uob-hep-cad/uob-hep-pc072/images/boardlocations.jpg

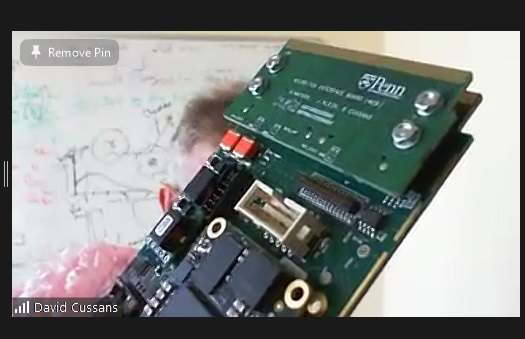
images/boardlocations.jpg
