uob-hep-cad/uob-hep-pc072/images/dune_mib_rev3_v224_top_layer_with_power_colour_white_bg.pdf

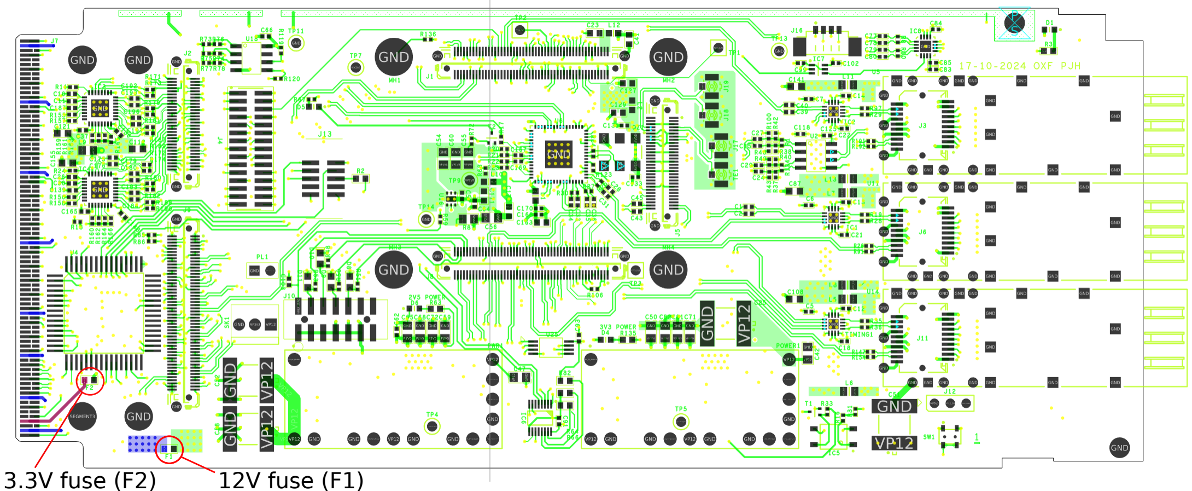
[picture p3: page 1]

3.3V fuse (F2) 12V fuse (F1)
