uob-hep-cad/uob-hep-pc072/hardware/Cadence/top/mtca_interface_board_reocc/02_#20power/sch_1/page1.csv

FILE_TYPE = CONNECTIVITY;
{Allegro Design Entry HDL 24.1 P001 (4234998) 9/4/2024}
"PAGE_NUMBER" = 1;
0"NC";
1"VCC3V3\g";
2"MP3V3\G";
3"GND\g";
4"GND\g";
5"GND\g";
8"GND\G";
7"GND\G";
6"GND\G";
9"GND\g";
10"GND\g";
11"GND\g";
12"GND\g";
13"GND\g";
14"GND\g";
15"GND\g";
16"GND\g";
17"P2V5\g";
18"VP1V8\g";
20"VCC3V3\G";
19"VCC3V3\G";
21"GND\g";
22"GND\g";
23"VP12\g";
24"MP3V3\g";
25"GND\g";
26"VP12";
27"MP3V3\g";
28"MP3V3\g";
29"VCC3V3_PRE_RSHUNT";
30"VO_3V3<1..0>";
31"UN$1$LTC2991$I162$V1";
32"UN$1$LTC2991$I162$V2";
33"VP12_EN";
34"UN$1$OPTOCOUPLERACEC$I139$ANODE";
35"UN$1$RSMD0603$I144$B";
37"SENSE_12C_SCL";
36"SENSE_12C_SCL";
38"UN$1$PTH08T210W$I137$VADJ";
39"P2V5_MON_HIGH";
40"UN$1$PTH08T210W$I137$TURBOTRANS";
41"UN$1$OPTOCOUPLERACEC$I139$COLLECTOR";
42"UN$1$LTC2991$I162$ADR1";
43"UN$1$LTC2991$I162$ADR0";
44"DC_DC_ENABLE";
45"DCDC_ENABLE";
46"1V8_POST_RSHUNT";
47"P2V5_MON_LOW";
49"SENSE_12C_SDA";
48"SENSE_12C_SDA";
50"UN$1$LTC2991$I162$ADR2";
51"VIN<1..0>";
52"DCDC_3V3_PG";
53"UN$1$ledred06030$121P$A";
54"UN$1$r$I154$1";
%"r"
"1","(1200,-4750)","0","discrete","108P";
;
VALUE"10K"
$LOCATION"R85"
SEC"1"
PART_NUMBER"M55342K11B10E0RS3"
PART_TYPE"Thick Film"
DESCRIPTION"RES SMD 10K OHM 1% 1/20W 0402"
POWER"1/10W"
TOLERANCE"1%"
MPN"M55342K11B10E0RS3"
MANUFACTURER"Vishay Dale"
DISTRIBUTOR_PARTNUMBER"1135-1061-1-ND"
DISTRIBUTOR"Digikey"
DATASHEET"C:\EMA\CISQuickStart\Technical_Datasheets\Vishay\dcrcwe3.pdf"
ROOM"MAIN_PWR"
SOURCE_PACKAGE"R"
JEDEC_TYPE"res0402"
CDS_LOCATION"R85"
CDS_LIB"discrete";
"1"
$PN"1"20,19;
"2"
$PN"2"52;
%"r"
"1","(800,-4800)","6","discrete","111P";
;
VALUE"249 Ohm"
$LOCATION"R135"
CDS_LIB"discrete"
CDS_LOCATION"R135"
JEDEC_TYPE"res0603"
SOURCE_PACKAGE"R"
REUSE_ANNOTATE"TRUE"
PART_NUMBER"EMA-00003608"
PART_TYPE"Thick Film"
DESCRIPTION"RES, Thick Film, 249 Ohm, 1.0 %, 1/10 W, SMD, 0603"
POWER"1/10 W"
TOLERANCE"1.0 %"
MPN"MCR03EZPFX2490"
MANUFACTURER"Rohm"
DISTRIBUTOR_PARTNUMBER"RHM249HTR-ND"
DISTRIBUTOR"Digikey"
DATASHEET"C:\EMA\CISQuickStart\Technical_Datasheets\Rohm\mcr03.pdf"
ROOM"VCC3V3I_V"
SEC"1";
"1"
$PN"1"53;
"2"
$PN"2"20,19;
%"r"
"1","(1200,-5225)","0","discrete","117P";
;
$LOCATION"R86"
VALUE"4.99k"
CDS_LIB"discrete"
CDS_LOCATION"R86"
JEDEC_TYPE"res0402"
SOURCE_PACKAGE"R"
REUSE_ANNOTATE"TRUE"
PART_NUMBER"ERJ-2RKF4991X"
PART_TYPE"Thick Film"
DESCRIPTION"RES SMD 4.99K OHM 1% 1/10W 0402"
POWER"1/10 W"
TOLERANCE"1%"
MPN"ERJ-2RKF4991X"
MANUFACTURER"Panasonic"
DISTRIBUTOR_PARTNUMBER"P4.99KLTR-ND"
DISTRIBUTOR"Digikey"
AVAILABILITY"In Stock"
ROOM"VP3V3"
SEC"1";
"1"
$PN"1"52;
"2"
$PN"2"8,7,6;
%"cap_np"
"1","(3675,-2075)","0","ocad_parts_lib","118P";
;
VALUE"0.1UF"
$LOCATION"C92"
VOLTAGE"25V"
CLASS"DISCRETE"
LAST_EDIT_BY"SNF"
ALT_SYMBOLS""
ROOM"MAIN_PWR"
PART_NUMBER"445-8173-1-ND"
PART_TYPE"Ceramic"
DESCRIPTION"CAP 0.1__F __10% 25V Ceramic Capacitor X7R 0805 "
PSPICE"C"
MPN"CGJ4J2X7R1E104K125AA "
MANUFACTURER"TDK CORP"
DISTRIBUTOR_PARTNUMBER"445-8173-1-ND"
DISTRIBUTOR"Digi-Key"
AVAILABILITY"In Stock"
SOURCE_PACKAGE"CAP_NP"
JEDEC_TYPE"cap0805"
SEC"1"
CDS_LOCATION"C92"
CDS_LIB"ocad_parts_lib";
"1"
$PN"1"29;
"2"
$PN"2"9;
%"cap_np"
"1","(3950,-2050)","0","ocad_parts_lib","119P";
;
VOLTAGE"6.3V"
VALUE"100UF"
$LOCATION"C95"
CDS_LIB"ocad_parts_lib"
CDS_LOCATION"C95"
JEDEC_TYPE"cap1206"
SOURCE_PACKAGE"CAP_NP"
REUSE_ANNOTATE"TRUE"
PART_NUMBER"GRM31CD80J107ME39K"
PART_TYPE"Ceramic"
DESCRIPTION"CAP CER 100UF 6.3V X6T 1206"
TOLERANCE"20%"
PSPICE"C"
MPN"GRM31CD80J107ME39K"
MANUFACTURER"Murata"
DISTRIBUTOR_PARTNUMBER"490-16313-2-ND"
DISTRIBUTOR"Digi-Key"
PRICE"0.5"
AVAILABILITY"In Stock"
ROOM"MAIN_PWR"
ALT_SYMBOLS""
LAST_EDIT_BY"SNF"
CLASS"DISCRETE"
SEC"1";
"1"
$PN"1"29;
"2"
$PN"2"9;
%"led red 0603_0"
"1","(750,-5100)","3","atcs","121P";
;
$LOCATION"D4"
VALUE"Red"
SEC"1"
MFR_PART_NUMBER"LTST-C190CKT"
DEVICE"LED_RED0603"
MFR_NAME"Lite-On Trading USA, Inc."
CY_PART_"860R-13780"
REUSE_ANNOTATE"TRUE"
ROOM"VCC3V3I_V"
PART_NUMBER"LNJ237W82RA"
PART_TYPE"LED\Red"
RATING"50 mW"
LEDCOLOR"Red"
MPN"LNJ237W82RA"
MANUFACTURER"Panasonic"
DISTRIBUTOR_PARTNUMBER"LNJ237W82RACT-ND"
DISTRIBUTOR"Digikey"
DATASHEET"C:\EMA\CISQuickStart\Technical_Datasheets\Panasonic\ATA7000CE271.pdf"
DESCRIPTION"LED RED 0603 SMD"
SOURCE_PACKAGE"LED RED 0603_0"
JEDEC_TYPE"LEDC1608X80N"
CDS_LOCATION"D4"
CDS_LIB"atcs";
"A"
$PN"2"53;
"K"
$PN"1"8,7,6;
%"cap_np_0"
"1","(4850,-3750)","7","ocad_parts_lib","126P";
;
VOLTAGE"25V"
VALUE"0.1UF"
$LOCATION"C91"
SEC"1"
ALT_SYMBOLS""
LAST_EDIT_BY"SNF"
CLASS"DISCRETE"
REUSE_ANNOTATE"TRUE"
ROOM"MAIN_PWR"
AVAILABILITY"In Stock"
DISTRIBUTOR"Digi-Key"
DISTRIBUTOR_PARTNUMBER"445-7348-2-ND"
MANUFACTURER"TDK CORP"
MPN"C1005X7R1E104K050BB "
PSPICE"C"
DESCRIPTION"CAP 0.1__F __10% 25V Ceramic Capacitor X7R 0402 "
PART_TYPE"Ceramic"
PART_NUMBER"445-7348-2-ND"
REUSE_ID"169"
SOURCE_PACKAGE"CAP_NP_0"
JEDEC_TYPE"cap0402"
CDS_LOCATION"C91"
CDS_LIB"ocad_parts_lib";
"1"
$PN"1"16;
"2"
$PN"2"28;
%"hdr1x3"
"2","(675,-3475)","0","ocad_parts_lib","127P";
;
$LOCATION"J12"
VALUE"HDR1x3"
SEC"1"
REUSE_ANNOTATE"TRUE"
ROOM"USB-JTAG"
PART_NUMBER"HDR1x3"
PART_TYPE"Header"
DESCRIPTION"CONN3, Header,TH"
CONTACTCURRENT"6.0 A"
CONTACTVOLTAGE"600 V"
CONTACTGENDER"Male"
HOUSINGGENDER"Male"
MANUFACTURER"Samtec"
DISTRIBUTOR"Digikey"
DATASHEET"C:\EMA\CISQuickStart\Technical_Datasheets\Molex Inc\MX42385.pdf"
SOURCE_PACKAGE"HDR1x3"
JEDEC_TYPE"Hdr_1x3"
CDS_LOCATION"J12"
CDS_LIB"ocad_parts_lib";
"P1"
$PN"1"2;
"P2"
$PN"2"33;
"P3"
$PN"3"45;
%"testpoint"
"1","(4900,-2125)","5","testpoint","130P";
;
BOM_IGNORE"TRUE"
$LOCATION"TP5"
SEC"1"
VALUE"5002 White"
ROOM"MAIN_PWR"
PART_NUMBER"EMA-00001481V22"
PART_TYPE"Testpoint"
DESCRIPTION"MISC, Testpoint, 5002 White, TH, 2.5x2.5x4.6 mm"
MPN"5002"
MANUFACTURER"Keystone Electronics"
DATASHEET"C:\EMA\CISQuickStart\Technical_Datasheets\Keystone Electronics\M55p51.pdf"
SOURCE_PACKAGE"TESTPOINT"
JEDEC_TYPE"TP_KEYSTONE_5000A"
CDS_LOCATION"TP5"
CDS_LIB"testpoint";
"TP"
$PN"1"29;
%"vcc_bar"
"1","(6750,-1725)","0","mtca_interface_board","132P";
;
HDL_POWER"VCC3V3"
CDS_LIB"mtca_interface_board";
"HOTSPOT_0"1;
%"vcc_bar"
"1","(875,-2950)","0","mtca_interface_board","133P";
;
HDL_POWER"MP3V3"
CDS_LIB"mtca_interface_board";
"HOTSPOT_0"2;
%"gnd"
"1","(1375,-2700)","0","mtca_interface_board","38P";
;
CDS_LIB"mtca_interface_board"
HDL_POWER"GND";
"HOTSPOT_0"3;
%"gnd"
"1","(2200,-2700)","0","mtca_interface_board","39P";
;
CDS_LIB"mtca_interface_board"
HDL_POWER"GND";
"HOTSPOT_0"4;
%"gnd"
"1","(5850,-2325)","0","mtca_interface_board","40P";
;
CDS_LIB"mtca_interface_board"
HDL_POWER"GND";
"HOTSPOT_0"5;
%"gnd"
"1","(750,-5575)","0","mtca_interface_board","41P";
;
CDS_LIB"mtca_interface_board"
HDL_POWER"GND";
"HOTSPOT_0"8,7,6;
%"gnd"
"1","(3900,-2475)","0","mtca_interface_board","5P";
;
CDS_LIB"mtca_interface_board"
HDL_POWER"GND";
"HOTSPOT_0"9;
%"PTH08T210W"
"1","(2775,-1950)","0","cnlinear","I137";
;
$LOCATION"IC?"
PACK_TYPE"ECP"
TYPE"PTH08T210WAD"
CDS_LIB"cnlinear";
"VI<1..0>"51;
"GND<3..0>"10;
"VO<1..0>"30;
"TURBOTRANS"40;
"SENSP"35;
"SENSM"11;
"UVLO"44;
"TRACK"26;
"VADJ"38;
%"TRANS MOSFET"
"1","(2200,-2400)","0","cndiscrete","I138";
;
$LOCATION"T?"
TYPE"SOT523"
VALUE"PJE8408"
CDS_LIB"cndiscrete"
PACK_TYPE"GSD";
"D\NAC"44;
"S\NAC"4;
"G\NAC"41;
%"OPTOCOUPLER_AC_EC"
"1","(1675,-2575)","0","cndiscrete","I139";
;
$LOCATION"IC?"
CASE"SOIC"
TYPE"TLP183"
NEEDS_NO_SIZE"TRUE"
CDS_LIB"cndiscrete"
PACK_TYPE"1264";
"EMITTER"13;
"COLLECTOR"41;
"CATHODE"3;
"ANODE"34;
%"r"
"1","(1925,-2150)","0","discrete","I141";
;
$LOCATION"?"
VALUE"150K"
CDS_LIB"discrete"
JEDEC_TYPE"res0402"
SOURCE_PACKAGE"R"
ROOM"MMC_DISCRETE"
DISTRIBUTOR"Digikey"
DISTRIBUTOR_PARTNUMBER"P150KLTR-ND"
MANUFACTURER"Panasonic"
MPN"ERJ-2RKF1873X"
TOLERANCE"1 %"
POWER"1/10 W"
DESCRIPTION"RES SMD 150K OHM 1% 1/10W 0402"
PART_TYPE"Thick Film"
PART_NUMBER"ERJ-2RKF1503X";
"1"
$PN"?"26;
"2"
$PN"?"41;
%"gnd"
"1","(2575,-2325)","0","mtca_interface_board","I142";
;
CDS_LIB"mtca_interface_board"
HDL_POWER"GND";
"HOTSPOT_0"10;
%"gnd"
"1","(3225,-2400)","0","mtca_interface_board","I143";
;
CDS_LIB"mtca_interface_board"
HDL_POWER"GND";
"HOTSPOT_0"11;
%"RSMD0603"
"1","(3175,-1600)","0","cnpassive","I144";
;
$LOCATION"R?"
VALUE"XX"
TOL"1%"
SIZE"1B"
TOL_ON_OFF"ON"
POSTOL"RTOL%"
NEGTOL"RTOL%"
DIST"FLAT"
POWER"RMAX"
VOLTAGE"RVMAX"
SLOPE"RSMAX"
MAX_TEMP"RTMAX"
TC1"RTMPL"
TC2"RTMPQ"
PACK_TYPE"1/10W"
CDS_LIB"cnpassive";
"B <SIZE-1..0>\NAC"35;
"A <SIZE-1..0>\NAC"40;
%"RSMD0603"
"1","(2925,-2450)","1","cnpassive","I145";
;
$LOCATION"R?"
TOL"1%"
VALUE"1.6K"
PACK_TYPE"1/10W"
CDS_LIB"cnpassive"
SIZE"1B"
TOL_ON_OFF"ON"
POSTOL"RTOL%"
NEGTOL"RTOL%"
DIST"FLAT"
POWER"RMAX"
VOLTAGE"RVMAX"
SLOPE"RSMAX"
MAX_TEMP"RTMAX"
TC1"RTMPL"
TC2"RTMPQ";
"B <SIZE-1..0>\NAC"38;
"A <SIZE-1..0>\NAC"12;
%"gnd"
"1","(2875,-2675)","0","mtca_interface_board","I146";
;
CDS_LIB"mtca_interface_board"
HDL_POWER"GND";
"HOTSPOT_0"12;
%"RSMD0603"
"1","(3700,-1600)","0","cnpassive","I148";
;
LOCATION"R84"
TOL"1%"
VALUE"1"
CDS_LIB"cnpassive"
SIZE"1B"
TOL_ON_OFF"ON"
POSTOL"RTOL%"
NEGTOL"RTOL%"
DIST"FLAT"
POWER"RMAX"
VOLTAGE"RVMAX"
SLOPE"RSMAX"
MAX_TEMP"RTMAX"
TC1"RTMPL"
TC2"RTMPQ"
PACK_TYPE"1/10W";
"B <SIZE-1..0>\NAC"1;
"A <SIZE-1..0>\NAC"35;
%"r"
"1","(1225,-3075)","2","discrete","I154";
;
$LOCATION"?"
VALUE"24.9"
CDS_LIB"discrete"
REUSE_ANNOTATE"TRUE"
ROOM"JTAG"
PART_NUMBER"311-24.9LRCT-ND"
PART_TYPE"Thick Film"
DESCRIPTION"RES SMD 24.9 OHM 1% 1/16W 0402"
POWER"1/10W"
TOLERANCE"1%"
MPN"RC0402FR-0724R9L"
MANUFACTURER"Yageo"
DISTRIBUTOR_PARTNUMBER"311-24.9LRCT-ND"
DISTRIBUTOR"Digikey"
REUSE_ID"38"
SOURCE_PACKAGE"R"
JEDEC_TYPE"res0402";
"1"
$PN"?"54;
"2"
$PN"?"33;
%"gnd"
"1","(1925,-2700)","0","mtca_interface_board","I155";
;
CDS_LIB"mtca_interface_board"
HDL_POWER"GND";
"HOTSPOT_0"13;
%"gnd"
"1","(1075,-2350)","0","mtca_interface_board","I158";
;
CDS_LIB"mtca_interface_board"
HDL_POWER"GND";
"HOTSPOT_0"14;
%"r"
"1","(1225,-2725)","2","discrete","I159";
;
$LOCATION"?"
VALUE"24.9"
CDS_LIB"discrete"
REUSE_ANNOTATE"TRUE"
ROOM"JTAG"
PART_NUMBER"311-24.9LRCT-ND"
PART_TYPE"Thick Film"
DESCRIPTION"RES SMD 24.9 OHM 1% 1/16W 0402"
POWER"1/10W"
TOLERANCE"1%"
MPN"RC0402FR-0724R9L"
MANUFACTURER"Yageo"
DISTRIBUTOR_PARTNUMBER"311-24.9LRCT-ND"
DISTRIBUTOR"Digikey"
REUSE_ID"38"
SOURCE_PACKAGE"R"
JEDEC_TYPE"res0402";
"1"
$PN"?"34;
"2"
$PN"?"54;
%"CTAP"
"1","(2225,-1850)","2","standard","I160";
;
CDS_LIB"standard"
BODY_TYPE"PLUMBING"
HDL_TAP"TRUE";
"S \NAC"
BN"0"26;
"B \NAC \NWC"51;
%"CTAP"
"1","(2225,-1775)","2","standard","I161";
;
CDS_LIB"standard"
BODY_TYPE"PLUMBING"
HDL_TAP"TRUE";
"S \NAC"
BN"1"26;
"B \NAC \NWC"51;
%"LTC2991"
"1","(4825,-2875)","0","cnlinear","I162";
;
$LOCATION"IC?"
POWER_GROUP"VCC=MP3V3"
PACK_TYPE"MSOP"
TYPE"LTC2991CMS#PBF"
CDS_LIB"cnlinear"
CDS_LMAN_SYM_OUTLINE"-200,225,200,-200";
"V4"46;
"V8"47;
"V7"39;
"V5"18;
"V6"0;
"V1"31;
"V2"32;
"V3"17;
"PWM"0;
"ADR2"50;
"ADR1"42;
"SDA"49,48;
"ADR0"43;
"SCL"37,36;
%"CTAP"
"1","(3350,-1975)","0","standard","I163";
;
CDS_LIB"standard"
BODY_TYPE"PLUMBING"
HDL_TAP"TRUE";
"S \NAC"
BN"1"29;
"B \NAC \NWC"30;
%"CTAP"
"1","(3350,-2050)","0","standard","I164";
;
CDS_LIB"standard"
BODY_TYPE"PLUMBING"
HDL_TAP"TRUE";
"S \NAC"
BN"0"29;
"B \NAC \NWC"30;
%"RSMD0603"
"1","(4300,-2925)","0","cnpassive","I165";
;
$LOCATION"R?"
TOL""
VALUE"00"
PACK_TYPE""
CDS_LIB"cnpassive"
SIZE"1B"
TOL_ON_OFF"ON"
POSTOL"RTOL%"
NEGTOL"RTOL%"
DIST"FLAT"
POWER"RMAX"
VOLTAGE"RVMAX"
SLOPE"RSMAX"
MAX_TEMP"RTMAX"
TC1"RTMPL"
TC2"RTMPQ";
"B <SIZE-1..0>\NAC"43;
"A <SIZE-1..0>\NAC"27;
%"RSMD0603"
"1","(4300,-2975)","0","cnpassive","I166";
;
$LOCATION"R?"
TOL""
VALUE"00"
PACK_TYPE""
CDS_LIB"cnpassive"
SIZE"1B"
TOL_ON_OFF"ON"
POSTOL"RTOL%"
NEGTOL"RTOL%"
DIST"FLAT"
POWER"RMAX"
VOLTAGE"RVMAX"
SLOPE"RSMAX"
MAX_TEMP"RTMAX"
TC1"RTMPL"
TC2"RTMPQ";
"B <SIZE-1..0>\NAC"42;
"A <SIZE-1..0>\NAC"15;
%"RSMD0603"
"1","(4300,-3025)","0","cnpassive","I167";
;
$LOCATION"R?"
VALUE"00"
TOL""
TC2"RTMPQ"
TC1"RTMPL"
MAX_TEMP"RTMAX"
SLOPE"RSMAX"
VOLTAGE"RVMAX"
POWER"RMAX"
DIST"FLAT"
NEGTOL"RTOL%"
POSTOL"RTOL%"
TOL_ON_OFF"ON"
SIZE"1B"
CDS_LIB"cnpassive"
PACK_TYPE"";
"B <SIZE-1..0>\NAC"50;
"A <SIZE-1..0>\NAC"15;
%"gnd"
"1","(4100,-3100)","0","mtca_interface_board","I168";
;
CDS_LIB"mtca_interface_board"
HDL_POWER"GND";
"HOTSPOT_0"15;
%"gnd"
"1","(5000,-3825)","0","mtca_interface_board","I169";
;
CDS_LIB"mtca_interface_board"
HDL_POWER"GND";
"HOTSPOT_0"16;
%"P2V5"
"1","(5850,-2650)","0","cnpower","I171";
;
CDS_LIB"cnpower"
SIZE"1B"
BODY_TYPE"PLUMBING"
HDL_POWER"P2V5";
"A<SIZE-1..0>\NAC"
VHDL_INIT"1"17;
%"vcc_bar"
"1","(6075,-2775)","0","mtca_interface_board","I172";
;
HDL_POWER"VP1V8"
CDS_LIB"mtca_interface_board";
"HOTSPOT_0"18;
%"cap_np"
"1","(1125,-2100)","0","ocad_parts_lib","I175";
;
CDS_LOCATION"C92"
$LOCATION"C92"
VALUE"0.1UF"
VOLTAGE"25V"
CDS_LIB"ocad_parts_lib"
JEDEC_TYPE"cap0805"
SOURCE_PACKAGE"CAP_NP"
AVAILABILITY"In Stock"
DISTRIBUTOR"Digi-Key"
DISTRIBUTOR_PARTNUMBER"445-8173-1-ND"
MANUFACTURER"TDK CORP"
MPN"CGJ4J2X7R1E104K125AA "
PSPICE"C"
DESCRIPTION"CAP 0.1__F __10% 25V Ceramic Capacitor X7R 0805 "
PART_TYPE"Ceramic"
PART_NUMBER"445-8173-1-ND"
ROOM"MAIN_PWR"
ALT_SYMBOLS""
LAST_EDIT_BY"SNF"
CLASS"DISCRETE"
SEC"1";
"1"
$PN"1"26;
"2"
$PN"2"14;
%"testpoint"
"1","(3550,-4600)","5","testpoint","I176";
;
$LOCATION"TP7"
JEDEC_TYPE"TP_KEYSTONE_5000A"
CDS_LOCATION"TP7"
CDS_LIB"testpoint"
SEC"1"
PART_NUMBER"EMA-00001481V22"
SOURCE_PACKAGE"TESTPOINT";
"TP"
$PN"1"20,19;
%"testpoint"
"1","(3550,-5425)","5","testpoint","I177";
;
$LOCATION"TP13"
SEC"1"
VALUE"5002 White"
ROOM"VCC3V3I_V"
DATASHEET"C:\EMA\CISQuickStart\Technical_Datasheets\Keystone Electronics\M55p51.pdf"
MANUFACTURER"Keystone Electronics"
MPN"5002"
DESCRIPTION"MISC, Testpoint, 5002 White, TH, 2.5x2.5x4.6 mm"
PART_TYPE"Testpoint"
PART_NUMBER"EMA-00001481V22"
SOURCE_PACKAGE"TESTPOINT"
JEDEC_TYPE"TP_KEYSTONE_5000A"
CDS_LOCATION"TP13"
CDS_LIB"testpoint";
"TP"
$PN"1"8,7,6;
%"cap_np"
"1","(2575,-4925)","0","ocad_parts_lib","I186";
;
VALUE"47UF"
$LOCATION"C82"
VOLTAGE"6.3V"
DESCRIPTION"CAP CER 47UF 6.3V X5R 0805"
PART_TYPE"Ceramic"
SEC"1"
CLASS"DISCRETE"
LAST_EDIT_BY"SNF"
ALT_SYMBOLS""
ROOM"VCC3V3I_V"
AVAILABILITY"In Stock"
DISTRIBUTOR"Digi-Key"
DISTRIBUTOR_PARTNUMBER"490-14660-2-ND"
MANUFACTURER"Murata"
MPN"GRM21BR60J476ME15K"
PSPICE"C"
TOLERANCE"20%"
PART_NUMBER"GRM21BR60J476ME15K"
SOURCE_PACKAGE"CAP_NP"
JEDEC_TYPE"cap0805"
CDS_LOCATION"C82"
CDS_LIB"ocad_parts_lib";
"1"
$PN"1"20,19;
"2"
$PN"2"8,7,6;
%"gnd"
"1","(2525,-5600)","0","mtca_interface_board","I187";
;
CDS_LIB"mtca_interface_board"
HDL_POWER"GND";
"HOTSPOT_0"8,7,6;
%"cap_np"
"1","(2275,-4925)","0","ocad_parts_lib","I188";
;
VOLTAGE"6.3V"
VALUE"47UF"
$LOCATION"C81"
DISTRIBUTOR_PARTNUMBER"490-14660-2-ND"
DISTRIBUTOR"Digi-Key"
SEC"1"
CLASS"DISCRETE"
LAST_EDIT_BY"SNF"
ALT_SYMBOLS""
ROOM"VCC3V3I_V"
PART_NUMBER"GRM21BR60J476ME15K"
PART_TYPE"Ceramic"
DESCRIPTION"CAP CER 47UF 6.3V X5R 0805"
TOLERANCE"20%"
PSPICE"C"
MPN"GRM21BR60J476ME15K"
MANUFACTURER"Murata"
AVAILABILITY"In Stock"
SOURCE_PACKAGE"CAP_NP"
JEDEC_TYPE"cap0805"
CDS_LOCATION"C81"
CDS_LIB"ocad_parts_lib";
"1"
$PN"1"20,19;
"2"
$PN"2"8,7,6;
%"cap_np"
"1","(2000,-4925)","0","ocad_parts_lib","I189";
;
VOLTAGE"6.3V"
VALUE"47UF"
$LOCATION"C71"
PART_TYPE"Ceramic"
PART_NUMBER"GRM21BR60J476ME15K"
SEC"1"
CLASS"DISCRETE"
LAST_EDIT_BY"SNF"
ALT_SYMBOLS""
AVAILABILITY"In Stock"
DISTRIBUTOR"Digi-Key"
DISTRIBUTOR_PARTNUMBER"490-14660-2-ND"
MANUFACTURER"Murata"
MPN"GRM21BR60J476ME15K"
PSPICE"C"
TOLERANCE"20%"
DESCRIPTION"CAP CER 47UF 6.3V X5R 0805"
ROOM"VCC3V3I_V"
SOURCE_PACKAGE"CAP_NP"
JEDEC_TYPE"cap0805"
CDS_LOCATION"C71"
CDS_LIB"ocad_parts_lib";
"1"
$PN"1"20,19;
"2"
$PN"2"8,7,6;
%"vcc_bar"
"1","(1525,-4475)","0","mtca_interface_board","I190";
;
HDL_POWER"VCC3V3"
CDS_LIB"mtca_interface_board";
"HOTSPOT_0"20,19;
%"cap_np"
"1","(1700,-4925)","0","ocad_parts_lib","I191";
;
$LOCATION"C69"
VALUE"0.1UF"
VOLTAGE"25V"
DISTRIBUTOR"Digi-Key"
AVAILABILITY"In Stock"
CDS_LIB"ocad_parts_lib"
CDS_LOCATION"C69"
JEDEC_TYPE"cap0402"
SOURCE_PACKAGE"CAP_NP"
REUSE_ID"18"
DISTRIBUTOR_PARTNUMBER"445-7348-2-ND"
MANUFACTURER"TDK CORP"
MPN"C1005X7R1E104K050BB "
PSPICE"C"
DESCRIPTION"CAP 0.1__F __10% 25V Ceramic Capacitor X7R 0402 "
PART_TYPE"Ceramic"
PART_NUMBER"445-7348-2-ND"
ROOM"VCC3V3I_V"
REUSE_ANNOTATE"TRUE"
ALT_SYMBOLS""
LAST_EDIT_BY"SNF"
CLASS"DISCRETE"
SEC"1";
"1"
$PN"1"20,19;
"2"
$PN"2"8,7,6;
%"cap_np"
"1","(2850,-4925)","0","ocad_parts_lib","I192";
;
$LOCATION"C50"
VALUE"47UF"
VOLTAGE"6.3V"
DISTRIBUTOR"Digi-Key"
AVAILABILITY"In Stock"
SEC"1"
CLASS"DISCRETE"
LAST_EDIT_BY"SNF"
ALT_SYMBOLS""
PART_NUMBER"GRM21BR60J476ME15K"
PART_TYPE"Ceramic"
DESCRIPTION"CAP CER 47UF 6.3V X5R 0805"
TOLERANCE"20%"
PSPICE"C"
MPN"GRM21BR60J476ME15K"
MANUFACTURER"Murata"
DISTRIBUTOR_PARTNUMBER"490-14660-2-ND"
ROOM"VP3V3"
SOURCE_PACKAGE"CAP_NP"
JEDEC_TYPE"cap0805"
CDS_LOCATION"C50"
CDS_LIB"ocad_parts_lib";
"1"
$PN"1"20,19;
"2"
$PN"2"8,7,6;
%"gnd"
"1","(475,-2350)","0","mtca_interface_board","I193";
;
CDS_LIB"mtca_interface_board"
HDL_POWER"GND";
"HOTSPOT_0"21;
%"ELCAPTAN"
"1","(825,-2150)","1","cnpassive","I194";
;
$LOCATION"C?"
VALUE"220UF"
VOLTAGE"25V"
PACK_TYPE"SMD"
CDS_LIB"cnpassive"
TOL_ON_OFF"ON"
TC"0"
SLOPE"CSMAX"
SIZE"1B"
POSTOL"CTOL%"
NEGTOL"CTOL%"
MAX_TEMP"CTMAX"
KNEE"CBMAX"
IC"UNDEF"
DIST"FLAT";
"A <SIZE-1..0>\NAC"
$PN"#"26;
"B <SIZE-1..0>\NAC"
$PN"#"22;
%"gnd"
"1","(775,-2350)","0","mtca_interface_board","I195";
;
CDS_LIB"mtca_interface_board"
HDL_POWER"GND";
"HOTSPOT_0"22;
%"ELCAPTAN"
"1","(525,-2150)","1","cnpassive","I196";
;
$LOCATION"C?"
VALUE"220UF"
VOLTAGE"25V"
PACK_TYPE"SMD"
CDS_LIB"cnpassive"
TOL_ON_OFF"ON"
TC"0"
SLOPE"CSMAX"
SIZE"1B"
POSTOL"CTOL%"
NEGTOL"CTOL%"
MAX_TEMP"CTMAX"
KNEE"CBMAX"
IC"UNDEF"
DIST"FLAT";
"A <SIZE-1..0>\NAC"
$PN"#"26;
"B <SIZE-1..0>\NAC"
$PN"#"21;
%"TANTPOLY"
"1","(6000,-2100)","1","bris_cds_discrete","I197";
;
$LOCATION"C?"
VALUE"220UF"
CDS_LMAN_SYM_OUTLINE"-25,25,25,-25"
DIST"FLAT"
IC"UNDEF"
KNEE"CBMAX"
MAX_TEMP"CTMAX"
NEGTOL"CTOL%"
POSTOL"CTOL%"
SIZE"1B"
SLOPE"CSMAX"
TC"0"
TOL_ON_OFF"ON"
CDS_LIB"bris_cds_discrete"
PACK_TYPE"SMD"
VOLTAGE"6.3V";
"A<SIZE-1..0>"
$PN"#"1;
"B<SIZE-1..0>"
$PN"#"5;
%"TANTPOLY"
"1","(4300,-2100)","1","bris_cds_discrete","I198";
;
$LOCATION"C?"
VALUE"220UF"
VOLTAGE"6.3V"
PACK_TYPE"SMD"
CDS_LIB"bris_cds_discrete"
TOL_ON_OFF"ON"
TC"0"
SLOPE"CSMAX"
SIZE"1B"
POSTOL"CTOL%"
NEGTOL"CTOL%"
MAX_TEMP"CTMAX"
KNEE"CBMAX"
IC"UNDEF"
DIST"FLAT"
CDS_LMAN_SYM_OUTLINE"-25,25,25,-25";
"A<SIZE-1..0>"
$PN"#"29;
"B<SIZE-1..0>"
$PN"#"9;
%"TANTPOLY"
"1","(4525,-2100)","1","bris_cds_discrete","I199";
;
$LOCATION"C?"
VALUE"220UF"
CDS_LMAN_SYM_OUTLINE"-25,25,25,-25"
DIST"FLAT"
IC"UNDEF"
KNEE"CBMAX"
MAX_TEMP"CTMAX"
NEGTOL"CTOL%"
POSTOL"CTOL%"
SIZE"1B"
SLOPE"CSMAX"
TC"0"
TOL_ON_OFF"ON"
CDS_LIB"bris_cds_discrete"
PACK_TYPE"SMD"
VOLTAGE"6.3V";
"A<SIZE-1..0>"
$PN"#"29;
"B<SIZE-1..0>"
$PN"#"9;
%"RES_SR"
"1","(5475,-1900)","0","cnpassive","I200";
;
$LOCATION"R?"
VALUE"0.05"
TOL"1%"
PACK_TYPE"LVK12"
CDS_LIB"cnpassive"
TC2"RTMPQ"
TC1"RTMPL"
MAX_TEMP"RTMAX"
SLOPE"RSMAX"
VOLTAGE"RVMAX"
POWER"RMAX"
DIST"FLAT"
NEGTOL"RTOL%"
POSTOL"RTOL%"
TOL_ON_OFF"ON"
SIZE"1B";
"C1 <SIZE-1..0>\NAC"29;
"S1 <SIZE-1..0>\NAC"31;
"S2 <SIZE-1..0>\NAC"32;
"C2 <SIZE-1..0>\NAC"1;
%"TANTPOLY"
"1","(5775,-2100)","1","bris_cds_discrete","I201";
;
$LOCATION"C?"
VALUE"220UF"
VOLTAGE"6.3V"
PACK_TYPE"SMD"
CDS_LIB"bris_cds_discrete"
TOL_ON_OFF"ON"
TC"0"
SLOPE"CSMAX"
SIZE"1B"
POSTOL"CTOL%"
NEGTOL"CTOL%"
MAX_TEMP"CTMAX"
KNEE"CBMAX"
IC"UNDEF"
DIST"FLAT"
CDS_LMAN_SYM_OUTLINE"-25,25,25,-25";
"A<SIZE-1..0>"
$PN"#"1;
"B<SIZE-1..0>"
$PN"#"5;
%"KKCON3"
"1","(2375,-3250)","2","oxflib","I203";
;
$LOCATION"?"
MANUF"MOLEX"
PACK_TYPE"STR"
CDS_LIB"oxflib"
SIZE"1B"
PL_COMMENTS"-"
OL_COMMENTS"-"
KL_COMMENTS"-";
"A1 <SIZE-1..0>"23;
"A2 <SIZE-1..0>"25;
"B1 <SIZE-1..0>"24;
%"vcc_bar"
"1","(2450,-3175)","0","mtca_interface_board","I204";
;
HDL_POWER"VP12"
CDS_LIB"mtca_interface_board";
"HOTSPOT_0"23;
%"vcc_bar"
"1","(2650,-3175)","0","mtca_interface_board","I205";
;
HDL_POWER"MP3V3"
CDS_LIB"mtca_interface_board";
"HOTSPOT_0"24;
%"gnd"
"1","(2450,-3425)","0","mtca_interface_board","I206";
;
HDL_POWER"GND"
CDS_LIB"mtca_interface_board";
"HOTSPOT_0"25;
%"vcc_bar"
"1","(-50,-1700)","0","mtca_interface_board","I208";
;
HDL_POWER"VP12"
CDS_LIB"mtca_interface_board";
"HOTSPOT_0"26;
%"cap_np"
"1","(3575,-1725)","0","ocad_parts_lib","I209";
;
$LOCATION"?"
VALUE"0.1UF"
VOLTAGE"25V"
CDS_LIB"ocad_parts_lib"
JEDEC_TYPE"cap0805"
SOURCE_PACKAGE"CAP_NP"
AVAILABILITY"In Stock"
DISTRIBUTOR"Digi-Key"
DISTRIBUTOR_PARTNUMBER"445-8173-1-ND"
MANUFACTURER"TDK CORP"
MPN"CGJ4J2X7R1E104K125AA "
PSPICE"C"
DESCRIPTION"CAP 0.1__F __10% 25V Ceramic Capacitor X7R 0805 "
PART_TYPE"Ceramic"
PART_NUMBER"445-8173-1-ND"
ROOM"MAIN_PWR"
ALT_SYMBOLS""
LAST_EDIT_BY"SNF"
CLASS"DISCRETE";
"1"
$PN"?"35;
"2"
$PN"?"29;
%"vcc_bar"
"1","(3750,-2825)","0","mtca_interface_board","I210";
;
HDL_POWER"MP3V3"
CDS_LIB"mtca_interface_board";
"HOTSPOT_0"27;
%"vcc_bar"
"1","(4600,-3675)","0","mtca_interface_board","I211";
;
HDL_POWER"MP3V3"
CDS_LIB"mtca_interface_board";
"HOTSPOT_0"28;
END.
