uob-hep-cad/uob-hep-pc072/hardware/Cadence/top/mtca_interface_board_reocc/02_#20power/sch_1/page2.csv

FILE_TYPE = CONNECTIVITY;
{Allegro Design Entry HDL 24.1 P001 (4234998) 9/4/2024}
"PAGE_NUMBER" = 4;
0"NC";
1"VP12";
2"GND\g";
3"GND\g";
4"GND\g";
5"GND\g";
6"GND\g";
7"GND\g";
8"P2V5\g";
9"P2V5\g";
11"GND\G";
10"GND\G";
12"GND\g";
13"GND\g";
14"VCC2V5_PRE_RSHUNT";
15"P2V5_MON_HIGH";
16"UN$4$PTH08T210W$I137$VADJ";
17"VO_2V5<1..0>";
18"DC_DC_ENABLE";
19"VIN<1..0>";
20"UN$4$PTH08T210W$I137$SENSP";
21"P2V5_MON_LOW";
22"UN$4$PTH08T210W$I137$TURBOTRANS";
23"UN$4$ledgreen06030$I176$A";
24"DCDC_2V5_PG";
%"cap_np"
"1","(4300,-2675)","0","ocad_parts_lib","119P";
;
CDS_LOCATION"C95"
$LOCATION"C95"
VOLTAGE"6.3V"
VALUE"100UF"
CDS_LIB"ocad_parts_lib"
JEDEC_TYPE"cap1206"
SOURCE_PACKAGE"CAP_NP"
REUSE_ANNOTATE"TRUE"
PART_NUMBER"GRM31CD80J107ME39K"
PART_TYPE"Ceramic"
DESCRIPTION"CAP CER 100UF 6.3V X6T 1206"
TOLERANCE"20%"
PSPICE"C"
MPN"GRM31CD80J107ME39K"
MANUFACTURER"Murata"
DISTRIBUTOR_PARTNUMBER"490-16313-2-ND"
DISTRIBUTOR"Digi-Key"
PRICE"0.5"
AVAILABILITY"In Stock"
ROOM"MAIN_PWR"
ALT_SYMBOLS""
LAST_EDIT_BY"SNF"
CLASS"DISCRETE"
SEC"1";
"1"
$PN"1"14;
"2"
$PN"2"2;
%"testpoint"
"1","(5250,-2750)","5","testpoint","130P";
;
BOM_IGNORE"TRUE"
CDS_LOCATION"TP5"
$LOCATION"TP5"
SEC"1"
VALUE"5002 White"
ROOM"MAIN_PWR"
PART_NUMBER"EMA-00001481V22"
PART_TYPE"Testpoint"
DESCRIPTION"MISC, Testpoint, 5002 White, TH, 2.5x2.5x4.6 mm"
MPN"5002"
MANUFACTURER"Keystone Electronics"
DATASHEET"C:\EMA\CISQuickStart\Technical_Datasheets\Keystone Electronics\M55p51.pdf"
SOURCE_PACKAGE"TESTPOINT"
JEDEC_TYPE"TP_KEYSTONE_5000A"
CDS_LIB"testpoint";
"TP"
$PN"1"14;
%"vcc_bar"
"1","(350,-2325)","0","mtca_interface_board","131P";
;
HDL_POWER"VP12"
CDS_LIB"mtca_interface_board";
"HOTSPOT_0"1;
%"gnd"
"1","(4250,-3050)","0","mtca_interface_board","5P";
;
HDL_POWER"GND"
CDS_LIB"mtca_interface_board";
"HOTSPOT_0"2;
%"PTH08T210W"
"1","(2800,-2575)","0","cnlinear","I137";
;
$LOCATION"IC?"
TYPE"PTH08T210WAD"
PACK_TYPE"ECP"
CDS_LIB"cnlinear";
"VI<1..0>"19;
"GND<3..0>"3;
"VO<1..0>"17;
"TURBOTRANS"22;
"SENSP"20;
"SENSM"4;
"UVLO"18;
"TRACK"1;
"VADJ"16;
%"gnd"
"1","(2600,-2950)","0","mtca_interface_board","I142";
;
CDS_LIB"mtca_interface_board"
HDL_POWER"GND";
"HOTSPOT_0"3;
%"gnd"
"1","(3250,-3025)","0","mtca_interface_board","I143";
;
CDS_LIB"mtca_interface_board"
HDL_POWER"GND";
"HOTSPOT_0"4;
%"RSMD0603"
"1","(3200,-2225)","0","cnpassive","I144";
;
$LOCATION"R?"
TOL"1%"
VALUE"XX"
CDS_LIB"cnpassive"
PACK_TYPE"1/10W"
TC2"RTMPQ"
TC1"RTMPL"
MAX_TEMP"RTMAX"
SLOPE"RSMAX"
VOLTAGE"RVMAX"
POWER"RMAX"
DIST"FLAT"
NEGTOL"RTOL%"
POSTOL"RTOL%"
TOL_ON_OFF"ON"
SIZE"1B";
"B <SIZE-1..0>\NAC"20;
"A <SIZE-1..0>\NAC"22;
%"RSMD0603"
"1","(2950,-2925)","1","cnpassive","I145";
;
$LOCATION"R?"
VALUE"5.6K"
TOL"1%"
TC2"RTMPQ"
TC1"RTMPL"
MAX_TEMP"RTMAX"
SLOPE"RSMAX"
VOLTAGE"RVMAX"
POWER"RMAX"
DIST"FLAT"
NEGTOL"RTOL%"
POSTOL"RTOL%"
TOL_ON_OFF"ON"
SIZE"1B"
CDS_LIB"cnpassive"
PACK_TYPE"1/10W";
"B <SIZE-1..0>\NAC"16;
"A <SIZE-1..0>\NAC"5;
%"gnd"
"1","(2900,-3075)","0","mtca_interface_board","I146";
;
CDS_LIB"mtca_interface_board"
HDL_POWER"GND";
"HOTSPOT_0"5;
%"RSMD0603"
"1","(4050,-2225)","0","cnpassive","I148";
;
LOCATION"R69"
VALUE"1"
TOL"1%"
TC2"RTMPQ"
TC1"RTMPL"
MAX_TEMP"RTMAX"
SLOPE"RSMAX"
VOLTAGE"RVMAX"
POWER"RMAX"
DIST"FLAT"
NEGTOL"RTOL%"
POSTOL"RTOL%"
TOL_ON_OFF"ON"
SIZE"1B"
CDS_LIB"cnpassive"
PACK_TYPE"1/10W";
"B <SIZE-1..0>\NAC"9;
"A <SIZE-1..0>\NAC"20;
%"gnd"
"1","(850,-2975)","0","mtca_interface_board","I157";
;
HDL_POWER"GND"
CDS_LIB"mtca_interface_board";
"HOTSPOT_0"6;
%"gnd"
"1","(1100,-2975)","0","mtca_interface_board","I158";
;
CDS_LIB"mtca_interface_board"
HDL_POWER"GND";
"HOTSPOT_0"7;
%"CTAP"
"1","(2250,-2475)","2","standard","I160";
;
CDS_LIB"standard"
BODY_TYPE"PLUMBING"
HDL_TAP"TRUE";
"S \NAC"
BN"0"1;
"B \NAC \NWC"19;
%"CTAP"
"1","(2250,-2400)","2","standard","I161";
;
CDS_LIB"standard"
BODY_TYPE"PLUMBING"
HDL_TAP"TRUE";
"S \NAC"
BN"1"1;
"B \NAC \NWC"19;
%"CTAP"
"1","(3825,-2625)","0","standard","I163";
;
CDS_LIB"standard"
BODY_TYPE"PLUMBING"
HDL_TAP"TRUE";
"S \NAC"
BN"1"14;
"B \NAC \NWC"17;
%"CTAP"
"1","(3825,-2725)","0","standard","I164";
;
CDS_LIB"standard"
BODY_TYPE"PLUMBING"
HDL_TAP"TRUE";
"S \NAC"
BN"0"14;
"B \NAC \NWC"17;
%"P2V5"
"1","(1175,-4475)","0","cnpower","I165";
;
CDS_LIB"cnpower"
SIZE"1B"
BODY_TYPE"PLUMBING"
HDL_POWER"P2V5";
"A<SIZE-1..0>\NAC"
VHDL_INIT"1"8;
%"P2V5"
"1","(5975,-2400)","0","cnpower","I166";
;
HDL_POWER"P2V5"
BODY_TYPE"PLUMBING"
SIZE"1B"
CDS_LIB"cnpower";
"A<SIZE-1..0>\NAC"
VHDL_INIT"1"9;
%"cap_np"
"1","(1150,-2725)","0","ocad_parts_lib","I167";
;
CDS_LOCATION"C92"
$LOCATION"C92"
VALUE"0.1UF"
VOLTAGE"25V"
CDS_LIB"ocad_parts_lib"
JEDEC_TYPE"cap0805"
SOURCE_PACKAGE"CAP_NP"
AVAILABILITY"In Stock"
DISTRIBUTOR"Digi-Key"
DISTRIBUTOR_PARTNUMBER"445-8173-1-ND"
MANUFACTURER"TDK CORP"
MPN"CGJ4J2X7R1E104K125AA "
PSPICE"C"
DESCRIPTION"CAP 0.1__F __10% 25V Ceramic Capacitor X7R 0805 "
PART_TYPE"Ceramic"
PART_NUMBER"445-8173-1-ND"
ROOM"MAIN_PWR"
ALT_SYMBOLS""
LAST_EDIT_BY"SNF"
CLASS"DISCRETE"
SEC"1";
"1"
$PN"1"1;
"2"
$PN"2"7;
%"cap_np"
"1","(4025,-2700)","0","ocad_parts_lib","I168";
;
CDS_LOCATION"C92"
$LOCATION"C92"
VOLTAGE"25V"
VALUE"0.1UF"
CDS_LIB"ocad_parts_lib"
SEC"1"
CLASS"DISCRETE"
LAST_EDIT_BY"SNF"
ALT_SYMBOLS""
ROOM"MAIN_PWR"
PART_NUMBER"445-8173-1-ND"
PART_TYPE"Ceramic"
DESCRIPTION"CAP 0.1__F __10% 25V Ceramic Capacitor X7R 0805 "
PSPICE"C"
MPN"CGJ4J2X7R1E104K125AA "
MANUFACTURER"TDK CORP"
DISTRIBUTOR_PARTNUMBER"445-8173-1-ND"
DISTRIBUTOR"Digi-Key"
AVAILABILITY"In Stock"
SOURCE_PACKAGE"CAP_NP"
JEDEC_TYPE"cap0805";
"1"
$PN"1"14;
"2"
$PN"2"2;
%"cap_np"
"1","(2450,-4925)","0","ocad_parts_lib","I170";
;
CDS_LOCATION"C50"
$LOCATION"C50"
VALUE"47UF"
VOLTAGE"6.3V"
SEC"1"
CLASS"DISCRETE"
LAST_EDIT_BY"SNF"
ALT_SYMBOLS""
PART_NUMBER"GRM21BR60J476ME15K"
PART_TYPE"Ceramic"
DESCRIPTION"CAP CER 47UF 6.3V X5R 0805"
TOLERANCE"20%"
PSPICE"C"
MPN"GRM21BR60J476ME15K"
MANUFACTURER"Murata"
DISTRIBUTOR_PARTNUMBER"490-14660-2-ND"
DISTRIBUTOR"Digi-Key"
AVAILABILITY"In Stock"
ROOM"VP3V3"
SOURCE_PACKAGE"CAP_NP"
JEDEC_TYPE"cap0805"
CDS_LIB"ocad_parts_lib";
"1"
$PN"1"8;
"2"
$PN"2"11,10;
%"cap_np"
"1","(1300,-4925)","0","ocad_parts_lib","I171";
;
CDS_LOCATION"C69"
$LOCATION"C69"
VOLTAGE"25V"
VALUE"0.1UF"
CDS_LIB"ocad_parts_lib"
JEDEC_TYPE"cap0402"
SOURCE_PACKAGE"CAP_NP"
REUSE_ID"18"
AVAILABILITY"In Stock"
DISTRIBUTOR"Digi-Key"
DISTRIBUTOR_PARTNUMBER"445-7348-2-ND"
MANUFACTURER"TDK CORP"
MPN"C1005X7R1E104K050BB "
PSPICE"C"
DESCRIPTION"CAP 0.1__F __10% 25V Ceramic Capacitor X7R 0402 "
PART_TYPE"Ceramic"
PART_NUMBER"445-7348-2-ND"
ROOM"VCC3V3I_V"
REUSE_ANNOTATE"TRUE"
ALT_SYMBOLS""
LAST_EDIT_BY"SNF"
CLASS"DISCRETE"
SEC"1";
"1"
$PN"1"8;
"2"
$PN"2"11,10;
%"cap_np"
"1","(1600,-4925)","0","ocad_parts_lib","I172";
;
CDS_LOCATION"C71"
$LOCATION"C71"
VALUE"47UF"
VOLTAGE"6.3V"
SEC"1"
CLASS"DISCRETE"
LAST_EDIT_BY"SNF"
ALT_SYMBOLS""
AVAILABILITY"In Stock"
DISTRIBUTOR"Digi-Key"
DISTRIBUTOR_PARTNUMBER"490-14660-2-ND"
MANUFACTURER"Murata"
MPN"GRM21BR60J476ME15K"
PSPICE"C"
TOLERANCE"20%"
DESCRIPTION"CAP CER 47UF 6.3V X5R 0805"
PART_TYPE"Ceramic"
PART_NUMBER"GRM21BR60J476ME15K"
ROOM"VCC3V3I_V"
SOURCE_PACKAGE"CAP_NP"
JEDEC_TYPE"cap0805"
CDS_LIB"ocad_parts_lib";
"1"
$PN"1"8;
"2"
$PN"2"11,10;
%"cap_np"
"1","(1875,-4925)","0","ocad_parts_lib","I173";
;
CDS_LOCATION"C81"
$LOCATION"C81"
VALUE"47UF"
VOLTAGE"6.3V"
SEC"1"
CLASS"DISCRETE"
LAST_EDIT_BY"SNF"
ALT_SYMBOLS""
ROOM"VCC3V3I_V"
PART_NUMBER"GRM21BR60J476ME15K"
PART_TYPE"Ceramic"
DESCRIPTION"CAP CER 47UF 6.3V X5R 0805"
TOLERANCE"20%"
PSPICE"C"
MPN"GRM21BR60J476ME15K"
MANUFACTURER"Murata"
DISTRIBUTOR_PARTNUMBER"490-14660-2-ND"
DISTRIBUTOR"Digi-Key"
AVAILABILITY"In Stock"
SOURCE_PACKAGE"CAP_NP"
JEDEC_TYPE"cap0805"
CDS_LIB"ocad_parts_lib";
"1"
$PN"1"8;
"2"
$PN"2"11,10;
%"gnd"
"1","(2125,-5475)","0","mtca_interface_board","I174";
;
CDS_LIB"mtca_interface_board"
HDL_POWER"GND";
"HOTSPOT_0"11,10;
%"cap_np"
"1","(2175,-4925)","0","ocad_parts_lib","I175";
;
CDS_LOCATION"C82"
$LOCATION"C82"
VOLTAGE"6.3V"
VALUE"47UF"
SEC"1"
CLASS"DISCRETE"
LAST_EDIT_BY"SNF"
ALT_SYMBOLS""
ROOM"VCC3V3I_V"
AVAILABILITY"In Stock"
DISTRIBUTOR"Digi-Key"
DISTRIBUTOR_PARTNUMBER"490-14660-2-ND"
MANUFACTURER"Murata"
MPN"GRM21BR60J476ME15K"
PSPICE"C"
TOLERANCE"20%"
DESCRIPTION"CAP CER 47UF 6.3V X5R 0805"
PART_TYPE"Ceramic"
PART_NUMBER"GRM21BR60J476ME15K"
SOURCE_PACKAGE"CAP_NP"
JEDEC_TYPE"cap0805"
CDS_LIB"ocad_parts_lib";
"1"
$PN"1"8;
"2"
$PN"2"11,10;
%"led green 0603_0"
"1","(2800,-5100)","3","ocad_parts_lib","I176";
;
CDS_LOCATION"D7"
$LOCATION"D7"
VALUE"Green"
LEDCOLOR"Green"
MPN"LNJ326W83RA"
MANUFACTURER"Panasonic"
DISTRIBUTOR_PARTNUMBER"P13485CT-ND"
DISTRIBUTOR"Digikey"
DATASHEET"C:\EMA\CISQuickStart\Technical_Datasheets\Panasonic\ATA7000CE271.pdf"
DESCRIPTION"LED GREEN 0603 SMD"
SOURCE_PACKAGE"LED GREEN 0603_0"
JEDEC_TYPE"LEDC1608X80N"
CDS_LIB"ocad_parts_lib"
SEC"1"
PART_NUMBER"LNJ326W83RA";
"A"
$PN"2"23;
"K"
$PN"1"11,10;
%"r"
"1","(2850,-4825)","6","discrete","I177";
;
CDS_LOCATION"R71"
$LOCATION"R71"
VALUE"249 Ohm"
CDS_LIB"discrete"
JEDEC_TYPE"res0603"
SOURCE_PACKAGE"R"
REUSE_ANNOTATE"TRUE"
SEC"1"
PART_NUMBER"EMA-00003608";
"1"
$PN"1"23;
"2"
$PN"2"8;
%"testpoint"
"1","(3150,-5300)","5","testpoint","I178";
;
CDS_LOCATION"TP13"
$LOCATION"TP13"
SEC"1"
VALUE"5002 White"
ROOM"VCC3V3I_V"
DATASHEET"C:\EMA\CISQuickStart\Technical_Datasheets\Keystone Electronics\M55p51.pdf"
MANUFACTURER"Keystone Electronics"
MPN"5002"
DESCRIPTION"MISC, Testpoint, 5002 White, TH, 2.5x2.5x4.6 mm"
PART_TYPE"Testpoint"
PART_NUMBER"EMA-00001481V22"
SOURCE_PACKAGE"TESTPOINT"
JEDEC_TYPE"TP_KEYSTONE_5000A"
CDS_LIB"testpoint";
"TP"
$PN"1"11,10;
%"r"
"1","(825,-5100)","0","discrete","I182";
;
CDS_LOCATION"R86"
$LOCATION"R86"
VALUE"4.99k"
CDS_LIB"discrete"
JEDEC_TYPE"res0402"
SOURCE_PACKAGE"R"
REUSE_ANNOTATE"TRUE"
PART_NUMBER"ERJ-2RKF4991X"
PART_TYPE"Thick Film"
DESCRIPTION"RES SMD 4.99K OHM 1% 1/10W 0402"
POWER"1/10 W"
TOLERANCE"1%"
MPN"ERJ-2RKF4991X"
MANUFACTURER"Panasonic"
DISTRIBUTOR_PARTNUMBER"P4.99KLTR-ND"
DISTRIBUTOR"Digikey"
AVAILABILITY"In Stock"
ROOM"VP3V3"
SEC"1";
"1"
$PN"1"24;
"2"
$PN"2"11,10;
%"RSMD0402"
"1","(825,-4800)","1","cnpassive","I183";
;
$LOCATION"R?"
TOL"1%"
VALUE"6.2K"
PACK_TYPE"1/16W"
CDS_LIB"cnpassive"
SIZE"1B"
TOL_ON_OFF"ON"
POSTOL"RTOL%"
NEGTOL"RTOL%"
DIST"FLAT"
POWER"RMAX"
VOLTAGE"RVMAX"
SLOPE"RSMAX"
MAX_TEMP"RTMAX"
TC1"RTMPL"
TC2"RTMPQ";
"B <SIZE-1..0>\NAC"8;
"A <SIZE-1..0>\NAC"24;
%"ELCAPTAN"
"1","(900,-2775)","1","cnpassive","I184";
;
$LOCATION"C?"
VALUE"220UF"
DIST"FLAT"
IC"UNDEF"
KNEE"CBMAX"
MAX_TEMP"CTMAX"
NEGTOL"CTOL%"
POSTOL"CTOL%"
SIZE"1B"
SLOPE"CSMAX"
TC"0"
TOL_ON_OFF"ON"
CDS_LIB"cnpassive"
PACK_TYPE"SMD"
VOLTAGE"25V";
"A <SIZE-1..0>\NAC"
$PN"#"1;
"B <SIZE-1..0>\NAC"
$PN"#"6;
%"ELCAPTAN"
"1","(600,-2775)","1","cnpassive","I185";
;
$LOCATION"C?"
VALUE"220UF"
DIST"FLAT"
IC"UNDEF"
KNEE"CBMAX"
MAX_TEMP"CTMAX"
NEGTOL"CTOL%"
POSTOL"CTOL%"
SIZE"1B"
SLOPE"CSMAX"
TC"0"
TOL_ON_OFF"ON"
CDS_LIB"cnpassive"
PACK_TYPE"SMD"
VOLTAGE"25V";
"A <SIZE-1..0>\NAC"
$PN"#"1;
"B <SIZE-1..0>\NAC"
$PN"#"12;
%"gnd"
"1","(550,-2975)","0","mtca_interface_board","I186";
;
HDL_POWER"GND"
CDS_LIB"mtca_interface_board";
"HOTSPOT_0"12;
%"RES_SR"
"1","(5725,-2525)","2","cnpassive","I188";
;
$LOCATION"R?"
VALUE"0.05"
TOL"1%"
TC2"RTMPQ"
TC1"RTMPL"
MAX_TEMP"RTMAX"
SLOPE"RSMAX"
VOLTAGE"RVMAX"
POWER"RMAX"
DIST"FLAT"
NEGTOL"RTOL%"
POSTOL"RTOL%"
SIZE"1B"
TOL_ON_OFF"ON"
CDS_LIB"cnpassive"
PACK_TYPE"LVK12";
"C1 <SIZE-1..0>\NAC"9;
"S1 <SIZE-1..0>\NAC"21;
"S2 <SIZE-1..0>\NAC"15;
"C2 <SIZE-1..0>\NAC"14;
%"TANTPOLY"
"1","(6250,-2725)","1","bris_cds_discrete","I189";
;
$LOCATION"C?"
VALUE"220UF"
VOLTAGE"6.3V"
PACK_TYPE"SMD"
CDS_LIB"bris_cds_discrete"
TOL_ON_OFF"ON"
TC"0"
SLOPE"CSMAX"
SIZE"1B"
POSTOL"CTOL%"
NEGTOL"CTOL%"
MAX_TEMP"CTMAX"
KNEE"CBMAX"
IC"UNDEF"
DIST"FLAT"
CDS_LMAN_SYM_OUTLINE"-25,25,25,-25";
"A<SIZE-1..0>"
$PN"#"9;
"B<SIZE-1..0>"
$PN"#"13;
%"TANTPOLY"
"1","(6025,-2725)","1","bris_cds_discrete","I190";
;
$LOCATION"C?"
VALUE"220UF"
CDS_LMAN_SYM_OUTLINE"-25,25,25,-25"
DIST"FLAT"
IC"UNDEF"
KNEE"CBMAX"
MAX_TEMP"CTMAX"
NEGTOL"CTOL%"
POSTOL"CTOL%"
SIZE"1B"
SLOPE"CSMAX"
TC"0"
TOL_ON_OFF"ON"
CDS_LIB"bris_cds_discrete"
PACK_TYPE"SMD"
VOLTAGE"6.3V";
"A<SIZE-1..0>"
$PN"#"9;
"B<SIZE-1..0>"
$PN"#"13;
%"gnd"
"1","(6100,-2950)","0","mtca_interface_board","I191";
;
HDL_POWER"GND"
CDS_LIB"mtca_interface_board";
"HOTSPOT_0"13;
%"TANTPOLY"
"1","(4875,-2725)","1","bris_cds_discrete","I192";
;
$LOCATION"C?"
VALUE"220UF"
CDS_LMAN_SYM_OUTLINE"-25,25,25,-25"
DIST"FLAT"
IC"UNDEF"
KNEE"CBMAX"
MAX_TEMP"CTMAX"
NEGTOL"CTOL%"
POSTOL"CTOL%"
SIZE"1B"
SLOPE"CSMAX"
TC"0"
TOL_ON_OFF"ON"
CDS_LIB"bris_cds_discrete"
PACK_TYPE"SMD"
VOLTAGE"6.3V";
"A<SIZE-1..0>"
$PN"#"14;
"B<SIZE-1..0>"
$PN"#"2;
%"TANTPOLY"
"1","(4650,-2725)","1","bris_cds_discrete","I193";
;
$LOCATION"C?"
VALUE"220UF"
VOLTAGE"6.3V"
PACK_TYPE"SMD"
CDS_LIB"bris_cds_discrete"
TOL_ON_OFF"ON"
TC"0"
SLOPE"CSMAX"
SIZE"1B"
POSTOL"CTOL%"
NEGTOL"CTOL%"
MAX_TEMP"CTMAX"
KNEE"CBMAX"
IC"UNDEF"
DIST"FLAT"
CDS_LMAN_SYM_OUTLINE"-25,25,25,-25";
"A<SIZE-1..0>"
$PN"#"14;
"B<SIZE-1..0>"
$PN"#"2;
%"cap_np"
"1","(3925,-2350)","0","ocad_parts_lib","I194";
;
$LOCATION"?"
VOLTAGE"25V"
VALUE"0.1UF"
JEDEC_TYPE"cap0805"
SOURCE_PACKAGE"CAP_NP"
AVAILABILITY"In Stock"
DISTRIBUTOR"Digi-Key"
DISTRIBUTOR_PARTNUMBER"445-8173-1-ND"
MANUFACTURER"TDK CORP"
MPN"CGJ4J2X7R1E104K125AA "
PSPICE"C"
DESCRIPTION"CAP 0.1__F __10% 25V Ceramic Capacitor X7R 0805 "
PART_TYPE"Ceramic"
PART_NUMBER"445-8173-1-ND"
ROOM"MAIN_PWR"
ALT_SYMBOLS""
LAST_EDIT_BY"SNF"
CLASS"DISCRETE"
CDS_LIB"ocad_parts_lib";
"1"
$PN"?"20;
"2"
$PN"?"14;
%"RSMD0603"
"1","(3125,-2925)","1","cnpassive","I195";
;
$LOCATION"R?"
VALUE"75K"
TOL"1%"
SIZE"1B"
TOL_ON_OFF"ON"
POSTOL"RTOL%"
NEGTOL"RTOL%"
DIST"FLAT"
POWER"RMAX"
VOLTAGE"RVMAX"
SLOPE"RSMAX"
MAX_TEMP"RTMAX"
TC1"RTMPL"
TC2"RTMPQ"
CDS_LIB"cnpassive"
PACK_TYPE"1/10W";
"B <SIZE-1..0>\NAC"16;
"A <SIZE-1..0>\NAC"5;
END.
