uob-hep-cad/uob-hep-pc072/hardware/Cadence/top/mtca_interface_board_reocc/08_#20timing/sch_1/page2.csv

FILE_TYPE = CONNECTIVITY
{Allegro Design Entry HDL 24.1 P001 (4234998) 9/4/2024}
PAGE_NUMBER = 2
0"NC"
1"VP1V8\G"
2"GND\G"
3"GND\G"
4"GND\G"
5"GND\G"
6"GND\G"
7"GND\G"
8"VCC3V3\G"
9"P2V5\g"
10"AVDD\g"
11"VCC3V3\g"
12"GND\G"
13"P2V5\g"
14"GND\G"
15"DFF_REF_CLK_P"
16"DFF_REF_CLK_N"
17"I2C_SEL"
18"CLK_SEL1"
19"CLKIN3_P"
20"SCOPE_P"
21"REFCLK_OUT0_P"
22"REFCLK_OUT0_N"
23"REFCLK_OUT1_N"
24"REFCLK_OUT1_P"
25"CLKIN1_P"
26"CLKIN2_P"
27"CLKIN1_N"
28"CLK_SEL0"
29"XB"
30"VDDA_CLK"
31"CLK_I2C_SCL"
32"CLK_I2C_SDA"
33"CLK_TST_N"
34"CLK_TST_P"
35"CLKGEN_LOL"
36"CLKGEN_CLK_N<0>"
37"CLKGEN_CLK_P<0>"
38"CLKGEN_CLK_N<1>"
39"CLKGEN_CLK_P<1>"
40"FBCLK_N"
41"FBCLK_P"
42"CLKIN3_N"
43"CLKIN0_P"
44"CLKIN0_N"
45"XA"
46"VDDO_CLK"
48"CLKGEN_RST"
47"CLKGEN_RST"
49"FBCLK_N"
50"SFP2_CLKGEN_P"
51"SFP2_CLKGEN_N"
52"SFP0_CLKGEN_P"
53"CLK_I2C_SCL"
54"CLK_I2C_SDA"
55"CLKGEN_INTR"
56"VDD_CLK"
57"CLKGEN_IO<10..0>"
58"CLK_SEL0"
59"CLK_SEL1"
60"CLKGEN_LOL"
61"CLKGEN_RST"
62"CLKGEN_CLK_P<1..0>"
63"SCOPE_N"
64"CLKGEN_CLK_N<1..0>"
65"CLKGEN_INTR"
66"SFP0_CLKGEN_N"
67"FBCLK_P"
68"SFP1_CLKGEN_P"
69"SFP1_CLKGEN_N"
70"CLKIN2_N"
71"N02371"
72"UN$2$CAPCERSMDCL2$I366$B"
73"UN$2$CAPCERSMDCL2$I367$B"
%"vcc_bar"
1,"(625,-1075)","0","mtca_interface_board","131P"
CDS_LIB"mtca_interface_board"
HDL_POWER"VP1V8"
ROOM"CLK_GEN_X12"
HOTSPOT_01
%"gnd"
1,"(6550,-3575)","2","mtca_interface_board","133P"
CDS_LIB"mtca_interface_board"
HDL_POWER"GND"
ROOM"CLK_GEN_X12"
HOTSPOT_02
%"gnd"
1,"(2875,-3500)","2","mtca_interface_board","134P"
CDS_LIB"mtca_interface_board"
HDL_POWER"GND"
ROOM"CLK_GEN_X12"
HOTSPOT_03
%"cap_np_0"
1,"(1750,-2950)","3","ocad_parts_lib","259P"
$LOCATION"C31"
VALUE"0.1UF"
VOLTAGE"25V"
CDS_LIB"ocad_parts_lib"
CDS_LOCATION"C31"
JEDEC_TYPE"cap0402"
SOURCE_PACKAGE"CAP_NP_0"
AVAILABILITY"In Stock"
DISTRIBUTOR"Digi-Key"
DISTRIBUTOR_PARTNUMBER"445-7348-2-ND"
MANUFACTURER"TDK CORP"
DESIGNATORNAMEPROP"TIMING"
MPN"C1005X7R1E104K050BB "
PSPICE"C"
DESCRIPTION"CAP 0.1__F __10% 25V Ceramic Capacitor X7R 0402 "
PART_TYPE"Ceramic"
PART_NUMBER"445-7348-2-ND"
CLASS"DISCRETE"
REUSE_ANNOTATE"TRUE"
LAST_EDIT_BY"SNF"
SEC"1"
ALT_SYMBOLS""
ROOM"CLK_GEN_X12"
1
XNET_PINS"1"
$PN"1"68
2
XNET_PINS"1"
$PN"2"25
%"cap_np_0"
1,"(1750,-2800)","3","ocad_parts_lib","266P"
$LOCATION"C35"
VOLTAGE"25V"
VALUE"0.1UF"
JEDEC_TYPE"cap0402"
CDS_LOCATION"C35"
CDS_LIB"ocad_parts_lib"
SOURCE_PACKAGE"CAP_NP_0"
AVAILABILITY"In Stock"
DESIGNATORNAMEPROP"TIMING"
DISTRIBUTOR_PARTNUMBER"445-7348-2-ND"
DISTRIBUTOR"Digi-Key"
MPN"C1005X7R1E104K050BB "
MANUFACTURER"TDK CORP"
PSPICE"C"
PART_TYPE"Ceramic"
DESCRIPTION"CAP 0.1__F __10% 25V Ceramic Capacitor X7R 0402 "
PART_NUMBER"445-7348-2-ND"
REUSE_ANNOTATE"TRUE"
CLASS"DISCRETE"
LAST_EDIT_BY"SNF"
ALT_SYMBOLS""
SEC"1"
ROOM"CLK_GEN_X12"
1
XNET_PINS"1"
$PN"1"52
2
XNET_PINS"1"
$PN"2"43
%"ind"
1,"(975,-1250)","1","ind","268P"
VALUE"120 Ohm@100MHz"
$LOCATION"L10"
DISTRIBUTOR_PARTNUMBER"490-1011-2-ND"
DISTRIBUTOR"Digikey"
SOURCE_PACKAGE"IND"
JEDEC_TYPE"INDC1608X95N"
DESIGNATORNAMEPROP"TIMING"
CDS_LOCATION"L10"
CDS_LIB"ind"
MANUFACTURER"Murata Electronics"
SEC"1"
PART_NUMBER"BLM18AG121SN1D"
ROOM"CLK_GEN_X12"
1
$PN"1"1
2
$PN"2"56
%"r"
1,"(6875,-2950)","1","discrete","269P"
VALUE"499 Ohm"
$LOCATION"R22"
JEDEC_TYPE"res0402"
SOURCE_PACKAGE"R"
CDS_LOCATION"R22"
CDS_LIB"discrete"
PART_NUMBER"ERJ-2RKF4990X"
PART_TYPE"Thick Film"
DESCRIPTION"RES SMD 499 OHM 1% 1/10W 0402"
POWER"1/10 W"
TOLERANCE"1 %"
DESIGNATORNAMEPROP"TIMING"
MANUFACTURER"Panasonic"
MPN"ERJ-2RKF4990X"
DISTRIBUTOR"Digikey"
DISTRIBUTOR_PARTNUMBER"P499LTR-ND"
DATASHEET"C:\EMA\CISQuickStart\Technical_Datasheets\Panasonic\AOA0000CE2.pdf"
SEC"1"
ROOM"CLK_GEN_X12"
1
$PN"1"72
2
$PN"2"20
%"r"
1,"(2675,-2500)","3","discrete","270P"
$LOCATION"R129"
VALUE"4.99k"
CDS_LIB"discrete"
CDS_LOCATION"R129"
JEDEC_TYPE"res0402"
SOURCE_PACKAGE"R"
AVAILABILITY"In Stock"
DESIGNATORNAMEPROP"TIMING"
DISTRIBUTOR"Digikey"
DISTRIBUTOR_PARTNUMBER"P4.99KLTR-ND"
MANUFACTURER"Panasonic"
MPN"ERJ-2RKF4991X"
TOLERANCE"1%"
SEC"1"
REUSE_ANNOTATE"TRUE"
PART_NUMBER"ERJ-2RKF4991X"
PART_TYPE"Thick Film"
DESCRIPTION"RES SMD 4.99K OHM 1% 1/10W 0402"
POWER"1/10 W"
ROOM"CLK_GEN_X12"
1
$PN"1"6
2
$PN"2"71
%"cap_np_0"
1,"(1750,-3300)","1","ocad_parts_lib","276P"
$LOCATION"C33"
VALUE"0.1UF"
VOLTAGE"25V"
JEDEC_TYPE"cap0402"
CDS_LOCATION"C33"
CDS_LIB"ocad_parts_lib"
SOURCE_PACKAGE"CAP_NP_0"
DESIGNATORNAMEPROP"TIMING"
AVAILABILITY"In Stock"
DISTRIBUTOR_PARTNUMBER"445-7348-2-ND"
DISTRIBUTOR"Digi-Key"
MANUFACTURER"TDK CORP"
MPN"C1005X7R1E104K050BB "
PSPICE"C"
DESCRIPTION"CAP 0.1__F __10% 25V Ceramic Capacitor X7R 0402 "
PART_TYPE"Ceramic"
PART_NUMBER"445-7348-2-ND"
REUSE_ANNOTATE"TRUE"
CLASS"DISCRETE"
LAST_EDIT_BY"SNF"
ALT_SYMBOLS""
SEC"1"
ROOM"CLK_GEN_X12"
1
XNET_PINS"1"
$PN"1"49
2
XNET_PINS"1"
$PN"2"42
%"r"
1,"(1575,-2325)","4","discrete","278P"
VALUE"4.99k"
$LOCATION"R123"
CDS_LIB"discrete"
CDS_LOCATION"R123"
DESIGNATORNAMEPROP"TIMING"
SOURCE_PACKAGE"R"
JEDEC_TYPE"res0402"
MPN"ERJ-2RKF4991X"
MANUFACTURER"Panasonic"
DISTRIBUTOR"Digikey"
AVAILABILITY"In Stock"
DISTRIBUTOR_PARTNUMBER"P4.99KLTR-ND"
TOLERANCE"1%"
POWER"1/10 W"
DESCRIPTION"RES SMD 4.99K OHM 1% 1/10W 0402"
PART_TYPE"Thick Film"
PART_NUMBER"ERJ-2RKF4991X"
REUSE_ANNOTATE"TRUE"
SEC"1"
ROOM"CLK_GEN_X12"
1
$PN"1"48,47
2
$PN"2"8
%"r"
1,"(1775,-2150)","3","discrete","279P"
$LOCATION"R17"
VALUE"4.99k"
JEDEC_TYPE"res0402"
CDS_LIB"discrete"
CDS_LOCATION"R17"
DESIGNATORNAMEPROP"TIMING"
MANUFACTURER"Panasonic"
DISTRIBUTOR_PARTNUMBER"P4.99KLTR-ND"
DISTRIBUTOR"Digikey"
AVAILABILITY"In Stock"
SOURCE_PACKAGE"R"
MPN"ERJ-2RKF4991X"
TOLERANCE"1%"
POWER"1/10 W"
DESCRIPTION"RES SMD 4.99K OHM 1% 1/10W 0402"
PART_TYPE"Thick Film"
SEC"1"
REUSE_ANNOTATE"TRUE"
PART_NUMBER"ERJ-2RKF4991X"
ROOM"CLK_GEN_X12"
1
$PN"1"8
2
$PN"2"17
%"si5395a-a-gm"
1,"(3800,-2900)","0","ocad_parts_lib","285P"
$LOCATION"U6"
ROOM"CLK_GEN_X12"
PART_NUMBER"SI5395A-A-GM"
SEC"1"
MPN"SI5395A-A-GM"
DESCRIPTION"IC CLOCK JITTER ATTEN 64-QFN"
PART_TYPE"Oscillator"
DISTRIBUTOR_PARTNUMBER"336-4802-ND"
MANUFACTURER"Silicon Labs"
DESIGNATORNAMEPROP"TIMING"
JEDEC_TYPE"QFN_64"
SOURCE_PACKAGE"SI5395A-A-GM"
AVAILABILITY"533"
PRICE"1"
DISTRIBUTOR"Digi-Key"
CDS_LIB"ocad_parts_lib"
CDS_LOCATION"U6"
VALUE"SI5395A-A-GM"
OUT1
$PN"28"24
IN1
$PN"1"25
IN2
$PN"14"26
OUT2
$PN"31"0
OUT3
$PN"35"0
IN1B \B
$PN"2"27
IN_SEL0
$PN"3"28
IN_SEL1
$PN"4"18
RSVD
$PN"5"0
RSTB \B
$PN"6"48,47
X1/NC
$PN"7"0
XA/NC
$PN"8"45
XB/NC
$PN"9"29
X2/NC
$PN"10"0
OEB \B
$PN"11"71
INTRB
$PN"12"55
VDDA
$PN"13"30
IN2B \B
$PN"15"70
SCLK
$PN"16"31
A1/SDO
$PN"17"6
SDA/SDIO
$PN"18"32
A0/CSB \B
$PN"19"6
OUT0AB
$PN"20"0
OUT0A
$PN"21"0
VDDO0
$PN"22"46
OUT0B
$PN"23"22
OUT0
$PN"24"21
FDEC
$PN"25"3
VDDO1
$PN"26"46
OUT1B
$PN"27"23
VDDO2
$PN"29"46
OUT2B
$PN"30"0
VDD0
$PN"32"56
VDDO3
$PN"33"46
OUT3B
$PN"34"0
VDDO4
$PN"36"46
OUT4B
$PN"37"16
OUT4
$PN"38"15
I2C_SEL
$PN"39"17
VDDO5
$PN"40"46
OUT5B
$PN"41"33
OUT5
$PN"42"34
VDDO6
$PN"43"46
OUT6B
$PN"44"0
OUT6
$PN"45"0
VDD1
$PN"46"56
LOLB
$PN"47"35
FINC
$PN"48"3
VDDO7
$PN"49"46
OUT7B
$PN"50"36
OUT7
$PN"51"37
VDDO8
$PN"52"46
OUT8B
$PN"53"38
OUT8
$PN"54"39
OUT9B
$PN"55"0
OUT9
$PN"56"0
VDDO9
$PN"57"46
OUT9AB
$PN"58"40
OUT9A
$PN"59"41
VDD2
$PN"60"56
IN3/FB_IN
$PN"61"19
IN3B/FB_INB \B
$PN"62"42
IN0
$PN"63"43
IN0B \B
$PN"64"44
GND_PAD
$PN"65"5
%"cap_np_0"
1,"(1750,-2850)","1","ocad_parts_lib","286P"
$LOCATION"C36"
VOLTAGE"25V"
VALUE"0.1UF"
CDS_LOCATION"C36"
CDS_LIB"ocad_parts_lib"
JEDEC_TYPE"cap0402"
SOURCE_PACKAGE"CAP_NP_0"
REUSE_ANNOTATE"TRUE"
PART_NUMBER"445-7348-2-ND"
PART_TYPE"Ceramic"
DESIGNATORNAMEPROP"TIMING"
PSPICE"C"
DESCRIPTION"CAP 0.1__F __10% 25V Ceramic Capacitor X7R 0402 "
MANUFACTURER"TDK CORP"
MPN"C1005X7R1E104K050BB "
DISTRIBUTOR_PARTNUMBER"445-7348-2-ND"
AVAILABILITY"In Stock"
DISTRIBUTOR"Digi-Key"
LAST_EDIT_BY"SNF"
CLASS"DISCRETE"
SEC"1"
ALT_SYMBOLS""
ROOM"CLK_GEN_X12"
1
XNET_PINS"1"
$PN"1"66
2
XNET_PINS"1"
$PN"2"44
%"r"
1,"(6875,-3000)","3","discrete","288P"
VALUE"499 Ohm"
$LOCATION"R21"
JEDEC_TYPE"res0402"
SOURCE_PACKAGE"R"
PART_NUMBER"ERJ-2RKF4990X"
CDS_LIB"discrete"
CDS_LOCATION"R21"
PART_TYPE"Thick Film"
DESCRIPTION"RES SMD 499 OHM 1% 1/10W 0402"
POWER"1/10 W"
TOLERANCE"1 %"
MPN"ERJ-2RKF4990X"
DESIGNATORNAMEPROP"TIMING"
MANUFACTURER"Panasonic"
DISTRIBUTOR_PARTNUMBER"P499LTR-ND"
DISTRIBUTOR"Digikey"
DATASHEET"C:\EMA\CISQuickStart\Technical_Datasheets\Panasonic\AOA0000CE2.pdf"
SEC"1"
ROOM"CLK_GEN_X12"
1
$PN"1"73
2
$PN"2"63
%"cap_np_0"
1,"(1750,-3000)","1","ocad_parts_lib","290P"
$LOCATION"C28"
VALUE"0.1UF"
VOLTAGE"25V"
CDS_LOCATION"C28"
CDS_LIB"ocad_parts_lib"
JEDEC_TYPE"cap0402"
SOURCE_PACKAGE"CAP_NP_0"
REUSE_ANNOTATE"TRUE"
PART_NUMBER"445-7348-2-ND"
PART_TYPE"Ceramic"
DESCRIPTION"CAP 0.1__F __10% 25V Ceramic Capacitor X7R 0402 "
PSPICE"C"
MPN"C1005X7R1E104K050BB "
DESIGNATORNAMEPROP"TIMING"
DISTRIBUTOR_PARTNUMBER"445-7348-2-ND"
MANUFACTURER"TDK CORP"
AVAILABILITY"In Stock"
DISTRIBUTOR"Digi-Key"
CLASS"DISCRETE"
LAST_EDIT_BY"SNF"
ALT_SYMBOLS""
SEC"1"
ROOM"CLK_GEN_X12"
1
XNET_PINS"1"
$PN"1"69
2
XNET_PINS"1"
$PN"2"27
%"r"
1,"(6375,-3250)","0","discrete","296P"
VALUE"49.9"
$LOCATION"R20"
ROOM"CLK_GEN_X12"
SEC"1"
PART_NUMBER"311-49.9LRCT-ND"
PART_TYPE"Thick Film"
DESCRIPTION"RES SMD 49.9 OHM 1% 1/16W 0402"
TOLERANCE"1%"
POWER"1/10W"
MPN"RC0402FR-0749R9L"
MANUFACTURER"Yageo"
DISTRIBUTOR_PARTNUMBER"311-49.9LRCT-ND"
DISTRIBUTOR"Digikey"
SOURCE_PACKAGE"R"
DESIGNATORNAMEPROP"TIMING"
CDS_LIB"discrete"
CDS_LOCATION"R20"
JEDEC_TYPE"res0402"
1
$PN"1"73
2
$PN"2"2
%"r"
1,"(2275,-3275)","1","discrete","298P"
$LOCATION"R30"
SEC"1"
PART_NUMBER"ERJ-2RKF1000X"
DESCRIPTION"RES SMD 100 OHM 1% 1/10W 0402"
POWER"1/10W"
PART_TYPE"Thick Film"
TOLERANCE"1%"
MPN"ERJ-2RKF1000X"
MANUFACTURER"Panasonic"
DISTRIBUTOR_PARTNUMBER"P100LCT-ND"
DISTRIBUTOR"Digikey"
DESIGNATORNAMEPROP"TIMING"
CDS_LOCATION"R30"
CDS_LIB"discrete"
DATASHEET"C:\EMA\CISQuickStart\Technical_Datasheets\Panasonic\AOA0000CE2.PDF"
SOURCE_PACKAGE"R"
JEDEC_TYPE"res0402"
VALUE"100"
ROOM"CLK_GEN_X12"
1
$PN"1"19
2
$PN"2"42
%"r"
1,"(6625,-3250)","0","discrete","299P"
VALUE"49.9"
$LOCATION"R23"
JEDEC_TYPE"res0402"
CDS_LOCATION"R23"
CDS_LIB"discrete"
DESIGNATORNAMEPROP"TIMING"
DESCRIPTION"RES SMD 49.9 OHM 1% 1/16W 0402"
PART_TYPE"Thick Film"
PART_NUMBER"311-49.9LRCT-ND"
SOURCE_PACKAGE"R"
POWER"1/10W"
DISTRIBUTOR"Digikey"
DISTRIBUTOR_PARTNUMBER"311-49.9LRCT-ND"
MANUFACTURER"Yageo"
MPN"RC0402FR-0749R9L"
TOLERANCE"1%"
SEC"1"
ROOM"CLK_GEN_X12"
1
$PN"1"72
2
$PN"2"2
%"r"
1,"(2275,-2825)","1","discrete","301P"
$LOCATION"R27"
SEC"1"
PART_NUMBER"ERJ-2RKF1000X"
PART_TYPE"Thick Film"
DESCRIPTION"RES SMD 100 OHM 1% 1/10W 0402"
POWER"1/10W"
TOLERANCE"1%"
MPN"ERJ-2RKF1000X"
MANUFACTURER"Panasonic"
DISTRIBUTOR_PARTNUMBER"P100LCT-ND"
DISTRIBUTOR"Digikey"
DESIGNATORNAMEPROP"TIMING"
DATASHEET"C:\EMA\CISQuickStart\Technical_Datasheets\Panasonic\AOA0000CE2.PDF"
JEDEC_TYPE"res0402"
SOURCE_PACKAGE"R"
CDS_LIB"discrete"
CDS_LOCATION"R27"
VALUE"100"
ROOM"CLK_GEN_X12"
1
$PN"1"43
2
$PN"2"44
%"r"
1,"(2275,-2975)","1","discrete","302P"
$LOCATION"R25"
SEC"1"
DATASHEET"C:\EMA\CISQuickStart\Technical_Datasheets\Panasonic\AOA0000CE2.PDF"
MPN"ERJ-2RKF1000X"
MANUFACTURER"Panasonic"
DISTRIBUTOR_PARTNUMBER"P100LCT-ND"
DISTRIBUTOR"Digikey"
TOLERANCE"1%"
DESIGNATORNAMEPROP"TIMING"
DESCRIPTION"RES SMD 100 OHM 1% 1/10W 0402"
POWER"1/10W"
PART_NUMBER"ERJ-2RKF1000X"
PART_TYPE"Thick Film"
CDS_LOCATION"R25"
CDS_LIB"discrete"
JEDEC_TYPE"res0402"
SOURCE_PACKAGE"R"
VALUE"100"
ROOM"CLK_GEN_X12"
1
$PN"1"25
2
$PN"2"27
%"cap_np_0"
1,"(1750,-3250)","3","ocad_parts_lib","305P"
$LOCATION"C34"
VALUE"0.1UF"
VOLTAGE"25V"
CDS_LIB"ocad_parts_lib"
CDS_LOCATION"C34"
SOURCE_PACKAGE"CAP_NP_0"
JEDEC_TYPE"cap0402"
DESIGNATORNAMEPROP"TIMING"
REUSE_ANNOTATE"TRUE"
PART_TYPE"Ceramic"
PART_NUMBER"445-7348-2-ND"
DESCRIPTION"CAP 0.1__F __10% 25V Ceramic Capacitor X7R 0402 "
PSPICE"C"
MPN"C1005X7R1E104K050BB "
MANUFACTURER"TDK CORP"
DISTRIBUTOR_PARTNUMBER"445-7348-2-ND"
DISTRIBUTOR"Digi-Key"
AVAILABILITY"In Stock"
LAST_EDIT_BY"SNF"
CLASS"DISCRETE"
ALT_SYMBOLS""
SEC"1"
ROOM"CLK_GEN_X12"
1
XNET_PINS"1"
$PN"1"67
2
XNET_PINS"1"
$PN"2"19
%"gnd"
1,"(4825,-1525)","2","mtca_interface_board","44P"
CDS_LIB"mtca_interface_board"
HDL_POWER"GND"
ROOM"CLK_GEN_X12"
HOTSPOT_04
%"gnd"
1,"(3850,-4275)","2","mtca_interface_board","45P"
CDS_LIB"mtca_interface_board"
HDL_POWER"GND"
ROOM"CLK_GEN_X12"
HOTSPOT_05
%"gnd"
1,"(1950,-2450)","2","mtca_interface_board","47P"
CDS_LIB"mtca_interface_board"
HDL_POWER"GND"
ROOM"CLK_GEN_X12"
HOTSPOT_06
%"gnd"
1,"(725,-1775)","2","mtca_interface_board","8P"
CDS_LIB"mtca_interface_board"
HDL_POWER"GND"
ROOM"CLK_GEN_X12"
HOTSPOT_07
%"vcc_bar"
1,"(1525,-1925)","0","mtca_interface_board","9P"
CDS_LIB"mtca_interface_board"
HDL_POWER"VCC3V3"
ROOM"CLK_GEN_X12"
HOTSPOT_08
%"r"
1,"(2300,-3125)","1","discrete","I319"
CDS_LOCATION"R27"
$LOCATION"R27"
SEC"1"
PART_TYPE"Thick Film"
PART_NUMBER"ERJ-2RKF1000X"
DESCRIPTION"RES SMD 100 OHM 1% 1/10W 0402"
DISTRIBUTOR_PARTNUMBER"P100LCT-ND"
MANUFACTURER"Panasonic"
MPN"ERJ-2RKF1000X"
TOLERANCE"1%"
POWER"1/10W"
DISTRIBUTOR"Digikey"
DATASHEET"C:\EMA\CISQuickStart\Technical_Datasheets\Panasonic\AOA0000CE2.PDF"
SOURCE_PACKAGE"R"
JEDEC_TYPE"res0402"
DESIGNATORNAMEPROP"TIMING"
CDS_LIB"discrete"
VALUE"100"
ROOM"CLK_GEN_X12"
1
$PN"1"26
2
$PN"2"70
%"cap_np_0"
1,"(1775,-3100)","3","ocad_parts_lib","I320"
CDS_LOCATION"C35"
$LOCATION"C35"
VALUE"0.1UF"
VOLTAGE"25V"
CDS_LIB"ocad_parts_lib"
JEDEC_TYPE"cap0402"
SOURCE_PACKAGE"CAP_NP_0"
AVAILABILITY"In Stock"
DISTRIBUTOR"Digi-Key"
DISTRIBUTOR_PARTNUMBER"445-7348-2-ND"
MANUFACTURER"TDK CORP"
MPN"C1005X7R1E104K050BB "
PSPICE"C"
DESCRIPTION"CAP 0.1__F __10% 25V Ceramic Capacitor X7R 0402 "
PART_NUMBER"445-7348-2-ND"
PART_TYPE"Ceramic"
REUSE_ANNOTATE"TRUE"
CLASS"DISCRETE"
LAST_EDIT_BY"SNF"
ALT_SYMBOLS""
SEC"1"
DESIGNATORNAMEPROP"TIMING"
ROOM"CLK_GEN_X12"
1
XNET_PINS"1"
$PN"1"50
2
XNET_PINS"1"
$PN"2"26
%"cap_np_0"
1,"(1775,-3150)","1","ocad_parts_lib","I321"
CDS_LOCATION"C36"
$LOCATION"C36"
VALUE"0.1UF"
VOLTAGE"25V"
CDS_LIB"ocad_parts_lib"
DESIGNATORNAMEPROP"TIMING"
JEDEC_TYPE"cap0402"
SOURCE_PACKAGE"CAP_NP_0"
REUSE_ANNOTATE"TRUE"
PART_NUMBER"445-7348-2-ND"
PART_TYPE"Ceramic"
DESCRIPTION"CAP 0.1__F __10% 25V Ceramic Capacitor X7R 0402 "
PSPICE"C"
MPN"C1005X7R1E104K050BB "
MANUFACTURER"TDK CORP"
DISTRIBUTOR_PARTNUMBER"445-7348-2-ND"
DISTRIBUTOR"Digi-Key"
AVAILABILITY"In Stock"
CLASS"DISCRETE"
LAST_EDIT_BY"SNF"
ALT_SYMBOLS""
SEC"1"
ROOM"CLK_GEN_X12"
1
XNET_PINS"1"
$PN"1"51
2
XNET_PINS"1"
$PN"2"70
%"ind"
1,"(5800,-700)","1","ind","I327"
CDS_LOCATION"L2"
$LOCATION"L2"
VALUE"120 Ohm@100MHz"
SEC"1"
DESIGNATORNAMEPROP"TIMING"
DISTRIBUTOR"Digikey"
SOURCE_PACKAGE"IND"
JEDEC_TYPE"INDC1608X95N"
CDS_LIB"ind"
PART_NUMBER"BLM18AG121SN1D"
PART_TYPE"Ferrite Bead"
DESCRIPTION"FERRITE BEAD 120 OHM 0603 1LN"
RATING"0.8 A"
TOLERANCE"25 %"
DCRESISTANCE"180mOhm"
MPN"BLM18AG121SN1D"
MANUFACTURER"Murata Electronics"
DISTRIBUTOR_PARTNUMBER"490-1011-2-ND"
ROOM"CLK_GEN_X12"
1
$PN"1"46
2
$PN"2"9
%"P2V5"
1,"(6650,-575)","0","cnpower","I331"
CDS_LIB"cnpower"
SIZE"1B"
BODY_TYPE"PLUMBING"
HDL_POWER"P2V5"
ROOM"CLK_GEN_X12"
A<SIZE-1..0>\NAC
VHDL_INIT"1"9
%"PCOAX"
1,"(7750,-2850)","0","cnconnector","I332"
$LOCATION"PX?"
$SEC"?"
TYPE"U.FL-R-SMT-1(10)"
CDS_LIB"cnconnector"
NEEDS_NO_SIZE"TRUE"
DESIGNATORNAMEPROP"TIMING"
ROOM"CLK_GEN_X12"
A\NAC20
%"PCOAX"
1,"(7750,-3100)","0","cnconnector","I333"
$LOCATION"PX?"
$SEC"?"
TYPE"U.FL-R-SMT-1(10)"
NEEDS_NO_SIZE"TRUE"
CDS_LIB"cnconnector"
DESIGNATORNAMEPROP"TIMING"
ROOM"CLK_GEN_X12"
A\NAC63
%"9 MERGE"
1,"(7650,-1600)","0","standard","I340"
CDS_LIB"standard"
NEEDS_NO_SIZE"TRUE"
BODY_TYPE"PLUMBING"
HDL_CONCAT"TRUE"
ROOM"CLK_GEN_X12"
A\NWC\NAC53
B\NWC\NAC54
C\NWC\NAC58
D\NWC\NAC59
E\NWC\NAC65
F\NWC\NAC60
G\NWC\NAC61
H\NWC\NAC62
I\NWC\NAC64
Y\NWC\NAC57
%"OSC_6P_ENDIS_OUTP_OUTN"
1,"(2350,-3675)","0","cndiscrete","I341"
$LOCATION"QZ?"
$SEC"?"
TYPE"SIT5021AI-2DE-25E-50.000000"
ROOM"CLK_GEN_X12"
DESIGNATORNAMEPROP"TIMING"
CDS_LIB"cndiscrete"
PACK_TYPE"145"
POWER_GROUP"VDD=AVDD"
VALUE"50MHZ"
OUTN \B29
OUTP45
ENDIS10
%"AVDD"
1,"(1725,-3525)","0","cnpower","I342"
CDS_LIB"cnpower"
SIZE"1B"
BODY_TYPE"PLUMBING"
HDL_POWER"AVDD"
ROOM"CLK_GEN_X12"
A<SIZE-1..0>\NAC
VHDL_INIT"1"10
%"ind"
1,"(1025,-3625)","1","ind","I346"
VALUE"120 Ohm@100MHz"
$LOCATION"L2"
DCRESISTANCE"180mOhm"
TOLERANCE"25 %"
RATING"0.8 A"
DESCRIPTION"FERRITE BEAD 120 OHM 0603 1LN"
MPN"BLM18AG121SN1D"
MANUFACTURER"Murata Electronics"
DISTRIBUTOR_PARTNUMBER"490-1011-2-ND"
DISTRIBUTOR"Digikey"
SOURCE_PACKAGE"IND"
JEDEC_TYPE"INDC1608X95N"
DESIGNATORNAMEPROP"TIMING"
PART_TYPE"Ferrite Bead"
SEC"1"
PART_NUMBER"BLM18AG121SN1D"
CDS_LOCATION"L2"
CDS_LIB"ind"
ROOM"CLK_GEN_X12"
1
$PN"1"13
2
$PN"2"10
%"vcc_bar"
1,"(925,-175)","0","mtca_interface_board","I347"
CDS_LIB"mtca_interface_board"
HDL_POWER"VCC3V3"
ROOM"CLK_GEN_X12"
HOTSPOT_011
%"gnd"
1,"(775,-4150)","2","mtca_interface_board","I349"
CDS_LIB"mtca_interface_board"
HDL_POWER"GND"
ROOM"CLK_GEN_X12"
HOTSPOT_012
%"r"
1,"(2725,-3850)","1","discrete","I350"
CDS_LOCATION"R30"
$LOCATION"R30"
VALUE"100"
DESIGNATORNAMEPROP"TIMING"
CDS_LIB"discrete"
SOURCE_PACKAGE"R"
JEDEC_TYPE"res0402"
DISTRIBUTOR"Digikey"
DATASHEET"C:\EMA\CISQuickStart\Technical_Datasheets\Panasonic\AOA0000CE2.PDF"
DISTRIBUTOR_PARTNUMBER"P100LCT-ND"
POWER"1/10W"
DESCRIPTION"RES SMD 100 OHM 1% 1/10W 0402"
TOLERANCE"1%"
PART_NUMBER"ERJ-2RKF1000X"
PART_TYPE"Thick Film"
MPN"ERJ-2RKF1000X"
MANUFACTURER"Panasonic"
SEC"1"
ROOM"CLK_GEN_X12"
1
$PN"1"29
2
$PN"2"45
%"IOPORT"
1,"(8375,-1600)","0","standard","I351"
CDS_LIB"standard"
OFFPAGE"TRUE"
ROOM"CLK_GEN_X12"
A
HDL_PORT"INOUT"
VHDL_PORT"INOUT"57
%"P2V5"
1,"(725,-3450)","0","cnpower","I352"
SIZE"1B"
CDS_LIB"cnpower"
BODY_TYPE"PLUMBING"
HDL_POWER"P2V5"
ROOM"CLK_GEN_X12"
A<SIZE-1..0>\NAC
VHDL_INIT"1"13
%"CAPCERSMDCL2"
1,"(2950,-1450)","1","cnpassive","I353"
$LOCATION"C?"
$SEC"?"
VALUE"100NF"
VOLTAGE"16V_GEN"
CDS_LIB"cnpassive"
SIZE"1"
DESIGNATORNAMEPROP"TIMING"
PACK_TYPE"0402"
ROOM"CLK_GEN_X12"
A <SIZE-1..0>\NAC
$PN"#"7
B <SIZE-1..0>\NAC
$PN"#"56
%"CAPCERSMDCL2"
1,"(1575,-1425)","1","cnpassive","I354"
$LOCATION"C?"
$SEC"?"
VALUE"1UF"
VOLTAGE"16V"
SIZE"1"
CDS_LIB"cnpassive"
DESIGNATORNAMEPROP"TIMING"
PACK_TYPE"0402"
ROOM"CLK_GEN_X12"
A <SIZE-1..0>\NAC
$PN"#"7
B <SIZE-1..0>\NAC
$PN"#"56
%"CAPCERSMDCL2"
1,"(1850,-1425)","1","cnpassive","I355"
$LOCATION"C?"
$SEC"?"
VALUE"1UF"
VOLTAGE"16V"
CDS_LIB"cnpassive"
DESIGNATORNAMEPROP"TIMING"
SIZE"1"
PACK_TYPE"0402"
ROOM"CLK_GEN_X12"
A <SIZE-1..0>\NAC
$PN"#"7
B <SIZE-1..0>\NAC
$PN"#"56
%"CAPCERSMDCL2"
1,"(2125,-1425)","1","cnpassive","I356"
$LOCATION"C?"
$SEC"?"
VALUE"1UF"
VOLTAGE"16V"
CDS_LIB"cnpassive"
DESIGNATORNAMEPROP"TIMING"
SIZE"1"
PACK_TYPE"0402"
ROOM"CLK_GEN_X12"
A <SIZE-1..0>\NAC
$PN"#"7
B <SIZE-1..0>\NAC
$PN"#"56
%"CAPCERSMDCL2"
1,"(2675,-1425)","1","cnpassive","I357"
$LOCATION"C?"
$SEC"?"
VALUE"100NF"
VOLTAGE"16V_GEN"
CDS_LIB"cnpassive"
DESIGNATORNAMEPROP"TIMING"
SIZE"1"
PACK_TYPE"0402"
ROOM"CLK_GEN_X12"
A <SIZE-1..0>\NAC
$PN"#"7
B <SIZE-1..0>\NAC
$PN"#"56
%"CAPCERSMDCL2"
1,"(2375,-1425)","1","cnpassive","I358"
$LOCATION"C?"
$SEC"?"
VALUE"100NF"
VOLTAGE"16V_GEN"
CDS_LIB"cnpassive"
DESIGNATORNAMEPROP"TIMING"
SIZE"1"
PACK_TYPE"0402"
ROOM"CLK_GEN_X12"
A <SIZE-1..0>\NAC
$PN"#"7
B <SIZE-1..0>\NAC
$PN"#"56
%"CAPCERSMDCL2"
1,"(1875,-3825)","1","cnpassive","I359"
$LOCATION"C?"
$SEC"?"
VOLTAGE"16V_GEN"
VALUE"100NF"
SIZE"1"
CDS_LIB"cnpassive"
DESIGNATORNAMEPROP"TIMING"
PACK_TYPE"0402"
ROOM"CLK_GEN_X12"
A <SIZE-1..0>\NAC
$PN"#"12
B <SIZE-1..0>\NAC
$PN"#"10
%"CAPCERSMDCL2"
1,"(1625,-3825)","1","cnpassive","I360"
$LOCATION"C?"
$SEC"?"
VALUE"1UF"
VOLTAGE"16V"
SIZE"1"
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
VOLTAGE"6.3V"
CDS_LIB"cnpassive"
SIZE"1"
DESIGNATORNAMEPROP"TIMING"
PACK_TYPE"0603"
ROOM"CLK_GEN_X12"
A <SIZE-1..0>\NAC
$PN"#"14
B <SIZE-1..0>\NAC
$PN"#"11
%"gnd"
1,"(1025,-875)","2","mtca_interface_board","I390"
CDS_LIB"mtca_interface_board"
HDL_POWER"GND"
ROOM"CLK_GEN_X12"
HOTSPOT_014
END.
