uob-hep-cad/uob-hep-pc072/hardware/Cadence/top/mtca_interface_board_reocc/08_#20timing/sch_1/page3.csv

FILE_TYPE = CONNECTIVITY
{Allegro Design Entry HDL 24.1 P001 (4234998) 9/4/2024}
PAGE_NUMBER = 3
0"NC"
1"GND\G"
2"GND\g"
3"VCC3V3\g"
4"GND\g"
5"GND\g"
6"GND\g"
7"GND\g"
8"GND\g"
9"VDD_CLK_BUFFER\G"
10"DC_REF_CLK_N<3>"
11"BP.REF_CLK_P<1>"
12"BP.REF_CLK_P<0>"
14"BP<180..0>"
13"BP<180..0>"
15"DC_REF_CLK_P<10>"
16"DC_REF_CLK_N<10>"
17"DC_REF_CLK_P<11>"
18"VDD_CLK_BUFFER\G"
19"BP.REF_CLK_P<4>"
20"BP.REF_CLK_N<3>"
21"BP.REF_CLK_P<3>"
22"BP.REF_CLK_N<2>"
23"BP.REF_CLK_P<2>"
24"BP.REF_CLK_N<4>"
25"BP.REF_CLK_N<1>"
26"SFP.TD_P<2..0>"
27"DC_REF_CLK_P<0>"
28"DC_REF_CLK_P<9>"
29"DC_REF_CLK_N<9>"
30"VDD_CLK_BUFFER\G"
31"RCLK_P1"
32"BP.REF_CLK_P<8>"
33"BP.REF_CLK_N<8>"
34"BP.REF_CLK_P<9>"
35"DC_REF_CLK_N<7>"
36"BP.REF_CLK_N<0>"
38"SFP<29..0>"
37"SFP<29..0>"
39"SFP.TD_N<2..0>"
40"SFP.RD_N<2..0>"
41"SFP.RD_P<2..0>"
42"SFP.LOS<2..0>"
43"SFP.TX_FAULT<2..0>"
44"SFP.TX_DISABLE<2..0>"
45"SFP.RATE_SELECT<2..0>"
46"DC_REF_CLK_N<11>"
47"REFCLK_OUT0_P"
48"REFCLK_OUT0_N"
49"RCLK_N0"
50"RCLK_P0"
51"DC_REF_CLK_N<1>"
52"DC_REF_CLK_P<1>"
53"DC_REF_CLK_N<0>"
54"DC_REF_CLK_P<2>"
55"DC_REF_CLK_P<4>"
56"REFCLK_OUT1_N"
57"REFCLK_OUT1_P"
58"DC_REF_CLK_N<8>"
59"BP.REF_CLK_N<11>"
60"BP.REF_CLK_P<11>"
61"BP.REF_CLK_N<10>"
62"BP.REF_CLK_P<10>"
63"BP.REF_CLK_N<9>"
64"DC_REF_CLK_P<8>"
65"RCLK_N1"
66"DC_REF_CLK_N<5>"
67"DC_REF_CLK_P<5>"
68"DC_REF_CLK_P<7>"
69"DC_REF_CLK_N<6>"
70"BP.REF_CLK_N<7>"
71"BP.REF_CLK_P<7>"
72"BP.REF_CLK_N<5>"
73"BP.REF_CLK_P<5>"
74"BP.REF_CLK_N<6>"
75"BP.REF_CLK_P<6>"
76"BP.REF_CLK_N<11..0>"
77"SFP.SDA<2..0>"
78"SFP.SCL<2..0>"
79"BP.REF_CLK_P<11..0>"
80"DC_REF_CLK_N<2>"
81"DC_REF_CLK_P<3>"
82"DC_REF_CLK_N<4>"
83"DC_REF_CLK_P<6>"
84"UN$3$ADCLK948$I244$INSEL"
85"UN$3$ADCLK948$I244$CLK1"
86"UN$3$ADCLK948$I244$CLK1$1"
87"UN$3$ADCLK948$I178$CLK1"
88"UN$3$ADCLK948$I178$Q$3"
89"UN$3$ADCLK948$I178$Q$2"
90"UN$3$ADCLK948$I244$Q"
91"UN$3$ADCLK948$I244$Q$1"
92"UN$3$ADCLK948$I244$Q$2"
93"UN$3$ADCLK948$I244$Q$3"
94"UN$3$ADCLK948$I178$Q$1"
95"UN$3$ADCLK948$I178$Q"
96"UN$3$ADCLK948$I244$VREF0"
97"UN$3$ADCLK948$I178$INSEL"
98"UN$3$ADCLK948$I178$CLK1$1"
99"UN$3$ADCLK948$I178$VREF0"
%"cap_np"
1,"(1875,-4300)","0","ocad_parts_lib","135P"
VALUE"1UF"
$LOCATION"C20"
VOLTAGE"6.3V"
ROOM"CLK_FO_0_5"
SEC"1"
CLASS"DISCRETE"
LAST_EDIT_BY"SNF"
PART_TYPE"Ceramic"
DESCRIPTION"CAP CER 1UF 6.3V X5R 0402"
PSPICE"C"
MPN"GRM152R60J105ME15D"
MANUFACTURER"Murata"
PART_NUMBER"GRM152R60J105ME15D"
JEDEC_TYPE"cap0402"
SOURCE_PACKAGE"CAP_NP"
CDS_LIB"ocad_parts_lib"
CDS_LOCATION"C20"
ALT_SYMBOLS""
AVAILABILITY"In Stock"
DISTRIBUTOR"Digi-Key"
DISTRIBUTOR_PARTNUMBER"490-10006-1-ND"
1
$PN"1"9
2
$PN"2"1
%"CAPCERSMDCL2"
1,"(3375,-4300)","1","cnpassive","136P"
VOLTAGE"16V_GEN"
VALUE"100NF"
$LOCATION"C166"
ROOM"CLK_FO_6_11"
PACK_TYPE"0402"
CDS_LOCATION"C166"
CDS_LIB"cnpassive"
SIZE"1"
JEDEC_TYPE"cap0402"
AVAILABILITY"In Stock"
DISTRIBUTOR"Digi-Key"
MANUFACTURER"TDK CORP"
DISTRIBUTOR_PARTNUMBER"445-7348-2-ND"
MPN"C1005X7R1E104K050BB "
PSPICE"C"
DESCRIPTION"CAP 0.1__F __10% 25V Ceramic Capacitor X7R 0402 "
PART_TYPE"Ceramic"
LAST_EDIT_BY"SNF"
ALT_SYMBOLS""
REUSE_ANNOTATE"TRUE"
CLASS"DISCRETE"
A <SIZE-1..0>\NAC
$PN"#"1
B <SIZE-1..0>\NAC
$PN"#"9
%"cap_np_0"
1,"(600,-2525)","3","ocad_parts_lib","137P"
VALUE"0.1UF"
$LOCATION"C26"
VOLTAGE"25V"
ROOM"CLK_FO_6_11"
DESCRIPTION"CAP 0.1__F __10% 25V Ceramic Capacitor X7R 0402 "
PSPICE"C"
MPN"C1005X7R1E104K050BB "
MANUFACTURER"TDK CORP"
DISTRIBUTOR_PARTNUMBER"445-7348-2-ND"
DISTRIBUTOR"Digi-Key"
AVAILABILITY"In Stock"
SOURCE_PACKAGE"CAP_NP_0"
JEDEC_TYPE"cap0402"
CDS_LOCATION"C26"
CDS_LIB"ocad_parts_lib"
LAST_EDIT_BY"SNF"
ALT_SYMBOLS""
SEC"1"
PART_NUMBER"445-7348-2-ND"
REUSE_ANNOTATE"TRUE"
CLASS"DISCRETE"
PART_TYPE"Ceramic"
1
XNET_PINS"1"
$PN"1"57
2
XNET_PINS"1"
$PN"2"31
%"cap_np"
1,"(750,-4300)","0","ocad_parts_lib","138P"
VALUE"10UF"
$LOCATION"C121"
VOLTAGE"10V"
ROOM"CLK_FO_0_5"
REUSE_ANNOTATE"TRUE"
ALT_SYMBOLS""
LAST_EDIT_BY"SNF"
SEC"1"
CLASS"DISCRETE"
AVAILABILITY"In Stock"
DISTRIBUTOR"Digi-Key"
DISTRIBUTOR_PARTNUMBER"490-10474-2-ND"
MANUFACTURER"Murata"
MPN"GRM188R61A106KE69D"
JEDEC_TYPE"cap0603"
SOURCE_PACKAGE"CAP_NP"
CDS_LOCATION"C121"
CDS_LIB"ocad_parts_lib"
PART_NUMBER"GRM188R61A106KE69D"
PART_TYPE"Ceramic"
PSPICE"C"
TOLERANCE"10%"
DESCRIPTION"CAP CER 10UF 10V X5R 0603"
1
$PN"1"9
2
$PN"2"1
%"cap_np"
1,"(3575,-4300)","0","ocad_parts_lib","141P"
$LOCATION"C9"
VALUE"1UF"
VOLTAGE"6.3V"
ROOM"CLK_FO_6_11"
PART_TYPE"Ceramic"
PART_NUMBER"GRM152R60J105ME15D"
JEDEC_TYPE"cap0402"
SOURCE_PACKAGE"CAP_NP"
CDS_LOCATION"C9"
CDS_LIB"ocad_parts_lib"
SEC"1"
CLASS"DISCRETE"
LAST_EDIT_BY"SNF"
ALT_SYMBOLS""
AVAILABILITY"In Stock"
DISTRIBUTOR"Digi-Key"
DISTRIBUTOR_PARTNUMBER"490-10006-1-ND"
MANUFACTURER"Murata"
MPN"GRM152R60J105ME15D"
PSPICE"C"
DESCRIPTION"CAP CER 1UF 6.3V X5R 0402"
1
$PN"1"9
2
$PN"2"1
%"CAPCERSMDCL2"
1,"(975,-4300)","1","cnpassive","142P"
VALUE"100NF"
VOLTAGE"16V_GEN"
$LOCATION"C37"
ROOM"CLK_FO_0_5"
PACK_TYPE"0402"
SIZE"1"
CDS_LIB"cnpassive"
CDS_LOCATION"C37"
JEDEC_TYPE"cap0402"
REUSE_ANNOTATE"TRUE"
PART_TYPE"Ceramic"
DESCRIPTION"CAP 0.1__F __10% 25V Ceramic Capacitor X7R 0402 "
PSPICE"C"
MPN"C1005X7R1E104K050BB "
DISTRIBUTOR_PARTNUMBER"445-7348-2-ND"
MANUFACTURER"TDK CORP"
AVAILABILITY"In Stock"
DISTRIBUTOR"Digi-Key"
LAST_EDIT_BY"SNF"
ALT_SYMBOLS""
CLASS"DISCRETE"
A <SIZE-1..0>\NAC
$PN"#"1
B <SIZE-1..0>\NAC
$PN"#"9
%"cap_np"
1,"(2450,-4300)","0","ocad_parts_lib","143P"
VALUE"10UF"
$LOCATION"C155"
VOLTAGE"10V"
ROOM"CLK_FO_6_11"
AVAILABILITY"In Stock"
CDS_LOCATION"C155"
CDS_LIB"ocad_parts_lib"
SOURCE_PACKAGE"CAP_NP"
JEDEC_TYPE"cap0603"
LAST_EDIT_BY"SNF"
CLASS"DISCRETE"
SEC"1"
ALT_SYMBOLS""
REUSE_ANNOTATE"TRUE"
PART_NUMBER"GRM188R61A106KE69D"
PART_TYPE"Ceramic"
DESCRIPTION"CAP CER 10UF 10V X5R 0603"
TOLERANCE"10%"
PSPICE"C"
MPN"GRM188R61A106KE69D"
MANUFACTURER"Murata"
DISTRIBUTOR_PARTNUMBER"490-10474-2-ND"
DISTRIBUTOR"Digi-Key"
1
$PN"1"9
2
$PN"2"1
%"CAPCERSMDCL2"
1,"(2100,-4300)","1","cnpassive","144P"
VOLTAGE"16V_GEN"
VALUE"100NF"
$LOCATION"C136"
ROOM"CLK_FO_0_5"
SIZE"1"
CDS_LIB"cnpassive"
CDS_LOCATION"C136"
JEDEC_TYPE"cap0402"
AVAILABILITY"In Stock"
DISTRIBUTOR"Digi-Key"
DISTRIBUTOR_PARTNUMBER"445-7348-2-ND"
MANUFACTURER"TDK CORP"
DESCRIPTION"CAP 0.1__F __10% 25V Ceramic Capacitor X7R 0402 "
PSPICE"C"
MPN"C1005X7R1E104K050BB "
PART_TYPE"Ceramic"
LAST_EDIT_BY"SNF"
ALT_SYMBOLS""
REUSE_ANNOTATE"TRUE"
CLASS"DISCRETE"
PACK_TYPE"0402"
A <SIZE-1..0>\NAC
$PN"#"1
B <SIZE-1..0>\NAC
$PN"#"9
%"cap_np_0"
1,"(625,-925)","1","ocad_parts_lib","145P"
VALUE"0.1UF"
VOLTAGE"25V"
$LOCATION"C11"
ROOM"CLK_FO_0_5"
REUSE_ANNOTATE"TRUE"
PART_TYPE"Ceramic"
DESCRIPTION"CAP 0.1__F __10% 25V Ceramic Capacitor X7R 0402 "
PSPICE"C"
MPN"C1005X7R1E104K050BB "
PART_NUMBER"445-7348-2-ND"
MANUFACTURER"TDK CORP"
DISTRIBUTOR_PARTNUMBER"445-7348-2-ND"
DISTRIBUTOR"Digi-Key"
AVAILABILITY"In Stock"
SOURCE_PACKAGE"CAP_NP_0"
JEDEC_TYPE"cap0402"
CDS_LOCATION"C11"
CDS_LIB"ocad_parts_lib"
CLASS"DISCRETE"
LAST_EDIT_BY"SNF"
ALT_SYMBOLS""
SEC"1"
1
XNET_PINS"1"
$PN"1"48
2
XNET_PINS"1"
$PN"2"49
%"cap_np_0"
1,"(600,-2575)","1","ocad_parts_lib","146P"
VALUE"0.1UF"
VOLTAGE"25V"
$LOCATION"C30"
ROOM"CLK_FO_6_11"
DISTRIBUTOR"Digi-Key"
DISTRIBUTOR_PARTNUMBER"445-7348-2-ND"
MANUFACTURER"TDK CORP"
MPN"C1005X7R1E104K050BB "
PSPICE"C"
DESCRIPTION"CAP 0.1__F __10% 25V Ceramic Capacitor X7R 0402 "
PART_TYPE"Ceramic"
REUSE_ANNOTATE"TRUE"
PART_NUMBER"445-7348-2-ND"
JEDEC_TYPE"cap0402"
SOURCE_PACKAGE"CAP_NP_0"
CDS_LOCATION"C30"
CDS_LIB"ocad_parts_lib"
ALT_SYMBOLS""
SEC"1"
CLASS"DISCRETE"
LAST_EDIT_BY"SNF"
AVAILABILITY"In Stock"
1
XNET_PINS"1"
$PN"1"56
2
XNET_PINS"1"
$PN"2"65
%"cap_np"
1,"(1200,-4300)","0","ocad_parts_lib","147P"
$LOCATION"C38"
VOLTAGE"6.3V"
VALUE"1UF"
ROOM"CLK_FO_0_5"
LAST_EDIT_BY"SNF"
CLASS"DISCRETE"
SEC"1"
PART_TYPE"Ceramic"
DESCRIPTION"CAP CER 1UF 6.3V X5R 0402"
PSPICE"C"
MPN"GRM152R60J105ME15D"
MANUFACTURER"Murata"
PART_NUMBER"GRM152R60J105ME15D"
SOURCE_PACKAGE"CAP_NP"
JEDEC_TYPE"cap0402"
CDS_LOCATION"C38"
CDS_LIB"ocad_parts_lib"
ALT_SYMBOLS""
AVAILABILITY"In Stock"
DISTRIBUTOR"Digi-Key"
DISTRIBUTOR_PARTNUMBER"490-10006-1-ND"
1
$PN"1"9
2
$PN"2"1
%"CAPCERSMDCL2"
1,"(2650,-4325)","1","cnpassive","148P"
$LOCATION"C148"
VALUE"100NF"
VOLTAGE"16V_GEN"
ROOM"CLK_FO_6_11"
PACK_TYPE"0402"
SIZE"1"
CDS_LIB"cnpassive"
CDS_LOCATION"C148"
REUSE_ANNOTATE"TRUE"
JEDEC_TYPE"cap0402"
PSPICE"C"
MPN"C1005X7R1E104K050BB "
DISTRIBUTOR_PARTNUMBER"445-7348-2-ND"
MANUFACTURER"TDK CORP"
DISTRIBUTOR"Digi-Key"
AVAILABILITY"In Stock"
LAST_EDIT_BY"SNF"
ALT_SYMBOLS""
CLASS"DISCRETE"
PART_TYPE"Ceramic"
DESCRIPTION"CAP 0.1__F __10% 25V Ceramic Capacitor X7R 0402 "
A <SIZE-1..0>\NAC
$PN"#"1
B <SIZE-1..0>\NAC
$PN"#"9
%"CAPCERSMDCL2"
1,"(3850,-4300)","1","cnpassive","151P"
VOLTAGE"16V_GEN"
VALUE"100NF"
$LOCATION"C8"
ROOM"CLK_FO_6_11"
SIZE"1"
CDS_LOCATION"C8"
CDS_LIB"cnpassive"
AVAILABILITY"In Stock"
JEDEC_TYPE"cap0402"
DISTRIBUTOR_PARTNUMBER"445-7348-2-ND"
DISTRIBUTOR"Digi-Key"
MPN"C1005X7R1E104K050BB "
MANUFACTURER"TDK CORP"
PSPICE"C"
PART_TYPE"Ceramic"
DESCRIPTION"CAP 0.1__F __10% 25V Ceramic Capacitor X7R 0402 "
REUSE_ANNOTATE"TRUE"
ALT_SYMBOLS""
CLASS"DISCRETE"
LAST_EDIT_BY"SNF"
PACK_TYPE"0402"
A <SIZE-1..0>\NAC
$PN"#"1
B <SIZE-1..0>\NAC
$PN"#"9
%"CAPCERSMDCL2"
1,"(1450,-4300)","1","cnpassive","152P"
VOLTAGE"16V_GEN"
VALUE"100NF"
$LOCATION"C135"
ROOM"CLK_FO_0_5"
PACK_TYPE"0402"
SIZE"1"
CDS_LIB"cnpassive"
CDS_LOCATION"C135"
JEDEC_TYPE"cap0402"
REUSE_ANNOTATE"TRUE"
PART_TYPE"Ceramic"
DESCRIPTION"CAP 0.1__F __10% 25V Ceramic Capacitor X7R 0402 "
PSPICE"C"
MPN"C1005X7R1E104K050BB "
MANUFACTURER"TDK CORP"
DISTRIBUTOR_PARTNUMBER"445-7348-2-ND"
DISTRIBUTOR"Digi-Key"
AVAILABILITY"In Stock"
ALT_SYMBOLS""
LAST_EDIT_BY"SNF"
CLASS"DISCRETE"
A <SIZE-1..0>\NAC
$PN"#"1
B <SIZE-1..0>\NAC
$PN"#"9
%"cap_np"
1,"(2900,-4300)","0","ocad_parts_lib","153P"
$LOCATION"C147"
VOLTAGE"6.3V"
VALUE"1UF"
ROOM"CLK_FO_6_11"
PART_TYPE"Ceramic"
PART_NUMBER"GRM152R60J105ME15D"
SOURCE_PACKAGE"CAP_NP"
JEDEC_TYPE"cap0402"
CDS_LIB"ocad_parts_lib"
CDS_LOCATION"C147"
LAST_EDIT_BY"SNF"
CLASS"DISCRETE"
SEC"1"
ALT_SYMBOLS""
AVAILABILITY"In Stock"
DISTRIBUTOR"Digi-Key"
DISTRIBUTOR_PARTNUMBER"490-10006-1-ND"
MANUFACTURER"Murata"
MPN"GRM152R60J105ME15D"
PSPICE"C"
DESCRIPTION"CAP CER 1UF 6.3V X5R 0402"
1
$PN"1"9
2
$PN"2"1
%"CAPCERSMDCL2"
1,"(1700,-4300)","1","cnpassive","154P"
VOLTAGE"16V_GEN"
VALUE"100NF"
$LOCATION"C19"
ROOM"CLK_FO_0_5"
PACK_TYPE"0402"
SIZE"1"
CDS_LIB"cnpassive"
CDS_LOCATION"C19"
JEDEC_TYPE"cap0402"
AVAILABILITY"In Stock"
DISTRIBUTOR"Digi-Key"
DISTRIBUTOR_PARTNUMBER"445-7348-2-ND"
MANUFACTURER"TDK CORP"
MPN"C1005X7R1E104K050BB "
PSPICE"C"
PART_TYPE"Ceramic"
DESCRIPTION"CAP 0.1__F __10% 25V Ceramic Capacitor X7R 0402 "
REUSE_ANNOTATE"TRUE"
ALT_SYMBOLS""
LAST_EDIT_BY"SNF"
CLASS"DISCRETE"
A <SIZE-1..0>\NAC
$PN"#"1
B <SIZE-1..0>\NAC
$PN"#"9
%"CAPCERSMDCL2"
1,"(3100,-4300)","1","cnpassive","155P"
VALUE"100NF"
VOLTAGE"16V_GEN"
$LOCATION"C165"
ROOM"CLK_FO_6_11"
PACK_TYPE"0402"
SIZE"1"
CDS_LOCATION"C165"
CDS_LIB"cnpassive"
JEDEC_TYPE"cap0402"
REUSE_ANNOTATE"TRUE"
DESCRIPTION"CAP 0.1__F __10% 25V Ceramic Capacitor X7R 0402 "
PART_TYPE"Ceramic"
MPN"C1005X7R1E104K050BB "
PSPICE"C"
MANUFACTURER"TDK CORP"
DISTRIBUTOR_PARTNUMBER"445-7348-2-ND"
DISTRIBUTOR"Digi-Key"
AVAILABILITY"In Stock"
CLASS"DISCRETE"
ALT_SYMBOLS""
LAST_EDIT_BY"SNF"
A <SIZE-1..0>\NAC
$PN"#"1
B <SIZE-1..0>\NAC
$PN"#"9
%"cap_np"
1,"(100,-4300)","0","ocad_parts_lib","157P"
$LOCATION"C112"
VALUE"10UF"
VOLTAGE"10V"
ROOM"CLK_FO_0_5"
SEC"1"
CLASS"DISCRETE"
LAST_EDIT_BY"SNF"
ALT_SYMBOLS""
DESCRIPTION"CAP CER 10UF 10V X5R 0603"
TOLERANCE"10%"
PSPICE"C"
PART_TYPE"Ceramic"
PART_NUMBER"GRM188R61A106KE69D"
REUSE_ANNOTATE"TRUE"
SOURCE_PACKAGE"CAP_NP"
JEDEC_TYPE"cap0603"
CDS_LIB"ocad_parts_lib"
CDS_LOCATION"C112"
AVAILABILITY"In Stock"
DISTRIBUTOR"Digi-Key"
DISTRIBUTOR_PARTNUMBER"490-10474-2-ND"
MANUFACTURER"Murata"
MPN"GRM188R61A106KE69D"
1
$PN"1"3
2
$PN"2"1
%"cap_np_0"
1,"(625,-875)","3","ocad_parts_lib","160P"
$LOCATION"C10"
VALUE"0.1UF"
VOLTAGE"25V"
ROOM"CLK_FO_0_5"
AVAILABILITY"In Stock"
DISTRIBUTOR"Digi-Key"
DISTRIBUTOR_PARTNUMBER"445-7348-2-ND"
MANUFACTURER"TDK CORP"
MPN"C1005X7R1E104K050BB "
PSPICE"C"
DESCRIPTION"CAP 0.1__F __10% 25V Ceramic Capacitor X7R 0402 "
PART_TYPE"Ceramic"
REUSE_ANNOTATE"TRUE"
SOURCE_PACKAGE"CAP_NP_0"
PART_NUMBER"445-7348-2-ND"
CDS_LIB"ocad_parts_lib"
CDS_LOCATION"C10"
JEDEC_TYPE"cap0402"
CLASS"DISCRETE"
LAST_EDIT_BY"SNF"
ALT_SYMBOLS""
SEC"1"
1
XNET_PINS"1"
$PN"1"47
2
XNET_PINS"1"
$PN"2"50
%"portboth-r_1"
1,"(7450,-1225)","2","mtca_interface_board","1P"
NAME"BP<180..0>"
CDS_LIB"mtca_interface_board"
HOTSPOT_0
PIN_NAME"BP<180..0>"
HDL_PORT"INOUT"14,13
%"gnd"
1,"(1875,-1850)","2","mtca_interface_board","39P"
ROOM"CLK_FO_0_5"
HDL_POWER"GND"
CDS_LIB"mtca_interface_board"
HOTSPOT_07
%"gnd"
1,"(150,-4650)","2","mtca_interface_board","40P"
ROOM"CLK_FO_0_5"
HDL_POWER"GND"
CDS_LIB"mtca_interface_board"
HOTSPOT_01
%"BUSWIDE_BTM_LEFT_RIP"
1,"(7125,-1350)","3","default","I165"
HDL_TAP"TRUE"
BODY_TYPE"PLUMBING"
CDS_LIB"default"
WIRE \NWC \NAC
BN"28..17"79
BUNDLE \NWC \NAC14,13
%"BUSWIDE_BTM_LEFT_RIP"
1,"(7125,-1400)","3","default","I166"
HDL_TAP"TRUE"
BODY_TYPE"PLUMBING"
CDS_LIB"default"
WIRE \NWC \NAC
BN"16..5"76
BUNDLE \NWC \NAC14,13
%"BUSWIDE_TOP_LEFT_RIP"
1,"(7175,-500)","0","default","I167"
HDL_TAP"TRUE"
BODY_TYPE"PLUMBING"
CDS_LIB"default"
WIRE \NWC \NAC
BN"29..27"45
BUNDLE \NWC \NAC38,37
%"BUSWIDE_TOP_LEFT_RIP"
1,"(7175,-600)","0","default","I168"
HDL_TAP"TRUE"
BODY_TYPE"PLUMBING"
CDS_LIB"default"
WIRE \NWC \NAC
BN"23..21"43
BUNDLE \NWC \NAC38,37
%"BUSWIDE_TOP_LEFT_RIP"
1,"(7175,-550)","0","default","I169"
HDL_TAP"TRUE"
BODY_TYPE"PLUMBING"
CDS_LIB"default"
WIRE \NWC \NAC
BN"26..24"44
BUNDLE \NWC \NAC38,37
%"BUSWIDE_TOP_LEFT_RIP"
1,"(7175,-700)","0","default","I170"
HDL_TAP"TRUE"
BODY_TYPE"PLUMBING"
CDS_LIB"default"
WIRE \NWC \NAC
BN"17..15"41
BUNDLE \NWC \NAC38,37
%"BUSWIDE_TOP_LEFT_RIP"
1,"(7175,-650)","0","default","I171"
HDL_TAP"TRUE"
BODY_TYPE"PLUMBING"
CDS_LIB"default"
WIRE \NWC \NAC
BN"20..18"42
BUNDLE \NWC \NAC38,37
%"BUSWIDE_TOP_LEFT_RIP"
1,"(7175,-750)","0","default","I172"
HDL_TAP"TRUE"
BODY_TYPE"PLUMBING"
CDS_LIB"default"
WIRE \NWC \NAC
BN"14..12"40
BUNDLE \NWC \NAC38,37
%"BUSWIDE_TOP_LEFT_RIP"
1,"(7175,-850)","0","default","I173"
HDL_TAP"TRUE"
BODY_TYPE"PLUMBING"
CDS_LIB"default"
WIRE \NWC \NAC
BN"8..6"39
BUNDLE \NWC \NAC38,37
%"BUSWIDE_TOP_LEFT_RIP"
1,"(7175,-800)","0","default","I174"
HDL_TAP"TRUE"
BODY_TYPE"PLUMBING"
CDS_LIB"default"
WIRE \NWC \NAC
BN"11..9"26
BUNDLE \NWC \NAC38,37
%"BUSWIDE_TOP_LEFT_RIP"
1,"(7175,-950)","0","default","I175"
HDL_TAP"TRUE"
BODY_TYPE"PLUMBING"
CDS_LIB"default"
WIRE \NWC \NAC
BN"2..0"78
BUNDLE \NWC \NAC38,37
%"BUSWIDE_TOP_LEFT_RIP"
1,"(7175,-900)","0","default","I176"
HDL_TAP"TRUE"
BODY_TYPE"PLUMBING"
CDS_LIB"default"
WIRE \NWC \NAC
BN"5..3"77
BUNDLE \NWC \NAC38,37
%"portboth-r_1"
1,"(6625,-300)","0","mtca_interface_board","I177"
NAME"SFP<29..0>"
CDS_LIB"mtca_interface_board"
HOTSPOT_0
HDL_PORT"INOUT"
PIN_NAME"SFP<29..0>"38,37
%"ADCLK948"
1,"(1500,-975)","0","cninterface","I178"
$LOCATION"IC?"
PACK_TYPE"LFCSP"
TYPE"ADCLK948BCPZ"
POWER_GROUP"VEE=GND | VCC=VDD_CLK_BUFFER"
ROOM"CLK_FO_0_5"
HAS_FIXED_SIZE"8B"
CDS_LIB"cninterface"
VT10
CLK198
CLK1*87
Q<0>27
Q<0>*53
Q<1>52
Q<2>54
Q<1>*51
Q<2>*80
Q<3>*10
Q<3>81
Q<4>55
Q<4>*82
Q<5>67
Q<5>*66
Q<6>95
Q<7>*88
Q<6>*94
Q<7>89
CLK0*49
CLK050
VT099
VREF10
IN_SEL97
VREF099
%"CAPCERSMDCL2"
1,"(950,-625)","1","cnpassive","I179"
CDS_LOCATION"C8"
$LOCATION"C8"
VOLTAGE"16V_GEN"
VALUE"100NF"
ROOM"CLK_FO_0_5"
PACK_TYPE"0402"
SIZE"1"
CDS_LIB"cnpassive"
JEDEC_TYPE"cap0402"
MANUFACTURER"TDK CORP"
DISTRIBUTOR_PARTNUMBER"445-7348-2-ND"
DISTRIBUTOR"Digi-Key"
AVAILABILITY"In Stock"
PART_TYPE"Ceramic"
MPN"C1005X7R1E104K050BB "
PSPICE"C"
DESCRIPTION"CAP 0.1__F __10% 25V Ceramic Capacitor X7R 0402 "
LAST_EDIT_BY"SNF"
ALT_SYMBOLS""
REUSE_ANNOTATE"TRUE"
CLASS"DISCRETE"
A <SIZE-1..0>\NAC
$PN"#"8
B <SIZE-1..0>\NAC
$PN"#"99
%"gnd"
1,"(1000,-800)","2","mtca_interface_board","I180"
ROOM"CLK_FO_0_5"
HDL_POWER"GND"
CDS_LIB"mtca_interface_board"
HOTSPOT_08
%"RSMD0402"
1,"(850,-1675)","1","cnpassive","I181"
$LOCATION"R?"
VALUE"1K"
TOL"1%"
ROOM"CLK_FO_0_5"
TC2"RTMPQ"
TC1"RTMPL"
MAX_TEMP"RTMAX"
SLOPE"RSMAX"
VOLTAGE"RVMAX"
POWER"RMAX"
DIST"FLAT"
TOL_ON_OFF"ON"
POSTOL"RTOL%"
NEGTOL"RTOL%"
CDS_LIB"cnpassive"
PACK_TYPE"1/16W"
SIZE"1B"
B <SIZE-1..0>\NAC30
A <SIZE-1..0>\NAC98
%"RSMD0402"
1,"(725,-1275)","0","cnpassive","I182"
$LOCATION"R?"
TOL"1%"
VALUE"1K"
ROOM"CLK_FO_0_5"
SIZE"1B"
CDS_LIB"cnpassive"
PACK_TYPE"1/16W"
TOL_ON_OFF"ON"
POSTOL"RTOL%"
NEGTOL"RTOL%"
DIST"FLAT"
POWER"RMAX"
VOLTAGE"RVMAX"
SLOPE"RSMAX"
MAX_TEMP"RTMAX"
TC1"RTMPL"
TC2"RTMPQ"
B <SIZE-1..0>\NAC97
A <SIZE-1..0>\NAC2
%"RSMD0402"
1,"(1100,-1675)","1","cnpassive","I183"
$LOCATION"R?"
TOL"1%"
VALUE"2.2K"
ROOM"CLK_FO_0_5"
TC2"RTMPQ"
TC1"RTMPL"
MAX_TEMP"RTMAX"
SLOPE"RSMAX"
VOLTAGE"RVMAX"
POWER"RMAX"
DIST"FLAT"
NEGTOL"RTOL%"
POSTOL"RTOL%"
TOL_ON_OFF"ON"
CDS_LIB"cnpassive"
PACK_TYPE"1/16W"
SIZE"1B"
B <SIZE-1..0>\NAC87
A <SIZE-1..0>\NAC7
%"RSMD0402"
1,"(1825,-1625)","1","cnpassive","I184"
$LOCATION"R?"
TOL"1%"
VALUE"200"
ROOM"CLK_FO_0_5"
MAX_TEMP"RTMAX"
TC1"RTMPL"
TC2"RTMPQ"
NEGTOL"RTOL%"
POSTOL"RTOL%"
DIST"FLAT"
POWER"RMAX"
VOLTAGE"RVMAX"
SLOPE"RSMAX"
TOL_ON_OFF"ON"
CDS_LIB"cnpassive"
PACK_TYPE"1/16W"
SIZE"1B"
B <SIZE-1..0>\NAC88
A <SIZE-1..0>\NAC7
%"RSMD0402"
1,"(1950,-1450)","1","cnpassive","I185"
$LOCATION"R?"
TOL"1%"
VALUE"200"
ROOM"CLK_FO_0_5"
TC2"RTMPQ"
TC1"RTMPL"
MAX_TEMP"RTMAX"
POSTOL"RTOL%"
NEGTOL"RTOL%"
DIST"FLAT"
SLOPE"RSMAX"
VOLTAGE"RVMAX"
POWER"RMAX"
TOL_ON_OFF"ON"
CDS_LIB"cnpassive"
SIZE"1B"
PACK_TYPE"1/16W"
B <SIZE-1..0>\NAC89
A <SIZE-1..0>\NAC7
%"RSMD0402"
1,"(3700,-1450)","1","cnpassive","I186"
$LOCATION"R?"
TOL"1%"
VALUE"200"
ROOM"CLK_FO_0_5"
CDS_LIB"cnpassive"
TC2"RTMPQ"
TC1"RTMPL"
MAX_TEMP"RTMAX"
SLOPE"RSMAX"
VOLTAGE"RVMAX"
POWER"RMAX"
DIST"FLAT"
NEGTOL"RTOL%"
POSTOL"RTOL%"
TOL_ON_OFF"ON"
PACK_TYPE"1/16W"
SIZE"1B"
B <SIZE-1..0>\NAC66
A <SIZE-1..0>\NAC7
%"RSMD0402"
1,"(3575,-1625)","1","cnpassive","I187"
$LOCATION"R?"
VALUE"200"
TOL"1%"
ROOM"CLK_FO_0_5"
TC2"RTMPQ"
DIST"FLAT"
POWER"RMAX"
VOLTAGE"RVMAX"
TC1"RTMPL"
MAX_TEMP"RTMAX"
SLOPE"RSMAX"
NEGTOL"RTOL%"
POSTOL"RTOL%"
TOL_ON_OFF"ON"
CDS_LIB"cnpassive"
PACK_TYPE"1/16W"
SIZE"1B"
B <SIZE-1..0>\NAC67
A <SIZE-1..0>\NAC7
%"RSMD0402"
1,"(3450,-1450)","1","cnpassive","I188"
$LOCATION"R?"
TOL"1%"
VALUE"200"
ROOM"CLK_FO_0_5"
TC2"RTMPQ"
TC1"RTMPL"
MAX_TEMP"RTMAX"
SLOPE"RSMAX"
VOLTAGE"RVMAX"
POWER"RMAX"
DIST"FLAT"
NEGTOL"RTOL%"
CDS_LIB"cnpassive"
SIZE"1B"
POSTOL"RTOL%"
TOL_ON_OFF"ON"
PACK_TYPE"1/16W"
B <SIZE-1..0>\NAC82
A <SIZE-1..0>\NAC7
%"RSMD0402"
1,"(3325,-1625)","1","cnpassive","I189"
$LOCATION"R?"
TOL"1%"
VALUE"200"
ROOM"CLK_FO_0_5"
TC2"RTMPQ"
SLOPE"RSMAX"
MAX_TEMP"RTMAX"
TC1"RTMPL"
VOLTAGE"RVMAX"
DIST"FLAT"
POWER"RMAX"
NEGTOL"RTOL%"
POSTOL"RTOL%"
TOL_ON_OFF"ON"
CDS_LIB"cnpassive"
PACK_TYPE"1/16W"
SIZE"1B"
B <SIZE-1..0>\NAC55
A <SIZE-1..0>\NAC7
%"RSMD0402"
1,"(3200,-1450)","1","cnpassive","I190"
$LOCATION"R?"
TOL"1%"
VALUE"200"
ROOM"CLK_FO_0_5"
CDS_LIB"cnpassive"
TC2"RTMPQ"
TC1"RTMPL"
MAX_TEMP"RTMAX"
SLOPE"RSMAX"
VOLTAGE"RVMAX"
POWER"RMAX"
DIST"FLAT"
NEGTOL"RTOL%"
POSTOL"RTOL%"
TOL_ON_OFF"ON"
PACK_TYPE"1/16W"
SIZE"1B"
B <SIZE-1..0>\NAC10
A <SIZE-1..0>\NAC7
%"RSMD0402"
1,"(3075,-1625)","1","cnpassive","I191"
$LOCATION"R?"
TOL"1%"
VALUE"200"
ROOM"CLK_FO_0_5"
TC2"RTMPQ"
TC1"RTMPL"
SLOPE"RSMAX"
MAX_TEMP"RTMAX"
VOLTAGE"RVMAX"
DIST"FLAT"
POWER"RMAX"
NEGTOL"RTOL%"
CDS_LIB"cnpassive"
POSTOL"RTOL%"
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
A <SIZE-1..0>\NAC4
%"RSMD0402"
1,"(2450,-3100)","1","cnpassive","I237"
$LOCATION"R?"
TOL"1%"
VALUE"200"
ROOM"CLK_FO_6_11"
CDS_LIB"cnpassive"
TC2"RTMPQ"
TC1"RTMPL"
MAX_TEMP"RTMAX"
NEGTOL"RTOL%"
DIST"FLAT"
POWER"RMAX"
VOLTAGE"RVMAX"
SLOPE"RSMAX"
POSTOL"RTOL%"
TOL_ON_OFF"ON"
SIZE"1B"
PACK_TYPE"1/16W"
B <SIZE-1..0>\NAC69
A <SIZE-1..0>\NAC4
%"RSMD0402"
1,"(2325,-3275)","1","cnpassive","I238"
$LOCATION"R?"
VALUE"200"
TOL"1%"
ROOM"CLK_FO_6_11"
TC1"RTMPL"
TC2"RTMPQ"
MAX_TEMP"RTMAX"
CDS_LIB"cnpassive"
NEGTOL"RTOL%"
DIST"FLAT"
POWER"RMAX"
VOLTAGE"RVMAX"
SLOPE"RSMAX"
POSTOL"RTOL%"
TOL_ON_OFF"ON"
PACK_TYPE"1/16W"
SIZE"1B"
B <SIZE-1..0>\NAC83
A <SIZE-1..0>\NAC4
%"RSMD0402"
1,"(2200,-3100)","1","cnpassive","I239"
$LOCATION"R?"
VALUE"200"
TOL"1%"
ROOM"CLK_FO_6_11"
CDS_LIB"cnpassive"
TC2"RTMPQ"
TC1"RTMPL"
MAX_TEMP"RTMAX"
NEGTOL"RTOL%"
DIST"FLAT"
POWER"RMAX"
VOLTAGE"RVMAX"
SLOPE"RSMAX"
POSTOL"RTOL%"
TOL_ON_OFF"ON"
SIZE"1B"
PACK_TYPE"1/16W"
B <SIZE-1..0>\NAC93
A <SIZE-1..0>\NAC4
%"RSMD0402"
1,"(2075,-3275)","1","cnpassive","I240"
$LOCATION"R?"
TOL"1%"
VALUE"200"
ROOM"CLK_FO_6_11"
TC1"RTMPL"
TC2"RTMPQ"
MAX_TEMP"RTMAX"
CDS_LIB"cnpassive"
VOLTAGE"RVMAX"
POWER"RMAX"
POSTOL"RTOL%"
NEGTOL"RTOL%"
DIST"FLAT"
SLOPE"RSMAX"
TOL_ON_OFF"ON"
SIZE"1B"
PACK_TYPE"1/16W"
B <SIZE-1..0>\NAC92
A <SIZE-1..0>\NAC4
%"RSMD0402"
1,"(1950,-3100)","1","cnpassive","I241"
$LOCATION"R?"
VALUE"200"
TOL"1%"
ROOM"CLK_FO_6_11"
TC2"RTMPQ"
TC1"RTMPL"
MAX_TEMP"RTMAX"
POSTOL"RTOL%"
NEGTOL"RTOL%"
DIST"FLAT"
POWER"RMAX"
VOLTAGE"RVMAX"
SLOPE"RSMAX"
TOL_ON_OFF"ON"
CDS_LIB"cnpassive"
SIZE"1B"
PACK_TYPE"1/16W"
B <SIZE-1..0>\NAC91
A <SIZE-1..0>\NAC4
%"RSMD0402"
1,"(1825,-3275)","1","cnpassive","I242"
$LOCATION"R?"
VALUE"200"
TOL"1%"
ROOM"CLK_FO_6_11"
MAX_TEMP"RTMAX"
TC1"RTMPL"
TC2"RTMPQ"
CDS_LIB"cnpassive"
NEGTOL"RTOL%"
POSTOL"RTOL%"
DIST"FLAT"
POWER"RMAX"
SLOPE"RSMAX"
VOLTAGE"RVMAX"
TOL_ON_OFF"ON"
SIZE"1B"
PACK_TYPE"1/16W"
B <SIZE-1..0>\NAC90
A <SIZE-1..0>\NAC4
%"gnd"
1,"(1875,-3500)","2","mtca_interface_board","I243"
ROOM"CLK_FO_6_11"
HDL_POWER"GND"
CDS_LIB"mtca_interface_board"
HOTSPOT_04
%"ADCLK948"
1,"(1500,-2625)","0","cninterface","I244"
$LOCATION"IC?"
POWER_GROUP"VEE=GND | VCC=VDD_CLK_BUFFER"
TYPE"ADCLK948BCPZ"
PACK_TYPE"LFCSP"
ROOM"CLK_FO_6_11"
CDS_LIB"cninterface"
HAS_FIXED_SIZE"8B"
VT10
CLK185
CLK1*86
Q<0>83
Q<0>*69
Q<1>68
Q<2>64
Q<1>*35
Q<2>*58
Q<3>*29
Q<3>28
Q<4>15
Q<4>*16
Q<5>17
Q<5>*46
Q<6>93
Q<7>*90
Q<6>*92
Q<7>91
CLK0*65
CLK031
VT096
VREF10
IN_SEL84
VREF096
%"RSMD0402"
1,"(1100,-3325)","1","cnpassive","I245"
$LOCATION"R?"
VALUE"2.2K"
TOL"1%"
ROOM"CLK_FO_6_11"
VOLTAGE"RVMAX"
SLOPE"RSMAX"
MAX_TEMP"RTMAX"
TC1"RTMPL"
TC2"RTMPQ"
CDS_LIB"cnpassive"
TOL_ON_OFF"ON"
POWER"RMAX"
DIST"FLAT"
NEGTOL"RTOL%"
POSTOL"RTOL%"
PACK_TYPE"1/16W"
SIZE"1B"
B <SIZE-1..0>\NAC86
A <SIZE-1..0>\NAC4
%"CAPCERSMDCL2"
1,"(950,-2275)","1","cnpassive","I246"
CDS_LOCATION"C8"
$LOCATION"C8"
VOLTAGE"16V_GEN"
VALUE"100NF"
ROOM"CLK_FO_6_11"
PACK_TYPE"0402"
CDS_LIB"cnpassive"
SIZE"1"
JEDEC_TYPE"cap0402"
MANUFACTURER"TDK CORP"
DISTRIBUTOR_PARTNUMBER"445-7348-2-ND"
DISTRIBUTOR"Digi-Key"
AVAILABILITY"In Stock"
MPN"C1005X7R1E104K050BB "
PSPICE"C"
DESCRIPTION"CAP 0.1__F __10% 25V Ceramic Capacitor X7R 0402 "
CLASS"DISCRETE"
LAST_EDIT_BY"SNF"
ALT_SYMBOLS""
REUSE_ANNOTATE"TRUE"
PART_TYPE"Ceramic"
A <SIZE-1..0>\NAC
$PN"#"5
B <SIZE-1..0>\NAC
$PN"#"96
%"gnd"
1,"(1000,-2450)","2","mtca_interface_board","I247"
ROOM"CLK_FO_6_11"
HDL_POWER"GND"
CDS_LIB"mtca_interface_board"
HOTSPOT_05
%"RSMD0402"
1,"(725,-2925)","0","cnpassive","I252"
$LOCATION"R?"
VALUE"1K"
TOL"1%"
ROOM"CLK_FO_6_11"
SIZE"1B"
CDS_LIB"cnpassive"
PACK_TYPE"1/16W"
TOL_ON_OFF"ON"
POSTOL"RTOL%"
NEGTOL"RTOL%"
DIST"FLAT"
TC2"RTMPQ"
TC1"RTMPL"
MAX_TEMP"RTMAX"
SLOPE"RSMAX"
VOLTAGE"RVMAX"
POWER"RMAX"
B <SIZE-1..0>\NAC84
A <SIZE-1..0>\NAC6
%"RSMD0402"
1,"(850,-3325)","1","cnpassive","I253"
$LOCATION"R?"
VALUE"1K"
TOL"1%"
ROOM"CLK_FO_6_11"
TC2"RTMPQ"
TC1"RTMPL"
MAX_TEMP"RTMAX"
SLOPE"RSMAX"
VOLTAGE"RVMAX"
POWER"RMAX"
CDS_LIB"cnpassive"
TOL_ON_OFF"ON"
POSTOL"RTOL%"
NEGTOL"RTOL%"
DIST"FLAT"
PACK_TYPE"1/16W"
SIZE"1B"
B <SIZE-1..0>\NAC18
A <SIZE-1..0>\NAC85
%"gnd"
1,"(600,-3000)","2","mtca_interface_board","I254"
ROOM"CLK_FO_6_11"
HDL_POWER"GND"
CDS_LIB"mtca_interface_board"
HOTSPOT_06
%"FERRITE"
1,"(425,-4125)","0","cndiscrete","I255"
$LOCATION"L?"
VALUE"BLM21PG221SN1"
ROOM"CLK_FO_0_5"
MODEL"MURATA"
CDS_LIB"cndiscrete"
PACK_TYPE"SMD"
B <SIZE-1..0>\NAC9
A <SIZE-1..0>\NAC3
END.
