uob-hep-cad/uob-hep-pc072/hardware/Cadence/top/mtca_interface_board_reocc/01_#20module#20management#20ctrl/sch_1/page1.csv

FILE_TYPE = CONNECTIVITY
{Allegro Design Entry HDL 24.1 P001 (4234998) 9/4/2024}
PAGE_NUMBER = 1
0"NC"
1"TDO"
2"VP12\G"
3"GND\G"
4"GND\G"
5"MP3V3\G"
6"GND\G"
7"GND\G"
8"MP3V3\g"
9"MP3V3\g"
10"GND\G"
11"RESET*"
12"GREEN_LED"
13"UN$1$KINGBRIGHTKPA$I253$2"
14"MP3V3\G"
15"GND\g"
16"N00505"
17"GND\g"
18"GND\g"
19"GND\G"
20"GND\G"
21"MP3V3\G"
22"MP3V3\G"
23"MP3V3\G"
24"GND\G"
25"MP3V3\G"
26"UN$1$RSMD0603$I250$B"
27"DCDC_ENABLE"
28"BP.AMC_GA<2>"
29"BP.AMC_GA<0>"
30"N00481"
31"BP.AMC_GA<1>"
32"RESET*"
33"BP.AMC_N-ENABLE"
34"TDI"
35"RED_LED"
36"UN$1$inv1chod$171P$A"
37"TDO"
38"DCDC_2V5_PG"
39"BP.AMC_IPMB_SCL"
40"BP.AMC_IPMB_SDA"
41"HANDLE_SW_CLOSE_N"
42"SENSE_12C_SDA"
43"N00473"
44"SENSE_12C_SCL"
45"HANDLE_SW_CLOSE_N"
46"BLUE_LED"
47"BP.AMC_N-PS<1>"
48"SENSE_12C_SCL"
49"NOVER_TEMP"
50"PRESENCE_12V"
51"TDI"
52"TMS"
53"TCK"
54"PRESENCE_12V"
55"DCDC_3V3_PG"
56"BLUE_LED"
57"GREEN_LED"
58"RED_LED"
59"RTM_PS"
60"UN$1$ATMGA128$I235$PE2"
61"N00469"
62"N00455"
63"FPGA_PG"
64"LDO_1V8_PG"
65"DCDC_2V5_PG"
66"UN$1$RSMD0603$I242$A"
67"TMS"
68"TCK"
69"NOVER_TEMP"
70"BP.AMC_N-PS<0>"
71"N00497"
72"N00471"
73"RESET*"
74"BP.TMS"
75"SENSE_12C_SDA"
76"UN$1$inv1chod$171P$Y"
77"DCDC_ENABLE"
78"DCDC_3V3_PG"
79"POWER<5..0>"
80"FPGA_PG"
82"BP<180..0>"
81"BP<180..0>"
83"SENSE_12C_SCL"
84"LDO_1V8_PG"
85"BP.TCK"
86"SENSE_12C_SDA"
87"BP.AMC_N-ENABLE"
88"BP.TDI"
89"BP.AMC_N-PS<1..0>"
90"BP.AMC_GA<2..0>"
91"BP.PWR_ON"
92"BP.AMC_IPMB_SCL"
93"BP.AMC_IPMB_SDA"
94"BP.TDO"
%"vcc_bar"
1,"(750,-875)","0","mtca_interface_board","125P"
HDL_POWER"VP12"
CDS_LIB"mtca_interface_board"
HOTSPOT_02
%"vcc_bar"
1,"(4775,-725)","0","mtca_interface_board","126P"
HDL_POWER"MP3V3"
CDS_LIB"mtca_interface_board"
HOTSPOT_025
%"gnd"
1,"(1525,-3200)","0","mtca_interface_board","128P"
HDL_POWER"GND"
CDS_LIB"mtca_interface_board"
HOTSPOT_010
%"gnd"
1,"(2475,-3350)","0","mtca_interface_board","129P"
HDL_POWER"GND"
CDS_LIB"mtca_interface_board"
HOTSPOT_015
%"gnd"
1,"(1700,-4775)","0","mtca_interface_board","130P"
CDS_LIB"mtca_interface_board"
HDL_POWER"GND"
HOTSPOT_03
%"gnd"
1,"(4475,-2950)","0","mtca_interface_board","131P"
HDL_POWER"GND"
CDS_LIB"mtca_interface_board"
HOTSPOT_04
%"gnd"
1,"(4025,-3600)","0","mtca_interface_board","132P"
HDL_POWER"GND"
CDS_LIB"mtca_interface_board"
HOTSPOT_024
%"r"
1,"(675,-4075)","0","discrete","162P"
VALUE"1k"
$LOCATION"R109"
CDS_LIB"discrete"
CDS_LOCATION"R109"
JEDEC_TYPE"res0402"
SOURCE_PACKAGE"R"
ROOM"MMC_DISCRETE"
PART_NUMBER"ERJ-2RKF1001X"
PART_TYPE"Thick Film"
DESCRIPTION"RES SMD 1K OHM 1% 1/10W 0402"
POWER"1/16 W"
MANUFACTURER"Panasonic"
MPN"ERJ-2RKF1001X"
TOLERANCE"1%"
DISTRIBUTOR"Digikey"
DISTRIBUTOR_PARTNUMBER"P1.00KLTR-ND"
DATASHEET"C:\EMA\CISQuickStart\Technical_Datasheets\Panasonic\AOA0000CE1.pdf"
SEC"1"
1
$PN"1"14
2
$PN"2"37
%"lm75a"
1,"(4025,-3150)","0","ocad_parts_lib","163P"
$LOCATION"U25"
VALUE"LM75AIMME/NOPB"
SEC"1"
PART_NUMBER"LM75AIMME/NOPB"
PART_TYPE"Misc"
DESCRIPTION"SENSOR DGTL -40C-150C 16LFCSP"
PSPICE"IC"
MPN"LM75AIMME/NOPB"
MANUFACTURER"Texas Instruments"
DISTRIBUTOR_PARTNUMBER"LM75AIMME/NOPBTR-ND"
DISTRIBUTOR"Digikey"
AVAILABILITY"9200"
DATASHEET"\\Mac\Home\Desktop\SPB_Data\CIS_HEP_Partslib\DataSheets\LTM4630fa.pdf"
SOURCE_PACKAGE"LM75A"
JEDEC_TYPE"tssop8_65p440x300mm"
CDS_LOCATION"U25"
CDS_LIB"ocad_parts_lib"
SCL
$PN"2"44
SDA
$PN"1"75
GND
$PN"4"24
A0
$PN"7"24
A1
$PN"6"24
A2
$PN"5"24
OS
$PN"3"49
+VS
$PN"8"5
%"r"
1,"(4825,-1000)","0","discrete","164P"
$LOCATION"R58"
VALUE"2.2k"
CDS_LIB"discrete"
CDS_LOCATION"R58"
JEDEC_TYPE"res0402"
SOURCE_PACKAGE"R"
REUSE_ID"1"
PART_NUMBER"ERJ-2RKF2201X"
PART_TYPE"Thick Film"
DESCRIPTION"RES SMD 2.2K OHM 1% 1/10W 0402"
POWER"1/10 W"
TOLERANCE"1%"
MPN"ERJ-2RKF2201X"
MANUFACTURER"Panasonic"
DISTRIBUTOR_PARTNUMBER"P2.20KLTR-ND"
DISTRIBUTOR"Digikey"
AVAILABILITY"6,080,000"
ROOM"MMC"
REUSE_ANNOTATE"TRUE"
SEC"1"
1
$PN"1"25
2
$PN"2"48
%"led green 0603_0"
1,"(2550,-4350)","1","ocad_parts_lib","165P"
$LOCATION"D1"
VALUE"Green"
CDS_LIB"ocad_parts_lib"
CDS_LOCATION"D1"
JEDEC_TYPE"LEDC1608X80N"
SOURCE_PACKAGE"LED GREEN 0603_0"
DESCRIPTION"LED GREEN 0603 SMD"
REUSE_ID"245"
DATASHEET"C:\EMA\CISQuickStart\Technical_Datasheets\Panasonic\ATA7000CE271.pdf"
DISTRIBUTOR"Digikey"
DISTRIBUTOR_PARTNUMBER"P13485CT-ND"
MANUFACTURER"Panasonic"
MPN"LNJ326W83RA"
LEDCOLOR"Green"
RATING"30 mW"
PART_TYPE"LED\Green"
PART_NUMBER"LNJ326W83RA"
ROOM"MMC"
REUSE_ANNOTATE"TRUE"
MFR_PART_NUMBER"LTST-C190GKT"
DEVICE"LED_GREEN0603"
MFR_NAME"Lite-On Trading USA, Inc."
CY_PART_"860R-13779"
SEC"1"
A
$PN"2"21
K
$PN"1"16
%"cap_np"
1,"(3375,-925)","0","ocad_parts_lib","166P"
VOLTAGE"6.3V"
$LOCATION"C104"
VALUE"0.1UF"
CDS_LIB"ocad_parts_lib"
CDS_LOCATION"C104"
JEDEC_TYPE"cap0402"
SOURCE_PACKAGE"CAP_NP"
ROOM"MMC_DISCRETE"
PART_NUMBER"C0402C104K9RACTU"
PART_TYPE"Ceramic"
DESCRIPTION"0.1__F __10% 6.3V Ceramic Capacitor X7R 0402 (1005 Metric)"
TOLERANCE"10%"
PSPICE"C"
MPN"C0402C104K9RACTU"
MANUFACTURER"KEMET"
DISTRIBUTOR_PARTNUMBER"399-4872-1-ND"
DISTRIBUTOR"Digi-Key"
AVAILABILITY"In Stock"
ALT_SYMBOLS""
LAST_EDIT_BY"SNF"
CLASS"DISCRETE"
SEC"1"
1
$PN"1"62
2
$PN"2"20
%"r"
1,"(4000,-1075)","0","discrete","167P"
$LOCATION"R61"
VALUE"33k"
CDS_LIB"discrete"
CDS_LOCATION"R61"
JEDEC_TYPE"res0402"
SOURCE_PACKAGE"R"
ROOM"MMC_DISCRETE"
PART_NUMBER"ERJ-2RKF3302X"
PART_TYPE"Thick Film"
DESCRIPTION"RES SMD 33K OHM 1% 1/10W 0402"
POWER"1/10 W"
TOLERANCE"1%"
MPN"ERJ-2RKF3302X"
MANUFACTURER"Panasonic"
DISTRIBUTOR_PARTNUMBER"P33.0KLTR-ND"
DISTRIBUTOR"Digikey"
AVAILABILITY"In Stock"
SEC"1"
1
$PN"1"23
2
$PN"2"41
%"r"
1,"(550,-1425)","1","discrete","168P"
VALUE"30k"
$LOCATION"R110"
CDS_LIB"discrete"
CDS_LOCATION"R110"
JEDEC_TYPE"res0402"
SOURCE_PACKAGE"R"
ROOM"MMC_DISCRETE"
AVAILABILITY"40,000 "
DISTRIBUTOR"Digikey"
DISTRIBUTOR_PARTNUMBER"P30KDCTR-ND"
MANUFACTURER"Panasonic"
MPN"ERA-2AEB303X"
TOLERANCE"1%"
POWER"1/10 W"
DESCRIPTION"RES SMD 30K OHM 0.1% 1/16W 0402"
PART_TYPE"Thick Film"
PART_NUMBER"ERA-2AEB303X"
SEC"1"
1
$PN"1"6
2
$PN"2"50
%"r"
1,"(4525,-2200)","0","discrete","169P"
$LOCATION"R105"
VALUE"330"
CDS_LIB"discrete"
CDS_LOCATION"R105"
JEDEC_TYPE"res0402"
SOURCE_PACKAGE"R"
ROOM"MMC_DISCRETE"
PART_NUMBER"ERJ-PA2F3300X"
PART_TYPE"Thick Film"
DESCRIPTION"RES SMD 330 OHM 1% 1/5W 0402"
POWER"1/10W"
TOLERANCE"1%"
MPN"ERJ-PA2F3300X"
MANUFACTURER"Panasonic - SCD"
DISTRIBUTOR_PARTNUMBER"P17221TR-ND"
DISTRIBUTOR"Digikey"
DATASHEET"C:\EMA\CISQuickStart\Technical_Datasheets\Yageo\PYu-RC0603_51_RoHS_L_4.pdf"
SEC"1"
1
$PN"1"43
2
$PN"2"19
%"r"
1,"(4525,-1000)","0","discrete","170P"
VALUE"4.7k"
$LOCATION"R41"
CDS_LIB"discrete"
CDS_LOCATION"R41"
JEDEC_TYPE"res0402"
SOURCE_PACKAGE"R"
ROOM"MMC_DISCRETE"
PART_NUMBER"ERJ-2RKF4701X"
PART_TYPE"Thick Film"
DESCRIPTION"RES SMD 4.7K OHM 1% 1/10W 0402"
POWER"1/10 W"
TOLERANCE"1%"
MPN"ERJ-2RKF4701X"
MANUFACTURER"Panasonic"
DISTRIBUTOR_PARTNUMBER"P4.70KLTR-ND"
DISTRIBUTOR"Digikey"
AVAILABILITY"In Stock"
SEC"1"
1
$PN"1"25
2
$PN"2"43
%"inv_1ch_od"
1,"(1275,-3300)","0","ocad_parts_lib","171P"
$LOCATION"U15"
VALUE"SN74LVC1G06"
CDS_LIB"ocad_parts_lib"
CDS_LOCATION"U15"
JEDEC_TYPE"SOT23-5"
SOURCE_PACKAGE"INV_1CH_OD"
PART_NUMBER"SN74LVC1G06DBVTE4"
PART_TYPE"Logic"
DESCRIPTION"Inverter IC 1 Channel Open Drain SOT-23-5"
PSPICE"IC"
MPN"SN74LVC1G06DBVTE4"
MANUFACTURER"Texas Instruments"
DISTRIBUTOR_PARTNUMBER"2156-SN74LVC1G06DBVTE4-ND"
DISTRIBUTOR"Digikey"
AVAILABILITY"In Stock"
DATASHEET"NULL"
ROOM"MMC_DISCRETE"
SEC"1"
A
$PN"2"36
GND
$PN"3"7
NC
$PN"1"0
VCC
$PN"5"22
Y
$PN"4"76
%"r"
1,"(4925,-1000)","0","discrete","172P"
VALUE"2.2k"
$LOCATION"R54"
CDS_LIB"discrete"
CDS_LOCATION"R54"
JEDEC_TYPE"res0402"
SOURCE_PACKAGE"R"
REUSE_ID"2"
ROOM"MMC"
AVAILABILITY"6,080,000"
DISTRIBUTOR"Digikey"
DISTRIBUTOR_PARTNUMBER"P2.20KLTR-ND"
MANUFACTURER"Panasonic"
MPN"ERJ-2RKF2201X"
TOLERANCE"1%"
POWER"1/10 W"
DESCRIPTION"RES SMD 2.2K OHM 1% 1/10W 0402"
PART_TYPE"Thick Film"
PART_NUMBER"ERJ-2RKF2201X"
REUSE_ANNOTATE"TRUE"
SEC"1"
1
$PN"1"25
2
$PN"2"42
%"r"
1,"(3125,-1475)","1","discrete","174P"
VALUE"49.9"
$LOCATION"R56"
CDS_LIB"discrete"
CDS_LOCATION"R56"
JEDEC_TYPE"res0402"
SOURCE_PACKAGE"R"
ROOM"MMC_DISCRETE"
DATASHEET"C:\EMA\CISQuickStart\Technical_Datasheets\Vishay\dcrcwe3.pdf"
DISTRIBUTOR"Digikey"
DISTRIBUTOR_PARTNUMBER"P49.9LTR-ND"
MANUFACTURER"Panasonic"
MPN"ERJ-2RKF49R9X"
TOLERANCE"1.0 %"
POWER"1/10W"
DESCRIPTION"RES SMD 49.9 OHM 1% 1/10W 0402"
PART_TYPE"Thick Film"
PART_NUMBER"ERJ-2RKF49R9X"
SEC"1"
1
$PN"1"72
2
$PN"2"48
%"r"
1,"(825,-4075)","0","discrete","175P"
VALUE"1k"
$LOCATION"R108"
CDS_LIB"discrete"
CDS_LOCATION"R108"
JEDEC_TYPE"res0402"
SOURCE_PACKAGE"R"
ROOM"MMC_DISCRETE"
PART_NUMBER"ERJ-2RKF1001X"
PART_TYPE"Thick Film"
DESCRIPTION"RES SMD 1K OHM 1% 1/10W 0402"
POWER"1/16 W"
DISTRIBUTOR"Digikey"
DISTRIBUTOR_PARTNUMBER"P1.00KLTR-ND"
MANUFACTURER"Panasonic"
MPN"ERJ-2RKF1001X"
TOLERANCE"1%"
DATASHEET"C:\EMA\CISQuickStart\Technical_Datasheets\Panasonic\AOA0000CE1.pdf"
SEC"1"
1
$PN"1"14
2
$PN"2"67
%"hdt0001"
1,"(6450,-3075)","0","ocad_parts_lib","176P"
$LOCATION"SW1"
VALUE"HDT0001"
SEC"1"
AVAILABILITY"In Stock"
PRICE"1.17"
DISTRIBUTOR"Digi-Key"
DISTRIBUTOR_PARTNUMBER"401-1733-1-ND"
MANUFACTURER"C&K"
MPN"HDT0001"
RATING"1mA DC"
DESCRIPTION"SWITCH DETECTOR SPST-NO 1MA 5V"
PART_TYPE"Misc"
PART_NUMBER"HDT0001"
ROOM"MMC"
SOURCE_PACKAGE"HDT0001"
JEDEC_TYPE"sw_HDT0001"
CDS_LOCATION"SW1"
CDS_LIB"ocad_parts_lib"
A
$PN"1"18
D
$PN"4"45
C
$PN"2"18
B
$PN"3"45
%"cap_np"
1,"(3025,-925)","0","ocad_parts_lib","179P"
VALUE"0.47UF"
VOLTAGE"6.3V"
$LOCATION"C46"
CDS_LIB"ocad_parts_lib"
CDS_LOCATION"C46"
JEDEC_TYPE"cap0402"
SOURCE_PACKAGE"CAP_NP"
ROOM"MMC_DISCRETE"
AVAILABILITY"In Stock"
DISTRIBUTOR"Digi-Key"
DISTRIBUTOR_PARTNUMBER"490-6293-2-ND"
MANUFACTURER"Murata"
MPN"GRM155R60J474KE19J"
PSPICE"C"
DESCRIPTION"CAP CER 0.47UF 6.3V X5R 0402"
PART_TYPE"Ceramic"
PART_NUMBER"GRM155R60J474KE19J"
ALT_SYMBOLS""
LAST_EDIT_BY"SNF"
CLASS"DISCRETE"
SEC"1"
1
$PN"1"23
2
$PN"2"20
%"r"
1,"(1325,-1025)","0","discrete","180P"
$LOCATION"R39"
VALUE"33k"
CDS_LIB"discrete"
CDS_LOCATION"R39"
JEDEC_TYPE"res0402"
SOURCE_PACKAGE"R"
PART_NUMBER"ERJ-2RKF3302X"
PART_TYPE"Thick Film"
DESCRIPTION"RES SMD 33K OHM 1% 1/10W 0402"
POWER"1/10 W"
TOLERANCE"1%"
MPN"ERJ-2RKF3302X"
MANUFACTURER"Panasonic"
DISTRIBUTOR_PARTNUMBER"P33.0KLTR-ND"
DISTRIBUTOR"Digikey"
AVAILABILITY"In Stock"
ROOM"MMC_DISCRETE"
SEC"1"
1
$PN"1"23
2
$PN"2"59
%"r"
1,"(625,-1700)","0","discrete","182P"
VALUE"33k"
$LOCATION"R47"
CDS_LIB"discrete"
CDS_LOCATION"R47"
JEDEC_TYPE"res0402"
SOURCE_PACKAGE"R"
ROOM"MMC_DISCRETE"
AVAILABILITY"In Stock"
DISTRIBUTOR"Digikey"
DISTRIBUTOR_PARTNUMBER"P33.0KLTR-ND"
MANUFACTURER"Panasonic"
MPN"ERJ-2RKF3302X"
TOLERANCE"1%"
POWER"1/10 W"
DESCRIPTION"RES SMD 33K OHM 1% 1/10W 0402"
PART_TYPE"Thick Film"
PART_NUMBER"ERJ-2RKF3302X"
SEC"1"
1
$PN"1"30
2
$PN"2"28
%"r"
1,"(2600,-4000)","6","discrete","183P"
$LOCATION"R3"
VALUE"249 Ohm"
CDS_LIB"discrete"
CDS_LOCATION"R3"
JEDEC_TYPE"res0603"
SOURCE_PACKAGE"R"
REUSE_ID"248"
REUSE_ANNOTATE"TRUE"
PART_NUMBER"EMA-00003608"
PART_TYPE"Thick Film"
DESCRIPTION"RES, Thick Film, 249 Ohm, 1.0 %, 1/10 W, SMD, 0603"
POWER"1/10 W"
TOLERANCE"1.0 %"
MPN"MCR03EZPFX2490"
MANUFACTURER"Rohm"
DISTRIBUTOR_PARTNUMBER"RHM249HTR-ND"
DISTRIBUTOR"Digikey"
DATASHEET"C:\EMA\CISQuickStart\Technical_Datasheets\Rohm\mcr03.pdf"
ROOM"MMC"
SEC"1"
1
$PN"1"16
2
$PN"2"12
%"r"
1,"(1725,-3125)","0","discrete","184P"
VALUE"4.7k"
$LOCATION"R52"
SEC"1"
ROOM"MMC_DISCRETE"
AVAILABILITY"In Stock"
DISTRIBUTOR"Digikey"
DISTRIBUTOR_PARTNUMBER"P4.70KLTR-ND"
MANUFACTURER"Panasonic"
MPN"ERJ-2RKF4701X"
TOLERANCE"1%"
POWER"1/10 W"
DESCRIPTION"RES SMD 4.7K OHM 1% 1/10W 0402"
PART_TYPE"Thick Film"
PART_NUMBER"ERJ-2RKF4701X"
SOURCE_PACKAGE"R"
JEDEC_TYPE"res0402"
CDS_LOCATION"R52"
CDS_LIB"discrete"
1
$PN"1"22
2
$PN"2"11
%"r"
1,"(950,-4075)","0","discrete","185P"
VALUE"1k"
$LOCATION"R113"
CDS_LIB"discrete"
CDS_LOCATION"R113"
JEDEC_TYPE"res0402"
SOURCE_PACKAGE"R"
ROOM"MMC_DISCRETE"
PART_NUMBER"ERJ-2RKF1001X"
PART_TYPE"Thick Film"
DESCRIPTION"RES SMD 1K OHM 1% 1/10W 0402"
POWER"1/16 W"
MANUFACTURER"Panasonic"
DISTRIBUTOR_PARTNUMBER"P1.00KLTR-ND"
DISTRIBUTOR"Digikey"
MPN"ERJ-2RKF1001X"
TOLERANCE"1%"
SEC"1"
DATASHEET"C:\EMA\CISQuickStart\Technical_Datasheets\Panasonic\AOA0000CE1.pdf"
1
$PN"1"14
2
$PN"2"34
%"r"
1,"(3650,-1075)","0","discrete","186P"
VALUE"33k"
$LOCATION"R57"
CDS_LIB"discrete"
CDS_LOCATION"R57"
JEDEC_TYPE"res0402"
SOURCE_PACKAGE"R"
ROOM"MMC_DISCRETE"
AVAILABILITY"In Stock"
DISTRIBUTOR"Digikey"
DISTRIBUTOR_PARTNUMBER"P33.0KLTR-ND"
MANUFACTURER"Panasonic"
MPN"ERJ-2RKF3302X"
TOLERANCE"1%"
POWER"1/10 W"
DESCRIPTION"RES SMD 33K OHM 1% 1/10W 0402"
PART_TYPE"Thick Film"
PART_NUMBER"ERJ-2RKF3302X"
SEC"1"
1
$PN"1"23
2
$PN"2"39
%"r"
1,"(800,-1200)","4","discrete","187P"
VALUE"150K"
$LOCATION"R111"
CDS_LIB"discrete"
CDS_LOCATION"R111"
JEDEC_TYPE"res0402"
SOURCE_PACKAGE"R"
DISTRIBUTOR"Digikey"
DISTRIBUTOR_PARTNUMBER"P150KLTR-ND"
MANUFACTURER"Panasonic"
MPN"ERJ-2RKF1873X"
TOLERANCE"1 %"
POWER"1/10 W"
DESCRIPTION"RES SMD 150K OHM 1% 1/10W 0402"
PART_TYPE"Thick Film"
PART_NUMBER"ERJ-2RKF1503X"
ROOM"MMC_DISCRETE"
SEC"1"
1
$PN"1"50
2
$PN"2"2
%"r"
1,"(5300,-2125)","0","discrete","188P"
$LOCATION"R102"
VALUE"33"
CDS_LIB"discrete"
CDS_LOCATION"R102"
JEDEC_TYPE"res0402"
SOURCE_PACKAGE"R"
ROOM"MMC_DISCRETE"
PART_NUMBER"ERJ-2RKF33R0X"
PART_TYPE"Thick Film"
DESCRIPTION"RES SMD 33 OHM 1% 1/10W 0402"
POWER"1/10W"
TOLERANCE"1.0 %"
MPN"ERJ-2RKF33R0X"
MANUFACTURER"Panasonic"
DISTRIBUTOR_PARTNUMBER"P33.0LTR-ND"
DISTRIBUTOR"Digikey"
DATASHEET"C:\EMA\CISQuickStart\Technical_Datasheets\Vishay\dcrcwe3.pdf"
SEC"1"
1
$PN"1"47
2
$PN"2"71
%"r"
1,"(775,-1700)","0","discrete","189P"
$LOCATION"R45"
VALUE"33k"
CDS_LIB"discrete"
CDS_LOCATION"R45"
JEDEC_TYPE"res0402"
SOURCE_PACKAGE"R"
ROOM"MMC_DISCRETE"
AVAILABILITY"In Stock"
DISTRIBUTOR"Digikey"
DISTRIBUTOR_PARTNUMBER"P33.0KLTR-ND"
MANUFACTURER"Panasonic"
MPN"ERJ-2RKF3302X"
TOLERANCE"1%"
POWER"1/10 W"
DESCRIPTION"RES SMD 33K OHM 1% 1/10W 0402"
PART_TYPE"Thick Film"
PART_NUMBER"ERJ-2RKF3302X"
SEC"1"
1
$PN"1"30
2
$PN"2"31
%"r"
1,"(525,-4075)","0","discrete","191P"
VALUE"1k"
$LOCATION"R107"
CDS_LIB"discrete"
CDS_LOCATION"R107"
JEDEC_TYPE"res0402"
SOURCE_PACKAGE"R"
ROOM"MMC_DISCRETE"
PART_NUMBER"ERJ-2RKF1001X"
PART_TYPE"Thick Film"
DESCRIPTION"RES SMD 1K OHM 1% 1/10W 0402"
POWER"1/16 W"
TOLERANCE"1%"
MPN"ERJ-2RKF1001X"
MANUFACTURER"Panasonic"
DISTRIBUTOR_PARTNUMBER"P1.00KLTR-ND"
DISTRIBUTOR"Digikey"
DATASHEET"C:\EMA\CISQuickStart\Technical_Datasheets\Panasonic\AOA0000CE1.pdf"
SEC"1"
1
$PN"1"14
2
$PN"2"68
%"r"
1,"(975,-3125)","0","discrete","193P"
VALUE"10K"
$LOCATION"R94"
SEC"1"
PART_NUMBER"M55342K11B10E0RS3"
PART_TYPE"Thick Film"
DESCRIPTION"RES SMD 10K OHM 1% 1/20W 0402"
POWER"1/10W"
TOLERANCE"1%"
MPN"M55342K11B10E0RS3"
MANUFACTURER"Vishay Dale"
DISTRIBUTOR_PARTNUMBER"1135-1061-1-ND"
DISTRIBUTOR"Digikey"
DATASHEET"C:\EMA\CISQuickStart\Technical_Datasheets\Vishay\dcrcwe3.pdf"
SOURCE_PACKAGE"R"
JEDEC_TYPE"res0402"
CDS_LOCATION"R94"
CDS_LIB"discrete"
1
$PN"1"22
2
$PN"2"36
%"ind"
1,"(3625,-825)","1","ind","194P"
VALUE"10 uH"
$LOCATION"L4"
CDS_LIB"ind"
CDS_LOCATION"L4"
JEDEC_TYPE"INDC2520X220N"
SOURCE_PACKAGE"IND"
ROOM"MMC_DISCRETE"
PART_NUMBER"74438323100"
PART_TYPE"Inductor"
DESCRIPTION"FIXED IND 10UH 600MA 843 MOHM"
RATING".6A"
TOLERANCE"20 %"
DCRESISTANCE"3.5 Ohm"
QFACTOR"25"
MPN"74438323100"
MANUFACTURER"Würth Elektronik"
DISTRIBUTOR_PARTNUMBER"732-4851-1-ND"
DISTRIBUTOR"Digikey"
DATASHEET"C:\EMA\CISQuickStart\Technical_Datasheets\Panasonic\AGA0000CE31.pdf"
SEC"1"
1
$PN"1"62
2
$PN"2"23
%"r"
1,"(3825,-1075)","0","discrete","196P"
$LOCATION"R93"
VALUE"33k"
CDS_LIB"discrete"
CDS_LOCATION"R93"
JEDEC_TYPE"res0402"
SOURCE_PACKAGE"R"
ROOM"MMC_DISCRETE"
PART_NUMBER"ERJ-2RKF3302X"
PART_TYPE"Thick Film"
DESCRIPTION"RES SMD 33K OHM 1% 1/10W 0402"
POWER"1/10 W"
TOLERANCE"1%"
MPN"ERJ-2RKF3302X"
MANUFACTURER"Panasonic"
DISTRIBUTOR_PARTNUMBER"P33.0KLTR-ND"
DISTRIBUTOR"Digikey"
AVAILABILITY"In Stock"
SEC"1"
1
$PN"1"23
2
$PN"2"40
%"cap_np"
1,"(1400,-3100)","1","ocad_parts_lib","198P"
VALUE"0.1UF"
$LOCATION"C53"
VOLTAGE"6.3V"
SEC"1"
CLASS"DISCRETE"
LAST_EDIT_BY"SNF"
ALT_SYMBOLS""
ROOM"MMC_DISCRETE"
PART_NUMBER"C0402C104K9RACTU"
PART_TYPE"Ceramic"
DESCRIPTION"0.1__F __10% 6.3V Ceramic Capacitor X7R 0402 (1005 Metric)"
TOLERANCE"10%"
PSPICE"C"
MPN"C0402C104K9RACTU"
MANUFACTURER"KEMET"
DISTRIBUTOR_PARTNUMBER"399-4872-1-ND"
DISTRIBUTOR"Digi-Key"
AVAILABILITY"In Stock"
SOURCE_PACKAGE"CAP_NP"
JEDEC_TYPE"cap0402"
CDS_LOCATION"C53"
CDS_LIB"ocad_parts_lib"
1
$PN"1"22
2
$PN"2"10
%"r"
1,"(925,-1700)","0","discrete","199P"
$LOCATION"R44"
VALUE"33k"
CDS_LIB"discrete"
CDS_LOCATION"R44"
JEDEC_TYPE"res0402"
SOURCE_PACKAGE"R"
ROOM"MMC_DISCRETE"
AVAILABILITY"In Stock"
DISTRIBUTOR"Digikey"
DISTRIBUTOR_PARTNUMBER"P33.0KLTR-ND"
MANUFACTURER"Panasonic"
MPN"ERJ-2RKF3302X"
TOLERANCE"1%"
POWER"1/10 W"
DESCRIPTION"RES SMD 33K OHM 1% 1/10W 0402"
PART_TYPE"Thick Film"
PART_NUMBER"ERJ-2RKF3302X"
SEC"1"
1
$PN"1"30
2
$PN"2"29
%"portleft-l"
1,"(6325,-1450)","2","mtca_interface_board","1P"
NAME"FPGA_PG"
CDS_LIB"mtca_interface_board"
HOTSPOT_0
HDL_PORT"IN"
PIN_NAME"FPGA_PG"80
%"cap_np"
1,"(4250,-2850)","1","ocad_parts_lib","200P"
VALUE"0.1UF"
$LOCATION"C93"
VOLTAGE"6.3V"
SEC"1"
CLASS"DISCRETE"
LAST_EDIT_BY"SNF"
ALT_SYMBOLS""
AVAILABILITY"In Stock"
DISTRIBUTOR"Digi-Key"
DISTRIBUTOR_PARTNUMBER"399-4872-1-ND"
MANUFACTURER"KEMET"
MPN"C0402C104K9RACTU"
PSPICE"C"
TOLERANCE"10%"
DESCRIPTION"0.1__F __10% 6.3V Ceramic Capacitor X7R 0402 (1005 Metric)"
PART_TYPE"Ceramic"
PART_NUMBER"C0402C104K9RACTU"
ROOM"MMC_DISCRETE"
SOURCE_PACKAGE"CAP_NP"
JEDEC_TYPE"cap0402"
CDS_LOCATION"C93"
CDS_LIB"ocad_parts_lib"
1
$PN"1"5
2
$PN"2"4
%"r"
1,"(4275,-2200)","0","discrete","201P"
$LOCATION"R104"
VALUE"390K"
CDS_LIB"discrete"
CDS_LOCATION"R104"
JEDEC_TYPE"res0402"
SOURCE_PACKAGE"R"
ROOM"MMC_DISCRETE"
PART_NUMBER"ERJ-2RKF3903X"
PART_TYPE"Thick Film"
DESCRIPTION"RES SMD 390K OHM 1% 1/10W 0402"
POWER"1/10 W"
TOLERANCE"1 %"
MPN"ERJ-2RKF3903X"
MANUFACTURER"Panasonic"
DISTRIBUTOR_PARTNUMBER"P390KLTR-ND"
DISTRIBUTOR"Digikey"
SEC"1"
1
$PN"1"60
2
$PN"2"19
%"r"
1,"(3125,-1275)","1","discrete","203P"
VALUE"49.9"
$LOCATION"R55"
CDS_LIB"discrete"
CDS_LOCATION"R55"
JEDEC_TYPE"res0402"
SOURCE_PACKAGE"R"
ROOM"MMC_DISCRETE"
DATASHEET"C:\EMA\CISQuickStart\Technical_Datasheets\Vishay\dcrcwe3.pdf"
DISTRIBUTOR"Digikey"
DISTRIBUTOR_PARTNUMBER"P49.9LTR-ND"
MANUFACTURER"Panasonic"
MPN"ERJ-2RKF49R9X"
TOLERANCE"1.0 %"
POWER"1/10W"
DESCRIPTION"RES SMD 49.9 OHM 1% 1/10W 0402"
PART_TYPE"Thick Film"
PART_NUMBER"ERJ-2RKF49R9X"
SEC"1"
1
$PN"1"61
2
$PN"2"39
%"vcc_bar"
1,"(4050,-525)","0","mtca_interface_board","204P"
HDL_POWER"MP3V3"
CDS_LIB"mtca_interface_board"
HOTSPOT_023
%"vcc_bar"
1,"(1225,-2875)","0","mtca_interface_board","205P"
HDL_POWER"MP3V3"
CDS_LIB"mtca_interface_board"
HOTSPOT_022
%"vcc_bar"
1,"(475,-3800)","0","mtca_interface_board","206P"
HDL_POWER"MP3V3"
CDS_LIB"mtca_interface_board"
HOTSPOT_014
%"vcc_bar"
1,"(2750,-4575)","0","mtca_interface_board","207P"
HDL_POWER"MP3V3"
CDS_LIB"mtca_interface_board"
HOTSPOT_021
%"vcc_bar"
1,"(4025,-2525)","0","mtca_interface_board","208P"
HDL_POWER"MP3V3"
CDS_LIB"mtca_interface_board"
HOTSPOT_05
%"gnd"
1,"(3325,-1150)","0","mtca_interface_board","38P"
CDS_LIB"mtca_interface_board"
HDL_POWER"GND"
HOTSPOT_020
%"gnd"
1,"(4625,-2525)","0","mtca_interface_board","39P"
CDS_LIB"mtca_interface_board"
HDL_POWER"GND"
HOTSPOT_019
%"portboth-r_1"
1,"(6000,-1750)","0","mtca_interface_board","3P"
NAME"BP<180..0>"
CDS_LIB"mtca_interface_board"
HOTSPOT_0
HDL_PORT"INOUT"
PIN_NAME"BP<180..0>"82,81
%"gnd"
1,"(300,-1500)","0","mtca_interface_board","40P"
CDS_LIB"mtca_interface_board"
HDL_POWER"GND"
HOTSPOT_06
%"gnd"
1,"(1125,-3625)","0","mtca_interface_board","41P"
HDL_POWER"GND"
CDS_LIB"mtca_interface_board"
HOTSPOT_07
%"gnd"
1,"(6200,-3350)","0","mtca_interface_board","4P"
CDS_LIB"mtca_interface_board"
HDL_POWER"GND"
HOTSPOT_018
%"BUSWIDE_TOP_LEFT_RIP"
1,"(6450,-2100)","0","default","I220"
CDS_LIB"default"
BODY_TYPE"PLUMBING"
HDL_TAP"TRUE"
WIRE \NWC \NAC
BN"4..2"90
BUNDLE \NWC \NAC82,81
%"BUSWIDE_TOP_LEFT_RIP"
1,"(6450,-2050)","0","default","I221"
CDS_LIB"default"
BODY_TYPE"PLUMBING"
HDL_TAP"TRUE"
WIRE \NWC \NAC
BN"1..0"89
BUNDLE \NWC \NAC82,81
%"BUS_TOP_LEFT_RIP"
1,"(6450,-1850)","0","default","I222"
CDS_LIB"default"
BODY_TYPE"PLUMBING"
HDL_TAP"TRUE"
BUS_END \NWC \NAC82,81
NET_END \NWC \NAC
BN"86"85
%"BUS_TOP_LEFT_RIP"
1,"(6450,-1900)","0","default","I223"
CDS_LIB"default"
BODY_TYPE"PLUMBING"
HDL_TAP"TRUE"
BUS_END \NWC \NAC82,81
NET_END \NWC \NAC
BN"85"74
%"BUS_TOP_LEFT_RIP"
1,"(6450,-1950)","0","default","I224"
CDS_LIB"default"
BODY_TYPE"PLUMBING"
HDL_TAP"TRUE"
BUS_END \NWC \NAC82,81
NET_END \NWC \NAC
BN"84"94
%"BUS_TOP_LEFT_RIP"
1,"(6450,-2000)","0","default","I225"
CDS_LIB"default"
BODY_TYPE"PLUMBING"
HDL_TAP"TRUE"
BUS_END \NWC \NAC82,81
NET_END \NWC \NAC
BN"83"88
%"BUS_TOP_LEFT_RIP"
1,"(6450,-2150)","0","default","I226"
CDS_LIB"default"
BODY_TYPE"PLUMBING"
HDL_TAP"TRUE"
BUS_END \NWC \NAC82,81
NET_END \NWC \NAC
BN"88"91
%"BUS_TOP_LEFT_RIP"
1,"(6450,-2200)","0","default","I227"
CDS_LIB"default"
BODY_TYPE"PLUMBING"
HDL_TAP"TRUE"
BUS_END \NWC \NAC82,81
NET_END \NWC \NAC
BN"78"92
%"BUS_TOP_LEFT_RIP"
1,"(6450,-2250)","0","default","I228"
CDS_LIB"default"
BODY_TYPE"PLUMBING"
HDL_TAP"TRUE"
BUS_END \NWC \NAC82,81
NET_END \NWC \NAC
BN"77"93
%"BUS_TOP_LEFT_RIP"
1,"(6450,-2300)","0","default","I229"
CDS_LIB"default"
BODY_TYPE"PLUMBING"
HDL_TAP"TRUE"
BUS_END \NWC \NAC82,81
NET_END \NWC \NAC
BN"87"87
%"6 MERGE"
1,"(6475,-900)","2","standard","I230"
CDS_LIB"standard"
HDL_CONCAT"TRUE"
NEEDS_NO_SIZE"TRUE"
BODY_TYPE"PLUMBING"
A\NWC\NAC77
B\NWC\NAC78
C\NWC\NAC38
D\NWC\NAC84
E\NWC\NAC83
F\NWC\NAC86
Y\NWC\NAC79
%"portboth-r"
1,"(5750,-850)","0","mtca_interface_board","I231"
CDS_LIB"mtca_interface_board"
HOTSPOT_0
PIN_NAME"POWER<10..0>"
HDL_PORT"INOUT"79
%"RSMD0603"
1,"(1550,-3350)","0","cnpassive","I232"
$LOCATION"R?"
TOL""
VALUE"00"
CDS_LIB"cnpassive"
TC2"RTMPQ"
TC1"RTMPL"
MAX_TEMP"RTMAX"
SLOPE"RSMAX"
VOLTAGE"RVMAX"
POWER"RMAX"
DIST"FLAT"
NEGTOL"RTOL%"
POSTOL"RTOL%"
TOL_ON_OFF"ON"
SIZE"1B"
PACK_TYPE""
B <SIZE-1..0>\NAC11
A <SIZE-1..0>\NAC76
%"RSMD0603"
1,"(750,-3350)","0","cnpassive","I233"
$LOCATION"R?"
VALUE"00"
TOL""
SIZE"1B"
TOL_ON_OFF"ON"
POSTOL"RTOL%"
NEGTOL"RTOL%"
DIST"FLAT"
POWER"RMAX"
VOLTAGE"RVMAX"
SLOPE"RSMAX"
MAX_TEMP"RTMAX"
TC1"RTMPL"
TC2"RTMPQ"
CDS_LIB"cnpassive"
PACK_TYPE""
B <SIZE-1..0>\NAC36
A <SIZE-1..0>\NAC33
%"ATMGA128"
1,"(2425,-2025)","0","ocad_parts_lib","I235"
$LOCATION"?"
PART_NUMBER"ATMEGA128A-AU"
SOURCE_PACKAGE"ATMGA128"
PACK_TYPE"TQFP"
CDS_LIB"ocad_parts_lib"
CDS_LMAN_SYM_OUTLINE"-400,1050,350,-1100"
GND1
$PN"?"15
GND2
$PN"?"15
GND3
$PN"?"15
VCC1
$PN"?"23
VCC2
$PN"?"23
PEN* \B
$PN"?"
OUTPUT_LOAD"(1.0,-1.0)"
INPUT_LOAD"(-0.01,0.01)"0
PE0
$PN"?"
OUTPUT_LOAD"(1.0,-1.0)"
INPUT_LOAD"(-0.01,0.01)"69
PE1
$PN"?"
OUTPUT_LOAD"(1.0,-1.0)"
INPUT_LOAD"(-0.01,0.01)"0
PE2
$PN"?"
OUTPUT_LOAD"(1.0,-1.0)"
INPUT_LOAD"(-0.01,0.01)"60
PE3
$PN"?"
OUTPUT_LOAD"(1.0,-1.0)"
INPUT_LOAD"(-0.01,0.01)"43
PE4
$PN"?"
OUTPUT_LOAD"(1.0,-1.0)"
INPUT_LOAD"(-0.01,0.01)"63
PE5
$PN"?"
OUTPUT_LOAD"(1.0,-1.0)"
INPUT_LOAD"(-0.01,0.01)"64
PE6
$PN"?"
OUTPUT_LOAD"(1.0,-1.0)"
INPUT_LOAD"(-0.01,0.01)"0
PE7
$PN"?"
OUTPUT_LOAD"(1.0,-1.0)"
INPUT_LOAD"(-0.01,0.01)"0
PB0
$PN"?"
OUTPUT_LOAD"(1.0,-1.0)"
INPUT_LOAD"(-0.01,0.01)"30
PB1
$PN"?"
OUTPUT_LOAD"(1.0,-1.0)"
INPUT_LOAD"(-0.01,0.01)"29
PB2
$PN"?"
OUTPUT_LOAD"(1.0,-1.0)"
INPUT_LOAD"(-0.01,0.01)"31
PB3
$PN"?"
OUTPUT_LOAD"(1.0,-1.0)"
INPUT_LOAD"(-0.01,0.01)"28
PB4
$PN"?"
OUTPUT_LOAD"(1.0,-1.0)"
INPUT_LOAD"(-0.01,0.01)"0
PB5
$PN"?"
OUTPUT_LOAD"(1.0,-1.0)"
INPUT_LOAD"(-0.01,0.01)"58
PB6
$PN"?"
OUTPUT_LOAD"(1.0,-1.0)"
INPUT_LOAD"(-0.01,0.01)"57
PB7
$PN"?"
OUTPUT_LOAD"(1.0,-1.0)"
INPUT_LOAD"(-0.01,0.01)"56
PG3
$PN"?"
OUTPUT_LOAD"(1.0,-1.0)"
INPUT_LOAD"(-0.01,0.01)"0
PG4
$PN"?"
OUTPUT_LOAD"(1.0,-1.0)"
INPUT_LOAD"(-0.01,0.01)"0
RESET* \B
$PN"?"
OUTPUT_LOAD"(1.0,-1.0)"
INPUT_LOAD"(-0.01,0.01)"73
XTAL2
$PN"?"
OUTPUT_LOAD"(1.0,-1.0)"
INPUT_LOAD"(-0.01,0.01)"0
XTAL1
$PN"?"
OUTPUT_LOAD"(1.0,-1.0)"
INPUT_LOAD"(-0.01,0.01)"0
PD0
$PN"?"
OUTPUT_LOAD"(1.0,-1.0)"
INPUT_LOAD"(-0.01,0.01)"61
PD1
$PN"?"
OUTPUT_LOAD"(1.0,-1.0)"
INPUT_LOAD"(-0.01,0.01)"40
PD2
$PN"?"
OUTPUT_LOAD"(1.0,-1.0)"
INPUT_LOAD"(-0.01,0.01)"41
PD3
$PN"?"
OUTPUT_LOAD"(1.0,-1.0)"
INPUT_LOAD"(-0.01,0.01)"0
PD4
$PN"?"
OUTPUT_LOAD"(1.0,-1.0)"
INPUT_LOAD"(-0.01,0.01)"72
PD5
$PN"?"
OUTPUT_LOAD"(1.0,-1.0)"
INPUT_LOAD"(-0.01,0.01)"42
PD6
$PN"?"
OUTPUT_LOAD"(1.0,-1.0)"
INPUT_LOAD"(-0.01,0.01)"0
PD7
$PN"?"
OUTPUT_LOAD"(1.0,-1.0)"
INPUT_LOAD"(-0.01,0.01)"0
PG0
$PN"?"
OUTPUT_LOAD"(1.0,-1.0)"
INPUT_LOAD"(-0.01,0.01)"0
PG1
$PN"?"
OUTPUT_LOAD"(1.0,-1.0)"
INPUT_LOAD"(-0.01,0.01)"0
PC0
$PN"?"
OUTPUT_LOAD"(1.0,-1.0)"
INPUT_LOAD"(-0.01,0.01)"0
PC1
$PN"?"
OUTPUT_LOAD"(1.0,-1.0)"
INPUT_LOAD"(-0.01,0.01)"0
PC2
$PN"?"
OUTPUT_LOAD"(1.0,-1.0)"
INPUT_LOAD"(-0.01,0.01)"0
PC3
$PN"?"
OUTPUT_LOAD"(1.0,-1.0)"
INPUT_LOAD"(-0.01,0.01)"0
PC4
$PN"?"
OUTPUT_LOAD"(1.0,-1.0)"
INPUT_LOAD"(-0.01,0.01)"0
PC5
$PN"?"
OUTPUT_LOAD"(1.0,-1.0)"
INPUT_LOAD"(-0.01,0.01)"0
PC6
$PN"?"
OUTPUT_LOAD"(1.0,-1.0)"
INPUT_LOAD"(-0.01,0.01)"0
PC7
$PN"?"
OUTPUT_LOAD"(1.0,-1.0)"
INPUT_LOAD"(-0.01,0.01)"27
PG2
$PN"?"
OUTPUT_LOAD"(1.0,-1.0)"
INPUT_LOAD"(-0.01,0.01)"0
PA7
$PN"?"
OUTPUT_LOAD"(1.0,-1.0)"
INPUT_LOAD"(-0.01,0.01)"0
PA6
$PN"?"
OUTPUT_LOAD"(1.0,-1.0)"
INPUT_LOAD"(-0.01,0.01)"0
PA5
$PN"?"
OUTPUT_LOAD"(1.0,-1.0)"
INPUT_LOAD"(-0.01,0.01)"0
PA4
$PN"?"
OUTPUT_LOAD"(1.0,-1.0)"
INPUT_LOAD"(-0.01,0.01)"0
PA3
$PN"?"
OUTPUT_LOAD"(1.0,-1.0)"
INPUT_LOAD"(-0.01,0.01)"0
PA2
$PN"?"
OUTPUT_LOAD"(1.0,-1.0)"
INPUT_LOAD"(-0.01,0.01)"59
PA1
$PN"?"
OUTPUT_LOAD"(1.0,-1.0)"
INPUT_LOAD"(-0.01,0.01)"0
PA0
$PN"?"
OUTPUT_LOAD"(1.0,-1.0)"
INPUT_LOAD"(-0.01,0.01)"55
PF7
$PN"?"
OUTPUT_LOAD"(1.0,-1.0)"
INPUT_LOAD"(-0.01,0.01)"51
PF6
$PN"?"
OUTPUT_LOAD"(1.0,-1.0)"
INPUT_LOAD"(-0.01,0.01)"1
PF5
$PN"?"
OUTPUT_LOAD"(1.0,-1.0)"
INPUT_LOAD"(-0.01,0.01)"52
PF4
$PN"?"
OUTPUT_LOAD"(1.0,-1.0)"
INPUT_LOAD"(-0.01,0.01)"53
PF3
$PN"?"
OUTPUT_LOAD"(1.0,-1.0)"
INPUT_LOAD"(-0.01,0.01)"0
PF2
$PN"?"
OUTPUT_LOAD"(1.0,-1.0)"
INPUT_LOAD"(-0.01,0.01)"0
PF1
$PN"?"
OUTPUT_LOAD"(1.0,-1.0)"
INPUT_LOAD"(-0.01,0.01)"65
PF0
$PN"?"
OUTPUT_LOAD"(1.0,-1.0)"
INPUT_LOAD"(-0.01,0.01)"54
AREF
$PN"?"
OUTPUT_LOAD"(1.0,-1.0)"
INPUT_LOAD"(-0.01,0.01)"62
AVCC
$PN"?"
OUTPUT_LOAD"(1.0,-1.0)"
INPUT_LOAD"(-0.01,0.01)"62
%"HEADER2X1"
1,"(700,-3500)","0","oxflib","I236"
$LOCATION"?"
MANUF"HARWIN"
PACK_TYPE"STR"
CDS_LIB"oxflib"
SIZE"1B"
OL_COMMENTS"-"
KL_COMMENTS"-"
PL_COMMENTS"-"
B <SIZE-1..0>\NAC36
A <SIZE-1..0>\NAC17
%"gnd"
1,"(400,-3575)","0","mtca_interface_board","I237"
CDS_LIB"mtca_interface_board"
HDL_POWER"GND"
HOTSPOT_017
%"SHF-105-01-L-D-SM"
1,"(1300,-4450)","0","oxflib","I238"
CDS_LMAN_SYM_OUTLINE"-125,125,125,-125"
CDS_LIB"oxflib"
23
414
666
80
103
567
337
168
70
934
%"R"
1,"(4700,-1925)","1","discrete","I239"
LOCATION"R103"
PART_NUMBER"DNF"
SOURCE_PACKAGE"R"
CDS_LIB"discrete"
1
$PN"?"43
2
$PN"?"70
%"SS16FP"
1,"(5175,-2125)","1","oxflib","I240"
CDS_LIB"oxflib"
CDS_LMAN_SYM_OUTLINE"-125,125,125,-125"
C70
A71
%"R"
1,"(4675,-1875)","1","discrete","I241"
$LOCATION"$"
PART_NUMBER"DNF"
CDS_LIB"discrete"
SOURCE_PACKAGE"R"
1
$PN"?"60
2
$PN"?"47
%"RSMD0603"
1,"(1600,-4450)","0","cnpassive","I242"
$LOCATION"R?"
TOL""
VALUE"00"
CDS_LIB"cnpassive"
TC2"RTMPQ"
TC1"RTMPL"
MAX_TEMP"RTMAX"
SLOPE"RSMAX"
VOLTAGE"RVMAX"
POWER"RMAX"
DIST"FLAT"
NEGTOL"RTOL%"
POSTOL"RTOL%"
TOL_ON_OFF"ON"
SIZE"1B"
PACK_TYPE""
B <SIZE-1..0>\NAC32
A <SIZE-1..0>\NAC66
%"vcc_bar"
1,"(3100,-3575)","0","mtca_interface_board","I245"
HDL_POWER"MP3V3"
CDS_LIB"mtca_interface_board"
HOTSPOT_08
%"vcc_bar"
1,"(3350,-3575)","0","mtca_interface_board","I248"
HDL_POWER"MP3V3"
CDS_LIB"mtca_interface_board"
HOTSPOT_09
%"RSMD0603"
1,"(3150,-4325)","1","cnpassive","I249"
$LOCATION"R?"
TOL"1%"
VALUE"20"
SIZE"1B"
TOL_ON_OFF"ON"
POSTOL"RTOL%"
NEGTOL"RTOL%"
DIST"FLAT"
POWER"RMAX"
VOLTAGE"RVMAX"
SLOPE"RSMAX"
MAX_TEMP"RTMAX"
TC1"RTMPL"
TC2"RTMPQ"
CDS_LIB"cnpassive"
PACK_TYPE"1/10W"
B <SIZE-1..0>\NAC13
A <SIZE-1..0>\NAC46
%"RSMD0603"
1,"(3400,-4325)","1","cnpassive","I250"
$LOCATION"R?"
TOL"1%"
VALUE"270"
SIZE"1B"
TOL_ON_OFF"ON"
POSTOL"RTOL%"
NEGTOL"RTOL%"
DIST"FLAT"
POWER"RMAX"
VOLTAGE"RVMAX"
SLOPE"RSMAX"
MAX_TEMP"RTMAX"
TC1"RTMPL"
TC2"RTMPQ"
CDS_LIB"cnpassive"
PACK_TYPE"1/16W"
B <SIZE-1..0>\NAC26
A <SIZE-1..0>\NAC35
%"WURTH_SMSW"
1,"(3400,-3875)","3","bris_cds_discrete","I252"
$LOCATION"?"
VALUE"155060RS73200"
MANUF""
PACK_TYPE"SMD"
CDS_LIB"bris_cds_discrete"
CDS_LMAN_SYM_OUTLINE"-50,100,50,-50"
A9
WURTH SMSW
$PN"?"26
%"KINGBRIGHT_KPA"
1,"(3150,-3875)","3","bris_cds_discrete","I253"
$LOCATION"?"
MANUF""
VALUE"KPA-2107LVVBC-D"
PACK_TYPE"SMD"
CDS_LMAN_SYM_OUTLINE"-50,100,50,-50"
CDS_LIB"bris_cds_discrete"
213
18
END.
