uob-hep-cad/uob-hep-pc072/hardware/Cadence/top/mtca_interface_board_reocc/front_panel_jtag_serial/sch_1/page1.csv

FILE_TYPE = CONNECTIVITY
{Allegro Design Entry HDL 24.1 P001 (4234998) 9/4/2024}
PAGE_NUMBER = 1
0"NC"
1"UN$1$RSMD0603$I131$B"
2"USB_DM"
3"GND\g"
4"VCC3V3\g"
5"UART_TX_FROM_FPGA_3V3"
6"UART_RX_TO_FPGA_3V3"
7"GND\g"
8"VREF_JTAG\g"
9"TCK"
10"TDO"
11"TDI"
12"TMS"
13"GND\g"
14"VCC3V3\g"
15"USB_DP"
16"UN$1$74LVC07A$I178$Y$1"
17"P5V\g"
18"UN$1$74LVC07A$I178$Y$2"
19"UN$1$74LVC07A$I178$Y$5"
20"UN$1$74LVC07A$I178$Y$4"
21"UN$1$74LVC07A$I178$Y"
22"GND\g"
23"GND\g"
24"GND\g"
25"GND\G"
26"GND\G"
27"GND\g"
28"GND\g"
29"GND\g"
30"GND\g"
31"GND\g"
32"GND\g"
33"GND\g"
34"GND\g"
35"GND\g"
36"GND"
37"AUXIO_N6"
38"LED_2B"
39"GND"
40"VREF_JTAG\g"
41"GND"
42"MP3V3\G"
43"MP3V3\G"
44"VCC3V3\g"
45"VCC3V3\g"
46"VCC3V3\g"
47"GND"
48"GND\g"
49"AUXIO_P2"
50"LED_3B"
51"AUXIO_P6"
52"GND"
53"AUXIO_P1"
54"AUXIO_P2"
55"AUXIO_N2"
56"AUXIO_P6"
57"LED_1B"
58"LED_1R"
59"AUXIO_N2"
60"GND"
61"GND"
62"GND"
63"AUXIO_N6"
64"GND"
65"GND"
66"LED_2R"
67"GND"
68"GND"
69"GND"
70"LED_3R"
71"UN$1$CON16PUSBCUSB2$I148$DB$1"
72"UN$1$CON16PUSBCUSB2$I148$DB"
73"GND"
74"GND"
75"GND"
76"GND"
77"UN$1$LED1BICOLOR4P$I192$A2"
78"MMC_TDO"
79"MMC_TMS"
80"MMC_SPARE"
81"MMC_TCK"
82"MMC_SPARE"
83"MMC_TMS"
84"MMC_TDO"
85"MMC_TCK"
86"MMC_TDI"
87"UN$1$RSMD0603$I169$B"
88"UN$1$RSMD0603$I170$A"
89"MMC_RESET*"
90"UN$1$CON16PUSBCUSB2$I148$CC1"
91"LED_1R"
92"LED_3B"
93"UN$1$CON16PUSBCUSB2$I148$CC2"
94"LED_1B"
95"LED_2R"
96"LED_3R"
97"MMC_TRST*"
98"MMC_TDI"
99"MMC_TRST*"
100"MMC_RESET*"
101"UN$1$CAPCERSMDCL2$I205$B"
102"2V5"
103"UN$1$LED1BICOLOR4P$I192$A1"
104"UN$1$LED1BICOLOR4P$I190$A1"
105"UN$1$LED1BICOLOR4P$I190$A2"
106"UN$1$LED1BICOLOR4P$I191$A2"
107"UN$1$LED1BICOLOR4P$I191$A1"
108"UN$1$74LVC07A$I178$Y$3"
109"LED_2B"
110"2V5"
%"vcc_bar"
1,"(2525,-150)","0","mtca_interface_board","I101"
HDL_POWER"VREF_JTAG"
CDS_LIB"mtca_interface_board"
HOTSPOT_040
%"mt_hole"
1,"(-25,-600)","1","ocad_parts_lib","I106"
CDS_SEC"1"
VALUE"Mt_Hole"
$LOCATION"MH2"
CDS_LIB"ocad_parts_lib"
JEDEC_TYPE"mounthole"
SOURCE_PACKAGE"Mt_Hole"
ROOM"TE0712"
REUSE_ANNOTATE"TRUE"
PART_NUMBER"Mt_Hole"
PART_TYPE"Misc"
DESCRIPTION"PCB MOUNT-HOLE PAD200C_128 DRILL"
MPN"Mt_Hole"
MANUFACTURER"HEP"
DISTRIBUTOR_PARTNUMBER"Mt_Hole"
$REUSE_ID"175"
CDS_LOCATION"MH2"
SEC"1"
MH_SIG \B
$PN"1"41
%"gnd"
1,"(-25,-800)","0","mtca_interface_board","I107"
CDS_LIB"mtca_interface_board"
HDL_POWER"GND"
HOTSPOT_041
%"mt_hole"
1,"(-350,-600)","1","ocad_parts_lib","I109"
CDS_SEC"1"
$LOCATION"MH1"
VALUE"Mt_Hole"
DISTRIBUTOR_PARTNUMBER"Mt_Hole"
MANUFACTURER"HEP"
MPN"Mt_Hole"
DESCRIPTION"PCB MOUNT-HOLE PAD200C_128 DRILL"
PART_TYPE"Misc"
PART_NUMBER"Mt_Hole"
REUSE_ANNOTATE"TRUE"
ROOM"TE0712"
REUSE_ID"175"
SOURCE_PACKAGE"Mt_Hole"
JEDEC_TYPE"mounthole"
CDS_LIB"ocad_parts_lib"
CDS_LOCATION"MH1"
SEC"1"
MH_SIG \B
$PN"1"41
%"mt_hole"
1,"(-675,-600)","1","ocad_parts_lib","I110"
CDS_SEC"1"
$LOCATION"MH4"
VALUE"Mt_Hole"
SEC"1"
CDS_LOCATION"MH4"
DISTRIBUTOR"HEP"
DISTRIBUTOR_PARTNUMBER"Mt_Hole"
MANUFACTURER"HEP"
MPN"Mt_Hole"
DESCRIPTION"PCB MOUNT-HOLE PAD200C_128 DRILL"
PART_TYPE"Misc"
PART_NUMBER"Mt_Hole"
REUSE_ANNOTATE"TRUE"
SOURCE_PACKAGE"Mt_Hole"
JEDEC_TYPE"mounthole"
CDS_LIB"ocad_parts_lib"
MH_SIG \B
$PN"1"41
%"P5V"
1,"(1750,-925)","0","cnpower","I113"
HDL_POWER"P5V"
CDS_LIB"cnpower"
BODY_TYPE"PLUMBING"
SIZE"1B"
A<SIZE-1..0>\NAC
VHDL_INIT"1"17
%"CAPCERSMDCL2"
1,"(1150,-1225)","1","cnpassive","I122"
CDS_LOCATION"C1"
CDS_SEC"1"
$SEC"1"
$LOCATION"C1"
VALUE"100NF"
VOLTAGE"16V"
PACK_TYPE"0603"
CDS_LIB"cnpassive"
SIZE"1"
A <SIZE-1..0>\NAC
$PN"1"24
B <SIZE-1..0>\NAC
$PN"2"17
%"410_357_B"
1,"(2125,-1500)","0","bris_cds_pld","I128"
MANUFACTURER_PART_NUMBER"410-357-B"
MANUFACTURER_NAME"DIGILENT"
PACK_TYPE"OTHER"
CDS_LIB"bris_cds_pld"
$LOCATION"IC1"
CDS_LMAN_SYM_OUTLINE"450,250,1300,-575"
VBUS_DETECT1
USB_DP15
USB_DM2
VDD14
GND_313
TMS12
TDI11
TDO10
TCK9
PS_SRST_B0
VREF_JTAG8
GND_27
TXD6
RXD5
RTS0
CTS0
VREF
$PN"2"4
GND_13
%"gnd"
1,"(975,-2025)","0","mtca_interface_board","I130"
CDS_LIB"mtca_interface_board"
HDL_POWER"GND"
HOTSPOT_022
%"RSMD0603"
1,"(2075,-2025)","1","cnpassive","I131"
CDS_LOCATION"R2"
CDS_SEC"1"
$SEC"1"
TOL"1%"
VALUE"10K"
$LOCATION"R2"
PACK_TYPE"1/10W"
CDS_LIB"cnpassive"
SIZE"1B"
TOL_ON_OFF"ON"
POSTOL"RTOL%"
NEGTOL"RTOL%"
DIST"FLAT"
POWER"RMAX"
VOLTAGE"RVMAX"
SLOPE"RSMAX"
MAX_TEMP"RTMAX"
TC1"RTMPL"
TC2"RTMPQ"
B <SIZE-1..0>\NAC
$PN"2"1
A <SIZE-1..0>\NAC
$PN"1"23
%"RSMD0603"
1,"(2075,-1325)","1","cnpassive","I132"
CDS_LOCATION"R1"
CDS_SEC"1"
$SEC"1"
TOL"1%"
VALUE"4.7K"
$LOCATION"R1"
PACK_TYPE"1/10W"
CDS_LIB"cnpassive"
TC2"RTMPQ"
TC1"RTMPL"
MAX_TEMP"RTMAX"
SLOPE"RSMAX"
VOLTAGE"RVMAX"
POWER"RMAX"
DIST"FLAT"
NEGTOL"RTOL%"
POSTOL"RTOL%"
TOL_ON_OFF"ON"
SIZE"1B"
B <SIZE-1..0>\NAC
$PN"2"17
A <SIZE-1..0>\NAC
$PN"1"1
%"gnd"
1,"(2775,-2400)","0","mtca_interface_board","I133"
CDS_LIB"mtca_interface_board"
HDL_POWER"GND"
HOTSPOT_03
%"gnd"
1,"(2025,-2250)","0","mtca_interface_board","I134"
HDL_POWER"GND"
CDS_LIB"mtca_interface_board"
HOTSPOT_023
%"gnd"
1,"(3775,-1725)","0","mtca_interface_board","I135"
CDS_LIB"mtca_interface_board"
HDL_POWER"GND"
HOTSPOT_07
%"vcc_bar"
1,"(3625,-1225)","0","mtca_interface_board","I136"
HDL_POWER"VREF_JTAG"
CDS_LIB"mtca_interface_board"
HOTSPOT_08
%"vcc_bar"
1,"(2150,-1025)","0","mtca_interface_board","I137"
HDL_POWER"VCC3V3"
CDS_LIB"mtca_interface_board"
HOTSPOT_014
%"gnd"
1,"(2650,-1150)","0","mtca_interface_board","I138"
HDL_POWER"GND"
CDS_LIB"mtca_interface_board"
HOTSPOT_013
%"vcc_bar"
1,"(2225,-2275)","0","mtca_interface_board","I139"
HDL_POWER"VCC3V3"
CDS_LIB"mtca_interface_board"
HOTSPOT_04
%"gnd"
1,"(1100,-1400)","0","mtca_interface_board","I140"
CDS_LIB"mtca_interface_board"
HDL_POWER"GND"
HOTSPOT_024
%"CON16P_USB_C_USB2"
1,"(-175,-1850)","0","bris_cds_discrete","I148"
CDS_LOCATION"J2"
CDS_SEC"1"
$LOCATION"J2"
$SEC"1"
TYPE"2137160001"
CDS_LMAN_SYM_OUTLINE"-250,400,250,-400"
PCB_FOOTPRINT"MOLEX_2137160001"
SNAPEDA_LINK"https://www.snapeda.com/parts/2137160001/Molex/view-part/?ref=snap"
DESCRIPTION"USB-C (USB TYPE-C) USB 2.0 Receptacle Connector 24 (16+8 Dummy) Position Through Hole, Right Angle"
PACKAGE"None"
MF"Molex"
MP"2137160001"
CHECK_PRICES"https://www.snapeda.com/parts/2137160001/Molex/view-part/?ref=eda"
ORIGINALSYMBOLORIGIN"(-50000,80000)"
PIN_NUMBERS_VISIBLE"True"
PIN_TEXT_VISIBLE"True"
PIN_NAMES_ROTATE"True"
CDS_LIB"bris_cds_discrete"
IMPLEMENTATION_PATH"NONE"
IMPLEMENTATION"NONE"
VBUS4
$PN"B9"17
GND4
$PN"B12"48
VBUS3
$PN"B4"17
GND3
$PN"B1"48
SHIELD4
$PN"SH4"48
SHIELD3
$PN"SH3"48
SHIELD2
$PN"SH2"48
SHIELD1
$PN"SH1"48
DB-
$PN"B7"72
DB+
$PN"B6"71
CC2
$PN"B5"93
SBU2
$PN"B8"0
VBUS2
$PN"A9"17
GND2
$PN"A12"48
SBU1
$PN"A8"0
DA-
$PN"A7"72
DA+
$PN"A6"71
CC1
$PN"A5"90
VBUS1
$PN"A4"17
GND1
$PN"A1"48
%"vcc_bar"
1,"(100,-3400)","0","mtca_interface_board","I149"
HDL_POWER"MP3V3"
CDS_LIB"mtca_interface_board"
HOTSPOT_042
%"gnd"
1,"(175,-4050)","0","mtca_interface_board","I150"
HDL_POWER"GND"
CDS_LIB"mtca_interface_board"
HOTSPOT_025
%"SHF-105-01-L-D-RA"
3,"(-225,-3725)","0","bris_cds_discrete","I151"
CDS_LOCATION"J4"
CDS_SEC"1"
$SEC"1"
$LOCATION"J4"
TYPE"SHF-105-01-L-D-RA"
CDS_LMAN_SYM_OUTLINE"-75,150,75,-150"
CDS_LIB"bris_cds_discrete"
A<4>
$PN"5"79
A<2>
$PN"3"78
A<0>
$PN"1"81
A<8>
$PN"9"98
A<6>
$PN"7"80
A<9>
$PN"10"25
A<7>
$PN"8"99
A<5>
$PN"6"100
A<3>
$PN"4"42
A<1>
$PN"2"25
%"SHF-105-01-X-D-SM"
3,"(-225,-4600)","0","bris_cds_discrete","I156"
CDS_LOCATION"J5"
CDS_SEC"1"
$SEC"1"
$LOCATION"J5"
TYPE"SHF-105-01-X-D-SM"
CDS_LIB"bris_cds_discrete"
CDS_LMAN_SYM_OUTLINE"-75,150,75,-150"
A<4>
$PN"5"83
A<2>
$PN"3"84
A<0>
$PN"1"85
A<8>
$PN"9"86
A<6>
$PN"7"87
A<9>
$PN"10"26
A<7>
$PN"8"97
A<5>
$PN"6"88
A<3>
$PN"4"43
A<1>
$PN"2"26
%"vcc_bar"
1,"(100,-4275)","0","mtca_interface_board","I157"
HDL_POWER"MP3V3"
CDS_LIB"mtca_interface_board"
HOTSPOT_043
%"gnd"
1,"(175,-4925)","0","mtca_interface_board","I159"
HDL_POWER"GND"
CDS_LIB"mtca_interface_board"
HOTSPOT_026
%"gnd"
1,"(400,-2400)","0","mtca_interface_board","I160"
HDL_POWER"GND"
CDS_LIB"mtca_interface_board"
HOTSPOT_048
%"RSMD0603"
1,"(675,-1225)","1","cnpassive","I161"
CDS_LOCATION"R4"
CDS_SEC"1"
$SEC"1"
VALUE"4.7K"
TOL"1%"
$LOCATION"R4"
PACK_TYPE"1/10W"
CDS_LIB"cnpassive"
TC2"RTMPQ"
TC1"RTMPL"
MAX_TEMP"RTMAX"
SLOPE"RSMAX"
VOLTAGE"RVMAX"
POWER"RMAX"
DIST"FLAT"
NEGTOL"RTOL%"
POSTOL"RTOL%"
TOL_ON_OFF"ON"
SIZE"1B"
B <SIZE-1..0>\NAC
$PN"2"93
A <SIZE-1..0>\NAC
$PN"1"27
%"gnd"
1,"(625,-1400)","0","mtca_interface_board","I162"
HDL_POWER"GND"
CDS_LIB"mtca_interface_board"
HOTSPOT_027
%"gnd"
1,"(-375,-1375)","0","mtca_interface_board","I163"
CDS_LIB"mtca_interface_board"
HDL_POWER"GND"
HOTSPOT_028
%"RSMD0603"
1,"(-325,-1200)","1","cnpassive","I164"
CDS_LOCATION"R3"
CDS_SEC"1"
$SEC"1"
VALUE"4.7K"
TOL"1%"
$LOCATION"R3"
SIZE"1B"
TOL_ON_OFF"ON"
POSTOL"RTOL%"
NEGTOL"RTOL%"
DIST"FLAT"
POWER"RMAX"
VOLTAGE"RVMAX"
SLOPE"RSMAX"
MAX_TEMP"RTMAX"
TC1"RTMPL"
TC2"RTMPQ"
CDS_LIB"cnpassive"
PACK_TYPE"1/10W"
B <SIZE-1..0>\NAC
$PN"2"90
A <SIZE-1..0>\NAC
$PN"1"28
%"gnd"
1,"(4550,-1975)","0","mtca_interface_board","I165"
CDS_LIB"mtca_interface_board"
HDL_POWER"GND"
HOTSPOT_029
%"CAPCERSMDCL2"
1,"(4600,-1800)","1","cnpassive","I166"
CDS_LOCATION"C3"
CDS_SEC"1"
$SEC"1"
$LOCATION"C3"
VALUE"100NF"
VOLTAGE"16V"
SIZE"1"
CDS_LIB"cnpassive"
PACK_TYPE"0603"
A <SIZE-1..0>\NAC
$PN"1"29
B <SIZE-1..0>\NAC
$PN"2"46
%"CON14P"
3,"(2300,-650)","0","cnconnector","I167"
CDS_LOCATION"J1"
CDS_SEC"1"
$SEC"1"
$LOCATION"J1"
TYPE"MOLEX_87833"
CDS_LIB"cnconnector"
A<10>\NAC
$PN"11"47
A<11>\NAC
$PN"12"0
A<12>\NAC
$PN"13"0
A<13>\NAC
$PN"14"0
A<1>\NAC
$PN"2"40
A<3>\NAC
$PN"4"12
A<5>\NAC
$PN"6"9
A<6>\NAC
$PN"7"47
A<7>\NAC
$PN"8"10
A<8>\NAC
$PN"9"47
A<9>\NAC
$PN"10"11
A<0>\NAC
$PN"1"47
A<2>\NAC
$PN"3"47
A<4>\NAC
$PN"5"47
%"CAPCERSMDCL2"
1,"(2775,-400)","0","cnpassive","I168"
CDS_LOCATION"C2"
CDS_SEC"1"
$SEC"1"
VALUE"100NF"
$LOCATION"C2"
VOLTAGE"16V"
PACK_TYPE"0603"
CDS_LIB"cnpassive"
SIZE"1"
A <SIZE-1..0>\NAC
$PN"1"40
B <SIZE-1..0>\NAC
$PN"2"36
%"RSMD0603"
1,"(-925,-4650)","0","cnpassive","I169"
CDS_LOCATION"R5"
CDS_SEC"1"
$SEC"1"
$LOCATION"R5"
TOL"5%"
VALUE"XX"
SIZE"1B"
TOL_ON_OFF"ON"
POSTOL"RTOL%"
NEGTOL"RTOL%"
DIST"FLAT"
POWER"RMAX"
VOLTAGE"RVMAX"
SLOPE"RSMAX"
MAX_TEMP"RTMAX"
TC1"RTMPL"
TC2"RTMPQ"
CDS_LIB"cnpassive"
PACK_TYPE"1/16W"
B <SIZE-1..0>\NAC
$PN"2"87
A <SIZE-1..0>\NAC
$PN"1"82
%"RSMD0603"
1,"(725,-4600)","0","cnpassive","I170"
CDS_LOCATION"R6"
CDS_SEC"1"
$SEC"1"
VALUE"XX"
$LOCATION"R6"
TOL"5%"
SIZE"1B"
TOL_ON_OFF"ON"
POSTOL"RTOL%"
NEGTOL"RTOL%"
DIST"FLAT"
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
GND
$PN"2"22
I/O2<0>
$PN"3"71
I/O2<1>
$PN"4"15
VBUS
$PN"5"17
%"gnd"
1,"(2950,-550)","0","mtca_interface_board","I81"
HDL_POWER"GND"
CDS_LIB"mtca_interface_board"
HOTSPOT_036
%"gnd"
1,"(2000,-1050)","0","mtca_interface_board","I94"
HDL_POWER"GND"
CDS_LIB"mtca_interface_board"
HOTSPOT_047
END.
