uob-hep-cad/uob-hep-pc072/hardware/Cadence/top/mtca_interface_board_reocc/05#20trenz#20te0712#20fpga#20module/sch_1/page2.csv

FILE_TYPE = CONNECTIVITY
{Allegro Design Entry HDL 24.1 P001 (4234998) 9/4/2024}
PAGE_NUMBER = 2
0"NC"
1"FPGA_PG"
2"DIRECT_US_DATA_2_P"
3"DIRECT_US_DATA_2_N"
4"DATA_SELECT_P2V5"
5"AUXIO_P1"
6"DATA_FROM_UPSTREAM_P<2>"
7"UPSTREAM_DATA_N<2>"
8"DATA_FROM_UPSTREAM_N<2>"
9"CLKGEN_CLK_P<0>"
10"CLKGEN_CLK_N<0>"
11"BP.DATA_IN_N<1>"
12"VCC3V3\G"
13"CLK_I2C_SCL"
14"GND"
15"UPSTREAM_DATA_P<1>"
16"UART_RX_TO_FPGA_3V3"
17"AUX_GBE_TX_P"
18"BP.FPGA_GBE_TXP"
19"AUX_GBE_TX_N"
20"AUX_GBE_RX_N"
21"AUX_GBE_RX_P"
22"VCC3V3\g"
23"GND\g"
24"GND"
25"LED_3B"
26"VREF_JTAG\g"
27"VCC3V3\g"
28"VCC3V3\g"
29"P2V5\g"
30"P2V5\g"
31"VCC3V3\g"
32"VCC3V3\g"
33"GND\g"
34"GND"
35"GND"
36"BP.FPGA_GBE_RXP"
37"GND"
38"BP.DATA_OUT_N<9>"
39"SFP_DATA_OUT_N<1>"
40"GND"
41"UART_TX_FROM_FPGA_3V3"
42"LED_3R"
43"SFP.TX_FAULT<1>"
44"CLK_I2C_SDA"
45"SFP_DATA_OUT_N<2>"
46"SFP_DATA_OUT_P<2>"
47"SFP_DATA_OUT_P<1>"
48"UN$2$SF-0603FP015F-2$I429$1"
49"GND"
50"BP.DATA_OUT_N<11>"
51"BP.DATA_IN_N<5>"
52"BP.DATA_IN_P<5>"
53"BP.DATA_IN_P<2>"
54"BP.DATA_OUT_N<0>"
55"BP.DATA_OUT_P<0>"
56"BP.DATA_OUT_N<1>"
57"BP.DATA_OUT_P<1>"
58"BP.DATA_OUT_N<2>"
59"BP.DATA_OUT_P<2>"
60"GND"
61"DATA_FROM_UPSTREAM_P<1>"
62"FPGA_TCK"
63"GND"
64"FPGA_TMS"
65"BP.DATA_OUT_P<4>"
66"BP.DATA_OUT_N<4>"
67"BP.DATA_OUT_N<7>"
68"BP.DATA_OUT_P<7>"
69"BP.DATA_OUT_N<3>"
70"SFP.SCL<2>"
71"SFP.SDA<2>"
72"SFP.SCL<1>"
73"SFP.SDA<1>"
74"AUXIO_N6"
75"GND"
76"AUXIO_N2"
77"AUXIO_P2"
78"LED_2B"
79"UPSTREAM_DATA_P<2>"
80"N00771"
81"BP.DATA_IN_P<4>"
82"P1V8_OUT"
83"BP.DATA_IN_P<3>"
84"BP.DATA_IN_N<3>"
85"BP.DATA_IN_N<2>"
86"BP.DATA_OUT_P<5>"
87"BP.DATA_IN_P<0>"
88"BP.DATA_IN_N<0>"
89"BP.DATA_OUT_N<5>"
90"DATA_FROM_UPSTREAM_N<1>"
91"UN$2$CAPCERSMDCL2$I418$B"
92"GND"
93"BP.DATA_IN_P<9>"
94"BP.DATA_IN_N<9>"
95"BP.DATA_IN_P<8>"
96"BP.DATA_IN_N<7>"
97"BP.DATA_IN_P<7>"
98"SFP.LOS<2>"
99"SFP.SDA<0>"
100"GND"
101"GND"
102"BP.DATA_IN_P<1>"
103"GND"
104"UPSTREAM_DATA_P<0>"
105"UPSTREAM_DATA_N<0>"
106"P3V3_OUT0"
107"LED_1R"
108"LED_1B"
109"BP.DATA_IN_N<11>"
110"BP.DATA_IN_P<11>"
111"UPSTREAM_DATA_N<1>"
112"GND"
113"GND"
114"GND"
115"GND"
116"GND"
117"GND"
118"FPGA_TDI"
119"GND"
120"P1V5_OUT"
121"SFP.TX_DISABLE<2>"
122"P3V3_OUT1"
123"CLK_SEL1"
124"GND"
125"GND"
126"GND"
127"GND"
128"GND"
129"CLK_SEL0"
130"CLKGEN_INTR"
131"CLKGEN_LOL"
132"SFP.TX_FAULT<2>"
133"GND"
134"GND"
135"FPGA_TDO"
136"N00775"
137"GND"
138"GND"
139"GND"
140"GND"
141"BP.FPGA_GBE_RXN"
142"GND"
143"GND"
144"GND"
145"GND"
146"BP.DATA_OUT_N<6>"
147"BP.DATA_OUT_P<6>"
148"CLKGEN_CLK_N<1>"
149"CLKGEN_CLK_P<1>"
150"BP.DATA_OUT_P<11>"
151"GND"
152"GND"
153"GND"
154"SFP.TX_DISABLE<1>"
155"SFP.LOS<1>"
156"SFP.LOS<0>"
157"SFP.TX_FAULT<0>"
158"SFP.TX_DISABLE<0>"
159"BP.DATA_OUT_P<3>"
160"SFP.SCL<0>"
161"SFP_DATA_OUT_P<0>"
162"SFP_DATA_OUT_N<0>"
163"DATA_FROM_UPSTREAM_N<0>"
164"DATA_FROM_UPSTREAM_P<0>"
165"BP.FPGA_GBE_TXN"
166"AUXIO_1B"
167"AUXIO_0B"
168"GND"
169"GND"
170"GND"
171"GND"
172"GND"
173"GND"
174"GND"
175"BP.DATA_IN_N<10>"
176"BP.DATA_IN_P<10>"
177"BP.DATA_IN_N<6>"
178"LED_2R"
179"GND"
180"BP.DATA_IN_N<8>"
181"GND"
182"GND"
183"BP.DATA_IN_P<6>"
184"BP.DATA_IN_N<4>"
185"AUXIO_P6"
186"BP.DATA_OUT_N<10>"
187"BP.DATA_OUT_P<10>"
188"BP.DATA_OUT_P<9>"
189"BP.DATA_OUT_N<8>"
190"BP.DATA_OUT_P<8>"
%"gnd"
1,"(6125,-6850)","0","mtca_interface_board","137P"
CDS_LIB"mtca_interface_board"
HDL_POWER"GND"
HOTSPOT_024
%"portright-l"
1,"(3600,-4800)","2","mtca_interface_board","2P"
NAME"FPGA_PG"
CDS_LIB"mtca_interface_board"
HOTSPOT_0
HDL_PORT"OUT"
PIN_NAME"FPGA_PG"1
%"te0712 connector-jb2"
1,"(8075,-5300)","0","ocad_parts_lib","307P"
VALUE"LSHM-150-03.0-L-DV-A-S-K-TR"
$LOCATION"J8"
CDS_LIB"ocad_parts_lib"
CDS_LOCATION"J8"
JEDEC_TYPE"samtec_lshm-150-04-0-l-dv-a-s"
SOURCE_PACKAGE"TE0712 Connector-JB2"
PART_NUMBER"LSHM-150-03.0-L-DV-A-S-K-TR"
PART_TYPE"Header"
DESCRIPTION"CONN SELF-MATE 100POS SMD GOLD"
CONTACTCURRENT"-"
SEC"1"
GND1
$PN"29"114
GND2
$PN"39"143
VIN4
$PN"1"32
VCCIO13_0
$PN"2"30
VIN5
$PN"3"32
VCCIO13_1
$PN"4"30
VIN6
$PN"5"32
NC0
$PN"6"0
VIN7
$PN"7"32
VCCIO15_0
$PN"8"30
VCC3V3_1
$PN"9"122
VCCIO15_1
$PN"10"30
VCC3V3_2
$PN"11"122
B14_L_8__N
$PN"12"158
B14_L_10__N
$PN"13"129
B14_L_8__P
$PN"14"157
B14_L_10_P
$PN"15"123
B14_L_17__N
$PN"16"156
RESIN
$PN"17"136
B14_L_17__P
$PN"18"154
GND0
$PN"19"115
VCC1V5
$PN"20"120
B14_L_12__P
$PN"21"130
B14_L_14__P
$PN"22"155
B14_L_12__N
$PN"23"131
B14_L_14__N
$PN"24"121
B14_L_11__P
$PN"25"132
B14_L_13__P
$PN"26"99
B14_L_11__N
$PN"27"98
B14_L_13__N
$PN"28"160
NC1
$PN"30"0
B15_L_9__N
$PN"31"54
B14_L_16__P
$PN"32"73
B15_L_9__P
$PN"33"55
B14_L_16__N
$PN"34"72
B15_L_8__N
$PN"35"56
B14_L_15__P
$PN"36"71
B15_L_8__P
$PN"37"57
B14_L_15__N
$PN"38"70
GND3
$PN"40"119
B15_L_7__N
$PN"41"58
B15_L_23__P
$PN"42"0
B15_L_7__P
$PN"43"59
B15_L_23__N
$PN"44"0
B15_L_13__P
$PN"45"0
B15_L_19__P
$PN"46"159
B15_L_13__N
$PN"47"0
B15_L_19__N
$PN"48"69
GND4
$PN"49"60
GND5
$PN"50"116
B15_L_14__P
$PN"51"61
B15_L_11__P
$PN"52"65
B15_L_14__N
$PN"53"90
B15_L_11__N
$PN"54"66
B15_L_12__P
$PN"55"149
B15_L_3__P
$PN"56"0
B15_L_12__N
$PN"57"148
B15_L_3__N
$PN"58"0
GND6
$PN"59"144
GND7
$PN"60"117
B15_L_10__N
$PN"61"146
B15_L_17__N
$PN"62"67
B15_L_10__P
$PN"63"147
B15_L_17__P
$PN"64"68
B15_L_18__P
$PN"65"0
B15_L_16__P
$PN"66"0
B15_L_18__N
$PN"67"0
B15_L_16__N
$PN"68"0
GND8
$PN"69"145
GND9
$PN"70"134
B15_L_20__P
$PN"71"190
B15_L_1__P
$PN"72"110
B15_L_20__N
$PN"73"189
B15_L_1__N
$PN"74"109
B15_L_15__P
$PN"75"188
B15_L_2__N
$PN"76"111
B15_L_15__N
$PN"77"38
B15_L_2__P
$PN"78"15
GND10
$PN"79"133
GND11
$PN"80"14
B15_L_6__N
$PN"81"0
B15_L_4__P
$PN"82"108
B15_L_6__P
$PN"83"0
B15_L_4__N
$PN"84"107
B15_L_21__P
$PN"85"187
B15_L_5__N
$PN"86"0
B15_L_21__N
$PN"87"186
B15_L_5__P
$PN"88"0
GND12
$PN"89"49
B15_IO0
$PN"90"0
B15_L_24__N
$PN"91"0
VCC3V3_3
$PN"92"48
B15_L_24__P
$PN"93"0
TMS
$PN"94"64
B15_L_22__P
$PN"95"150
TDI
$PN"96"118
B15_L_22__N
$PN"97"50
TDO
$PN"98"135
B15_IO25
$PN"99"0
TCK
$PN"100"62
F2
$PN"101"124
F1
$PN"102"63
%"cap_np_0"
1,"(6150,-5975)","7","ocad_parts_lib","313P"
$LOCATION"C39"
VALUE"0.1UF"
VOLTAGE"25V"
SEC"1"
ALT_SYMBOLS""
LAST_EDIT_BY"SNF"
CLASS"DISCRETE"
ROOM"TE0712"
AVAILABILITY"In Stock"
PART_NUMBER"445-7348-2-ND"
SOURCE_PACKAGE"CAP_NP_0"
JEDEC_TYPE"cap0402"
CDS_LOCATION"C39"
CDS_LIB"ocad_parts_lib"
1
$PN"1"46
2
$PN"2"6
%"r"
1,"(3700,-4550)","0","discrete","322P"
$LOCATION"R13"
VALUE"4.99k"
CDS_LIB"discrete"
CDS_LOCATION"R13"
JEDEC_TYPE"res0402"
SOURCE_PACKAGE"R"
REUSE_ID"48"
ROOM"TE0712"
AVAILABILITY"In Stock"
DISTRIBUTOR"Digikey"
DISTRIBUTOR_PARTNUMBER"P4.99KLTR-ND"
MANUFACTURER"Panasonic"
MPN"ERJ-2RKF4991X"
TOLERANCE"1%"
POWER"1/10 W"
DESCRIPTION"RES SMD 4.99K OHM 1% 1/10W 0402"
PART_TYPE"Thick Film"
PART_NUMBER"ERJ-2RKF4991X"
REUSE_ANNOTATE"TRUE"
SEC"1"
1
$PN"1"12
2
$PN"2"1
%"cap_np_0"
1,"(6150,-8700)","3","ocad_parts_lib","327P"
$LOCATION"C45"
VOLTAGE"25V"
VALUE"0.1UF"
CDS_LIB"ocad_parts_lib"
CDS_LOCATION"C45"
JEDEC_TYPE"cap0402"
DISTRIBUTOR"Digi-Key"
DISTRIBUTOR_PARTNUMBER"445-7348-2-ND"
MANUFACTURER"TDK CORP"
MPN"C1005X7R1E104K050BB "
PSPICE"C"
DESCRIPTION"CAP 0.1__F __10% 25V Ceramic Capacitor X7R 0402 "
PART_TYPE"Ceramic"
PART_NUMBER"445-7348-2-ND"
REUSE_ANNOTATE"TRUE"
CLASS"DISCRETE"
LAST_EDIT_BY"SNF"
ALT_SYMBOLS""
SEC"1"
AVAILABILITY"In Stock"
ROOM"TE0712"
SOURCE_PACKAGE"CAP_NP_0"
1
$PN"1"164
2
$PN"2"161
%"cap_np_0"
1,"(6150,-6050)","5","ocad_parts_lib","329P"
$LOCATION"C40"
VALUE"0.1UF"
VOLTAGE"25V"
SEC"1"
ALT_SYMBOLS""
LAST_EDIT_BY"SNF"
CLASS"DISCRETE"
ROOM"TE0712"
PART_NUMBER"445-7348-2-ND"
REUSE_ANNOTATE"TRUE"
SOURCE_PACKAGE"CAP_NP_0"
JEDEC_TYPE"cap0402"
CDS_LOCATION"C40"
CDS_LIB"ocad_parts_lib"
1
$PN"1"45
2
$PN"2"8
%"te0712 connector-jb3"
1,"(4925,-8000)","0","ocad_parts_lib","333P"
$LOCATION"J5"
VALUE"LSHM-130-03.0-L-DV-A-S-K-TR"
SEC"1"
DISTRIBUTOR"Digikey"
DISTRIBUTOR_PARTNUMBER"SAM14110TR-ND"
MANUFACTURER"Samtec"
MPN"LSHM-130-03.0-L-DV-A-S-K-TR"
HOUSINGGENDER"Female"
CONTACTGENDER"Male"
CONTACTVOLTAGE"-"
CONTACTCURRENT"-"
DESCRIPTION"CONN SELF-MATE 60POS SMD GOLD"
PART_TYPE"Header"
PART_NUMBER"LSHM-130-03.0-L-DV-A-S-K-TR"
SOURCE_PACKAGE"TE0712 Connector-JB3"
JEDEC_TYPE"samtec_lshm-130-04-0-l-dv-a-s"
CDS_LOCATION"J5"
CDS_LIB"ocad_parts_lib"
GND1
$PN"5"127
GND2
$PN"12"112
GND0
$PN"6"153
NC1
$PN"56"0
GND3
$PN"11"35
GND4
$PN"18"137
GND5
$PN"17"140
GND6
$PN"24"152
GND7
$PN"23"37
GND8
$PN"30"151
GND9
$PN"29"139
GND10
$PN"36"128
GND11
$PN"35"142
GND12
$PN"46"126
F2
$PN"62"125
F1
$PN"61"113
13_L_14_P
$PN"1"0
B13_L_17__P
$PN"2"0
13_L_14_N
$PN"3"0
B13_L_17__N
$PN"4"0
MGT_RX0_N
$PN"7"20
MGT_TX0_N
$PN"8"19
MGT_RX0_P
$PN"9"21
MGT_TX0_P
$PN"10"17
MGT_RX1_N
$PN"13"141
MGT_TX1_N
$PN"14"165
MGT_RX1_P
$PN"15"36
MGT_TX1_P
$PN"16"18
MGT_RX2_N
$PN"19"0
MGT_TX2_N
$PN"20"0
MGT_RX2_P
$PN"21"0
MGT_TX2_P
$PN"22"0
MGT_RX3_N
$PN"25"0
MGT_TX3_N
$PN"26"0
MGT_RX3_P
$PN"27"0
MGT_TX3_P
$PN"28"0
CLKIN2_N
$PN"31"0
MGT_CLK1_N
$PN"32"0
CLKIN2_P
$PN"33"0
MGT_CLK1_P
$PN"34"0
B13_L_16_P
$PN"37"0
B13_L_10__P
$PN"38"0
B13_L_16_N
$PN"39"0
B13_L_10_N
$PN"40"0
B13_L_1_P
$PN"41"0
B13_L_15__P
$PN"42"0
B13_L_1_N
$PN"43"0
B13_L_15_N
$PN"44"0
GND13
$PN"45"138
B13_L_4_P
$PN"47"0
B14_L_5__P
$PN"48"167
B13_L_4_N
$PN"49"0
B14_L_5__N
$PN"50"0
B13_L_2_N
$PN"51"0
B14_L_20__P
$PN"52"166
B13_L_2_P
$PN"53"0
B14_L_20_N
$PN"54"0
NC2
$PN"55"0
B13_L_12_P
$PN"57"77
B13_L_13__P
$PN"58"164
B13_L_12_N
$PN"59"76
B13_L_13__N
$PN"60"163
%"cap_np_0"
1,"(6150,-8750)","1","ocad_parts_lib","339P"
$LOCATION"C43"
VOLTAGE"25V"
VALUE"0.1UF"
CDS_LIB"ocad_parts_lib"
CDS_LOCATION"C43"
JEDEC_TYPE"cap0402"
SOURCE_PACKAGE"CAP_NP_0"
DESCRIPTION"CAP 0.1__F __10% 25V Ceramic Capacitor X7R 0402 "
PSPICE"C"
MPN"C1005X7R1E104K050BB "
MANUFACTURER"TDK CORP"
DISTRIBUTOR_PARTNUMBER"445-7348-2-ND"
DISTRIBUTOR"Digi-Key"
AVAILABILITY"In Stock"
ROOM"TE0712"
CLASS"DISCRETE"
LAST_EDIT_BY"SNF"
ALT_SYMBOLS""
SEC"1"
PART_TYPE"Ceramic"
PART_NUMBER"445-7348-2-ND"
REUSE_ANNOTATE"TRUE"
1
$PN"1"163
2
$PN"2"162
%"r"
1,"(6175,-6575)","0","discrete","340P"
$LOCATION"R136"
VALUE"10K"
MANUFACTURER"Vishay Dale"
CDS_LIB"discrete"
CDS_LOCATION"R136"
JEDEC_TYPE"res0402"
SOURCE_PACKAGE"R"
DATASHEET"C:\EMA\CISQuickStart\Technical_Datasheets\Vishay\dcrcwe3.pdf"
DISTRIBUTOR"Digikey"
DISTRIBUTOR_PARTNUMBER"1135-1061-1-ND"
SEC"1"
PART_NUMBER"M55342K11B10E0RS3"
1
$PN"1"80
2
$PN"2"24
%"r"
1,"(6900,-4275)","0","discrete","342P"
$LOCATION"R106"
VALUE"10K"
CDS_LIB"discrete"
CDS_LOCATION"R106"
JEDEC_TYPE"res0402"
SOURCE_PACKAGE"R"
DATASHEET"C:\EMA\CISQuickStart\Technical_Datasheets\Vishay\dcrcwe3.pdf"
DISTRIBUTOR"Digikey"
DISTRIBUTOR_PARTNUMBER"1135-1061-1-ND"
MANUFACTURER"Vishay Dale"
MPN"M55342K11B10E0RS3"
TOLERANCE"1%"
POWER"1/10W"
SEC"1"
PART_NUMBER"M55342K11B10E0RS3"
1
$PN"1"32
2
$PN"2"136
%"te0712 connector-jb1"
1,"(4925,-5350)","0","ocad_parts_lib","350P"
$LOCATION"J1"
VALUE"LSHM-150-03.0-L-DV-A-S-K-TR"
SEC"1"
DISTRIBUTOR"Digikey"
DISTRIBUTOR_PARTNUMBER"SAM14151TR-ND"
MANUFACTURER"Samtec"
MPN"LSHM-150-03.0-L-DV-A-S-K-TR"
HOUSINGGENDER"Female"
CONTACTGENDER"Male"
CONTACTVOLTAGE"-"
CONTACTCURRENT"-"
DESCRIPTION"CONN SELF-MATE 100POS SMD GOLD"
PART_TYPE"Header"
PART_NUMBER"LSHM-150-03.0-L-DV-A-S-K-TR"
SOURCE_PACKAGE"TE0712 Connector-JB1"
JEDEC_TYPE"samtec_lshm-150-04-0-l-dv-a-s"
CDS_LOCATION"J1"
CDS_LIB"ocad_parts_lib"
GND1
$PN"7"168
GND2
$PN"19"103
GND0
$PN"1"92
GND3
$PN"25"169
GND4
$PN"30"170
GND5
$PN"33"179
GND6
$PN"43"181
GND7
$PN"53"182
GND8
$PN"54"101
GND9
$PN"63"171
GND10
$PN"64"100
GND11
$PN"73"172
GND12
$PN"74"173
F2
$PN"101"174
F1
$PN"102"75
GND13
$PN"83"34
VIN1
$PN"2"91
ETH_TD_P
$PN"3"0
VIN2
$PN"4"91
ETH_TD_N
$PN"5"0
VIN3
$PN"6"91
NOSSEQ
$PN"8"0
ETH_RD_P
$PN"9"0
VCCIO16_0
$PN"10"29
ETH_RD_N
$PN"11"0
VCCIO16_1
$PN"12"29
VCC3V3_0
$PN"13"106
3V3VIN0
$PN"14"31
B13_L_6_N
$PN"15"105
3V3VIN1
$PN"16"31
B13_L_6__P
$PN"17"104
B13_L_3__P
$PN"18"87
B13_L_3_N
$PN"20"88
B13_L_5_N
$PN"21"175
B13_L_11_N
$PN"22"89
B13_L_5__P
$PN"23"176
B13_L_11__P
$PN"24"86
B13_L_9_N
$PN"26"11
EN1
$PN"27"0
B13_L_9__P
$PN"28"102
PGOOD
$PN"29"1
MODE
$PN"31"0
B16_L_22__P
$PN"32"53
B16_L_22_N
$PN"34"85
B16_L_16_P
$PN"35"93
B16_L_24_N
$PN"36"84
B16_L_16_N
$PN"37"94
B16_L_24__P
$PN"38"83
B16_L_19_N
$PN"39"180
VCC1V8
$PN"40"82
B16_L_19_P
$PN"41"95
B16_L_23__P
$PN"42"81
B16_L_23_N
$PN"44"184
B16_L_17_N
$PN"45"0
B16_L_15__P
$PN"46"0
B16_L_17_P
$PN"47"0
B16_L_15_N
$PN"48"0
B16_L_18_N
$PN"49"96
B16_L20_P
$PN"50"52
B16_L_18_P
$PN"51"97
B16_L20_N
$PN"52"51
B16_L_9_N
$PN"55"177
B16_L_21__P
$PN"56"0
B16_L_9__P
$PN"57"183
B16_L_21_N
$PN"58"0
B16_L_7_N
$PN"59"0
B16_L_13__P
$PN"60"10
B16_L_7__P
$PN"61"0
B16_L_13_N
$PN"62"9
B16_L_11__P
$PN"65"0
B16_L_14__P
$PN"66"2
B16_L_11_N
$PN"67"0
B16_L_14_N
$PN"68"3
B16_L_10_N
$PN"69"0
B16_L_3_N
$PN"70"4
B16_L_10__P
$PN"71"0
B16_L_3__P
$PN"72"5
B16_L_5_N
$PN"75"0
B16_L_12__P
$PN"76"6
B16_L_5__P
$PN"77"0
B16_L_12_N
$PN"78"8
B16_L_2_N
$PN"79"0
VBAT_IN
$PN"80"0
B16_L_2__P
$PN"81"0
B16_L_8_N
$PN"82"7
B16_L_8__P
$PN"84"79
B16_L_6_N
$PN"85"178
B14_L_18__N
$PN"86"44
B16_L_6__P
$PN"87"78
B14_L_18__P
$PN"88"13
GND14
$PN"89"40
JTAGEN
$PN"90"80
B14_L_24__P
$PN"91"0
B14_L_9__P
$PN"92"16
B16_L_4_N
$PN"93"42
B14_L_9_N
$PN"94"41
B16_L_4__P
$PN"95"25
B14_L_4__P
$PN"96"185
B16_L_1_N
$PN"97"0
B14_L_4_N
$PN"98"74
B16_L_1__P
$PN"99"0
B14_L_24_N
$PN"100"43
%"vcc_bar"
1,"(9350,-6250)","0","mtca_interface_board","354P"
HDL_POWER"VREF_JTAG"
CDS_LIB"mtca_interface_board"
HOTSPOT_026
%"vcc_bar"
1,"(3650,-4250)","0","mtca_interface_board","7P"
HDL_POWER"VCC3V3"
CDS_LIB"mtca_interface_board"
HOTSPOT_012
%"vcc_bar"
1,"(9750,-4150)","0","mtca_interface_board","I395"
HDL_POWER"VCC3V3"
CDS_LIB"mtca_interface_board"
HOTSPOT_027
%"r"
1,"(9700,-4400)","0","discrete","I396"
VALUE"2.2k"
$LOCATION"R122"
CDS_LIB"discrete"
CDS_LOCATION"R122"
JEDEC_TYPE"res0402"
SOURCE_PACKAGE"R"
REUSE_ANNOTATE"TRUE"
ROOM"SFP I2C SWITCH"
AVAILABILITY"6,080,000"
DISTRIBUTOR"Digikey"
DISTRIBUTOR_PARTNUMBER"P2.20KLTR-ND"
MANUFACTURER"Panasonic"
MPN"ERJ-2RKF2201X"
TOLERANCE"1%"
POWER"1/10 W"
DESCRIPTION"RES SMD 2.2K OHM 1% 1/10W 0402"
PART_TYPE"Thick Film"
PART_NUMBER"ERJ-2RKF2201X"
SEC"1"
1
$PN"1"27
2
$PN"2"71
%"r"
1,"(6775,-5950)","0","discrete","I397"
VALUE"2.2k"
$LOCATION"R120"
SEC"1"
REUSE_ANNOTATE"TRUE"
ROOM"SFP I2C SWITCH"
AVAILABILITY"6,080,000"
DISTRIBUTOR"Digikey"
DISTRIBUTOR_PARTNUMBER"P2.20KLTR-ND"
MANUFACTURER"Panasonic"
MPN"ERJ-2RKF2201X"
TOLERANCE"1%"
POWER"1/10 W"
DESCRIPTION"RES SMD 2.2K OHM 1% 1/10W 0402"
PART_TYPE"Thick Film"
PART_NUMBER"ERJ-2RKF2201X"
SOURCE_PACKAGE"R"
JEDEC_TYPE"res0402"
CDS_LOCATION"R120"
CDS_LIB"discrete"
1
$PN"1"28
2
$PN"2"44
%"r"
1,"(9800,-4400)","0","discrete","I398"
$LOCATION"R121"
VALUE"2.2k"
CDS_LIB"discrete"
CDS_LOCATION"R121"
JEDEC_TYPE"res0402"
SOURCE_PACKAGE"R"
REUSE_ANNOTATE"TRUE"
PART_NUMBER"ERJ-2RKF2201X"
PART_TYPE"Thick Film"
DESCRIPTION"RES SMD 2.2K OHM 1% 1/10W 0402"
POWER"1/10 W"
TOLERANCE"1%"
MPN"ERJ-2RKF2201X"
MANUFACTURER"Panasonic"
DISTRIBUTOR_PARTNUMBER"P2.20KLTR-ND"
DISTRIBUTOR"Digikey"
AVAILABILITY"6,080,000"
ROOM"SFP I2C SWITCH"
SEC"1"
1
$PN"1"27
2
$PN"2"70
%"r"
1,"(6850,-5950)","0","discrete","I399"
$LOCATION"R119"
VALUE"2.2k"
SEC"1"
REUSE_ANNOTATE"TRUE"
PART_NUMBER"ERJ-2RKF2201X"
PART_TYPE"Thick Film"
DESCRIPTION"RES SMD 2.2K OHM 1% 1/10W 0402"
POWER"1/10 W"
TOLERANCE"1%"
MPN"ERJ-2RKF2201X"
MANUFACTURER"Panasonic"
DISTRIBUTOR_PARTNUMBER"P2.20KLTR-ND"
DISTRIBUTOR"Digikey"
AVAILABILITY"6,080,000"
ROOM"SFP I2C SWITCH"
SOURCE_PACKAGE"R"
JEDEC_TYPE"res0402"
CDS_LOCATION"R119"
CDS_LIB"discrete"
1
$PN"1"28
2
$PN"2"13
%"r"
1,"(9600,-4400)","0","discrete","I400"
$LOCATION"R127"
VALUE"2.2k"
CDS_LIB"discrete"
CDS_LOCATION"R127"
JEDEC_TYPE"res0402"
SOURCE_PACKAGE"R"
REUSE_ANNOTATE"TRUE"
PART_NUMBER"ERJ-2RKF2201X"
PART_TYPE"Thick Film"
DESCRIPTION"RES SMD 2.2K OHM 1% 1/10W 0402"
POWER"1/10 W"
TOLERANCE"1%"
MPN"ERJ-2RKF2201X"
MANUFACTURER"Panasonic"
DISTRIBUTOR_PARTNUMBER"P2.20KLTR-ND"
DISTRIBUTOR"Digikey"
AVAILABILITY"6,080,000"
ROOM"SFP I2C SWITCH"
SEC"1"
1
$PN"1"27
2
$PN"2"72
%"r"
1,"(9400,-4400)","0","discrete","I401"
$LOCATION"R125"
VALUE"2.2k"
CDS_LIB"discrete"
CDS_LOCATION"R125"
JEDEC_TYPE"res0402"
SOURCE_PACKAGE"R"
REUSE_ANNOTATE"TRUE"
PART_NUMBER"ERJ-2RKF2201X"
PART_TYPE"Thick Film"
DESCRIPTION"RES SMD 2.2K OHM 1% 1/10W 0402"
POWER"1/10 W"
TOLERANCE"1%"
MPN"ERJ-2RKF2201X"
MANUFACTURER"Panasonic"
DISTRIBUTOR_PARTNUMBER"P2.20KLTR-ND"
DISTRIBUTOR"Digikey"
AVAILABILITY"6,080,000"
ROOM"SFP I2C SWITCH"
SEC"1"
1
$PN"1"27
2
$PN"2"160
%"r"
1,"(9500,-4400)","0","discrete","I402"
$LOCATION"R126"
VALUE"2.2k"
CDS_LIB"discrete"
CDS_LOCATION"R126"
JEDEC_TYPE"res0402"
SOURCE_PACKAGE"R"
REUSE_ANNOTATE"TRUE"
ROOM"SFP I2C SWITCH"
AVAILABILITY"6,080,000"
DISTRIBUTOR"Digikey"
DISTRIBUTOR_PARTNUMBER"P2.20KLTR-ND"
MANUFACTURER"Panasonic"
MPN"ERJ-2RKF2201X"
TOLERANCE"1%"
POWER"1/10 W"
DESCRIPTION"RES SMD 2.2K OHM 1% 1/10W 0402"
PART_TYPE"Thick Film"
PART_NUMBER"ERJ-2RKF2201X"
SEC"1"
1
$PN"1"27
2
$PN"2"73
%"r"
1,"(9300,-4400)","0","discrete","I403"
VALUE"2.2k"
$LOCATION"R124"
CDS_LIB"discrete"
CDS_LOCATION"R124"
JEDEC_TYPE"res0402"
SOURCE_PACKAGE"R"
REUSE_ANNOTATE"TRUE"
ROOM"SFP I2C SWITCH"
AVAILABILITY"6,080,000"
DISTRIBUTOR"Digikey"
DISTRIBUTOR_PARTNUMBER"P2.20KLTR-ND"
MANUFACTURER"Panasonic"
MPN"ERJ-2RKF2201X"
TOLERANCE"1%"
POWER"1/10 W"
DESCRIPTION"RES SMD 2.2K OHM 1% 1/10W 0402"
PART_TYPE"Thick Film"
PART_NUMBER"ERJ-2RKF2201X"
SEC"1"
1
$PN"1"27
2
$PN"2"99
%"vcc_bar"
1,"(6800,-5600)","0","mtca_interface_board","I404"
HDL_POWER"VCC3V3"
CDS_LIB"mtca_interface_board"
HOTSPOT_028
%"cap_np_0"
1,"(6675,-5400)","3","ocad_parts_lib","I405"
CDS_LOCATION"C45"
$LOCATION"C45"
VALUE"0.1UF"
VOLTAGE"25V"
PART_TYPE"Ceramic"
PART_NUMBER"445-7348-2-ND"
REUSE_ANNOTATE"TRUE"
CLASS"DISCRETE"
DISTRIBUTOR_PARTNUMBER"445-7348-2-ND"
MANUFACTURER"TDK CORP"
DESCRIPTION"CAP 0.1__F __10% 25V Ceramic Capacitor X7R 0402 "
PSPICE"C"
MPN"C1005X7R1E104K050BB "
DISTRIBUTOR"Digi-Key"
SOURCE_PACKAGE"CAP_NP_0"
ROOM"TE0712"
AVAILABILITY"In Stock"
SEC"1"
ALT_SYMBOLS""
LAST_EDIT_BY"SNF"
JEDEC_TYPE"cap0402"
CDS_LIB"ocad_parts_lib"
1
$PN"1"39
2
$PN"2"90
%"cap_np_0"
1,"(6675,-5350)","1","ocad_parts_lib","I406"
CDS_LOCATION"C43"
$LOCATION"C43"
VOLTAGE"25V"
VALUE"0.1UF"
AVAILABILITY"In Stock"
ROOM"TE0712"
CLASS"DISCRETE"
LAST_EDIT_BY"SNF"
MPN"C1005X7R1E104K050BB "
MANUFACTURER"TDK CORP"
DISTRIBUTOR_PARTNUMBER"445-7348-2-ND"
DISTRIBUTOR"Digi-Key"
PSPICE"C"
DESCRIPTION"CAP 0.1__F __10% 25V Ceramic Capacitor X7R 0402 "
REUSE_ANNOTATE"TRUE"
PART_NUMBER"445-7348-2-ND"
PART_TYPE"Ceramic"
SEC"1"
ALT_SYMBOLS""
SOURCE_PACKAGE"CAP_NP_0"
JEDEC_TYPE"cap0402"
CDS_LIB"ocad_parts_lib"
1
$PN"1"47
2
$PN"2"61
%"P2V5"
1,"(5700,-4300)","0","cnpower","I407"
BODY_TYPE"PLUMBING"
HDL_POWER"P2V5"
SIZE"1B"
CDS_LIB"cnpower"
A<SIZE-1..0>\NAC
VHDL_INIT"1"29
%"P2V5"
1,"(9025,-4050)","0","cnpower","I408"
BODY_TYPE"PLUMBING"
HDL_POWER"P2V5"
SIZE"1B"
CDS_LIB"cnpower"
A<SIZE-1..0>\NAC
VHDL_INIT"1"30
%"vcc_bar"
1,"(6625,-3925)","0","mtca_interface_board","I409"
HDL_POWER"VCC3V3"
CDS_LIB"mtca_interface_board"
HOTSPOT_031
%"vcc_bar"
1,"(7375,-4000)","0","mtca_interface_board","I410"
HDL_POWER"VCC3V3"
CDS_LIB"mtca_interface_board"
HOTSPOT_032
%"TP"
1,"(4000,-4375)","2","cnpassive","I411"
$LOCATION"TP?"
VALUE"1.0MM"
CDS_LIB"cnpassive"
PACK_TYPE"HOLE"
PART_NAME"TP"
SIZE"1B"
A <SIZE-1..0>\NAC
$PN"#"106
%"TP"
1,"(5950,-5100)","0","cnpassive","I412"
$LOCATION"TP?"
VALUE"1.0MM"
SIZE"1B"
CDS_LIB"cnpassive"
PART_NAME"TP"
PACK_TYPE"HOLE"
A <SIZE-1..0>\NAC
$PN"#"82
%"TP"
1,"(9175,-4550)","0","cnpassive","I413"
$LOCATION"TP?"
VALUE"1.0MM"
SIZE"1B"
CDS_LIB"cnpassive"
PART_NAME"TP"
PACK_TYPE"HOLE"
A <SIZE-1..0>\NAC
$PN"#"120
%"CON4P"
1,"(6275,-8500)","2","cnconnector","I414"
$LOCATION"J?"
TYPE"53398-0471"
CDS_LIB"cnconnector"
A<3>\NAC167
A<1>\NAC166
A<2>\NAC22
A<0>\NAC33
%"gnd"
1,"(5875,-8600)","0","mtca_interface_board","I415"
HDL_POWER"GND"
CDS_LIB"mtca_interface_board"
HOTSPOT_033
%"FERRITE"
1,"(6225,-4025)","0","cndiscrete","I416"
$LOCATION"L?"
VALUE"MPZ1608S101A"
CDS_LIB"cndiscrete"
PACK_TYPE"SMD"
MODEL"TDK"
B <SIZE-1..0>\NAC31
A <SIZE-1..0>\NAC91
%"CAPCERSMDCL2"
1,"(6500,-4175)","1","cnpassive","I417"
$LOCATION"C?"
VALUE"1UF"
VOLTAGE"16V"
PACK_TYPE"0603"
CDS_LIB"cnpassive"
SIZE"1"
A <SIZE-1..0>\NAC
$PN"#"23
B <SIZE-1..0>\NAC
$PN"#"31
%"CAPCERSMDCL2"
1,"(5950,-4175)","1","cnpassive","I418"
$LOCATION"C?"
VOLTAGE"16V"
VALUE"1UF"
PACK_TYPE"0603"
CDS_LIB"cnpassive"
SIZE"1"
A <SIZE-1..0>\NAC
$PN"#"23
B <SIZE-1..0>\NAC
$PN"#"91
%"gnd"
1,"(6175,-4350)","0","mtca_interface_board","I419"
HDL_POWER"GND"
CDS_LIB"mtca_interface_board"
HOTSPOT_023
%"PCOAX"
1,"(6325,-7150)","0","cnconnector","I421"
$LOCATION"PX?"
TYPE"U.FL-R-SMT-1(10)"
CDS_LIB"cnconnector"
NEEDS_NO_SIZE"TRUE"
A\NAC21
%"PCOAX"
1,"(6325,-7300)","0","cnconnector","I422"
$LOCATION"PX?"
TYPE"U.FL-R-SMT-1(10)"
NEEDS_NO_SIZE"TRUE"
CDS_LIB"cnconnector"
A\NAC20
%"PCOAX"
1,"(6325,-7425)","0","cnconnector","I423"
$LOCATION"PX?"
TYPE"U.FL-R-SMT-1(10)"
CDS_LIB"cnconnector"
NEEDS_NO_SIZE"TRUE"
A\NAC19
%"PCOAX"
1,"(6325,-7550)","0","cnconnector","I424"
$LOCATION"PX?"
TYPE"U.FL-R-SMT-1(10)"
NEEDS_NO_SIZE"TRUE"
CDS_LIB"cnconnector"
A\NAC17
%"vcc_bar"
1,"(6000,-8250)","0","mtca_interface_board","I425"
HDL_POWER"VCC3V3"
CDS_LIB"mtca_interface_board"
HOTSPOT_022
%"IOPORT"
1,"(6000,-5750)","0","standard","I426"
OFFPAGE"TRUE"
CDS_LIB"standard"
A
VHDL_PORT"INOUT"
HDL_PORT"INOUT"2
%"IOPORT"
1,"(6000,-5800)","0","standard","I427"
OFFPAGE"TRUE"
CDS_LIB"standard"
A
VHDL_PORT"INOUT"
HDL_PORT"INOUT"3
%"IOPORT"
1,"(6000,-5850)","0","standard","I428"
OFFPAGE"TRUE"
CDS_LIB"standard"
A
VHDL_PORT"INOUT"
HDL_PORT"INOUT"4
%"SF-0603FP015F-2"
1,"(9100,-6350)","0","oxflib","I429"
CDS_LIB"oxflib"
CDS_LMAN_SYM_OUTLINE"-125,125,125,-125"
148
226
END.
