uob-hep-cad/uob-hep-pc072/hardware/Cadence/top/mtca_interface_board_reocc/07_#20backplane#20interface/sch_1/page1.csv

FILE_TYPE = CONNECTIVITY
{Allegro Design Entry HDL 24.1 P001 (4234998) 9/4/2024}
PAGE_NUMBER = 2
0"NC"
1"MP3V3\g"
2"GND"
3"GND"
4"GND"
5"VP12\g"
6"MP3V3_IN"
7"GND"
8"BP.FPGA_GBE_RXP"
9"BP.FPGA_GBE_RXN"
10"GND"
11"12V_IN"
12"GND"
13"GND"
14"GND"
15"GND"
16"BP.DATA_OUT_N<11>"
17"GND"
18"BP.DATA_OUT_P<11>"
19"BP.DATA_OUT_N<10>"
20"GND"
21"BP.DATA_OUT_P<10>"
22"GND"
23"GND"
24"BP.DATA_OUT_N<9>"
25"GND"
26"BP.DATA_OUT_P<9>"
27"BP.DATA_OUT_N<8>"
28"GND"
29"BP.DATA_OUT_P<8>"
30"GND"
31"GND"
32"BP.DATA_OUT_N<7>"
33"GND"
34"BP.DATA_OUT_P<7>"
35"BP.DATA_OUT_N<6>"
36"GND"
37"BP.DATA_OUT_P<6>"
38"GND"
39"GND"
40"BP.DATA_OUT_N<5>"
41"GND"
42"BP.DATA_OUT_P<5>"
43"BP.DATA_OUT_N<4>"
44"GND"
45"BP.DATA_OUT_P<4>"
46"GND"
47"GND"
48"BP.DATA_OUT_N<3>"
49"GND"
50"BP.DATA_OUT_P<3>"
51"BP.DATA_OUT_N<2>"
52"GND"
53"BP.DATA_OUT_P<2>"
54"GND"
55"GND"
56"BP.DATA_OUT_N<1>"
57"GND"
58"BP.DATA_OUT_P<1>"
59"BP.DATA_OUT_N<0>"
60"GND"
61"BP.DATA_OUT_P<0>"
62"GND"
63"GND"
64"BP.DATA_IN_N<11>"
65"GND"
66"BP.DATA_IN_P<11>"
67"BP.DATA_IN_N<10>"
68"GND"
69"BP.DATA_IN_P<10>"
70"GND"
71"GND"
72"BP.DATA_IN_N<9>"
73"GND"
74"BP.DATA_IN_P<9>"
75"BP.DATA_IN_N<8>"
76"GND"
77"BP.DATA_IN_P<8>"
78"GND"
79"GND"
80"BP.DATA_IN_N<7>"
81"GND"
82"BP.DATA_IN_P<7>"
83"BP.DATA_IN_N<6>"
84"GND"
85"BP.DATA_IN_P<6>"
86"GND"
87"GND"
88"BP.DATA_IN_N<5>"
89"GND"
90"BP.DATA_IN_P<5>"
91"GND"
92"GND"
93"GND"
94"BP.DATA_IN_N<3>"
95"BP.DATA_IN_P<3>"
96"BP.DATA_IN_N<2>"
97"GND"
98"BP.DATA_IN_P<2>"
99"GND"
100"GND"
101"GND"
102"BP.DATA_IN_N<0>"
103"BP.DATA_IN_P<0>"
104"GND"
105"GND"
106"GND"
107"GND"
108"GND"
109"GND"
110"GND"
111"GND"
112"GND"
113"GND"
114"GND"
115"GND"
116"GND"
117"GND"
118"BP.REF_CLK_N<11>"
119"GND"
120"BP.REF_CLK_P<11>"
121"BP.REF_CLK_N<10>"
122"GND"
123"BP.REF_CLK_P<10>"
124"GND"
125"GND"
126"BP.REF_CLK_N<9>"
127"BP.REF_CLK_P<9>"
128"BP.REF_CLK_N<8>"
129"GND"
130"BP.REF_CLK_N<7>"
131"GND"
132"BP.REF_CLK_P<7>"
133"GND"
134"BP.REF_CLK_P<6>"
135"GND"
136"GND"
137"BP.REF_CLK_N<5>"
138"GND"
139"BP.REF_CLK_P<5>"
140"BP.REF_CLK_N<4>"
141"GND"
142"BP.REF_CLK_P<4>"
143"GND"
144"GND"
145"BP.REF_CLK_N<3>"
146"GND"
147"BP.REF_CLK_P<3>"
148"BP.REF_CLK_N<2>"
149"GND"
150"GND"
151"GND"
152"BP.REF_CLK_P<1>"
153"GND"
154"GND"
155"BP.REF_CLK_N<1>"
156"GND"
157"GND"
158"BP.DATA_OUT_P<11..0>"
159"BP.PWR_ON"
160"BP.FPGA_GBE_RXP"
161"BP.AMC_IPMB_SCL"
162"BP.AMC_IPMB_SDA"
163"BP.DATA_IN_P<11..0>"
164"BP.DATA_IN_N<11..0>"
165"BP.REF_CLK_P<11..0>"
166"BP.REF_CLK_N<11..0>"
167"BP.AMC_N-PS<1..0>"
168"SEGMENT1"
169"SEGMENT3"
170"GND"
171"GND"
172"BP.REF_CLK_N<6>"
173"BP.REF_CLK_P<8>"
174"BP.AMC_GA<2..0>"
175"BP.DATA_OUT_N<11..0>"
176"GND"
177"GND"
178"GND"
179"GND"
180"BP.REF_CLK_P<0>"
181"BP<180..0>"
182"BP.FPGA_GBE_RXN"
183"BP.FPGA_GBE_TXP"
184"BP.FPGA_GBE_TXN"
185"BP.TDI"
186"BP.TDO"
187"BP.TCK"
188"BP.TMS"
189"BP.AMC_N-ENABLE"
190"GND"
191"GND"
192"GND"
193"GND"
194"GND"
195"BP.TMS"
196"BP.TDI"
197"BP.TDO"
198"BP.TCK"
199"GND"
200"GND"
201"GND"
202"GND"
203"GND"
204"GND"
205"GND"
206"GND"
207"GND"
208"GND"
209"GND"
210"GND"
211"GND"
212"GND"
213"GND"
214"GND"
215"GND"
216"GND"
217"GND"
218"GND"
219"GND"
220"GND"
221"GND"
222"GND"
223"GND"
224"GND"
225"GND"
226"GND"
227"GND"
228"GND"
229"GND"
230"GND"
231"GND"
232"GND"
233"GND"
234"GND"
235"GND"
236"12V_IN"
237"BP.AMC_N-ENABLE"
238"12V_IN"
239"BP.AMC_IPMB_SCL"
240"12V_IN"
241"BP.AMC_IPMB_SDA"
242"12V_IN"
243"BP.AMC_N-PS<0>"
244"12V_IN"
245"GND"
246"BP.FPGA_GBE_TXP"
247"GND"
248"12V_IN"
249"GND"
250"BP.AMC_GA<2>"
251"BP.AMC_GA<1>"
252"12V_IN"
253"GND"
254"BP.FPGA_GBE_TXN"
255"BP.AMC_N-PS<1>"
256"SEGMENT2"
257"GND"
258"GND"
259"BP.DATA_IN_P<1>"
260"BP.DATA_IN_N<1>"
261"GND"
262"BP.DATA_IN_P<4>"
263"BP.DATA_IN_N<4>"
264"GND"
265"BP.REF_CLK_N<0>"
266"BP.REF_CLK_P<2>"
267"GND"
268"BP.AMC_GA<0>"
269"GND"
270"GND"
271"GND"
272"GND"
273"GND"
274"BP.PWR_ON"
%"gnd"
1,"(1550,-4800)","0","mtca_interface_board","12P"
HDL_POWER"GND"
CDS_LIB"mtca_interface_board"
HOTSPOT_02
%"gnd"
1,"(6100,-3500)","0","mtca_interface_board","13P"
HDL_POWER"GND"
CDS_LIB"mtca_interface_board"
HOTSPOT_07
%"gnd"
1,"(4025,-925)","0","mtca_interface_board","14P"
HDL_POWER"GND"
CDS_LIB"mtca_interface_board"
HOTSPOT_03
%"vcc_bar"
1,"(875,-500)","0","mtca_interface_board","16P"
HDL_POWER"MP3V3"
CDS_LIB"mtca_interface_board"
HOTSPOT_01
%"mt_hole"
1,"(6925,-3225)","1","ocad_parts_lib","17P"
VALUE"Mt_Hole"
$LOCATION"MH7"
SEC"1"
AVAILABILITY"21 days"
PRICE"0.02"
DISTRIBUTOR"HEP"
DISTRIBUTOR_PARTNUMBER"Mt_Hole"
MANUFACTURER"HEP"
MPN"Mt_Hole"
DESCRIPTION"PCB MOUNT-HOLE PAD200C_128 DRILL"
PART_TYPE"Misc"
PART_NUMBER"Mt_Hole"
REUSE_ANNOTATE"TRUE"
SOURCE_PACKAGE"Mt_Hole"
JEDEC_TYPE"mounthole"
CDS_LOCATION"MH7"
CDS_LIB"ocad_parts_lib"
MH_SIG \B
$PN"1"7
%"mt_hole"
1,"(6175,-3225)","1","ocad_parts_lib","18P"
VALUE"Mt_Hole"
$LOCATION"MH8"
SEC"1"
AVAILABILITY"21 days"
PRICE"0.02"
DISTRIBUTOR"HEP"
DISTRIBUTOR_PARTNUMBER"Mt_Hole"
MANUFACTURER"HEP"
MPN"Mt_Hole"
DESCRIPTION"PCB MOUNT-HOLE PAD200C_128 DRILL"
PART_TYPE"Misc"
PART_NUMBER"Mt_Hole"
REUSE_ANNOTATE"TRUE"
SOURCE_PACKAGE"Mt_Hole"
JEDEC_TYPE"mounthole"
CDS_LOCATION"MH8"
CDS_LIB"ocad_parts_lib"
MH_SIG \B
$PN"1"7
%"mch_connector1"
1,"(2500,-2550)","0","ocad_parts_lib","19P"
VALUE"MCH_TG1-EDGE-170"
$LOCATION"J7"
CDS_LIB"ocad_parts_lib"
CDS_LOCATION"J7"
JEDEC_TYPE"amc0_r2_bplus_pcb_edge"
SOURCE_PACKAGE"MCH_CONNECTOR1"
AVAILABILITY"In Stock"
PRICE"0.25"
DISTRIBUTOR"HEP"
DISTRIBUTOR_PARTNUMBER"MCH-EDGE-170"
MANUFACTURER"HEP"
MPN"MCH-EDGE-170"
DESCRIPTION"MCH-EDGE-170"
PART_TYPE"Connector"
PART_NUMBER"MCH1B-EDGE-170"
SEC"1"
GND1
$PN"1"12
GND2
$PN"7"267
GND3
$PN"10"247
GND4
$PN"13"245
GND5
$PN"16"10
GND6
$PN"19"253
GND7
$PN"22"190
GND8
$PN"25"249
GND9
$PN"28"191
GND10
$PN"31"192
GND11
$PN"34"193
GND12
$PN"37"194
TMS
$PN"166"195
TDI
$PN"169"196
TDO
$PN"168"197
TCK
$PN"165"198
GND13
$PN"40"199
GND14
$PN"43"200
RSVD
$PN"132"0
RSVD1
$PN"8"0
GND15
$PN"46"201
GND16
$PN"49"202
GND17
$PN"52"203
GND18
$PN"55"204
GND19
$PN"58"205
GND20
$PN"61"206
GND21
$PN"64"207
GND22
$PN"67"208
GND23
$PN"70"209
GND24
$PN"73"210
GND25
$PN"76"211
GND26
$PN"79"212
GND27
$PN"82"213
GND28
$PN"85"2
GND29
$PN"86"258
GND30
$PN"89"257
GND31
$PN"92"214
GND32
$PN"95"215
GND33
$PN"98"216
GND34
$PN"101"217
GND35
$PN"104"218
GND36
$PN"107"270
GND37
$PN"110"271
GND38
$PN"113"219
GND39
$PN"116"220
GND40
$PN"119"221
GND41
$PN"122"222
GND42
$PN"125"223
GND43
$PN"128"224
GND44
$PN"131"225
GND45
$PN"134"226
GND46
$PN"137"227
GND47
$PN"140"228
GND48
$PN"143"229
GND49
$PN"146"230
GND50
$PN"149"231
GND51
$PN"152"269
GND52
$PN"155"232
GND53
$PN"158"233
GND54
$PN"161"234
GND55
$PN"164"235
PWR1
$PN"2"11
PS1#
$PN"3"255
MP
$PN"4"6
GA0
$PN"5"268
RSVD0
$PN"6"0
PWR2
$PN"9"248
TXFUA+
$PN"11"246
TXFUA- \B
$PN"12"254
RXFUA+
$PN"14"8
RXFUA- \B
$PN"15"9
GA1
$PN"17"251
PWR3
$PN"18"252
TXFA-3+
$PN"20"0
TXFA-3- \B
$PN"21"0
RXFA-3+
$PN"23"0
RXFA-3- \B
$PN"24"0
GA2
$PN"26"250
PWR4
$PN"27"236
TXFA-5+
$PN"29"0
TXFA-5- \B
$PN"30"0
RXFA-5+
$PN"32"0
RXFA-5- \B
$PN"33"0
TXFA-7+
$PN"35"0
TXFA-7- \B
$PN"36"0
RXFA-7+
$PN"38"0
RXFA-7- \B
$PN"39"0
ENABLE#
$PN"41"237
PWR5
$PN"42"238
TXFA-9+
$PN"44"0
TXFA-9- \B
$PN"45"0
RXFA-9+
$PN"47"0
RXFA-9- \B
$PN"48"0
TXFA-10+
$PN"50"0
TXFA-10- \B
$PN"51"0
RXFA-10+
$PN"53"0
RXFA-10- \B
$PN"54"0
SCL_L
$PN"56"239
PWR6
$PN"57"240
TXFA-11+
$PN"59"0
TXFA-11- \B
$PN"60"0
RXFA-11+
$PN"62"0
RXFA-11- \B
$PN"63"0
TXFA-12+
$PN"65"0
TXFA-12- \B
$PN"66"0
RXFA-12+
$PN"68"0
RXFA-12- \B
$PN"69"0
SDA_L
$PN"71"241
PWR7
$PN"72"242
XOVER0+
$PN"74"0
XOVER0- \B
$PN"75"0
XOVER1+
$PN"77"0
XOVER1- \B
$PN"78"0
XOVER2+
$PN"80"0
XOVER2- \B
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
BN"85"188
%"BUS_TOP_LEFT_RIP"
1,"(5025,-2400)","0","default","I46"
HDL_TAP"TRUE"
BODY_TYPE"PLUMBING"
CDS_LIB"default"
BUS_END \NWC \NAC181
NET_END \NWC \NAC
BN"86"187
%"BUS_TOP_LEFT_RIP"
1,"(5025,-2350)","0","default","I47"
HDL_TAP"TRUE"
BODY_TYPE"PLUMBING"
CDS_LIB"default"
BUS_END \NWC \NAC181
NET_END \NWC \NAC
BN"87"189
%"BUS_TOP_LEFT_RIP"
1,"(5025,-2300)","0","default","I48"
HDL_TAP"TRUE"
BODY_TYPE"PLUMBING"
CDS_LIB"default"
BUS_END \NWC \NAC181
NET_END \NWC \NAC
BN"88"159
%"vcc_bar"
1,"(1225,-150)","0","mtca_interface_board","I50"
HDL_POWER"VP12"
CDS_LIB"mtca_interface_board"
HOTSPOT_05
%"SF-0603S300-2"
1,"(1525,-300)","0","oxflib","I51"
CDS_LIB"oxflib"
CDS_LMAN_SYM_OUTLINE"-125,125,125,-125"
211
15
%"SF-0603FP015F-2"
1,"(1175,-650)","0","oxflib","I52"
CDS_LMAN_SYM_OUTLINE"-125,125,125,-125"
CDS_LIB"oxflib"
11
26
END.
