uob-hep-cad/uob-hep-pc072/hardware/Cadence/top/mtca_interface_board_reocc/08_#20timing/sch_1/page1.csv

FILE_TYPE = CONNECTIVITY
{Allegro Design Entry HDL 24.1 P001 (4234998) 9/4/2024}
PAGE_NUMBER = 1
0"NC"
1"DFF_REF_CLK_P"
2"DFF_REF_CLK_N"
3"GND\g"
4"P2V5\g"
5"GND\g"
6"GND\g"
7"GND\g"
8"GND\g"
9"GND\g"
10"DIRECT_US_DATA_2_N"
11"P2V5\g"
12"DATA_SELECT_P2V5"
13"SFP_DATA_OUT_N<1>"
14"SFP_DATA_OUT_P<1>"
15"CLOCKED_US_DATA_2_P"
16"CLOCKED_US_DATA_2_N"
17"UN$1$r$I835$2"
18"GND\G"
19"P2V5\g"
20"SFP.RD_N<2>"
21"SFP.RD_P<2>"
22"P2V5\g"
23"SFP.RD_N<1>"
24"SFP1_CLKGEN_N"
25"DIRECT_US_DATA_2_P"
26"SFP_DATA_IO<11..0>"
27"GND\G"
28"P2V5\g"
29"P2V5\g"
30"GND\g"
31"GND\g"
32"GND\g"
33"GND\g"
34"P2V5\g"
35"P2V5\g"
36"P2V5\g"
37"GND\G"
38"P2V5\g"
39"GND\G"
40"GND\g"
41"VCC3V3\g"
42"GND\g"
43"GND\g"
44"VCC3V3\g"
45"UPSTREAM_DATA_N<1>"
46"UPSTREAM_DATA_P<1>"
47"UPSTREAM_DATA_P<0>"
48"UPSTREAM_DATA_N<0>"
49"DFF_CLK_P<2>"
50"DFF_CLK_N<2>"
51"SFP_DATA_OUT_N<2..0>"
52"UDATA_IN_P<2>"
53"UDATA_IN_N<2>"
54"UN$1$r$I575$2"
55"UN$1$r$I574$2"
56"UN$1$SY58608U$I571$VREF"
57"UPSTREAM_DATA_N<2..0>"
58"SFP.RD_P<1>"
59"UN$1$r$I568$2"
60"UN$1$r$I567$2"
61"UN$1$SY58608U$I564$VREF"
62"SFP_DATA_OUT_P<2..0>"
63"DIFF_CLK_SELECT"
64"DCT_DAT2_P"
65"DCT_DAT2_N"
66"UPSTREAM_DATA_P<2..0>"
67"CLOCKED_US_DATA_2_P"
68"CLOCKED_US_DATA_2_N"
69"SFP.RD_N<0>"
70"SFP_DATA_OUT_N<2>"
71"SFP_DATA_OUT_P<2>"
72"SFP2_CLKGEN_N"
73"SFPTD2_N"
74"SFPTD2_P"
75"SFP1_CLKGEN_P"
76"SFP.TD_N<2>"
77"SFP.TD_P<2>"
78"SFP.TD_P<1>"
79"SFP.TD_N<1>"
80"SFP0_CLKGEN_N"
81"SFP.TD_P<0>"
82"SFP.TD_N<0>"
83"UPSTREAM_DATA_P<2>"
84"SFP_DATA_OUT_N<0>"
85"UN$1$SY58608U$I557$VREF"
86"UN$1$r$I559$2"
87"SFP2_CLKGEN_P"
88"SFP_DATA_OUT_P<0>"
89"UN$1$r$I558$2"
90"SFP0_CLKGEN_P"
91"SFP.RD_P<0>"
92"UPSTREAM_DATA_N<2>"
%"gnd"
1,"(9500,-6675)","0","mtca_interface_board","141P"
CDS_LIB"mtca_interface_board"
HDL_POWER"GND"
ROOM"SFP_DFF_AND_FANOUT"
HOTSPOT_027
%"SY58608U"
1,"(11025,-5850)","0","cninterface","I557"
$LOCATION"IC?"
TYPE"SY58608UMG"
PACK_TYPE"QFN"
POWER_GROUP"VCC=P2V5"
CDS_LIB"cninterface"
ROOM"SFP_DFF_AND_FANOUT"
IN* \B89
VREF-AC85
IN86
Q090
Q188
Q0* \B80
Q1* \B84
VT85
%"r"
1,"(10400,-5950)","3","discrete","I558"
VALUE"0"
$LOCATION"R35"
SEC"1"
PART_NUMBER"EMA-00007500V42"
PART_TYPE"Thick Film"
DESCRIPTION"RES, Thick Film, 0, Jumper, 1/10W, SMD, 0402"
POWER"1/10W"
TOLERANCE"Jumper"
MPN"ERJ-2GE0R00X"
MANUFACTURER"Panasonic"
DISTRIBUTOR_PARTNUMBER"P0.0JTR-ND"
SOURCE_PACKAGE"R"
DATASHEET"C:\EMA\CISQuickStart\Technical_Datasheets\Panasonic\AOA0000CE1.PDF"
DISTRIBUTOR"Digikey"
JEDEC_TYPE"res0402"
CDS_LOCATION"R35"
CDS_LIB"discrete"
ROOM"SFP_DFF_AND_FANOUT"
1
XNET_PINS"1"
$PN"1"69
2
XNET_PINS"1"
$PN"2"89
%"r"
1,"(10425,-5750)","1","discrete","I559"
$LOCATION"R36"
VALUE"0"
DESCRIPTION"RES, Thick Film, 0, Jumper, 1/10W, SMD, 0402"
POWER"1/10W"
TOLERANCE"Jumper"
MPN"ERJ-2GE0R00X"
MANUFACTURER"Panasonic"
DISTRIBUTOR_PARTNUMBER"P0.0JTR-ND"
DISTRIBUTOR"Digikey"
DATASHEET"C:\EMA\CISQuickStart\Technical_Datasheets\Panasonic\AOA0000CE1.PDF"
SEC"1"
PART_NUMBER"EMA-00007500V42"
PART_TYPE"Thick Film"
SOURCE_PACKAGE"R"
CDS_LOCATION"R36"
CDS_LIB"discrete"
JEDEC_TYPE"res0402"
ROOM"SFP_DFF_AND_FANOUT"
1
XNET_PINS"1"
$PN"1"91
2
XNET_PINS"1"
$PN"2"86
%"gnd"
1,"(10650,-6450)","0","mtca_interface_board","I561"
CDS_LIB"mtca_interface_board"
HDL_POWER"GND"
ROOM"SFP_DFF_AND_FANOUT"
HOTSPOT_07
%"SY58608U"
1,"(11050,-6750)","0","cninterface","I564"
$LOCATION"IC?"
POWER_GROUP"VCC=P2V5"
PACK_TYPE"QFN"
TYPE"SY58608UMG"
CDS_LIB"cninterface"
ROOM"SFP_DFF_AND_FANOUT"
IN* \B60
VREF-AC61
IN59
Q075
Q114
Q0* \B24
Q1* \B13
VT61
%"gnd"
1,"(10675,-7350)","0","mtca_interface_board","I566"
CDS_LIB"mtca_interface_board"
HDL_POWER"GND"
ROOM"SFP_DFF_AND_FANOUT"
HOTSPOT_06
%"r"
1,"(10425,-6850)","3","discrete","I567"
$LOCATION"R35"
VALUE"0"
CDS_LOCATION"R35"
SEC"1"
TOLERANCE"Jumper"
POWER"1/10W"
DESCRIPTION"RES, Thick Film, 0, Jumper, 1/10W, SMD, 0402"
PART_TYPE"Thick Film"
PART_NUMBER"EMA-00007500V42"
MPN"ERJ-2GE0R00X"
MANUFACTURER"Panasonic"
DISTRIBUTOR_PARTNUMBER"P0.0JTR-ND"
DISTRIBUTOR"Digikey"
DATASHEET"C:\EMA\CISQuickStart\Technical_Datasheets\Panasonic\AOA0000CE1.PDF"
CDS_LIB"discrete"
SOURCE_PACKAGE"R"
JEDEC_TYPE"res0402"
ROOM"SFP_DFF_AND_FANOUT"
1
XNET_PINS"1"
$PN"1"23
2
XNET_PINS"1"
$PN"2"60
%"r"
1,"(10450,-6650)","1","discrete","I568"
$LOCATION"R36"
VALUE"0"
CDS_LOCATION"R36"
DISTRIBUTOR_PARTNUMBER"P0.0JTR-ND"
MANUFACTURER"Panasonic"
DISTRIBUTOR"Digikey"
DATASHEET"C:\EMA\CISQuickStart\Technical_Datasheets\Panasonic\AOA0000CE1.PDF"
SEC"1"
PART_TYPE"Thick Film"
DESCRIPTION"RES, Thick Film, 0, Jumper, 1/10W, SMD, 0402"
POWER"1/10W"
TOLERANCE"Jumper"
MPN"ERJ-2GE0R00X"
CDS_LIB"discrete"
PART_NUMBER"EMA-00007500V42"
SOURCE_PACKAGE"R"
JEDEC_TYPE"res0402"
ROOM"SFP_DFF_AND_FANOUT"
1
XNET_PINS"1"
$PN"1"58
2
XNET_PINS"1"
$PN"2"59
%"SY58608U"
1,"(11125,-7650)","0","cninterface","I571"
$LOCATION"IC?"
PACK_TYPE"QFN"
TYPE"SY58608UMG"
POWER_GROUP"VCC=P2V5"
CDS_LIB"cninterface"
ROOM"SFP_DFF_AND_FANOUT"
IN* \B55
VREF-AC56
IN54
Q087
Q171
Q0* \B72
Q1* \B70
VT56
%"gnd"
1,"(10750,-8250)","0","mtca_interface_board","I573"
CDS_LIB"mtca_interface_board"
HDL_POWER"GND"
ROOM"SFP_DFF_AND_FANOUT"
HOTSPOT_05
%"r"
1,"(10500,-7750)","3","discrete","I574"
$LOCATION"R35"
VALUE"0"
CDS_LOCATION"R35"
ROOM"SFP_DFF_AND_FANOUT"
CDS_LIB"discrete"
JEDEC_TYPE"res0402"
SOURCE_PACKAGE"R"
DATASHEET"C:\EMA\CISQuickStart\Technical_Datasheets\Panasonic\AOA0000CE1.PDF"
DISTRIBUTOR"Digikey"
DISTRIBUTOR_PARTNUMBER"P0.0JTR-ND"
TOLERANCE"Jumper"
MPN"ERJ-2GE0R00X"
MANUFACTURER"Panasonic"
POWER"1/10W"
DESCRIPTION"RES, Thick Film, 0, Jumper, 1/10W, SMD, 0402"
SEC"1"
PART_NUMBER"EMA-00007500V42"
PART_TYPE"Thick Film"
1
XNET_PINS"1"
$PN"1"20
2
XNET_PINS"1"
$PN"2"55
%"r"
1,"(10525,-7550)","1","discrete","I575"
$LOCATION"R36"
VALUE"0"
CDS_LOCATION"R36"
SEC"1"
DATASHEET"C:\EMA\CISQuickStart\Technical_Datasheets\Panasonic\AOA0000CE1.PDF"
DISTRIBUTOR"Digikey"
DISTRIBUTOR_PARTNUMBER"P0.0JTR-ND"
MANUFACTURER"Panasonic"
MPN"ERJ-2GE0R00X"
TOLERANCE"Jumper"
CDS_LIB"discrete"
PART_NUMBER"EMA-00007500V42"
PART_TYPE"Thick Film"
DESCRIPTION"RES, Thick Film, 0, Jumper, 1/10W, SMD, 0402"
POWER"1/10W"
JEDEC_TYPE"res0402"
SOURCE_PACKAGE"R"
ROOM"SFP_DFF_AND_FANOUT"
1
XNET_PINS"1"
$PN"1"21
2
XNET_PINS"1"
$PN"2"54
%"P2V5"
1,"(9550,-6150)","0","cnpower","I609"
SIZE"1B"
CDS_LIB"cnpower"
BODY_TYPE"PLUMBING"
HDL_POWER"P2V5"
ROOM"SFP_DFF_AND_FANOUT"
A<SIZE-1..0>\NAC
VHDL_INIT"1"28
%"P2V5"
1,"(12075,-8950)","0","cnpower","I643"
CDS_LIB"cnpower"
SIZE"1B"
BODY_TYPE"PLUMBING"
HDL_POWER"P2V5"
ROOM"SFP_DFF_AND_FANOUT"
A<SIZE-1..0>\NAC
VHDL_INIT"1"4
%"gnd"
1,"(12025,-10025)","0","mtca_interface_board","I648"
CDS_LIB"mtca_interface_board"
HDL_POWER"GND"
ROOM"SFP_DFF_AND_FANOUT"
HOTSPOT_03
%"MAX9381ESA"
1,"(12075,-9500)","0","bris_cds_logic","I649"
$LOCATION"?"
VALUE"MAX9381ESA"
CDS_LMAN_SYM_OUTLINE"-465,400,480,-300"
CDS_LIB"bris_cds_logic"
PACK_TYPE"SMD"
C"COPYRIGHT (C) 2015 ACCELERATED DESIGNS. ALL RIGHTS RESERVED"
VCC
$PN"?"4
Q
$PN"?"67
VEE
$PN"?"3
CLK
$PN"?"49
D
$PN"?"52
D* \B
$PN"?"53
CLK* \B
$PN"?"50
Q* \B
$PN"?"68
%"P2V5"
1,"(10375,-9075)","0","cnpower","I652"
SIZE"1B"
CDS_LIB"cnpower"
BODY_TYPE"PLUMBING"
HDL_POWER"P2V5"
ROOM"SFP_DFF_AND_FANOUT"
A<SIZE-1..0>\NAC
VHDL_INIT"1"29
%"gnd"
1,"(11075,-9200)","0","mtca_interface_board","I653"
CDS_LIB"mtca_interface_board"
HDL_POWER"GND"
ROOM"SFP_DFF_AND_FANOUT"
HOTSPOT_030
%"gnd"
1,"(11025,-9725)","0","mtca_interface_board","I654"
CDS_LIB"mtca_interface_board"
HDL_POWER"GND"
ROOM"SFP_DFF_AND_FANOUT"
HOTSPOT_031
%"gnd"
1,"(11025,-10000)","0","mtca_interface_board","I655"
CDS_LIB"mtca_interface_board"
HDL_POWER"GND"
ROOM"SFP_DFF_AND_FANOUT"
HOTSPOT_032
%"r"
1,"(10950,-9500)","5","discrete","I656"
$LOCATION"R134"
VALUE"100"
CDS_LOCATION"R134"
CDS_LIB"discrete"
JEDEC_TYPE"res0402"
SOURCE_PACKAGE"R"
DATASHEET"C:\EMA\CISQuickStart\Technical_Datasheets\Panasonic\AOA0000CE2.PDF"
DISTRIBUTOR_PARTNUMBER"P100LCT-ND"
DISTRIBUTOR"Digikey"
MANUFACTURER"Panasonic"
MPN"ERJ-2RKF1000X"
TOLERANCE"1%"
DESCRIPTION"RES SMD 100 OHM 1% 1/10W 0402"
PART_TYPE"Thick Film"
POWER"1/10W"
SEC"1"
REUSE_ANNOTATE"TRUE"
PART_NUMBER"ERJ-2RKF1000X"
ROOM"SFP_DFF_AND_FANOUT"
1
$PN"1"53
2
$PN"2"52
%"gnd"
1,"(10975,-10525)","0","mtca_interface_board","I659"
CDS_LIB"mtca_interface_board"
HDL_POWER"GND"
ROOM"SFP_DFF_AND_FANOUT"
HOTSPOT_033
%"r"
1,"(10900,-10300)","5","discrete","I660"
$LOCATION"R134"
VALUE"100"
CDS_LIB"discrete"
CDS_LOCATION"R134"
JEDEC_TYPE"res0402"
SOURCE_PACKAGE"R"
DATASHEET"C:\EMA\CISQuickStart\Technical_Datasheets\Panasonic\AOA0000CE2.PDF"
DISTRIBUTOR"Digikey"
DISTRIBUTOR_PARTNUMBER"P100LCT-ND"
MANUFACTURER"Panasonic"
MPN"ERJ-2RKF1000X"
DESCRIPTION"RES SMD 100 OHM 1% 1/10W 0402"
TOLERANCE"1%"
POWER"1/10W"
PART_TYPE"Thick Film"
PART_NUMBER"ERJ-2RKF1000X"
REUSE_ANNOTATE"TRUE"
SEC"1"
ROOM"SFP_DFF_AND_FANOUT"
1
$PN"1"50
2
$PN"2"49
%"P2V5"
1,"(10325,-9600)","0","cnpower","I663"
SIZE"1B"
CDS_LIB"cnpower"
BODY_TYPE"PLUMBING"
HDL_POWER"P2V5"
ROOM"SFP_DFF_AND_FANOUT"
A<SIZE-1..0>\NAC
VHDL_INIT"1"34
%"P2V5"
1,"(10325,-9875)","0","cnpower","I666"
CDS_LIB"cnpower"
SIZE"1B"
BODY_TYPE"PLUMBING"
HDL_POWER"P2V5"
ROOM"SFP_DFF_AND_FANOUT"
A<SIZE-1..0>\NAC
VHDL_INIT"1"35
%"P2V5"
1,"(10275,-10400)","0","cnpower","I671"
SIZE"1B"
CDS_LIB"cnpower"
BODY_TYPE"PLUMBING"
HDL_POWER"P2V5"
ROOM"SFP_DFF_AND_FANOUT"
A<SIZE-1..0>\NAC
VHDL_INIT"1"36
%"4 MERGE"
1,"(11325,-8600)","0","standard","I712"
CDS_LIB"standard"
NEEDS_NO_SIZE"TRUE"
BODY_TYPE"PLUMBING"
HDL_CONCAT"TRUE"
ROOM"SFP_DFF_AND_FANOUT"
A\NWC\NAC66
B\NWC\NAC57
C\NWC\NAC62
D\NWC\NAC51
Y\NWC\NAC26
%"IOPORT"
1,"(12100,-8600)","0","standard","I713"
CDS_LIB"standard"
OFFPAGE"TRUE"
ROOM"SFP_DFF_AND_FANOUT"
A
VHDL_PORT"INOUT"
HDL_PORT"INOUT"26
%"RSMD0402"
1,"(10475,-10475)","0","cnpassive","I726"
$LOCATION"R?"
TOL"1%"
VALUE"1K"
SIZE"1B"
CDS_LIB"cnpassive"
PACK_TYPE"1/16W"
DIST"FLAT"
NEGTOL"RTOL%"
POSTOL"RTOL%"
TOL_ON_OFF"ON"
POWER"RMAX"
VOLTAGE"RVMAX"
SLOPE"RSMAX"
MAX_TEMP"RTMAX"
TC1"RTMPL"
TC2"RTMPQ"
ROOM"SFP_DFF_AND_FANOUT"
B <SIZE-1..0>\NAC50
A <SIZE-1..0>\NAC36
%"RSMD0402"
1,"(10900,-10475)","0","cnpassive","I727"
$LOCATION"R?"
VALUE"2.2K"
TOL"1%"
CDS_LIB"cnpassive"
PACK_TYPE"1/16W"
SIZE"1B"
TOL_ON_OFF"ON"
POSTOL"RTOL%"
NEGTOL"RTOL%"
DIST"FLAT"
TC1"RTMPL"
MAX_TEMP"RTMAX"
SLOPE"RSMAX"
VOLTAGE"RVMAX"
POWER"RMAX"
TC2"RTMPQ"
ROOM"SFP_DFF_AND_FANOUT"
B <SIZE-1..0>\NAC33
A <SIZE-1..0>\NAC50
%"RSMD0402"
1,"(10950,-9950)","0","cnpassive","I728"
$LOCATION"R?"
TOL"1%"
VALUE"2.2K"
CDS_LIB"cnpassive"
PACK_TYPE"1/16W"
SIZE"1B"
TC2"RTMPQ"
TC1"RTMPL"
POWER"RMAX"
DIST"FLAT"
NEGTOL"RTOL%"
POSTOL"RTOL%"
TOL_ON_OFF"ON"
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
A <SIZE-1..0>\NAC
$PN"#"18
B <SIZE-1..0>\NAC
$PN"#"19
%"CAPCERSMDCL2"
1,"(9825,-8200)","1","cnpassive","I765"
$LOCATION"C?"
VOLTAGE"16V_GEN"
VALUE"100NF"
PACK_TYPE"0402"
SIZE"1"
CDS_LIB"cnpassive"
ROOM"SFP_DFF_AND_FANOUT"
A <SIZE-1..0>\NAC
$PN"#"18
B <SIZE-1..0>\NAC
$PN"#"19
%"P2V5"
1,"(9550,-7925)","0","cnpower","I766"
SIZE"1B"
CDS_LIB"cnpower"
BODY_TYPE"PLUMBING"
HDL_POWER"P2V5"
ROOM"SFP_DFF_AND_FANOUT"
A<SIZE-1..0>\NAC
VHDL_INIT"1"19
%"CAPCERSMDCL2"
1,"(9550,-8200)","1","cnpassive","I767"
$LOCATION"C?"
VOLTAGE"16V"
VALUE"1UF"
CDS_LIB"cnpassive"
PACK_TYPE"0402"
SIZE"1"
ROOM"SFP_DFF_AND_FANOUT"
A <SIZE-1..0>\NAC
$PN"#"18
B <SIZE-1..0>\NAC
$PN"#"19
%"gnd"
1,"(9500,-8450)","0","mtca_interface_board","I768"
CDS_LIB"mtca_interface_board"
HDL_POWER"GND"
ROOM"SFP_DFF_AND_FANOUT"
HOTSPOT_018
%"CAPCERSMDCL2"
1,"(13350,-10075)","1","cnpassive","I779"
$LOCATION"C?"
VALUE"1NF_X7R"
VOLTAGE"50V"
CDS_LIB"cnpassive"
ROOM"SFP_DFF_AND_FANOUT"
SIZE"1"
PACK_TYPE"0402"
A <SIZE-1..0>\NAC
$PN"#"39
B <SIZE-1..0>\NAC
$PN"#"38
%"CAPCERSMDCL2"
1,"(13100,-10075)","1","cnpassive","I780"
$LOCATION"C?"
VALUE"100NF"
VOLTAGE"16V_GEN"
CDS_LIB"cnpassive"
ROOM"SFP_DFF_AND_FANOUT"
SIZE"1"
PACK_TYPE"0402"
A <SIZE-1..0>\NAC
$PN"#"39
B <SIZE-1..0>\NAC
$PN"#"38
%"P2V5"
1,"(12825,-9800)","0","cnpower","I781"
CDS_LIB"cnpower"
ROOM"SFP_DFF_AND_FANOUT"
HDL_POWER"P2V5"
BODY_TYPE"PLUMBING"
SIZE"1B"
A<SIZE-1..0>\NAC
VHDL_INIT"1"38
%"CAPCERSMDCL2"
1,"(12825,-10075)","1","cnpassive","I782"
$LOCATION"C?"
VOLTAGE"16V"
VALUE"1UF"
CDS_LIB"cnpassive"
ROOM"SFP_DFF_AND_FANOUT"
SIZE"1"
PACK_TYPE"0402"
A <SIZE-1..0>\NAC
$PN"#"39
B <SIZE-1..0>\NAC
$PN"#"38
%"gnd"
1,"(12775,-10325)","0","mtca_interface_board","I783"
CDS_LIB"mtca_interface_board"
ROOM"SFP_DFF_AND_FANOUT"
HDL_POWER"GND"
HOTSPOT_039
%"CAPCERSMDCL2"
1,"(10025,-9400)","0","cnpassive","I784"
$LOCATION"C?"
VOLTAGE"16V_GEN"
VALUE"100NF"
SIZE"1"
CDS_LIB"cnpassive"
PACK_TYPE"0402"
ROOM"SFP_DFF_AND_FANOUT"
A <SIZE-1..0>\NAC
XNET_PINS"1"
$PN"#"92
B <SIZE-1..0>\NAC
XNET_PINS"1"
$PN"#"53
%"CAPCERSMDCL2"
1,"(10225,-9300)","0","cnpassive","I785"
$LOCATION"C?"
VOLTAGE"16V_GEN"
VALUE"100NF"
CDS_LIB"cnpassive"
SIZE"1"
PACK_TYPE"0402"
ROOM"SFP_DFF_AND_FANOUT"
A <SIZE-1..0>\NAC
XNET_PINS"1"
$PN"#"83
B <SIZE-1..0>\NAC
XNET_PINS"1"
$PN"#"52
%"CAPCERSMDCL2"
1,"(10225,-10100)","0","cnpassive","I786"
$LOCATION"C?"
VOLTAGE"16V_GEN"
VALUE"100NF"
CDS_LIB"cnpassive"
SIZE"1"
PACK_TYPE"0402"
ROOM"SFP_DFF_AND_FANOUT"
A <SIZE-1..0>\NAC
XNET_PINS"1"
$PN"#"1
B <SIZE-1..0>\NAC
XNET_PINS"1"
$PN"#"49
%"CAPCERSMDCL2"
1,"(10075,-10200)","0","cnpassive","I787"
$LOCATION"C?"
VALUE"100NF"
VOLTAGE"16V_GEN"
CDS_LIB"cnpassive"
SIZE"1"
PACK_TYPE"0402"
ROOM"SFP_DFF_AND_FANOUT"
A <SIZE-1..0>\NAC
XNET_PINS"1"
$PN"#"2
B <SIZE-1..0>\NAC
XNET_PINS"1"
$PN"#"50
%"r"
1,"(15850,-7275)","3","discrete","I796"
$LOCATION"R35"
VALUE"0"
CDS_LOCATION"R35"
ROOM"SFP_DFF_AND_FANOUT"
CDS_LIB"discrete"
JEDEC_TYPE"res0402"
SOURCE_PACKAGE"R"
DATASHEET"C:\EMA\CISQuickStart\Technical_Datasheets\Panasonic\AOA0000CE1.PDF"
DISTRIBUTOR"Digikey"
DISTRIBUTOR_PARTNUMBER"P0.0JTR-ND"
TOLERANCE"Jumper"
MPN"ERJ-2GE0R00X"
MANUFACTURER"Panasonic"
POWER"1/10W"
DESCRIPTION"RES, Thick Film, 0, Jumper, 1/10W, SMD, 0402"
SEC"1"
PART_NUMBER"EMA-00007500V42"
PART_TYPE"Thick Film"
1
$PN"1"74
2
$PN"2"77
%"r"
1,"(15850,-7125)","3","discrete","I797"
$LOCATION"R35"
VALUE"0"
CDS_LOCATION"R35"
ROOM"SFP_DFF_AND_FANOUT"
CDS_LIB"discrete"
JEDEC_TYPE"res0402"
SOURCE_PACKAGE"R"
DATASHEET"C:\EMA\CISQuickStart\Technical_Datasheets\Panasonic\AOA0000CE1.PDF"
DISTRIBUTOR"Digikey"
DISTRIBUTOR_PARTNUMBER"P0.0JTR-ND"
TOLERANCE"Jumper"
MPN"ERJ-2GE0R00X"
MANUFACTURER"Panasonic"
POWER"1/10W"
DESCRIPTION"RES, Thick Film, 0, Jumper, 1/10W, SMD, 0402"
SEC"1"
PART_NUMBER"EMA-00007500V42"
PART_TYPE"Thick Film"
1
$PN"1"73
2
$PN"2"76
%"r"
1,"(15975,-6325)","3","discrete","I798"
$LOCATION"R35"
VALUE"0"
CDS_LOCATION"R35"
ROOM"SFP_DFF_AND_FANOUT"
CDS_LIB"discrete"
JEDEC_TYPE"res0402"
SOURCE_PACKAGE"R"
DATASHEET"C:\EMA\CISQuickStart\Technical_Datasheets\Panasonic\AOA0000CE1.PDF"
DISTRIBUTOR"Digikey"
DISTRIBUTOR_PARTNUMBER"P0.0JTR-ND"
TOLERANCE"Jumper"
MPN"ERJ-2GE0R00X"
MANUFACTURER"Panasonic"
POWER"1/10W"
DESCRIPTION"RES, Thick Film, 0, Jumper, 1/10W, SMD, 0402"
SEC"1"
PART_NUMBER"EMA-00007500V42"
PART_TYPE"Thick Film"
1
$PN"1"46
2
$PN"2"78
%"r"
1,"(15975,-6425)","3","discrete","I799"
$LOCATION"R35"
VALUE"0"
CDS_LOCATION"R35"
PART_TYPE"Thick Film"
PART_NUMBER"EMA-00007500V42"
SEC"1"
DESCRIPTION"RES, Thick Film, 0, Jumper, 1/10W, SMD, 0402"
POWER"1/10W"
MANUFACTURER"Panasonic"
MPN"ERJ-2GE0R00X"
TOLERANCE"Jumper"
DISTRIBUTOR_PARTNUMBER"P0.0JTR-ND"
DISTRIBUTOR"Digikey"
DATASHEET"C:\EMA\CISQuickStart\Technical_Datasheets\Panasonic\AOA0000CE1.PDF"
SOURCE_PACKAGE"R"
JEDEC_TYPE"res0402"
CDS_LIB"discrete"
ROOM"SFP_DFF_AND_FANOUT"
1
$PN"1"45
2
$PN"2"79
%"r"
1,"(15950,-5875)","3","discrete","I800"
$LOCATION"R35"
VALUE"0"
CDS_LOCATION"R35"
PART_TYPE"Thick Film"
PART_NUMBER"EMA-00007500V42"
SEC"1"
DESCRIPTION"RES, Thick Film, 0, Jumper, 1/10W, SMD, 0402"
POWER"1/10W"
MANUFACTURER"Panasonic"
MPN"ERJ-2GE0R00X"
TOLERANCE"Jumper"
DISTRIBUTOR_PARTNUMBER"P0.0JTR-ND"
DISTRIBUTOR"Digikey"
DATASHEET"C:\EMA\CISQuickStart\Technical_Datasheets\Panasonic\AOA0000CE1.PDF"
SOURCE_PACKAGE"R"
JEDEC_TYPE"res0402"
CDS_LIB"discrete"
ROOM"SFP_DFF_AND_FANOUT"
1
$PN"1"47
2
$PN"2"81
%"r"
1,"(15950,-5975)","3","discrete","I801"
$LOCATION"R35"
VALUE"0"
CDS_LOCATION"R35"
PART_TYPE"Thick Film"
PART_NUMBER"EMA-00007500V42"
SEC"1"
DESCRIPTION"RES, Thick Film, 0, Jumper, 1/10W, SMD, 0402"
POWER"1/10W"
MANUFACTURER"Panasonic"
MPN"ERJ-2GE0R00X"
TOLERANCE"Jumper"
DISTRIBUTOR_PARTNUMBER"P0.0JTR-ND"
DISTRIBUTOR"Digikey"
DATASHEET"C:\EMA\CISQuickStart\Technical_Datasheets\Panasonic\AOA0000CE1.PDF"
SOURCE_PACKAGE"R"
JEDEC_TYPE"res0402"
CDS_LIB"discrete"
ROOM"SFP_DFF_AND_FANOUT"
1
$PN"1"48
2
$PN"2"82
%"854S01I"
1,"(14950,-7275)","0","cninterface","I802"
$LOCATION"IC?"
PACK_TYPE"QFN"
TYPE"854S01AKILF"
POWER_GROUP"VDD=VCC3V3"
CDS_LIB"cninterface"
CDS_LMAN_SYM_OUTLINE"-250,200,250,-200"
HAS_FIXED_SIZE"2B"
NPCLK<0>16
PCLK<0>15
PCLK<1>64
NPCLK<1>65
RESERVED0
CLK_SEL63
NQ73
Q74
%"74AVC1T45"
1,"(13425,-8000)","0","cninterface","I803"
$LOCATION"IC?"
TYPE"SN74AVC1T45DCK"
PACK_TYPE"SC70"
CDS_LIB"cninterface"
VCCA11
VCCB44
GND8
DIR11
B63
A12
%"CAPCERSMDCL2"
1,"(13900,-7225)","0","cnpassive","I808"
$LOCATION"C?"
VALUE"100NF"
CDS_LIB"cnpassive"
SIZE"1"
PACK_TYPE"0402"
VOLTAGE"16V_GEN"
ROOM"SFP_DFF_AND_FANOUT"
A <SIZE-1..0>\NAC
$PN"#"25
B <SIZE-1..0>\NAC
$PN"#"64
%"CAPCERSMDCL2"
1,"(13900,-7400)","0","cnpassive","I809"
$LOCATION"C?"
VALUE"100NF"
ROOM"SFP_DFF_AND_FANOUT"
PACK_TYPE"0402"
SIZE"1"
CDS_LIB"cnpassive"
VOLTAGE"16V_GEN"
A <SIZE-1..0>\NAC
$PN"#"10
B <SIZE-1..0>\NAC
$PN"#"65
%"r"
1,"(14275,-7300)","5","discrete","I810"
$LOCATION"?"
VALUE"100"
ROOM"SFP_DFF_AND_FANOUT"
REUSE_ANNOTATE"TRUE"
DESCRIPTION"RES SMD 100 OHM 1% 1/10W 0402"
PART_TYPE"Thick Film"
PART_NUMBER"ERJ-2RKF1000X"
POWER"1/10W"
TOLERANCE"1%"
MPN"ERJ-2RKF1000X"
DISTRIBUTOR_PARTNUMBER"P100LCT-ND"
MANUFACTURER"Panasonic"
DISTRIBUTOR"Digikey"
DATASHEET"C:\EMA\CISQuickStart\Technical_Datasheets\Panasonic\AOA0000CE2.PDF"
SOURCE_PACKAGE"R"
JEDEC_TYPE"res0402"
CDS_LIB"discrete"
1
$PN"?"64
2
$PN"?"65
%"CAPCERSMDCL2"
1,"(16775,-7875)","1","cnpassive","I813"
$LOCATION"C?"
VALUE"1NF_X7R"
VOLTAGE"50V"
PACK_TYPE"0402"
SIZE"1"
ROOM"SFP_DFF_AND_FANOUT"
CDS_LIB"cnpassive"
A <SIZE-1..0>\NAC
$PN"#"40
B <SIZE-1..0>\NAC
$PN"#"41
%"CAPCERSMDCL2"
1,"(16525,-7875)","1","cnpassive","I814"
$LOCATION"C?"
VALUE"100NF"
VOLTAGE"16V_GEN"
ROOM"SFP_DFF_AND_FANOUT"
SIZE"1"
PACK_TYPE"0402"
CDS_LIB"cnpassive"
A <SIZE-1..0>\NAC
$PN"#"40
B <SIZE-1..0>\NAC
$PN"#"41
%"CAPCERSMDCL2"
1,"(16250,-7875)","1","cnpassive","I815"
$LOCATION"C?"
VOLTAGE"16V"
VALUE"1UF"
PACK_TYPE"0402"
SIZE"1"
ROOM"SFP_DFF_AND_FANOUT"
CDS_LIB"cnpassive"
A <SIZE-1..0>\NAC
$PN"#"40
B <SIZE-1..0>\NAC
$PN"#"41
%"gnd"
1,"(16200,-8125)","0","mtca_interface_board","I817"
HDL_POWER"GND"
ROOM"SFP_DFF_AND_FANOUT"
CDS_LIB"mtca_interface_board"
HOTSPOT_040
%"vcc_bar"
1,"(16200,-7600)","0","mtca_interface_board","I818"
HDL_POWER"VCC3V3"
CDS_LIB"mtca_interface_board"
HOTSPOT_041
%"gnd"
1,"(13375,-8300)","0","mtca_interface_board","I822"
ROOM"SFP_DFF_AND_FANOUT"
HDL_POWER"GND"
CDS_LIB"mtca_interface_board"
HOTSPOT_08
%"gnd"
1,"(14350,-8375)","0","mtca_interface_board","I824"
HDL_POWER"GND"
ROOM"SFP_DFF_AND_FANOUT"
CDS_LIB"mtca_interface_board"
HOTSPOT_042
%"CAPCERSMDCL2"
1,"(14225,-8275)","0","cnpassive","I825"
$LOCATION"C?"
VOLTAGE"16V_GEN"
VALUE"100NF"
PACK_TYPE"0402"
SIZE"1"
ROOM"SFP_DFF_AND_FANOUT"
CDS_LIB"cnpassive"
A <SIZE-1..0>\NAC
$PN"#"44
B <SIZE-1..0>\NAC
$PN"#"42
%"CAPCERSMDCL2"
1,"(12975,-8225)","2","cnpassive","I826"
$LOCATION"C?"
VALUE"100NF"
VOLTAGE"16V_GEN"
ROOM"SFP_DFF_AND_FANOUT"
SIZE"1"
PACK_TYPE"0402"
CDS_LIB"cnpassive"
A <SIZE-1..0>\NAC
$PN"#"11
B <SIZE-1..0>\NAC
$PN"#"43
%"gnd"
1,"(12775,-8325)","0","mtca_interface_board","I827"
CDS_LIB"mtca_interface_board"
ROOM"SFP_DFF_AND_FANOUT"
HDL_POWER"GND"
HOTSPOT_043
%"P2V5"
1,"(12650,-7925)","0","cnpower","I828"
CDS_LIB"cnpower"
SIZE"1B"
BODY_TYPE"PLUMBING"
HDL_POWER"P2V5"
ROOM"SFP_DFF_AND_FANOUT"
A<SIZE-1..0>\NAC
VHDL_INIT"1"11
%"IOPORT"
1,"(12675,-7675)","2","standard","I831"
OFFPAGE"TRUE"
CDS_LIB"standard"
A
HDL_PORT"INOUT"
VHDL_PORT"INOUT"12
%"IOPORT"
1,"(12950,-7400)","2","standard","I832"
OFFPAGE"TRUE"
CDS_LIB"standard"
A
VHDL_PORT"INOUT"
HDL_PORT"INOUT"10
%"IOPORT"
1,"(12950,-7225)","2","standard","I833"
OFFPAGE"TRUE"
CDS_LIB"standard"
A
VHDL_PORT"INOUT"
HDL_PORT"INOUT"25
%"vcc_bar"
1,"(13925,-8050)","0","mtca_interface_board","I834"
HDL_POWER"VCC3V3"
CDS_LIB"mtca_interface_board"
HOTSPOT_044
%"r"
1,"(13375,-6600)","0","discrete","I835"
VALUE"49.9"
$LOCATION"R20"
ROOM"CLK_GEN_X12"
SEC"1"
PART_NUMBER"311-49.9LRCT-ND"
PART_TYPE"Thick Film"
DESCRIPTION"RES SMD 49.9 OHM 1% 1/16W 0402"
TOLERANCE"1%"
POWER"1/10W"
MPN"RC0402FR-0749R9L"
MANUFACTURER"Yageo"
DISTRIBUTOR_PARTNUMBER"311-49.9LRCT-ND"
DISTRIBUTOR"Digikey"
SOURCE_PACKAGE"R"
DESIGNATORNAMEPROP"TIMING"
CDS_LIB"discrete"
CDS_LOCATION"R20"
JEDEC_TYPE"res0402"
1
$PN"1"16
2
$PN"2"17
%"r"
1,"(13675,-6600)","0","discrete","I836"
VALUE"49.9"
$LOCATION"R20"
ROOM"CLK_GEN_X12"
SEC"1"
PART_NUMBER"311-49.9LRCT-ND"
PART_TYPE"Thick Film"
DESCRIPTION"RES SMD 49.9 OHM 1% 1/16W 0402"
TOLERANCE"1%"
POWER"1/10W"
MPN"RC0402FR-0749R9L"
MANUFACTURER"Yageo"
DISTRIBUTOR_PARTNUMBER"311-49.9LRCT-ND"
DISTRIBUTOR"Digikey"
SOURCE_PACKAGE"R"
DESIGNATORNAMEPROP"TIMING"
CDS_LIB"discrete"
CDS_LOCATION"R20"
JEDEC_TYPE"res0402"
1
$PN"1"15
2
$PN"2"17
%"RSMD0603"
1,"(13550,-6900)","1","cnpassive","I837"
$LOCATION"R?"
TOL"1%"
VALUE"20"
SIZE"1B"
TOL_ON_OFF"ON"
POSTOL"RTOL%"
NEGTOL"RTOL%"
DIST"FLAT"
POWER"RMAX"
VOLTAGE"RVMAX"
SLOPE"RSMAX"
MAX_TEMP"RTMAX"
TC1"RTMPL"
TC2"RTMPQ"
CDS_LIB"cnpassive"
PACK_TYPE"1/10W"
B <SIZE-1..0>\NAC17
A <SIZE-1..0>\NAC9
%"gnd"
1,"(13500,-7050)","0","mtca_interface_board","I838"
CDS_LIB"mtca_interface_board"
HDL_POWER"GND"
ROOM"SFP_DFF_AND_FANOUT"
HOTSPOT_09
END.
