uob-hep-cad/uob-hep-pc072/hardware/Cadence/top/mtca_interface_board_reocc/mib_tongue2/sch_1/page1.csv

FILE_TYPE = CONNECTIVITY
{Allegro Design Entry HDL 24.1 P001 (4234998) 9/4/2024}
PAGE_NUMBER = 2
0"NC"
1"BP.DATA_IN_P<5>"
2"GND"
3"GND_TONGUE2\g"
4"BP.DATA_IN_P<4>"
5"BP.DATA_IN_N<4>"
6"BP.DATA_IN_N<5>"
7"BP.DATA_IN_P<6>"
8"BP.DATA_IN_N<6>"
9"BP.DATA_IN_P<7>"
10"BP.DATA_IN_N<7>"
11"GND"
12"BP.DATA_IN_N<8>"
13"BP.DATA_IN_P<8>"
14"BP.DATA_IN_P<9>"
15"BP.DATA_OUT_N<4>"
16"GND"
17"BP.DATA_OUT_N<6>"
18"GND"
19"BP.DATA_IN_N<11>"
20"BP.DATA_OUT_P<1>"
21"GND"
22"GND"
23"GND"
24"BP.REF_CLK_N<10>"
25"BP.REF_CLK_P<10>"
26"BP.DATA_IN_P<9>"
27"BP.DATA_IN_N<9>"
28"BP.DATA_OUT_N<8>"
29"BP.DATA_OUT_P<7>"
30"GND"
31"GND"
32"BP.DATA_OUT_N<0>"
33"BP.DATA_OUT_N<2>"
34"BP.DATA_OUT_P<4>"
35"GND"
36"BP.DATA_OUT_P<2>"
37"BP.DATA_IN_P<11>"
38"BP.DATA_IN_P<11>"
39"BP.DATA_IN_P<10>"
40"BP.DATA_IN_P<10>"
41"BP.DATA_IN_P<8>"
42"BP.DATA_IN_P<7>"
43"BP.DATA_IN_P<6>"
44"BP.DATA_IN_P<4>"
45"BP.DATA_IN_P<3>"
46"BP.DATA_IN_P<3>"
47"BP.DATA_IN_P<2>"
48"BP.DATA_IN_P<2>"
49"BP.DATA_IN_P<1>"
50"BP.DATA_IN_P<1>"
51"BP.DATA_IN_P<0>"
52"BP.DATA_IN_P<0>"
53"BP.DATA_IN_P<5>"
54"BP.DATA_OUT_N<10>"
55"BP.DATA_OUT_P<10>"
56"BP.DATA_OUT_P<6>"
57"GND"
58"GND"
59"BP.DATA_OUT_P<1>"
60"GND"
61"BP.DATA_OUT_N<0>"
62"BP.REF_CLK_P<9>"
63"BP.DATA_OUT_P<7>"
64"BP.DATA_OUT_N<7>"
65"GND"
66"BP.DATA_OUT_P<8>"
67"GND"
68"BP.DATA_OUT_P<10>"
69"BP.REF_CLK_N<9>"
70"BP.DATA_IN_N<10>"
71"GND"
72"GND"
73"BP.DATA_OUT_N<9>"
74"GND"
75"BP.DATA_IN_N<5>"
76"BP.REF_CLK_P<6>"
77"BP.REF_CLK_N<6>"
78"BP.REF_CLK_N<7>"
79"BP.REF_CLK_N<11>"
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
$PN"46"263
47
$PN"47"264
48
$PN"48"80
49
$PN"49"265
50
$PN"50"79
51
$PN"51"266
52
$PN"52"267
53
$PN"53"23
54
$PN"54"268
55
$PN"55"269
56
$PN"56"270
57
$PN"57"21
58
$PN"58"271
59
$PN"59"272
60
$PN"60"58
%"ALIAS"
1,"(4075,-4200)","0","standard","I15"
CDS_LIB"standard"
A3
B
VHDL_ALIAS"TRUE"92
END.
