uob-hep-cad/uob-hep-pc072/hardware/Cadence/top/mtca_interface_board_reocc/05#20trenz#20te0712#20fpga#20modul_arce/sch_1/page2.csv

FILE_TYPE = CONNECTIVITY
{Allegro Design Entry HDL 17.4-2019 S011 (3890763) 9/18/2020}
PAGE_NUMBER = 2
0"NC"
1"VCC3V3\g"
2"GND\g"
3"GND\g"
4"VCC3V3\g"
5"VCC3V3\g"
6"P2V5\g"
7"P2V5\g"
8"VCC3V3\g"
9"VCC3V3\g"
10"VCC3V3\G"
11"VREF_JTAG\G"
12"GND"
13"DATA_SELECT_P2V5"
14"DIRECT_US_DATA_2_N"
15"DIRECT_US_DATA_2_P"
16"UPSTREAM_DATA_N<1>"
17"UPSTREAM_DATA_P<1>"
18"UPSTREAM_DATA_P<2>"
19"UPSTREAM_DATA_N<2>"
20"BP.DATA_IN_P<11>"
21"BP.DATA_IN_N<11>"
22"BP.DATA_IN_N<11>"
23"BP.DATA_IN_P<11>"
24"UPSTREAM_DATA_P<0>"
25"UPSTREAM_DATA_N<0>"
26"UPSTREAM_DATA_N<0>"
27"UPSTREAM_DATA_P<0>"
28"BP.DATA_OUT_N<7>"
29"BP.DATA_OUT_P<7>"
30"BP.DATA_OUT_P<5>"
31"BP.DATA_IN_P<5>"
32"BP.DATA_IN_N<5>"
33"GND"
34"CLKGEN_CLK_N<0>"
35"CLKGEN_CLK_P<0>"
36"AUXIO_P2"
37"BP.DATA_IN_P<3>"
38"P1V8_OUT"
39"BP.DATA_IN_P<4>"
40"BP.DATA_OUT_P<8>"
41"BP.DATA_OUT_N<8>"
42"BP.DATA_OUT_P<9>"
43"BP.DATA_OUT_N<9>"
44"BP.DATA_OUT_P<10>"
45"BP.DATA_OUT_N<10>"
46"GND"
47"SFP.TX_FAULT<1>"
48"CLK_I2C_SDA"
49"AUXIO_P3"
50"CLK_I2C_SCL"
51"N00771"
52"AUXIO_P5"
53"AUXIO_N5"
54"AUXIO_P6"
55"AUXIO_N6"
56"AUXIO_N2"
57"BP.DATA_IN_N<4>"
58"BP.DATA_OUT_N<5>"
59"GND"
60"AUXIO_P1"
61"BP.DATA_IN_N<3>"
62"BP.DATA_IN_N<2>"
63"BP.DATA_IN_P<2>"
64"BP.DATA_IN_P<1>"
65"BP.DATA_IN_P<0>"
66"BP.DATA_IN_P<8>"
67"BP.DATA_IN_P<6>"
68"GND"
69"BP.DATA_IN_P<7>"
70"BP.DATA_IN_N<7>"
71"GND"
72"BP.DATA_IN_N<8>"
73"BP.DATA_IN_N<9>"
74"GND"
75"DATA_FROM_UPSTREAM_N<1>"
76"DATA_FROM_UPSTREAM_P<1>"
77"AUXIO_P7"
78"AUXIO_N7"
79"GND"
80"AUXIO_P4"
81"AUXIO_N4"
82"AUXIO_N3"
83"BP.DATA_IN_N<6>"
84"BP.DATA_IN_P<9>"
85"FPGA_PG"
86"BP.DATA_IN_N<1>"
87"BP.DATA_IN_P<10>"
88"BP.DATA_IN_N<10>"
89"BP.DATA_IN_N<0>"
90"P3V3_OUT0"
91"UN$2$CAPCERSMDCL2$I418$B"
92"GND"
93"GND"
94"GND"
95"GND"
96"GND"
97"GND"
98"GND"
99"GND"
100"GND"
101"GND"
102"GND"
103"UART_TX_FROM_FPGA_3V3"
104"UART_RX_TO_FPGA_3V3"
105"AUX_GBE_RX_P"
106"AUX_GBE_RX_N"
107"AUX_GBE_TX_P"
108"BP.FPGA_GBE_TXN"
109"BP.FPGA_GBE_TXP"
110"DATA_FROM_UPSTREAM_P<0>"
111"DATA_FROM_UPSTREAM_N<0>"
112"SFP_DATA_OUT_N<0>"
113"SFP_DATA_OUT_P<0>"
114"SFP.SDA<0>"
115"SFP.SCL<0>"
116"SFP.SDA<1>"
117"SFP.SCL<1>"
118"SFP.SDA<2>"
119"SFP.SCL<2>"
120"BP.DATA_OUT_P<3>"
121"AUX_GBE_TX_N"
122"SFP.TX_DISABLE<0>"
123"SFP.TX_FAULT<0>"
124"SFP.LOS<0>"
125"BP.DATA_OUT_N<1>"
126"BP.DATA_OUT_P<1>"
127"SFP.LOS<1>"
128"SFP.TX_DISABLE<1>"
129"GND"
130"GND"
131"GND"
132"BP.DATA_OUT_N<11>"
133"BP.DATA_OUT_P<11>"
134"CLKGEN_CLK_P<1>"
135"CLKGEN_CLK_N<1>"
136"BP.DATA_OUT_P<6>"
137"BP.DATA_OUT_N<6>"
138"GND"
139"GND"
140"BP.DATA_OUT_P<2>"
141"GND"
142"BP.DATA_OUT_N<0>"
143"SFP_DATA_OUT_P<1>"
144"GND"
145"GND"
146"BP.FPGA_GBE_RXN"
147"GND"
148"GND"
149"GND"
150"GND"
151"GND"
152"BP.FPGA_GBE_RXP"
153"N00775"
154"FPGA_TMS"
155"FPGA_TDO"
156"SFP_DATA_OUT_N<1>"
157"GND"
158"GND"
159"BP.DATA_OUT_N<2>"
160"SFP.LOS<2>"
161"SFP.TX_FAULT<2>"
162"CLKGEN_LOL"
163"CLKGEN_INTR"
164"CLK_SEL0"
165"GND"
166"GND"
167"GND"
168"GND"
169"SFP_DATA_OUT_N<2>"
170"GND"
171"BP.DATA_OUT_N<4>"
172"BP.DATA_OUT_P<4>"
173"BP.DATA_OUT_P<0>"
174"CLK_SEL1"
175"P3V3_OUT1"
176"SFP.TX_DISABLE<2>"
177"P1V5_OUT"
178"DATA_FROM_UPSTREAM_N<2>"
179"DATA_FROM_UPSTREAM_P<2>"
180"SFP_DATA_OUT_P<2>"
181"BP.DATA_OUT_N<3>"
182"GND"
183"GND"
184"FPGA_TCK"
185"FPGA_TDI"
186"GND"
187"GND"
188"GND"
189"GND"
190"GND"
191"GND"
192"GND"
193"GND"
%"gnd"
1,"(6125,-6850)","0","mtca_interface_board","137P"
CDS_LIB"mtca_interface_board"
HDL_POWER"GND"
HOTSPOT_012
%"portright-l"
1,"(3600,-4800)","2","mtca_interface_board","2P"
NAME"FPGA_PG"
CDS_LIB"mtca_interface_board"
HOTSPOT_0
HDL_PORT"OUT"
PIN_NAME"FPGA_PG"85
%"te0712 connector-jb2"
1,"(8075,-5300)","0","ocad_parts_lib","307P"
$LOCATION"J8"
VALUE"LSHM-150-03.0-L-DV-A-S-K-TR"
CDS_LIB"ocad_parts_lib"
CDS_LOCATION"J8"
JEDEC_TYPE"samtec_lshm-150-04-0-l-dv-a-s"
SOURCE_PACKAGE"TE0712 Connector-JB2"
PART_NUMBER"LSHM-150-03.0-L-DV-A-S-K-TR"
PART_TYPE"Header"
DESCRIPTION"CONN SELF-MATE 100POS SMD GOLD"
CONTACTCURRENT"-"
SEC"1"
GND1
$PN"29"191
GND2
$PN"39"141
VIN4
$PN"1"4
VCCIO13_0
$PN"2"6
VIN5
$PN"3"4
VCCIO13_1
$PN"4"6
VIN6
$PN"5"4
NC0
$PN"6"0
VIN7
$PN"7"4
VCCIO15_0
$PN"8"6
VCC3V3_1
$PN"9"175
VCCIO15_1
$PN"10"6
VCC3V3_2
$PN"11"175
B14_L_8__N
$PN"12"122
B14_L_10__N
$PN"13"164
B14_L_8__P
$PN"14"123
B14_L_10_P
$PN"15"174
B14_L_17__N
$PN"16"124
RESIN
$PN"17"153
B14_L_17__P
$PN"18"128
GND0
$PN"19"190
VCC1V5
$PN"20"177
B14_L_12__P
$PN"21"163
B14_L_14__P
$PN"22"127
B14_L_12__N
$PN"23"162
B14_L_14__N
$PN"24"176
B14_L_11__P
$PN"25"161
B14_L_13__P
$PN"26"114
B14_L_11__N
$PN"27"160
B14_L_13__N
$PN"28"115
NC1
$PN"30"0
B15_L_9__N
$PN"31"142
B14_L_16__P
$PN"32"116
B15_L_9__P
$PN"33"173
B14_L_16__N
$PN"34"117
B15_L_8__N
$PN"35"125
B14_L_15__P
$PN"36"118
B15_L_8__P
$PN"37"126
B14_L_15__N
$PN"38"119
GND3
$PN"40"182
B15_L_7__N
$PN"41"159
B15_L_23__P
$PN"42"0
B15_L_7__P
$PN"43"140
B15_L_23__N
$PN"44"0
B15_L_13__P
$PN"45"0
B15_L_19__P
$PN"46"120
B15_L_13__N
$PN"47"0
B15_L_19__N
$PN"48"181
GND4
$PN"49"189
GND5
$PN"50"188
B15_L_14__P
$PN"51"30
B15_L_11__P
$PN"52"172
B15_L_14__N
$PN"53"58
B15_L_11__N
$PN"54"171
B15_L_12__P
$PN"55"134
B15_L_3__P
$PN"56"0
B15_L_12__N
$PN"57"135
B15_L_3__N
$PN"58"0
GND6
$PN"59"139
GND7
$PN"60"187
B15_L_10__N
$PN"61"137
B15_L_17__N
$PN"62"28
B15_L_10__P
$PN"63"136
B15_L_17__P
$PN"64"29
B15_L_18__P
$PN"65"0
B15_L_16__P
$PN"66"0
B15_L_18__N
$PN"67"0
B15_L_16__N
$PN"68"0
GND8
$PN"69"138
GND9
$PN"70"157
B15_L_20__P
$PN"71"40
B15_L_1__P
$PN"72"27
B15_L_20__N
$PN"73"41
B15_L_1__N
$PN"74"26
B15_L_15__P
$PN"75"42
B15_L_2__N
$PN"76"16
B15_L_15__N
$PN"77"43
B15_L_2__P
$PN"78"17
GND10
$PN"79"158
GND11
$PN"80"186
B15_L_6__N
$PN"81"0
B15_L_4__P
$PN"82"18
B15_L_6__P
$PN"83"0
B15_L_4__N
$PN"84"19
B15_L_21__P
$PN"85"44
B15_L_5__N
$PN"86"0
B15_L_21__N
$PN"87"45
B15_L_5__P
$PN"88"0
GND12
$PN"89"46
B15_IO0
$PN"90"0
B15_L_24__N
$PN"91"0
VCC3V3_3
$PN"92"11
B15_L_24__P
$PN"93"0
TMS
$PN"94"154
B15_L_22__P
$PN"95"133
TDI
$PN"96"185
B15_L_22__N
$PN"97"132
TDO
$PN"98"155
B15_IO25
$PN"99"0
TCK
$PN"100"184
F2
$PN"101"170
F1
$PN"102"183
%"cap_np_0"
1,"(3650,-8700)","7","ocad_parts_lib","313P"
VOLTAGE"25V"
VALUE"0.1UF"
$LOCATION"C39"
CDS_LIB"ocad_parts_lib"
CDS_LOCATION"C39"
JEDEC_TYPE"cap0402"
SOURCE_PACKAGE"CAP_NP_0"
PART_NUMBER"445-7348-2-ND"
AVAILABILITY"In Stock"
ROOM"TE0712"
CLASS"DISCRETE"
LAST_EDIT_BY"SNF"
ALT_SYMBOLS""
SEC"1"
1
$PN"1"179
2
$PN"2"180
%"r"
1,"(3700,-4550)","0","discrete","322P"
VALUE"4.99k"
$LOCATION"R13"
CDS_LIB"discrete"
CDS_LOCATION"R13"
JEDEC_TYPE"res0402"
SOURCE_PACKAGE"R"
REUSE_ID"48"
ROOM"TE0712"
AVAILABILITY"In Stock"
DISTRIBUTOR"Digikey"
DISTRIBUTOR_PARTNUMBER"P4.99KLTR-ND"
MANUFACTURER"Panasonic"
MPN"ERJ-2RKF4991X"
TOLERANCE"1%"
POWER"1/10 W"
DESCRIPTION"RES SMD 4.99K OHM 1% 1/10W 0402"
PART_TYPE"Thick Film"
PART_NUMBER"ERJ-2RKF4991X"
REUSE_ANNOTATE"TRUE"
SEC"1"
1
$PN"1"10
2
$PN"2"85
%"cap_np_0"
1,"(6150,-8700)","3","ocad_parts_lib","327P"
$LOCATION"C45"
VOLTAGE"25V"
VALUE"0.1UF"
CDS_LIB"ocad_parts_lib"
CDS_LOCATION"C45"
JEDEC_TYPE"cap0402"
DISTRIBUTOR"Digi-Key"
DISTRIBUTOR_PARTNUMBER"445-7348-2-ND"
MANUFACTURER"TDK CORP"
MPN"C1005X7R1E104K050BB "
PSPICE"C"
DESCRIPTION"CAP 0.1__F __10% 25V Ceramic Capacitor X7R 0402 "
PART_TYPE"Ceramic"
PART_NUMBER"445-7348-2-ND"
REUSE_ANNOTATE"TRUE"
CLASS"DISCRETE"
LAST_EDIT_BY"SNF"
ALT_SYMBOLS""
SEC"1"
AVAILABILITY"In Stock"
ROOM"TE0712"
SOURCE_PACKAGE"CAP_NP_0"
1
$PN"1"110
2
$PN"2"113
%"cap_np_0"
1,"(3650,-8750)","5","ocad_parts_lib","329P"
VOLTAGE"25V"
$LOCATION"C40"
VALUE"0.1UF"
CDS_LIB"ocad_parts_lib"
CDS_LOCATION"C40"
JEDEC_TYPE"cap0402"
SOURCE_PACKAGE"CAP_NP_0"
REUSE_ANNOTATE"TRUE"
PART_NUMBER"445-7348-2-ND"
ROOM"TE0712"
CLASS"DISCRETE"
LAST_EDIT_BY"SNF"
ALT_SYMBOLS""
SEC"1"
1
$PN"1"178
2
$PN"2"169
%"te0712 connector-jb3"
1,"(4925,-8000)","0","ocad_parts_lib","333P"
$LOCATION"J5"
VALUE"LSHM-130-03.0-L-DV-A-S-K-TR"
SEC"1"
DISTRIBUTOR"Digikey"
DISTRIBUTOR_PARTNUMBER"SAM14110TR-ND"
MANUFACTURER"Samtec"
MPN"LSHM-130-03.0-L-DV-A-S-K-TR"
HOUSINGGENDER"Female"
CONTACTGENDER"Male"
CONTACTVOLTAGE"-"
CONTACTCURRENT"-"
DESCRIPTION"CONN SELF-MATE 60POS SMD GOLD"
PART_TYPE"Header"
PART_NUMBER"LSHM-130-03.0-L-DV-A-S-K-TR"
SOURCE_PACKAGE"TE0712 Connector-JB3"
JEDEC_TYPE"samtec_lshm-130-04-0-l-dv-a-s"
CDS_LOCATION"J5"
CDS_LIB"ocad_parts_lib"
GND1
$PN"5"166
GND2
$PN"12"193
GND0
$PN"6"129
NC1
$PN"56"0
GND3
$PN"11"145
GND4
$PN"18"151
GND5
$PN"17"147
GND6
$PN"24"130
GND7
$PN"23"148
GND8
$PN"30"131
GND9
$PN"29"149
GND10
$PN"36"165
GND11
$PN"35"144
GND12
$PN"46"167
F2
$PN"62"168
F1
$PN"61"192
13_L_14_P
$PN"1"0
B13_L_17__P
$PN"2"0
13_L_14_N
$PN"3"0
B13_L_17__N
$PN"4"0
MGT_RX0_N
$PN"7"106
MGT_TX0_N
$PN"8"121
MGT_RX0_P
$PN"9"105
MGT_TX0_P
$PN"10"107
MGT_RX1_N
$PN"13"146
MGT_TX1_N
$PN"14"108
MGT_RX1_P
$PN"15"152
MGT_TX1_P
$PN"16"109
MGT_RX2_N
$PN"19"0
MGT_TX2_N
$PN"20"0
MGT_RX2_P
$PN"21"0
MGT_TX2_P
$PN"22"0
MGT_RX3_N
$PN"25"0
MGT_TX3_N
$PN"26"0
MGT_RX3_P
$PN"27"0
MGT_TX3_P
$PN"28"0
CLKIN2_N
$PN"31"0
MGT_CLK1_N
$PN"32"0
CLKIN2_P
$PN"33"0
MGT_CLK1_P
$PN"34"0
B13_L_16_P
$PN"37"0
B13_L_10__P
$PN"38"0
B13_L_16_N
$PN"39"0
B13_L_10_N
$PN"40"0
B13_L_1_P
$PN"41"0
B13_L_15__P
$PN"42"0
B13_L_1_N
$PN"43"0
B13_L_15_N
$PN"44"0
GND13
$PN"45"150
B13_L_4_P
$PN"47"0
B14_L_5__P
$PN"48"103
B13_L_4_N
$PN"49"0
B14_L_5__N
$PN"50"0
B13_L_2_N
$PN"51"0
B14_L_20__P
$PN"52"104
B13_L_2_P
$PN"53"0
B14_L_20_N
$PN"54"0
NC2
$PN"55"0
B13_L_12_P
$PN"57"179
B13_L_13__P
$PN"58"110
B13_L_12_N
$PN"59"178
B13_L_13__N
$PN"60"111
%"cap_np_0"
1,"(6150,-8750)","1","ocad_parts_lib","339P"
$LOCATION"C43"
VOLTAGE"25V"
VALUE"0.1UF"
CDS_LIB"ocad_parts_lib"
CDS_LOCATION"C43"
JEDEC_TYPE"cap0402"
SOURCE_PACKAGE"CAP_NP_0"
DESCRIPTION"CAP 0.1__F __10% 25V Ceramic Capacitor X7R 0402 "
PSPICE"C"
MPN"C1005X7R1E104K050BB "
MANUFACTURER"TDK CORP"
DISTRIBUTOR_PARTNUMBER"445-7348-2-ND"
DISTRIBUTOR"Digi-Key"
AVAILABILITY"In Stock"
ROOM"TE0712"
CLASS"DISCRETE"
LAST_EDIT_BY"SNF"
ALT_SYMBOLS""
SEC"1"
PART_TYPE"Ceramic"
PART_NUMBER"445-7348-2-ND"
REUSE_ANNOTATE"TRUE"
1
$PN"1"111
2
$PN"2"112
%"r"
1,"(6175,-6575)","0","discrete","340P"
$LOCATION"R136"
VALUE"10K"
MANUFACTURER"Vishay Dale"
CDS_LIB"discrete"
CDS_LOCATION"R136"
JEDEC_TYPE"res0402"
SOURCE_PACKAGE"R"
DATASHEET"C:\EMA\CISQuickStart\Technical_Datasheets\Vishay\dcrcwe3.pdf"
DISTRIBUTOR"Digikey"
DISTRIBUTOR_PARTNUMBER"1135-1061-1-ND"
SEC"1"
PART_NUMBER"M55342K11B10E0RS3"
1
$PN"1"51
2
$PN"2"12
%"r"
1,"(6900,-4275)","0","discrete","342P"
$LOCATION"R106"
VALUE"10K"
CDS_LIB"discrete"
CDS_LOCATION"R106"
JEDEC_TYPE"res0402"
SOURCE_PACKAGE"R"
DATASHEET"C:\EMA\CISQuickStart\Technical_Datasheets\Vishay\dcrcwe3.pdf"
DISTRIBUTOR"Digikey"
DISTRIBUTOR_PARTNUMBER"1135-1061-1-ND"
MANUFACTURER"Vishay Dale"
MPN"M55342K11B10E0RS3"
TOLERANCE"1%"
POWER"1/10W"
SEC"1"
PART_NUMBER"M55342K11B10E0RS3"
1
$PN"1"4
2
$PN"2"153
%"te0712 connector-jb1"
1,"(4925,-5350)","0","ocad_parts_lib","350P"
VALUE"LSHM-150-03.0-L-DV-A-S-K-TR"
$LOCATION"J1"
SEC"1"
DISTRIBUTOR"Digikey"
DISTRIBUTOR_PARTNUMBER"SAM14151TR-ND"
MANUFACTURER"Samtec"
MPN"LSHM-150-03.0-L-DV-A-S-K-TR"
HOUSINGGENDER"Female"
CONTACTGENDER"Male"
CONTACTVOLTAGE"-"
CONTACTCURRENT"-"
DESCRIPTION"CONN SELF-MATE 100POS SMD GOLD"
PART_TYPE"Header"
PART_NUMBER"LSHM-150-03.0-L-DV-A-S-K-TR"
SOURCE_PACKAGE"TE0712 Connector-JB1"
JEDEC_TYPE"samtec_lshm-150-04-0-l-dv-a-s"
CDS_LOCATION"J1"
CDS_LIB"ocad_parts_lib"
GND1
$PN"7"102
GND2
$PN"19"101
GND0
$PN"1"100
GND3
$PN"25"99
GND4
$PN"30"98
GND5
$PN"33"74
GND6
$PN"43"71
GND7
$PN"53"68
GND8
$PN"54"33
GND9
$PN"63"97
GND10
$PN"64"59
GND11
$PN"73"96
GND12
$PN"74"95
F2
$PN"101"94
F1
$PN"102"93
GND13
$PN"83"92
VIN1
$PN"2"91
ETH_TD_P
$PN"3"0
VIN2
$PN"4"91
ETH_TD_N
$PN"5"0
VIN3
$PN"6"91
NOSSEQ
$PN"8"0
ETH_RD_P
$PN"9"0
VCCIO16_0
$PN"10"7
ETH_RD_N
$PN"11"0
VCCIO16_1
$PN"12"7
VCC3V3_0
$PN"13"90
3V3VIN0
$PN"14"5
B13_L_6_N
$PN"15"22
3V3VIN1
$PN"16"5
B13_L_6__P
$PN"17"23
B13_L_3__P
$PN"18"65
B13_L_3_N
$PN"20"89
B13_L_5_N
$PN"21"88
B13_L_11_N
$PN"22"75
B13_L_5__P
$PN"23"87
B13_L_11__P
$PN"24"76
B13_L_9_N
$PN"26"86
EN1
$PN"27"0
B13_L_9__P
$PN"28"64
PGOOD
$PN"29"85
MODE
$PN"31"0
B16_L_22__P
$PN"32"63
B16_L_22_N
$PN"34"62
B16_L_16_P
$PN"35"84
B16_L_24_N
$PN"36"61
B16_L_16_N
$PN"37"73
B16_L_24__P
$PN"38"37
B16_L_19_N
$PN"39"72
VCC1V8
$PN"40"38
B16_L_19_P
$PN"41"66
B16_L_23__P
$PN"42"39
B16_L_23_N
$PN"44"57
B16_L_17_N
$PN"45"0
B16_L_15__P
$PN"46"0
B16_L_17_P
$PN"47"0
B16_L_15_N
$PN"48"0
B16_L_18_N
$PN"49"70
B16_L20_P
$PN"50"31
B16_L_18_P
$PN"51"69
B16_L20_N
$PN"52"32
B16_L_9_N
$PN"55"83
B16_L_21__P
$PN"56"0
B16_L_9__P
$PN"57"67
B16_L_21_N
$PN"58"0
B16_L_7_N
$PN"59"0
B16_L_13__P
$PN"60"34
B16_L_7__P
$PN"61"0
B16_L_13_N
$PN"62"35
B16_L_11__P
$PN"65"0
B16_L_14__P
$PN"66"15
B16_L_11_N
$PN"67"0
B16_L_14_N
$PN"68"14
B16_L_10_N
$PN"69"0
B16_L_3_N
$PN"70"13
B16_L_10__P
$PN"71"0
B16_L_3__P
$PN"72"60
B16_L_5_N
$PN"75"0
B16_L_12__P
$PN"76"36
B16_L_5__P
$PN"77"0
B16_L_12_N
$PN"78"56
B16_L_2_N
$PN"79"0
VBAT_IN
$PN"80"0
B16_L_2__P
$PN"81"0
B16_L_8_N
$PN"82"82
B16_L_8__P
$PN"84"49
B16_L_6_N
$PN"85"81
B14_L_18__N
$PN"86"48
B16_L_6__P
$PN"87"80
B14_L_18__P
$PN"88"50
GND14
$PN"89"79
JTAGEN
$PN"90"51
B14_L_24__P
$PN"91"0
B14_L_9__P
$PN"92"52
B16_L_4_N
$PN"93"78
B14_L_9_N
$PN"94"53
B16_L_4__P
$PN"95"77
B14_L_4__P
$PN"96"54
B16_L_1_N
$PN"97"0
B14_L_4_N
$PN"98"55
B16_L_1__P
$PN"99"0
B14_L_24_N
$PN"100"47
%"vcc_bar"
1,"(9350,-6250)","0","mtca_interface_board","354P"
HDL_POWER"VREF_JTAG"
CDS_LIB"mtca_interface_board"
HOTSPOT_011
%"vcc_bar"
1,"(3650,-4250)","0","mtca_interface_board","7P"
HDL_POWER"VCC3V3"
CDS_LIB"mtca_interface_board"
HOTSPOT_010
%"vcc_bar"
1,"(9750,-4150)","0","mtca_interface_board","I395"
HDL_POWER"VCC3V3"
CDS_LIB"mtca_interface_board"
HOTSPOT_09
%"r"
1,"(9700,-4400)","0","discrete","I396"
VALUE"2.2k"
$LOCATION"R122"
CDS_LIB"discrete"
CDS_LOCATION"R122"
JEDEC_TYPE"res0402"
SOURCE_PACKAGE"R"
REUSE_ANNOTATE"TRUE"
ROOM"SFP I2C SWITCH"
AVAILABILITY"6,080,000"
DISTRIBUTOR"Digikey"
DISTRIBUTOR_PARTNUMBER"P2.20KLTR-ND"
MANUFACTURER"Panasonic"
MPN"ERJ-2RKF2201X"
TOLERANCE"1%"
POWER"1/10 W"
DESCRIPTION"RES SMD 2.2K OHM 1% 1/10W 0402"
PART_TYPE"Thick Film"
PART_NUMBER"ERJ-2RKF2201X"
SEC"1"
1
$PN"1"9
2
$PN"2"118
%"r"
1,"(6600,-5950)","0","discrete","I397"
$LOCATION"R120"
VALUE"2.2k"
SEC"1"
REUSE_ANNOTATE"TRUE"
ROOM"SFP I2C SWITCH"
AVAILABILITY"6,080,000"
DISTRIBUTOR"Digikey"
DISTRIBUTOR_PARTNUMBER"P2.20KLTR-ND"
MANUFACTURER"Panasonic"
MPN"ERJ-2RKF2201X"
TOLERANCE"1%"
POWER"1/10 W"
DESCRIPTION"RES SMD 2.2K OHM 1% 1/10W 0402"
PART_TYPE"Thick Film"
PART_NUMBER"ERJ-2RKF2201X"
SOURCE_PACKAGE"R"
JEDEC_TYPE"res0402"
CDS_LOCATION"R120"
CDS_LIB"discrete"
1
$PN"1"8
2
$PN"2"48
%"r"
1,"(9800,-4400)","0","discrete","I398"
$LOCATION"R121"
VALUE"2.2k"
CDS_LIB"discrete"
CDS_LOCATION"R121"
JEDEC_TYPE"res0402"
SOURCE_PACKAGE"R"
REUSE_ANNOTATE"TRUE"
PART_NUMBER"ERJ-2RKF2201X"
PART_TYPE"Thick Film"
DESCRIPTION"RES SMD 2.2K OHM 1% 1/10W 0402"
POWER"1/10 W"
TOLERANCE"1%"
MPN"ERJ-2RKF2201X"
MANUFACTURER"Panasonic"
DISTRIBUTOR_PARTNUMBER"P2.20KLTR-ND"
DISTRIBUTOR"Digikey"
AVAILABILITY"6,080,000"
ROOM"SFP I2C SWITCH"
SEC"1"
1
$PN"1"9
2
$PN"2"119
%"r"
1,"(6700,-5950)","0","discrete","I399"
$LOCATION"R119"
VALUE"2.2k"
SEC"1"
REUSE_ANNOTATE"TRUE"
PART_NUMBER"ERJ-2RKF2201X"
PART_TYPE"Thick Film"
DESCRIPTION"RES SMD 2.2K OHM 1% 1/10W 0402"
POWER"1/10 W"
TOLERANCE"1%"
MPN"ERJ-2RKF2201X"
MANUFACTURER"Panasonic"
DISTRIBUTOR_PARTNUMBER"P2.20KLTR-ND"
DISTRIBUTOR"Digikey"
AVAILABILITY"6,080,000"
ROOM"SFP I2C SWITCH"
SOURCE_PACKAGE"R"
JEDEC_TYPE"res0402"
CDS_LOCATION"R119"
CDS_LIB"discrete"
1
$PN"1"8
2
$PN"2"50
%"r"
1,"(9600,-4400)","0","discrete","I400"
$LOCATION"R127"
VALUE"2.2k"
CDS_LIB"discrete"
CDS_LOCATION"R127"
JEDEC_TYPE"res0402"
SOURCE_PACKAGE"R"
REUSE_ANNOTATE"TRUE"
PART_NUMBER"ERJ-2RKF2201X"
PART_TYPE"Thick Film"
DESCRIPTION"RES SMD 2.2K OHM 1% 1/10W 0402"
POWER"1/10 W"
TOLERANCE"1%"
MPN"ERJ-2RKF2201X"
MANUFACTURER"Panasonic"
DISTRIBUTOR_PARTNUMBER"P2.20KLTR-ND"
DISTRIBUTOR"Digikey"
AVAILABILITY"6,080,000"
ROOM"SFP I2C SWITCH"
SEC"1"
1
$PN"1"9
2
$PN"2"117
%"r"
1,"(9400,-4400)","0","discrete","I401"
$LOCATION"R125"
VALUE"2.2k"
CDS_LIB"discrete"
CDS_LOCATION"R125"
JEDEC_TYPE"res0402"
SOURCE_PACKAGE"R"
REUSE_ANNOTATE"TRUE"
PART_NUMBER"ERJ-2RKF2201X"
PART_TYPE"Thick Film"
DESCRIPTION"RES SMD 2.2K OHM 1% 1/10W 0402"
POWER"1/10 W"
TOLERANCE"1%"
MPN"ERJ-2RKF2201X"
MANUFACTURER"Panasonic"
DISTRIBUTOR_PARTNUMBER"P2.20KLTR-ND"
DISTRIBUTOR"Digikey"
AVAILABILITY"6,080,000"
ROOM"SFP I2C SWITCH"
SEC"1"
1
$PN"1"9
2
$PN"2"115
%"r"
1,"(9500,-4400)","0","discrete","I402"
$LOCATION"R126"
VALUE"2.2k"
CDS_LIB"discrete"
CDS_LOCATION"R126"
JEDEC_TYPE"res0402"
SOURCE_PACKAGE"R"
REUSE_ANNOTATE"TRUE"
ROOM"SFP I2C SWITCH"
AVAILABILITY"6,080,000"
DISTRIBUTOR"Digikey"
DISTRIBUTOR_PARTNUMBER"P2.20KLTR-ND"
MANUFACTURER"Panasonic"
MPN"ERJ-2RKF2201X"
TOLERANCE"1%"
POWER"1/10 W"
DESCRIPTION"RES SMD 2.2K OHM 1% 1/10W 0402"
PART_TYPE"Thick Film"
PART_NUMBER"ERJ-2RKF2201X"
SEC"1"
1
$PN"1"9
2
$PN"2"116
%"r"
1,"(9300,-4400)","0","discrete","I403"
$LOCATION"R124"
VALUE"2.2k"
CDS_LIB"discrete"
CDS_LOCATION"R124"
JEDEC_TYPE"res0402"
SOURCE_PACKAGE"R"
REUSE_ANNOTATE"TRUE"
ROOM"SFP I2C SWITCH"
AVAILABILITY"6,080,000"
DISTRIBUTOR"Digikey"
DISTRIBUTOR_PARTNUMBER"P2.20KLTR-ND"
MANUFACTURER"Panasonic"
MPN"ERJ-2RKF2201X"
TOLERANCE"1%"
POWER"1/10 W"
DESCRIPTION"RES SMD 2.2K OHM 1% 1/10W 0402"
PART_TYPE"Thick Film"
PART_NUMBER"ERJ-2RKF2201X"
SEC"1"
1
$PN"1"9
2
$PN"2"114
%"vcc_bar"
1,"(6650,-5700)","0","mtca_interface_board","I404"
HDL_POWER"VCC3V3"
CDS_LIB"mtca_interface_board"
HOTSPOT_08
%"cap_np_0"
1,"(6150,-4650)","3","ocad_parts_lib","I405"
VOLTAGE"25V"
VALUE"0.1UF"
PART_TYPE"Ceramic"
PART_NUMBER"445-7348-2-ND"
REUSE_ANNOTATE"TRUE"
CLASS"DISCRETE"
DISTRIBUTOR_PARTNUMBER"445-7348-2-ND"
MANUFACTURER"TDK CORP"
DESCRIPTION"CAP 0.1__F __10% 25V Ceramic Capacitor X7R 0402 "
PSPICE"C"
MPN"C1005X7R1E104K050BB "
DISTRIBUTOR"Digi-Key"
SOURCE_PACKAGE"CAP_NP_0"
ROOM"TE0712"
AVAILABILITY"In Stock"
SEC"1"
ALT_SYMBOLS""
LAST_EDIT_BY"SNF"
JEDEC_TYPE"cap0402"
CDS_LIB"ocad_parts_lib"
1
$PN"1"75
2
$PN"2"156
%"cap_np_0"
1,"(6150,-4700)","1","ocad_parts_lib","I406"
VOLTAGE"25V"
VALUE"0.1UF"
AVAILABILITY"In Stock"
ROOM"TE0712"
CLASS"DISCRETE"
LAST_EDIT_BY"SNF"
MPN"C1005X7R1E104K050BB "
MANUFACTURER"TDK CORP"
DISTRIBUTOR_PARTNUMBER"445-7348-2-ND"
DISTRIBUTOR"Digi-Key"
PSPICE"C"
DESCRIPTION"CAP 0.1__F __10% 25V Ceramic Capacitor X7R 0402 "
REUSE_ANNOTATE"TRUE"
PART_NUMBER"445-7348-2-ND"
PART_TYPE"Ceramic"
SEC"1"
ALT_SYMBOLS""
SOURCE_PACKAGE"CAP_NP_0"
JEDEC_TYPE"cap0402"
CDS_LIB"ocad_parts_lib"
1
$PN"1"76
2
$PN"2"143
%"P2V5"
1,"(5700,-4300)","0","cnpower","I407"
BODY_TYPE"PLUMBING"
HDL_POWER"P2V5"
SIZE"1B"
CDS_LIB"cnpower"
A<SIZE-1..0>\NAC
VHDL_INIT"1"7
%"P2V5"
1,"(9025,-4050)","0","cnpower","I408"
BODY_TYPE"PLUMBING"
HDL_POWER"P2V5"
SIZE"1B"
CDS_LIB"cnpower"
A<SIZE-1..0>\NAC
VHDL_INIT"1"6
%"vcc_bar"
1,"(6625,-3925)","0","mtca_interface_board","I409"
HDL_POWER"VCC3V3"
CDS_LIB"mtca_interface_board"
HOTSPOT_05
%"vcc_bar"
1,"(7375,-4000)","0","mtca_interface_board","I410"
HDL_POWER"VCC3V3"
CDS_LIB"mtca_interface_board"
HOTSPOT_04
%"TP"
1,"(4100,-4450)","2","cnpassive","I411"
VALUE"1.0MM"
SIZE"1B"
CDS_LIB"cnpassive"
PART_NAME"TP"
PACK_TYPE"HOLE"
A <SIZE-1..0>\NAC
$PN"#"90
%"TP"
1,"(5950,-5100)","0","cnpassive","I412"
VALUE"1.0MM"
SIZE"1B"
CDS_LIB"cnpassive"
PART_NAME"TP"
PACK_TYPE"HOLE"
A <SIZE-1..0>\NAC
$PN"#"38
%"TP"
1,"(9175,-4550)","0","cnpassive","I413"
VALUE"1.0MM"
SIZE"1B"
CDS_LIB"cnpassive"
PART_NAME"TP"
PACK_TYPE"HOLE"
A <SIZE-1..0>\NAC
$PN"#"177
%"CON4P"
1,"(6275,-8500)","2","cnconnector","I414"
TYPE"53398-0471"
CDS_LIB"cnconnector"
A<3>\NAC103
A<1>\NAC104
A<2>\NAC1
A<0>\NAC3
%"gnd"
1,"(5875,-8600)","0","mtca_interface_board","I415"
HDL_POWER"GND"
CDS_LIB"mtca_interface_board"
HOTSPOT_03
%"FERRITE"
1,"(6225,-4025)","0","cndiscrete","I416"
VALUE"MPZ1608S101A"
CDS_LIB"cndiscrete"
PACK_TYPE"SMD"
MODEL"TDK"
B <SIZE-1..0>\NAC5
A <SIZE-1..0>\NAC91
%"CAPCERSMDCL2"
1,"(6500,-4175)","1","cnpassive","I417"
VALUE"1UF"
VOLTAGE"16V"
PACK_TYPE"0603"
CDS_LIB"cnpassive"
SIZE"1"
A <SIZE-1..0>\NAC
$PN"#"2
B <SIZE-1..0>\NAC
$PN"#"5
%"CAPCERSMDCL2"
1,"(5950,-4175)","1","cnpassive","I418"
VOLTAGE"16V"
VALUE"1UF"
PACK_TYPE"0603"
CDS_LIB"cnpassive"
SIZE"1"
A <SIZE-1..0>\NAC
$PN"#"2
B <SIZE-1..0>\NAC
$PN"#"91
%"gnd"
1,"(6175,-4350)","0","mtca_interface_board","I419"
HDL_POWER"GND"
CDS_LIB"mtca_interface_board"
HOTSPOT_02
%"PCOAX"
1,"(6325,-7150)","0","cnconnector","I421"
TYPE"U.FL-R-SMT-1(10)"
CDS_LIB"cnconnector"
NEEDS_NO_SIZE"TRUE"
A\NAC105
%"PCOAX"
1,"(6325,-7300)","0","cnconnector","I422"
TYPE"U.FL-R-SMT-1(10)"
NEEDS_NO_SIZE"TRUE"
CDS_LIB"cnconnector"
A\NAC106
%"PCOAX"
1,"(6325,-7425)","0","cnconnector","I423"
TYPE"U.FL-R-SMT-1(10)"
CDS_LIB"cnconnector"
NEEDS_NO_SIZE"TRUE"
A\NAC121
%"PCOAX"
1,"(6325,-7550)","0","cnconnector","I424"
TYPE"U.FL-R-SMT-1(10)"
NEEDS_NO_SIZE"TRUE"
CDS_LIB"cnconnector"
A\NAC107
%"vcc_bar"
1,"(6000,-8250)","0","mtca_interface_board","I425"
HDL_POWER"VCC3V3"
CDS_LIB"mtca_interface_board"
HOTSPOT_01
%"IOPORT"
1,"(6000,-5750)","0","standard","I426"
OFFPAGE"TRUE"
CDS_LIB"standard"
A
VHDL_PORT"INOUT"
HDL_PORT"INOUT"15
%"IOPORT"
1,"(6000,-5800)","0","standard","I427"
OFFPAGE"TRUE"
CDS_LIB"standard"
A
VHDL_PORT"INOUT"
HDL_PORT"INOUT"14
%"IOPORT"
1,"(6000,-5850)","0","standard","I428"
OFFPAGE"TRUE"
CDS_LIB"standard"
A
VHDL_PORT"INOUT"
HDL_PORT"INOUT"13
END.
