uob-hep-cad/uob-hep-pc072/hardware/Cadence/top/mtca_interface_board_reocc/02_#20power/sch_1/page3.csv

FILE_TYPE = CONNECTIVITY;
{Allegro Design Entry HDL 23.1 P001 (4147275) 9/30/2023}
"PAGE_NUMBER" = 2;
0"NC";
1"VCC3V3\G";
2"VCC3V3\G";
3"P2V5\g";
6"GND\G";
5"GND\G";
4"GND\G";
7"GND\G";
8"VP1V8\G"ORC_VOLTAGE"3.3 V"ORC_RATSNEST_SCHEDULE"POWER_AND_GROUND";
9"1V8_POST_RSHUNT";
10"SENSE_12C_SCL";
11"POWER<5..0>";
12"DCDC_ENABLE";
13"DCDC_3V3_PG";
14"DCDC_2V5_PG";
15"LDO_1V8_PG";
16"SENSE_12C_SDA";
17"LDO_1V8_PG";
18"POWER.PG_VP1V8";
20"POWER.SENSE_12C_SCL";
19"POWER.SENSE_12C_SCL";
22"DCDC_PG";
21"DCDC_PG";
24"POWER.SENSE_12C_SDA";
23"POWER.SENSE_12C_SDA";
25"POWER.PG_VCC3V3";
26"POWER.PG_VP3V3";
28"DCDC_ENABLE";
27"DCDC_ENABLE";
29"N00904";
30"N00902";
31"N003941";
32"FPGA_PG";
%"r"
"1","(5350,-4200)","1","discrete","138P";
;
$LOCATION"R68"
VALUE"1k"
SEC"1"
ROOM"VCC1V8"
DATASHEET"C:\EMA\CISQuickStart\Technical_Datasheets\Panasonic\AOA0000CE1.pdf"
DISTRIBUTOR"Digikey"
DISTRIBUTOR_PARTNUMBER"P1.00KLTR-ND"
MANUFACTURER"Panasonic"
MPN"ERJ-2RKF1001X"
TOLERANCE"1%"
POWER"1/16 W"
DESCRIPTION"RES SMD 1K OHM 1% 1/10W 0402"
PART_TYPE"Thick Film"
PART_NUMBER"ERJ-2RKF1001X"
SOURCE_PACKAGE"R"
JEDEC_TYPE"res0402"
CDS_LOCATION"R68"
CDS_LIB"discrete";
"1"
$PN"1"8;
"2"
$PN"2"29;
%"testpoint"
"1","(5000,-4925)","5","testpoint","140P";
;
$LOCATION"TP14"
SEC"1"
VALUE"5002 White"
ROOM"VCC1V8"
DATASHEET"C:\EMA\CISQuickStart\Technical_Datasheets\Keystone Electronics\M55p51.pdf"
MANUFACTURER"Keystone Electronics"
MPN"5002"
DESCRIPTION"MISC, Testpoint, 5002 White, TH, 2.5x2.5x4.6 mm"
PART_TYPE"Testpoint"
PART_NUMBER"EMA-00001481V22"
SOURCE_PACKAGE"TESTPOINT"
JEDEC_TYPE"TP_KEYSTONE_5000A"
CDS_LOCATION"TP14"
CDS_LIB"testpoint";
"TP"
$PN"1"6,5,4;
%"cap_np"
"1","(4125,-4650)","0","ocad_parts_lib","144P";
;
$LOCATION"C55"
VALUE"47UF"
VOLTAGE"6.3V"
CDS_LIB"ocad_parts_lib"
CDS_LOCATION"C55"
JEDEC_TYPE"cap0805"
SOURCE_PACKAGE"CAP_NP"
AVAILABILITY"In Stock"
DISTRIBUTOR"Digi-Key"
DISTRIBUTOR_PARTNUMBER"490-14660-2-ND"
MANUFACTURER"Murata"
MPN"GRM21BR60J476ME15K"
PSPICE"C"
TOLERANCE"20%"
DESCRIPTION"CAP CER 47UF 6.3V X5R 0805"
PART_TYPE"Ceramic"
PART_NUMBER"GRM21BR60J476ME15K"
ROOM"VCC1V8"
ALT_SYMBOLS""
LAST_EDIT_BY"SNF"
CLASS"DISCRETE"
SEC"1";
"1"
$PN"1"8;
"2"
$PN"2"6,5,4;
%"r"
"1","(2850,-4125)","0","discrete","145P";
;
$LOCATION"R59"
VALUE"4.99k"
CDS_LIB"discrete"
CDS_LOCATION"R59"
JEDEC_TYPE"res0402"
SOURCE_PACKAGE"R"
REUSE_ID"146"
ROOM"VCC1V8"
AVAILABILITY"In Stock"
DISTRIBUTOR"Digikey"
DISTRIBUTOR_PARTNUMBER"P4.99KLTR-ND"
MANUFACTURER"Panasonic"
MPN"ERJ-2RKF4991X"
TOLERANCE"1%"
POWER"1/10 W"
DESCRIPTION"RES SMD 4.99K OHM 1% 1/10W 0402"
PART_TYPE"Thick Film"
PART_NUMBER"ERJ-2RKF4991X"
REUSE_ANNOTATE"TRUE"
SEC"1";
"1"
$PN"1"1;
"2"
$PN"2"17;
%"cap_np"
"1","(1575,-4650)","0","ocad_parts_lib","149P";
;
$LOCATION"C64"
VALUE"0.1UF"
VOLTAGE"25V"
SEC"1"
CLASS"DISCRETE"
LAST_EDIT_BY"SNF"
ALT_SYMBOLS""
REUSE_ANNOTATE"TRUE"
ROOM"VCC1V8"
PART_NUMBER"445-7348-2-ND"
PART_TYPE"Ceramic"
DESCRIPTION"CAP 0.1__F __10% 25V Ceramic Capacitor X7R 0402 "
PSPICE"C"
MPN"C1005X7R1E104K050BB "
MANUFACTURER"TDK CORP"
DISTRIBUTOR_PARTNUMBER"445-7348-2-ND"
DISTRIBUTOR"Digi-Key"
AVAILABILITY"In Stock"
REUSE_ID"148"
SOURCE_PACKAGE"CAP_NP"
JEDEC_TYPE"cap0402"
CDS_LOCATION"C64"
CDS_LIB"ocad_parts_lib";
"1"
$PN"1"3;
"2"
$PN"2"6,5,4;
%"tps74618p"
"1","(2850,-4525)","0","ocad_parts_lib","159P";
;
VALUE"TPS74618PQWDRVRQ1"
$LOCATION"U16"
CDS_LIB"ocad_parts_lib"
CDS_LOCATION"U16"
JEDEC_TYPE"6-WSON_2x2"
SOURCE_PACKAGE"TPS74618P"
DATASHEET"\\Mac\Home\Desktop\SPB_Data\CIS_HEP_Partslib\DataSheets\ltc60812fd.pdf"
AVAILABILITY"In Stock"
DISTRIBUTOR"Digi-Key"
DISTRIBUTOR_PARTNUMBER"296-TPS74618PQWDRVRQ1CT-ND"
MANUFACTURER"Texas Instruments"
MPN"TPS74618PQWDRVRQ1"
PSPICE"IC"
DESCRIPTION"GAINESVILLE AUTO TPS74618PQWDRVR"
PART_TYPE"Voltage Regulator"
PART_NUMBER"TPS74618PQWDRVRQ1"
ROOM"VCC1V8"
SEC"1";
"GND"
$PN"3"6,5,4;
"OUT"
$PN"1"8;
"EN"
$PN"4"9;
"PG"
$PN"5"17;
"IN"
$PN"6"9;
"EPAD"
$PN"7"6,5,4;
%"r"
"1","(5975,-4350)","0","discrete","168P";
;
VALUE"10K"
$LOCATION"R72"
SEC"1"
REUSE_ANNOTATE"TRUE"
DATASHEET"C:\EMA\CISQuickStart\Technical_Datasheets\Vishay\dcrcwe3.pdf"
DISTRIBUTOR"Digikey"
DISTRIBUTOR_PARTNUMBER"1135-1061-1-ND"
MANUFACTURER"Vishay Dale"
MPN"M55342K11B10E0RS3"
TOLERANCE"1%"
POWER"1/10W"
DESCRIPTION"RES SMD 10K OHM 1% 1/20W 0402"
PART_TYPE"Thick Film"
PART_NUMBER"M55342K11B10E0RS3"
ROOM"VCC1V8"
SOURCE_PACKAGE"R"
JEDEC_TYPE"res0402"
CDS_LOCATION"R72"
CDS_LIB"discrete";
"1"
$PN"1"29;
"2"
$PN"2"7;
%"testpoint"
"1","(5000,-4475)","5","testpoint","174P";
;
$LOCATION"TP9"
SEC"1"
VALUE"5002 White"
ROOM"VCC1V8"
DATASHEET"C:\EMA\CISQuickStart\Technical_Datasheets\Keystone Electronics\M55p51.pdf"
MANUFACTURER"Keystone Electronics"
MPN"5002"
DESCRIPTION"MISC, Testpoint, 5002 White, TH, 2.5x2.5x4.6 mm"
PART_TYPE"Testpoint"
PART_NUMBER"EMA-00001481V22"
SOURCE_PACKAGE"TESTPOINT"
JEDEC_TYPE"TP_KEYSTONE_5000A"
CDS_LOCATION"TP9"
CDS_LIB"testpoint";
"TP"
$PN"1"8;
%"cap_np"
"1","(3900,-4650)","0","ocad_parts_lib","180P";
;
VALUE"47UF"
VOLTAGE"6.3V"
$LOCATION"C54"
SEC"1"
CLASS"DISCRETE"
LAST_EDIT_BY"SNF"
ALT_SYMBOLS""
ROOM"VCC1V8"
PART_NUMBER"GRM21BR60J476ME15K"
PART_TYPE"Ceramic"
DESCRIPTION"CAP CER 47UF 6.3V X5R 0805"
TOLERANCE"20%"
PSPICE"C"
MPN"GRM21BR60J476ME15K"
MANUFACTURER"Murata"
DISTRIBUTOR_PARTNUMBER"490-14660-2-ND"
DISTRIBUTOR"Digi-Key"
AVAILABILITY"In Stock"
SOURCE_PACKAGE"CAP_NP"
JEDEC_TYPE"cap0805"
CDS_LIB"ocad_parts_lib"
CDS_LOCATION"C54";
"1"
$PN"1"8;
"2"
$PN"2"6,5,4;
%"r"
"1","(6400,-3475)","0","discrete","190P";
;
VALUE"4.99k"
$LOCATION"R67"
CDS_LIB"discrete"
CDS_LOCATION"R67"
JEDEC_TYPE"res0402"
SOURCE_PACKAGE"R"
REUSE_ANNOTATE"TRUE"
PART_NUMBER"ERJ-2RKF4991X"
PART_TYPE"Thick Film"
DESCRIPTION"RES SMD 4.99K OHM 1% 1/10W 0402"
POWER"1/10 W"
TOLERANCE"1%"
MPN"ERJ-2RKF4991X"
MANUFACTURER"Panasonic"
DISTRIBUTOR_PARTNUMBER"P4.99KLTR-ND"
DISTRIBUTOR"Digikey"
AVAILABILITY"In Stock"
ROOM"VCC1V8"
SEC"1";
"1"
$PN"1"2;
"2"
$PN"2"31;
%"led green 0603_0"
"1","(6350,-3800)","3","ocad_parts_lib","191P";
;
$LOCATION"D5"
VALUE"Green"
SEC"1"
CY_PART_"860R-13779"
MFR_NAME"Lite-On Trading USA, Inc."
DEVICE"LED_GREEN0603"
MFR_PART_NUMBER"LTST-C190GKT"
DATASHEET"C:\EMA\CISQuickStart\Technical_Datasheets\Panasonic\ATA7000CE271.pdf"
DISTRIBUTOR"Digikey"
DISTRIBUTOR_PARTNUMBER"P13485CT-ND"
MANUFACTURER"Panasonic"
MPN"LNJ326W83RA"
LEDCOLOR"Green"
RATING"30 mW"
PART_TYPE"LED\Green"
PART_NUMBER"LNJ326W83RA"
ROOM"MMC"
REUSE_ANNOTATE"TRUE"
DESCRIPTION"LED GREEN 0603 SMD"
SOURCE_PACKAGE"LED GREEN 0603_0"
JEDEC_TYPE"LEDC1608X80N"
CDS_LOCATION"D5"
CDS_LIB"ocad_parts_lib";
"A"
$PN"2"31;
"K"
$PN"1"30;
%"cap_np"
"1","(3325,-4650)","0","ocad_parts_lib","194P";
;
$LOCATION"C57"
VALUE"0.1UF"
VOLTAGE"25V"
CDS_LIB"ocad_parts_lib"
CDS_LOCATION"C57"
JEDEC_TYPE"cap0402"
SOURCE_PACKAGE"CAP_NP"
REUSE_ID"54"
ROOM"VCC1V8"
PART_NUMBER"445-7348-2-ND"
PART_TYPE"Ceramic"
DESCRIPTION"CAP 0.1__F __10% 25V Ceramic Capacitor X7R 0402 "
PSPICE"C"
MPN"C1005X7R1E104K050BB "
MANUFACTURER"TDK CORP"
DISTRIBUTOR_PARTNUMBER"445-7348-2-ND"
DISTRIBUTOR"Digi-Key"
AVAILABILITY"In Stock"
REUSE_ANNOTATE"TRUE"
ALT_SYMBOLS""
LAST_EDIT_BY"SNF"
CLASS"DISCRETE"
SEC"1";
"1"
$PN"1"8;
"2"
$PN"2"6,5,4;
%"portleft-l"
"1","(2525,-7000)","2","mtca_interface_board","1P";
;
NAME"FPGA_PG"
CDS_LIB"mtca_interface_board";
"HOTSPOT_0"
PIN_NAME"FPGA_PG"
HDL_PORT"IN"32;
%"vcc_bar"
"1","(3725,-4350)","0","mtca_interface_board","203P";
;
HDL_POWER"VP1V8"
CDS_LIB"mtca_interface_board";
"HOTSPOT_0"8;
%"gnd"
"1","(2800,-5025)","0","mtca_interface_board","213P";
;
HDL_POWER"GND"
CDS_LIB"mtca_interface_board";
"HOTSPOT_0"6,5,4;
%"gnd"
"1","(6350,-4675)","0","mtca_interface_board","226P";
;
HDL_POWER"GND"
CDS_LIB"mtca_interface_board";
"HOTSPOT_0"7;
%"vcc_bar"
"1","(2800,-3950)","0","mtca_interface_board","8P";
;
HDL_POWER"VCC3V3"
CDS_LIB"mtca_interface_board";
"HOTSPOT_0"1;
%"vcc_bar"
"1","(6350,-3275)","0","mtca_interface_board","9P";
;
HDL_POWER"VCC3V3"
CDS_LIB"mtca_interface_board";
"HOTSPOT_0"2;
%"P2V5"
"1","(1750,-3950)","0","cnpower","I397";
;
HDL_POWER"P2V5"
BODY_TYPE"PLUMBING"
CDS_LIB"cnpower"
SIZE"1B";
"A<SIZE-1..0>\NAC"
VHDL_INIT"1"3;
%"TRANS MOSFET"
"1","(6350,-4150)","0","cndiscrete","I398";
;
TYPE"SOT523"
VALUE"PJE8408"
$LOCATION"T?"
PACK_TYPE"GSD"
CDS_LIB"cndiscrete"
CDS_LOCATION"POWER1";
"D\NAC"30;
"S\NAC"7;
"G\NAC"29;
%"cap_np"
"1","(1375,-4650)","0","ocad_parts_lib","I399";
;
VOLTAGE"6.3V"
VALUE"47UF"
$LOCATION"C54"
SEC"1"
CLASS"DISCRETE"
LAST_EDIT_BY"SNF"
ALT_SYMBOLS""
ROOM"VCC1V8"
PART_NUMBER"GRM21BR60J476ME15K"
PART_TYPE"Ceramic"
DESCRIPTION"CAP CER 47UF 6.3V X5R 0805"
TOLERANCE"20%"
PSPICE"C"
MPN"GRM21BR60J476ME15K"
MANUFACTURER"Murata"
DISTRIBUTOR_PARTNUMBER"490-14660-2-ND"
DISTRIBUTOR"Digi-Key"
AVAILABILITY"In Stock"
SOURCE_PACKAGE"CAP_NP"
JEDEC_TYPE"cap0805"
CDS_LIB"ocad_parts_lib"
CDS_LOCATION"C54";
"1"
$PN"1"3;
"2"
$PN"2"6,5,4;
%"cap_np"
"1","(3575,-4650)","0","ocad_parts_lib","I403";
;
VALUE"47UF"
$LOCATION"C54"
VOLTAGE"6.3V"
CDS_LIB"ocad_parts_lib"
CDS_LOCATION"C54"
JEDEC_TYPE"cap0805"
SOURCE_PACKAGE"CAP_NP"
AVAILABILITY"In Stock"
DISTRIBUTOR"Digi-Key"
DISTRIBUTOR_PARTNUMBER"490-14660-2-ND"
MANUFACTURER"Murata"
MPN"GRM21BR60J476ME15K"
PSPICE"C"
TOLERANCE"20%"
DESCRIPTION"CAP CER 47UF 6.3V X5R 0805"
PART_TYPE"Ceramic"
PART_NUMBER"GRM21BR60J476ME15K"
ROOM"VCC1V8"
ALT_SYMBOLS""
LAST_EDIT_BY"SNF"
CLASS"DISCRETE"
SEC"1";
"1"
$PN"1"8;
"2"
$PN"2"6,5,4;
%"6 MERGE"
"1","(1125,-6175)","2","standard","I404";
;
BODY_TYPE"PLUMBING"
NEEDS_NO_SIZE"TRUE"
HDL_CONCAT"TRUE"
CDS_LIB"standard";
"A\NWC\NAC"12;
"B\NWC\NAC"13;
"C\NWC\NAC"14;
"D\NWC\NAC"15;
"E\NWC\NAC"10;
"F\NWC\NAC"16;
"Y\NWC\NAC"11;
%"portboth-r"
"1","(400,-6125)","0","mtca_interface_board","I405";
;
CDS_LIB"mtca_interface_board";
"HOTSPOT_0"
HDL_PORT"INOUT"
PIN_NAME"POWER<10..0>"11;
%"RSMD0805"
"1","(1975,-4475)","0","cnpassive","I406";
;
VALUE"0.27"
TOL"1%"
$LOCATION"R?"
TC2"RTMPQ"
TC1"RTMPL"
MAX_TEMP"RTMAX"
SLOPE"RSMAX"
VOLTAGE"RVMAX"
POWER"RMAX"
DIST"FLAT"
NEGTOL"RTOL%"
POSTOL"RTOL%"
TOL_ON_OFF"ON"
SIZE"1B"
CDS_LIB"cnpassive"
PACK_TYPE"125MW";
"B <SIZE-1..0>\NAC"9;
"A <SIZE-1..0>\NAC"3;
END.
