uob-hep-cad/uob-hep-pc072/hardware/Cadence/top/mtca_interface_board_reocc/04_#20sfp_module/sch_1/page1.csv

FILE_TYPE = CONNECTIVITY;
{Allegro Design Entry HDL 23.1 P001 (4147275) 9/30/2023}
"PAGE_NUMBER" = 1;
0"NC";
1"VCC3V3\G";
2"VCC3V3\G";
3"GND\g";
4"TD_N";
5"TD_P";
6"GND\G";
7"VCCT_3V3";
8"RATE_SELECT";
9"TX_DISABLE";
10"N00183";
11"VCC3V3\G";
12"VCC3V3\G";
13"GND\G";
14"GND\G";
15"GND\G";
16"RD_N";
17"VCCR_3V3";
19"TX_FAULT";
18"TX_FAULT";
20"SDA";
21"RD_P";
23"LOS";
22"LOS";
24"SCL";
%"portleft-l"
"1","(4600,-1725)","6","mtca_interface_board","10P";
;
NAME"TX_FAULT"
CDS_LIB"mtca_interface_board";
"HOTSPOT_0"
PIN_NAME"TX_FAULT"
HDL_PORT"OUT"19,18;
%"gnd"
"1","(1150,-3475)","0","mtca_interface_board","11P";
;
CDS_LIB"mtca_interface_board"
HDL_POWER"GND";
"HOTSPOT_0"3;
%"vcc_bar"
"1","(950,-350)","0","mtca_interface_board","12P";
;
HDL_POWER"VCC3V3"
CDS_LIB"mtca_interface_board";
"HOTSPOT_0"11;
%"vcc_bar"
"1","(4325,-225)","0","mtca_interface_board","13P";
;
HDL_POWER"VCC3V3"
CDS_LIB"mtca_interface_board";
"HOTSPOT_0"1;
%"vcc_bar"
"1","(4500,-1000)","2","mtca_interface_board","14P";
;
HDL_POWER"VCC3V3"
CDS_LIB"mtca_interface_board";
"HOTSPOT_0"2;
%"portleft-l"
"1","(650,-1975)","4","mtca_interface_board","1P";
;
NAME"RATE_SELECT"
CDS_LIB"mtca_interface_board";
"HOTSPOT_0"
PIN_NAME"RATE_SELECT"
HDL_PORT"IN"8;
%"portleft-l"
"1","(2100,-1725)","4","mtca_interface_board","2P";
;
NAME"SCL"
CDS_LIB"mtca_interface_board";
"HOTSPOT_0"
PIN_NAME"SCL"
HDL_PORT"IN"24;
%"portboth-l"
"1","(2100,-1675)","2","mtca_interface_board","3P";
;
NAME"SDA"
CDS_LIB"mtca_interface_board";
"HOTSPOT_0"
PIN_NAME"SDA"
HDL_PORT"INOUT"20;
%"cap_np"
"1","(2125,-650)","0","ocad_parts_lib","47P";
;
VALUE"1UF"
VOLTAGE"25V"
LOCATION"C110"
SEC"1"
CLASS"DISCRETE"
LAST_EDIT_BY"SNF"
ALT_SYMBOLS""
AVAILABILITY"In Stock"
DISTRIBUTOR"Digi-Key"
DISTRIBUTOR_PARTNUMBER"490-10006-1-ND"
MANUFACTURER"Murata"
MPN"GRT155R61E105ME01D"
PSPICE"C"
DESCRIPTION"CAP CER 1UF 25V X5R 0402"
PART_TYPE"Ceramic"
PART_NUMBER"GRT155R61E105ME01D"
ROOM"SFP0"
REUSE_ANNOTATE"TRUE"
SOURCE_PACKAGE"CAP_NP"
JEDEC_TYPE"cap0402"
CDS_LIB"ocad_parts_lib"
CDS_LOCATION"C110";
"1"
$PN"1"17;
"2"
$PN"2"15;
%"cap_np"
"1","(3575,-600)","0","ocad_parts_lib","48P";
;
VOLTAGE"25V"
VALUE"0.1UF"
LOCATION"C115"
SEC"1"
CLASS"DISCRETE"
LAST_EDIT_BY"SNF"
ALT_SYMBOLS""
AVAILABILITY"In Stock"
DISTRIBUTOR"Digi-Key"
DISTRIBUTOR_PARTNUMBER"445-7348-2-ND"
MANUFACTURER"TDK CORP"
MPN"C1005X7R1E104K050BB "
PSPICE"C"
DESCRIPTION"CAP 0.1__F __10% 25V Ceramic Capacitor X7R 0402 "
PART_TYPE"Ceramic"
PART_NUMBER"445-7348-2-ND"
ROOM"SFP0"
REUSE_ANNOTATE"TRUE"
SOURCE_PACKAGE"CAP_NP"
JEDEC_TYPE"cap0402"
CDS_LIB"ocad_parts_lib"
CDS_LOCATION"C115";
"1"
$PN"1"7;
"2"
$PN"2"13;
%"cap_np"
"1","(1200,-625)","0","ocad_parts_lib","49P";
;
VALUE"10UF"
VOLTAGE"10V"
LOCATION"C87"
SEC"1"
CLASS"DISCRETE"
LAST_EDIT_BY"SNF"
ALT_SYMBOLS""
PART_NUMBER"GRM188R61A106KE69D"
PART_TYPE"Ceramic"
DESCRIPTION"CAP CER 10UF 10V X5R 0603"
TOLERANCE"10%"
PSPICE"C"
MPN"GRM188R61A106KE69D"
MANUFACTURER"Murata"
DISTRIBUTOR_PARTNUMBER"490-10474-2-ND"
DISTRIBUTOR"Digi-Key"
AVAILABILITY"In Stock"
ROOM"SFP0"
REUSE_ANNOTATE"TRUE"
SOURCE_PACKAGE"CAP_NP"
JEDEC_TYPE"cap0603"
CDS_LIB"ocad_parts_lib"
CDS_LOCATION"C87";
"1"
$PN"1"11;
"2"
$PN"2"14;
%"portleft-l"
"1","(1975,-1575)","4","mtca_interface_board","4P";
;
NAME"TD_N"
CDS_LIB"mtca_interface_board";
"HOTSPOT_0"
PIN_NAME"TD_N"
HDL_PORT"IN"4;
%"r"
"1","(4325,-1300)","0","discrete","50P";
;
VALUE"4.99k"
LOCATION"R117"
SEC"1"
ROOM"SFP0"
AVAILABILITY"In Stock"
DISTRIBUTOR"Digikey"
DISTRIBUTOR_PARTNUMBER"P4.99KLTR-ND"
MANUFACTURER"Panasonic"
MPN"ERJ-2RKF4991X"
TOLERANCE"1%"
POWER"1/10 W"
DESCRIPTION"RES SMD 4.99K OHM 1% 1/10W 0402"
PART_TYPE"Thick Film"
PART_NUMBER"ERJ-2RKF4991X"
REUSE_ANNOTATE"TRUE"
SOURCE_PACKAGE"R"
JEDEC_TYPE"res0402"
CDS_LIB"discrete"
CDS_LOCATION"R117";
"1"
$PN"1"2;
"2"
$PN"2"19,18;
%"r"
"1","(1150,-1275)","0","discrete","51P";
;
VALUE"4.99k"
LOCATION"R115"
SEC"1"
REUSE_ANNOTATE"TRUE"
PART_NUMBER"ERJ-2RKF4991X"
PART_TYPE"Thick Film"
DESCRIPTION"RES SMD 4.99K OHM 1% 1/10W 0402"
POWER"1/10 W"
TOLERANCE"1%"
MPN"ERJ-2RKF4991X"
MANUFACTURER"Panasonic"
DISTRIBUTOR_PARTNUMBER"P4.99KLTR-ND"
DISTRIBUTOR"Digikey"
AVAILABILITY"In Stock"
ROOM"SFP0"
SOURCE_PACKAGE"R"
JEDEC_TYPE"res0402"
CDS_LIB"discrete"
CDS_LOCATION"R115";
"1"
$PN"1"12;
"2"
$PN"2"10;
%"r"
"1","(4450,-1300)","0","discrete","52P";
;
VALUE"4.99k"
LOCATION"R112"
SEC"1"
REUSE_ANNOTATE"TRUE"
PART_NUMBER"ERJ-2RKF4991X"
PART_TYPE"Thick Film"
DESCRIPTION"RES SMD 4.99K OHM 1% 1/10W 0402"
POWER"1/10 W"
TOLERANCE"1%"
MPN"ERJ-2RKF4991X"
MANUFACTURER"Panasonic"
DISTRIBUTOR_PARTNUMBER"P4.99KLTR-ND"
DISTRIBUTOR"Digikey"
AVAILABILITY"In Stock"
ROOM"SFP0"
SOURCE_PACKAGE"R"
JEDEC_TYPE"res0402"
CDS_LIB"discrete"
CDS_LOCATION"R112";
"1"
$PN"1"2;
"2"
$PN"2"23,22;
%"cap_np"
"1","(3225,-600)","0","ocad_parts_lib","53P";
;
VOLTAGE"6.3V"
VALUE"22UF"
LOCATION"C117"
SEC"1"
CLASS"DISCRETE"
LAST_EDIT_BY"SNF"
ALT_SYMBOLS""
PART_NUMBER"GRM188R60J226MEA0D"
PART_TYPE"Ceramic"
DESCRIPTION"CAP CER 22UF 6.3V X5R 0603"
TOLERANCE"20%"
PSPICE"C"
MPN"GRM188R60J226MEA0D"
MANUFACTURER"Murata"
DISTRIBUTOR_PARTNUMBER"490-7611-2-ND"
DISTRIBUTOR"Digi-Key"
AVAILABILITY"In Stock"
ROOM"SFP0"
REUSE_ANNOTATE"TRUE"
SOURCE_PACKAGE"CAP_NP"
JEDEC_TYPE"cap0603"
CDS_LIB"ocad_parts_lib"
CDS_LOCATION"C117";
"1"
$PN"1"7;
"2"
$PN"2"13;
%"ind"
"1","(3750,-450)","1","ind","54P";
;
VALUE"1 uH"
LOCATION"L8"
SEC"1"
PART_NUMBER"CIGT201208EH1R0MNE"
PART_TYPE"Inductor"
DESCRIPTION"FIXED IND 1UH 3.1A 55MOHM SMD"
RATING"3.0 A"
TOLERANCE"10 %"
DCRESISTANCE"55mOhm "
QFACTOR"25"
MPN"CIGT201208EH1R0MNE"
MANUFACTURER"Samsung Electro-Mechanics"
DISTRIBUTOR_PARTNUMBER"1276-6886-2-ND"
DISTRIBUTOR"Digikey"
DATASHEET"C:\EMA\CISQuickStart\Technical_Datasheets\Panasonic\AGA0000CE31.pdf"
SOURCE_PACKAGE"IND"
JEDEC_TYPE"INDC2013X105N"
CDS_LIB"ind"
CDS_LOCATION"L8";
"1"
$PN"1"7;
"2"
$PN"2"1;
%"cap_np"
"1","(1000,-625)","0","ocad_parts_lib","55P";
;
VOLTAGE"25V"
VALUE"0.1UF"
LOCATION"C86"
SEC"1"
CLASS"DISCRETE"
LAST_EDIT_BY"SNF"
ALT_SYMBOLS""
REUSE_ANNOTATE"TRUE"
ROOM"SFP0"
PART_NUMBER"445-7348-2-ND"
PART_TYPE"Ceramic"
DESCRIPTION"CAP 0.1__F __10% 25V Ceramic Capacitor X7R 0402 "
PSPICE"C"
MPN"C1005X7R1E104K050BB "
MANUFACTURER"TDK CORP"
DISTRIBUTOR_PARTNUMBER"445-7348-2-ND"
DISTRIBUTOR"Digi-Key"
AVAILABILITY"In Stock"
SOURCE_PACKAGE"CAP_NP"
JEDEC_TYPE"cap0402"
CDS_LIB"ocad_parts_lib"
CDS_LOCATION"C86";
"1"
$PN"1"11;
"2"
$PN"2"14;
%"r"
"1","(875,-1275)","0","discrete","56P";
;
VALUE"4.99k"
LOCATION"R114"
SEC"1"
REUSE_ANNOTATE"TRUE"
PART_NUMBER"ERJ-2RKF4991X"
PART_TYPE"Thick Film"
DESCRIPTION"RES SMD 4.99K OHM 1% 1/10W 0402"
POWER"1/10 W"
TOLERANCE"1%"
MPN"ERJ-2RKF4991X"
MANUFACTURER"Panasonic"
DISTRIBUTOR_PARTNUMBER"P4.99KLTR-ND"
DISTRIBUTOR"Digikey"
AVAILABILITY"In Stock"
ROOM"SFP0"
SOURCE_PACKAGE"R"
JEDEC_TYPE"res0402"
CDS_LIB"discrete"
CDS_LOCATION"R114";
"1"
$PN"1"12;
"2"
$PN"2"8;
%"con20p_sfp-1367073-1"
"1","(2925,-1725)","0","ocad_parts_lib","57P";
;
VALUE"1367073-1"
LOCATION"J6"
SEC"1"
DATASHEET"C:\EMA\CISQuickStart\Technical_Datasheets\Tyco\ENG_CAT_1242163_0299_10_[1].pdf"
DISTRIBUTOR"Digikey"
DISTRIBUTOR_PARTNUMBER"A97430TR-ND"
MANUFACTURER"TE Connectivity AMP Connectors"
MPN"1367073-1"
HOUSINGGENDER"Female"
CONTACTGENDER"Female"
DESCRIPTION"CONN SFP RCPT 20POS SLD R/A SMD"
PART_TYPE"Receptacle"
PART_NUMBER"1367073-1"
ROOM"SFP0"
REUSE_ANNOTATE"TRUE"
SOURCE_PACKAGE"CON20P_SFP-1367073-1"
JEDEC_TYPE"TYCO_1367073"
CDS_LIB"ocad_parts_lib"
CDS_LOCATION"J6";
"RATE_SELECT"
$PN"7"8;
"TX_DISABLE"
$PN"3"9;
"LOS"
$PN"8"23,22;
"TX_FAULT"
$PN"2"19,18;
"VEET0"
$PN"1"6;
"MOD_DEF2"
$PN"4"20;
"MOD_DEF1"
$PN"5"24;
"MOD_DEF0"
$PN"6"10;
"VEER0"
$PN"9"6;
"VEER1"
$PN"10"6;
"VEER2"
$PN"11"6;
"RD-"
$PN"12"16;
"RD+"
$PN"13"21;
"VEER3"
$PN"14"6;
"VCCR"
$PN"15"17;
"VCCT"
$PN"16"7;
"VEET1"
$PN"17"6;
"TD+"
$PN"18"5;
"TD-"
$PN"19"4;
"VEET2"
$PN"20"6;
%"r"
"1","(1025,-1275)","0","discrete","58P";
;
VALUE"4.99k"
LOCATION"R116"
SEC"1"
ROOM"SFP0"
AVAILABILITY"In Stock"
DISTRIBUTOR"Digikey"
DISTRIBUTOR_PARTNUMBER"P4.99KLTR-ND"
MANUFACTURER"Panasonic"
MPN"ERJ-2RKF4991X"
TOLERANCE"1%"
POWER"1/10 W"
DESCRIPTION"RES SMD 4.99K OHM 1% 1/10W 0402"
PART_TYPE"Thick Film"
PART_NUMBER"ERJ-2RKF4991X"
REUSE_ANNOTATE"TRUE"
SOURCE_PACKAGE"R"
JEDEC_TYPE"res0402"
CDS_LIB"discrete"
CDS_LOCATION"R116";
"1"
$PN"1"12;
"2"
$PN"2"9;
%"cap_np"
"1","(1900,-650)","0","ocad_parts_lib","59P";
;
VALUE"0.1UF"
VOLTAGE"25V"
LOCATION"C111"
SEC"1"
CLASS"DISCRETE"
LAST_EDIT_BY"SNF"
ALT_SYMBOLS""
AVAILABILITY"In Stock"
DISTRIBUTOR"Digi-Key"
DISTRIBUTOR_PARTNUMBER"445-7348-2-ND"
MANUFACTURER"TDK CORP"
MPN"C1005X7R1E104K050BB "
PSPICE"C"
DESCRIPTION"CAP 0.1__F __10% 25V Ceramic Capacitor X7R 0402 "
PART_TYPE"Ceramic"
PART_NUMBER"445-7348-2-ND"
ROOM"SFP0"
REUSE_ANNOTATE"TRUE"
SOURCE_PACKAGE"CAP_NP"
JEDEC_TYPE"cap0402"
CDS_LIB"ocad_parts_lib"
CDS_LOCATION"C111";
"1"
$PN"1"17;
"2"
$PN"2"15;
%"portleft-l"
"1","(1975,-1525)","4","mtca_interface_board","5P";
;
NAME"TD_P"
CDS_LIB"mtca_interface_board";
"HOTSPOT_0"
PIN_NAME"TD_P"
HDL_PORT"IN"5;
%"sfp_cage-2227023-1"
"1","(900,-2850)","0","ocad_parts_lib","60P";
;
VALUE"2227023-1"
$LOCATION"U14"
CDS_LIB"ocad_parts_lib"
JEDEC_TYPE"SFP_CAGE"
SOURCE_PACKAGE"SFP_CAGE-2227023-1"
PART_NUMBER"2227023-1"
PART_TYPE"Misc"
DESCRIPTION"CONN SFP CAGE 1POS PRESS-FIT R/A"
MPN"2227023-1"
MANUFACTURER"TE Connectivity AMP Connectors"
DISTRIBUTOR_PARTNUMBER"A120615-ND"
DISTRIBUTOR"Digi-Key"
AVAILABILITY"In Stock"
ROOM"SFP0"
SEC"1"
CDS_LOCATION"U14";
"CG1"
$PN"1"3;
"CG2"
$PN"2"3;
"CG3"
$PN"3"3;
"CG4"
$PN"4"3;
"CG5"
$PN"5"3;
"CG6"
$PN"6"3;
"CG7"
$PN"7"3;
"CG8"
$PN"8"3;
"CG"
$PN"9"3;
"CG_0"
$PN"10"3;
"CG_1"
$PN"11"3;
"CG_2"
$PN"12"3;
"CG_3"
$PN"13"3;
"CG_4"
$PN"14"3;
"CG_5"
$PN"15"3;
"CG_6"
$PN"16"3;
"CG_7"
$PN"17"3;
"CG_8"
$PN"18"3;
"CG_9"
$PN"19"3;
"CG_10"
$PN"20"3;
%"cap_np"
"1","(2325,-650)","0","ocad_parts_lib","61P";
;
VOLTAGE"6.3V"
VALUE"22UF"
LOCATION"C109"
SEC"1"
CLASS"DISCRETE"
LAST_EDIT_BY"SNF"
ALT_SYMBOLS""
PART_NUMBER"GRM188R60J226MEA0D"
PART_TYPE"Ceramic"
DESCRIPTION"CAP CER 22UF 6.3V X5R 0603"
TOLERANCE"20%"
PSPICE"C"
MPN"GRM188R60J226MEA0D"
MANUFACTURER"Murata"
DISTRIBUTOR_PARTNUMBER"490-7611-2-ND"
DISTRIBUTOR"Digi-Key"
AVAILABILITY"In Stock"
ROOM"SFP0"
REUSE_ANNOTATE"TRUE"
SOURCE_PACKAGE"CAP_NP"
JEDEC_TYPE"cap0603"
CDS_LIB"ocad_parts_lib"
CDS_LOCATION"C109";
"1"
$PN"1"17;
"2"
$PN"2"15;
%"ind"
"1","(1475,-450)","1","ind","62P";
;
VALUE"1 uH"
LOCATION"L7"
SEC"1"
PART_NUMBER"CIGT201208EH1R0MNE"
PART_TYPE"Inductor"
DESCRIPTION"FIXED IND 1UH 3.1A 55MOHM SMD"
RATING"3.0 A"
TOLERANCE"10 %"
DCRESISTANCE"55mOhm "
QFACTOR"25"
MPN"CIGT201208EH1R0MNE"
MANUFACTURER"Samsung Electro-Mechanics"
DISTRIBUTOR_PARTNUMBER"1276-6886-2-ND"
DISTRIBUTOR"Digikey"
DATASHEET"C:\EMA\CISQuickStart\Technical_Datasheets\Panasonic\AGA0000CE31.pdf"
SOURCE_PACKAGE"IND"
JEDEC_TYPE"INDC2013X105N"
CDS_LIB"ind"
CDS_LOCATION"L7";
"1"
$PN"1"11;
"2"
$PN"2"17;
%"vcc_bar"
"1","(825,-975)","0","mtca_interface_board","63P";
;
HDL_POWER"VCC3V3"
CDS_LIB"mtca_interface_board";
"HOTSPOT_0"12;
%"gnd"
"1","(3525,-825)","0","mtca_interface_board","64P";
;
HDL_POWER"GND"
CDS_LIB"mtca_interface_board";
"HOTSPOT_0"13;
%"gnd"
"1","(1150,-925)","0","mtca_interface_board","65P";
;
HDL_POWER"GND"
CDS_LIB"mtca_interface_board";
"HOTSPOT_0"14;
%"gnd"
"1","(1850,-925)","0","mtca_interface_board","66P";
;
HDL_POWER"GND"
CDS_LIB"mtca_interface_board";
"HOTSPOT_0"15;
%"gnd"
"1","(2375,-2475)","0","mtca_interface_board","67P";
;
HDL_POWER"GND"
CDS_LIB"mtca_interface_board";
"HOTSPOT_0"6;
%"portleft-l"
"1","(650,-1875)","4","mtca_interface_board","6P";
;
NAME"TX_DISABLE"
CDS_LIB"mtca_interface_board";
"HOTSPOT_0"
PIN_NAME"TX_DISABLE"
HDL_PORT"IN"9;
%"portleft-l"
"1","(4600,-1775)","6","mtca_interface_board","7P";
;
NAME"LOS"
CDS_LIB"mtca_interface_board";
"HOTSPOT_0"
PIN_NAME"LOS"
HDL_PORT"OUT"23,22;
%"portleft-l"
"1","(3800,-1575)","6","mtca_interface_board","8P";
;
NAME"RD_N"
CDS_LIB"mtca_interface_board";
"HOTSPOT_0"
PIN_NAME"RD_N"
HDL_PORT"OUT"16;
%"portleft-l"
"1","(3800,-1525)","6","mtca_interface_board","9P";
;
NAME"RD_P"
CDS_LIB"mtca_interface_board";
"HOTSPOT_0"
PIN_NAME"RD_P"
HDL_PORT"OUT"21;
END.
