uob-hep-cad/uob-hep-pc072/images/dune_mib_rev3_v224_layer_5_with_power_colour_white_bg.pdf

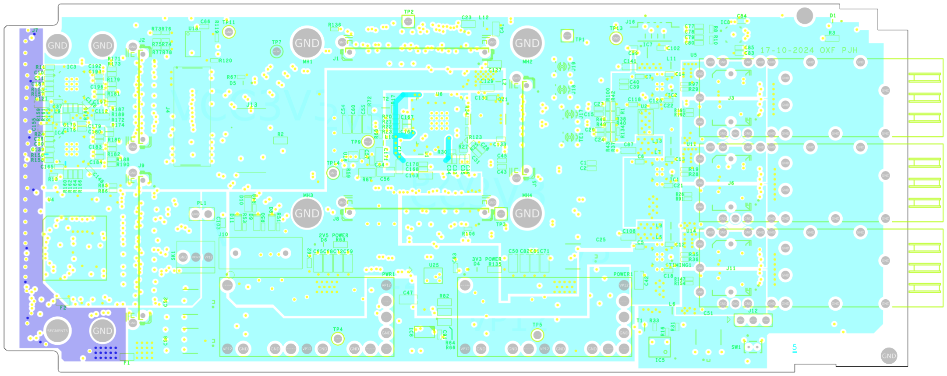
[picture p4: page 1]
