uob-hep-cad/uob-hep-pc072/hardware/Cadence/top/mtca_interface_board_reocc/top/sch_1/page2.csv

FILE_TYPE = CONNECTIVITY;
{Allegro Design Entry HDL 17.4-2019 S033 (4064022) 10/8/2022}
"PAGE_NUMBER" = 2;
0"NC";
1"DCDC_ENABLE:DCDC_3V3_PG:DCDC_2V5_PG:LDO_1V8_PG:SENSE_I2C_SCL:SENSE_I2C_SDA";
2"FPGA_PG";
3"UNCONNECTED<91:0>:PWR_ON:AMC_N_ENABLE:TCK:TMS:TDO:TDI:GBE_TX_N:GBE_TX_P:GBE_RX_N:GBE_RX_P:IMPB_SCL:IMPB_SDA:DATA_OUT_P<11..0>:DATA_OUT_N<11..0>:DATA_IN_P<11..0>:DATA_IN_N<11..0>:REF_CLK_P<11..0>:REF_CLK_N<11..0>:AMC_GA<2..0>:AMC_N_PS<1..0>";
4"SFP_RATE_SELECT<2..0>:SFP_TX_DISABLE<2..0>:SFP_TX_FAULT<2..0>:SFP_LOS<2..0>:SFP_RD_P<2..0>:SFP_RD_N<2..0>:SFP_TD_P<2..0>:SFP_TD_N<2..0>:SFP_SDA<2..0>:SFP_SCL<2..0>";
5"CLK_SCL:CLK_SDA:CLK_SEL0:CLK_SEL1:CLK_INTR:CLK_LOL:CLK_RST:CLK_P<1..0>:CLK_N<1..0>";
6"UPSTREAM_DATA_P<2..0>:UPSTREAM_DATA_N_<2..0>:SFP_DATA_OUT_P<2..0>:SFP_DATA_OUT_N<2..0>";
%"02_ power"
"1","(2825,-1100)","0","mtca_interface_board_reocc","1P";
;
ROOM"POWER"
$LOCATION"POWER1"
VALUE"02. POWER"
BLOCK"TRUE"
DESIGNATORNAMEPROP"POWER"
CDS_LOCATION"POWER1"
CDS_LIB"mtca_interface_board_reocc"
LIBRARY1"ieee"
USE1"ieee.std_logic_1164.all"
USE2"work.all";
"POWER<5..0>"
VHDL_MODE"inout"
VHDL_VECTOR_TYPE"std_logic_vector"1;
"FPGA_PG"
VHDL_MODE"IN"
VHDL_SCALAR_TYPE"std_logic"2;
%"08_ timing"
"1","(850,-3050)","0","mtca_interface_board_reocc","2P";
;
$LOCATION"TIMING1"
VALUE"08. TIMING"
LIBRARY1"ieee"
USE1"ieee.std_logic_1164.all"
USE2"work.all"
CDS_LIB"mtca_interface_board_reocc"
CDS_LOCATION"TIMING1"
DESIGNATORNAMEPROP"TIMING"
BLOCK"TRUE";
"SFP_DATA_IO<11..0>"
VHDL_VECTOR_TYPE"std_logic_vector"
VHDL_MODE"inout"6;
"CLKGEN_IO<10..0>"
VHDL_VECTOR_TYPE"std_logic_vector"
VHDL_MODE"inout"5;
"SFP<29..0>"
VHDL_VECTOR_TYPE"std_logic_vector"
VHDL_MODE"INOUT"4;
"BP<180..0>"
VHDL_VECTOR_TYPE"std_logic_vector"
VHDL_MODE"INOUT"3;
%"03_ sfp"
"1","(850,-2025)","0","mtca_interface_board_reocc","3P";
;
$LOCATION"3X_SFP0"
VALUE"03. SFP"
BLOCK"TRUE"
DESIGNATORNAMEPROP"SFP0"
CDS_LOCATION"3X_SFP0"
CDS_LIB"mtca_interface_board_reocc";
"SFP<29..0>"
VHDL_MODE"INOUT"4;
%"05 trenz te0712 fpga module"
"1","(4850,-1600)","0","mtca_interface_board_reocc","4P";
;
$LOCATION"TE1"
VALUE"05 TRENZ TE0712 FPGA MODULE"
LIBRARY1"ieee"
USE1"ieee.std_logic_1164.all"
USE2"work.all"
CDS_LIB"mtca_interface_board_reocc"
CDS_LOCATION"TE1"
DESIGNATORNAMEPROP"TE0712"
BLOCK"TRUE";
"SFP_DATA_IO<11..0>"
VHDL_VECTOR_TYPE"std_logic_vector"
VHDL_MODE"inout"6;
"CLKGEN_IO<10..0>"
VHDL_VECTOR_TYPE"std_logic_vector"
VHDL_MODE"inout"5;
"SFP<29..0>"
VHDL_VECTOR_TYPE"std_logic_vector"
VHDL_MODE"INOUT"4;
"FPGA_PG"
VHDL_SCALAR_TYPE"std_logic"
VHDL_MODE"OUT"2;
"BP<180..0>"
VHDL_VECTOR_TYPE"std_logic_vector"
VHDL_MODE"INOUT"3;
%"01_ module management ctrl"
"1","(1500,-850)","0","mtca_interface_board_reocc","5P";
;
$LOCATION"MMC"
VALUE"01. MODULE MANAGEMENT CTRL"
CDS_LIB"mtca_interface_board_reocc"
CDS_LOCATION"MMC"
DESIGNATORNAMEPROP"MMC"
BLOCK"TRUE"
LIBRARY1"ieee"
USE1"ieee.std_logic_1164.all"
USE2"work.all";
"POWER<5..0>"
VHDL_MODE"inout"
VHDL_VECTOR_TYPE"std_logic_vector"1;
"FPGA_PG"
VHDL_MODE"IN"
VHDL_SCALAR_TYPE"std_logic"2;
"BP<180..0>"
VHDL_MODE"INOUT"
VHDL_VECTOR_TYPE"std_logic_vector"3;
%"07_ backplane interface"
"1","(6225,-450)","0","mtca_interface_board_reocc","6P";
;
VALUE"07. BACKPLANE INTERFACE"
$LOCATION"BACKPLANE_INTERFACE"
CDS_LIB"mtca_interface_board_reocc"
CDS_LOCATION"BACKPLANE_INTERFACE"
DESIGNATORNAMEPROP"BACKPLANE INTERFACE"
BLOCK"TRUE";
"BP<180..0>"
VHDL_MODE"INOUT"3;
END.
