uob-hep-cad/uob-hep-pc072/hardware/Cadence/top/mtca_interface_board_reocc/03_#20sfp/sch_1/page1.csv

FILE_TYPE = CONNECTIVITY
{Allegro Design Entry HDL 23.1 P001 (4147275) 9/30/2023}
PAGE_NUMBER = 1
0"NC"
1"SFP.SDA<2>"
2"SFP.RATE_SELECT<0>"
3"SFP.TX_DISABLE<0>"
4"SFP.TX_FAULT<0>"
5"SFP.LOS<0>"
6"SFP.TX_DISABLE<2>"
7"SFP.LOS<2>"
8"SFP.SCL<2..0>"
9"SFP.SDA<2..0>"
11"SFP<29..0>"
10"SFP<29..0>"
12"SFP.TD_N<2..0>"
13"SFP.RD_N<2>"
14"SFP.RD_P<2>"
15"SFP.TX_FAULT<2>"
16"SFP.RATE_SELECT<2>"
17"SFP.RD_P<1>"
18"SFP.RD_N<1>"
19"SFP.TD_P<1>"
20"SFP.TD_N<1>"
21"SFP.SDA<1>"
22"SFP.SCL<1>"
23"SFP.RATE_SELECT<1>"
24"SFP.SCL<0>"
25"SFP.SDA<0>"
26"SFP.TD_N<0>"
27"SFP.TD_P<0>"
28"SFP.RD_N<0>"
29"SFP.RD_P<0>"
30"SFP.SCL<2>"
31"SFP.TD_N<2>"
32"SFP.TD_P<2>"
33"SFP.LOS<1>"
34"SFP.TX_FAULT<1>"
35"SFP.TX_DISABLE<1>"
36"SFP.TX_FAULT<2..0>"
37"SFP.LOS<2..0>"
38"SFP.RD_N<2..0>"
39"SFP.TD_P<2..0>"
40"SFP.TX_DISABLE<2..0>"
41"SFP.RD_P<2..0>"
42"SFP.RATE_SELECT<2..0>"
%"portboth-r_1"
1,"(3050,-650)","0","mtca_interface_board","1P"
NAME"SFP<29..0>"
CDS_LIB"mtca_interface_board"
HOTSPOT_0
HDL_PORT"INOUT"
PIN_NAME"SFP<29..0>"11,10
%"04_ sfp_module"
1,"(1550,-1350)","0","mtca_interface_board_reocc","2P"
VALUE"04. SFP_MODULE"
ROOM"SFP2"
$LOCATION"SFP2"
CDS_LIB"mtca_interface_board_reocc"
CDS_LOCATION"SFP2"
REUSEANNOTATED"YES"
DESIGNATORNAMEPROP"SFP?"
BLOCK"TRUE"
RATE_SELECT
VHDL_MODE"IN"23
SCL
VHDL_MODE"IN"22
SDA
VHDL_MODE"INOUT"21
TD_N
VHDL_MODE"IN"20
TD_P
VHDL_MODE"IN"19
TX_DISABLE
VHDL_MODE"IN"35
LOS
VHDL_MODE"OUT"33
RD_N
VHDL_MODE"OUT"18
RD_P
VHDL_MODE"OUT"17
TX_FAULT
VHDL_MODE"OUT"34
%"04_ sfp_module"
2,"(1525,-700)","0","mtca_interface_board_reocc","3P"
$LOCATION"SFP1"
VALUE"04. SFP_MODULE"
ROOM"SFP1"
BLOCK"TRUE"
DESIGNATORNAMEPROP"SFP?"
REUSEANNOTATED"YES"
CAPTURECELLPACKPROP"04. SFP_MODULE##1"
CDS_LOCATION"SFP1"
CDS_LIB"mtca_interface_board_reocc"
TD_N
VHDL_MODE"OUT"26
TD_P
VHDL_MODE"IN"27
SDA
VHDL_MODE"INOUT"25
RD_N
VHDL_MODE"IN"28
TX_FAULT
VHDL_MODE"OUT"4
RD_P
VHDL_MODE"OUT"29
LOS
VHDL_MODE"OUT"5
TX_DISABLE
VHDL_MODE"IN"3
SCL
VHDL_MODE"IN"24
RATE_SELECT
VHDL_MODE"IN"2
%"04_ sfp_module"
1,"(1550,-2050)","0","mtca_interface_board_reocc","4P"
VALUE"04. SFP_MODULE"
ROOM"SFP3"
$LOCATION"SFP3"
CDS_LIB"mtca_interface_board_reocc"
CDS_LOCATION"SFP3"
CAPTURECELLPACKPROP"04. SFP_MODULE##2"
REUSEANNOTATED"YES"
DESIGNATORNAMEPROP"SFP?"
BLOCK"TRUE"
RATE_SELECT
VHDL_MODE"IN"16
SCL
VHDL_MODE"IN"30
SDA
VHDL_MODE"INOUT"1
TD_N
VHDL_MODE"IN"31
TD_P
VHDL_MODE"IN"32
TX_DISABLE
VHDL_MODE"IN"6
LOS
VHDL_MODE"OUT"7
RD_N
VHDL_MODE"OUT"13
RD_P
VHDL_MODE"OUT"14
TX_FAULT
VHDL_MODE"OUT"15
%"BUSWIDE_TOP_LEFT_RIP"
1,"(3600,-950)","0","default","I10"
CDS_LIB"default"
BODY_TYPE"PLUMBING"
HDL_TAP"TRUE"
WIRE \NWC \NAC
BN"23..21"36
BUNDLE \NWC \NAC11,10
%"BUSWIDE_TOP_LEFT_RIP"
1,"(3600,-1000)","0","default","I11"
CDS_LIB"default"
BODY_TYPE"PLUMBING"
HDL_TAP"TRUE"
WIRE \NWC \NAC
BN"20..18"37
BUNDLE \NWC \NAC11,10
%"BUSWIDE_TOP_LEFT_RIP"
1,"(3600,-1050)","0","default","I12"
CDS_LIB"default"
BODY_TYPE"PLUMBING"
HDL_TAP"TRUE"
WIRE \NWC \NAC
BN"17..15"41
BUNDLE \NWC \NAC11,10
%"BUSWIDE_TOP_LEFT_RIP"
1,"(3600,-1100)","0","default","I13"
CDS_LIB"default"
BODY_TYPE"PLUMBING"
HDL_TAP"TRUE"
WIRE \NWC \NAC
BN"14..12"38
BUNDLE \NWC \NAC11,10
%"BUSWIDE_TOP_LEFT_RIP"
1,"(3600,-1150)","0","default","I14"
CDS_LIB"default"
BODY_TYPE"PLUMBING"
HDL_TAP"TRUE"
WIRE \NWC \NAC
BN"11..9"39
BUNDLE \NWC \NAC11,10
%"BUSWIDE_TOP_LEFT_RIP"
1,"(3600,-1200)","0","default","I15"
CDS_LIB"default"
BODY_TYPE"PLUMBING"
HDL_TAP"TRUE"
WIRE \NWC \NAC
BN"8..6"12
BUNDLE \NWC \NAC11,10
%"BUSWIDE_TOP_LEFT_RIP"
1,"(3600,-1250)","0","default","I16"
CDS_LIB"default"
BODY_TYPE"PLUMBING"
HDL_TAP"TRUE"
WIRE \NWC \NAC
BN"5..3"9
BUNDLE \NWC \NAC11,10
%"BUSWIDE_TOP_LEFT_RIP"
1,"(3600,-1300)","0","default","I17"
CDS_LIB"default"
BODY_TYPE"PLUMBING"
HDL_TAP"TRUE"
WIRE \NWC \NAC
BN"2..0"8
BUNDLE \NWC \NAC11,10
%"BUSWIDE_TOP_LEFT_RIP"
1,"(3600,-850)","0","default","I8"
CDS_LIB"default"
BODY_TYPE"PLUMBING"
HDL_TAP"TRUE"
WIRE \NWC \NAC
BN"29..27"42
BUNDLE \NWC \NAC11,10
%"BUSWIDE_TOP_LEFT_RIP"
1,"(3600,-900)","0","default","I9"
CDS_LIB"default"
BODY_TYPE"PLUMBING"
HDL_TAP"TRUE"
WIRE \NWC \NAC
BN"26..24"40
BUNDLE \NWC \NAC11,10
END.
