uob-hep-cad/uob-hep-pc072/hardware/Cadence/top/archive_libs/cnlinear/ltc2991/metadata/pinlist.txt

(Pinlist
	(Pin
		(Name V3)
		(MSB )
		(LSB )
		(Type INPUT)
		(Location Left)
		(InputLoadLow -0.01)
		(InputLoadHigh 0.01)
		(OutputLoadLow )
		(OutputLoadHigh )
		(CheckLoad Off)
		(CheckIO Off)
		(CheckDir 1)
		(CheckAssert 1)
		(CheckOutput 0)
		(UnknownLoading 1)
		(PinShape )
		(DIFF_PAIR_PINS_POS )
		(DIFF_PAIR_PINS_NEG )
	)

	(Pin
		(Name V4)
		(MSB )
		(LSB )
		(Type INPUT)
		(Location Left)
		(InputLoadLow -0.01)
		(InputLoadHigh 0.01)
		(OutputLoadLow )
		(OutputLoadHigh )
		(CheckLoad Off)
		(CheckIO Off)
		(CheckDir 1)
		(CheckAssert 1)
		(CheckOutput 0)
		(UnknownLoading 1)
		(PinShape )
		(DIFF_PAIR_PINS_POS )
		(DIFF_PAIR_PINS_NEG )
	)

	(Pin
		(Name V1)
		(MSB )
		(LSB )
		(Type INPUT)
		(Location Left)
		(InputLoadLow -0.01)
		(InputLoadHigh 0.01)
		(OutputLoadLow )
		(OutputLoadHigh )
		(CheckLoad Off)
		(CheckIO Off)
		(CheckDir 1)
		(CheckAssert 1)
		(CheckOutput 0)
		(UnknownLoading 1)
		(PinShape )
		(DIFF_PAIR_PINS_POS )
		(DIFF_PAIR_PINS_NEG )
	)

	(Pin
		(Name SDA)
		(MSB )
		(LSB )
		(Type BIDIR)
		(Location Left)
		(InputLoadLow -0.01)
		(InputLoadHigh 0.01)
		(OutputLoadLow 1.0)
		(OutputLoadHigh -1.0)
		(CheckLoad Off)
		(CheckIO Off)
		(CheckDir 1)
		(CheckAssert 1)
		(CheckOutput 0)
		(UnknownLoading 1)
		(PinShape )
		(DIFF_PAIR_PINS_POS )
		(DIFF_PAIR_PINS_NEG )
	)

	(Pin
		(Name V2)
		(MSB )
		(LSB )
		(Type INPUT)
		(Location Left)
		(InputLoadLow -0.01)
		(InputLoadHigh 0.01)
		(OutputLoadLow )
		(OutputLoadHigh )
		(CheckLoad Off)
		(CheckIO Off)
		(CheckDir 1)
		(CheckAssert 1)
		(CheckOutput 0)
		(UnknownLoading 1)
		(PinShape )
		(DIFF_PAIR_PINS_POS )
		(DIFF_PAIR_PINS_NEG )
	)

	(Pin
		(Name ADR0)
		(MSB )
		(LSB )
		(Type INPUT)
		(Location Left)
		(InputLoadLow -0.01)
		(InputLoadHigh 0.01)
		(OutputLoadLow )
		(OutputLoadHigh )
		(CheckLoad Off)
		(CheckIO Off)
		(CheckDir 1)
		(CheckAssert 1)
		(CheckOutput 0)
		(UnknownLoading 1)
		(PinShape )
		(DIFF_PAIR_PINS_POS )
		(DIFF_PAIR_PINS_NEG )
	)

	(Pin
		(Name ADR1)
		(MSB )
		(LSB )
		(Type INPUT)
		(Location Left)
		(InputLoadLow -0.01)
		(InputLoadHigh 0.01)
		(OutputLoadLow )
		(OutputLoadHigh )
		(CheckLoad Off)
		(CheckIO Off)
		(CheckDir 1)
		(CheckAssert 1)
		(CheckOutput 0)
		(UnknownLoading 1)
		(PinShape )
		(DIFF_PAIR_PINS_POS )
		(DIFF_PAIR_PINS_NEG )
	)

	(Pin
		(Name SCL)
		(MSB )
		(LSB )
		(Type INPUT)
		(Location Left)
		(InputLoadLow -0.01)
		(InputLoadHigh 0.01)
		(OutputLoadLow )
		(OutputLoadHigh )
		(CheckLoad Off)
		(CheckIO Off)
		(CheckDir 1)
		(CheckAssert 1)
		(CheckOutput 0)
		(UnknownLoading 1)
		(PinShape )
		(DIFF_PAIR_PINS_POS )
		(DIFF_PAIR_PINS_NEG )
	)

	(Pin
		(Name GND)
		(MSB )
		(LSB )
		(Type GROUND)
		(Location Top)
		(InputLoadLow )
		(InputLoadHigh )
		(OutputLoadLow )
		(OutputLoadHigh )
		(CheckLoad Off)
		(CheckIO Off)
		(CheckDir 0)
		(CheckAssert 0)
		(CheckOutput 0)
		(UnknownLoading 0)
		(PinShape )
		(DIFF_PAIR_PINS_POS )
		(DIFF_PAIR_PINS_NEG )
	)

	(Pin
		(Name VCC)
		(MSB )
		(LSB )
		(Type POWER)
		(Location Top)
		(InputLoadLow )
		(InputLoadHigh )
		(OutputLoadLow )
		(OutputLoadHigh )
		(CheckLoad Off)
		(CheckIO Off)
		(CheckDir 0)
		(CheckAssert 0)
		(CheckOutput 0)
		(UnknownLoading 0)
		(PinShape )
		(DIFF_PAIR_PINS_POS )
		(DIFF_PAIR_PINS_NEG )
	)

)
