uob-hep-cad/uob-hep-pc072/hardware/Cadence/top/archive_libs/cnlinear/pth08t210w/metadata/pinlist.txt

(Pinlist
	(Pin
		(Name GND)
		(MSB 3)
		(LSB 0)
		(Type GROUND)
		(Location Bottom)
		(InputLoadLow )
		(InputLoadHigh )
		(OutputLoadLow )
		(OutputLoadHigh )
		(CheckLoad Off)
		(CheckIO Off)
		(CheckDir 0)
		(CheckAssert 0)
		(CheckOutput 0)
		(UnknownLoading 0)
		(PinShape )
		(DIFF_PAIR_PINS_POS )
		(DIFF_PAIR_PINS_NEG )
	)

	(Pin
		(Name VADJ)
		(MSB )
		(LSB )
		(Type ANALOG)
		(Location Left)
		(InputLoadLow )
		(InputLoadHigh )
		(OutputLoadLow )
		(OutputLoadHigh )
		(CheckLoad Off)
		(CheckIO Off)
		(CheckDir 0)
		(CheckAssert 0)
		(CheckOutput 0)
		(UnknownLoading 0)
		(PinShape )
		(DIFF_PAIR_PINS_POS )
		(DIFF_PAIR_PINS_NEG )
	)

	(Pin
		(Name TRACK)
		(MSB )
		(LSB )
		(Type ANALOG)
		(Location Left)
		(InputLoadLow )
		(InputLoadHigh )
		(OutputLoadLow )
		(OutputLoadHigh )
		(CheckLoad Off)
		(CheckIO Off)
		(CheckDir 0)
		(CheckAssert 0)
		(CheckOutput 0)
		(UnknownLoading 0)
		(PinShape )
		(DIFF_PAIR_PINS_POS )
		(DIFF_PAIR_PINS_NEG )
	)

	(Pin
		(Name UVLO)
		(MSB )
		(LSB )
		(Type OC)
		(Location Right)
		(InputLoadLow )
		(InputLoadHigh )
		(OutputLoadLow 1.0)
		(OutputLoadHigh *)
		(CheckLoad Both)
		(CheckIO Both)
		(CheckDir 1)
		(CheckAssert 1)
		(CheckOutput 1)
		(UnknownLoading 0)
		(PinShape )
		(DIFF_PAIR_PINS_POS )
		(DIFF_PAIR_PINS_NEG )
	)

	(Pin
		(Name SENSM)
		(MSB )
		(LSB )
		(Type INPUT)
		(Location Left)
		(InputLoadLow -0.01)
		(InputLoadHigh 0.01)
		(OutputLoadLow )
		(OutputLoadHigh )
		(CheckLoad Both)
		(CheckIO Both)
		(CheckDir 1)
		(CheckAssert 1)
		(CheckOutput 1)
		(UnknownLoading 0)
		(PinShape )
		(DIFF_PAIR_PINS_POS )
		(DIFF_PAIR_PINS_NEG )
	)

	(Pin
		(Name SENSP)
		(MSB )
		(LSB )
		(Type INPUT)
		(Location Left)
		(InputLoadLow -0.01)
		(InputLoadHigh 0.01)
		(OutputLoadLow )
		(OutputLoadHigh )
		(CheckLoad Both)
		(CheckIO Both)
		(CheckDir 1)
		(CheckAssert 1)
		(CheckOutput 1)
		(UnknownLoading 0)
		(PinShape )
		(DIFF_PAIR_PINS_POS )
		(DIFF_PAIR_PINS_NEG )
	)

	(Pin
		(Name TURBOTRANS)
		(MSB )
		(LSB )
		(Type INPUT)
		(Location Left)
		(InputLoadLow -0.01)
		(InputLoadHigh 0.01)
		(OutputLoadLow )
		(OutputLoadHigh )
		(CheckLoad Both)
		(CheckIO Both)
		(CheckDir 1)
		(CheckAssert 1)
		(CheckOutput 1)
		(UnknownLoading 0)
		(PinShape )
		(DIFF_PAIR_PINS_POS )
		(DIFF_PAIR_PINS_NEG )
	)

	(Pin
		(Name VI)
		(MSB 1)
		(LSB 0)
		(Type POWER)
		(Location Right)
		(InputLoadLow )
		(InputLoadHigh )
		(OutputLoadLow )
		(OutputLoadHigh )
		(CheckLoad Off)
		(CheckIO Off)
		(CheckDir 0)
		(CheckAssert 0)
		(CheckOutput 0)
		(UnknownLoading 0)
		(PinShape )
		(DIFF_PAIR_PINS_POS )
		(DIFF_PAIR_PINS_NEG )
	)

	(Pin
		(Name VO)
		(MSB 1)
		(LSB 0)
		(Type POWER)
		(Location Right)
		(InputLoadLow )
		(InputLoadHigh )
		(OutputLoadLow )
		(OutputLoadHigh )
		(CheckLoad Off)
		(CheckIO Off)
		(CheckDir 0)
		(CheckAssert 0)
		(CheckOutput 0)
		(UnknownLoading 0)
		(PinShape )
		(DIFF_PAIR_PINS_POS )
		(DIFF_PAIR_PINS_NEG )
	)

)
