uob-hep-cad/uob-hep-pc072/hardware/Cadence/top/archive_libs/standard/4#20merge/metadata/pinlist.txt

(Pinlist
	(Pin
		(Name Y)
		(MSB )
		(LSB )
		(Type UNSPEC)
		(Location Left)
		(InputLoadLow )
		(InputLoadHigh )
		(OutputLoadLow )
		(OutputLoadHigh )
		(CheckLoad Off)
		(CheckIO Off)
		(CheckDir 0)
		(CheckAssert 0)
		(CheckOutput 0)
		(UnknownLoading 0)
	)

	(Pin
		(Name D)
		(MSB )
		(LSB )
		(Type UNSPEC)
		(Location Right)
		(InputLoadLow )
		(InputLoadHigh )
		(OutputLoadLow )
		(OutputLoadHigh )
		(CheckLoad Off)
		(CheckIO Off)
		(CheckDir 0)
		(CheckAssert 0)
		(CheckOutput 0)
		(UnknownLoading 0)
	)

	(Pin
		(Name C)
		(MSB )
		(LSB )
		(Type UNSPEC)
		(Location Right)
		(InputLoadLow )
		(InputLoadHigh )
		(OutputLoadLow )
		(OutputLoadHigh )
		(CheckLoad Off)
		(CheckIO Off)
		(CheckDir 0)
		(CheckAssert 0)
		(CheckOutput 0)
		(UnknownLoading 0)
	)

	(Pin
		(Name B)
		(MSB )
		(LSB )
		(Type UNSPEC)
		(Location Right)
		(InputLoadLow )
		(InputLoadHigh )
		(OutputLoadLow )
		(OutputLoadHigh )
		(CheckLoad Off)
		(CheckIO Off)
		(CheckDir 0)
		(CheckAssert 0)
		(CheckOutput 0)
		(UnknownLoading 0)
	)

	(Pin
		(Name A)
		(MSB )
		(LSB )
		(Type UNSPEC)
		(Location Right)
		(InputLoadLow )
		(InputLoadHigh )
		(OutputLoadLow )
		(OutputLoadHigh )
		(CheckLoad Off)
		(CheckIO Off)
		(CheckDir 0)
		(CheckAssert 0)
		(CheckOutput 0)
		(UnknownLoading 0)
	)

)
