uob-hep-cad/uob-hep-pc072/hardware/Cadence/top/archive_libs/oxflib/08_#20timing__arc/sch_1/page1.csv

FILE_TYPE = CONNECTIVITY
{Allegro Design Entry HDL 17.4-2019 S011 (3890763) 9/18/2020}
PAGE_NUMBER = 1
0"NC"
1"GND\G"
2"P2V5\g"
3"GND\G"
4"P2V5\g"
5"GND\G"
6"P2V5\g"
7"GND\G"
8"P2V5\g"
9"GND\G"
10"P2V5\g"
11"P2V5\g"
12"P2V5\g"
13"P2V5\g"
14"GND\g"
15"GND\g"
16"GND\g"
17"GND\g"
18"P2V5\g"
19"GND\g"
20"GND\g"
21"GND\g"
22"P2V5\g"
23"P2V5\g"
24"P2V5\g"
25"P2V5\g"
26"GND\g"
27"GND\g"
28"GND\g"
29"GND\g"
30"P2V5\g"
31"GND\g"
32"GND\g"
33"GND\g"
34"P2V5\g"
35"P2V5\g"
36"P2V5\g"
37"GND\g"
38"GND\g"
39"P2V5\g"
40"GND\g"
41"P2V5\g"
42"P2V5\g"
43"GND\g"
44"GND\g"
45"GND\g"
46"GND\g"
47"P2V5\g"
48"GND\g"
49"GND\g"
50"GND\g"
51"GND\G"
52"SFP_DATA_IO<11..0>"
53"UPSTREAM_DATA_N<2..0>"
54"UN$1$r$I567$2"
55"UPSTREAM_DATA_P<1>"
56"UPSTREAM_DATA_N<1>"
57"DFF_REF_CLK_P<1>"
58"DFF_REF_CLK_N<1>"
59"UN$1$MAX9381ESA$I649$Q$1"
60"UN$1$MAX9381ESA$I649$Q"
61"DFF_CLK_N<1>"
62"DFF_CLK_P<1>"
63"UDATA_IN_N<1>"
64"UDATA_IN_P<1>"
65"DFF_CLK_N<0>"
66"DFF_CLK_P<0>"
67"DFF_REF_CLK_P<0>"
68"DFF_REF_CLK_N<0>"
69"UDATA_IN_P<0>"
70"UDATA_IN_N<0>"
71"UN$1$MAX9381ESA$I578$Q$1"
72"UN$1$MAX9381ESA$I578$Q"
73"SFP.TD_N<0>"
74"SFP_DATA_OUT_N<0>"
75"SFP.TD_P<2>"
76"SFP.TD_N<2>"
77"SFP2_CLKGEN_N"
78"SFP_DATA_OUT_N<2>"
79"UN$1$MAX9381ESA$I618$Q"
80"UN$1$MAX9381ESA$I618$Q$1"
81"SFP.TD_N<1>"
82"SFP.TD_P<1>"
83"SFP.TD_P<0>"
84"DFF_CLK_N<2>"
85"DFF_CLK_P<2>"
86"UDATA_IN_P<2>"
87"UN$1$SY58608U$I571$VREF"
88"UN$1$r$I575$2"
89"SFP.RD_P<1>"
90"UN$1$SY58608U$I557$VREF"
91"SFP1_CLKGEN_N"
92"UN$1$r$I559$2"
93"UDATA_IN_N<2>"
94"UPSTREAM_DATA_P<2..0>"
95"SFP2_CLKGEN_P"
96"DFF_REF_CLK_N<2>"
97"DFF_REF_CLK_P<2>"
98"SFP_DATA_OUT_N<2..0>"
99"SFP_DATA_OUT_P<2..0>"
100"UN$1$r$I574$2"
101"SFP_DATA_OUT_P<2>"
102"UPSTREAM_DATA_P<2>"
103"SFP_DATA_OUT_P<0>"
104"UN$1$r$I568$2"
105"UN$1$SY58608U$I564$VREF"
106"SFP.RD_N<1>"
107"SFP.RD_P<2>"
108"UN$1$r$I558$2"
109"SFP0_CLKGEN_P"
110"SFP0_CLKGEN_N"
111"SFP_DATA_OUT_P<1>"
112"SFP.RD_N<0>"
113"SFP.RD_P<0>"
114"SFP.RD_N<2>"
115"UPSTREAM_DATA_P<0>"
116"SFP1_CLKGEN_P"
117"SFP_DATA_OUT_N<1>"
118"UPSTREAM_DATA_N<0>"
119"UPSTREAM_DATA_N<2>"
%"gnd"
1,"(9500,-6675)","0","mtca_interface_board","141P"
CDS_LIB"mtca_interface_board"
HDL_POWER"GND"
ROOM"SFP_DFF_AND_FANOUT"
HOTSPOT_051
%"SY58608U"
1,"(11025,-5850)","0","cninterface","I557"
TYPE"SY58608UMG"
PACK_TYPE"QFN"
POWER_GROUP"VCC=P2V5"
CDS_LIB"cninterface"
ROOM"SFP_DFF_AND_FANOUT"
IN* \B108
VREF-AC90
IN92
Q0109
Q1103
Q0* \B110
Q1* \B74
VT90
%"r"
1,"(10400,-5950)","3","discrete","I558"
VALUE"0"
$LOCATION"R35"
SEC"1"
PART_NUMBER"EMA-00007500V42"
PART_TYPE"Thick Film"
DESCRIPTION"RES, Thick Film, 0, Jumper, 1/10W, SMD, 0402"
POWER"1/10W"
TOLERANCE"Jumper"
MPN"ERJ-2GE0R00X"
MANUFACTURER"Panasonic"
DISTRIBUTOR_PARTNUMBER"P0.0JTR-ND"
SOURCE_PACKAGE"R"
DATASHEET"C:\EMA\CISQuickStart\Technical_Datasheets\Panasonic\AOA0000CE1.PDF"
DISTRIBUTOR"Digikey"
JEDEC_TYPE"res0402"
CDS_LOCATION"R35"
CDS_LIB"discrete"
ROOM"SFP_DFF_AND_FANOUT"
1
$PN"1"112
2
$PN"2"108
%"r"
1,"(10425,-5750)","1","discrete","I559"
$LOCATION"R36"
VALUE"0"
DESCRIPTION"RES, Thick Film, 0, Jumper, 1/10W, SMD, 0402"
POWER"1/10W"
TOLERANCE"Jumper"
MPN"ERJ-2GE0R00X"
MANUFACTURER"Panasonic"
DISTRIBUTOR_PARTNUMBER"P0.0JTR-ND"
DISTRIBUTOR"Digikey"
DATASHEET"C:\EMA\CISQuickStart\Technical_Datasheets\Panasonic\AOA0000CE1.PDF"
SEC"1"
PART_NUMBER"EMA-00007500V42"
PART_TYPE"Thick Film"
SOURCE_PACKAGE"R"
CDS_LOCATION"R36"
CDS_LIB"discrete"
JEDEC_TYPE"res0402"
ROOM"SFP_DFF_AND_FANOUT"
1
$PN"1"113
2
$PN"2"92
%"gnd"
1,"(10650,-6450)","0","mtca_interface_board","I561"
CDS_LIB"mtca_interface_board"
HDL_POWER"GND"
ROOM"SFP_DFF_AND_FANOUT"
HOTSPOT_050
%"SY58608U"
1,"(11050,-6750)","0","cninterface","I564"
PACK_TYPE"QFN"
TYPE"SY58608UMG"
POWER_GROUP"VCC=P2V5"
CDS_LIB"cninterface"
ROOM"SFP_DFF_AND_FANOUT"
IN* \B54
VREF-AC105
IN104
Q0116
Q1111
Q0* \B91
Q1* \B117
VT105
%"gnd"
1,"(10675,-7350)","0","mtca_interface_board","I566"
CDS_LIB"mtca_interface_board"
HDL_POWER"GND"
ROOM"SFP_DFF_AND_FANOUT"
HOTSPOT_049
%"r"
1,"(10425,-6850)","3","discrete","I567"
VALUE"0"
SEC"1"
TOLERANCE"Jumper"
POWER"1/10W"
DESCRIPTION"RES, Thick Film, 0, Jumper, 1/10W, SMD, 0402"
PART_TYPE"Thick Film"
PART_NUMBER"EMA-00007500V42"
MPN"ERJ-2GE0R00X"
MANUFACTURER"Panasonic"
DISTRIBUTOR_PARTNUMBER"P0.0JTR-ND"
DISTRIBUTOR"Digikey"
DATASHEET"C:\EMA\CISQuickStart\Technical_Datasheets\Panasonic\AOA0000CE1.PDF"
CDS_LIB"discrete"
SOURCE_PACKAGE"R"
JEDEC_TYPE"res0402"
ROOM"SFP_DFF_AND_FANOUT"
1
$PN"1"106
2
$PN"2"54
%"r"
1,"(10450,-6650)","1","discrete","I568"
VALUE"0"
DISTRIBUTOR_PARTNUMBER"P0.0JTR-ND"
MANUFACTURER"Panasonic"
DISTRIBUTOR"Digikey"
DATASHEET"C:\EMA\CISQuickStart\Technical_Datasheets\Panasonic\AOA0000CE1.PDF"
SEC"1"
PART_TYPE"Thick Film"
DESCRIPTION"RES, Thick Film, 0, Jumper, 1/10W, SMD, 0402"
POWER"1/10W"
TOLERANCE"Jumper"
MPN"ERJ-2GE0R00X"
CDS_LIB"discrete"
PART_NUMBER"EMA-00007500V42"
SOURCE_PACKAGE"R"
JEDEC_TYPE"res0402"
ROOM"SFP_DFF_AND_FANOUT"
1
$PN"1"89
2
$PN"2"104
%"SY58608U"
1,"(11125,-7650)","0","cninterface","I571"
POWER_GROUP"VCC=P2V5"
PACK_TYPE"QFN"
TYPE"SY58608UMG"
CDS_LIB"cninterface"
ROOM"SFP_DFF_AND_FANOUT"
IN* \B100
VREF-AC87
IN88
Q095
Q1101
Q0* \B77
Q1* \B78
VT87
%"gnd"
1,"(10750,-8250)","0","mtca_interface_board","I573"
CDS_LIB"mtca_interface_board"
HDL_POWER"GND"
ROOM"SFP_DFF_AND_FANOUT"
HOTSPOT_048
%"r"
1,"(10500,-7750)","3","discrete","I574"
VALUE"0"
ROOM"SFP_DFF_AND_FANOUT"
CDS_LIB"discrete"
JEDEC_TYPE"res0402"
SOURCE_PACKAGE"R"
DATASHEET"C:\EMA\CISQuickStart\Technical_Datasheets\Panasonic\AOA0000CE1.PDF"
DISTRIBUTOR"Digikey"
DISTRIBUTOR_PARTNUMBER"P0.0JTR-ND"
TOLERANCE"Jumper"
MPN"ERJ-2GE0R00X"
MANUFACTURER"Panasonic"
POWER"1/10W"
DESCRIPTION"RES, Thick Film, 0, Jumper, 1/10W, SMD, 0402"
SEC"1"
PART_NUMBER"EMA-00007500V42"
PART_TYPE"Thick Film"
1
$PN"1"114
2
$PN"2"100
%"r"
1,"(10525,-7550)","1","discrete","I575"
VALUE"0"
SEC"1"
DATASHEET"C:\EMA\CISQuickStart\Technical_Datasheets\Panasonic\AOA0000CE1.PDF"
DISTRIBUTOR"Digikey"
DISTRIBUTOR_PARTNUMBER"P0.0JTR-ND"
MANUFACTURER"Panasonic"
MPN"ERJ-2GE0R00X"
TOLERANCE"Jumper"
CDS_LIB"discrete"
PART_NUMBER"EMA-00007500V42"
PART_TYPE"Thick Film"
DESCRIPTION"RES, Thick Film, 0, Jumper, 1/10W, SMD, 0402"
POWER"1/10W"
JEDEC_TYPE"res0402"
SOURCE_PACKAGE"R"
ROOM"SFP_DFF_AND_FANOUT"
1
$PN"1"107
2
$PN"2"88
%"MAX9381ESA"
1,"(15000,-6475)","0","bris_cds_logic","I578"
VALUE"MAX9381ESA"
CDS_LIB"bris_cds_logic"
CDS_LMAN_SYM_OUTLINE"-465,400,480,-300"
PACK_TYPE"SMD"
C"COPYRIGHT (C) 2015 ACCELERATED DESIGNS. ALL RIGHTS RESERVED"
ROOM"SFP_DFF_AND_FANOUT"
VCC
$PN"?"47
Q
$PN"?"71
VEE
$PN"?"46
CLK
$PN"?"66
D
$PN"?"69
D* \B
$PN"?"70
CLK* \B
$PN"?"65
Q* \B
$PN"?"72
%"P2V5"
1,"(15000,-5925)","0","cnpower","I579"
SIZE"1B"
CDS_LIB"cnpower"
BODY_TYPE"PLUMBING"
HDL_POWER"P2V5"
ROOM"SFP_DFF_AND_FANOUT"
A<SIZE-1..0>\NAC
VHDL_INIT"1"47
%"gnd"
1,"(14950,-7000)","0","mtca_interface_board","I580"
CDS_LIB"mtca_interface_board"
HDL_POWER"GND"
ROOM"SFP_DFF_AND_FANOUT"
HOTSPOT_046
%"r"
1,"(15825,-6825)","4","discrete","I581"
VALUE"100"
SEC"1"
REUSE_ANNOTATE"TRUE"
PART_NUMBER"ERJ-2RKF1000X"
PART_TYPE"Thick Film"
DESCRIPTION"RES SMD 100 OHM 1% 1/10W 0402"
POWER"1/10W"
MANUFACTURER"Panasonic"
MPN"ERJ-2RKF1000X"
TOLERANCE"1%"
DISTRIBUTOR_PARTNUMBER"P100LCT-ND"
DISTRIBUTOR"Digikey"
DATASHEET"C:\EMA\CISQuickStart\Technical_Datasheets\Panasonic\AOA0000CE2.PDF"
SOURCE_PACKAGE"R"
JEDEC_TYPE"res0402"
CDS_LIB"discrete"
ROOM"SFP_DFF_AND_FANOUT"
1
$PN"1"45
2
$PN"2"72
%"gnd"
1,"(15775,-6975)","0","mtca_interface_board","I582"
CDS_LIB"mtca_interface_board"
HDL_POWER"GND"
ROOM"SFP_DFF_AND_FANOUT"
HOTSPOT_045
%"r"
1,"(16100,-6825)","4","discrete","I583"
VALUE"100"
SEC"1"
REUSE_ANNOTATE"TRUE"
PART_NUMBER"ERJ-2RKF1000X"
PART_TYPE"Thick Film"
POWER"1/10W"
TOLERANCE"1%"
MPN"ERJ-2RKF1000X"
MANUFACTURER"Panasonic"
DESCRIPTION"RES SMD 100 OHM 1% 1/10W 0402"
DISTRIBUTOR_PARTNUMBER"P100LCT-ND"
DISTRIBUTOR"Digikey"
DATASHEET"C:\EMA\CISQuickStart\Technical_Datasheets\Panasonic\AOA0000CE2.PDF"
SOURCE_PACKAGE"R"
JEDEC_TYPE"res0402"
CDS_LIB"discrete"
ROOM"SFP_DFF_AND_FANOUT"
1
$PN"1"44
2
$PN"2"71
%"gnd"
1,"(16050,-6975)","0","mtca_interface_board","I584"
CDS_LIB"mtca_interface_board"
HDL_POWER"GND"
ROOM"SFP_DFF_AND_FANOUT"
HOTSPOT_044
%"r"
1,"(13875,-6500)","5","discrete","I587"
VALUE"100"
SEC"1"
REUSE_ANNOTATE"TRUE"
PART_NUMBER"ERJ-2RKF1000X"
PART_TYPE"Thick Film"
DESCRIPTION"RES SMD 100 OHM 1% 1/10W 0402"
POWER"1/10W"
TOLERANCE"1%"
MPN"ERJ-2RKF1000X"
MANUFACTURER"Panasonic"
DISTRIBUTOR_PARTNUMBER"P100LCT-ND"
DISTRIBUTOR"Digikey"
DATASHEET"C:\EMA\CISQuickStart\Technical_Datasheets\Panasonic\AOA0000CE2.PDF"
SOURCE_PACKAGE"R"
JEDEC_TYPE"res0402"
CDS_LIB"discrete"
ROOM"SFP_DFF_AND_FANOUT"
1
$PN"1"70
2
$PN"2"69
%"gnd"
1,"(14000,-6175)","0","mtca_interface_board","I590"
CDS_LIB"mtca_interface_board"
HDL_POWER"GND"
ROOM"SFP_DFF_AND_FANOUT"
HOTSPOT_043
%"P2V5"
1,"(13300,-6050)","0","cnpower","I591"
CDS_LIB"cnpower"
SIZE"1B"
BODY_TYPE"PLUMBING"
HDL_POWER"P2V5"
ROOM"SFP_DFF_AND_FANOUT"
A<SIZE-1..0>\NAC
VHDL_INIT"1"42
%"P2V5"
1,"(13250,-6575)","0","cnpower","I594"
SIZE"1B"
CDS_LIB"cnpower"
BODY_TYPE"PLUMBING"
HDL_POWER"P2V5"
ROOM"SFP_DFF_AND_FANOUT"
A<SIZE-1..0>\NAC
VHDL_INIT"1"41
%"gnd"
1,"(13950,-6700)","0","mtca_interface_board","I595"
CDS_LIB"mtca_interface_board"
HDL_POWER"GND"
ROOM"SFP_DFF_AND_FANOUT"
HOTSPOT_040
%"P2V5"
1,"(13250,-6850)","0","cnpower","I598"
CDS_LIB"cnpower"
SIZE"1B"
BODY_TYPE"PLUMBING"
HDL_POWER"P2V5"
ROOM"SFP_DFF_AND_FANOUT"
A<SIZE-1..0>\NAC
VHDL_INIT"1"39
%"gnd"
1,"(13950,-6975)","0","mtca_interface_board","I599"
CDS_LIB"mtca_interface_board"
HDL_POWER"GND"
ROOM"SFP_DFF_AND_FANOUT"
HOTSPOT_038
%"gnd"
1,"(13900,-7500)","0","mtca_interface_board","I600"
CDS_LIB"mtca_interface_board"
HDL_POWER"GND"
ROOM"SFP_DFF_AND_FANOUT"
HOTSPOT_037
%"r"
1,"(13825,-7275)","5","discrete","I601"
VALUE"100"
CDS_LIB"discrete"
JEDEC_TYPE"res0402"
SOURCE_PACKAGE"R"
DATASHEET"C:\EMA\CISQuickStart\Technical_Datasheets\Panasonic\AOA0000CE2.PDF"
DISTRIBUTOR"Digikey"
MANUFACTURER"Panasonic"
DISTRIBUTOR_PARTNUMBER"P100LCT-ND"
MPN"ERJ-2RKF1000X"
TOLERANCE"1%"
POWER"1/10W"
PART_NUMBER"ERJ-2RKF1000X"
PART_TYPE"Thick Film"
DESCRIPTION"RES SMD 100 OHM 1% 1/10W 0402"
SEC"1"
REUSE_ANNOTATE"TRUE"
ROOM"SFP_DFF_AND_FANOUT"
1
$PN"1"65
2
$PN"2"66
%"P2V5"
1,"(13200,-7375)","0","cnpower","I603"
CDS_LIB"cnpower"
SIZE"1B"
BODY_TYPE"PLUMBING"
HDL_POWER"P2V5"
ROOM"SFP_DFF_AND_FANOUT"
A<SIZE-1..0>\NAC
VHDL_INIT"1"36
%"P2V5"
1,"(9550,-6150)","0","cnpower","I609"
SIZE"1B"
CDS_LIB"cnpower"
BODY_TYPE"PLUMBING"
HDL_POWER"P2V5"
ROOM"SFP_DFF_AND_FANOUT"
A<SIZE-1..0>\NAC
VHDL_INIT"1"35
%"P2V5"
1,"(14925,-7525)","0","cnpower","I612"
SIZE"1B"
CDS_LIB"cnpower"
BODY_TYPE"PLUMBING"
HDL_POWER"P2V5"
ROOM"SFP_DFF_AND_FANOUT"
A<SIZE-1..0>\NAC
VHDL_INIT"1"34
%"r"
1,"(16025,-8425)","4","discrete","I613"
VALUE"100"
PART_NUMBER"ERJ-2RKF1000X"
REUSE_ANNOTATE"TRUE"
SEC"1"
DESCRIPTION"RES SMD 100 OHM 1% 1/10W 0402"
PART_TYPE"Thick Film"
MPN"ERJ-2RKF1000X"
TOLERANCE"1%"
POWER"1/10W"
SOURCE_PACKAGE"R"
DATASHEET"C:\EMA\CISQuickStart\Technical_Datasheets\Panasonic\AOA0000CE2.PDF"
DISTRIBUTOR"Digikey"
DISTRIBUTOR_PARTNUMBER"P100LCT-ND"
MANUFACTURER"Panasonic"
JEDEC_TYPE"res0402"
CDS_LIB"discrete"
ROOM"SFP_DFF_AND_FANOUT"
1
$PN"1"33
2
$PN"2"79
%"gnd"
1,"(15975,-8575)","0","mtca_interface_board","I614"
CDS_LIB"mtca_interface_board"
HDL_POWER"GND"
ROOM"SFP_DFF_AND_FANOUT"
HOTSPOT_033
%"r"
1,"(15750,-8425)","4","discrete","I615"
VALUE"100"
PART_NUMBER"ERJ-2RKF1000X"
REUSE_ANNOTATE"TRUE"
SEC"1"
TOLERANCE"1%"
POWER"1/10W"
DESCRIPTION"RES SMD 100 OHM 1% 1/10W 0402"
MPN"ERJ-2RKF1000X"
PART_TYPE"Thick Film"
SOURCE_PACKAGE"R"
DISTRIBUTOR"Digikey"
DISTRIBUTOR_PARTNUMBER"P100LCT-ND"
MANUFACTURER"Panasonic"
DATASHEET"C:\EMA\CISQuickStart\Technical_Datasheets\Panasonic\AOA0000CE2.PDF"
CDS_LIB"discrete"
JEDEC_TYPE"res0402"
ROOM"SFP_DFF_AND_FANOUT"
1
$PN"1"32
2
$PN"2"80
%"gnd"
1,"(15700,-8575)","0","mtca_interface_board","I616"
CDS_LIB"mtca_interface_board"
HDL_POWER"GND"
ROOM"SFP_DFF_AND_FANOUT"
HOTSPOT_032
%"gnd"
1,"(14875,-8600)","0","mtca_interface_board","I617"
CDS_LIB"mtca_interface_board"
HDL_POWER"GND"
ROOM"SFP_DFF_AND_FANOUT"
HOTSPOT_031
%"MAX9381ESA"
1,"(14925,-8075)","0","bris_cds_logic","I618"
VALUE"MAX9381ESA"
CDS_LMAN_SYM_OUTLINE"-465,400,480,-300"
CDS_LIB"bris_cds_logic"
PACK_TYPE"SMD"
C"COPYRIGHT (C) 2015 ACCELERATED DESIGNS. ALL RIGHTS RESERVED"
ROOM"SFP_DFF_AND_FANOUT"
VCC
$PN"?"34
Q
$PN"?"79
VEE
$PN"?"31
CLK
$PN"?"62
D
$PN"?"64
D* \B
$PN"?"63
CLK* \B
$PN"?"61
Q* \B
$PN"?"80
%"P2V5"
1,"(13225,-7650)","0","cnpower","I621"
SIZE"1B"
CDS_LIB"cnpower"
BODY_TYPE"PLUMBING"
HDL_POWER"P2V5"
ROOM"SFP_DFF_AND_FANOUT"
A<SIZE-1..0>\NAC
VHDL_INIT"1"30
%"gnd"
1,"(13925,-7775)","0","mtca_interface_board","I622"
CDS_LIB"mtca_interface_board"
HDL_POWER"GND"
ROOM"SFP_DFF_AND_FANOUT"
HOTSPOT_029
%"gnd"
1,"(13875,-8300)","0","mtca_interface_board","I623"
CDS_LIB"mtca_interface_board"
HDL_POWER"GND"
ROOM"SFP_DFF_AND_FANOUT"
HOTSPOT_028
%"gnd"
1,"(13875,-8575)","0","mtca_interface_board","I624"
CDS_LIB"mtca_interface_board"
HDL_POWER"GND"
ROOM"SFP_DFF_AND_FANOUT"
HOTSPOT_027
%"r"
1,"(13800,-8075)","5","discrete","I625"
VALUE"100"
CDS_LIB"discrete"
JEDEC_TYPE"res0402"
SOURCE_PACKAGE"R"
DATASHEET"C:\EMA\CISQuickStart\Technical_Datasheets\Panasonic\AOA0000CE2.PDF"
DISTRIBUTOR"Digikey"
MANUFACTURER"Panasonic"
DISTRIBUTOR_PARTNUMBER"P100LCT-ND"
MPN"ERJ-2RKF1000X"
TOLERANCE"1%"
POWER"1/10W"
PART_TYPE"Thick Film"
DESCRIPTION"RES SMD 100 OHM 1% 1/10W 0402"
REUSE_ANNOTATE"TRUE"
SEC"1"
PART_NUMBER"ERJ-2RKF1000X"
ROOM"SFP_DFF_AND_FANOUT"
1
$PN"1"63
2
$PN"2"64
%"gnd"
1,"(13825,-9100)","0","mtca_interface_board","I628"
CDS_LIB"mtca_interface_board"
HDL_POWER"GND"
ROOM"SFP_DFF_AND_FANOUT"
HOTSPOT_026
%"r"
1,"(13750,-8875)","5","discrete","I629"
VALUE"100"
CDS_LIB"discrete"
JEDEC_TYPE"res0402"
SOURCE_PACKAGE"R"
DATASHEET"C:\EMA\CISQuickStart\Technical_Datasheets\Panasonic\AOA0000CE2.PDF"
DISTRIBUTOR"Digikey"
DISTRIBUTOR_PARTNUMBER"P100LCT-ND"
DESCRIPTION"RES SMD 100 OHM 1% 1/10W 0402"
MANUFACTURER"Panasonic"
MPN"ERJ-2RKF1000X"
TOLERANCE"1%"
POWER"1/10W"
PART_NUMBER"ERJ-2RKF1000X"
REUSE_ANNOTATE"TRUE"
PART_TYPE"Thick Film"
SEC"1"
ROOM"SFP_DFF_AND_FANOUT"
1
$PN"1"61
2
$PN"2"62
%"P2V5"
1,"(13175,-8175)","0","cnpower","I632"
CDS_LIB"cnpower"
SIZE"1B"
BODY_TYPE"PLUMBING"
HDL_POWER"P2V5"
ROOM"SFP_DFF_AND_FANOUT"
A<SIZE-1..0>\NAC
VHDL_INIT"1"25
%"P2V5"
1,"(13175,-8450)","0","cnpower","I635"
SIZE"1B"
CDS_LIB"cnpower"
BODY_TYPE"PLUMBING"
HDL_POWER"P2V5"
ROOM"SFP_DFF_AND_FANOUT"
A<SIZE-1..0>\NAC
VHDL_INIT"1"24
%"P2V5"
1,"(13125,-8975)","0","cnpower","I640"
SIZE"1B"
CDS_LIB"cnpower"
BODY_TYPE"PLUMBING"
HDL_POWER"P2V5"
ROOM"SFP_DFF_AND_FANOUT"
A<SIZE-1..0>\NAC
VHDL_INIT"1"23
%"P2V5"
1,"(12075,-8950)","0","cnpower","I643"
CDS_LIB"cnpower"
SIZE"1B"
BODY_TYPE"PLUMBING"
HDL_POWER"P2V5"
ROOM"SFP_DFF_AND_FANOUT"
A<SIZE-1..0>\NAC
VHDL_INIT"1"22
%"r"
1,"(12950,-9850)","4","discrete","I644"
VALUE"100"
SEC"1"
REUSE_ANNOTATE"TRUE"
PART_NUMBER"ERJ-2RKF1000X"
PART_TYPE"Thick Film"
DESCRIPTION"RES SMD 100 OHM 1% 1/10W 0402"
POWER"1/10W"
TOLERANCE"1%"
MPN"ERJ-2RKF1000X"
MANUFACTURER"Panasonic"
DISTRIBUTOR_PARTNUMBER"P100LCT-ND"
DISTRIBUTOR"Digikey"
DATASHEET"C:\EMA\CISQuickStart\Technical_Datasheets\Panasonic\AOA0000CE2.PDF"
SOURCE_PACKAGE"R"
JEDEC_TYPE"res0402"
CDS_LIB"discrete"
ROOM"SFP_DFF_AND_FANOUT"
1
$PN"1"21
2
$PN"2"59
%"gnd"
1,"(12900,-10000)","0","mtca_interface_board","I645"
CDS_LIB"mtca_interface_board"
HDL_POWER"GND"
ROOM"SFP_DFF_AND_FANOUT"
HOTSPOT_021
%"r"
1,"(12675,-9850)","4","discrete","I646"
VALUE"100"
PART_TYPE"Thick Film"
DESCRIPTION"RES SMD 100 OHM 1% 1/10W 0402"
PART_NUMBER"ERJ-2RKF1000X"
REUSE_ANNOTATE"TRUE"
SEC"1"
POWER"1/10W"
TOLERANCE"1%"
MPN"ERJ-2RKF1000X"
MANUFACTURER"Panasonic"
DISTRIBUTOR_PARTNUMBER"P100LCT-ND"
DISTRIBUTOR"Digikey"
DATASHEET"C:\EMA\CISQuickStart\Technical_Datasheets\Panasonic\AOA0000CE2.PDF"
SOURCE_PACKAGE"R"
JEDEC_TYPE"res0402"
CDS_LIB"discrete"
ROOM"SFP_DFF_AND_FANOUT"
1
$PN"1"20
2
$PN"2"60
%"gnd"
1,"(12625,-10000)","0","mtca_interface_board","I647"
CDS_LIB"mtca_interface_board"
HDL_POWER"GND"
ROOM"SFP_DFF_AND_FANOUT"
HOTSPOT_020
%"gnd"
1,"(12025,-10025)","0","mtca_interface_board","I648"
CDS_LIB"mtca_interface_board"
HDL_POWER"GND"
ROOM"SFP_DFF_AND_FANOUT"
HOTSPOT_019
%"MAX9381ESA"
1,"(12075,-9500)","0","bris_cds_logic","I649"
VALUE"MAX9381ESA"
CDS_LMAN_SYM_OUTLINE"-465,400,480,-300"
CDS_LIB"bris_cds_logic"
PACK_TYPE"SMD"
C"COPYRIGHT (C) 2015 ACCELERATED DESIGNS. ALL RIGHTS RESERVED"
ROOM"SFP_DFF_AND_FANOUT"
VCC
$PN"?"22
Q
$PN"?"59
VEE
$PN"?"19
CLK
$PN"?"85
D
$PN"?"86
D* \B
$PN"?"93
CLK* \B
$PN"?"84
Q* \B
$PN"?"60
%"P2V5"
1,"(10375,-9075)","0","cnpower","I652"
SIZE"1B"
CDS_LIB"cnpower"
BODY_TYPE"PLUMBING"
HDL_POWER"P2V5"
ROOM"SFP_DFF_AND_FANOUT"
A<SIZE-1..0>\NAC
VHDL_INIT"1"18
%"gnd"
1,"(11075,-9200)","0","mtca_interface_board","I653"
CDS_LIB"mtca_interface_board"
HDL_POWER"GND"
ROOM"SFP_DFF_AND_FANOUT"
HOTSPOT_017
%"gnd"
1,"(11025,-9725)","0","mtca_interface_board","I654"
CDS_LIB"mtca_interface_board"
HDL_POWER"GND"
ROOM"SFP_DFF_AND_FANOUT"
HOTSPOT_016
%"gnd"
1,"(11025,-10000)","0","mtca_interface_board","I655"
CDS_LIB"mtca_interface_board"
HDL_POWER"GND"
ROOM"SFP_DFF_AND_FANOUT"
HOTSPOT_015
%"r"
1,"(10950,-9500)","5","discrete","I656"
VALUE"100"
CDS_LIB"discrete"
JEDEC_TYPE"res0402"
SOURCE_PACKAGE"R"
DATASHEET"C:\EMA\CISQuickStart\Technical_Datasheets\Panasonic\AOA0000CE2.PDF"
DISTRIBUTOR_PARTNUMBER"P100LCT-ND"
DISTRIBUTOR"Digikey"
MANUFACTURER"Panasonic"
MPN"ERJ-2RKF1000X"
TOLERANCE"1%"
DESCRIPTION"RES SMD 100 OHM 1% 1/10W 0402"
PART_TYPE"Thick Film"
POWER"1/10W"
SEC"1"
REUSE_ANNOTATE"TRUE"
PART_NUMBER"ERJ-2RKF1000X"
ROOM"SFP_DFF_AND_FANOUT"
1
$PN"1"93
2
$PN"2"86
%"gnd"
1,"(10975,-10525)","0","mtca_interface_board","I659"
CDS_LIB"mtca_interface_board"
HDL_POWER"GND"
ROOM"SFP_DFF_AND_FANOUT"
HOTSPOT_014
%"r"
1,"(10900,-10300)","5","discrete","I660"
$LOCATION"R134"
VALUE"100"
CDS_LIB"discrete"
CDS_LOCATION"R134"
JEDEC_TYPE"res0402"
SOURCE_PACKAGE"R"
DATASHEET"C:\EMA\CISQuickStart\Technical_Datasheets\Panasonic\AOA0000CE2.PDF"
DISTRIBUTOR"Digikey"
DISTRIBUTOR_PARTNUMBER"P100LCT-ND"
MANUFACTURER"Panasonic"
MPN"ERJ-2RKF1000X"
DESCRIPTION"RES SMD 100 OHM 1% 1/10W 0402"
TOLERANCE"1%"
POWER"1/10W"
PART_TYPE"Thick Film"
PART_NUMBER"ERJ-2RKF1000X"
REUSE_ANNOTATE"TRUE"
SEC"1"
ROOM"SFP_DFF_AND_FANOUT"
1
$PN"1"84
2
$PN"2"85
%"P2V5"
1,"(10325,-9600)","0","cnpower","I663"
SIZE"1B"
CDS_LIB"cnpower"
BODY_TYPE"PLUMBING"
HDL_POWER"P2V5"
ROOM"SFP_DFF_AND_FANOUT"
A<SIZE-1..0>\NAC
VHDL_INIT"1"13
%"P2V5"
1,"(10325,-9875)","0","cnpower","I666"
CDS_LIB"cnpower"
SIZE"1B"
BODY_TYPE"PLUMBING"
HDL_POWER"P2V5"
ROOM"SFP_DFF_AND_FANOUT"
A<SIZE-1..0>\NAC
VHDL_INIT"1"12
%"P2V5"
1,"(10275,-10400)","0","cnpower","I671"
SIZE"1B"
CDS_LIB"cnpower"
BODY_TYPE"PLUMBING"
HDL_POWER"P2V5"
ROOM"SFP_DFF_AND_FANOUT"
A<SIZE-1..0>\NAC
VHDL_INIT"1"11
%"4 MERGE"
1,"(11325,-8600)","0","standard","I712"
CDS_LIB"standard"
NEEDS_NO_SIZE"TRUE"
BODY_TYPE"PLUMBING"
HDL_CONCAT"TRUE"
ROOM"SFP_DFF_AND_FANOUT"
A\NWC\NAC94
B\NWC\NAC53
C\NWC\NAC99
D\NWC\NAC98
Y\NWC\NAC52
%"IOPORT"
1,"(12100,-8600)","0","standard","I713"
CDS_LIB"standard"
OFFPAGE"TRUE"
ROOM"SFP_DFF_AND_FANOUT"
A
HDL_PORT"INOUT"
VHDL_PORT"INOUT"52
%"RSMD0402"
1,"(10475,-10475)","0","cnpassive","I726"
TOL"1%"
VALUE"1K"
SIZE"1B"
CDS_LIB"cnpassive"
PACK_TYPE"1/16W"
DIST"FLAT"
NEGTOL"RTOL%"
POSTOL"RTOL%"
TOL_ON_OFF"ON"
POWER"RMAX"
VOLTAGE"RVMAX"
SLOPE"RSMAX"
MAX_TEMP"RTMAX"
TC1"RTMPL"
TC2"RTMPQ"
ROOM"SFP_DFF_AND_FANOUT"
B <SIZE-1..0>\NAC84
A <SIZE-1..0>\NAC11
%"RSMD0402"
1,"(10900,-10475)","0","cnpassive","I727"
TOL"1%"
VALUE"2.2K"
CDS_LIB"cnpassive"
PACK_TYPE"1/16W"
SIZE"1B"
TOL_ON_OFF"ON"
POSTOL"RTOL%"
NEGTOL"RTOL%"
DIST"FLAT"
TC1"RTMPL"
MAX_TEMP"RTMAX"
SLOPE"RSMAX"
VOLTAGE"RVMAX"
POWER"RMAX"
TC2"RTMPQ"
ROOM"SFP_DFF_AND_FANOUT"
B <SIZE-1..0>\NAC14
A <SIZE-1..0>\NAC84
%"RSMD0402"
1,"(10950,-9950)","0","cnpassive","I728"
TOL"1%"
VALUE"2.2K"
CDS_LIB"cnpassive"
PACK_TYPE"1/16W"
SIZE"1B"
TC2"RTMPQ"
TC1"RTMPL"
POWER"RMAX"
DIST"FLAT"
NEGTOL"RTOL%"
POSTOL"RTOL%"
TOL_ON_OFF"ON"
VOLTAGE"RVMAX"
SLOPE"RSMAX"
MAX_TEMP"RTMAX"
ROOM"SFP_DFF_AND_FANOUT"
B <SIZE-1..0>\NAC15
A <SIZE-1..0>\NAC85
%"RSMD0402"
1,"(10950,-9675)","0","cnpassive","I729"
VALUE"2.2K"
TOL"1%"
CDS_LIB"cnpassive"
SIZE"1B"
PACK_TYPE"1/16W"
TC2"RTMPQ"
TC1"RTMPL"
MAX_TEMP"RTMAX"
SLOPE"RSMAX"
POWER"RMAX"
DIST"FLAT"
NEGTOL"RTOL%"
POSTOL"RTOL%"
TOL_ON_OFF"ON"
VOLTAGE"RVMAX"
ROOM"SFP_DFF_AND_FANOUT"
B <SIZE-1..0>\NAC16
A <SIZE-1..0>\NAC93
%"RSMD0402"
1,"(11000,-9150)","0","cnpassive","I730"
VALUE"2.2K"
TOL"1%"
SIZE"1B"
CDS_LIB"cnpassive"
PACK_TYPE"1/16W"
TC2"RTMPQ"
TC1"RTMPL"
MAX_TEMP"RTMAX"
SLOPE"RSMAX"
VOLTAGE"RVMAX"
POWER"RMAX"
DIST"FLAT"
NEGTOL"RTOL%"
POSTOL"RTOL%"
TOL_ON_OFF"ON"
ROOM"SFP_DFF_AND_FANOUT"
B <SIZE-1..0>\NAC17
A <SIZE-1..0>\NAC86
%"RSMD0402"
1,"(10525,-9950)","0","cnpassive","I731"
VALUE"1K"
TOL"1%"
CDS_LIB"cnpassive"
SIZE"1B"
PACK_TYPE"1/16W"
TC2"RTMPQ"
TC1"RTMPL"
MAX_TEMP"RTMAX"
SLOPE"RSMAX"
VOLTAGE"RVMAX"
POWER"RMAX"
DIST"FLAT"
NEGTOL"RTOL%"
POSTOL"RTOL%"
TOL_ON_OFF"ON"
ROOM"SFP_DFF_AND_FANOUT"
B <SIZE-1..0>\NAC85
A <SIZE-1..0>\NAC12
%"RSMD0402"
1,"(10525,-9675)","0","cnpassive","I732"
TOL"1%"
VALUE"1K"
CDS_LIB"cnpassive"
SIZE"1B"
PACK_TYPE"1/16W"
POWER"RMAX"
DIST"FLAT"
NEGTOL"RTOL%"
POSTOL"RTOL%"
TOL_ON_OFF"ON"
TC2"RTMPQ"
TC1"RTMPL"
MAX_TEMP"RTMAX"
SLOPE"RSMAX"
VOLTAGE"RVMAX"
ROOM"SFP_DFF_AND_FANOUT"
B <SIZE-1..0>\NAC93
A <SIZE-1..0>\NAC13
%"RSMD0402"
1,"(10575,-9150)","0","cnpassive","I733"
TOL"1%"
VALUE"1K"
SIZE"1B"
CDS_LIB"cnpassive"
PACK_TYPE"1/16W"
TC2"RTMPQ"
TC1"RTMPL"
MAX_TEMP"RTMAX"
SLOPE"RSMAX"
VOLTAGE"RVMAX"
POWER"RMAX"
DIST"FLAT"
NEGTOL"RTOL%"
POSTOL"RTOL%"
TOL_ON_OFF"ON"
ROOM"SFP_DFF_AND_FANOUT"
B <SIZE-1..0>\NAC86
A <SIZE-1..0>\NAC18
%"RSMD0402"
1,"(13325,-9050)","0","cnpassive","I737"
TOL"1%"
VALUE"1K"
CDS_LIB"cnpassive"
SIZE"1B"
PACK_TYPE"1/16W"
DIST"FLAT"
NEGTOL"RTOL%"
POSTOL"RTOL%"
TOL_ON_OFF"ON"
POWER"RMAX"
TC2"RTMPQ"
TC1"RTMPL"
MAX_TEMP"RTMAX"
SLOPE"RSMAX"
VOLTAGE"RVMAX"
ROOM"SFP_DFF_AND_FANOUT"
B <SIZE-1..0>\NAC61
A <SIZE-1..0>\NAC23
%"RSMD0402"
1,"(13375,-8525)","0","cnpassive","I738"
VALUE"1K"
TOL"1%"
CDS_LIB"cnpassive"
SIZE"1B"
PACK_TYPE"1/16W"
POWER"RMAX"
DIST"FLAT"
NEGTOL"RTOL%"
POSTOL"RTOL%"
TOL_ON_OFF"ON"
TC2"RTMPQ"
TC1"RTMPL"
MAX_TEMP"RTMAX"
SLOPE"RSMAX"
VOLTAGE"RVMAX"
ROOM"SFP_DFF_AND_FANOUT"
B <SIZE-1..0>\NAC62
A <SIZE-1..0>\NAC24
%"RSMD0402"
1,"(13375,-8250)","0","cnpassive","I739"
VALUE"1K"
TOL"1%"
SIZE"1B"
PACK_TYPE"1/16W"
CDS_LIB"cnpassive"
TOL_ON_OFF"ON"
POSTOL"RTOL%"
NEGTOL"RTOL%"
DIST"FLAT"
POWER"RMAX"
VOLTAGE"RVMAX"
SLOPE"RSMAX"
MAX_TEMP"RTMAX"
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
DISTRIBUTOR"Digikey"
DISTRIBUTOR_PARTNUMBER"P0.0JTR-ND"
TOLERANCE"Jumper"
MPN"ERJ-2GE0R00X"
MANUFACTURER"Panasonic"
POWER"1/10W"
DESCRIPTION"RES, Thick Film, 0, Jumper, 1/10W, SMD, 0402"
SEC"1"
PART_NUMBER"EMA-00007500V42"
PART_TYPE"Thick Film"
1
$PN"1"60
2
$PN"2"76
%"r"
1,"(16250,-7975)","3","discrete","I798"
VALUE"0"
ROOM"SFP_DFF_AND_FANOUT"
CDS_LIB"discrete"
JEDEC_TYPE"res0402"
SOURCE_PACKAGE"R"
DATASHEET"C:\EMA\CISQuickStart\Technical_Datasheets\Panasonic\AOA0000CE1.PDF"
DISTRIBUTOR"Digikey"
DISTRIBUTOR_PARTNUMBER"P0.0JTR-ND"
TOLERANCE"Jumper"
MPN"ERJ-2GE0R00X"
MANUFACTURER"Panasonic"
POWER"1/10W"
DESCRIPTION"RES, Thick Film, 0, Jumper, 1/10W, SMD, 0402"
SEC"1"
PART_NUMBER"EMA-00007500V42"
PART_TYPE"Thick Film"
1
$PN"1"79
2
$PN"2"82
%"r"
1,"(16250,-8175)","3","discrete","I799"
VALUE"0"
PART_TYPE"Thick Film"
PART_NUMBER"EMA-00007500V42"
SEC"1"
DESCRIPTION"RES, Thick Film, 0, Jumper, 1/10W, SMD, 0402"
POWER"1/10W"
MANUFACTURER"Panasonic"
MPN"ERJ-2GE0R00X"
TOLERANCE"Jumper"
DISTRIBUTOR_PARTNUMBER"P0.0JTR-ND"
DISTRIBUTOR"Digikey"
DATASHEET"C:\EMA\CISQuickStart\Technical_Datasheets\Panasonic\AOA0000CE1.PDF"
SOURCE_PACKAGE"R"
JEDEC_TYPE"res0402"
CDS_LIB"discrete"
ROOM"SFP_DFF_AND_FANOUT"
1
$PN"1"80
2
$PN"2"81
%"r"
1,"(16300,-6375)","3","discrete","I800"
VALUE"0"
ROOM"SFP_DFF_AND_FANOUT"
CDS_LIB"discrete"
JEDEC_TYPE"res0402"
SOURCE_PACKAGE"R"
DATASHEET"C:\EMA\CISQuickStart\Technical_Datasheets\Panasonic\AOA0000CE1.PDF"
DISTRIBUTOR"Digikey"
DISTRIBUTOR_PARTNUMBER"P0.0JTR-ND"
TOLERANCE"Jumper"
MPN"ERJ-2GE0R00X"
MANUFACTURER"Panasonic"
POWER"1/10W"
DESCRIPTION"RES, Thick Film, 0, Jumper, 1/10W, SMD, 0402"
SEC"1"
PART_NUMBER"EMA-00007500V42"
PART_TYPE"Thick Film"
1
$PN"1"71
2
$PN"2"83
%"r"
1,"(16300,-6575)","3","discrete","I801"
VALUE"0"
PART_TYPE"Thick Film"
PART_NUMBER"EMA-00007500V42"
SEC"1"
DESCRIPTION"RES, Thick Film, 0, Jumper, 1/10W, SMD, 0402"
POWER"1/10W"
MANUFACTURER"Panasonic"
MPN"ERJ-2GE0R00X"
TOLERANCE"Jumper"
DISTRIBUTOR_PARTNUMBER"P0.0JTR-ND"
DISTRIBUTOR"Digikey"
DATASHEET"C:\EMA\CISQuickStart\Technical_Datasheets\Panasonic\AOA0000CE1.PDF"
SOURCE_PACKAGE"R"
JEDEC_TYPE"res0402"
CDS_LIB"discrete"
ROOM"SFP_DFF_AND_FANOUT"
1
$PN"1"72
2
$PN"2"73
%"854S01I"
1,"(15075,-5175)","0","cninterface","I802"
PACK_TYPE"QFN"
TYPE"854S01AKILF"
HAS_FIXED_SIZE"2B"
CDS_LMAN_SYM_OUTLINE"-250,200,250,-200"
CDS_LIB"cninterface"
NPCLK<0>0
PCLK<0>0
PCLK<1>0
NPCLK<1>0
RESERVED0
CLK_SEL0
NQ0
Q0
%"74AVC1T45"
1,"(14400,-5100)","0","cninterface","I803"
PACK_TYPE"SC70"
TYPE"SN74AVC1T45DCK"
CDS_LIB"cninterface"
VCCA0
VCCB0
GND0
DIR0
B0
A0
END.
