uob-hep-cad/uob-hep-pc072/hardware/Cadence/cis_hep_partslib/cis_hep_partslib/Allegro_Library/symbols/HCCStar/HccStar_V1b/WideChip_pads.GIF

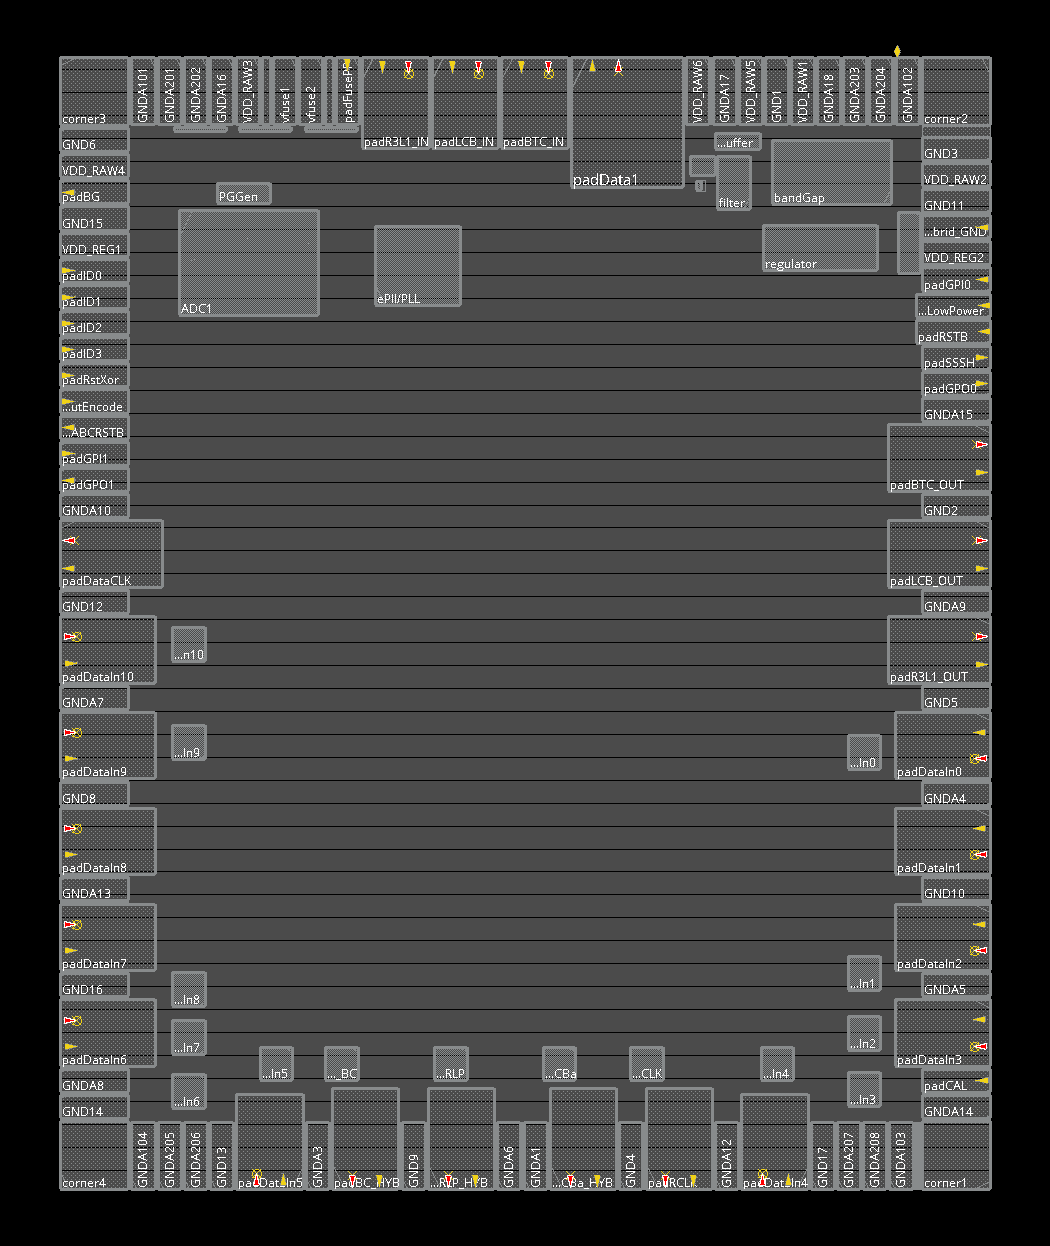
hardware/Cadence/cis_hep_partslib/cis_hep_partslib/Allegro_Library/symbols/HCCStar/HccStar_V1b/WideChip_pads.GIF
