uob-hep-cad/uob-hep-pc072/hardware/Cadence/cis_hep_partslib/cis_hep_partslib/DataSheets/virtex_ultrascale-hbm-fpga_B.png

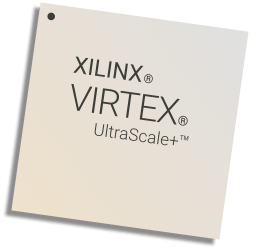
hardware/Cadence/cis_hep_partslib/cis_hep_partslib/DataSheets/virtex_ultrascale-hbm-fpga_B.png
