uob-hep-cad/uob-hep-pc072/hardware/Cadence/top/mtca_interface_board_reocc/mib_tongue2/physical/Screenshot 2025-02-21 143327.png

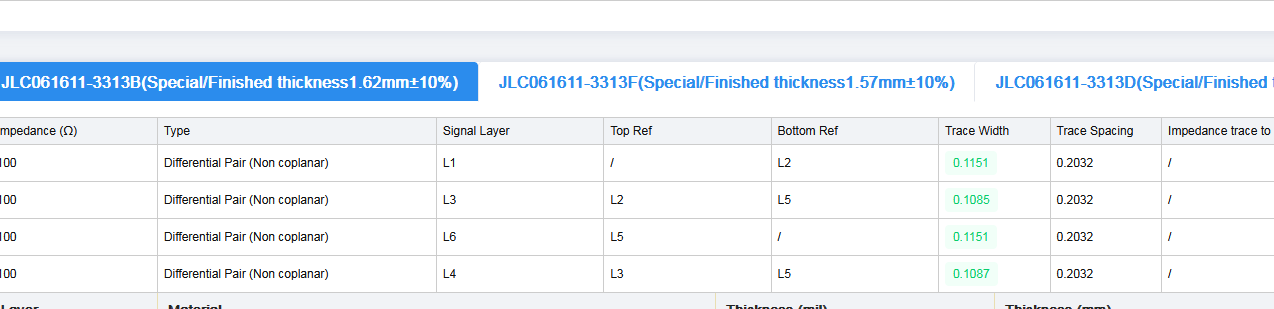
hardware/Cadence/top/mtca_interface_board_reocc/mib_tongue2/physical/Screenshot 2025-02-21 143327.png
