uob-hep-cad/uob-hep-pc072/hardware/Cadence/top/mtca_interface_board_reocc/top_mib_v3/images/diagram.jpg

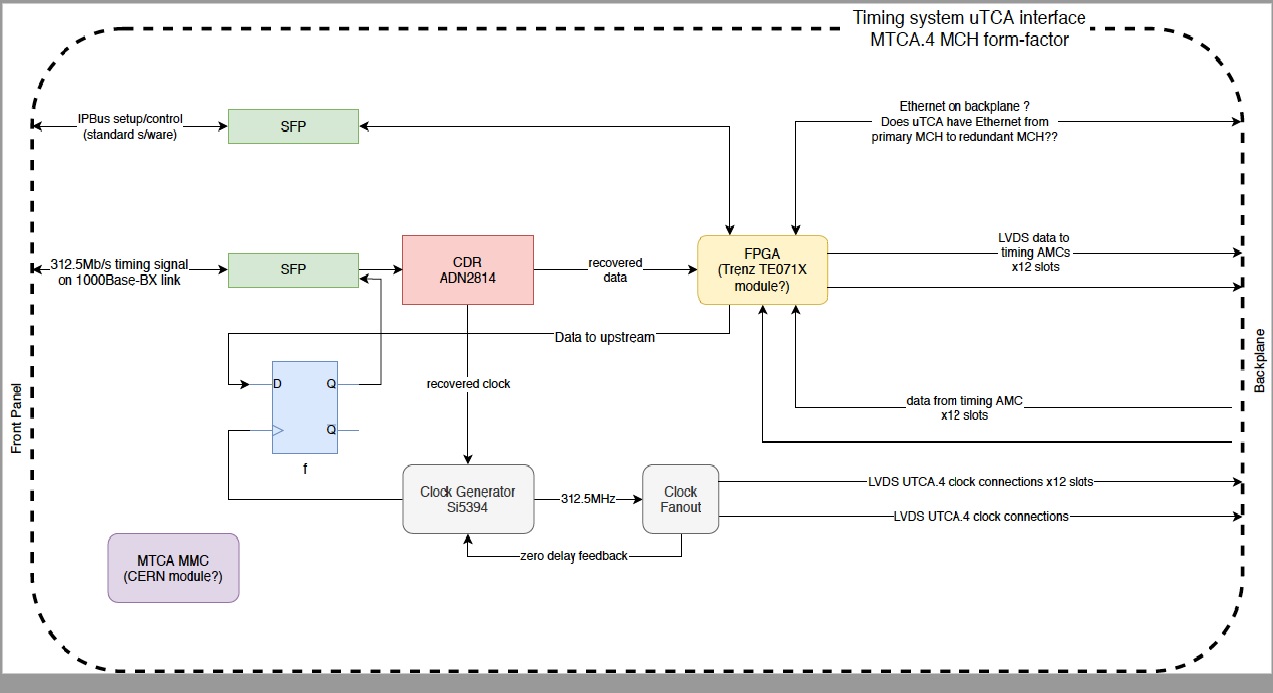
hardware/Cadence/top/mtca_interface_board_reocc/top_mib_v3/images/diagram.jpg
