uob-hep-cad/uob-hep-pc072/hardware/Cadence/top/mtca_interface_board_reocc/top_mib_v3/physical/mib_rev2_v121_mapped_image.png

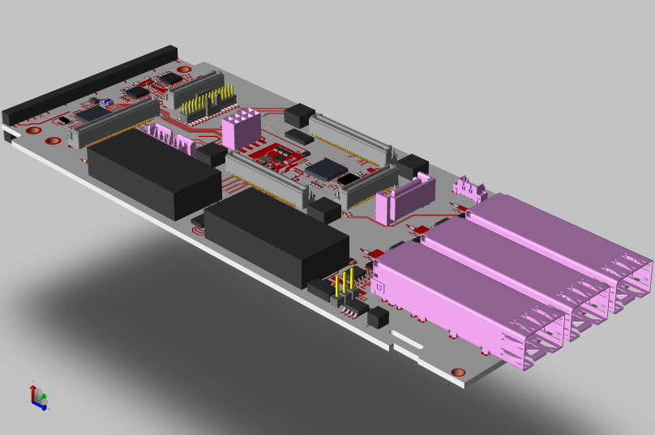
hardware/Cadence/top/mtca_interface_board_reocc/top_mib_v3/physical/mib_rev2_v121_mapped_image.png
