uob-hep-cad/uob-hep-pc072/images/ledlocatioons.jpg

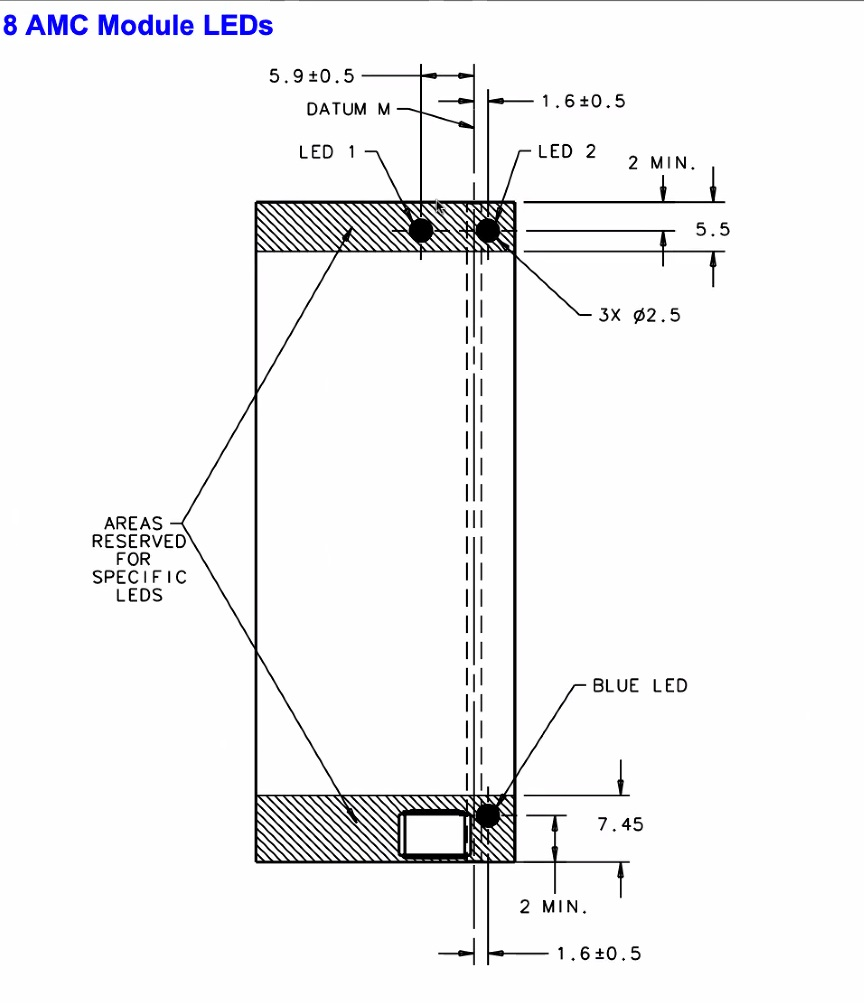
images/ledlocatioons.jpg
