uob-hep-cad/uob-hep-pc072/hardware/Cadence/top/mtca_interface_board_reocc/mib_tongue2/bom/mib_tongue2_m21.csv

TITLE: Bill of Materials
DATE: 03/07/2025
DESIGN: mib_tongue2
TEMPLATE: Z:\cad\tools\cadence_templates\spreadsheet-format.bom
CALLOUT: bom.callouts
Part Name | Ref Des | Qty | PART_NUMBER | PART_DESCRIPTION | OL_COMMENTS | KL_COMMENTS | PL_COMMENTS | Do Not Fit | MANUFACTURER | DNF
LSHM-130-0XXX-L-DV-A-S-LSHM-130-03.0-L-DV-A-S-K-TR,LSHM-130-0XXX-L-DV-A-S | JTG3 | 1 | LSHM-130-03.0-L-DV-A-S-K-TR | ? | ? | ? | ? | ? | SAMTEC | ?
LSHM-150-0XXX-L-DV-A-S-LSHM-150-03.0-L-DV-A-S-K-TR,LSHM-150-0XXX-L-DV-A-S | JTG2 | 1 | LSHM-150-03.0-L-DV-A-S-K-TR | ? | ? | ? | ? | ? | SAMTEC | ?
MCH_CONNECTOR2_ALT2-MCH2B-EDGE-170,MCH_CONNECTOR2_ALT2 | JTG1 | 1 | MCH2B-EDGE-170 | ? | ? | ? | ? | ? | HEP | ?
MT_HOLE-MT_HOLE,MT_HOLE | MTG1,MTG2,MTG3,MTG4 | 4 | Mt_Hole | ? | ? | ? | ? | ? | HEP | ?
TOTAL |  | 7
