uob-hep-cad/uob-hep-pc072/hardware/Cadence/top/mtca_interface_board_reocc/top_mib_v3/bom/PCBTrain_BOM.xls

Sheet: BOM Report
Quantity | Designator | Description | Manufacturer | Manufacturer Part Number | Supplier 1 | Supplier Part Number 1 | Notes
1 | U16 | TPS74618PQWDRVRQ1 | Texas Instruments | TPS74618PQWDRVRQ1
1 | DS1 | Blue LED | Wurth Eletronik | 155060BS73200
1 | DS2 | Red LED | Wurth Eletronik | 155060RS73200
12 | C5, C6, C7, C83, C118, C130, C131, C132, C134, C160, C168, C173 | 1uF 16V 0402 X5R
36 | C12, C13, C14, C15, C24, C27, C29, C32, C49, C77, C78, C79, C80, C84, C97, C99, C102, C122, C133, C137, C138, C142, C146, C149, C150, C151, C152, C153, C154, C157, C158, C159, C167, C169, C170, C174 | 100nF 16V 0402 X5R | TDK | C1005X7R1E104K050BB
5 | C18, C21, C22, C85, C125 | 1nF 50V 0402 X7R
8 | R11, R24, R37, R38, R40, R42, R155, R156 | 1K 0402 1%
6 | R43, R46, R49, R100, R157, R158 | 2.2K 0402 1%
1 | R88 | 6.2K 0402 1%
32 | R159, R160, R161, R162, R163, R164, R165, R166, R167, R168, R169, R170, R171, R172, R173, R174, R175, R176, R177, R178, R179, R180, R181, R182, R183, R184, R185, R186, R187, R188, R189, R190 | 200 0402 1%
2 | C23, C41 | 1uF 16V 0603
8 | C126, C127, C128, C129, C162, C163, C171, C172 | 10uF 6.3V 0603
1 | F1 | SF-0603S300-2 | Bourns | SF-0603S300-2
1 | F2 | SF-0603FP015F-2 | Bourns | SF-0603FP015F-2
6 | MMC, R2, R64, R66, R82, R89 | 0 Ohm 0603 1%
1 | R4 | 20 Ohm 0603 1%
1 | R7 | 270 Ohm 0603 1%
2 | R60, R70 | 1.6K 0603 1%
2 | R69, R84 | 1 Ohm 0603 1%
1 | L9 | 220 Ohms @ 100 MHz Ferrite Bead 0805 2A 45mOhm | Murata Electronics | BLM21PG221SN1D
1 | R87 | 0.27 Ohm 0805 1%
19 | C1, C2, C3, C4, C10, C11, C26, C28, C30, C31, C33, C34, C35, C36, C39, C40, C43, C45, C91 | 100nF 25V 0402 X7R | TDK | C1005X7R1E104K050BB
34 | C8, C19, C37, C135, C136, C139, C148, C165, C166, C175, C176, C177, C178, C179, C180, C181, C182, C183, C184, C185, C186, C187, C188, C189, C190, C191, C192, C193, C194, C195, C196, C197, C198, C199 | 100nF 25V 0402 X7R | TDK | C1005X7R1E104K050BB
4 | C9, C20, C38, C147 | 1UF | Murata Electronics | GRM152R60J105ME15D
1 | C46 | 0.47UF | Murata Electronics | GRM155R60J474KE19J
3 | C53, C93, C104 | 0.1UF | Kemet | C0402C104K9RACTU
15 | C57, C62, C64, C66, C69, C86, C90, C94, C103, C107, C111, C115, C140, C145, C156 | 100nF 25V 0402 X7R | TDK | C1005X7R1E104K050BB
3 | C89, C110, C144 | 1UF | Murata Electronics | GRT155R61E105ME01D
6 | C87, C108, C112, C121, C141, C155 | 10UF | Murata Electronics | GRM188R61A106KE69D
6 | C88, C96, C109, C117, C143, C161 | 22UF | Murata Electronics | GRM188R60J226MEA0D
6 | C42, C47, C48, C75, C76, C92 | 0.1UF 50V X8R 0805 | TDK | CGA4J2X8R1H104K125AA
12 | C50, C54, C55, C56, C59, C60, C65, C68, C71, C72, C81, C82 | 47UF | Murata Electronics | GRM21BR60J476ME15K
2 | C16, C95 | 100UF | Murata Electronics | GRM31CD80J107ME39K
4 | C25, C51, C52, C58 | 220uF | Vishay | 597D227X0025M2T
4 | D8, D9, D10, D11 | PGB1010603NR | Littelfuse | PGB1010603NR
1 | J4 | FTSH-115-01-L-DV | Samtec | FTSH-115-01-L-DV
1 | J10 | 0878321420 | Molex | 0878321420
1 | J12 | M20-9990345 | Harwin | M20-9990345
1 | PL1 | M20-9990245 | Harwin | M20-9990245
6 | J14, J15, J17, J18, J19, TE1 | U.FL-R-SMT-1(10) | Hirose | U.FL-R-SMT-1(10)
4 | L1, L2, L3, L10 | 120 OHM@100MHZ | Murata Electronics | BLM18AG121SN1D
1 | L12 | 100R@100MHz | TDK | MPZ1608S101ATAH0
6 | L5, L6, L7, L8, L11, L13 | 1 UH | Samsung Electro-Mechanics | CIGT201208EH1R0MNE
1 | L4 | 10 UH | Wurth Eletronik | 74438323100
3 | D1, D5, D6 | GREEN LED | Panasonic | LNJ326W83RA
1 | D4 | RED LED | LiteOn | LTST-C193KRKT-5A
1 | SK1 | MOLEX 22_23_2031 | Molex | 22-23-2031
1 | J16 | MOLEX 53398-0471 | Molex | 53398-0471
1 | QZ1 | 50MHz | SiTime | SIT5021AI-2DE-25E-50.000000X
2 | POWER1, PWR1 | PTH08T210WAD | Texas Instruments | PTH08T210WAD
3 | IC1, IC2, TIMING1 | SY58608UMG | Microchip | SY58608UMG
1 | IC8 | 854S01AKILF | Renesas Electronics | 854S01AKILF
2 | IC3, IC4 | ADCLK948BCPZ | Analog Devices | ADCLK948BCPZ
1 | U6 | SI5395A-A-GM | Skyworks | SI5395A-A-GM
9 | R1, R8, R10, R25, R27, R30, R32, R34, R134 | 100 Ohm | Panasonic | ERJ-2RKF1000X
23 | R13, R17, R59, R67, R71, R86, R92, R95, R96, R98, R99, R112, R114, R115, R116, R117, R123, R128, R129, R130, R131, R132, R133 | 4.99K | Panasonic | ERJ-2RKF4991X
6 | R16, R31, R48, R50, R51, R53 | 24.9 Ohm | Yageo | RC0402FR-0724R9L
15 | R19, R26, R28, R29, R35, R36, R73, R75, R77, R91, R97, R147, R154, R191, R192 | 0 Ohm 0402 1% | Yageo | RC0402JR-070RP
2 | R20, R23 | 49.9 Ohm | Panasonic | ERJ-2RKF49R9X
2 | R21, R22 | 499 OHM | Panasonic | ERJ-2RKF4990X
2 | R33, R111 | 150K | Panasonic | ERJ-2RKF1503X
7 | R39, R44, R45, R47, R57, R61, R93 | 33K | Panasonic | ERJ-2RKF3302X
2 | R41, R52 | 4.7K | Panasonic | ERJ-2RKF4701X
10 | R54, R58, R119, R120, R121, R122, R124, R125, R126, R127 | 2.2K | Panasonic | ERJ-2RKF2201X
2 | R55, R56 | 49.9 Ohm | Panasonic | ERJ-2RKF49R9X
5 | R68, R107, R108, R109, R113 | 1K | Panasonic | ERJ-2RKF1001X
5 | R72, R85, R94, R106, R136 | 10K | Vishay | M55342K11B10E0RS3
1 | R102 | 33 Ohm | Panasonic | ERJ-2RKF33R0X
1 | R104 | 390K | Panasonic | ERJ-2RKF3903X
1 | R105 | 330 Ohm | Panasonic | ERJ-PA2F3300X
1 | R110 | 30K | Panasonic | ERA-2AEB303X
3 | R3, R63, R135 | 249 Ohm 0603 1% | Vishay | CRCW0603249RFKEAC
2 | R137, R138 | 10M | Vishay | CRCW060310M0FKEAC
1 | R80 | 0 Ohm 0805 5% | Panasonic | ERJ-6GEY0R00V
2 | R62, R90 | 0.05 Ohm | Ohmite | LVK12R050FER
2 | J2, J5 | LSHM-130-03.0-L-DV-A-S-K-TR | Samtec | LSHM-130-03.0-L-DV-A-S-K-TR
3 | J1, J8, J9 | LSHM-150-03.0-L-DV-A-S-K-TR | Samtec | LSHM-150-03.0-L-DV-A-S-K-TR
3 | U5, U11, U14 | 2227023-1 | TE Connectivity | 2227023-1
1 | J13 | SHF-105-01-L-D-SM | Samtec | SHF-105-01-L-D-SM
1 | U2 | MAX9381ESA | Maxim IC | MAX9381ESA
1 | U18 | 24AA025E48T-I/SN | Microchip | 24AA025E48T-I/SN
1 | IC6 | LTC2991CMS | Analog Devices | LTC2991CMS
1 | IC7 | SN74AVC1T45DCK | Texas Instruments | SN74AVC1T45DCK
1 | U15 | SN74LVC1G06 | Texas Instruments | SN74LVC1G06
2 | T1, T2 | PJE8408 | Panjit Internation Inc. | PJE8408
1 | D12 | SS16FP | OnSemi | SS16FP
1 | SW1 | HDT0001 | C&K | HDT0001
8 | C17, C44, C61, C63, C67, C70, C73, C74 | 220uF | Kemet | T520V227M006ATE018
1 | IC5 | 11-4M1S | Toshiba | 11-4M1S
1 | U4 | ATMEGA128A-AU | Microchip | ATMEGA128A-AU
1 | U25 | LM75AIMME/NOPB | Texas Instruments | LM75AIMME/NOPB
3 | J3, J6, J11 | 1367073-1 | TE Connectivity | 1367073-1

Sheet: src
Design Name//ppfs6.physics.ox.ac.uk/CEG/Central Electronics/Projects/Hastingsp/DUNE/uob-hep-pc072/hardware/Cadence/top/mtca_interface_board_reocc/top_mib_v3/physical/mib_rev3ox_v224_manuf.brd
DateThu Oct 17 07:56:23 2024
Bill of Material Report (Condensed)
SYM_NAME | COMP_DEVICE_TYPE | COMP_VALUE | COMP_TOL | COMP_CLASS | QUANTITY | REFDES
6-WSON_2X2 | TPS74618P-TPS74618PQWDRVRQ1,TPB | TPS74618PQWDRVRQ1 |  | IC | 1 | U16
155060YS73200 | WURTH_155060BS73200 |  |  | DISCRETE | 1 | DS1
155060YS73200 | WURTH_155060RS73200 |  |  | DISCRETE | 1 | DS2
C0402 | CAPCERSMDCL2_0402-1UF,16V | 1uF | 10% | DISCRETE | 12 | C5, C6, C7, C83, C118, C130, C131, C132, C134, C160, C168, C173
C0402 | CAPCERSMDCL2_0402-100NF,16V_GEN | 100nF | 10% | DISCRETE | 36 | C12, C13, C14, C15, C24, C27, C29, C32, C49, C77, C78, C79, C80, C84, C97, C99, C102, C122, C133, C137, C138, C142, C146, C149, C150, C151, C152, C153, C154, C157, C158, C159, C167, C169, C170, C174
C0402 | CAPCERSMDCL2_0402-1NF_X7R,50V | 1nF | 10% | DISCRETE | 5 | C18, C21, C22, C85, C125
C0402 | RSMD0402_1/16W-1K,1% | 1k | 1% | DISCRETE | 8 | R11, R24, R37, R38, R40, R42, R155, R156
C0402 | RSMD0402_1/16W-2.2K,1% | 2.2k | 1% | DISCRETE | 6 | R43, R46, R49, R100, R157, R158
C0402 | RSMD0402_1/16W-6.2K,1% | 6.2k | 1% | DISCRETE | 1 | R88
C0402 | RSMD0402_1/16W-200,1% | 200 | 1% | DISCRETE | 32 | R159, R160, R161, R162, R163, R164, R165, R166, R167, R168, R169, R170, R171, R172, R173, R174, R175, R176, R177, R178, R179, R180, R181, R182, R183, R184, R185, R186, R187, R188, R189, R190
C0603 | CAPCERSMDCL2_0603-1UF,16V | 1uF | 10% | DISCRETE | 2 | C23, C41
C0603 | CAPCERSMDCL2_0603-10UF,6.3V | 10uF | 20% | DISCRETE | 8 | C126, C127, C128, C129, C162, C163, C171, C172
C0603 | SF-0603S300-2 |  |  | DISCRETE | 1 | F1
C0603 | SF-0603FP015F-2 |  |  | IC | 1 | F2
C0603 | RSMD0603_-00, | 0 |  | DISCRETE | 6 | MMC, R2, R64, R66, R82, R89
C0603 | RSMD0603_1/10W-20,1% | 20 | 1% | DISCRETE | 1 | R4
C0603 | RSMD0603_1/16W-270,1% | 270 | 1% | DISCRETE | 1 | R7
C0603 | RSMD0603_1/10W-1.6K,1% | 1.6k | 1% | DISCRETE | 2 | R60, R70
C0603 | RSMD0603_1/10W-XX,1% | XX | 1% | DISCRETE | 2 | R65, R79
C0603 | RSMD0603_1/10W-1,1% | 1 | 1% | DISCRETE | 2 | R69, R84
C0805 | FERRITE_SMD-BLM21PG221SN1,MURAA |  |  | DISCRETE | 1 | L9
C0805 | RSMD0805_125MW-0.27,1% | 0.27 | 1% | DISCRETE | 1 | R87
CAP0402 | CAP_NP_0-445-7348-2-ND,CAP_NP_A | 0.1UF |  | DISCRETE | 19 | C1, C2, C3, C4, C10, C11, C26, C28, C30, C31, C33, C34, C35, C36, C39, C40, C43, C45, C91
CAP0402 | CAPCERSMDCL2_0402-100NF,16V_GEA | 100nF | 10% | DISCRETE | 34 | C8, C19, C37, C135, C136, C139, C148, C165, C166, C175, C176, C177, C178, C179, C180, C181, C182, C183, C184, C185, C186, C187, C188, C189, C190, C191, C192, C193, C194, C195, C196, C197, C198, C199
CAP0402 | CAP_NP-GRM152R60J105ME15D,CAP_B | 1UF |  | DISCRETE | 4 | C9, C20, C38, C147
CAP0402 | CAP_NP-GRM155R60J474KE19J,CAP_B | 0.47UF |  | DISCRETE | 1 | C46
CAP0402 | CAP_NP-C0402C104K9RACTU,CAP_NPA | 0.1UF |  | DISCRETE | 3 | C53, C93, C104
CAP0402 | CAP_NP-445-7348-2-ND,CAP_NP-44A | 0.1UF |  | DISCRETE | 15 | C57, C62, C64, C66, C69, C86, C90, C94, C103, C107, C111, C115, C140, C145, C156
CAP0402 | CAP_NP-GRT155R61E105ME01D,CAP_B | 1UF |  | DISCRETE | 3 | C89, C110, C144
CAP0603 | CAP_NP-GRM188R61A106KE69D,CAP_B | 10UF |  | DISCRETE | 6 | C87, C108, C112, C121, C141, C155
CAP0603 | CAP_NP-GRM188R60J226MEA0D,CAP_B | 22UF |  | DISCRETE | 6 | C88, C96, C109, C117, C143, C161
CAP0805 | CAP_NP-445-8173-1-ND,CAP_NP-44A | 0.1UF |  | DISCRETE | 6 | C42, C47, C48, C75, C76, C92
CAP0805 | CAP_NP-GRM21BR60J476ME15K,CAP_B | 47UF |  | DISCRETE | 12 | C50, C54, C55, C56, C59, C60, C65, C68, C71, C72, C81, C82
CAP1206 | CAP_NP-GRM31CD80J107ME39K,CAP_B | 100UF |  | DISCRETE | 2 | C16, C95
CTE_VISHAY_597D-M | ELCAPTAN_SMD-220UF,25V | 220uF | 20% | DISCRETE | 4 | C25, C51, C52, C58
D0603 | TVS_2X-PGB1010603NR,TVS_2X-D06A | PGB1010603NR |  | DISCRETE | 4 | D8, D9, D10, D11
FTSH-115-01-L-DV | CONN30P-FTSH-115-01-L-DV,CONN3B | FTSH-115-01-L-DV |  | IO | 1 | J4
HDR14PINSMD | 7X2RECPT_SMD_2MM-878321420,7X2B | 7X2RECPT_SMD_2MM |  | IO | 1 | J10
HDR_1X3 | HDR1X3-HDR1X3,HDR1X3-HDR1X3,HDA | HDR1X3 |  | IO | 1 | J12
HEADER2X1_STR | HEADER2X1_STR-HARWIN |  |  | IO | 1 | PL1
HIROSE_U-FL-R-SMT-1_10 | PCOAX-U.FL-R-SMT-1(10) |  |  | IO | 6 | J14, J15, J17, J18, J19, TE1
INDC1608X95N | IND-BLM18AG121SN1D,IND-BLM18AGA | 120 OHM@100MHZ |  | DISCRETE | 4 | L1, L2, L3, L10
INDC1608X95N | FERRITE_SMD-MPZ1608S101A,TDK | 100R@100MHz |  | DISCRETE | 1 | L12
INDC2013X105N | IND-CIGT201208EH1R0MNE,IND-CIGA | 1 UH |  | DISCRETE | 6 | L5, L6, L7, L8, L11, L13
INDC2520X220N | IND-74438323100,IND-7443832310A | 10 UH |  | DISCRETE | 1 | L4
LEDC1608X80N | LED GREEN 0603_0-LNJ326W83RA,LB | GREEN |  | DISCRETE | 3 | D1, D5, D6
LEDC1608X80N | LED RED 0603_0-LNJ237W82RA,LEDB | RED |  | DISCRETE | 1 | D4
MOLEX22_23_2031 | KKCON3_STR-MOLEX |  |  | IO | 1 | SK1
MOLEX_53398-0471 | CON4P-53398-0471 |  |  | IO | 1 | J16
OSCSC254P500X700X100-6N | SIT5021AI-2DE-25E-50.000000-VDA | 50MHz |  | IC | 1 | QZ1
PWS_TI_ECP-R-PDSS-T14 | PTH08T210WAD |  |  | IC | 2 | POWER1, PWR1
QFN50P300X300X90-17N-S160 | SY58608UMG-VCC=P2V5 |  |  | IC | 3 | IC1, IC2, TIMING1
QFN50P300X300X100-17N-S180 | 854S01AKILF-VDD=VCC3V3 |  |  | IC | 1 | IC8
QFN50P500X500X100-33N-S285 | ADCLK948BCPZ-VCC=VDD_CLK_BUFFEA |  |  | IC | 2 | IC3, IC4
QFN_64 | SI5395A-A-GM-SI5395A-A-GM,SI53B | SI5395A-A-GM |  | IC | 1 | U6
RES0402 | R-ERJ-2RKF1000X,R-ERJ-2RKF1000A | 100 |  | DISCRETE | 9 | R1, R8, R10, R25, R27, R30, R32, R34, R134
RES0402 | R-ERJ-2RKF4991X,R-ERJ-2RKF4991A | 4.99K |  | DISCRETE | 23 | R13, R17, R59, R67, R71, R86, R92, R95, R96, R98, R99, R112, R114, R115, R116, R117, R123, R128, R129, R130, R131, R132, R133
RES0402 | R-311-24.9LRCT-ND,R-311-24.9LRA | 24.9 |  | DISCRETE | 6 | R16, R31, R48, R50, R51, R53
RES0402 | R-EMA-00007500V42,R-EMA-000075A | 0 |  | DISCRETE | 15 | R19, R26, R28, R29, R35, R36, R73, R75, R77, R91, R97, R147, R154, R191, R192
RES0402 | R-311-49.9LRCT-ND,R-311-49.9LRA | 49.9 |  | DISCRETE | 2 | R20, R23
RES0402 | R-ERJ-2RKF4990X,R-ERJ-2RKF4990A | 499 OHM |  | DISCRETE | 2 | R21, R22
RES0402 | R-ERJ-2RKF1503X,R-ERJ-2RKF1503A | 150K |  | DISCRETE | 2 | R33, R111
RES0402 | R-ERJ-2RKF3302X,R-ERJ-2RKF3302A | 33K |  | DISCRETE | 7 | R39, R44, R45, R47, R57, R61, R93
RES0402 | R-ERJ-2RKF4701X,R-ERJ-2RKF4701A | 4.7K |  | DISCRETE | 2 | R41, R52
RES0402 | R-ERJ-2RKF2201X,R-ERJ-2RKF2201A | 2.2K |  | DISCRETE | 10 | R54, R58, R119, R120, R121, R122, R124, R125, R126, R127
RES0402 | R-ERJ-2RKF49R9X,R-ERJ-2RKF49R9A | 49.9 |  | DISCRETE | 2 | R55, R56
RES0402 | R-ERJ-2RKF1001X,R-ERJ-2RKF1001A | 1K |  | DISCRETE | 5 | R68, R107, R108, R109, R113
RES0402 | R-M55342K11B10E0RS3,R-M55342K1A | 10K |  | DISCRETE | 5 | R72, R85, R94, R106, R136
RES0402 | R-ERJ-2RKF33R0X,R-ERJ-2RKF33R0A | 33 |  | DISCRETE | 1 | R102
RES0402 | R-ERJ-2RKF3903X,R-ERJ-2RKF3903A | 390K |  | DISCRETE | 1 | R104
RES0402 | R-ERJ-PA2F3300X,R-ERJ-PA2F3300A | 330 |  | DISCRETE | 1 | R105
RES0402 | R-ERA-2AEB303X,R-ERA-2AEB303X,A | 30K |  | DISCRETE | 1 | R110
RES0603 | R-EMA-00003608,R-EMA-00003608,A | 249 OHM |  | DISCRETE | 3 | R3, R63, R135
RES0603 | R-CRCW060310M0FKEAC,R-CRCW0603A | 10M |  | DISCRETE | 2 | R137, R138
RES0805 | R-ERJ-6GEY0R00V,R-ERJ-6GEY0R00A | 0 |  | DISCRETE | 1 | R80
RES_LVK12 | RES_SR_LVK12-0.05,1% | 0.05 |  | DISCRETE | 2 | R62, R90
SAMTEC_LSHM-130-04-0-L-DV-A-S | LSHM-130-0XXX-L-DV-A-S-LSHM-13B | LSHM-130-03.0-L-DV-A-S-K-TR |  | IO | 1 | J2
SAMTEC_LSHM-130-04-0-L-DV-A-S | TE0712 CONNECTOR-JB3-LSHM-130-B | LSHM-130-03.0-L-DV-A-S-K-TR |  | IO | 1 | J5
SAMTEC_LSHM-150-04-0-L-DV-A-S | TE0712 CONNECTOR-JB1-LSHM-150-B | LSHM-150-03.0-L-DV-A-S-K-TR |  | IO | 1 | J1
SAMTEC_LSHM-150-04-0-L-DV-A-S | TE0712 CONNECTOR-JB2-LSHM-150-B | LSHM-150-03.0-L-DV-A-S-K-TR |  | IO | 1 | J8
SAMTEC_LSHM-150-04-0-L-DV-A-S | LSHM-150-0XXX-L-DV-A-S-LSHM-15B | LSHM-150-03.0-L-DV-A-S-K-TR |  | IC | 1 | J9
SFP_CAGE | SFP_CAGE-2227023-1-2227023-1,SB | 2227023-1 |  | IC | 3 | U5, U11, U14
SHF-105-01-X-D-SM | SHF-105-01-L-D-SM |  |  | IC | 1 | J13
SOIC8 | MAX9381ESA_SMD-MAX9381ESA |  |  | IC | 1 | U2
SOIC8 | 24AA025E48T-I/SN-24AA025E48T-IB | 24AA025E48T-I/SN |  | IC | 1 | U18
SOP50P490X110-16N | LTC2991CMS#PBF-VCC=MP3V3 |  |  | IC | 1 | IC6
SOP65P210X110-6N | SN74AVC1T45DCK |  |  | IC | 1 | IC7
SOT23-5 | INV_1CH_OD-SN74LVC1G06DBVTE4,IB | SN74LVC1G06 |  | IC | 1 | U15
SOTFL50P160X60-3N | TRANS MOSFET_GSD-PJE8408,SOT523 |  |  | DISCRETE | 2 | T1, T2
SS16FP | SS16FP |  |  | IC | 1 | D12
SW_HDT0001 | HDT0001-HDT0001,HDT0001-HDT000A | HDT0001 |  | IO | 1 | SW1
T520V | TANTPOLY_SMD-220UF,6.3V | 220uF | 20% | DISCRETE | 8 | C17, C44, C61, C63, C67, C70, C73, C74
TOSHIBA_11-4M1S | TOSHIBA |  |  | IC | 1 | IC5
TQFP64_080 | ATMGA128_TQFP-ATMEGA128A-AU,ATB | ATMEGA128A-AU |  | IC | 1 | U4
TSSOP8_65P440X300MM | LM75A-LM75AIMME/NOPB,LM75A-LM7A | LM75AIMME/NOPB |  | IC | 1 | U25
TYCO_1367073 | CON20P_SFP-1367073-1-1367073-1B | 1367073-1 |  | IO | 3 | J3, J6, J11
