uob-hep-cad/uob-hep-pc072/hardware/Cadence/top/mtca_interface_board_reocc/top/bom/uob-hep-pc072-v205_28apr23.xlsx

TITLE: Bill of Materials
DATE: 28/April/2023
DESIGN: top
TEMPLATE: Z:\cad\tools\cadence_templates\spreadsheet-format.bom
CALLOUT: bom.callouts
Part Name | Ref Des | Qty | Manufacturer PART NUMBER | Do Not Fit | MANUFACTURER | Mounting SMD/TH/BGA/QFN | Supplier | Comment | DNF true/false | Components to fit (DNF = false) | BGA/QFN true/false | Number of BGA/QFN to fit
24AA025E48T-I/SN-24AA025E48T-I/SN,24AA025E48T-I/SN | U18 | 1 | 24AA025E48T-I/SN | ? | MICROCHIP TECHNOLOGY |  | Free Issue |  | TRUE | 1 | FALSE | 0
7X2RECPT_SMD_2MM-878321420,7X2RECPT_SMD_2MM | J10 | 1 | 878321420 | ? | MOLEX CONNECTOR CORPORATION |  | Free Issue |  | TRUE | 1 | FALSE | 0
ADCLK948BCPZ | IC3,IC4 | 2 | ADCLK948BCPZ | ? | ANALOG DEVICES | BGA/QFN | Newbury |  | TRUE | 2 | TRUE | 2
ATMGA128-ATMEGA128A-AU,ATMGA128 | U4 | 1 | ATMEGA128A-AU | ? | MICRO CHIP |  | Newbury | MU --> AU since first BoM | TRUE | 1 | FALSE | 0
cap ceramic smd class2 0402 100NF,16V_GEN | C8,C12,C13,C14,C15,C19,C24,C27,C29,C32,C37,C49,C97,C98,C99,C100,C101,C102,C105,C106,C113,C119,C120,C122,C133,C135,C136,C137,C138,C139,C142,C146,C148,C149,C150,C151,C152,C153,C154,C157,C158,C159,C165,C166,C167,C169,C170,C174,C175,C176,C177,C178,C179,C180,C181,C182,C183,C184,C185,C186,C187,C188,C189,C190,C191,C192,C193,C194,C195,C196,C197,C198,C199 | 73 | CC0402_100NF_16V_10%_X7R | ? | GENERIC |  | Newbury |  | TRUE | 73 | FALSE | 0
cap ceramic smd class2 0402 1NF_X7R,50V | C18,C21,C22,C123,C124,C125 | 6 | CC0402_1NF_50V_10%_X7R | ? | GENERIC |  | Newbury |  | TRUE | 6 | FALSE | 0
cap ceramic smd class2 0402 1UF,16V | C5,C6,C7,C114,C116,C118,C130,C131,C132,C134,C160,C168,C173 | 13 | CC0402_1.0UF_16V_10%_X5R | ? | GENERIC |  | Newbury |  | TRUE | 13 | FALSE | 0
cap ceramic smd class2 0603 10UF,6.3V | C126,C127,C128,C129,C162,C163,C171,C172 | 8 | CC0603_10UF_6V3_20%_X5R | ? | GENERIC |  | Newbury |  | TRUE | 8 | FALSE | 0
cap ceramic smd class2 0603 1UF,16V | C23,C41 | 2 | CC0603_1UF_16V_10%_X5R | ? | GENERIC |  | Newbury |  | TRUE | 2 | FALSE | 0
CAP Non-polarized 445-7348-2-ND,CAP_NP | C57,C62,C64,C66,C69,C86,C90,C94,C103,C107,C111,C115,C140,C145,C156 | 15 | 445-7348-2-ND | ? | TDK CORP |  | Newbury |  | TRUE | 15 | FALSE | 0
CAP Non-polarized 445-8173-1-ND,CAP_NP | C42,C47,C48,C92 | 4 | 445-8173-1-ND | ? | TDK CORP |  | Newbury |  | TRUE | 4 | FALSE | 0
CAP Non-polarized C0402 C104K9RACTU,CAP_NP | C53,C93,C104 | 3 | C0402C104K9RACTU | ? | KEMET |  | Newbury |  | TRUE | 3 | FALSE | 0
CAP Non-polarized GRM152R60J105ME15D,CAP_NP | C9,C20,C38,C147 | 4 | GRM152R60J105ME15D | ? | MURATA |  | Newbury |  | TRUE | 4 | FALSE | 0
CAP Non-polarized GRM155R60J474KE19J,CAP_NP | C46 | 1 | GRM155R60J474KE19J | ? | MURATA |  | Newbury |  | TRUE | 1 | FALSE | 0
CAP Non-polarized GRM188R60J226MEA0D,CAP_NP | C88,C96,C109,C117,C143,C161 | 6 | GRM188R60J226MEA0D | ? | MURATA |  | Newbury |  | TRUE | 6 | FALSE | 0
CAP Non-polarized GRM188R61A106KE69D,CAP_NP | C87,C108,C112,C121,C141,C155 | 6 | GRM188R61A106KE69D | ? | MURATA |  | Newbury |  | TRUE | 6 | FALSE | 0
generic ceramic cap 47UF 6.3V X5R 0805. e.g. https://www.digikey.co.uk/en/products/detail/samsung-electro-mechanics/CL21A476MQYNNNE/3887510 | C50,C54,C55,C56,C59,C60,C65,C68,C71,C72,C81,C82 | 12 |  | ? |  |  | Newbury |  | TRUE | 12 | FALSE | 0
generic ceramic cap 100UF 6.3V X6T 1206 . E.g. https://www.digikey.co.uk/en/products/detail/murata-electronics/GRM31CD80J107MEA8K/13905021 | C16,C95 | 2 |  | ? |  |  | Newbury |  | TRUE | 2 | FALSE | 0
CAP Non-polarized GRT155R61E105ME01D,CAP_NP | C89,C110,C144 | 3 | GRT155R61E105ME01D | ? | MURATA |  | Newbury |  | TRUE | 3 | FALSE | 0
CAP Non-polarized 0-445-7348-2-ND ,CAP_NP_0 | C1,C2,C3,C4,C10,C11,C26,C28,C30,C31,C33,C34,C35,C36,C39,C40,C43,C45,C91 | 19 | 445-7348-2-ND | ? | TDK CORP |  | Newbury |  | TRUE | 19 | FALSE | 0
10 Way, 2 Row, Straight PCB Header, Surface mount. E.g. https://www.digikey.co.uk/en/products/detail/samtec-inc/HTST-105-01-L-DV-A/1662844 | J13 | 1 | HTST-105-01-L-DV | ? | SAMTEC |  | Newbury |  | TRUE | 1 | FALSE | 0
CON20P_SFP-1367073-1-1367073-1,CON20P_SFP-1367073-1 | J3,J6,J11 | 3 | 1367073-1 | ? | TE CONNECTIVITY AMP CONNECTORS | Press-fit | Newbury |  | TRUE | 3 | FALSE | 0
CON4P-53398-0471 | J16 | 1 | 53398-0471 | ? | MOLEX |  | Newbury |  | TRUE | 1 | FALSE | 0
CONN30P-FTSH-115-01-L-DV,CONN30P | J4 | 1 | FTSH-115-01-L-DV | ? | SAMTEC |  | Free Issue |  | TRUE | 1 | FALSE | 0
DIODE-1N4148W-13-F,DIODE | D12 | 1 | 1N4148W-13-F | ? | DIODES INCORPORATED |  | Newbury |  | TRUE | 1 | FALSE | 0
ELCAPTAN_SMD-220UF,25V,case-M | C25,C51,C52,C58 | 4 | 597D227X0025M2T | ? | VISHAY |  | Newbury |  | TRUE | 4 | FALSE | 0
FERRITE_SMD-BLM21PG221SN1,MURATA | L9 | 1 | BLM21PG221SN1 | ? | MURATA |  | Newbury |  | TRUE | 1 | FALSE | 0
FERRITE_SMD-MPZ1608S101A,TDK | L12 | 1 | MPZ1608S101A | ? | TDK |  | Newbury |  | TRUE | 1 | FALSE | 0
Generic 2.54mm 3-way header. E.g. https://uk.farnell.com/amp-te-connectivity/825433-3/header-1row-3way/dp/3417657 | J12 | 1 |  | ? |  | TH | Newbury |  | TRUE | 1 | FALSE | 0
HDT0001-HDT0001,HDT0001 | SW1 | 1 | HDT0001 | ? | C&K |  | Newbury |  | TRUE | 1 | FALSE | 0
IND-74438323100,IND | L4 | 1 | 74438323100 | ? | W__RTH ELEKTRONIK |  | Newbury |  | TRUE | 1 | FALSE | 0
IND-BLM18AG121SN1D,IND | L1,L2,L3,L10 | 4 | BLM18AG121SN1D | ? | MURATA ELECTRONICS |  | Free Issue |  | TRUE | 4 | FALSE | 0
IND-CIGT201208EH1R0MNE,IND | L5,L6,L7,L8,L11,L13 | 6 | CIGT201208EH1R0MNE | ? | SAMSUNG ELECTRO-MECHANICS |  | Newbury |  | TRUE | 6 | FALSE | 0
Use any SN74LVC1G06DBVT variant. E.g. https://www.mouser.co.uk/ProductDetail/Texas-Instruments/SN74LVC1G06DBV | U15 | 1 | SN74LVC1G06DBVT | ? | TEXAS INSTRUMENTS |  | Newbury |  | TRUE | 1 | FALSE | 0
Generic 0603 SMD green LED. E.g. https://www.mouser.co.uk/ProductDetail/Wurth-Elektronik/150060VS55040 | D1,D5,D6 | 3 |  | ? |  |  | Newbury |  | TRUE | 3 | FALSE | 0
Generic 0603 SMD red LED. E.g. https://www.mouser.co.uk/ProductDetail/Wurth-Elektronik/150060SS75003 | D2,D4 | 2 |  | ? |  |  | Newbury |  | TRUE | 2 | FALSE | 0
LED_0-LTST-C193TBKT-5A,LED_0 | D3 | 1 | LTST-C193TBKT-5A | ? | LITE-ON INC. |  | Free Issue |  | TRUE | 1 | FALSE | 0
TMP75BIDR | U25 | 1 | TMP75BIDR | ? | TEXAS INSTRUMENTS |  | Newbury | Subsituted from LM75A-LM75AIMME/NOPB,LM75A. Need to change schematic | TRUE | 1 | FALSE | 0
LP_515XXX-5151230F,LP_515XXX | U1 | 1 | 5151230F | ? | DIALIGHT |  | Newbury |  | TRUE | 1 | FALSE | 0
LSHM-130-0XXX-L-DV-A-S-LSHM-130-03.0-L-DV-A-S-K-TR,LSHM-130-0XXX-L-DV-A-S | J2 | 1 | LSHM-130-03.0-L-DV-A-S-K-TR | ? | SAMTEC |  | Free Issue |  | TRUE | 1 | FALSE | 0
LSHM-150-0XXX-L-DV-A-S-LSHM-150-03.0-L-DV-A-S-K-TR,LSHM-150-0XXX-L-DV-A-S | J9 | 1 | LSHM-150-03.0-L-DV-A-S-K-TR | ? | SAMTEC |  | Free Issue |  | TRUE | 1 | FALSE | 0
LTC2991CMS#PBF | IC6 | 1 | LTC2991CMS#PBF | ? | LINEAR TECHNOLOGY |  | Newbury |  | TRUE | 1 | FALSE | 0
MAX9381ESA_SMD-MAX9381ESA | U2,U3,U8 | 3 | MAX9381ESA | ? | ? |  | Free Issue |  | TRUE | 3 | FALSE | 0
MCH_CONNECTOR1-MCH1B-EDGE-170,MCH_CONNECTOR1 | J7 | 1 | MCH1B-EDGE-170 | DNF | Part of PCB |  | N/A |  | FALSE | 0 | FALSE | 0
MT_HOLE-MT_HOLE,MT_HOLE | MH1,MH2,MH3,MH4,MH5,MH6,MH7,MH8,MH9,MH10 | 10 | Mt_Hole | DNF | HEP |  | N/A |  | FALSE | 0 | FALSE | 0
PCOAX-U.FL-R-SMT-1(10) | J14,J15,J17,J18,J19,TE1 | 6 | U.FL-R-SMT-1(10) | ? | HIROSE |  | Newbury |  | TRUE | 6 | FALSE | 0
PTH08T210WAD | POWER1,PWR1 | 2 | PTH08T210WAD | ? | TEXAS INSTRUMENTS |  | Free Issue |  | TRUE | 2 | FALSE | 0
R-311-24.9LRCT-ND,R | R16,R31,R48,R50,R51,R53 | 6 | 311-24.9LRCT-ND | ? | YAGEO |  | Newbury |  | TRUE | 6 | FALSE | 0
R-311-49.9LRCT-ND,R | R20,R23 | 2 | 311-49.9LRCT-ND | ? | YAGEO |  | Newbury |  | TRUE | 2 | FALSE | 0
R-CRCW060310M0FKEAC,R | R137,R138 | 2 | CRCW060310M0FKEAC | ? | VISHAY DALE |  | Newbury |  | TRUE | 2 | FALSE | 0
Generic 0603 resistor, 1/16W or higher, 1%, 249 Ohms | R3,R5,R63,R135 | 4 |  | ? |  |  | Newbury |  | TRUE | 4 | FALSE | 0
Generic 0402 resistor, "zero ohm" | R19,R26,R28,R29,R35,R36,R73,R75,R77,R91,R97,R147,R154,R191,R192 | 15 |  | ? |  |  | Newbury |  | TRUE | 15 | FALSE | 0
R-ERA-2AEB303X,R | R110 | 1 | ERA-2AEB303X | ? | PANASONIC |  | Newbury |  | TRUE | 1 | FALSE | 0
R-ERJ-2RKF1000X,R | R1,R2,R4,R7,R8,R9,R10,R12,R14,R15,R18,R25,R27,R30,R32,R34,R134 | 17 | ERJ-2RKF1000X | ? | PANASONIC |  | Newbury |  | TRUE | 17 | FALSE | 0
R-ERJ-2RKF1001X,R | R68,R107,R108,R109,R113 | 5 | ERJ-2RKF1001X | ? | PANASONIC |  | Newbury |  | TRUE | 5 | FALSE | 0
R-ERJ-2RKF1503X,R | R33,R103,R111 | 3 | ERJ-2RKF1503X | ? | PANASONIC |  | Newbury |  | TRUE | 3 | FALSE | 0
R-ERJ-2RKF2201X,R | R54,R58,R119,R120,R121,R122,R124,R125,R126,R127 | 10 | ERJ-2RKF2201X | ? | PANASONIC |  | Newbury |  | TRUE | 10 | FALSE | 0
R-ERJ-2RKF3302X,R | R39,R44,R45,R47,R57,R61,R93 | 7 | ERJ-2RKF3302X | ? | PANASONIC |  | Newbury |  | TRUE | 7 | FALSE | 0
R-ERJ-2RKF33R0X,R | R102 | 1 | ERJ-2RKF33R0X | ? | PANASONIC |  | Newbury |  | TRUE | 1 | FALSE | 0
R-ERJ-2RKF3903X,R | R104 | 1 | ERJ-2RKF3903X | ? | PANASONIC |  | Newbury |  | TRUE | 1 | FALSE | 0
R-ERJ-2RKF4701X,R | R41,R52 | 2 | ERJ-2RKF4701X | ? | PANASONIC |  | Newbury |  | TRUE | 2 | FALSE | 0
R-ERJ-2RKF4990X,R | R21,R22 | 2 | ERJ-2RKF4990X | ? | PANASONIC |  | Newbury |  | TRUE | 2 | FALSE | 0
R-ERJ-2RKF4991X,R | R13,R17,R59,R67,R71,R86,R92,R95,R96,R98,R99,R112,R114,R115,R116,R117,R123,R128,R129,R130,R131,R132,R133 | 23 | ERJ-2RKF4991X | ? | PANASONIC |  | Newbury |  | TRUE | 23 | FALSE | 0
R-ERJ-2RKF49R9X,R | R55,R56 | 2 | ERJ-2RKF49R9X | ? | PANASONIC |  | Newbury |  | TRUE | 2 | FALSE | 0
R-ERJ-3EKF1600V,R | R6 | 1 | ERJ-3EKF1600V | ? | PANASONIC |  | Newbury |  | TRUE | 1 | FALSE | 0
R-ERJ-6GEY0R00V,R | R80 | 1 | ERJ-6GEY0R00V | ? | PANASONIC |  | Newbury |  | TRUE | 1 | FALSE | 0
R-ERJ-PA2F3300X,R | R105 | 1 | ERJ-PA2F3300X | ? | PANASONIC - SCD |  | Newbury |  | TRUE | 1 | FALSE | 0
R-M55342K11B10E0RS3,R | R72,R85,R94,R106,R136 | 5 | M55342K11B10E0RS3 | ? | VISHAY DALE |  | Newbury |  | TRUE | 5 | FALSE | 0
R-NO_STUFF,R | R74,R76,R78 | 3 | NO_STUFF | DNF | NS |  | N/A |  | FALSE | 0 | FALSE | 0
RES_SR_LVK12-0.05,1% | R62,R90 | 2 | LVK12R050FER | ? | OHMITE |  | Newbury |  | TRUE | 2 | FALSE | 0
RSMD0402_1/16W-1K,1% | R11,R24,R37,R38,R40,R42,R101,R118,R139,R140,R141,R142,R143,R144,R155,R156 | 16 | R0402_1K_1%_0.063W_100PPM | ? | GENERIC |  | Newbury |  | TRUE | 16 | FALSE | 0
RSMD0402_1/16W-2.2K,1% | R43,R46,R49,R100,R145,R146,R148,R149,R150,R151,R152,R153,R157,R158 | 14 | R0402_2K2_1%_0.063W_200PPM | ? | GENERIC |  | Newbury |  | TRUE | 14 | FALSE | 0
RSMD0402_1/16W-200,1% | R159,R160,R161,R162,R163,R164,R165,R166,R167,R168,R169,R170,R171,R172,R173,R174,R175,R176,R177,R178,R179,R180,R181,R182,R183,R184,R185,R186,R187,R188,R189,R190 | 32 | R0402_200R_1%_0.063W_200PPM | ? | GENERIC |  | Newbury |  | TRUE | 32 | FALSE | 0
RSMD0402_1/16W-6.2K,1% | R88 | 1 | R0402_6K2_1%_0.063W_200PPM | ? | GENERIC |  | Newbury |  | TRUE | 1 | FALSE | 0
RSMD0603_-00, | MMC,R64,R66,R69,R82,R84,R89 | 7 | R0603_00_JUMPER | ? | GENERIC |  | Newbury |  | TRUE | 7 | FALSE | 0
RSMD0603_1/10W-1.6K,1% | R60,R70 | 2 | R0603_1K6_1%_0.1W_100PPM | ? | GENERIC |  | Newbury |  | TRUE | 2 | FALSE | 0
RSMD0603_1/10W-XX,1% | R65,R79,R81,R83 | 4 | R0603_XX_1%_0.1W_100PPM | DNF | GENERIC |  | N/A |  | FALSE | 0 | FALSE | 0
RSMD0805_125MW-0.27,1% | R87 | 1 | R0805_0R27_1%_0.125W_100PPM | ? | GENERIC |  | Newbury |  | TRUE | 1 | FALSE | 0
SFP_CAGE-2227023-1-2227023-1,SFP_CAGE-2227023-1 | U5,U11,U14 | 3 | 2227023-1 | ? | TE CONNECTIVITY AMP CONNECTORS | Press-fit | Newbury |  | TRUE | 3 | FALSE | 0
SI5395A-A-GM-SI5395A-A-GM,SI5395A-A-GM | U6 | 1 | SI5395A-A-GM | ? | SILICON LABS | BGA/QFN | Free Issue |  | TRUE | 1 | TRUE | 1
SIT5021AI-2DE-25E-50.000000 | QZ1 | 1 | SIT5021AI-2DE-25E-50.000000 | ? | SI TIME |  | Newbury |  | TRUE | 1 | FALSE | 0
SY58608UMG | IC1,IC2,TIMING1 | 3 | SY58608UMG | ? | MICREL | BGA/QFN | Newbury |  | TRUE | 3 | TRUE | 3
TANTPOLY_SMD-220UF,6.3V,case-v | C17,C44,C61,C63,C67,C70,C73,C74 | 8 | T520V227M006ATE018 | ? | Kemet |  | Newbury |  | TRUE | 8 | FALSE | 0
TE0712 CONNECTOR-JB1-LSHM-150-03.0-L-DV-A-S-K-TR,TE0712 CONNECTOR-JB1 | J1 | 1 | LSHM-150-03.0-L-DV-A-S-K-TR | ? | SAMTEC |  | Newbury |  | TRUE | 1 | FALSE | 0
TE0712 CONNECTOR-JB2-LSHM-150-03.0-L-DV-A-S-K-TR,TE0712 CONNECTOR-JB2 | J8 | 1 | LSHM-150-03.0-L-DV-A-S-K-TR | ? | SAMTEC |  | Newbury |  | TRUE | 1 | FALSE | 0
TE0712 CONNECTOR-JB3-LSHM-130-03.0-L-DV-A-S-K-TR,TE0712 CONNECTOR-JB3 | J5 | 1 | LSHM-130-03.0-L-DV-A-S-K-TR | ? | SAMTEC |  | Newbury |  | TRUE | 1 | FALSE | 0
TESTPOINT-EMA-00001481V22,TESTPOINT | TP4,TP5,TP7,TP9,TP11,TP13,TP14 | 7 | EMA-00001481V22 | DNF | KEYSTONE ELECTRONICS |  | N/A |  | FALSE | 0 | FALSE | 0
TOSHIBA | IC5 | 1 | TLP183 | ? | TOSHIBA |  | Newbury |  | TRUE | 1 | FALSE | 0
TPS74618P-TPS74618PQWDRVRQ1,TPS74618P | U16 | 1 | TPS74618PQWDRVRQ1 | ? | TEXAS INSTRUMENTS | BGA/QFN | Newbury |  | TRUE | 1 | TRUE | 1
TP_HOLE-1.0MM | TP1,TP2,TP3 | 3 | TP_HOLE_1.0mm | DNF | ? |  | N/A |  | FALSE | 0 | FALSE | 0
TRANS MOSFET_GSD-PJE8408,SOT523 | T1,T2 | 2 | PJE8408 | ? | PANJIT SEMICONDUCTOR |  | Newbury |  | TRUE | 2 | FALSE | 0
TVS_2X-PGB1010603NR,TVS_2X | D8,D9,D10,D11 | 4 | PGB1010603NR | ? | LITTELFUSE INC. |  | Free Issue |  | TRUE | 4 | FALSE | 0
 |  | 472 |  |  |  |  |  | Number of unique components to fit | 86
 |  |  |  |  |  |  |  | Total number of components to fit | 444
 |  |  |  |  |  |  |  | "standard" SMT to fit | 436
 |  |  |  |  |  |  |  | BGA/QFN to fit | 7
 |  |  |  |  |  |  |  | Through hole (excluding press-fit) | 1
 |  |  |  |  |  |  |  | Press-fit | 3
