uob-hep-cad/uob-hep-pc072/hardware/Manufacturing/artwork/mib_tongue2_v3-manufacturing-artwork-2025-10-23/mib_tongue2_m21.xlsx

Column1 | Column2 | Column3 | Column4 | Column5 | Column10
TITLE: Bill of Materials
DATE: 03/07/2025
DESIGN: mib_tongue2
TEMPLATE: Z:\cad\tools\cadence_templates\spreadsheet-format.bom
CALLOUT: bom.callouts
Part Name | Ref Des | Qty | Suppler part number | Supplier | MANUFACTURER
LSHM-130-03.0-L-DV-A-S-K-TR | JTG3 | 1 | SAM14110CT-ND | Digikey | SAMTEC
LSHM-150-03.0-L-DV-A-S-K-TR | JTG2 | 1 | SAM14151CT-ND | Digikey | SAMTEC
TOTAL |  | 2
