uob-hep-cad/uob-hep-pc072/hardware/Cadence/top/mtca_interface_board_reocc/front_panel_jtag_serial/physical/Manufacturing March 2025/pc072_mib_jtag_18MAR25.xls

Sheet: BOM Report
Quantity per board | Designator | Description | Manufacturer | Manufacturer Part Number | Supplier 1 | Supplier Part Number 1 | Notes
5 | C1, C2, C3, C4, C5 | 100nF 16V X7R 0603 Capacitor | KYOCERA AVX | 0603YC104K4T4A |  |  | Not exact but min spec as descpt - can be substituted from Newbury stock
2 | C6, C9 | 1uF 6.3V X5R 0603 Capacitor | KYOCERA AVX | 0603YC105KAT2A |  |  | Not exact but min spec as descpt - can be substituted from Newbury stock
1 | C8 | 10nF 50V X5R 0603 Capacitor | KYOCERA AVX | 0603YC103KAT2A |  |  | Not exact but min spec as descpt - can be substituted from Newbury stock
1 | C7 | 10uF 10V X5R 0805 Capacitor | KYOCERA AVX | 0805YC106KAT2A |  |  | Not exact but min spec as descpt - can be substituted from Newbury stock
3 | R1, R3, R4 | 4.7K 0603 1% Resistor | Panasonic | ERJ3EKF4701V |  |  | Not exact but min spec as descpt - can be substituted from Newbury stock
1 | R2 | 10K 0603 1% Resistor | Panasonic | ERJ3EKF1002V |  |  | Not exact but min spec as descpt - can be substituted from Newbury stock
6 | R7, R8, R9, R10, R11, R12 | 270R 0402 1% Resistor | Panasonic | R-ERA-2VEB2700X |  |  | Not exact but min spec as descpt - can be substituted from Newbury stock
1 | J1 | Molex 878331419 | Molex | 878331419
1 | J3 | CONN HEADER VERT 30POS 1.27MM | Samtec | FTSH-115-01-L-D |  |  | FTSH-115-01-L-D-RA-KV
1 | J2 | CON16P_USB_C_USB2-2137160001 | Molex | 2137160001 | GCT | USB4085-GF-A | <- Alternative
1 | J5 | CONN HEADER SMD 10POS 1.27MM | Samtec | SHF-105-01-S-D-SM
1 | J4 | CONN HEADER R/A 10POS 1.27MM | Samtec | SHF-105-01-L-D-RA
1 | IC1 | JTAG-SMT3-NC: SURFACE-MNT PROG | Digilent | 410-357-B
1 | IC2 | IC BUF NON-INVERT 5.5V 14SOIC | OnSemi | MC74LCX07DR2G
1 | RG1 | IC REG LINEAR 2.5V 150MA SOT23-5 | STMicro | LD3985M25R
1 | D1 | TVS DIODE 5VWM 15VC SOT236 | UMW | USBLC6-2SC6
3 | LD1, LD2, LD3 | 591-3001-113F | Dialight | 591-3001-113F
Compulsory columns highlighted in yellow

Sheet: DELETE ME
SYM_NAME | COMP_DEVICE_TYPE | COMP_VALUE | COMP_TOL | COMP_CLASS | QUANTITY | REFDES
410357B | 410_357_B-DIGILENT,410-357-B |  |  | IC | 1 | IC1
C0603 | CAPCERSMDCL2_0603-100NF,16V | 100nF | 10% | DISCRETE | 5 | C1;C2;C3;C4;C5
C0603 | CAPCERSMDCL2_0603-1.0UF,6.3V | 1.0uF | 10% | DISCRETE | 2 | C6;C9
C0603 | CAPCERSMDCL2_0603-10NF,50V | 10nF | 10% | DISCRETE | 1 | C8
C0603 | RSMD0603_1/10W-4.7K,1% | 4.7k | 1% | DISCRETE | 3 | R1;R3;R4
C0603 | RSMD0603_1/10W-10K,1% | 10k | 1% | DISCRETE | 1 | R2
C0603 | RSMD0603_1/16W-XX,5% | XX | 5% | DISCRETE | 2 | R5;R6
C0805 | CAPCERSMDCL2_0805-10UF_Y5V,10V_GEN | 10uF | 0.6 | DISCRETE | 1 | C7
CONMOLEX14MC_2MM | CON14P-MOLEX_87833 |  |  | IO | 1 | J1
FTSH-115-01-L-D-RA-KV | CONN30P-FTSH-115-01-L-D-RA-KV,CONN30P-CONN30P,FTSH-115-01-L-D-A | FTSH-115-01-L-D-RA-KV |  | IO | 1 | J3
LED_DIALIGHT_591-3XX1 | 591-3001-0XXF |  |  | DISCRETE | 3 | LD1;LD2;LD3
MOLEX_2137160001 | CON16P_USB_C_USB2-2137160001 |  |  | IO | 1 | J2
RES0402 | R-ERA-2VEB2700X,R-ERA-2VEB2700X,R | 270 |  | DISCRETE | 6 | R7;R8;R9;R10;R11;R12
SAMTEC_SHF-105-01-X-D-SM | SHF-105-01-X-D-SM-SHF-105-01-X-D-SM |  |  | IO | 1 | J5
SHDRRA10W41P127_2X5_1270X546X533P | SHF-105-01-L-D-RA-SHF-105-01-L-D-RA |  |  | IO | 1 | J4
SOIC14S_127 | 74LVC07A_SOIC-VCC=2V5 |  |  | IC | 1 | IC2
SOT95P280X145-5N | LD3985M25R |  |  | IC | 1 | RG1
SOT95P280X145-6N | USBLC6-2SC6 |  |  | DISCRETE | 1 | D1
