uob-hep-cad/uob-hep-pc072/hardware/Cadence/cis_hep_partslib/cis_hep_partslib/models/DDR4/z90b_ibis/z90b_ibis_quality_checklist.xls

Sheet: summary
This checklist will help validate the quality of an IBIS file.
Copy the component and Model tabs below so that this spreadsheet contains one tab
for each [Component] and [Model]. Fill in the tabs to determine the quality level for
each item, then complete the summary of IQ levels below to determine the overall
IQ level. For more information check the IBIS Quality Specification
Vendor | Micron Technology, Inc.
IBIS File | z90b.ibs, z90b_it.ibs
Rev | 2.1
Date | 2018-04-04
Overall IBIS Quality | 3MSX
IBISCHK Parser Information
Version | 6.1.2
Errors | 0
Warnings | 0
Caution | 0
Notes | Yes
Summary of IBIS Check
File Header
In column Pass/Fail below mark each item PASS, FAIL, NA or EXCEPTION.
The IQ level is the highest level number for which all checks PASS.
The IQ level is FAIL if no level completely passes.
See IBIS Quality Specification for complete descriptions of the checks.
IQ Spec Reference | IQ LEVEL | Description | PASS/FAIL | Comments
2.1 | LEVEL 1 | IBIS file passes IBISCHK | PASS
Components
Components | IQ LEVEL | Comments
Packaged - MT40A1G4RH, MT40A512M8RH, MT40A256M16GE | 3
Bare Die - MT40A1G4Z90B, MT40A512M8Z90B, MT40A256M16Z90B | 3
Models
Models | IQ LEVEL | Comments
I/O - DQ_34_*, DQ_40_*, DQ_48_*, DQS_34_*, DQS_40_*, DQS_48_* | 3SX
Input - DM_*, INPUT_*, CTRL_*, CLKIN_*, RESET, TEN | 3S
Teminator - TDQS_*, NF_INPUT | 3S
Open_sink - ALERT_* | 3S

Sheet: components(pkg)
COMPONENT(S): | MT40A1G4RH, MT40A512M8RH, MT40A256M16GE
IQ Level: | 3
Exception:
Correlation:
In column Pass/Fail below mark each item PASS, FAIL, NA or EXCEPTION.
The IQ level is the highest level number for which all checks PASS.
The IQ level is FAIL if no level completely passes.
See IBIS Quality Specification for complete descriptions of the checks.
IQ Spec Reference | IQ LEVEL | Description | PASS/FAIL | Comments
3.1.1 | LEVEL 2 | [Package] must have typ/min/max values | PASS
3.1.2 | LEVEL 2 | [Package] parasitics must be reasonable | PASS
3.2.1 | LEVEL 2 | [Pin] section complete | PASS
3.2.2 | LEVEL 3 | [Pin] RLC parasitics are present and reasonable | PASS
3.3.1 | LEVEL 2 | [Diff Pin] referenced pin models matched | PASS
3.3.2 | LEVEL 3 | [Diff Pin] Vdiff and Tdelay_* complete and reasonable | PASS
4.1 | LEVEL 2 | [Model Selector] entries have reasonable descriptions | PASS
4.2 | LEVEL 2 | Default [Model Selector] entries are consistent | PASS

Sheet: components(bare die)
COMPONENT(S): | MT40A1G4Z90B, MT40A512M8Z90B, MT40A256M16Z90B
IQ Level: | 3
Exception:
Correlation:
In column Pass/Fail below mark each item PASS, FAIL, NA or EXCEPTION.
The IQ level is the highest level number for which all checks PASS.
The IQ level is FAIL if no level completely passes.
See IBIS Quality Specification for complete descriptions of the checks.
IQ Spec Reference | IQ LEVEL | Description | PASS/FAIL | Comments
3.1.1 | LEVEL 2 | [Package] must have typ/min/max values | PASS
3.1.2 | LEVEL 2 | [Package] parasitics must be reasonable | NA | Bare Die
3.2.1 | LEVEL 2 | [Pin] section complete | PASS
3.2.2 | LEVEL 3 | [Pin] RLC parasitics are present and reasonable | NA | Bare Die
3.3.1 | LEVEL 2 | [Diff Pin] referenced pin models matched | PASS
3.3.2 | LEVEL 3 | [Diff Pin] Vdiff and Tdelay_* complete and reasonable | PASS
4.1 | LEVEL 2 | [Model Selector] entries have reasonable descriptions | PASS
4.2 | LEVEL 2 | Default [Model Selector] entries are consistent | PASS

Sheet: models(IO)
MODEL(S): | DQ_34_*, DQ_40_*, DQ_48_*, DQS_34_*, DQS_40_*, DQS_48_*
IQ Level: | 3
Exception: | 5.4.3 | V-t length is excessive due to inclusion of [Composite Current] I-t data.
Correlation: | MSX | Measuremant and Simulation Correlated
In column Pass/Fail below mark each item PASS, FAIL, NA or EXCEPTION.
The IQ level is the highest level number for which all checks PASS.
The IQ level is FAIL if no level completely passes.
See IBIS Quality Specification for complete descriptions of the checks.
IQ Spec Reference | IQ LEVEL | Description | PASS/FAIL | Comments
5.1.1 | LEVEL 2 | [Model] parameters have correct typ/min/max order | PASS
5.1.2 | LEVEL 2 | [Model] C_comp is reasonable | PASS
5.1.3 | LEVEL 2 | [Temperature Range] is reasonable | PASS
5.1.4 | LEVEL 2 | [Voltage Range] or [* Reference] is reasonable | PASS
5.2.1 | LEVEL 3 | [Model] Vinl and Vinh reasonable | PASS
5.2.2 | LEVEL 3 | [Model Spec] Vinl and Vinh reasonable | PASS
5.2.3 | LEVEL 3 | [Model Spec] Vinl+/- and Vinh+/- complete and reasonable | NA
5.2.5 | LEVEL 2 | [Model Spec] S_Overshoot subparameters complete and match data sheet | PASS
5.2.6 | LEVEL 2 | [Model Spec] S_Overshoot subparameters track typ/min/max | PASS
5.2.7 | LEVEL 2 | [Model Spec] D_Overshoot_* subparameters complete and match data sheet | PASS
5.2.8 | LEVEL 2 | [Model Spec] D_Overshoot_* subparameters track typ/min/max | PASS
5.2.9 | LEVEL 3 | [Receiver Thresholds] Vth present and matches data sheet, if needed | NA
5.2.10 | LEVEL 3 | [Receiver Thresholds] Vth_min and Vth_max present and match data sheet, if needed | NA
5.2.11 | LEVEL 3 | [Receiver Thresholds] Vinh_ac, Vinl_ac present and match data sheet, if needed | NA
5.2.12 | LEVEL 3 | [Receiver Thresholds] Vinh_dc, Vinl_dc present and match data sheet, if needed | NA
5.2.13 | LEVEL 3 | [Receiver Thresholds] Tslew_ac/Tdiffslew_ac present and match data sheet, if needed | NA
5.2.14 | LEVEL 3 | [Receiver Thresholds] Threshold_sensitivity and Ext_ref present and match data sheet, if needed | NA
5.3.1 | LEVEL 2 | I-V tables have correct typ/min/max order | PASS
5.3.2 | LEVEL 2 | [Pullup] voltage sweep range is correct | PASS
5.3.3 | LEVEL 2 | [Pulldown] voltage sweep range is correct | PASS
5.3.4 | LEVEL 2 | [POWER Clamp] voltage sweep range is correct | PASS
5.3.5 | LEVEL 2 | [GND Clamp] voltage sweep range is correct | PASS
5.3.6 | LEVEL 2 | I-V tables do not exhibit stair-stepping | PASS
5.3.7 | LEVEL 2 | Combined I-V tables are monotonic | PASS
5.3.8 | LEVEL 2 | [Pulldown] I-V tables pass through zero/zero | PASS
5.3.9 | LEVEL 2 | [Pullup] I-V tables pass through zero/zero | PASS
5.3.10 | LEVEL 2 | No leakage current in clamp I-V tables | PASS
5.3.11 | LEVEL 2 | I-V behavior not double-counted | PASS
5.3.12 | LEVEL 2 | On-die termination modeling documented | PASS
5.3.13 | LEVEL 2 | ECL models I-V tables swept from -Vcc to +2 * Vcc. | NA
5.3.14 | LEVEL 2 | Point distributions in I-V tables should be sufficient | PASS
5.4.1 | LEVEL 2 | Output and I/O buffers have sufficient V-T tables | PASS
5.4.2 | LEVEL 2 | V-T tables have reasonable point distribution | PASS
5.4.3 | LEVEL 3 | V-T table duration is not excessive | EXCEPTION | V-t length is long due to inclusion of [Composite Current] I-t data.
5.4.4 | LEVEL 2 | V-T table endpoints match fixture voltages | PASS
5.5.1 | LEVEL 2 | [Ramp] R_load present if value other than 50 ohms | PASS
5.5.2 | LEVEL 2 | [Ramp] typ/min/max order is correct | PASS
5.5.3 | LEVEL 2 | [Ramp] dV consistent with I-V table calculations | PASS
5.5.4 | LEVEL 2 | [Ramp] dt is consistent with 20%-80% crossing time | PASS
5.6.1 | LEVEL 3 | [Model Spec] Vmeas and Vref used if typ/min/max variation | PASS
5.6.2 | LEVEL 3 | Vref consistent for Open-drain, Open-source, and ECL Model_types | NA

Sheet: models(Input)
MODEL(S): | DM_*, INPUT_*, CTRL_*, CLKIN_*, RESET, TEN
IQ Level: | 3
Exception:
Correlation: | MS | Measurement and Simulation Correlated
In column Pass/Fail below mark each item PASS, FAIL, NA or EXCEPTION.
The IQ level is the highest level number for which all checks PASS.
The IQ level is FAIL if no level completely passes.
See IBIS Quality Specification for complete descriptions of the checks.
IQ Spec Reference | IQ LEVEL | Description | PASS/FAIL | Comments
5.1.1 | LEVEL 2 | [Model] parameters have correct typ/min/max order | PASS
5.1.2 | LEVEL 2 | [Model] C_comp is reasonable | PASS
5.1.3 | LEVEL 2 | [Temperature Range] is reasonable | PASS
5.1.4 | LEVEL 2 | [Voltage Range] or [* Reference] is reasonable | PASS
5.2.1 | LEVEL 3 | [Model] Vinl and Vinh reasonable | PASS
5.2.2 | LEVEL 3 | [Model Spec] Vinl and Vinh reasonable | PASS
5.2.3 | LEVEL 3 | [Model Spec] Vinl+/- and Vinh+/- complete and reasonable | NA
5.2.5 | LEVEL 2 | [Model Spec] S_Overshoot subparameters complete and match data sheet | PASS
5.2.6 | LEVEL 2 | [Model Spec] S_Overshoot subparameters track typ/min/max | PASS
5.2.7 | LEVEL 2 | [Model Spec] D_Overshoot_* subparameters complete and match data sheet | PASS
5.2.8 | LEVEL 2 | [Model Spec] D_Overshoot_* subparameters track typ/min/max | PASS
5.2.9 | LEVEL 3 | [Receiver Thresholds] Vth present and matches data sheet, if needed | PASS
5.2.10 | LEVEL 3 | [Receiver Thresholds] Vth_min and Vth_max present and match data sheet, if needed | PASS
5.2.11 | LEVEL 3 | [Receiver Thresholds] Vinh_ac, Vinl_ac present and match data sheet, if needed | PASS
5.2.12 | LEVEL 3 | [Receiver Thresholds] Vinh_dc, Vinl_dc present and match data sheet, if needed | PASS
5.2.13 | LEVEL 3 | [Receiver Thresholds] Tslew_ac/Tdiffslew_ac present and match data sheet, if needed | PASS
5.2.14 | LEVEL 3 | [Receiver Thresholds] Threshold_sensitivity and Ext_ref present and match data sheet, if needed | PASS
5.3.1 | LEVEL 2 | I-V tables have correct typ/min/max order | PASS
5.3.2 | LEVEL 2 | [Pullup] voltage sweep range is correct | NA
5.3.3 | LEVEL 2 | [Pulldown] voltage sweep range is correct | NA
5.3.4 | LEVEL 2 | [POWER Clamp] voltage sweep range is correct | PASS
5.3.5 | LEVEL 2 | [GND Clamp] voltage sweep range is correct | PASS
5.3.6 | LEVEL 2 | I-V tables do not exhibit stair-stepping | PASS
5.3.7 | LEVEL 2 | Combined I-V tables are monotonic | PASS
5.3.8 | LEVEL 2 | [Pulldown] I-V tables pass through zero/zero | NA
5.3.9 | LEVEL 2 | [Pullup] I-V tables pass through zero/zero | NA
5.3.10 | LEVEL 2 | No leakage current in clamp I-V tables | PASS
5.3.11 | LEVEL 2 | I-V behavior not double-counted | PASS
5.3.12 | LEVEL 2 | On-die termination modeling documented | PASS
5.3.13 | LEVEL 2 | ECL models I-V tables swept from -Vcc to +2 * Vcc. | NA
5.3.14 | LEVEL 2 | Point distributions in I-V tables should be sufficient | PASS
5.4.1 | LEVEL 2 | Output and I/O buffers have sufficient V-T tables | NA
5.4.2 | LEVEL 2 | V-T tables have reasonable point distribution | NA
5.4.3 | LEVEL 3 | V-T table duration is not excessive | NA
5.4.4 | LEVEL 2 | V-T table endpoints match fixture voltages | NA
5.5.1 | LEVEL 2 | [Ramp] R_load present if value other than 50 ohms | NA
5.5.2 | LEVEL 2 | [Ramp] typ/min/max order is correct | NA
5.5.3 | LEVEL 2 | [Ramp] dV consistent with I-V table calculations | NA
5.5.4 | LEVEL 2 | [Ramp] dt is consistent with 20%-80% crossing time | NA
5.6.1 | LEVEL 3 | [Model Spec] Vmeas and Vref used if typ/min/max variation | NA
5.6.2 | LEVEL 3 | Vref consistent for Open-drain, Open-source, and ECL Model_types | NA

Sheet: models(Terminator)
MODEL(S): | TDQS_*, NF_INPUT
IQ Level: | 3
Exception:
Correlation: | MS | Measurement and Simulation Correlated
In column Pass/Fail below mark each item PASS, FAIL, NA or EXCEPTION.
The IQ level is the highest level number for which all checks PASS.
The IQ level is FAIL if no level completely passes.
See IBIS Quality Specification for complete descriptions of the checks.
IQ Spec Reference | IQ LEVEL | Description | PASS/FAIL | Comments
5.1.1 | LEVEL 2 | [Model] parameters have correct typ/min/max order | PASS
5.1.2 | LEVEL 2 | [Model] C_comp is reasonable | PASS
5.1.3 | LEVEL 2 | [Temperature Range] is reasonable | PASS
5.1.4 | LEVEL 2 | [Voltage Range] or [* Reference] is reasonable | PASS
5.2.1 | LEVEL 3 | [Model] Vinl and Vinh reasonable | NA
5.2.2 | LEVEL 3 | [Model Spec] Vinl and Vinh reasonable | NA
5.2.3 | LEVEL 3 | [Model Spec] Vinl+/- and Vinh+/- complete and reasonable | NA
5.2.5 | LEVEL 2 | [Model Spec] S_Overshoot subparameters complete and match data sheet | NA
5.2.6 | LEVEL 2 | [Model Spec] S_Overshoot subparameters track typ/min/max | NA
5.2.7 | LEVEL 2 | [Model Spec] D_Overshoot_* subparameters complete and match data sheet | NA
5.2.8 | LEVEL 2 | [Model Spec] D_Overshoot_* subparameters track typ/min/max | NA
5.2.9 | LEVEL 3 | [Receiver Thresholds] Vth present and matches data sheet, if needed | NA
5.2.10 | LEVEL 3 | [Receiver Thresholds] Vth_min and Vth_max present and match data sheet, if needed | NA
5.2.11 | LEVEL 3 | [Receiver Thresholds] Vinh_ac, Vinl_ac present and match data sheet, if needed | NA
5.2.12 | LEVEL 3 | [Receiver Thresholds] Vinh_dc, Vinl_dc present and match data sheet, if needed | NA
5.2.13 | LEVEL 3 | [Receiver Thresholds] Tslew_ac/Tdiffslew_ac present and match data sheet, if needed | NA
5.2.14 | LEVEL 3 | [Receiver Thresholds] Threshold_sensitivity and Ext_ref present and match data sheet, if needed | NA
5.3.1 | LEVEL 2 | I-V tables have correct typ/min/max order | PASS
5.3.2 | LEVEL 2 | [Pullup] voltage sweep range is correct | NA
5.3.3 | LEVEL 2 | [Pulldown] voltage sweep range is correct | NA
5.3.4 | LEVEL 2 | [POWER Clamp] voltage sweep range is correct | PASS
5.3.5 | LEVEL 2 | [GND Clamp] voltage sweep range is correct | PASS
5.3.6 | LEVEL 2 | I-V tables do not exhibit stair-stepping | PASS
5.3.7 | LEVEL 2 | Combined I-V tables are monotonic | PASS
5.3.8 | LEVEL 2 | [Pulldown] I-V tables pass through zero/zero | NA
5.3.9 | LEVEL 2 | [Pullup] I-V tables pass through zero/zero | NA
5.3.10 | LEVEL 2 | No leakage current in clamp I-V tables | PASS
5.3.11 | LEVEL 2 | I-V behavior not double-counted | PASS
5.3.12 | LEVEL 2 | On-die termination modeling documented | PASS
5.3.13 | LEVEL 2 | ECL models I-V tables swept from -Vcc to +2 * Vcc. | NA
5.3.14 | LEVEL 2 | Point distributions in I-V tables should be sufficient | PASS
5.4.1 | LEVEL 2 | Output and I/O buffers have sufficient V-T tables | NA
5.4.2 | LEVEL 2 | V-T tables have reasonable point distribution | NA
5.4.3 | LEVEL 3 | V-T table duration is not excessive | NA
5.4.4 | LEVEL 2 | V-T table endpoints match fixture voltages | NA
5.5.1 | LEVEL 2 | [Ramp] R_load present if value other than 50 ohms | NA
5.5.2 | LEVEL 2 | [Ramp] typ/min/max order is correct | NA
5.5.3 | LEVEL 2 | [Ramp] dV consistent with I-V table calculations | NA
5.5.4 | LEVEL 2 | [Ramp] dt is consistent with 20%-80% crossing time | NA
5.6.1 | LEVEL 3 | [Model Spec] Vmeas and Vref used if typ/min/max variation | NA
5.6.2 | LEVEL 3 | Vref consistent for Open-drain, Open-source, and ECL Model_types | NA

Sheet: models(Open_drain)
MODEL(S): | ALERT_*
IQ Level: | 3
Exception:
Correlation: | MS | Measurement and Simulation Correlated
In column Pass/Fail below mark each item PASS, FAIL, NA or EXCEPTION.
The IQ level is the highest level number for which all checks PASS.
The IQ level is FAIL if no level completely passes.
See IBIS Quality Specification for complete descriptions of the checks.
IQ Spec Reference | IQ LEVEL | Description | PASS/FAIL | Comments
5.1.1 | LEVEL 2 | [Model] parameters have correct typ/min/max order | PASS
5.1.2 | LEVEL 2 | [Model] C_comp is reasonable | PASS
5.1.3 | LEVEL 2 | [Temperature Range] is reasonable | PASS
5.1.4 | LEVEL 2 | [Voltage Range] or [* Reference] is reasonable | PASS
5.2.1 | LEVEL 3 | [Model] Vinl and Vinh reasonable | NA
5.2.2 | LEVEL 3 | [Model Spec] Vinl and Vinh reasonable | NA
5.2.3 | LEVEL 3 | [Model Spec] Vinl+/- and Vinh+/- complete and reasonable | NA
5.2.5 | LEVEL 2 | [Model Spec] S_Overshoot subparameters complete and match data sheet | NA
5.2.6 | LEVEL 2 | [Model Spec] S_Overshoot subparameters track typ/min/max | NA
5.2.7 | LEVEL 2 | [Model Spec] D_Overshoot_* subparameters complete and match data sheet | NA
5.2.8 | LEVEL 2 | [Model Spec] D_Overshoot_* subparameters track typ/min/max | NA
5.2.9 | LEVEL 3 | [Receiver Thresholds] Vth present and matches data sheet, if needed | NA
5.2.10 | LEVEL 3 | [Receiver Thresholds] Vth_min and Vth_max present and match data sheet, if needed | NA
5.2.11 | LEVEL 3 | [Receiver Thresholds] Vinh_ac, Vinl_ac present and match data sheet, if needed | NA
5.2.12 | LEVEL 3 | [Receiver Thresholds] Vinh_dc, Vinl_dc present and match data sheet, if needed | NA
5.2.13 | LEVEL 3 | [Receiver Thresholds] Tslew_ac/Tdiffslew_ac present and match data sheet, if needed | NA
5.2.14 | LEVEL 3 | [Receiver Thresholds] Threshold_sensitivity and Ext_ref present and match data sheet, if needed | NA
5.3.1 | LEVEL 2 | I-V tables have correct typ/min/max order | PASS
5.3.2 | LEVEL 2 | [Pullup] voltage sweep range is correct | NA
5.3.3 | LEVEL 2 | [Pulldown] voltage sweep range is correct | PASS
5.3.4 | LEVEL 2 | [POWER Clamp] voltage sweep range is correct | PASS
5.3.5 | LEVEL 2 | [GND Clamp] voltage sweep range is correct | PASS
5.3.6 | LEVEL 2 | I-V tables do not exhibit stair-stepping | PASS
5.3.7 | LEVEL 2 | Combined I-V tables are monotonic | PASS
5.3.8 | LEVEL 2 | [Pulldown] I-V tables pass through zero/zero | PASS
5.3.9 | LEVEL 2 | [Pullup] I-V tables pass through zero/zero | NA
5.3.10 | LEVEL 2 | No leakage current in clamp I-V tables | PASS
5.3.11 | LEVEL 2 | I-V behavior not double-counted | PASS
5.3.12 | LEVEL 2 | On-die termination modeling documented | NA
5.3.13 | LEVEL 2 | ECL models I-V tables swept from -Vcc to +2 * Vcc. | NA
5.3.14 | LEVEL 2 | Point distributions in I-V tables should be sufficient | PASS
5.4.1 | LEVEL 2 | Output and I/O buffers have sufficient V-T tables | PASS
5.4.2 | LEVEL 2 | V-T tables have reasonable point distribution | PASS
5.4.3 | LEVEL 3 | V-T table duration is not excessive | PASS
5.4.4 | LEVEL 2 | V-T table endpoints match fixture voltages | PASS
5.5.1 | LEVEL 2 | [Ramp] R_load present if value other than 50 ohms | PASS
5.5.2 | LEVEL 2 | [Ramp] typ/min/max order is correct | PASS
5.5.3 | LEVEL 2 | [Ramp] dV consistent with I-V table calculations | PASS
5.5.4 | LEVEL 2 | [Ramp] dt is consistent with 20%-80% crossing time | PASS
5.6.1 | LEVEL 3 | [Model Spec] Vmeas and Vref used if typ/min/max variation | PASS
5.6.2 | LEVEL 3 | Vref consistent for Open-drain, Open-source, and ECL Model_types | PASS
