uob-hep-cad/uob-hep-pc072/hardware/Cadence/cis_hep_partslib/cis_hep_partslib/Allegro_Library/symbols/HCCStar/HccStar_v1a/WideChip_pads_20210602_print.pdf

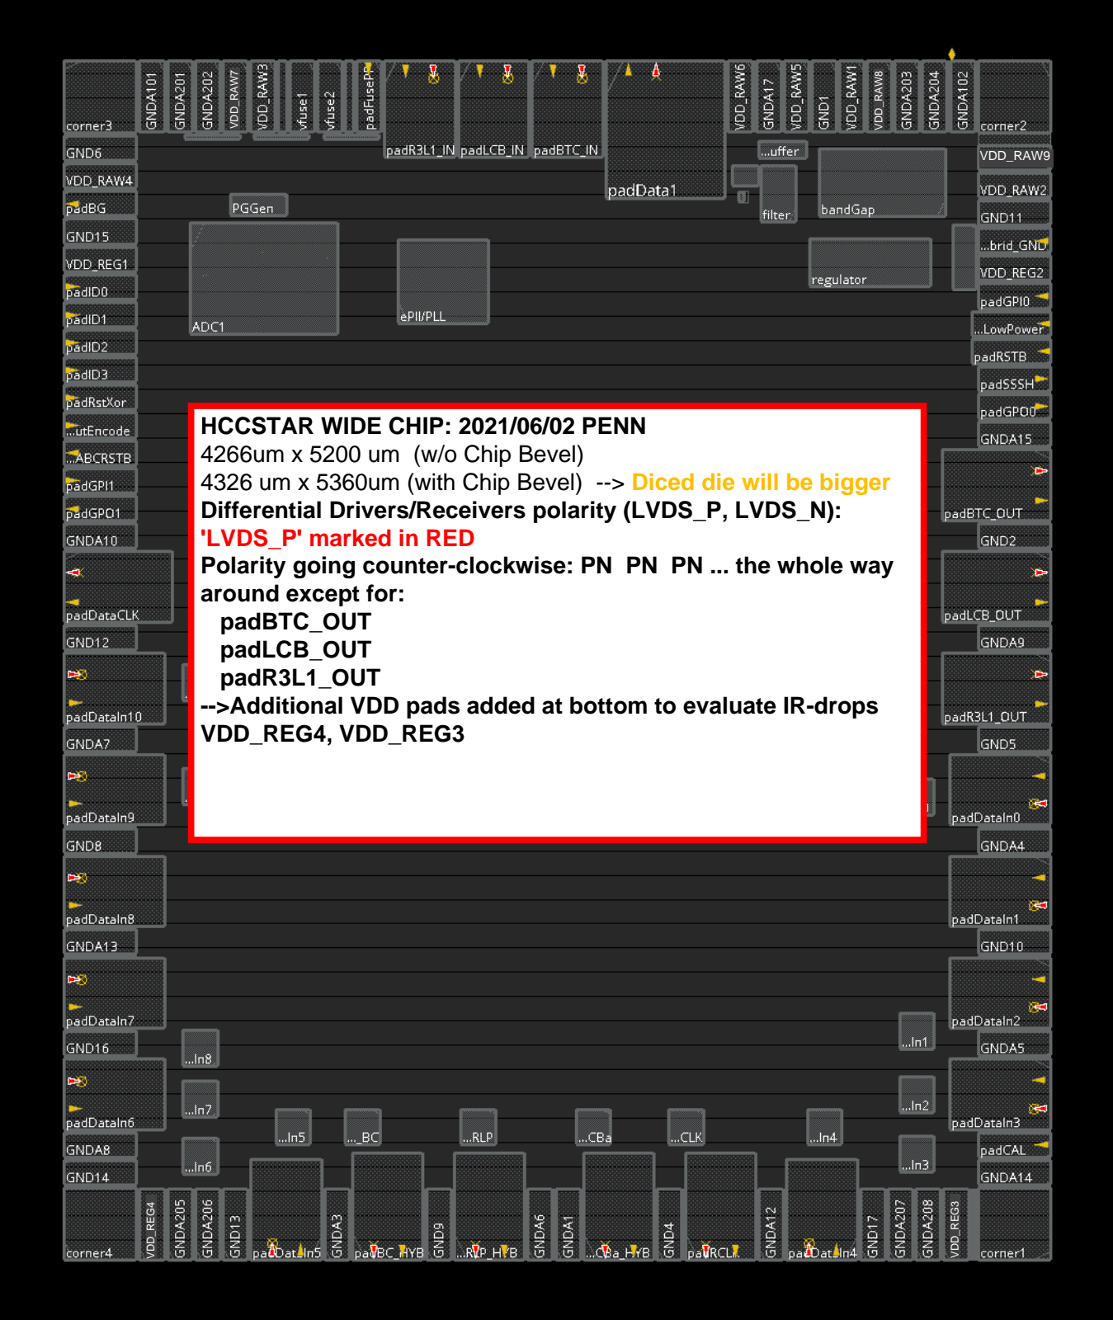
[picture p22: page 1]
