uob-hep-cad/uob-hep-pc072/hardware/Cadence/top/archive_libs/cnpassive/tp/metadata/pdv_validation.txt

pdv_117,Package Pin:No mapping between Logical Pin 'A<0>' and section number S1. Blank values not allowed for any Section Number,Error
pdv_117,Package Pin:No mapping between Logical Pin 'A<0>' and section number S1. Blank values not allowed for any Section Number,Error
pdv_506,Cell 'tp':For logical part TP, pack type HOLE is missing in chips.prt file but present in part table file,Warning
pdv_506,Cell 'tp':For logical part TP, pack type WIRING is missing in chips.prt file but present in part table file,Warning
pdv_506,Cell 'tp':For logical part TP, pack type SMD is missing in chips.prt file but present in part table file,Warning
pdv_506,Cell 'tp':For logical part TP, pack type PIN-6.3 is missing in chips.prt file but present in part table file,Warning
pdv_506,Cell 'tp':For logical part TP, pack type PIN-16.5 is missing in chips.prt file but present in part table file,Warning
pdv_506,Cell 'tp':For logical part TP, pack type U-TERM is missing in chips.prt file but present in part table file,Warning
pdv_506,Cell 'tp':For logical part TP_GND, pack type HOLE+GND is missing in chips.prt file but present in part table file,Warning
pdv_506,Cell 'tp':For logical part TP_GND, pack type WIRING+GND is missing in chips.prt file but present in part table file,Warning
pdv_506,Cell 'tp':For logical part TP_GND, pack type SMD+GND is missing in chips.prt file but present in part table file,Warning
pdv_506,Cell 'tp':For logical part TP_GND, pack type PIN-6.3+GND is missing in chips.prt file but present in part table file,Warning
pdv_506,Cell 'tp':For logical part TP_GND, pack type PIN-16.5+GND is missing in chips.prt file but present in part table file,Warning
