uob-hep-cad/uob-hep-pc072/hardware/Cadence/top/archive_libs/standard/ctap/metadata/pdv_validation.txt

pdv_323,Symbol 'sym_1':Pin(s) B are on symbol origin,Error
