uob-hep-cad/uob-hep-pc072/hardware/MIB v3 to v3a changes 8oct26.xlsx

issue number | title | author | createdAt | Action | Report to Tech Coordination? | Board | Old components/nets | New components/nets
79 | extraneous net: DFF_REF_CLK_P/N<0/1> ? | strilov | 2026-08-10 10:57 | Removed superfluous nets. No change to netlist | Unsure (no change to copper) | Main | DFF_REF_CLK_P/N<0/1> | None (deleted)
78 | backplane JTAG connection | strilov | 2026-08-10 10:50 | Removed b/plane connections to MMC. Connected to FPGA via switches | Yes | Main | None | TE1
74 | Rename nets on MIB v3 main board now that UART and LEDs have been moved to AUX-IO connector ( J4 ) | DavidCussans | 2026-01-22 13:54 | UART connections addressed in #68. Edited LED nets as well. | Unsure (no change to copper) | Main
73 | look at front GPIO to/from FPGA | strilov | 2025-12-18 15:34 | Added U/FL connectors on JTAG d/board (no room on f/panel) | Yes | JTAG | None | J6,J7,J8,J9,J10
70 | Add fuse to JTAG Vref_jtag line | DavidCussans | 2025-11-12 11:41 | Done. Added fuse. | Yes | Main | None | F3
68 | UART/AUXIO signal labels | strilov | 2025-10-29 12:50 | Done. Changed net-names. | Unsure (no change to copper)
67 | D-FF on SFP[2] needs pull-down for PECL outputs | DavidCussans | 2025-10-24 10:05 | "Y" termination scheme implemented. | Yes | Main | C77, C78, R8 | R8, R9, R12
66 | Resistor location | strilov | 2025-10-03 12:18 | R55 moved. | Yes | Main | R55 | R55
65 | JTAG daugherboard outline is too big | DavidCussans | 2025-08-19 14:36 | Edited outline. | Yes (minor change) | JTAG
60 | Front panel switch , SW1 , is 180-degrees wrong rotation | DavidCussans | 2025-02-24 10:12 | Checked. Rotated w.r.t v215. Good. Closed | Yes | Main | SW1 | SW1
59 | Indicator LEDs , DS1 , DS2 ( red, blue ) have incorrect part numbers. D4 (red) is obsolete | DavidCussans | 2025-02-17 14:53 | Replaced blue LED. Other obsolete LEDs are 0603 so fix manually in BoM | Yes(minor change) | Main | DS2 | DS2
58 | R60 (voltage set on 2.5V) on MIB v3 (pre-production MIB) wrong value. | DavidCussans | 2025-02-04 13:42 | Fixed in schematic and PCB | Yes | Main |  | R60, R6
57 | IC5 on MIB v3 (pre-production MIB) assembled incorrectly | DavidCussans | 2025-02-04 12:16 | Fixed confusing silk | Yes(minor change) | Main
