uob-hep-cad/uob-hep-pc072/hardware/Schematics/dune_mib_v3_3july24_bw_v2.pdf

1 | 3 | 4
5 6

Fri Jun 7 16:04:20 2024; mtca_interface_board_reocc; USED ON; ISSUE; APPD. DATE; MOD NO.; DRN BY.; CHKD.; STATUS; C UOB-HEP 20; UOB-HEP

N.B. THIS IS A DRAWING, NO CONNECTIVITY

UNIVERSITY OF BRISTOL
HIGH ENERGY PHYSICS GROUP
TITLE
MODULE: top_mib_v3

H.H.WILLS PHYSICS LAB, TYNDALL AVE, BRISTOL, BS8 1TL.

MODULE PAGE: 1 OF 2
OVERALL PAGE: 1 OF 16

TOTAL NO. OF SHEETS

## ROOM=POWER

02. POWER | 07. BACKPLANE INTERFACE

(TOP LEVEL); MIB_HIERARCHY; 3. Clock Generator; 4. Clock Fanout; Wed Jul 3 07:32:48 2024; mtca_interface_board_reocc; SFP_RATE_SELECT<2..0>:SFP_TX_DISABLE<2..0>:SFP_TX_FAULT<2..0>:SFP_LOS<2..0>:SFP_RD_P<2..0>:SFP_RD_N<2..0>:SFP_TD_P<2..0>:SFP_TD_N<2..0>:SFP_SDA<2..0>:SFP_SCL<2..0>; CLK_SCL:CLK_SDA:CLK_SEL0:CLK_SEL1:CLK_INTR:CLK_LOL:CLK_RST:CLK_P<1..0>:CLK_N<1..0>; UPSTREAM_DATA_P<2..0>:UPSTREAM_DATA_N_<2..0>:SFP_DATA_OUT_P<2..0>:SFP_DATA_OUT_N<2..0>; DATA_SELECT_P2V5; DIRECT_US_DATA_2_P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

UNCONNECTED<91:0>:PWR_ON:AMC_N_ENABLE:TCK:TMS:TDO:TDI:GBE_TX_N:GBE_TX_P:GBE_RX_N:GBE_RX_P:IMPB_SCL:IMPB_SDA:DATA_OUT_P<11..0>:DATA_OUT_N<11..0>:DATA_IN_P<11..0>:DATA_IN_N<11..0>:REF_CLK_P<11..0>:REF_CLK_N<11..0>:AMC_GA<2..0>:AMC_N_PS<1..0>

05 TRENZ TE0712 FPGA MODULE

01. MODULE MANAGEMENT CTRL

TIMING1
1. D-FF FOR UPSTREAM
2. SFP DATA 1:2 FANOUTS

UNIVERSITY OF BRISTOL
HIGH ENERGY PHYSICS GROUP
TITLE
MODULE: top_mib_v3

H.H.WILLS PHYSICS LAB, TYNDALL AVE, BRISTOL, BS8 1TL.

MODULE PAGE: 2 OF 2
OVERALL PAGE: 2 OF 16

# MIN ESR OF 3 MILLI-OHMS ON OUTPUT OF PTH08T210WAD

# 12V TO 3V3 @ 14A DC-DC CONVERTER

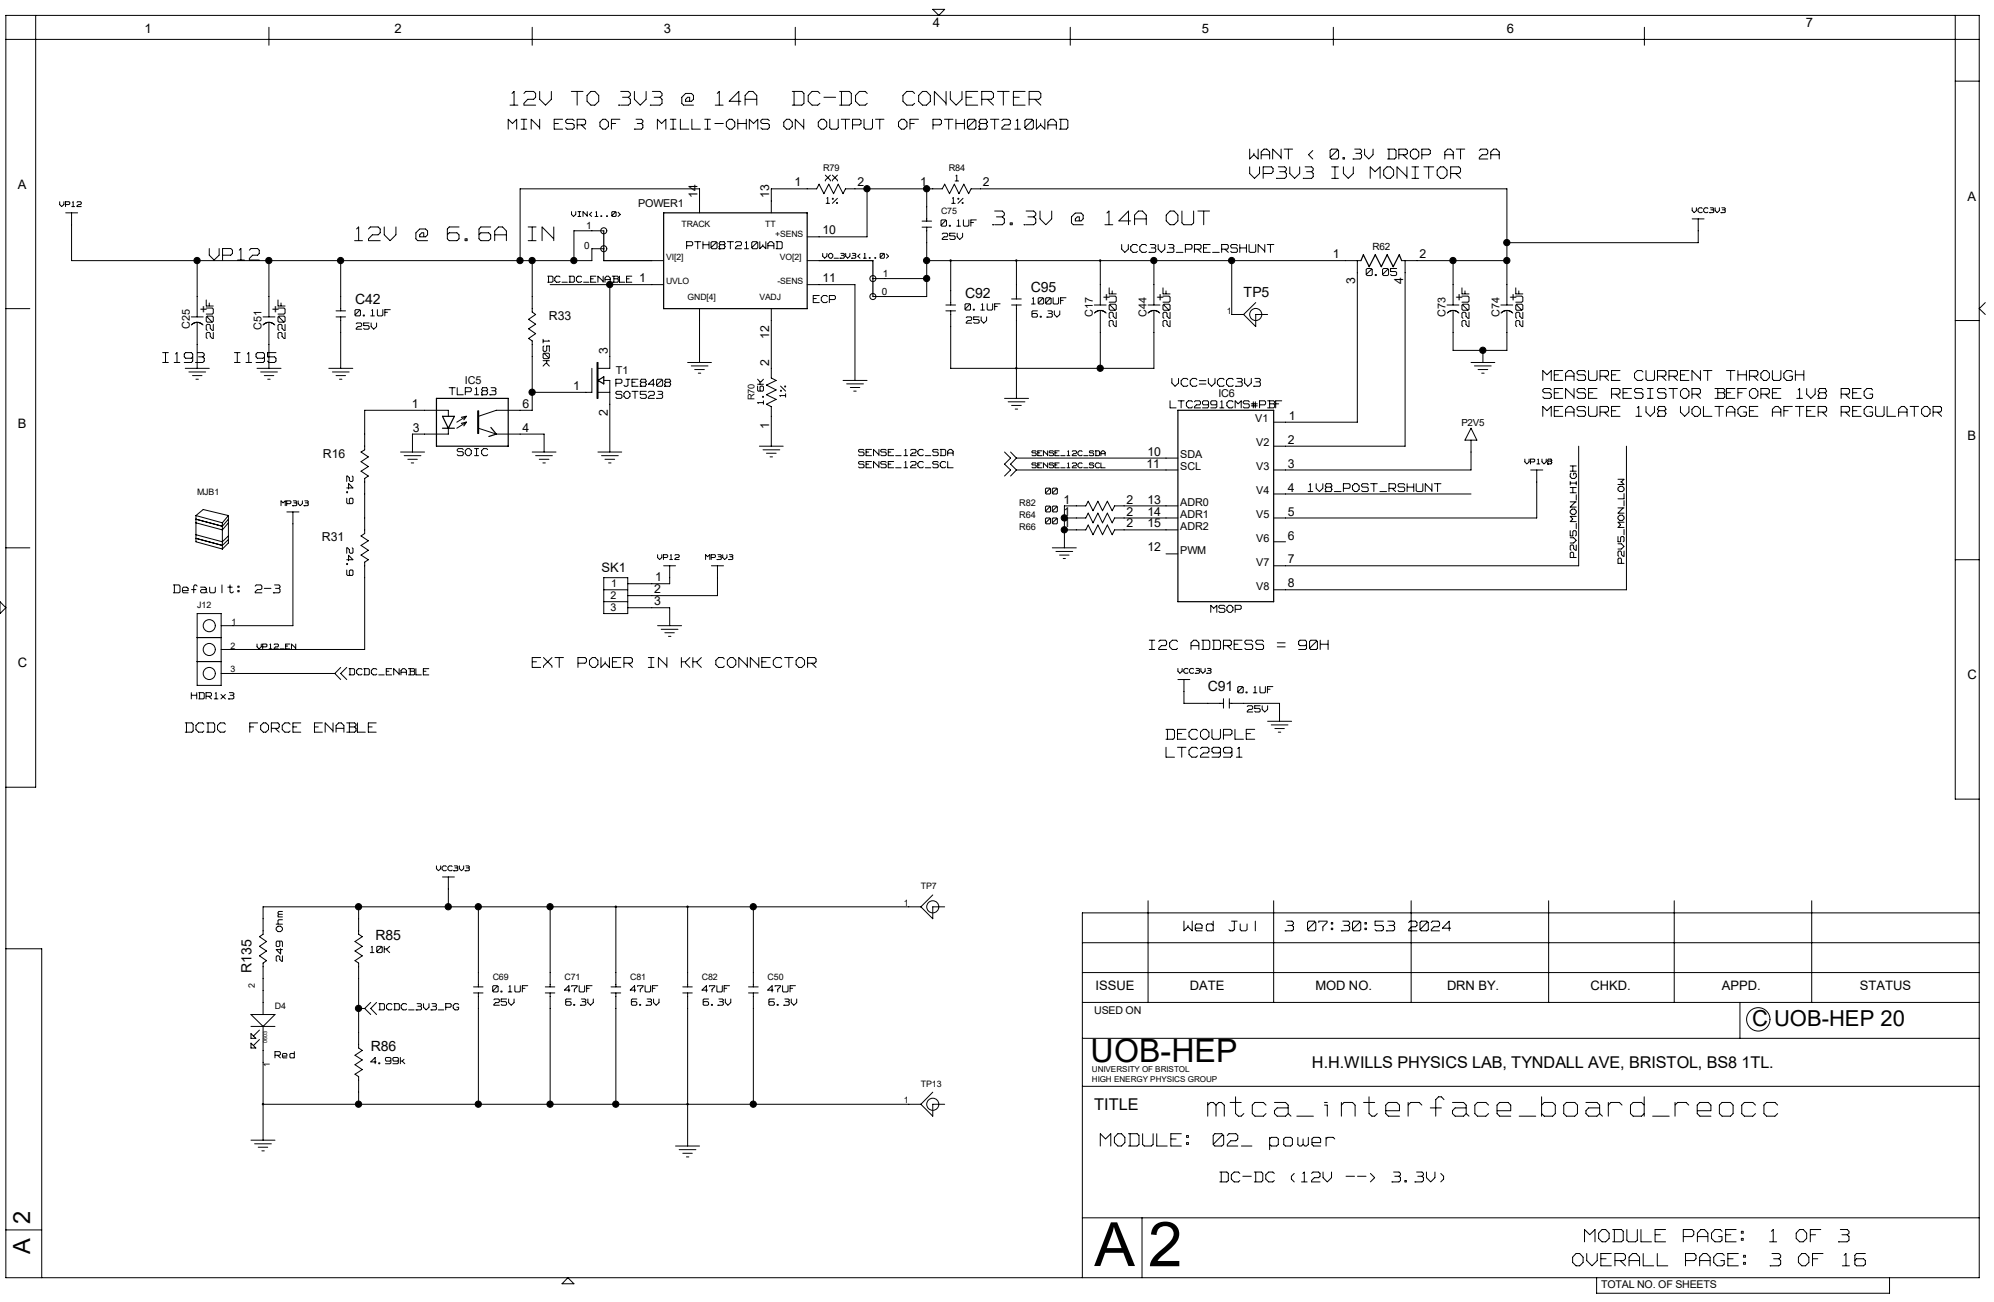
[picture p68: page 3]

MEASURE CURRENT THROUGH
SENSE RESISTOR BEFORE 1V8 REG
MEASURE 1V8 VOLTAGE AFTER REGULATOR

EXT POWER IN KK CONNECTOR

UNIVERSITY OF BRISTOL
HIGH ENERGY PHYSICS GROUP
TITLE
MODULE: 02_ power

H.H.WILLS PHYSICS LAB, TYNDALL AVE, BRISTOL, BS8 1TL.

# 12V TO 2V5 @ 14A DC-DC CONVERTER

# WANT <0.3V DROP AT 2A

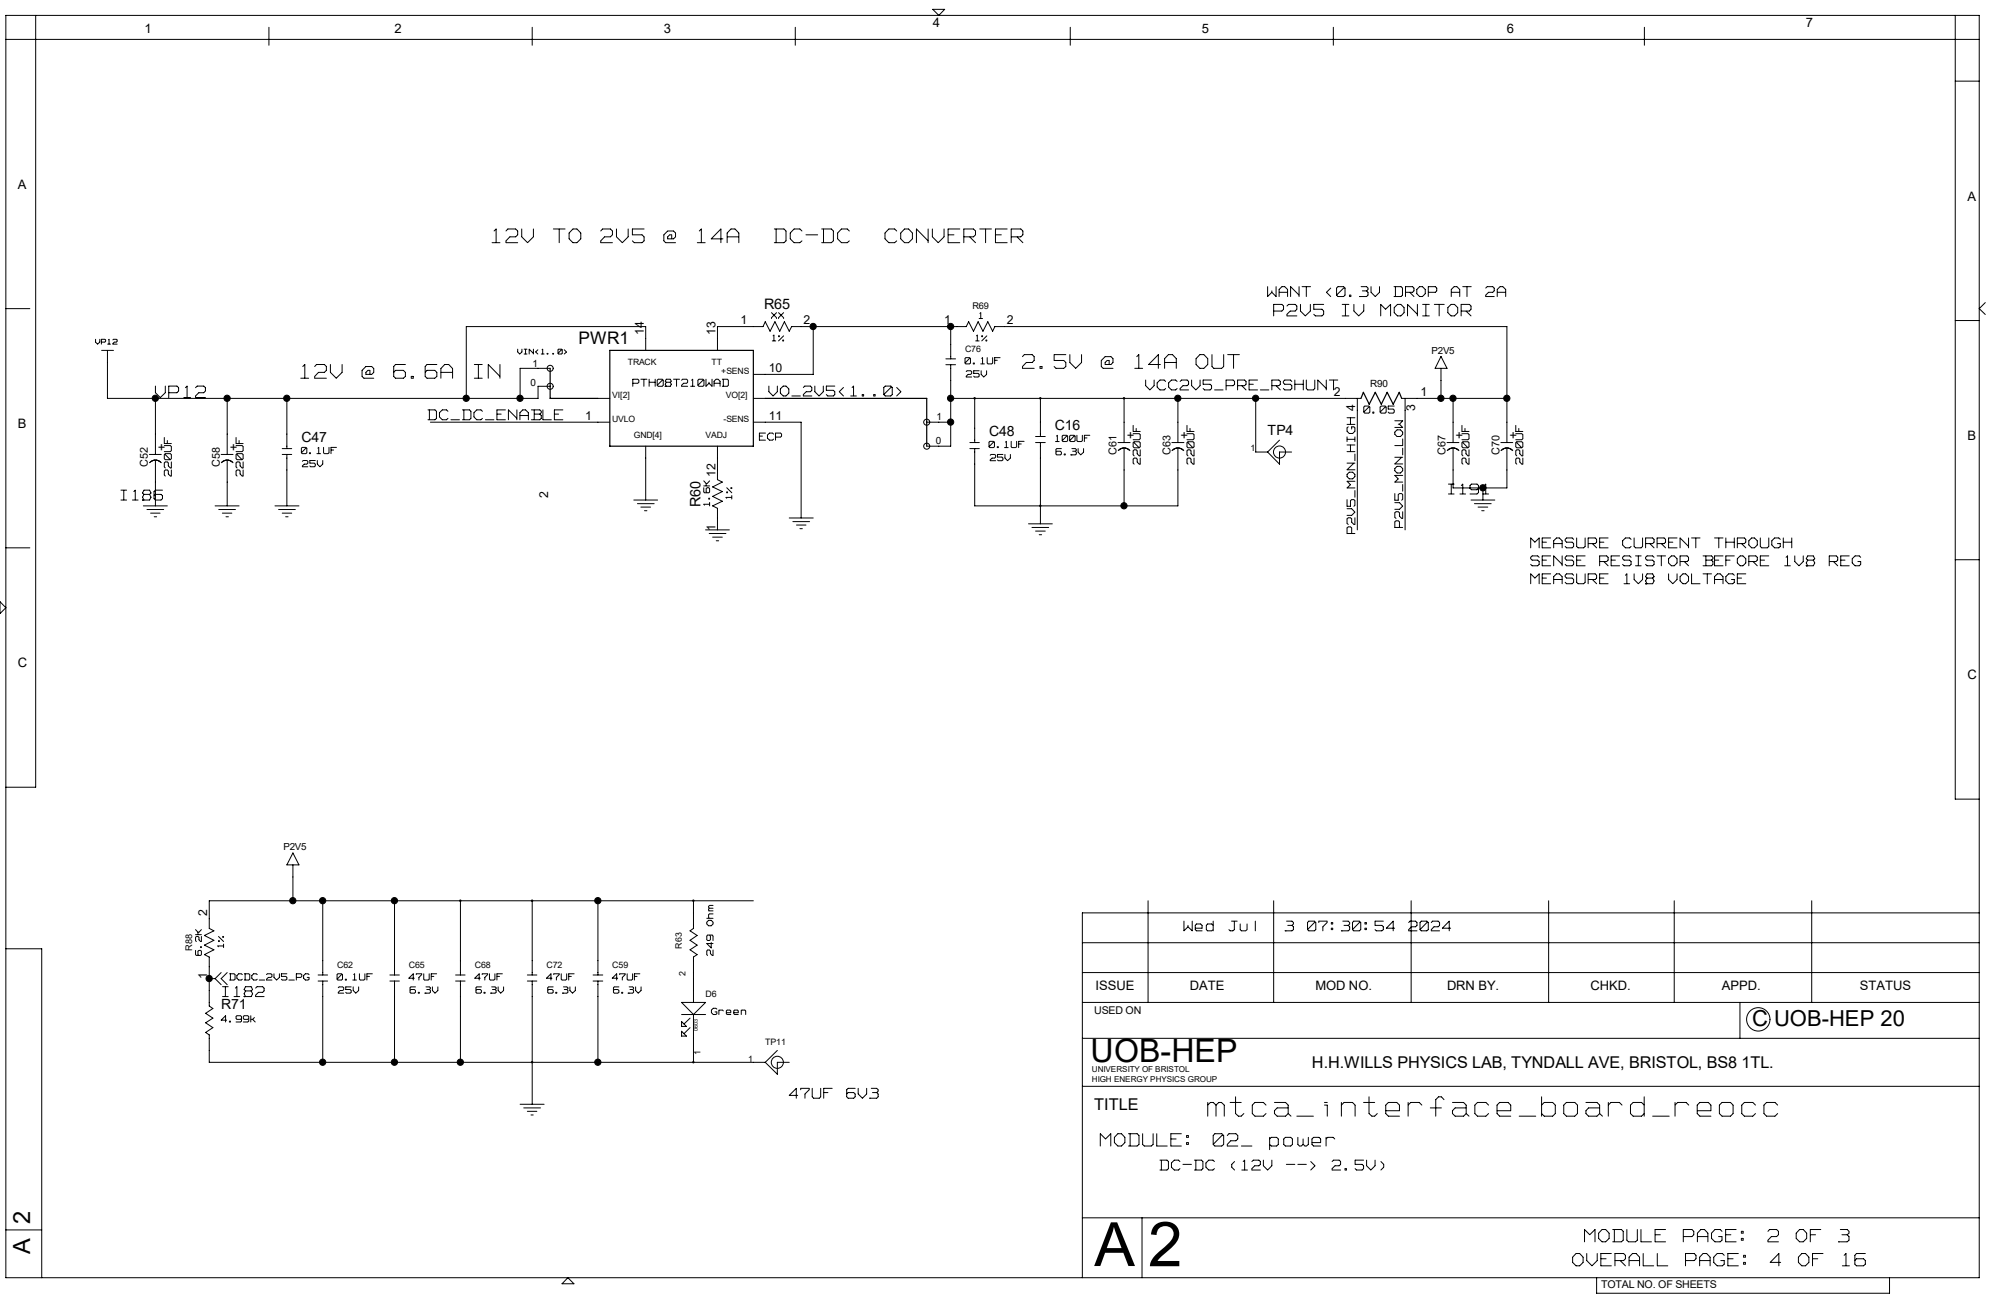
[picture p69: page 4]

MEASURE CURRENT THROUGH
SENSE RESISTOR BEFORE 1V8 REG
MEASURE 1V8 VOLTAGE

UNIVERSITY OF BRISTOL
HIGH ENERGY PHYSICS GROUP
TITLE
MODULE: 02_ power

H.H.WILLS PHYSICS LAB, TYNDALL AVE, BRISTOL, BS8 1TL.

A
A


MEASURE CURRENT THROUGH
SENSE RESISTOR BEFORE 1V8 REG

UNIVERSITY OF BRISTOL
HIGH ENERGY PHYSICS GROUP
TITLE
MODULE: 02_ power

H.H.WILLS PHYSICS LAB, TYNDALL AVE, BRISTOL, BS8 1TL.

# SFP DATA TO FPGA

## SFP1_CLKGEN_P


UNIVERSITY OF BRISTOL
HIGH ENERGY PHYSICS GROUP
TITLE
MODULE: 08_ timing

H.H.WILLS PHYSICS LAB, TYNDALL AVE, BRISTOL, BS8 1TL.
mtca_interface_board_reocc

# ROOM = CLK_GEN_X12

# VDDO_CLK


REF CLK TO CLOCK FANOUT MODULES, SEE PAGE-3 OF THIS MODULE

REF CLK TO D-FF, SEE PAGE-1 OF THIS MODULE

UNIVERSITY OF BRISTOL
HIGH ENERGY PHYSICS GROUP
TITLE
MODULE: 08_ timing

H.H.WILLS PHYSICS LAB, TYNDALL AVE, BRISTOL, BS8 1TL.

# ROOM = CLK_FO_0_5

100NF


USE 8 WAY LVPECL FANOUT
NOT AVAILABLE DUE TO
SUPPLY CHAIN ISSUES

... BECAUSE 6 WAY LVDS BUFFER

UNIVERSITY OF BRISTOL
HIGH ENERGY PHYSICS GROUP
TITLE
MODULE: 08_ timing

H.H.WILLS PHYSICS LAB, TYNDALL AVE, BRISTOL, BS8 1TL.

## SFP.RATE_SELECT<0>

A

Mon Mar 6 16:31:19 2023; mtca_interface_board_reocc; ROOM=SFP1 04. SFP_MODULE; ROOM=SFP3 04. SFP_MODULE; SFP.RATE_SELECT<2> SFP.TX_DISABLE<2> SFP.TX_FAULT<2> SFP.LOS<2>; SFP<29..0>; SFP.TD_P<2>; SFP.RD_N<2>; SFP.RD_P<2>; SFP.TD_N<0>; SFP.TD_P<0>; SFP.RD_P<0> SFP.RD_N<0>; SFP.SCL<0>; SFP.SDA<0>; SFP.TX_DISABLE<0>; SFP.LOS<0>; SFP.TX_FAULT<0>; SFP.SCL<2>; SFP.SDA<2>; SFP.TD_N<2>; SFP.SCL<1>; SFP.SDA<1>; SFP.TD_N<1>; SFP.TD_P<1>; SFP.RD_N<1>; SFP.RD_P<1>; SFP.LOS<1>; SFP.TX_FAULT<1>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

312.5 Mb/S Timing Signals
on 1000Base BX Link

ROOM=SFP2
04. SFP_MODULE

UNIVERSITY OF BRISTOL
HIGH ENERGY PHYSICS GROUP
TITLE
MODULE: 03_ sfp

H.H.WILLS PHYSICS LAB, TYNDALL AVE, BRISTOL, BS8 1TL.

MODULE PAGE: 1 OF 1
OVERALL PAGE: 9 OF 16

22UF
6.3V


UNIVERSITY OF BRISTOL
HIGH ENERGY PHYSICS GROUP
TITLE
MODULE: 04_ sfp_module

H.H.WILLS PHYSICS LAB, TYNDALL AVE, BRISTOL, BS8 1TL.

JTAG CONNECTOR | EEPROM

# AUX IO INTERFACE

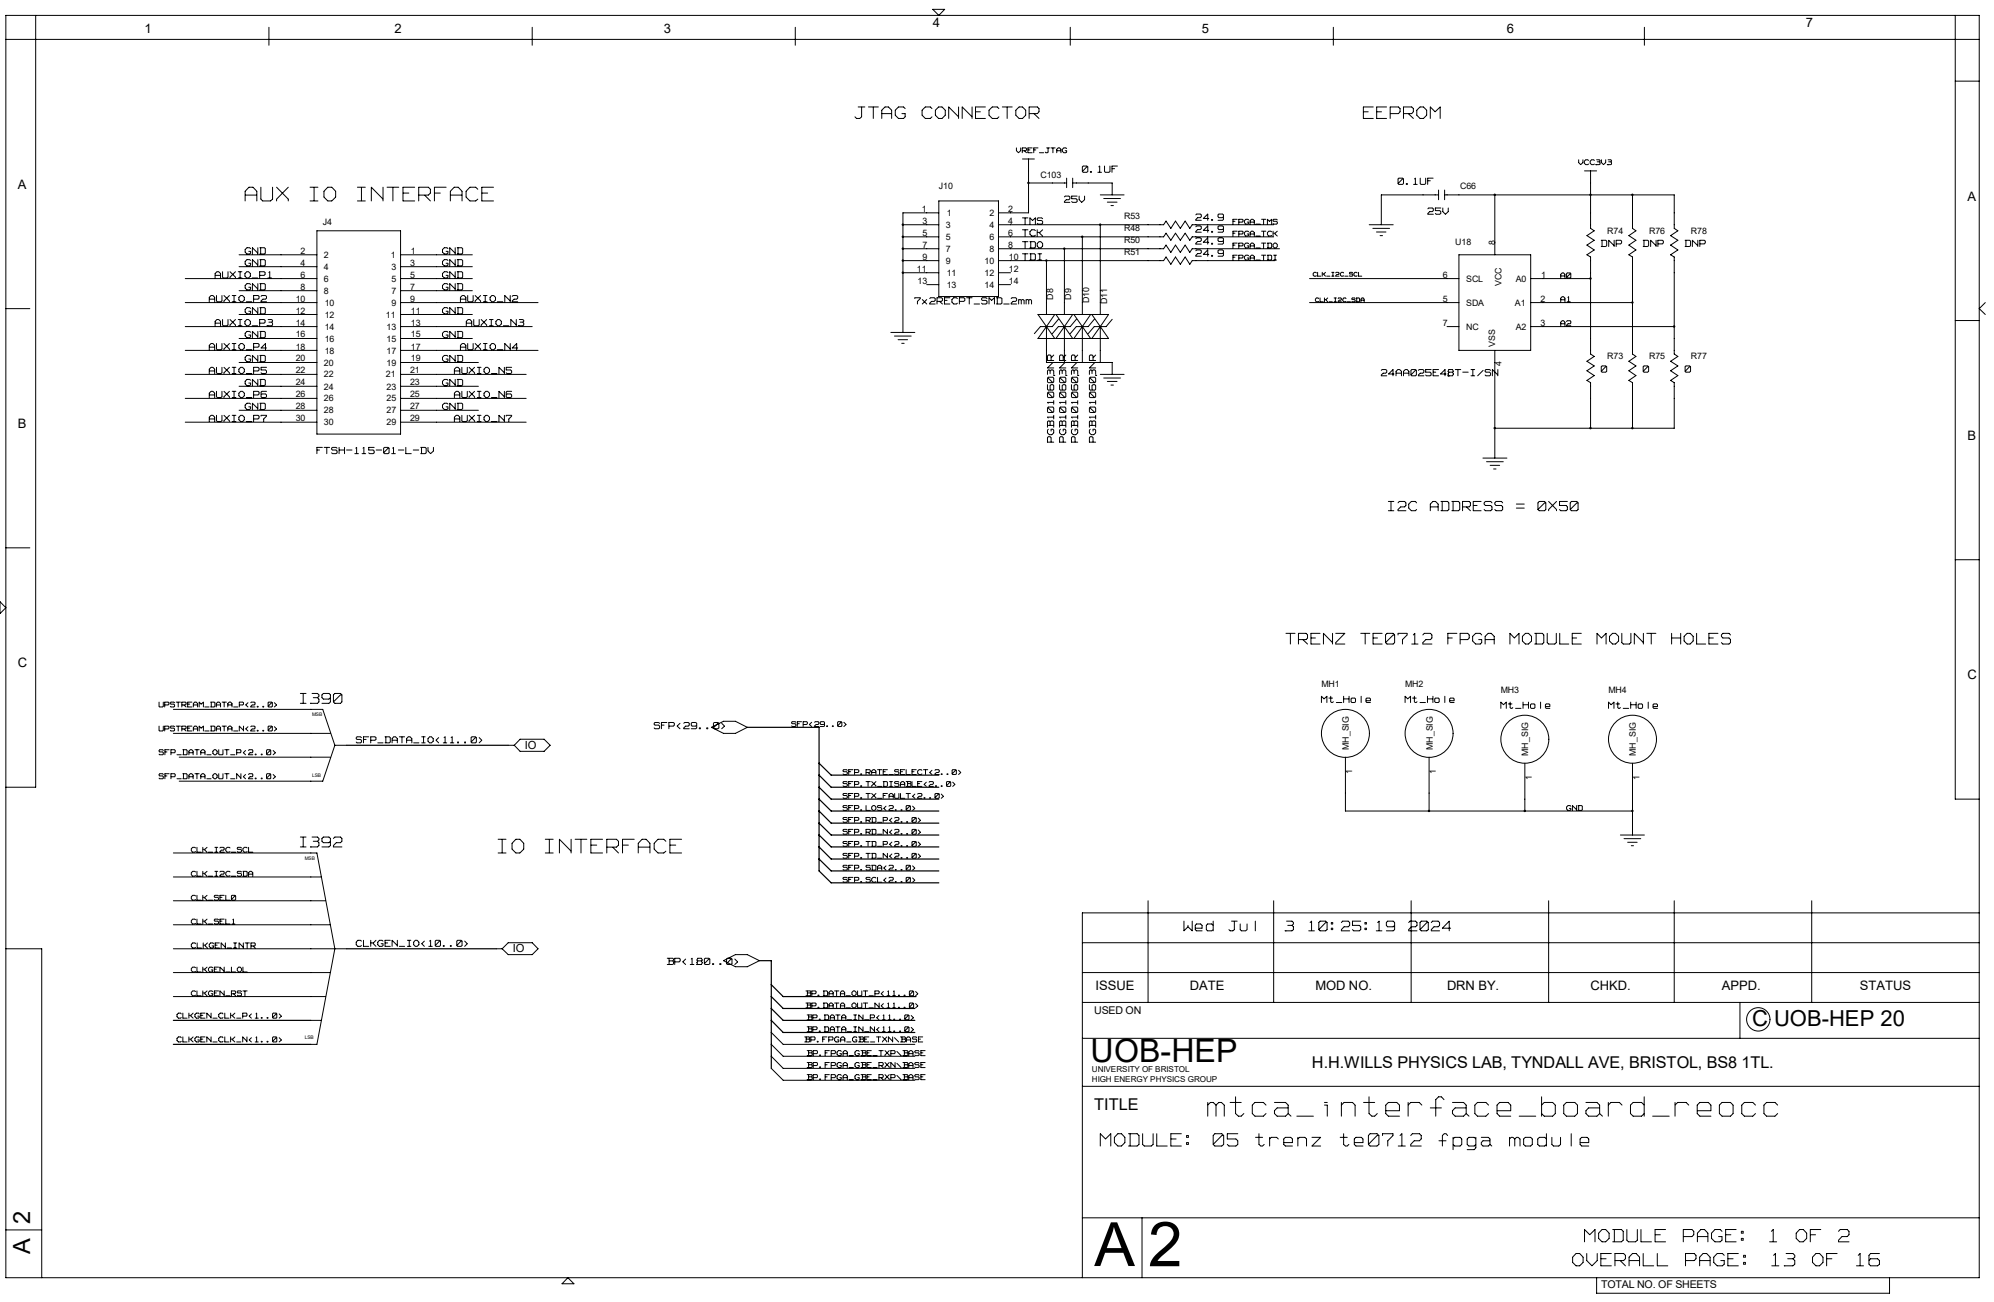
[picture p70: page 11]

TRENZ TE0712 FPGA MODULE MOUNT HOLES

UNIVERSITY OF BRISTOL
HIGH ENERGY PHYSICS GROUP
TITLE
MODULE: 05 trenz te0712 fpga module

H.H.WILLS PHYSICS LAB, TYNDALL AVE, BRISTOL, BS8 1TL.

I419

## P3V3_OUT0

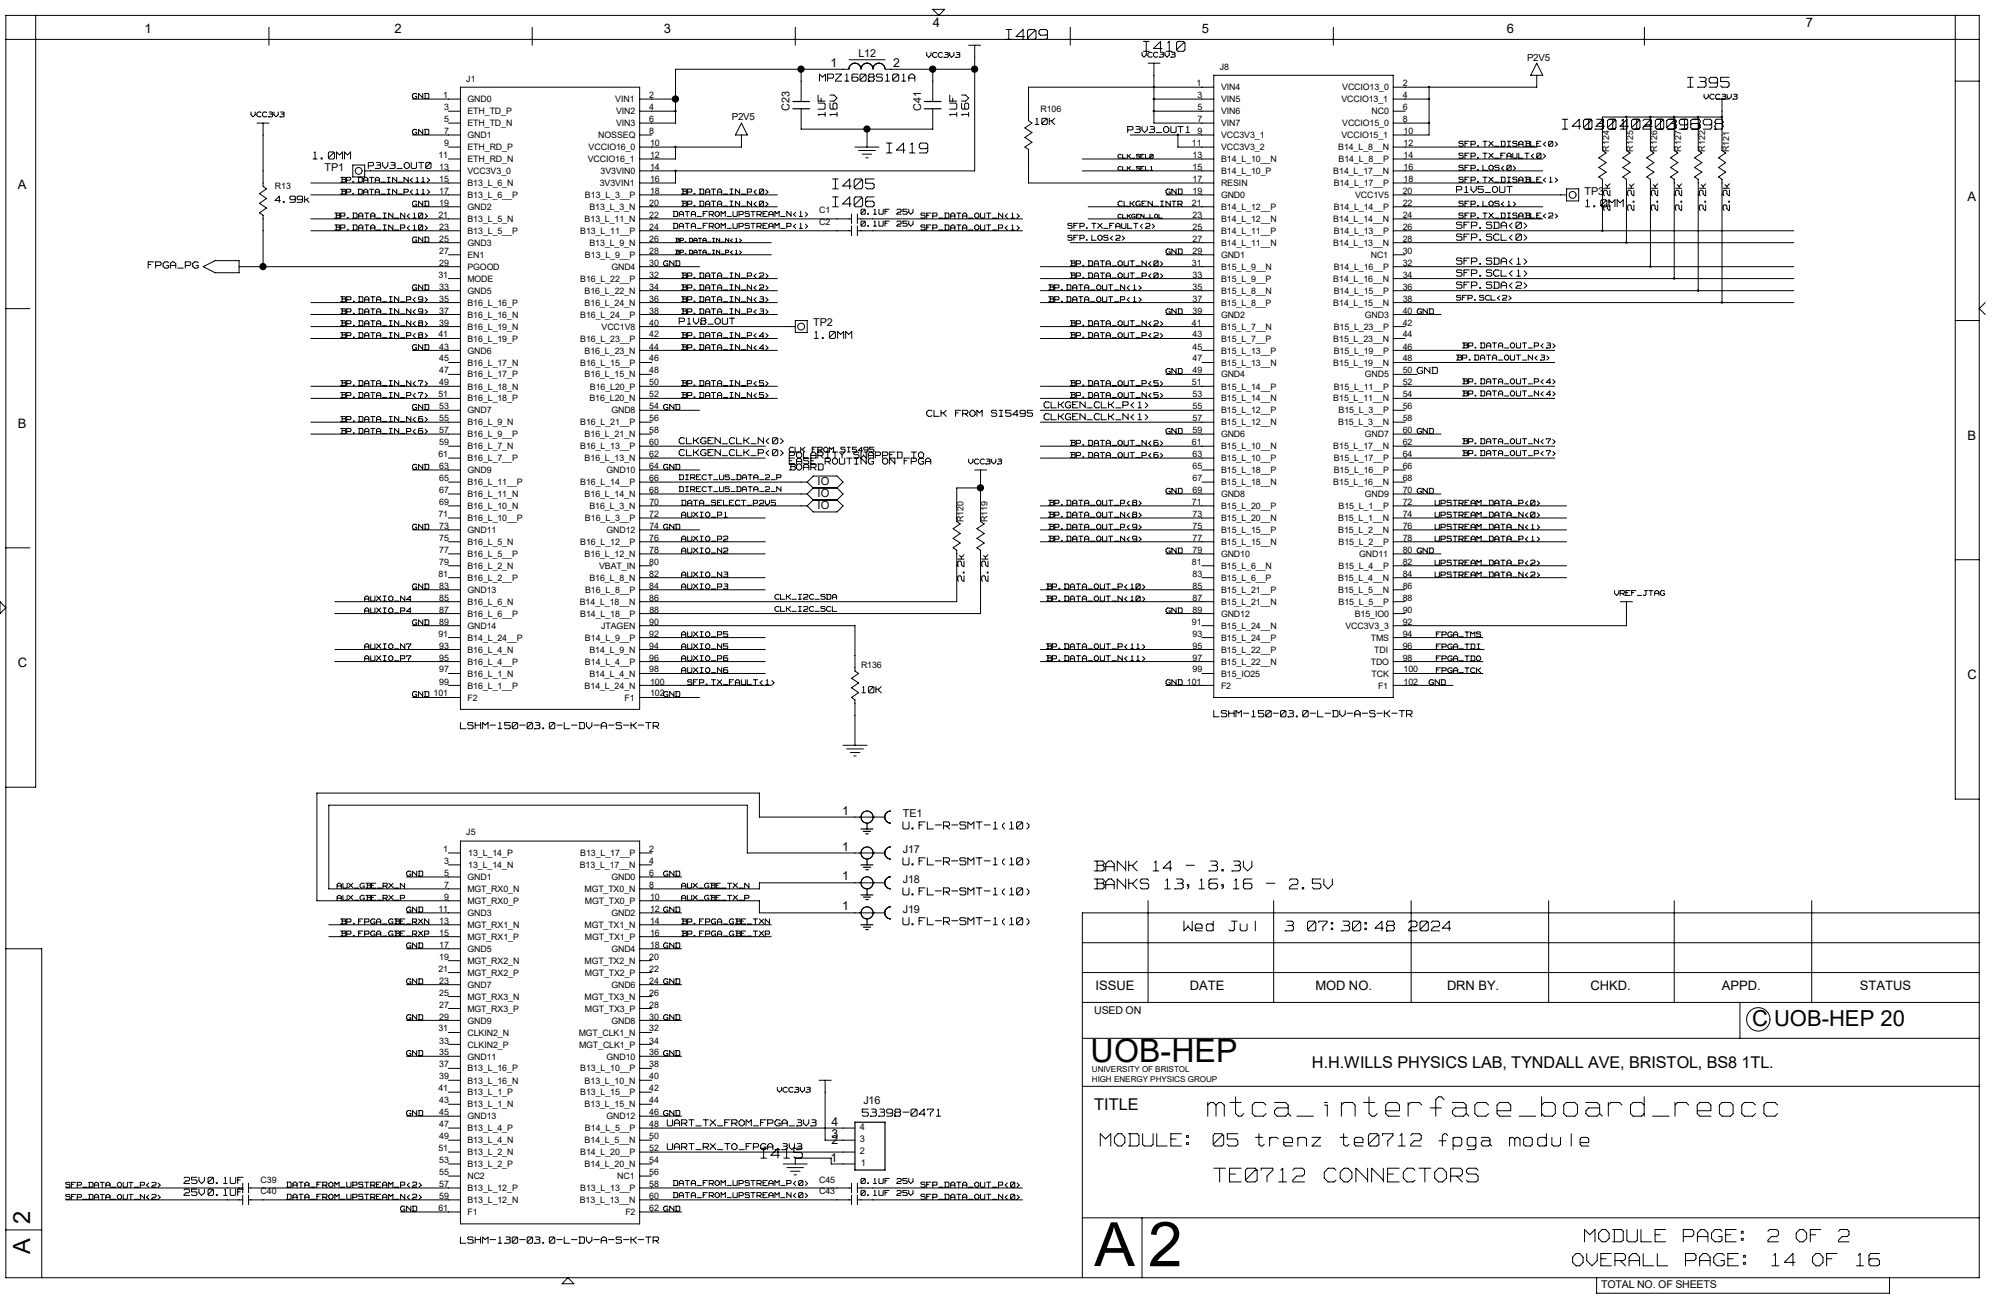
[picture p71: page 12]

CLK FROM SI5495
EASE ROUTING ON FPGA POLARITY SWAPPED TO
BOARD

UNIVERSITY OF BRISTOL
HIGH ENERGY PHYSICS GROUP
TITLE
MODULE: 05 trenz te0712 fpga module

H.H.WILLS PHYSICS LAB, TYNDALL AVE, BRISTOL, BS8 1TL.

# MODULE MANAGEMENT CONTROL IO INTERFACE

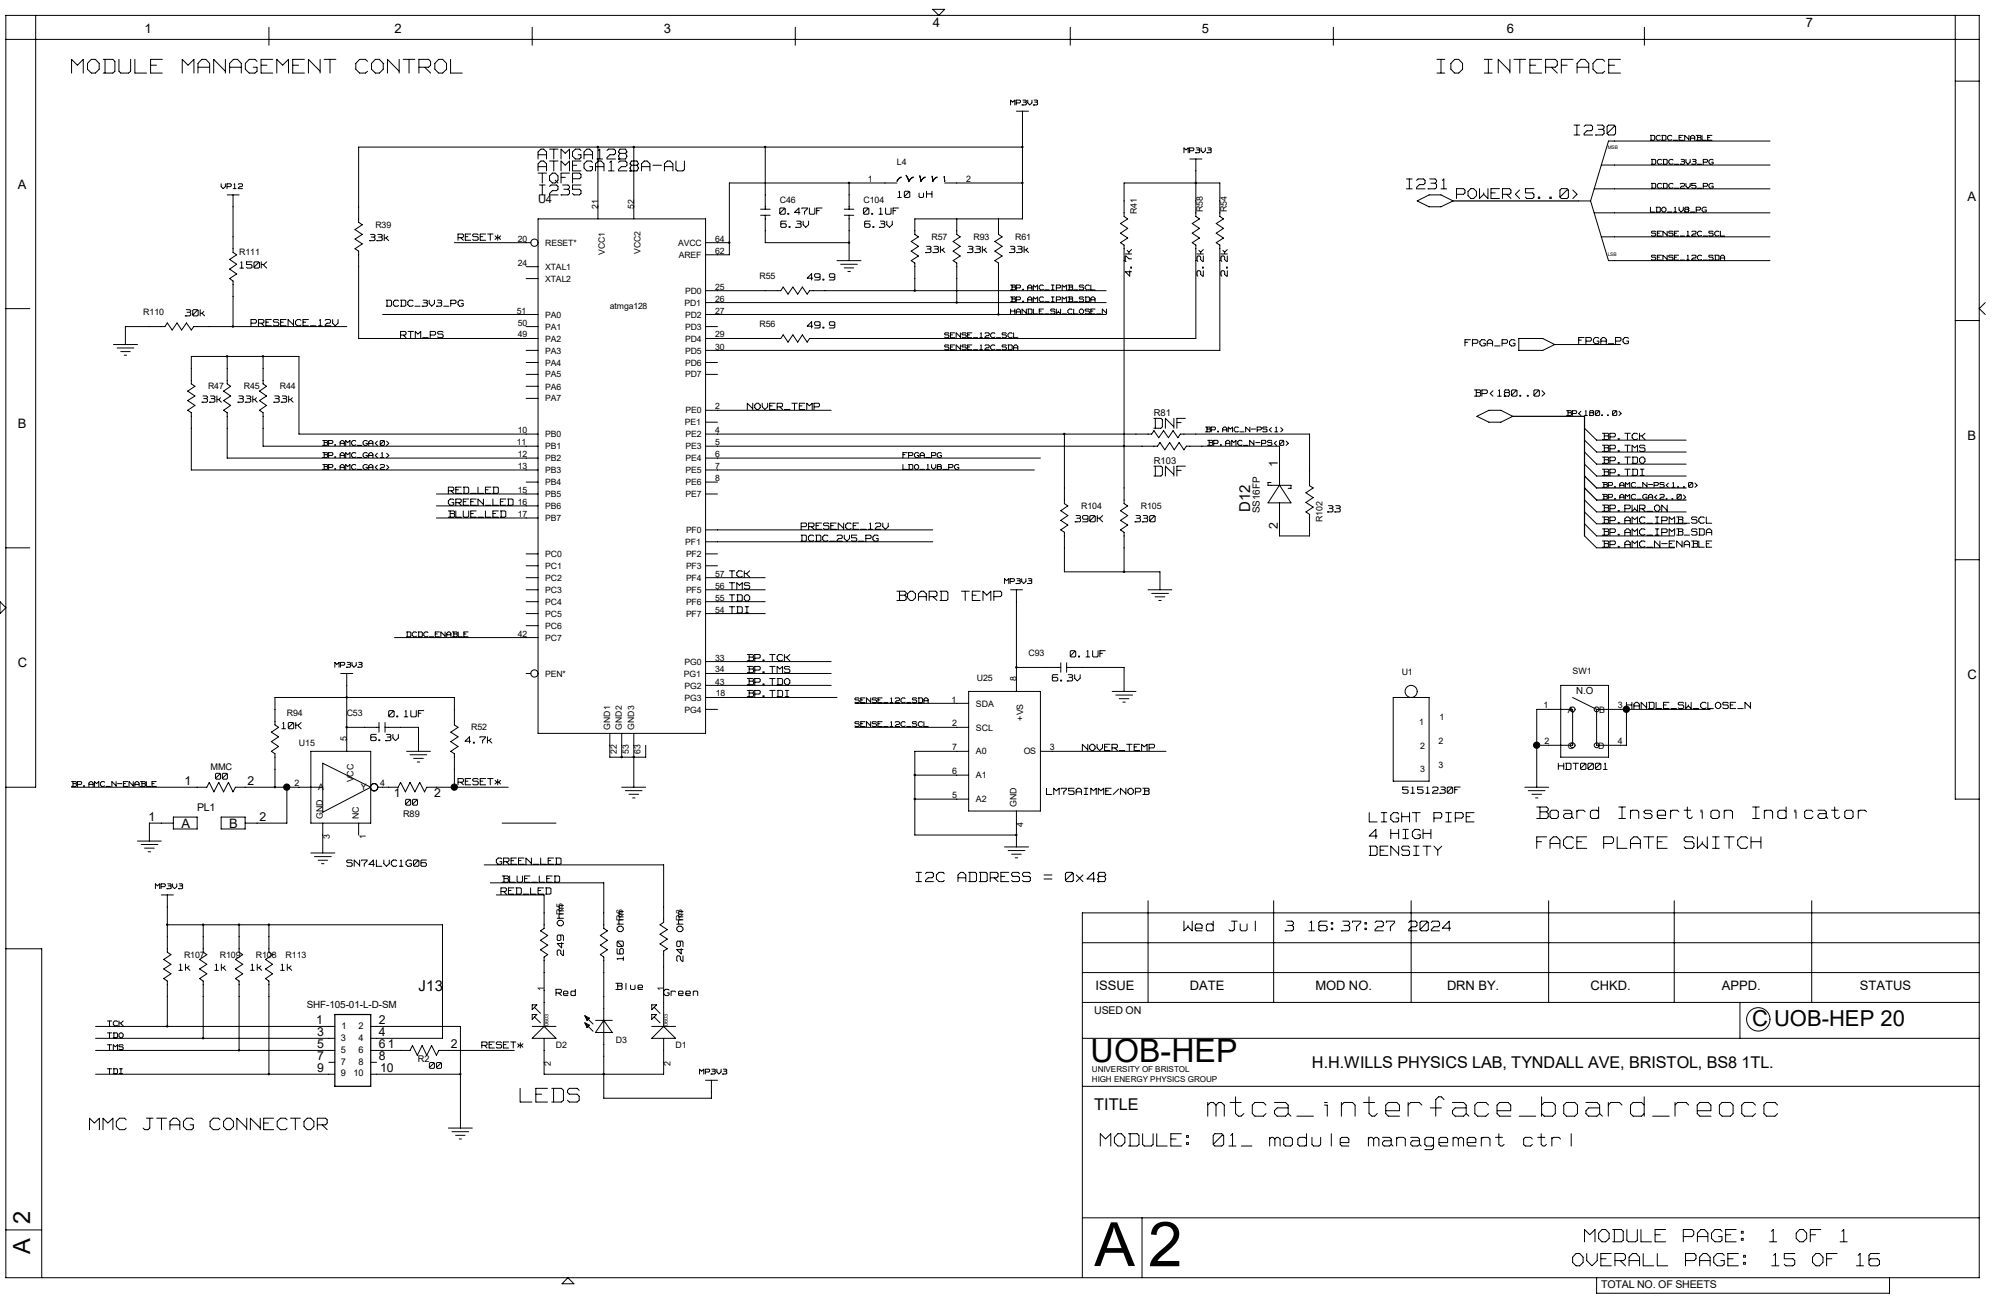
[picture p72: page 13]

1 R102 GND NC VCC GND +VS

UNIVERSITY OF BRISTOL
HIGH ENERGY PHYSICS GROUP
TITLE
MODULE: 01_ module management ctrl

H.H.WILLS PHYSICS LAB, TYNDALL AVE, BRISTOL, BS8 1TL.

# TONGUE 2 MEZZENINE CONNECTOR

## MP3V3_IN

2-16) of PICMG_ATCA; ESD PROTECTION; FRONT PANEL MOUNT HOLES; IO INTERFACE; Wed Jul 3 07:30:44 2024; mtca_interface_board_reocc; GND; BP.DATA_OUT_N<11>; BP.DATA_OUT_P<11>; BP.DATA_OUT_N<10>; BP.DATA_OUT_P<10>; BP.DATA_OUT_N<9>; BP.DATA_OUT_P<9>; BP.DATA_OUT_N<8>; BP.DATA_OUT_P<8>; BP.DATA_OUT_N<7>; BP.DATA_OUT_P<7>; BP.DATA_OUT_N<6>; BP.DATA_OUT_P<6>; BP.DATA_OUT_N<5>; BP.DATA_OUT_P<5>; BP.DATA_OUT_N<4>; BP.DATA_OUT_P<4>; BP.DATA_OUT_N<3>; BP.DATA_OUT_P<3>; BP.DATA_OUT_N<2>; BP.DATA_OUT_P<2>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

LSHM-130-03.0-L-DV-A-S-K-TR

LSHM-150-03.0-L-DV-A-S-K-TR

TONGUE 2 MEZZENINE MOUNT HOLES

Promotes save ESD discharge
during board insertion (see pg

UNIVERSITY OF BRISTOL
HIGH ENERGY PHYSICS GROUP
TITLE
MODULE: 07_ backplane interface

H.H.WILLS PHYSICS LAB, TYNDALL AVE, BRISTOL, BS8 1TL.

BP PLANE CONNECTOR TONGUE 1

MODULE PAGE: 1 OF 1
OVERALL PAGE: 16 OF 16
