uob-hep-cad/uob-hep-pc072/hardware/Schematics/dune_mib_v2_fp_ethernet_5jul23.pdf

6.3V

1 uH | 1 uH 10UF

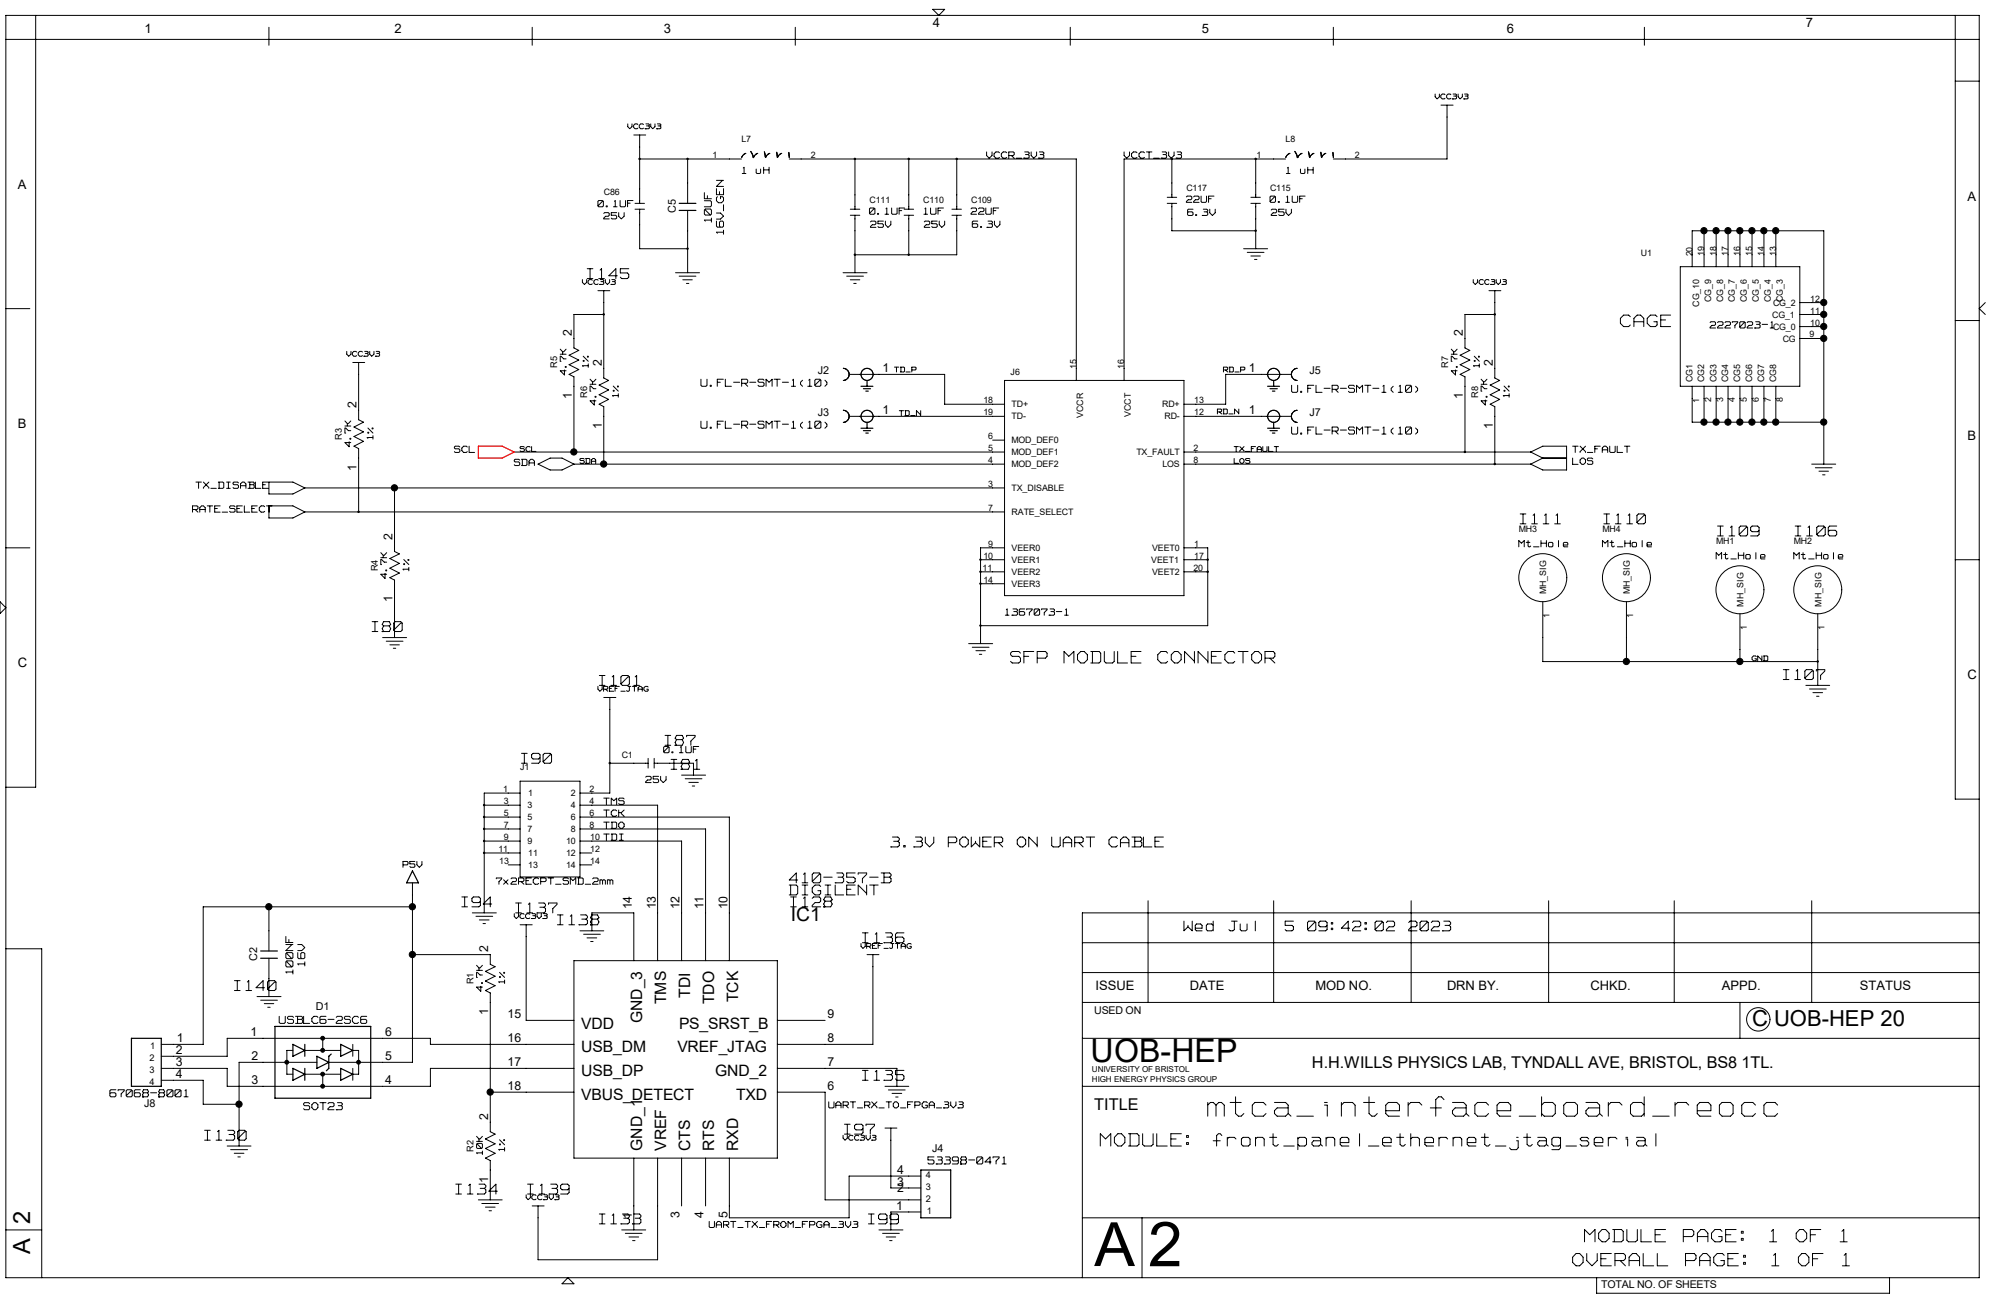
[picture p96: page 1]

3.3V POWER ON UART CABLE

UNIVERSITY OF BRISTOL
HIGH ENERGY PHYSICS GROUP
TITLE
MODULE: front_panel_ethernet_jtag_serial

H.H.WILLS PHYSICS LAB, TYNDALL AVE, BRISTOL, BS8 1TL.

TOTAL NO. OF SHEETS
