uob-hep-cad/uob-hep-pc072/hardware/Schematics/dune_mib_v2_4apr23_bw.pdf

1 | 3 | 4
5 6

mtca_interface_board_reocc; Thu Mar 2 11:14:02 2023; USED ON; ISSUE; APPD. DATE; MOD NO.; DRN BY.; CHKD.; STATUS; C UOB-HEP 20; UOB-HEP

N.B. THIS IS A DRAWING, NO CONNECTIVITY

UNIVERSITY OF BRISTOL
HIGH ENERGY PHYSICS GROUP
TITLE
MODULE: top

H.H.WILLS PHYSICS LAB, TYNDALL AVE, BRISTOL, BS8 1TL.

MODULE PAGE: 1 OF 2
OVERALL PAGE: 1 OF 16

TOTAL NO. OF SHEETS

## ROOM=POWER

02. POWER | 07. BACKPLANE INTERFACE FPGA_PG

(TOP LEVEL); MIB_HIERARCHY; 4. Clock Fanout; 3. Clock Generator; Wed Mar 8 11:34:07 2023; mtca_interface_board_reocc; DCDC_ENABLE:DCDC_3V3_PG:DCDC_2V5_PG:LDO_1V8_PG:SENSE_I2C_SCL:SENSE_I2C_SDA; 03. SFP; CLK_SCL:CLK_SDA:CLK_SEL0:CLK_SEL1:CLK_INTR:CLK_LOL:CLK_RST:CLK_P<1..0>:CLK_N<1..0>; UPSTREAM_DATA_P<2..0>:UPSTREAM_DATA_N_<2..0>:SFP_DATA_OUT_P<2..0>:SFP_DATA_OUT_N<2..0>; 08. TIMING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

UNCONNECTED<91:0>:PWR_ON:AMC_N_ENABLE:TCK:TMS:TDO:TDI:GBE_TX_N:GBE_TX_P:GBE_RX_N:GBE_RX_P:IMPB_SCL:IMPB_SDA:DATA_OUT_P<11..0>:DATA_OUT_N<11..0>:DATA_IN_P<11..0>:DATA_IN_N<11..0>:REF_CLK_P<11..0>:REF_CLK_N<11..0>:AMC_GA<2..0>:AMC_N_PS<1..0>

05 TRENZ TE0712 FPGA MODULE

01. MODULE MANAGEMENT CTRL

TIMING1
1. D-FF FOR UPSTREAM

2. SFP DATA 1:2 FANOUTS

UNIVERSITY OF BRISTOL
HIGH ENERGY PHYSICS GROUP
TITLE
MODULE: top

H.H.WILLS PHYSICS LAB, TYNDALL AVE, BRISTOL, BS8 1TL.

MODULE PAGE: 2 OF 2
OVERALL PAGE: 2 OF 16

# 3.3V @ 14A OUT

# 12V TO 3V3 @ 14A DC-DC CONVERTER

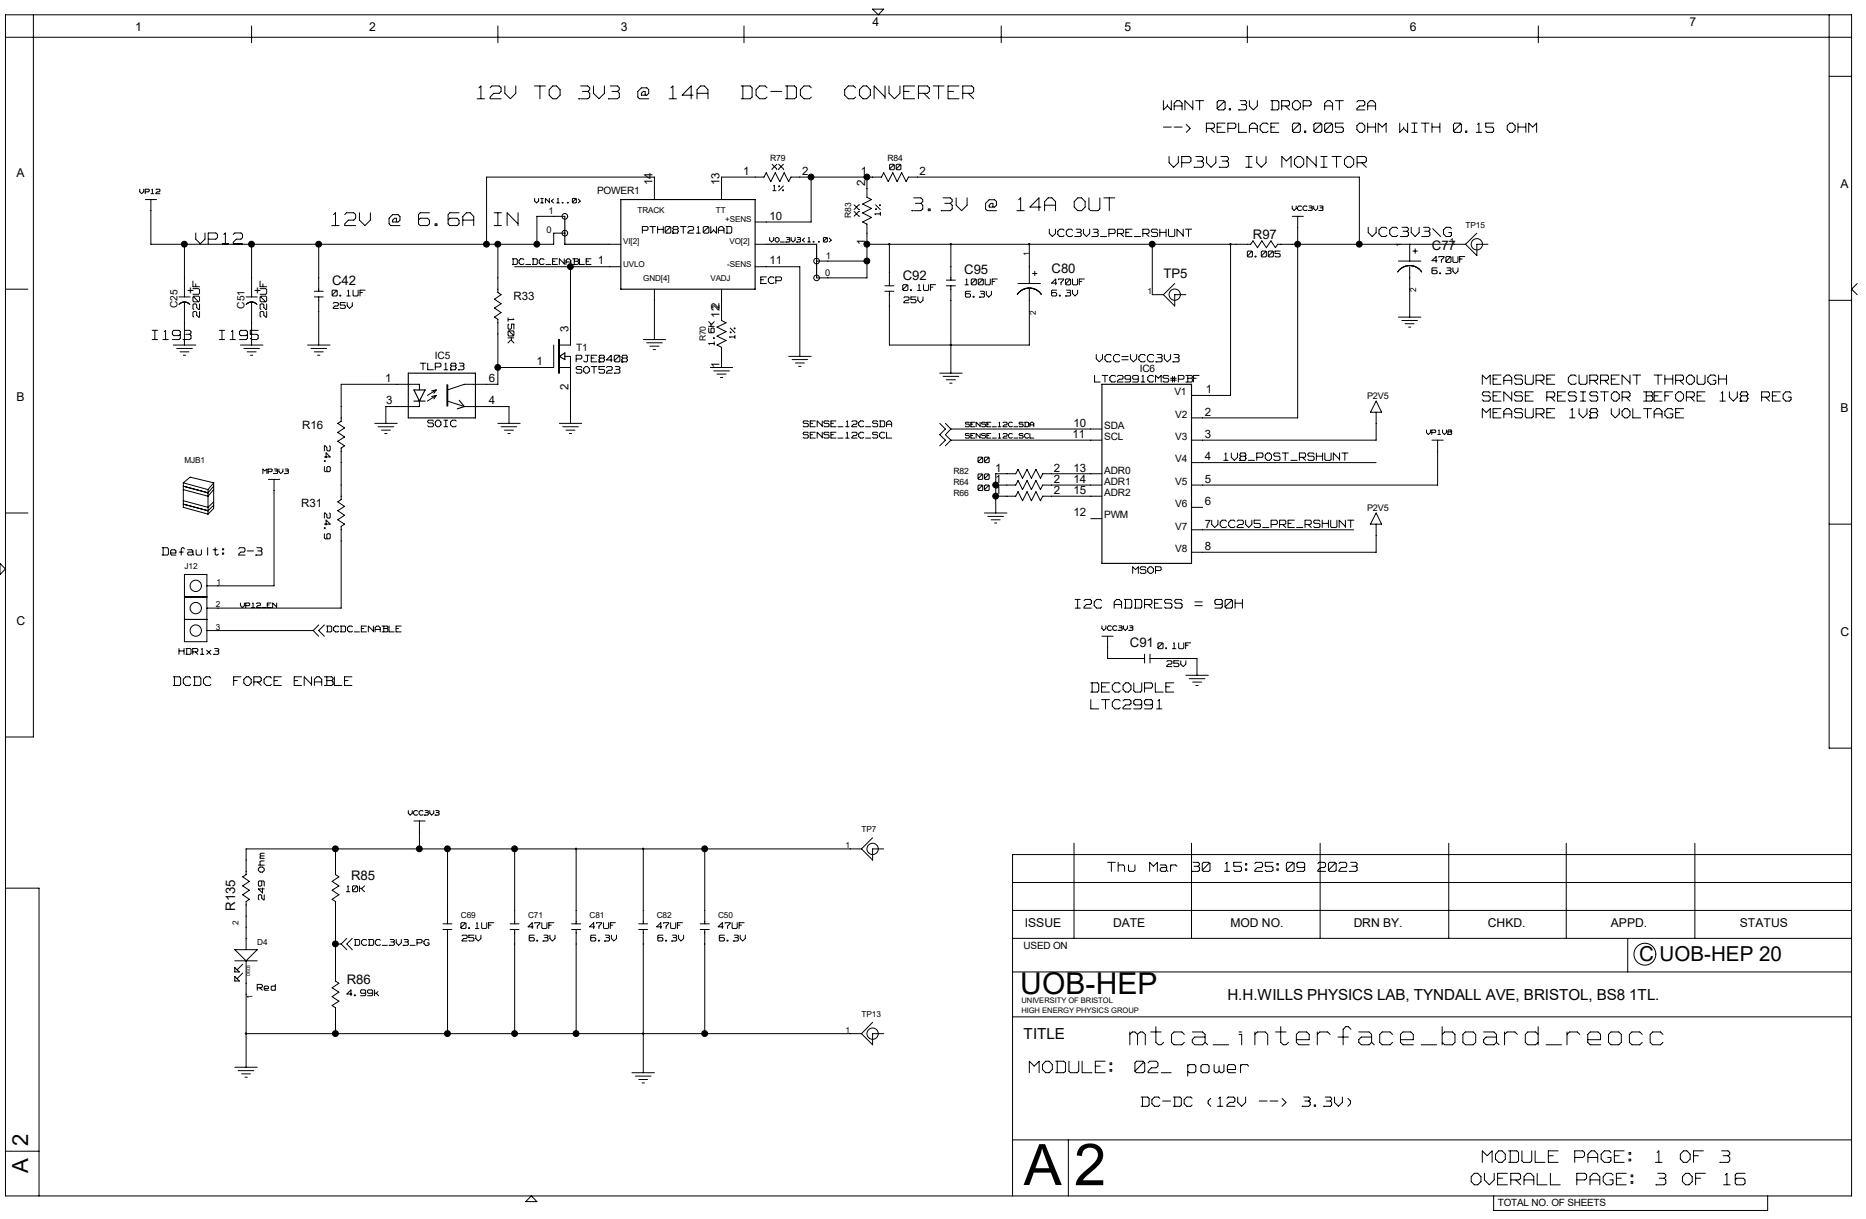
[picture p97: page 3]

WANT 0.3V DROP AT 2A
--> REPLACE 0.005 OHM WITH 0.15 OHM
VP3V3 IV MONITOR

MEASURE CURRENT THROUGH
SENSE RESISTOR BEFORE 1V8 REG
MEASURE 1V8 VOLTAGE

UNIVERSITY OF BRISTOL
HIGH ENERGY PHYSICS GROUP
TITLE
MODULE: 02_ power

H.H.WILLS PHYSICS LAB, TYNDALL AVE, BRISTOL, BS8 1TL.

# --> REPLACE 0.005 OHM WITH 0.15 OHM

# WANT 0.3V DROP AT 2A

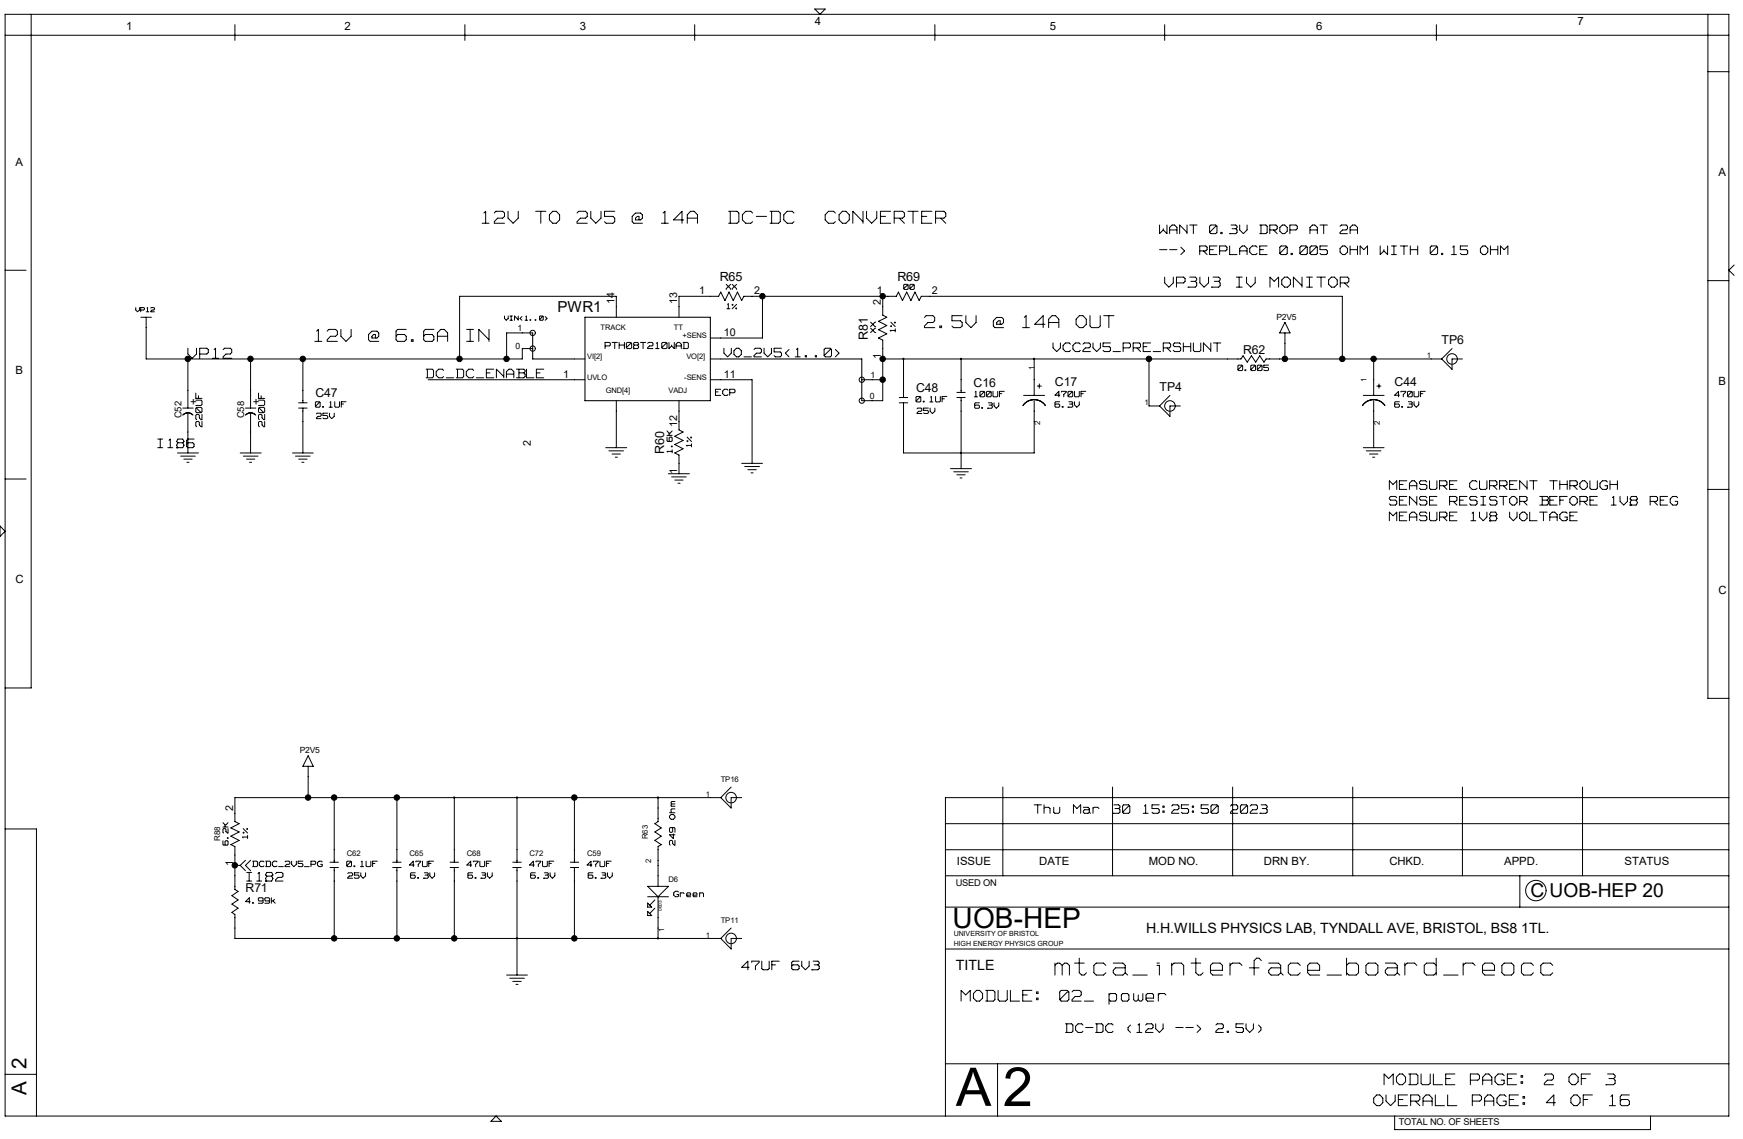
[picture p98: page 4]

MEASURE CURRENT THROUGH
SENSE RESISTOR BEFORE 1V8 REG
MEASURE 1V8 VOLTAGE

UNIVERSITY OF BRISTOL
HIGH ENERGY PHYSICS GROUP
TITLE

H.H.WILLS PHYSICS LAB, TYNDALL AVE, BRISTOL, BS8 1TL.

A
A

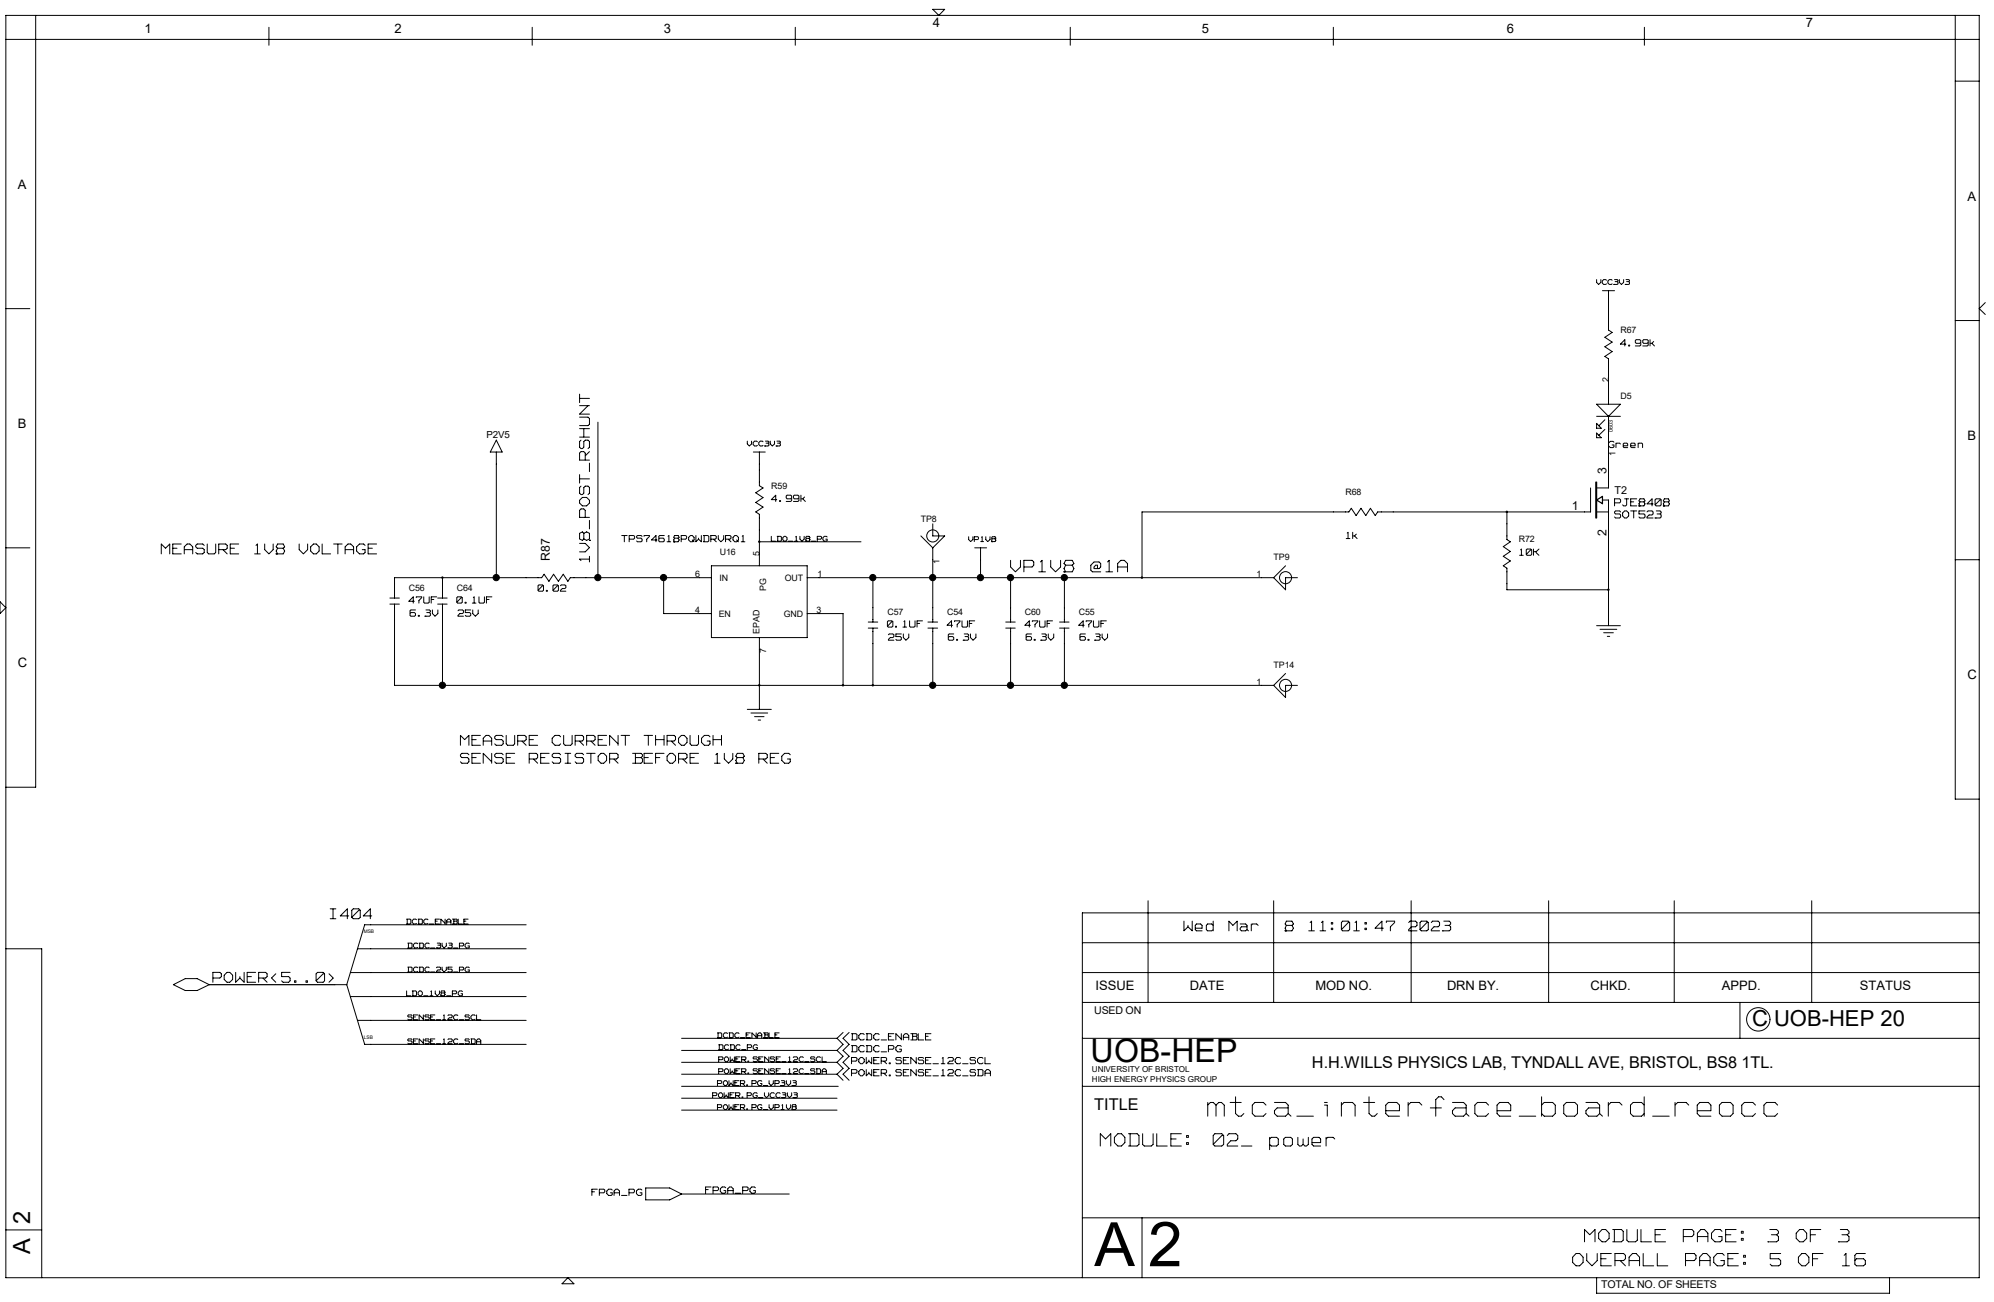
[picture p99: page 5]

MEASURE CURRENT THROUGH
SENSE RESISTOR BEFORE 1V8 REG

UNIVERSITY OF BRISTOL
HIGH ENERGY PHYSICS GROUP
TITLE
MODULE: 02_ power

H.H.WILLS PHYSICS LAB, TYNDALL AVE, BRISTOL, BS8 1TL.

# SFP DATA TO FPGA

## UN$1$SY58608U$I557$VREF 16V_GEN

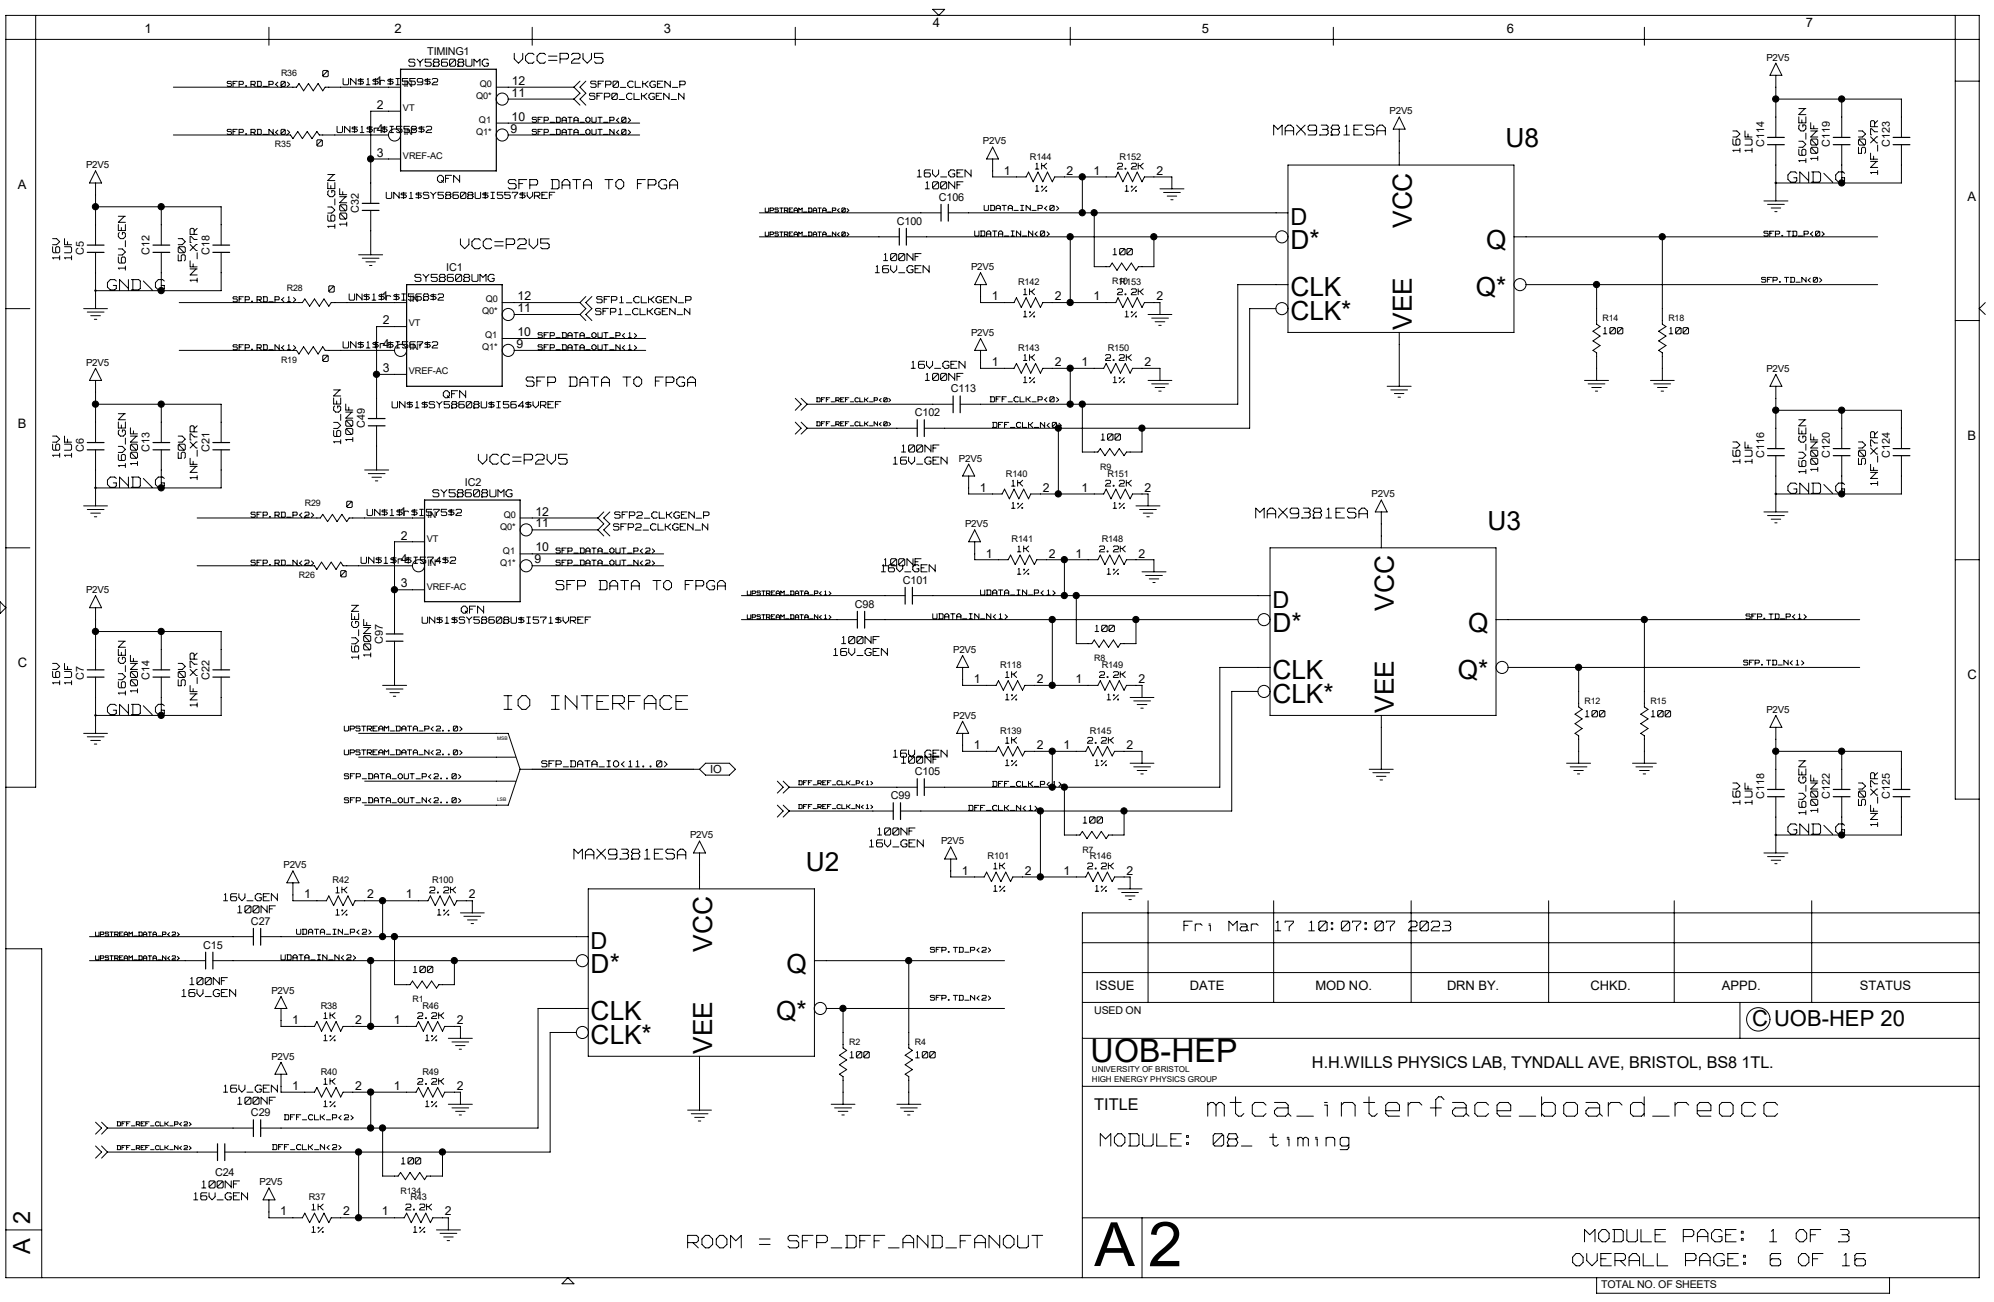
[picture p100: page 6]

UNIVERSITY OF BRISTOL
HIGH ENERGY PHYSICS GROUP
TITLE
MODULE: 08_ timing

H.H.WILLS PHYSICS LAB, TYNDALL AVE, BRISTOL, BS8 1TL.

# ROOM = CLK_GEN_X12

# VP1V8\G

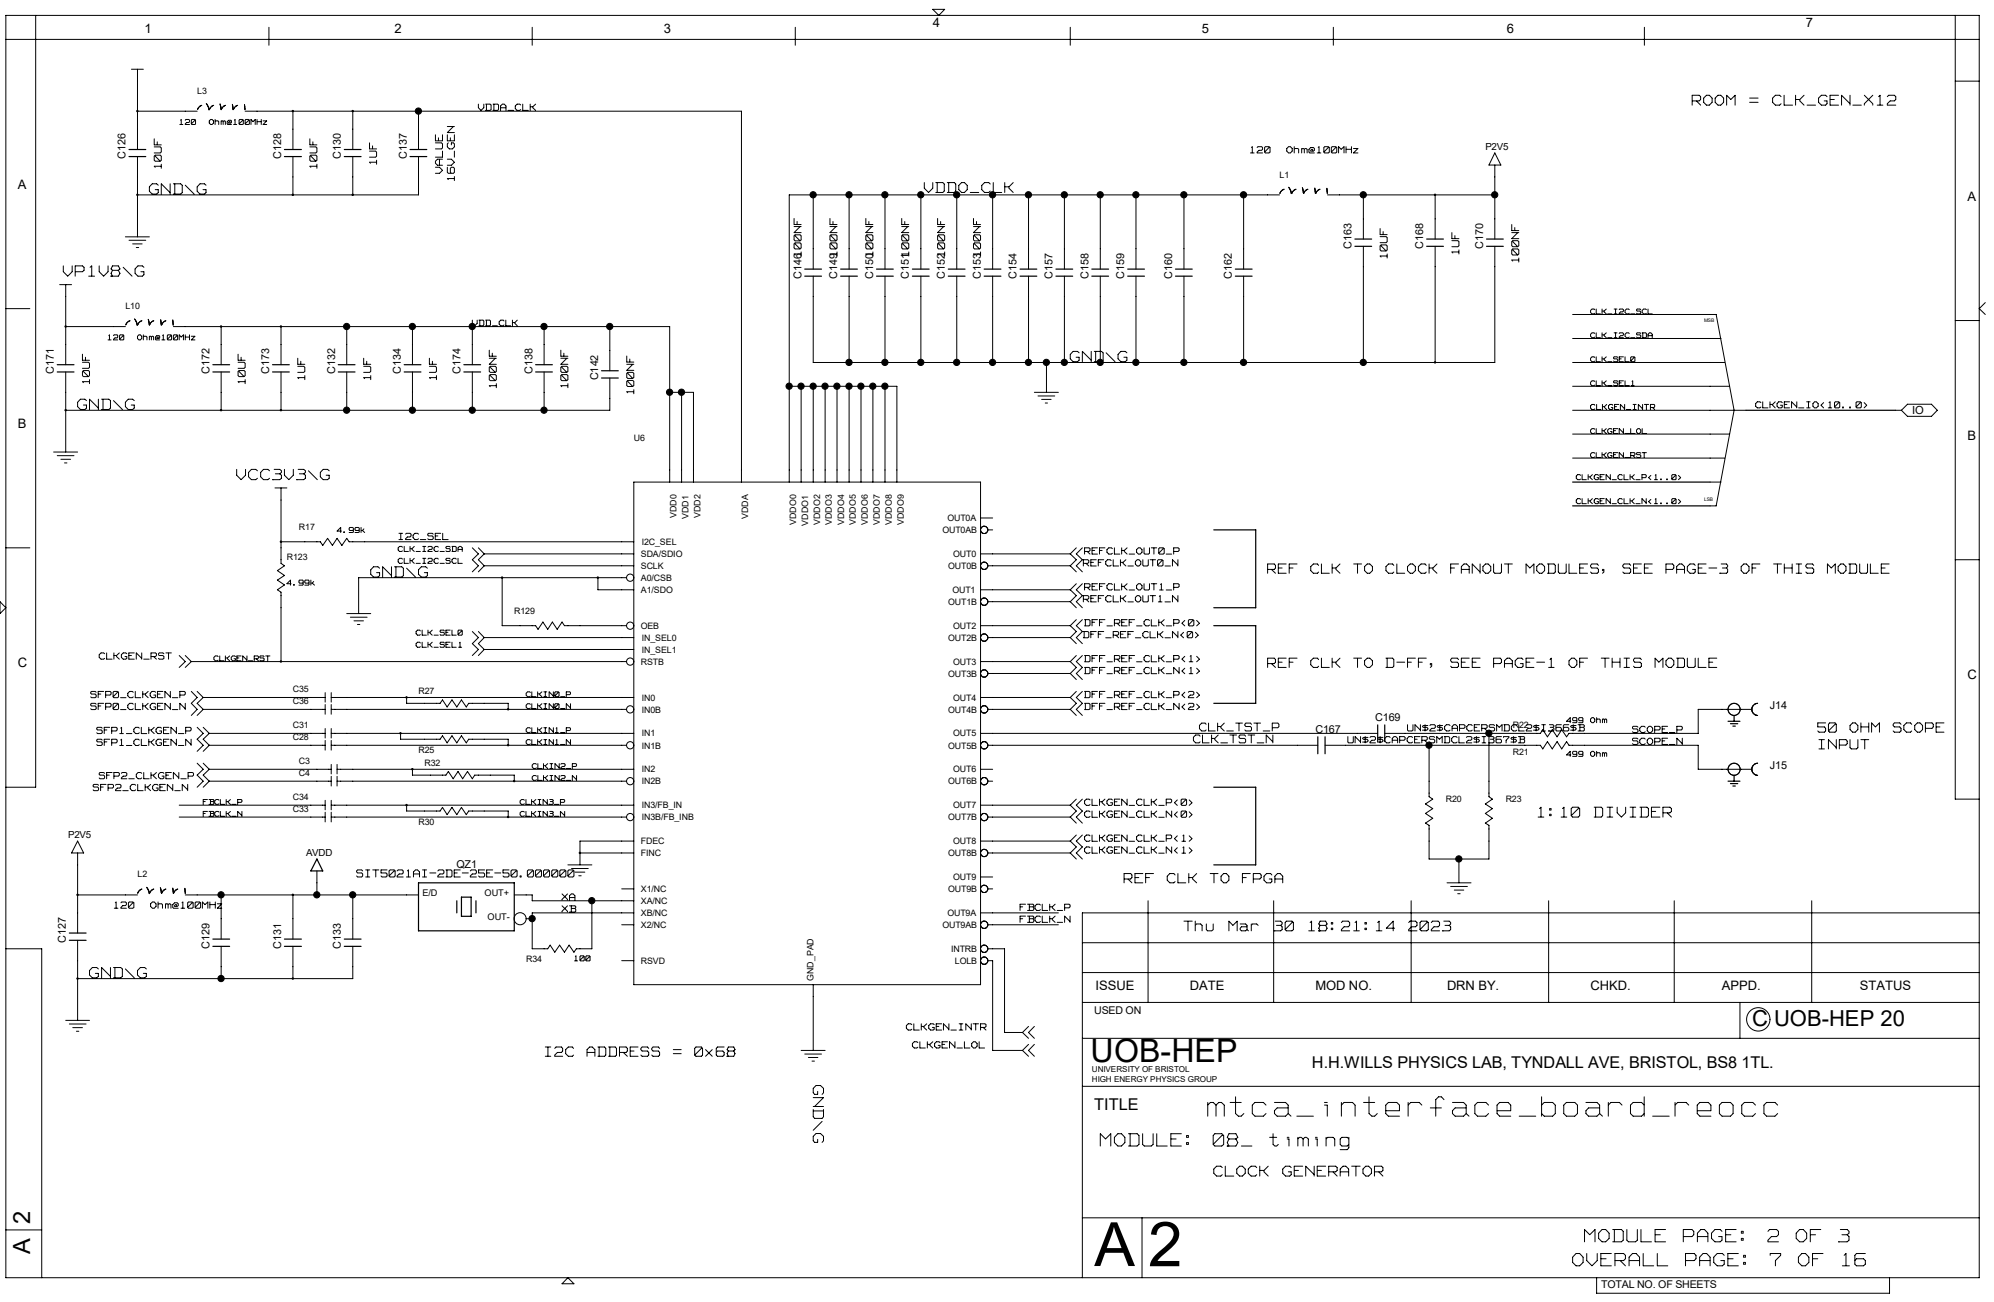
[picture p101: page 7]

REF CLK TO CLOCK FANOUT MODULES, SEE PAGE-3 OF THIS MODULE

REF CLK TO D-FF, SEE PAGE-1 OF THIS MODULE

UNIVERSITY OF BRISTOL
HIGH ENERGY PHYSICS GROUP
TITLE
MODULE: 08_ timing

H.H.WILLS PHYSICS LAB, TYNDALL AVE, BRISTOL, BS8 1TL.

# ROOM = CLK_FO_0_5

100NF


USE 8 WAY LVPECL FANOUT
NOT AVAILABLE DUE TO
SUPPLY CHAIN ISSUES

... BECAUSE 6 WAY LVDS BUFFER

UNIVERSITY OF BRISTOL
HIGH ENERGY PHYSICS GROUP
TITLE
MODULE: 08_ timing

H.H.WILLS PHYSICS LAB, TYNDALL AVE, BRISTOL, BS8 1TL.

## SFP.RATE_SELECT<0>

A

Mon Mar 6 16:31:19 2023; mtca_interface_board_reocc; ROOM=SFP1 04. SFP_MODULE; ROOM=SFP3 04. SFP_MODULE; SFP.RATE_SELECT<2> SFP.TX_DISABLE<2> SFP.TX_FAULT<2> SFP.LOS<2>; SFP<29..0>; SFP.TD_P<2>; SFP.RD_N<2>; SFP.RD_P<2>; SFP.TD_N<0>; SFP.TD_P<0>; SFP.RD_P<0> SFP.RD_N<0>; SFP.SCL<0>; SFP.SDA<0>; SFP.TX_DISABLE<0>; SFP.LOS<0>; SFP.TX_FAULT<0>; SFP.SCL<2>; SFP.SDA<2>; SFP.TD_N<2>; SFP.SCL<1>; SFP.SDA<1>; SFP.TD_N<1>; SFP.TD_P<1>; SFP.RD_N<1>; SFP.RD_P<1>; SFP.LOS<1>; SFP.TX_FAULT<1>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

312.5 Mb/S Timing Signals
on 1000Base BX Link

ROOM=SFP2
04. SFP_MODULE

UNIVERSITY OF BRISTOL
HIGH ENERGY PHYSICS GROUP
TITLE
MODULE: 03_ sfp

H.H.WILLS PHYSICS LAB, TYNDALL AVE, BRISTOL, BS8 1TL.

MODULE PAGE: 1 OF 1
OVERALL PAGE: 9 OF 16

22UF
6.3V


UNIVERSITY OF BRISTOL
HIGH ENERGY PHYSICS GROUP
TITLE
MODULE: 04_ sfp_module

H.H.WILLS PHYSICS LAB, TYNDALL AVE, BRISTOL, BS8 1TL.

# AUX IO INTERFACE

JTAG CONNECTOR | EEPROM

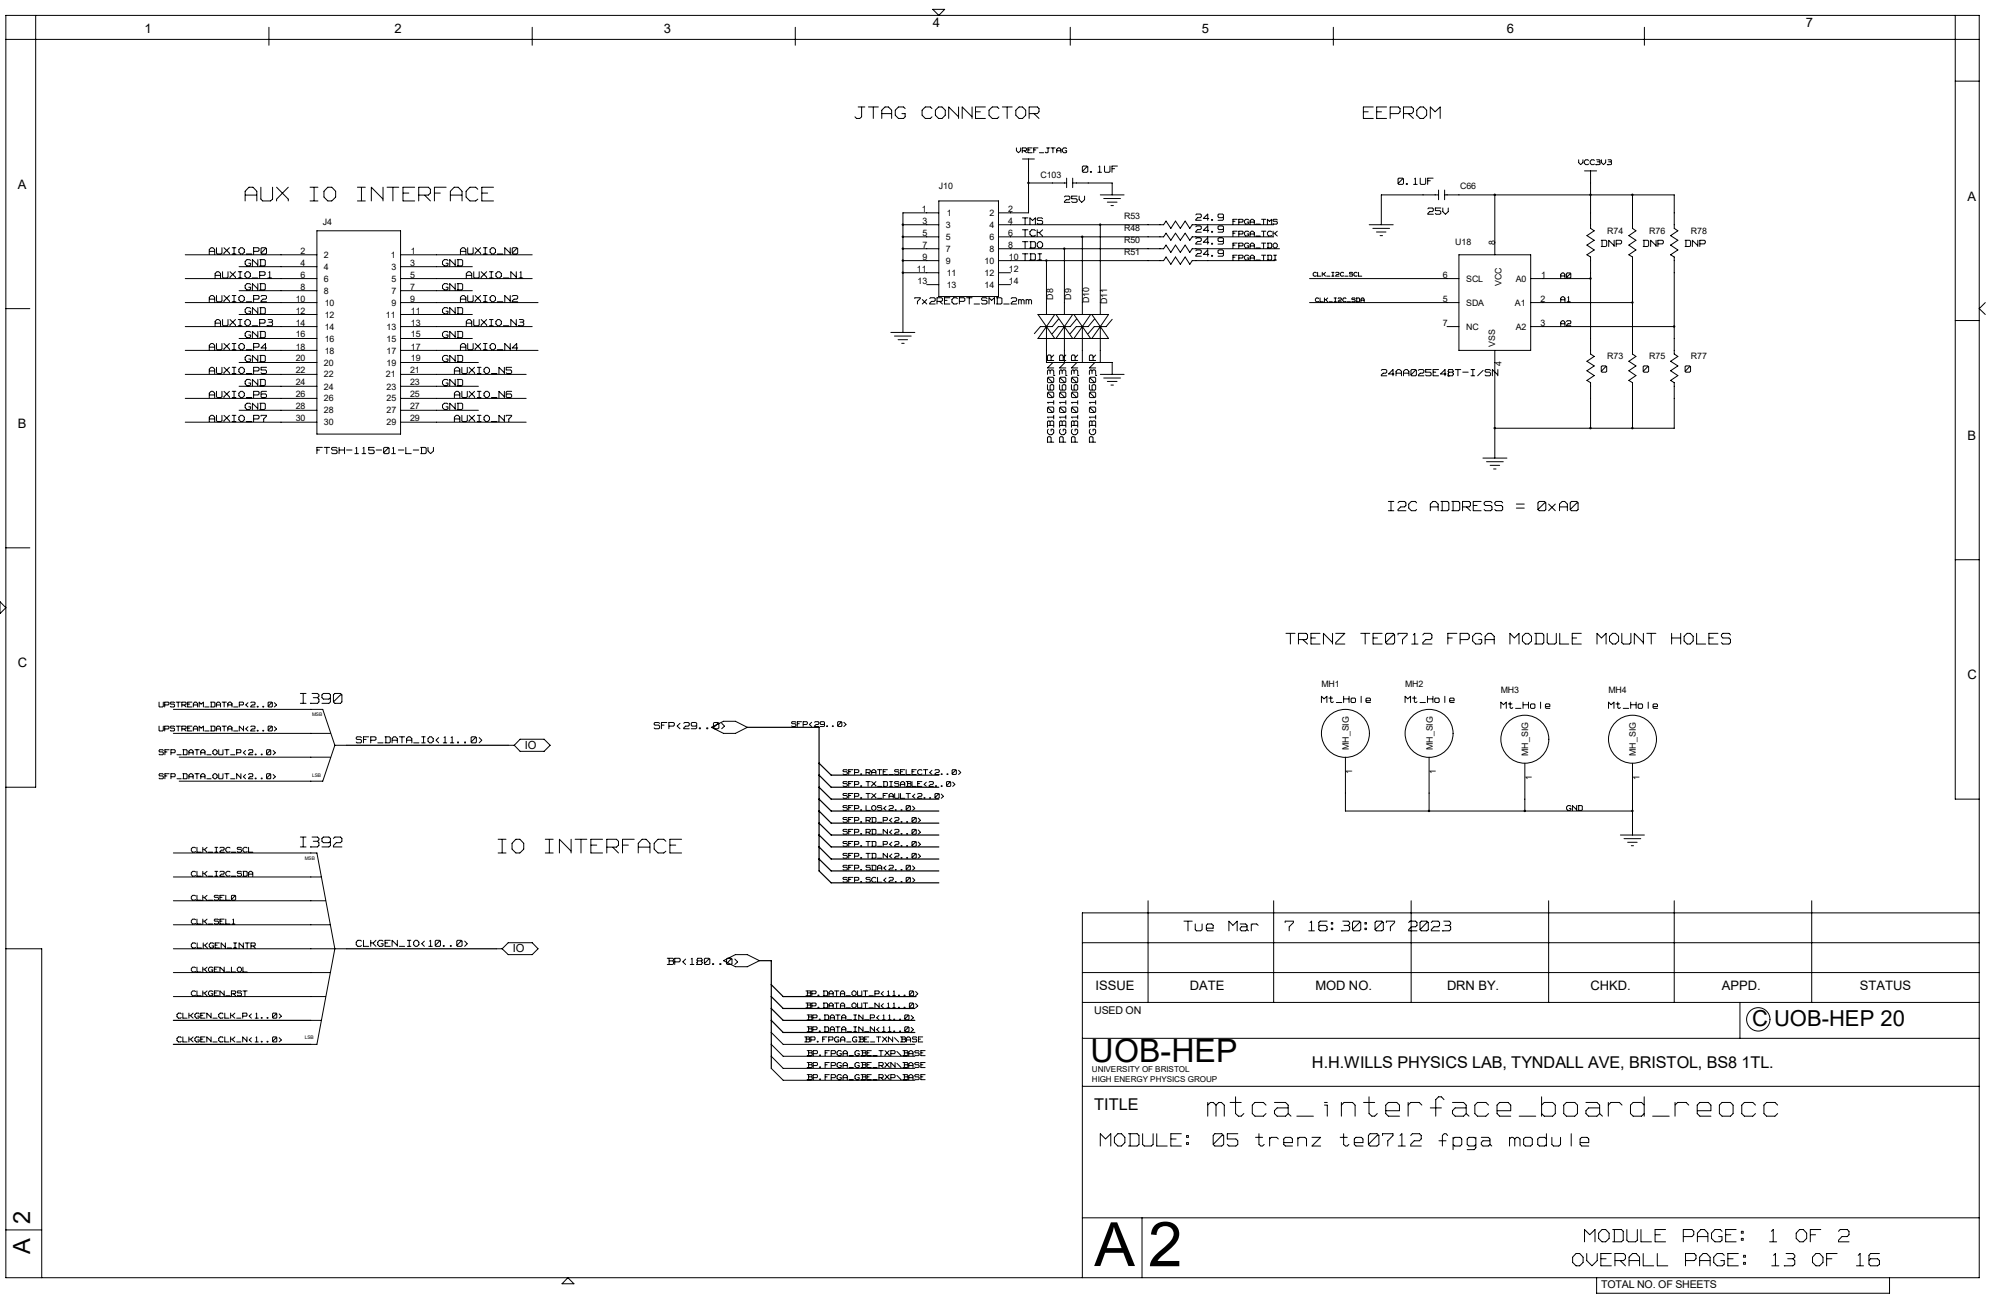
[picture p102: page 11]

TRENZ TE0712 FPGA MODULE MOUNT HOLES

UNIVERSITY OF BRISTOL
HIGH ENERGY PHYSICS GROUP
TITLE
MODULE: 05 trenz te0712 fpga module

H.H.WILLS PHYSICS LAB, TYNDALL AVE, BRISTOL, BS8 1TL.

## P3V3_OUT0

I405

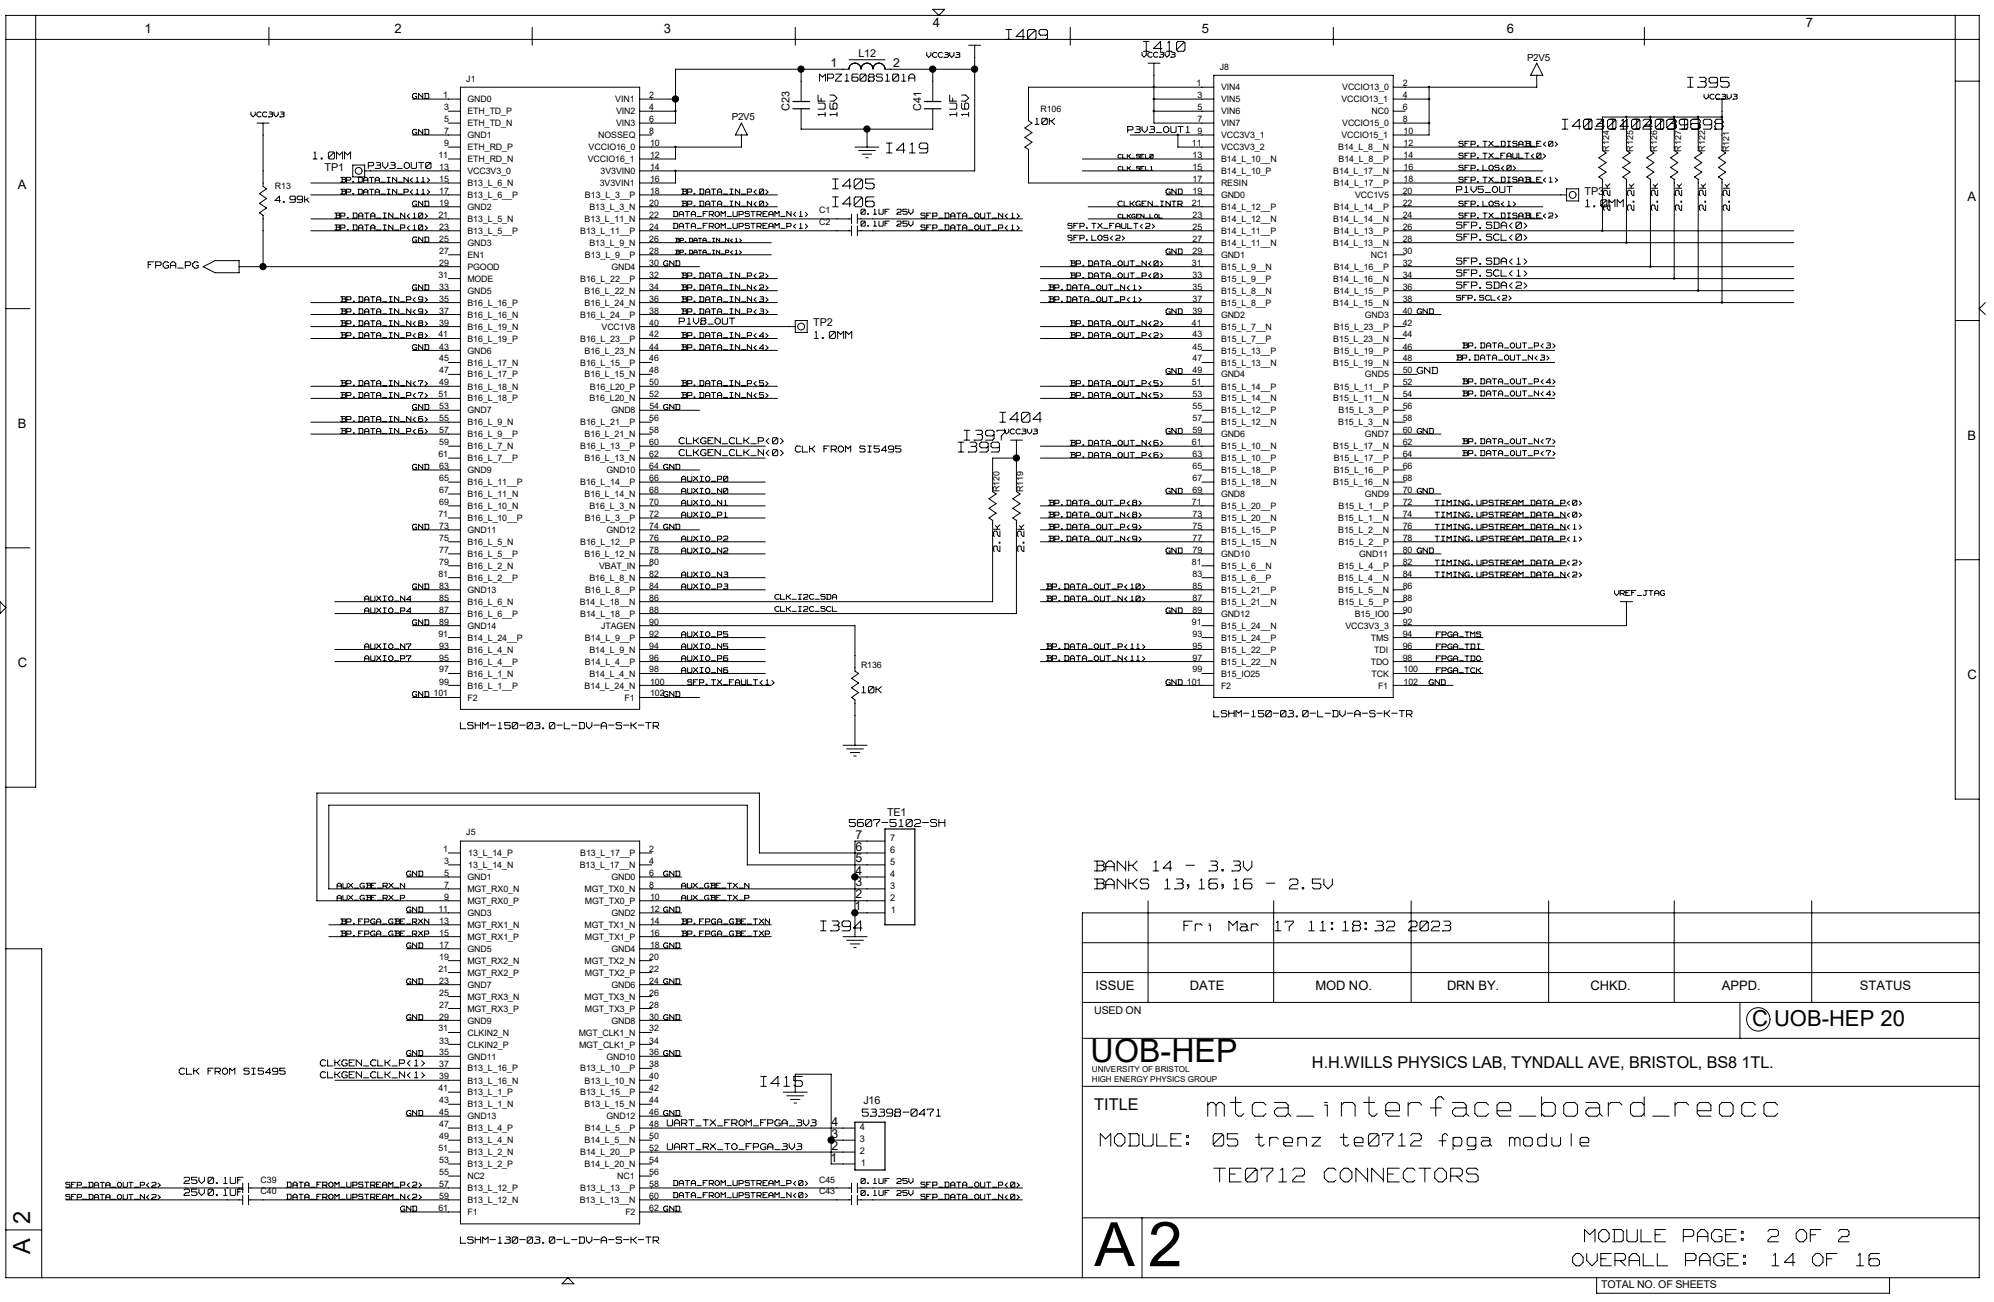
[picture p103: page 12]

UNIVERSITY OF BRISTOL
HIGH ENERGY PHYSICS GROUP
TITLE
MODULE: 05 trenz te0712 fpga module

H.H.WILLS PHYSICS LAB, TYNDALL AVE, BRISTOL, BS8 1TL.

# TONGUE 2 MEZZENINE CONNECTOR

## BP.REF_CLK_P<2>

2-16) of PICMG_ATCA; ESD PROTECTION; FRONT PANEL MOUNT HOLES; IO INTERFACE; Thu Mar 30 14:47:50 2023; mtca_interface_board_reocc; BP.AMC_N-ENABLE VP12 GND; BP.AMC_N-ENABLE; BP.TMS; BP.TCK; BP.TDO BP.TDI BP.FPGA_GBE_TXN; SEGMENT1; BP.REF_CLK_N<4>; BP.REF_CLK_P<6>; BP.REF_CLK_N<10>; BP.FPGA_GBE_TXP BP.FPGA_GBE_RXN; BP.DATA_OUT_P<11..0>; BP.DATA_IN_N<11..0>; BP.REF_CLK_N<11..0>; GND; BP.REF_CLK_N<0>; SEGMENT3; SEGMENT2; Mt_Hole; Mt_Hole Mt_Hole Mt_Hole Mt_Hole; BP.AMC_GA<2..0> BP.AMC_N-PS<1..0>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

LSHM-130-03.0-L-DV-A-S-K-TR

LSHM-150-03.0-L-DV-A-S-K-TR

TONGUE 2 MEZZENINE MOUNT HOLES

Promotes save ESD discharge
during board insertion (see pg

UNIVERSITY OF BRISTOL
HIGH ENERGY PHYSICS GROUP
TITLE
MODULE: 07_ backplane interface

H.H.WILLS PHYSICS LAB, TYNDALL AVE, BRISTOL, BS8 1TL.

BP PLANE CONNECTOR TONGUE 1

MODULE PAGE: 1 OF 1
OVERALL PAGE: 15 OF 16

# IO INTERFACE

# MODULE MANAGEMENT CONTROL

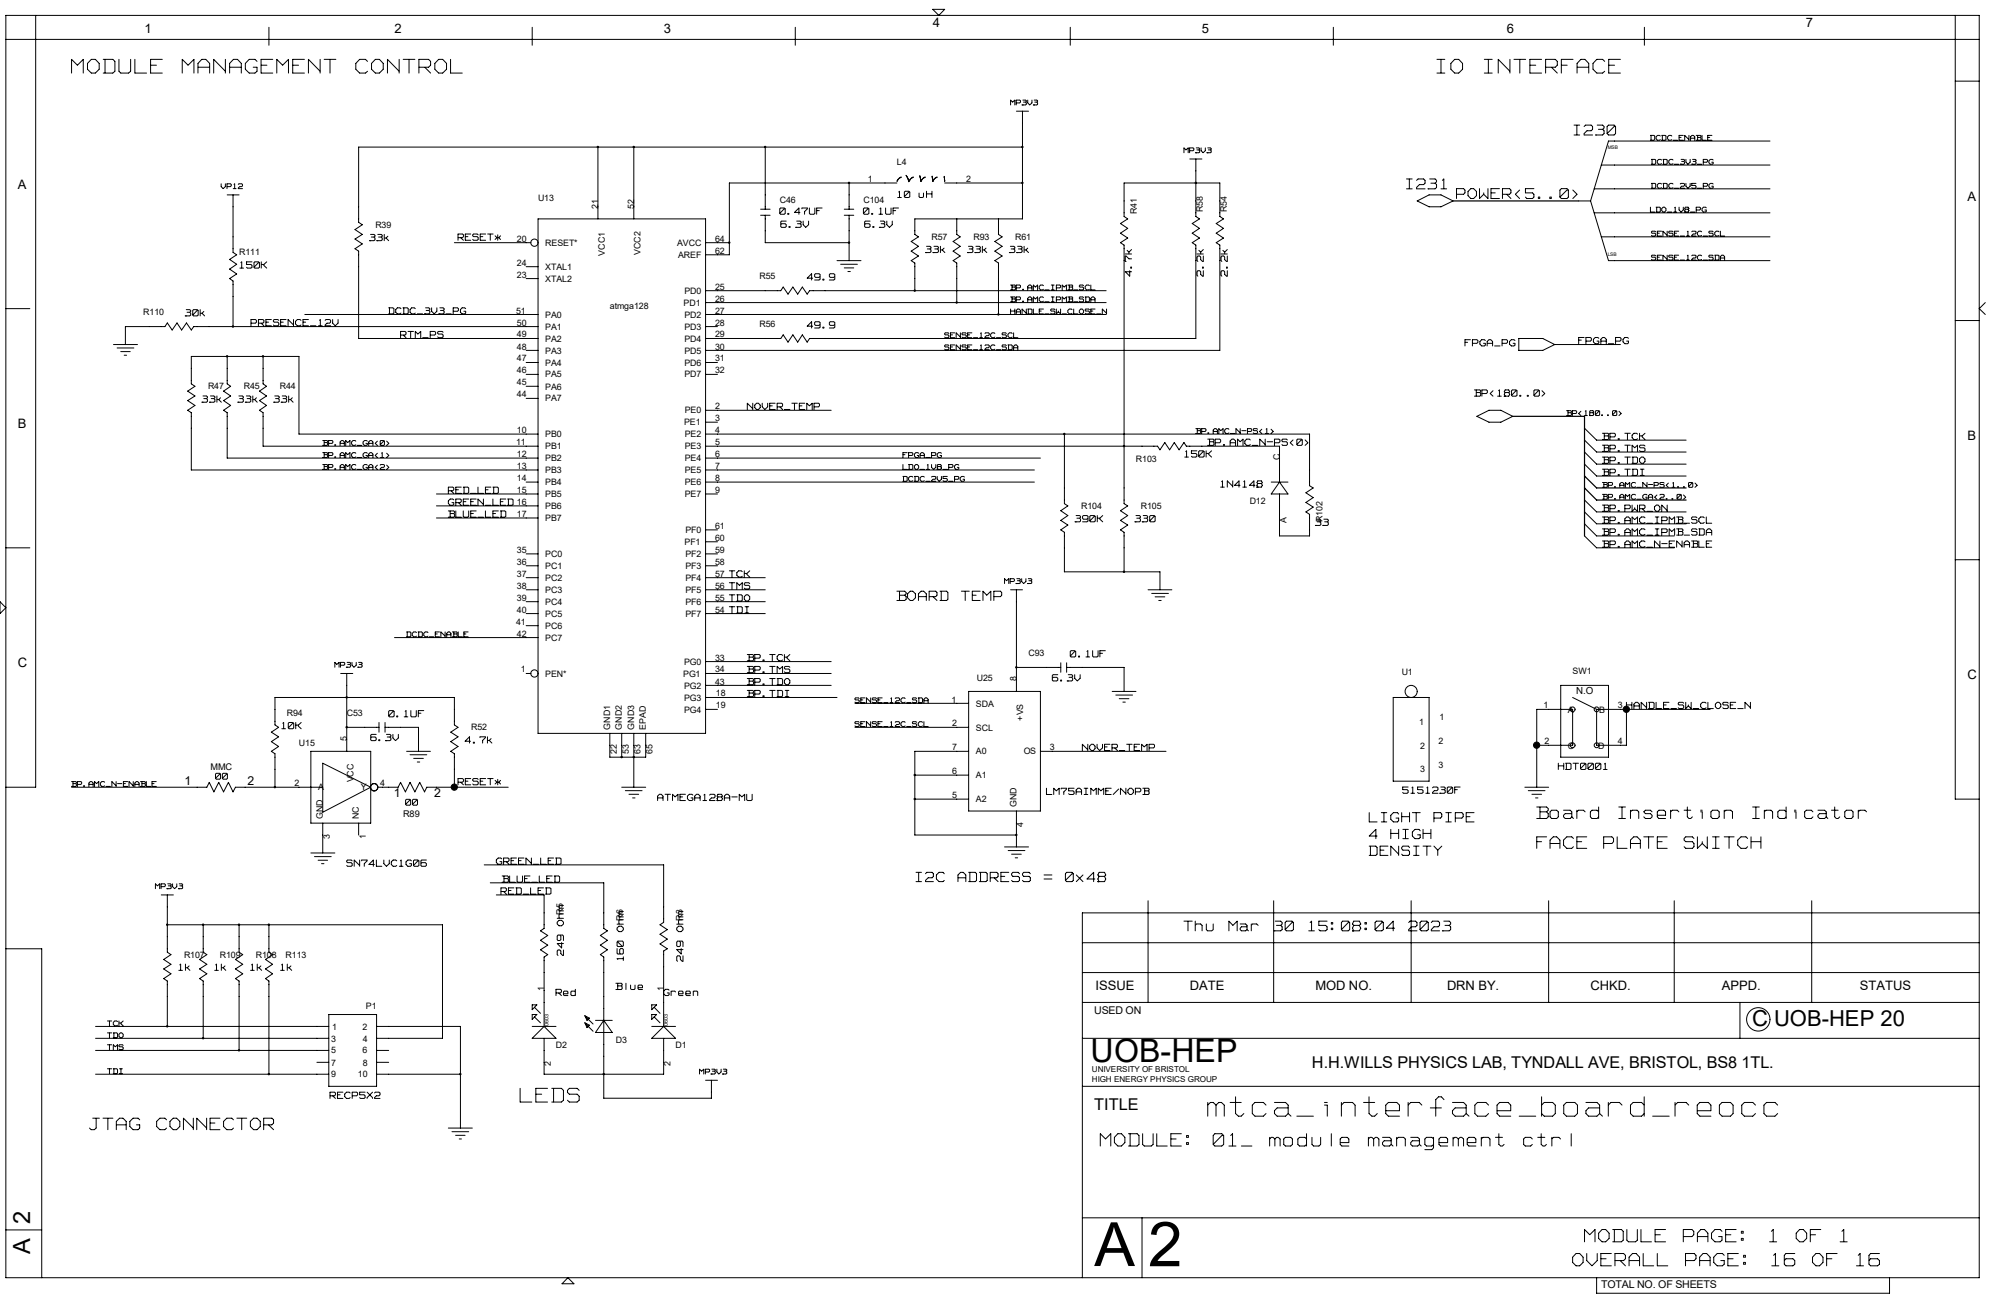
[picture p104: page 14]

8 R58 GND1 GND2 GND3 EPAD VCC1 VCC2 GND NC VCC GND +VS

UNIVERSITY OF BRISTOL
HIGH ENERGY PHYSICS GROUP
TITLE
MODULE: 01_ module management ctrl

H.H.WILLS PHYSICS LAB, TYNDALL AVE, BRISTOL, BS8 1TL.
