uob-hep-cad/uob-hep-pc072/hardware/Schematics/dune_mib_v2_6mar23.pdf

1 | 3 | 4
5 6

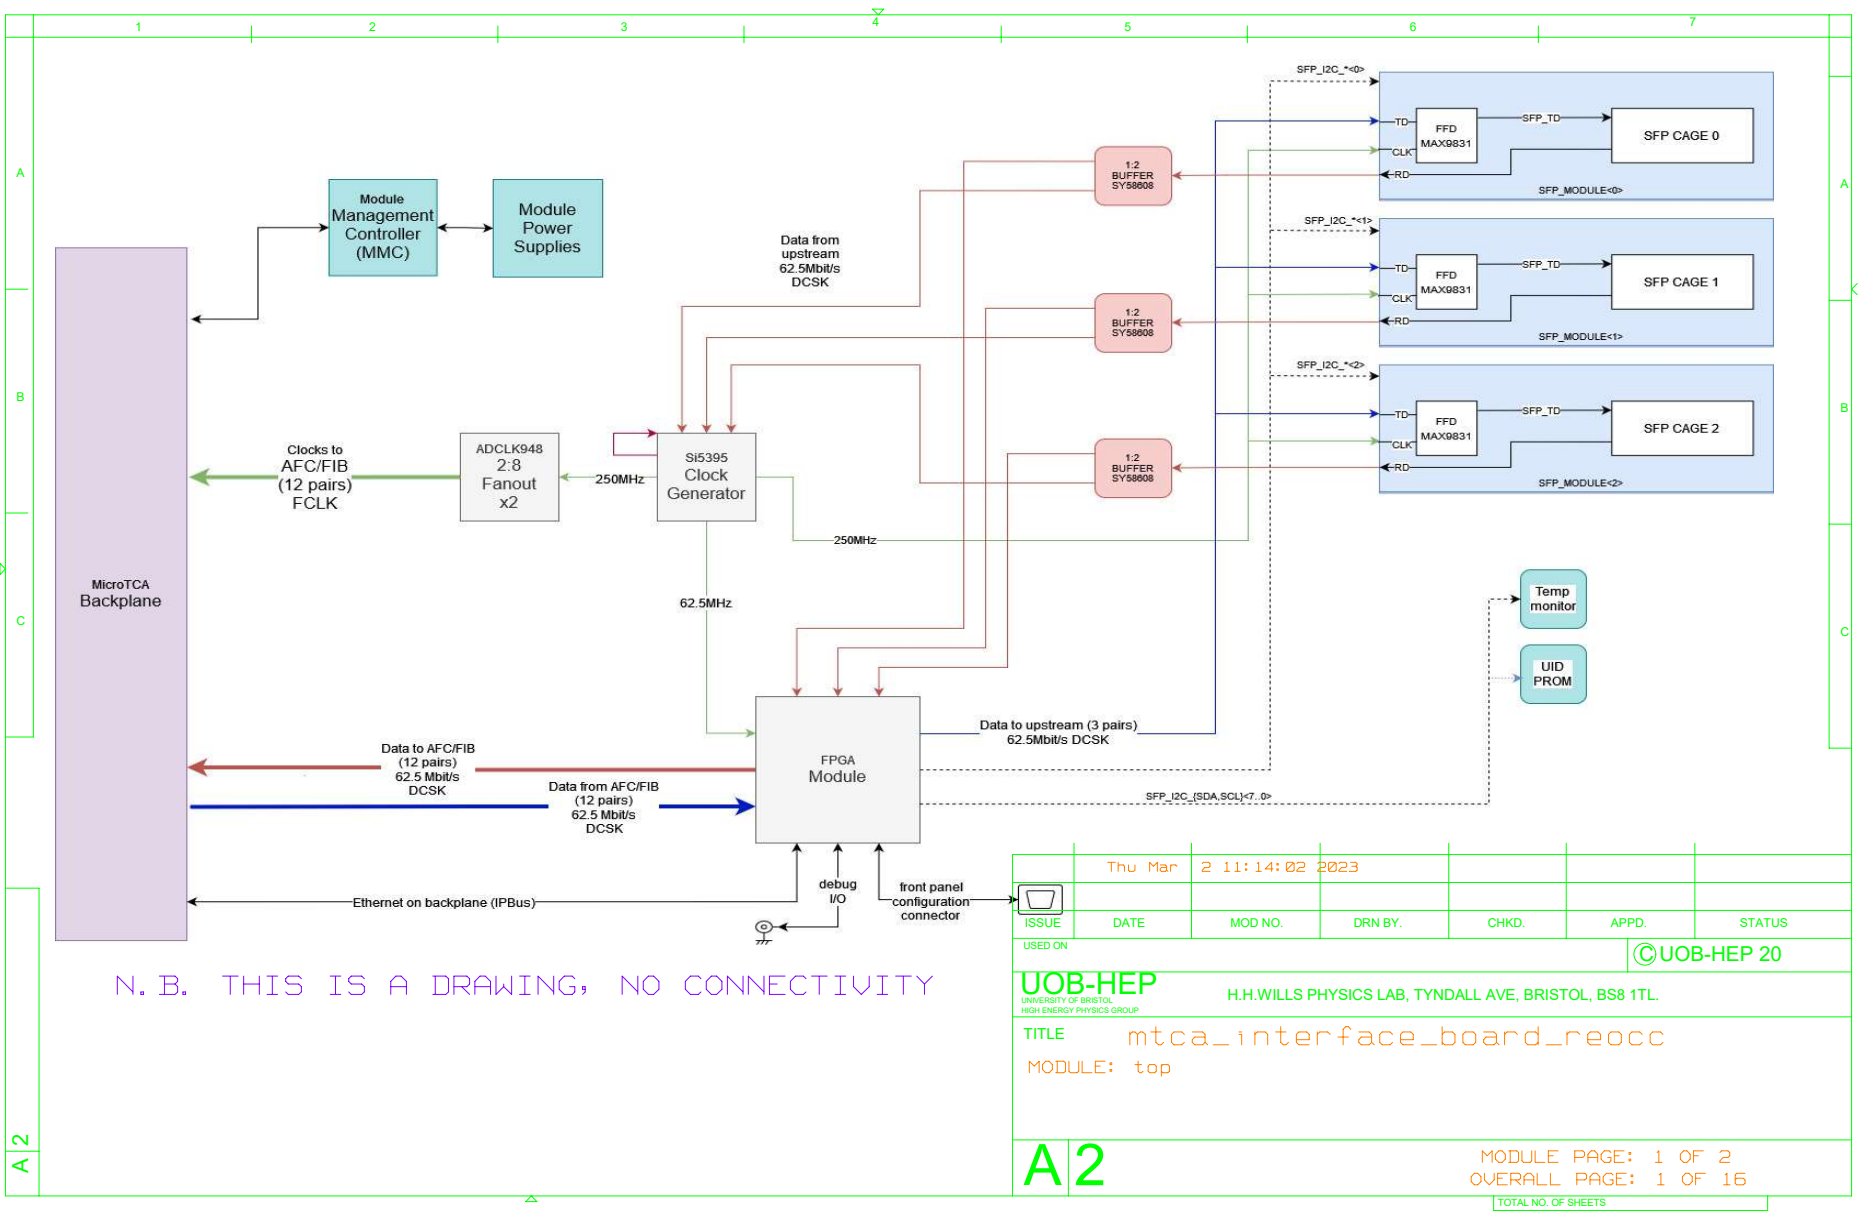
[picture p119: page 1]
Thu Mar 2 11:14:02 2023; mtca_interface_board_reocc; USED ON; ISSUE; APPD. DATE; MOD NO.; DRN BY.; CHKD.; STATUS; C UOB-HEP 20; UOB-HEP

N.B. THIS IS A DRAWING, NO CONNECTIVITY

UNIVERSITY OF BRISTOL
HIGH ENERGY PHYSICS GROUP
TITLE
MODULE: top

H.H.WILLS PHYSICS LAB, TYNDALL AVE, BRISTOL, BS8 1TL.

MODULE PAGE: 1 OF 2
OVERALL PAGE: 1 OF 16

TOTAL NO. OF SHEETS

## ROOM=POWER

BP<180..0>

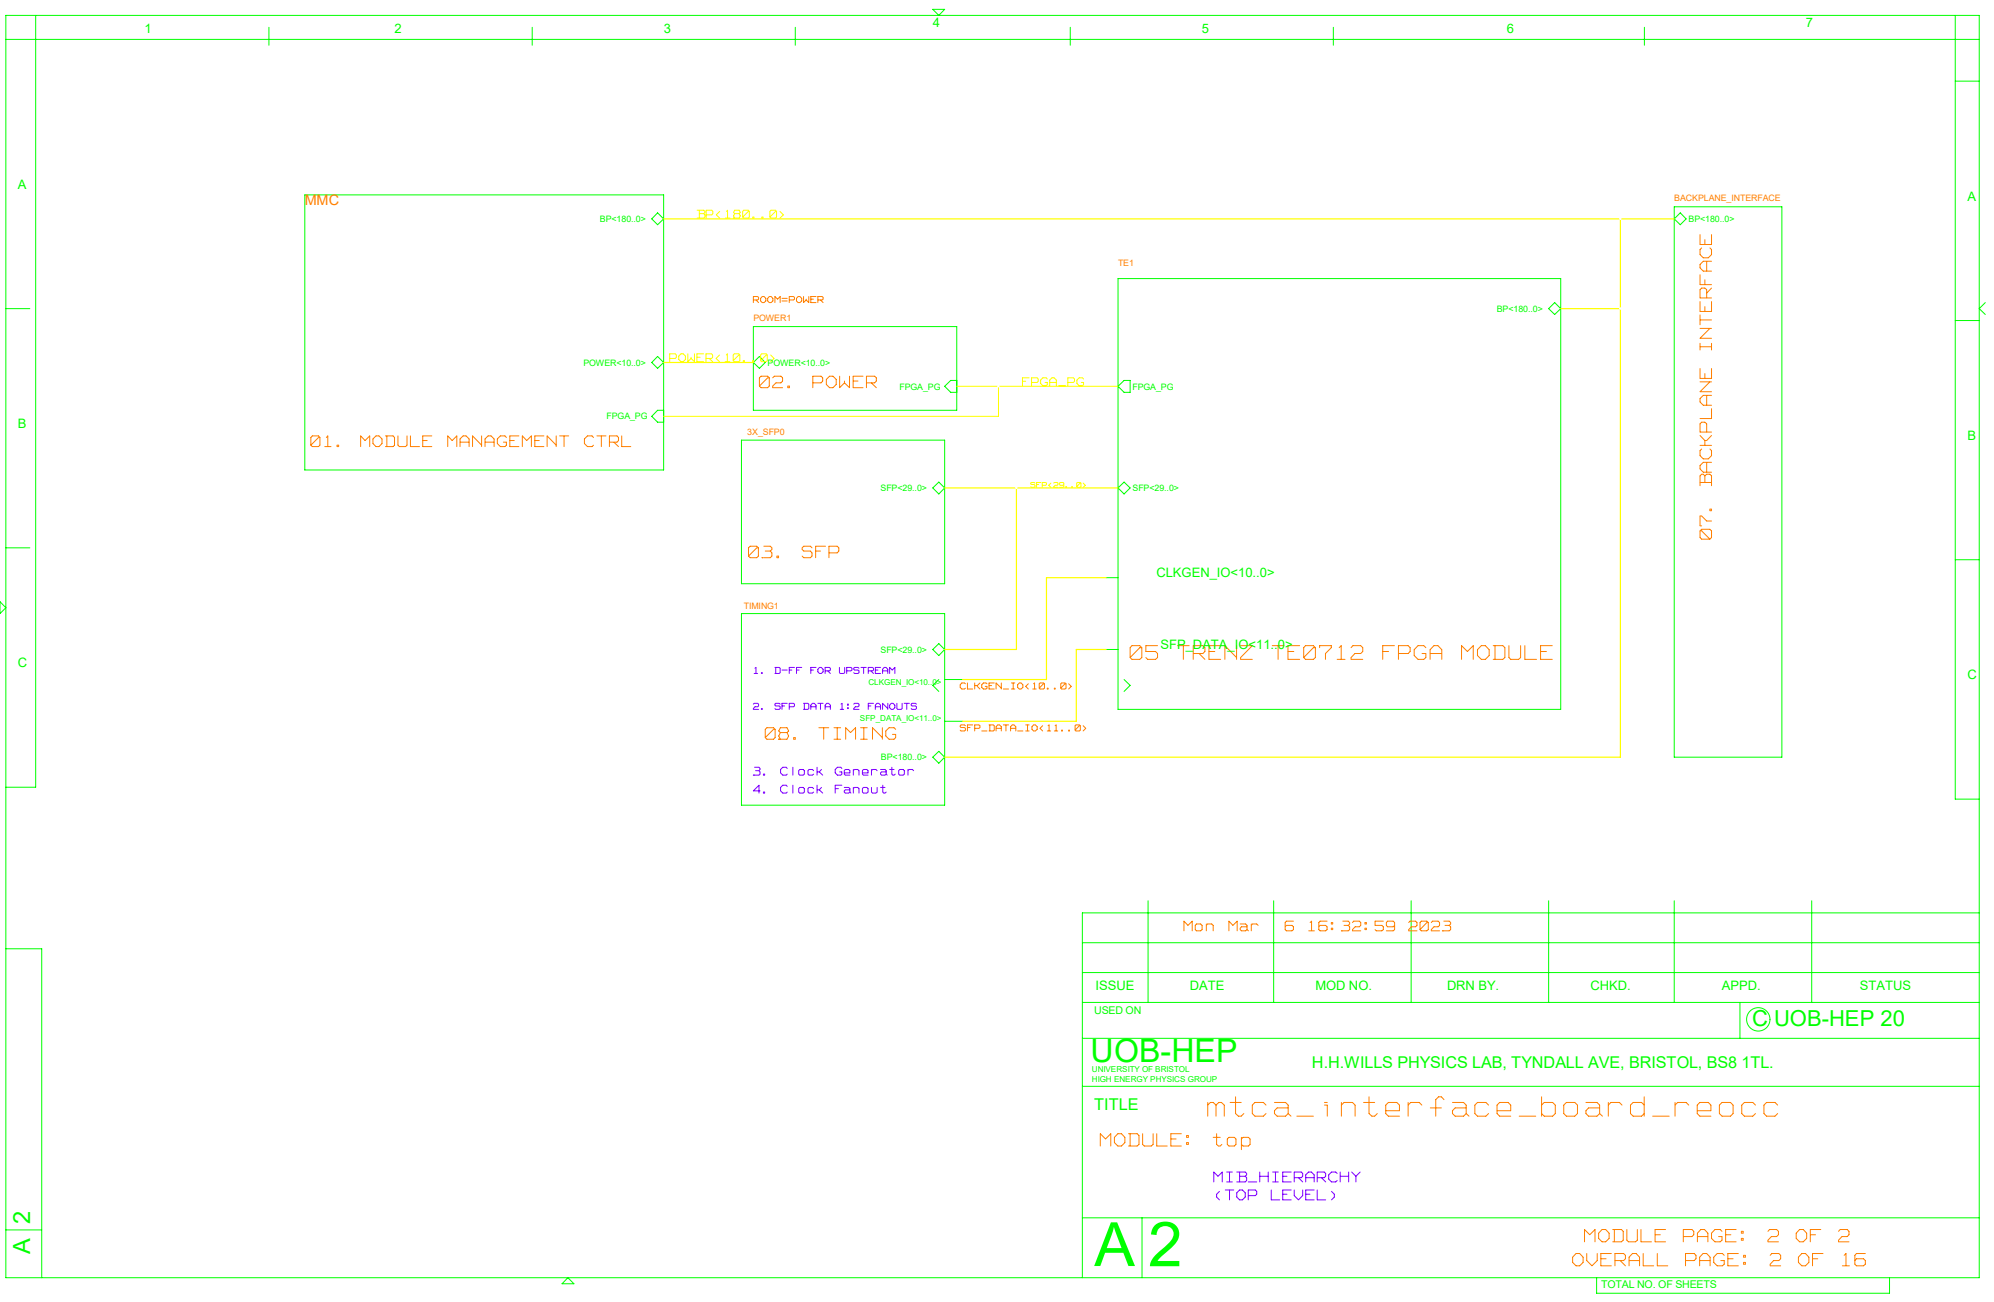
[picture p120: page 2]
MIB_HIERARCHY (TOP LEVEL); 3. Clock Generator 4. Clock Fanout; Mon Mar 6 16:32:59 2023; mtca_interface_board_reocc; FPGA_PG; POWER<10..0> 02. POWER; 03. SFP; CLKGEN_IO<10..0>; SFP_DATA_IO<11..0>; SFP<29..0>; 07. BACKPLANE INTERFACE; POWER1; 3X_SFP0; TIMING1; BACKPLANE_INTERFACE; POWER<10..0>; USED ON; ISSUE; APPD. DATE; MOD NO.; DRN BY.; CHKD.; STATUS; MMC; C UOB-HEP 20; UOB-HEP

01. MODULE MANAGEMENT CTRL

SFP_DATA_IO<11..0>
05 TRENZ TE0712 FPGA MODULE

1. D-FF FOR UPSTREAM

2. SFP DATA 1:2 FANOUTS
08. TIMING

UNIVERSITY OF BRISTOL
HIGH ENERGY PHYSICS GROUP
TITLE
MODULE: top

H.H.WILLS PHYSICS LAB, TYNDALL AVE, BRISTOL, BS8 1TL.

MODULE PAGE: 2 OF 2
OVERALL PAGE: 2 OF 16

# 12V @ 6.6A IN

# VP3V3 IV MONITOR

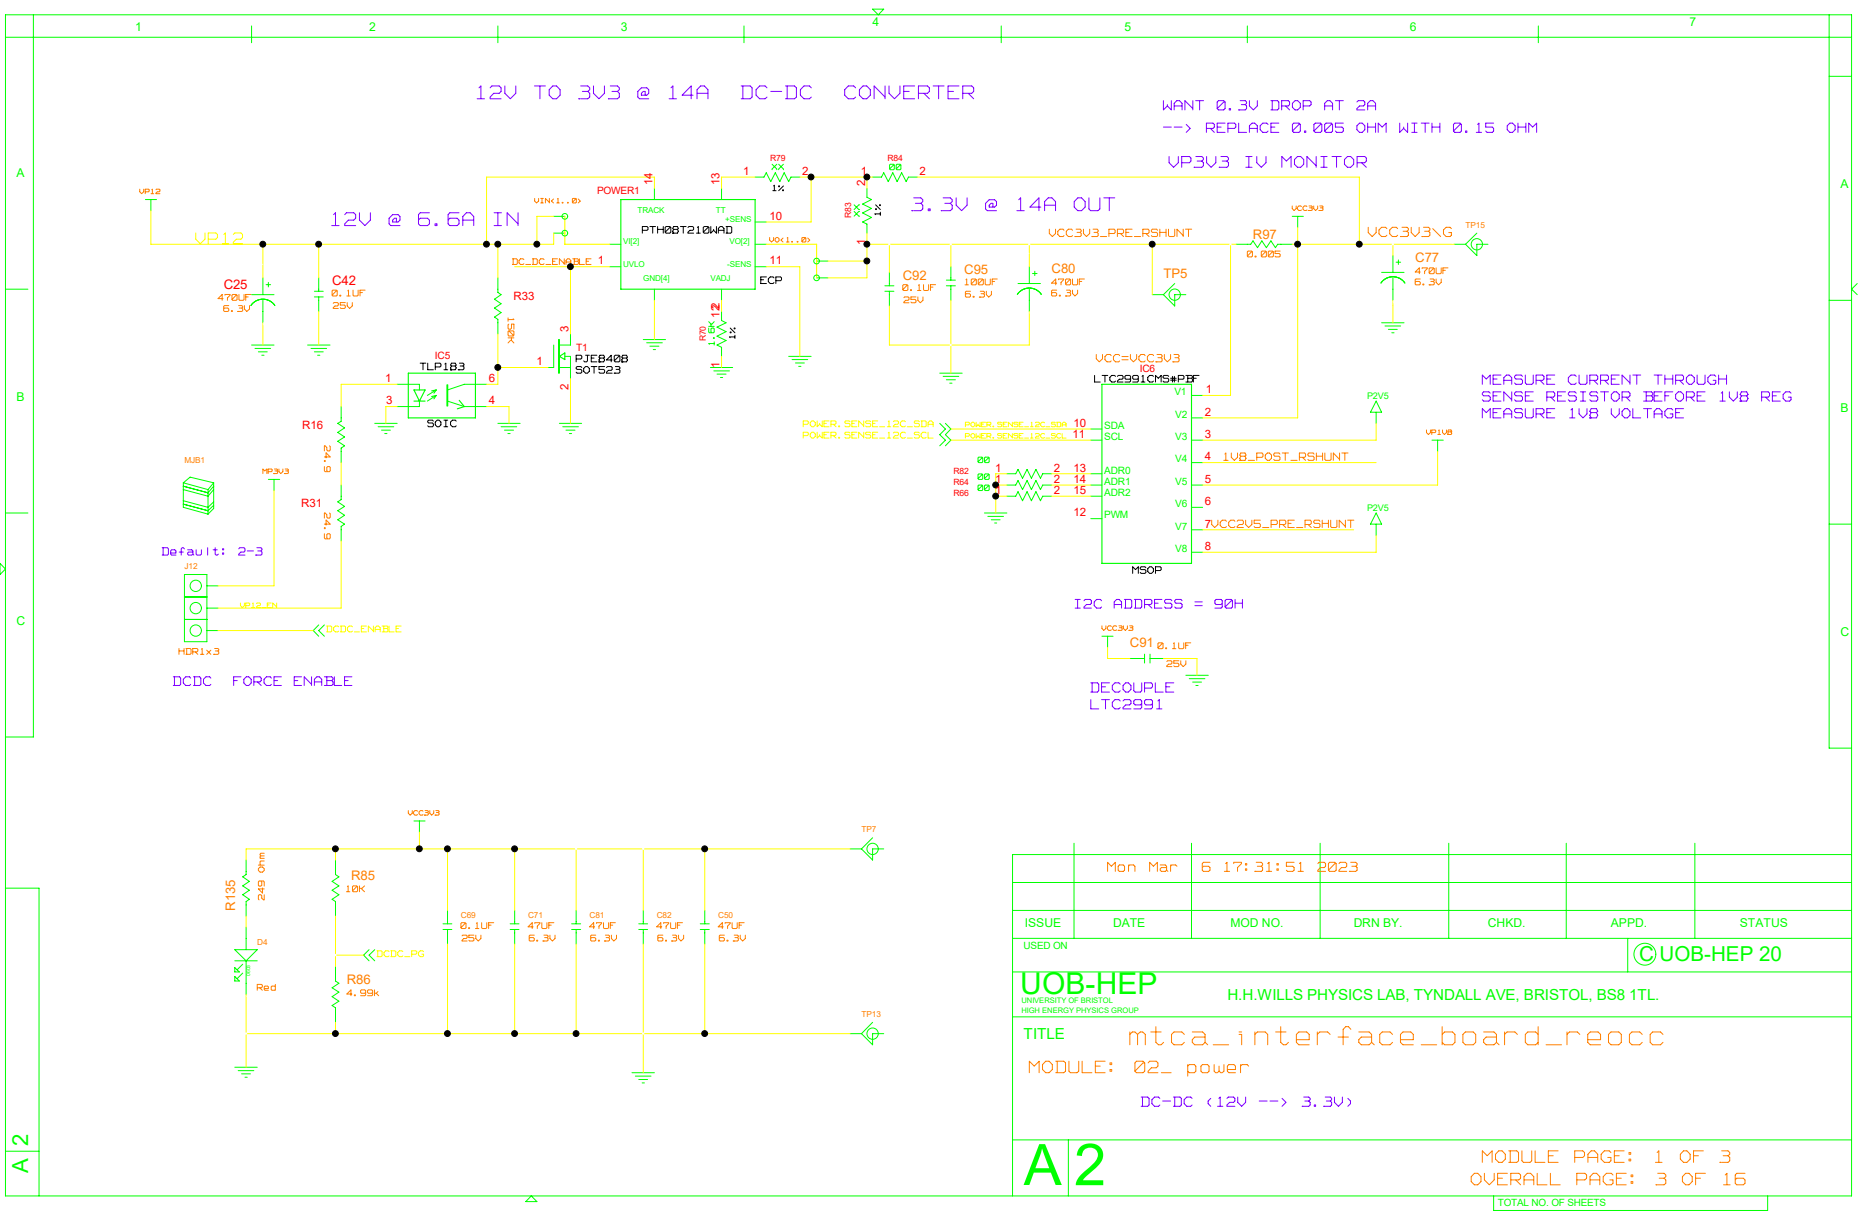
[picture p121: page 3]

12V TO 3V3 @ 14A DC-DC CONVERTER

WANT 0.3V DROP AT 2A
--> REPLACE 0.005 OHM WITH 0.15 OHM

MEASURE CURRENT THROUGH
SENSE RESISTOR BEFORE 1V8 REG
MEASURE 1V8 VOLTAGE

HDR1x3
DECOUPLE DCDC FORCE ENABLE

UNIVERSITY OF BRISTOL
HIGH ENERGY PHYSICS GROUP
TITLE
MODULE: 02_ power

H.H.WILLS PHYSICS LAB, TYNDALL AVE, BRISTOL, BS8 1TL.

# WANT 0.3V DROP AT 2A --> REPLACE 0.005 OHM WITH 0.15 OHM

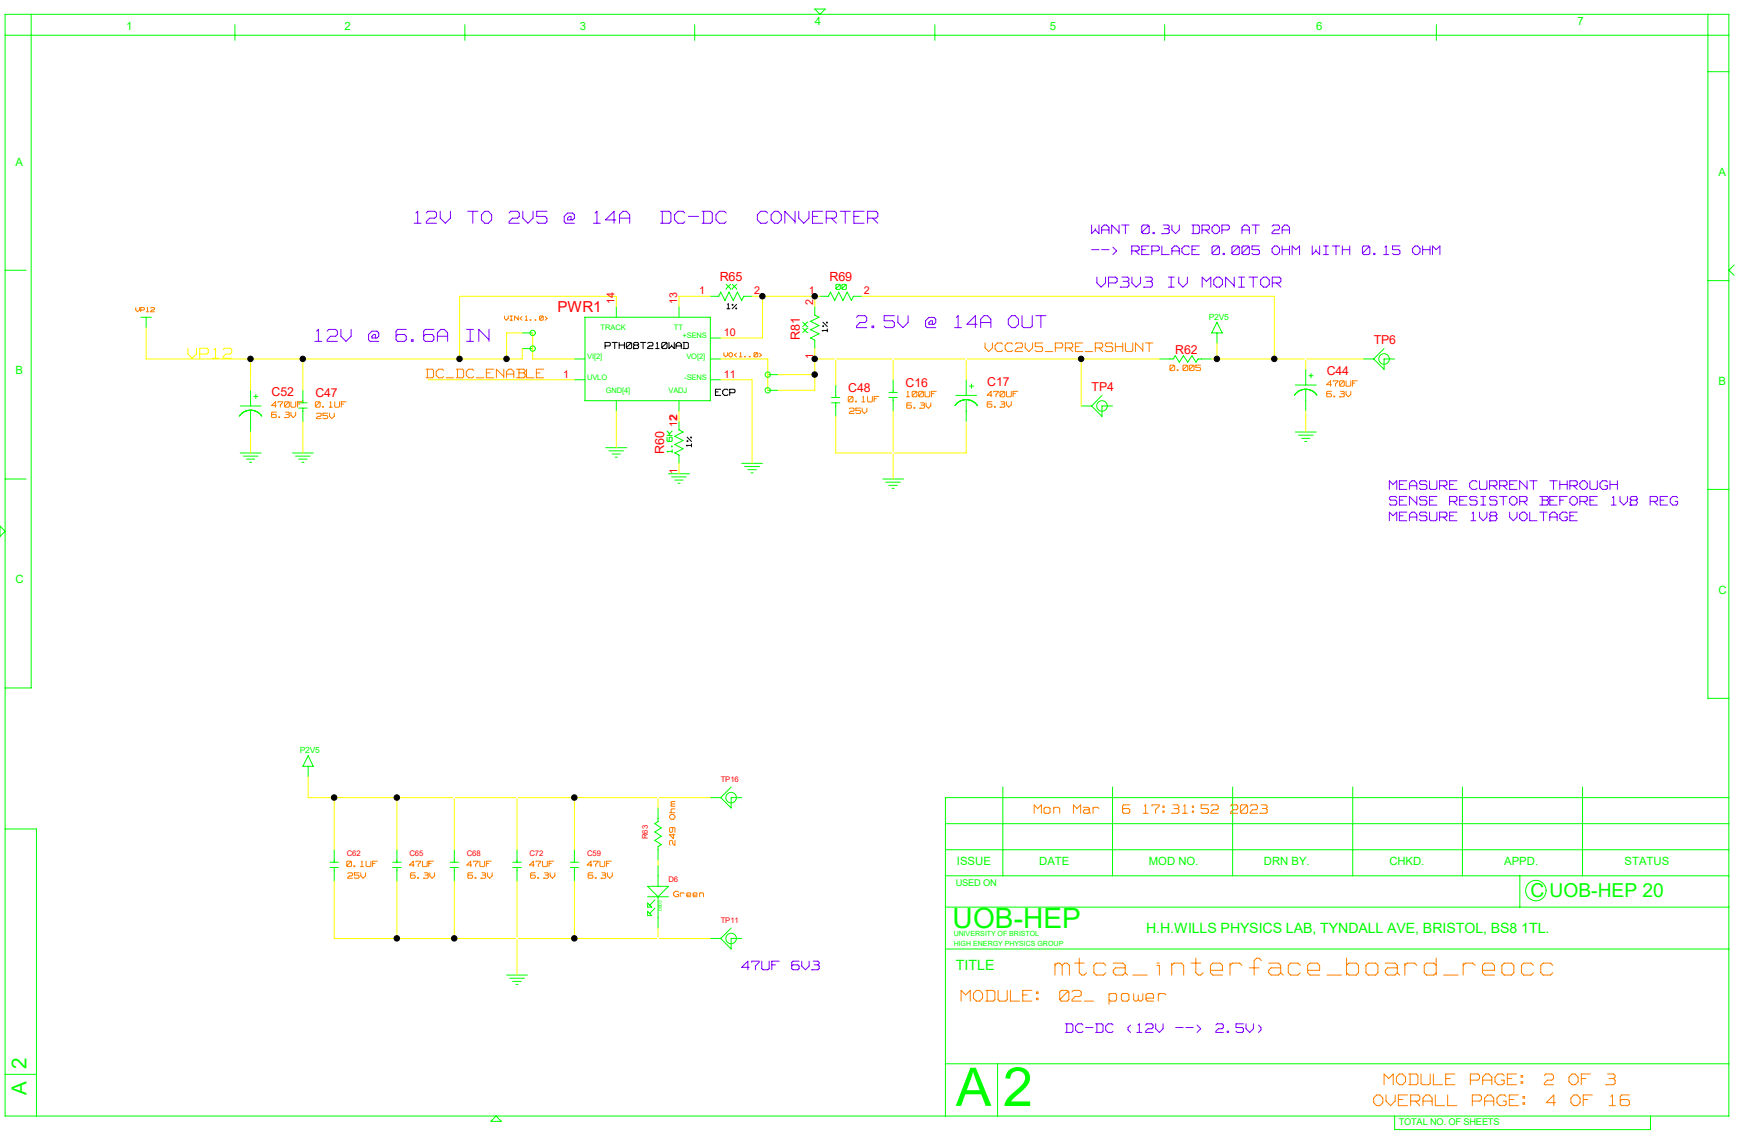
[picture p122: page 4]

12V TO 2V5 @ 14A DC-DC CONVERTER

MEASURE CURRENT THROUGH
SENSE RESISTOR BEFORE 1V8 REG
MEASURE 1V8 VOLTAGE

UNIVERSITY OF BRISTOL
HIGH ENERGY PHYSICS GROUP
TITLE
MODULE: 02_ power

H.H.WILLS PHYSICS LAB, TYNDALL AVE, BRISTOL, BS8 1TL.

4.99k

## PJE8408

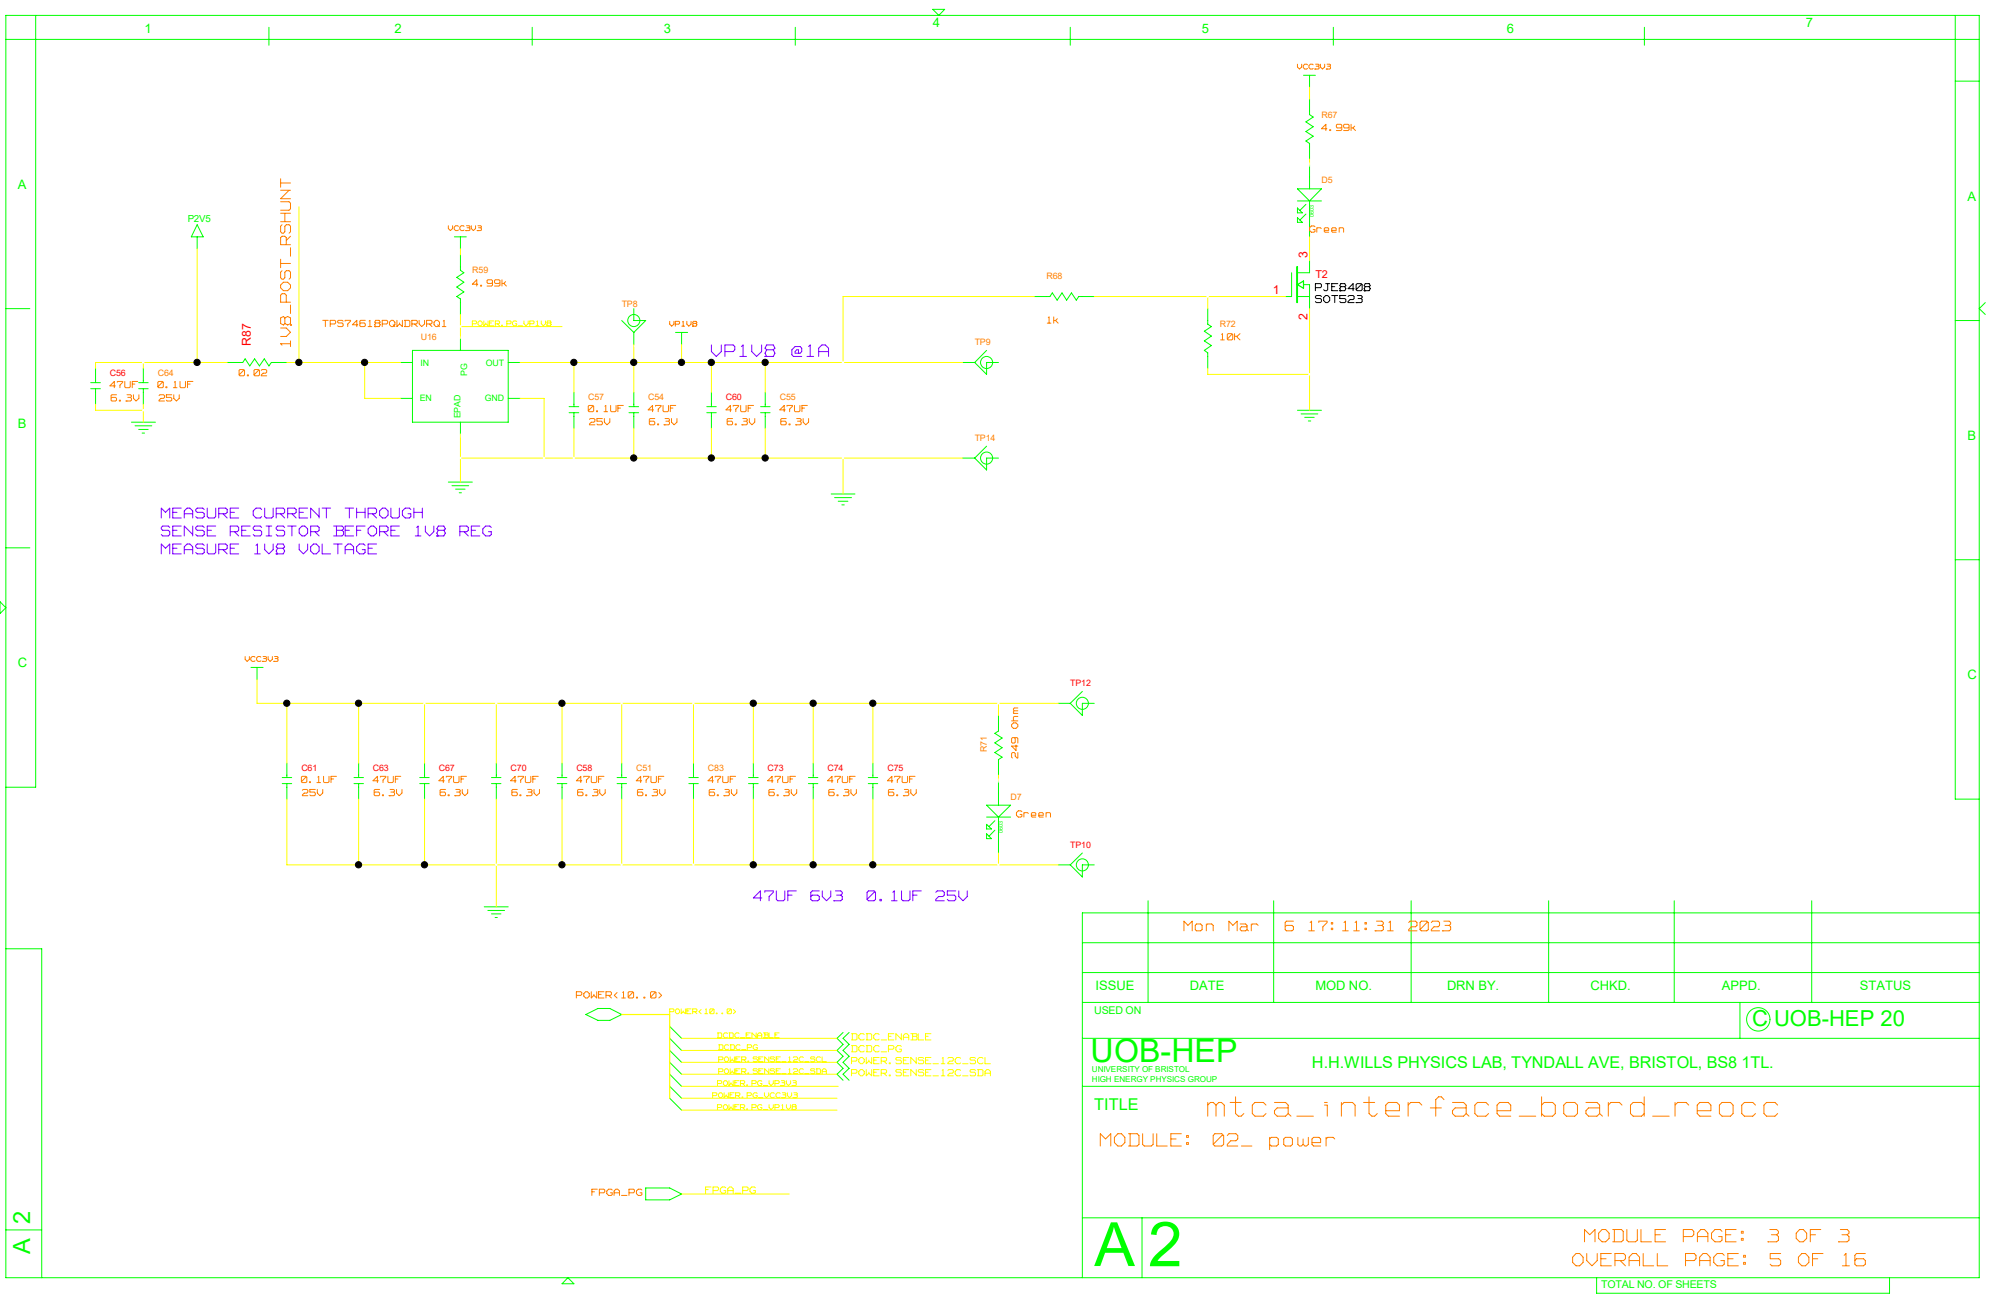
[picture p123: page 5]

MEASURE CURRENT THROUGH
SENSE RESISTOR BEFORE 1V8 REG
MEASURE 1V8 VOLTAGE

UNIVERSITY OF BRISTOL
HIGH ENERGY PHYSICS GROUP
TITLE
MODULE: 02_ power

H.H.WILLS PHYSICS LAB, TYNDALL AVE, BRISTOL, BS8 1TL.

# SFP DATA TO FPGA

# MAX9381ESA

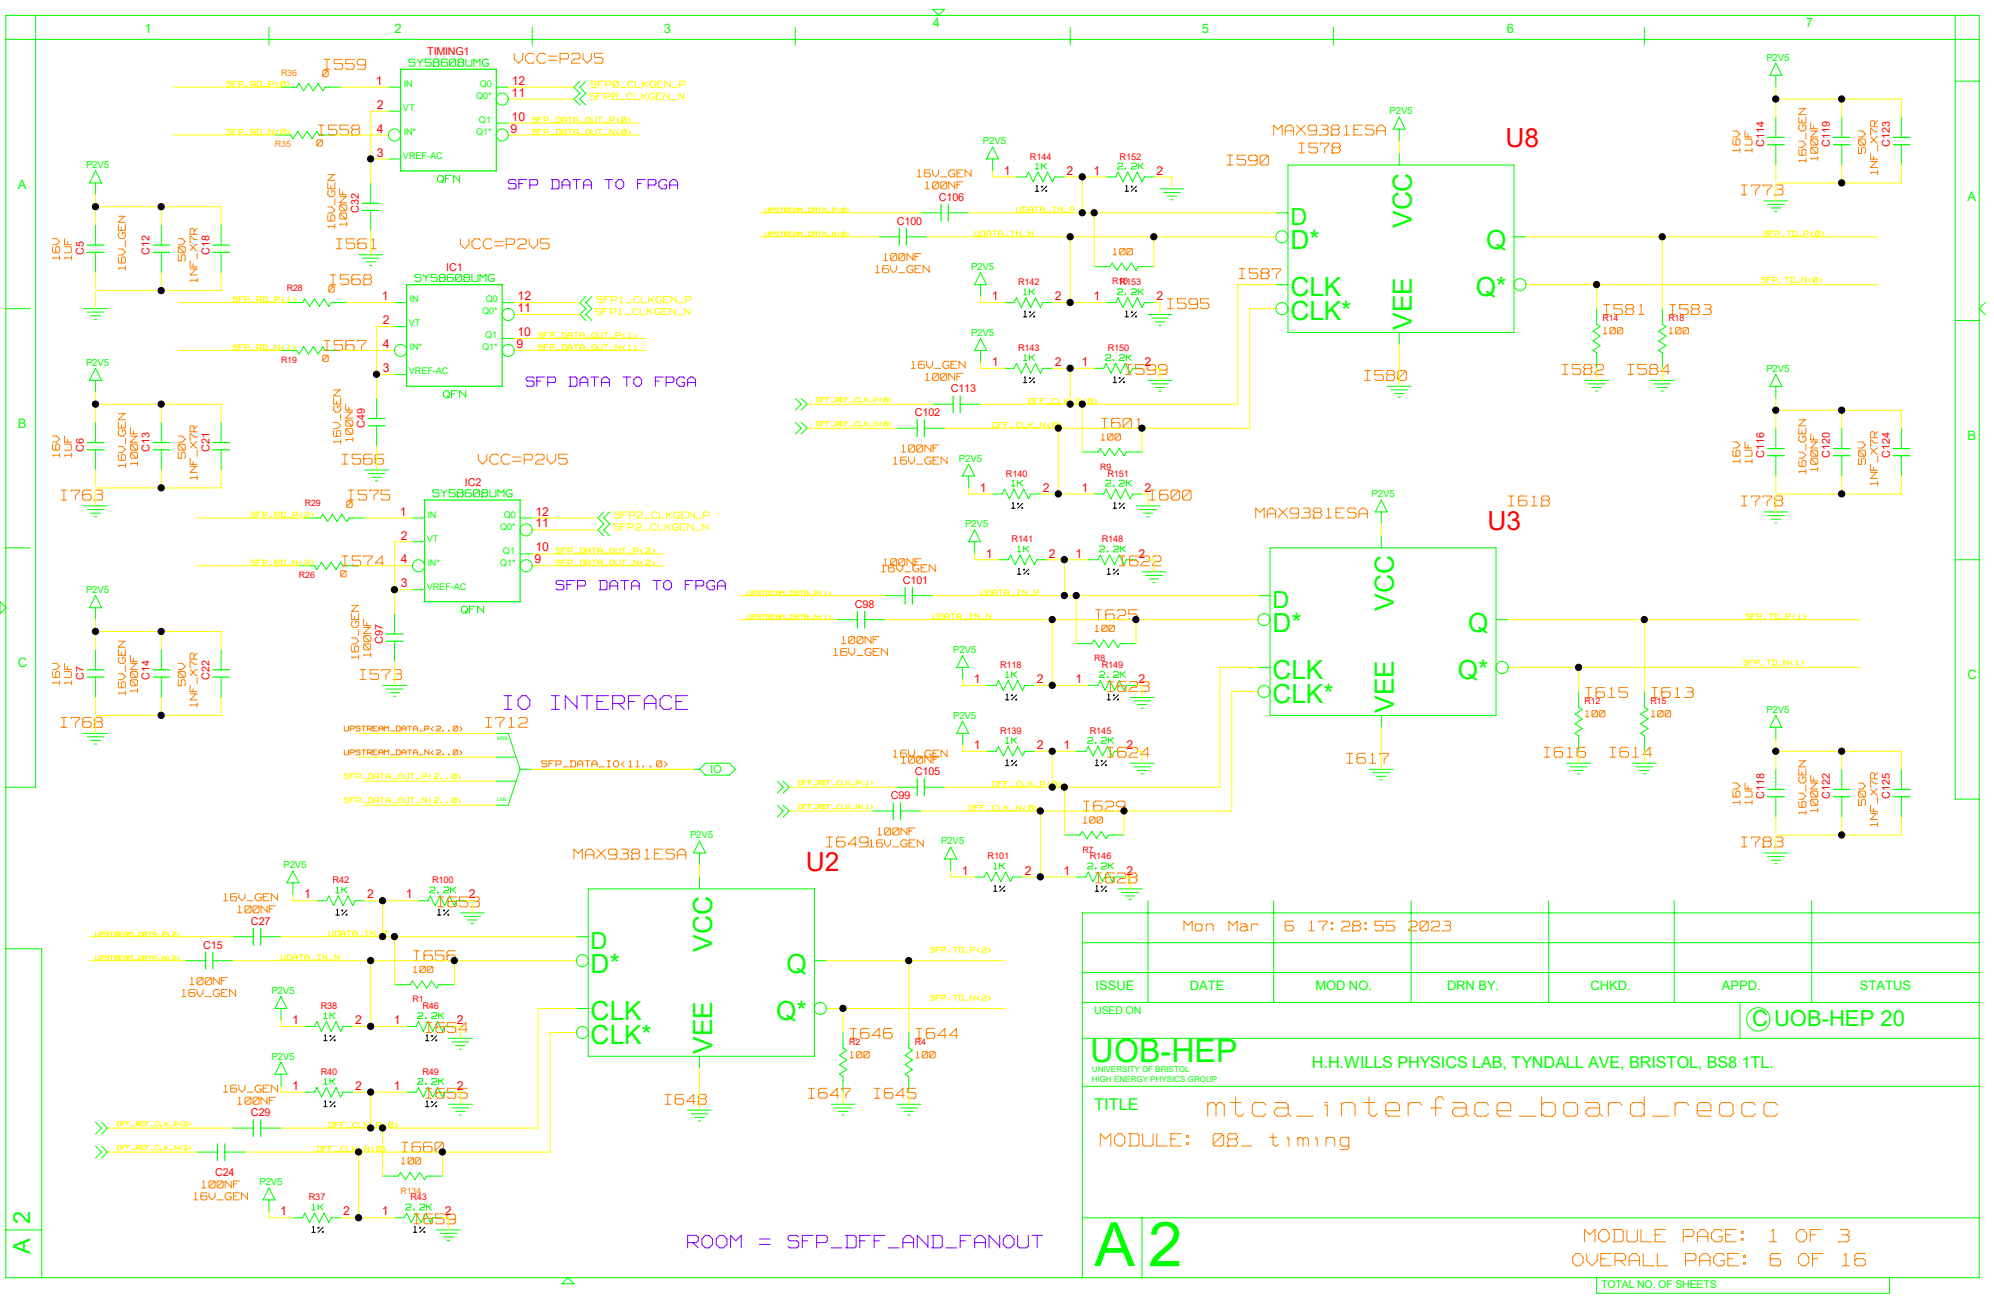
[picture p124: page 6]

UNIVERSITY OF BRISTOL
HIGH ENERGY PHYSICS GROUP
TITLE
MODULE: 08_ timing

H.H.WILLS PHYSICS LAB, TYNDALL AVE, BRISTOL, BS8 1TL.

# ROOM = CLK_GEN_X12

A

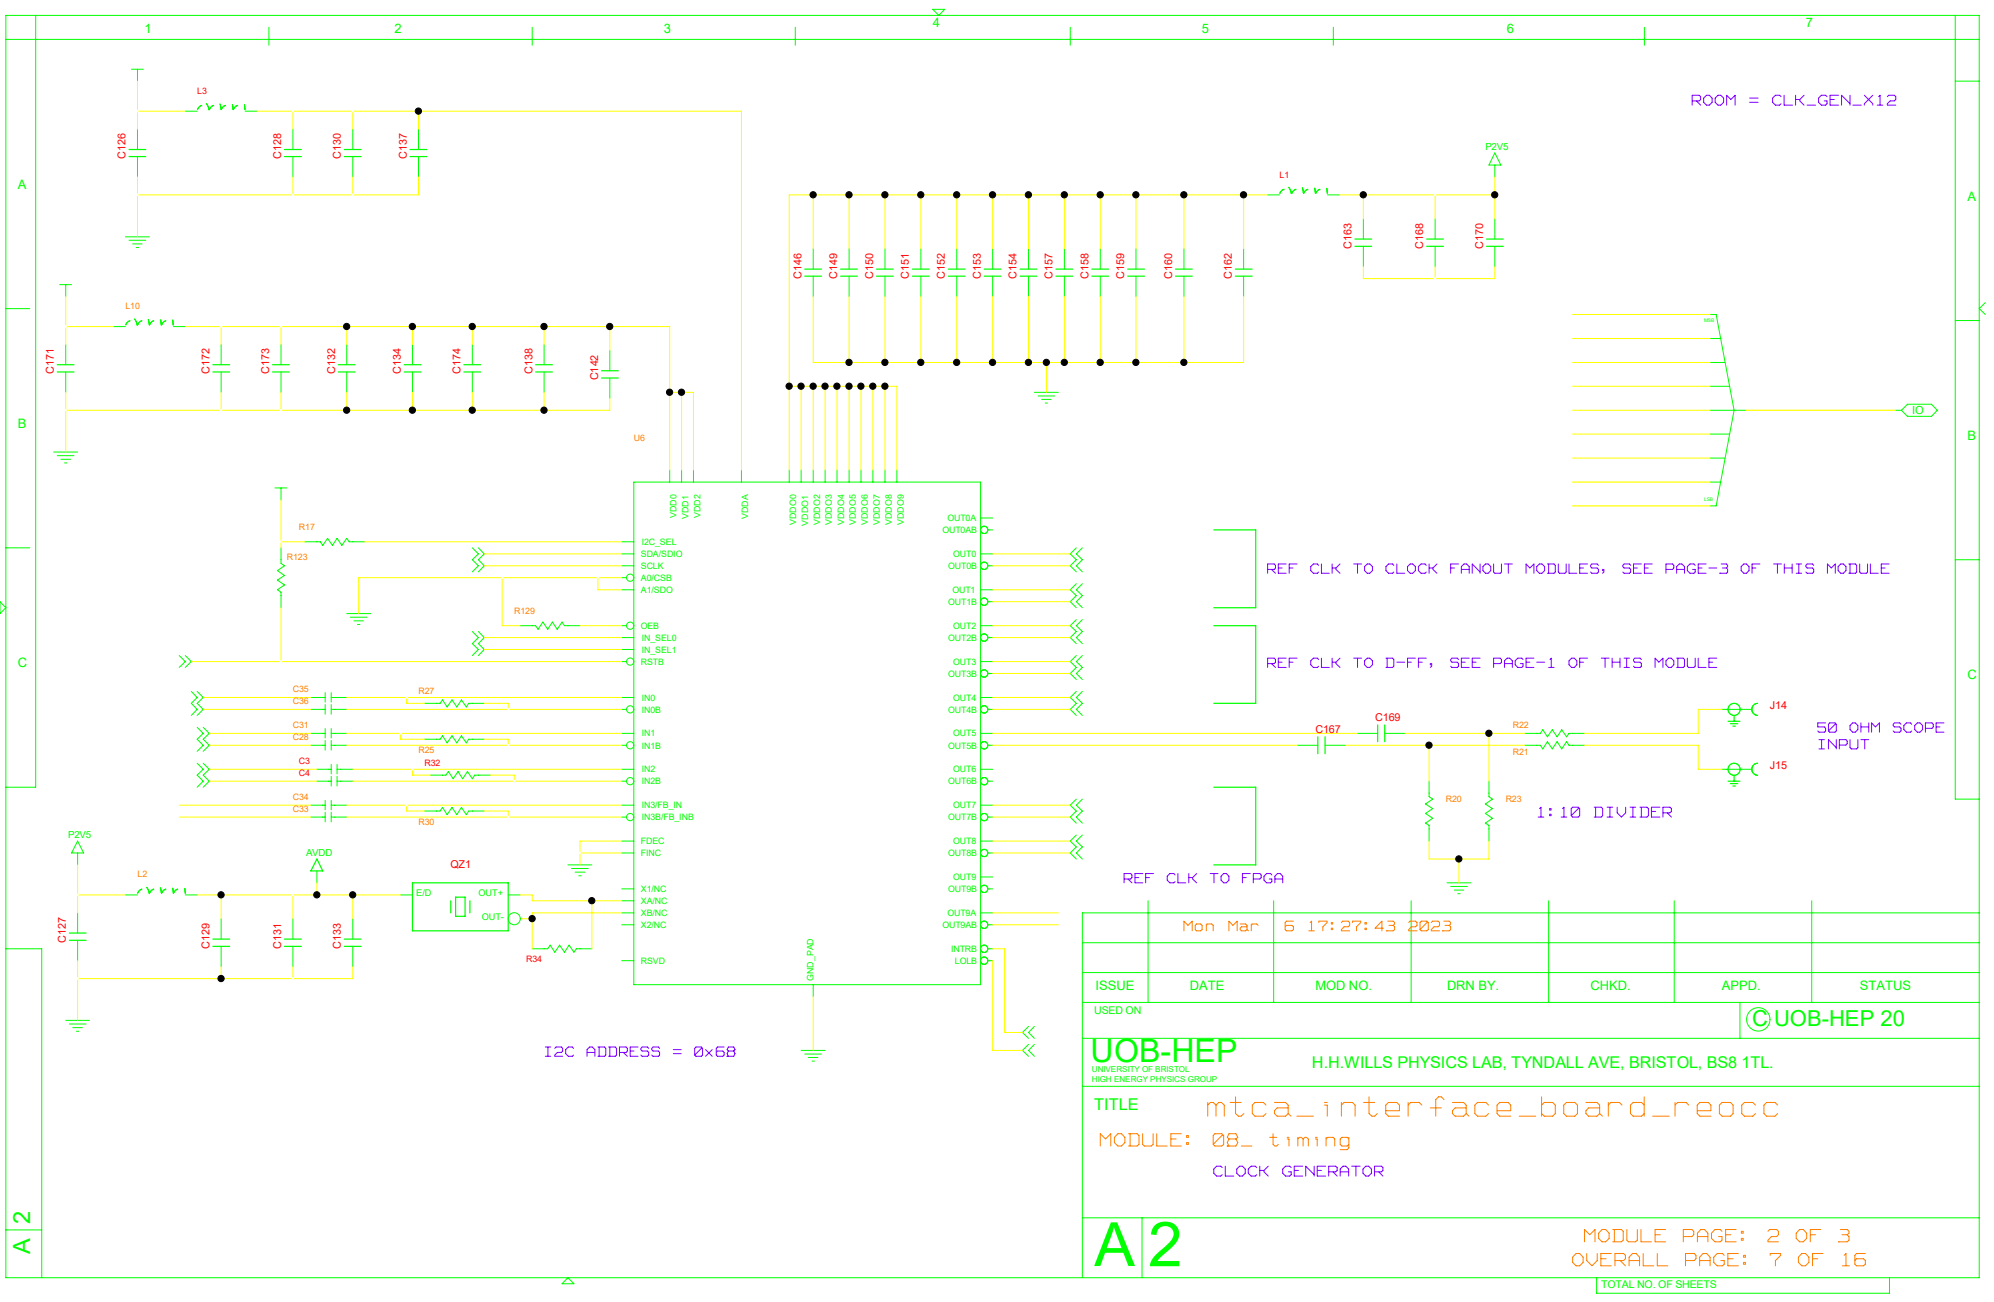
[picture p125: page 7]

REF CLK TO CLOCK FANOUT MODULES, SEE PAGE-3 OF THIS MODULE

REF CLK TO D-FF, SEE PAGE-1 OF THIS MODULE

REF CLK TO FPGA

UNIVERSITY OF BRISTOL
HIGH ENERGY PHYSICS GROUP
TITLE
MODULE: 08_ timing

H.H.WILLS PHYSICS LAB, TYNDALL AVE, BRISTOL, BS8 1TL.

# ROOM = CLK_FO_0_5

## 16V_GEN

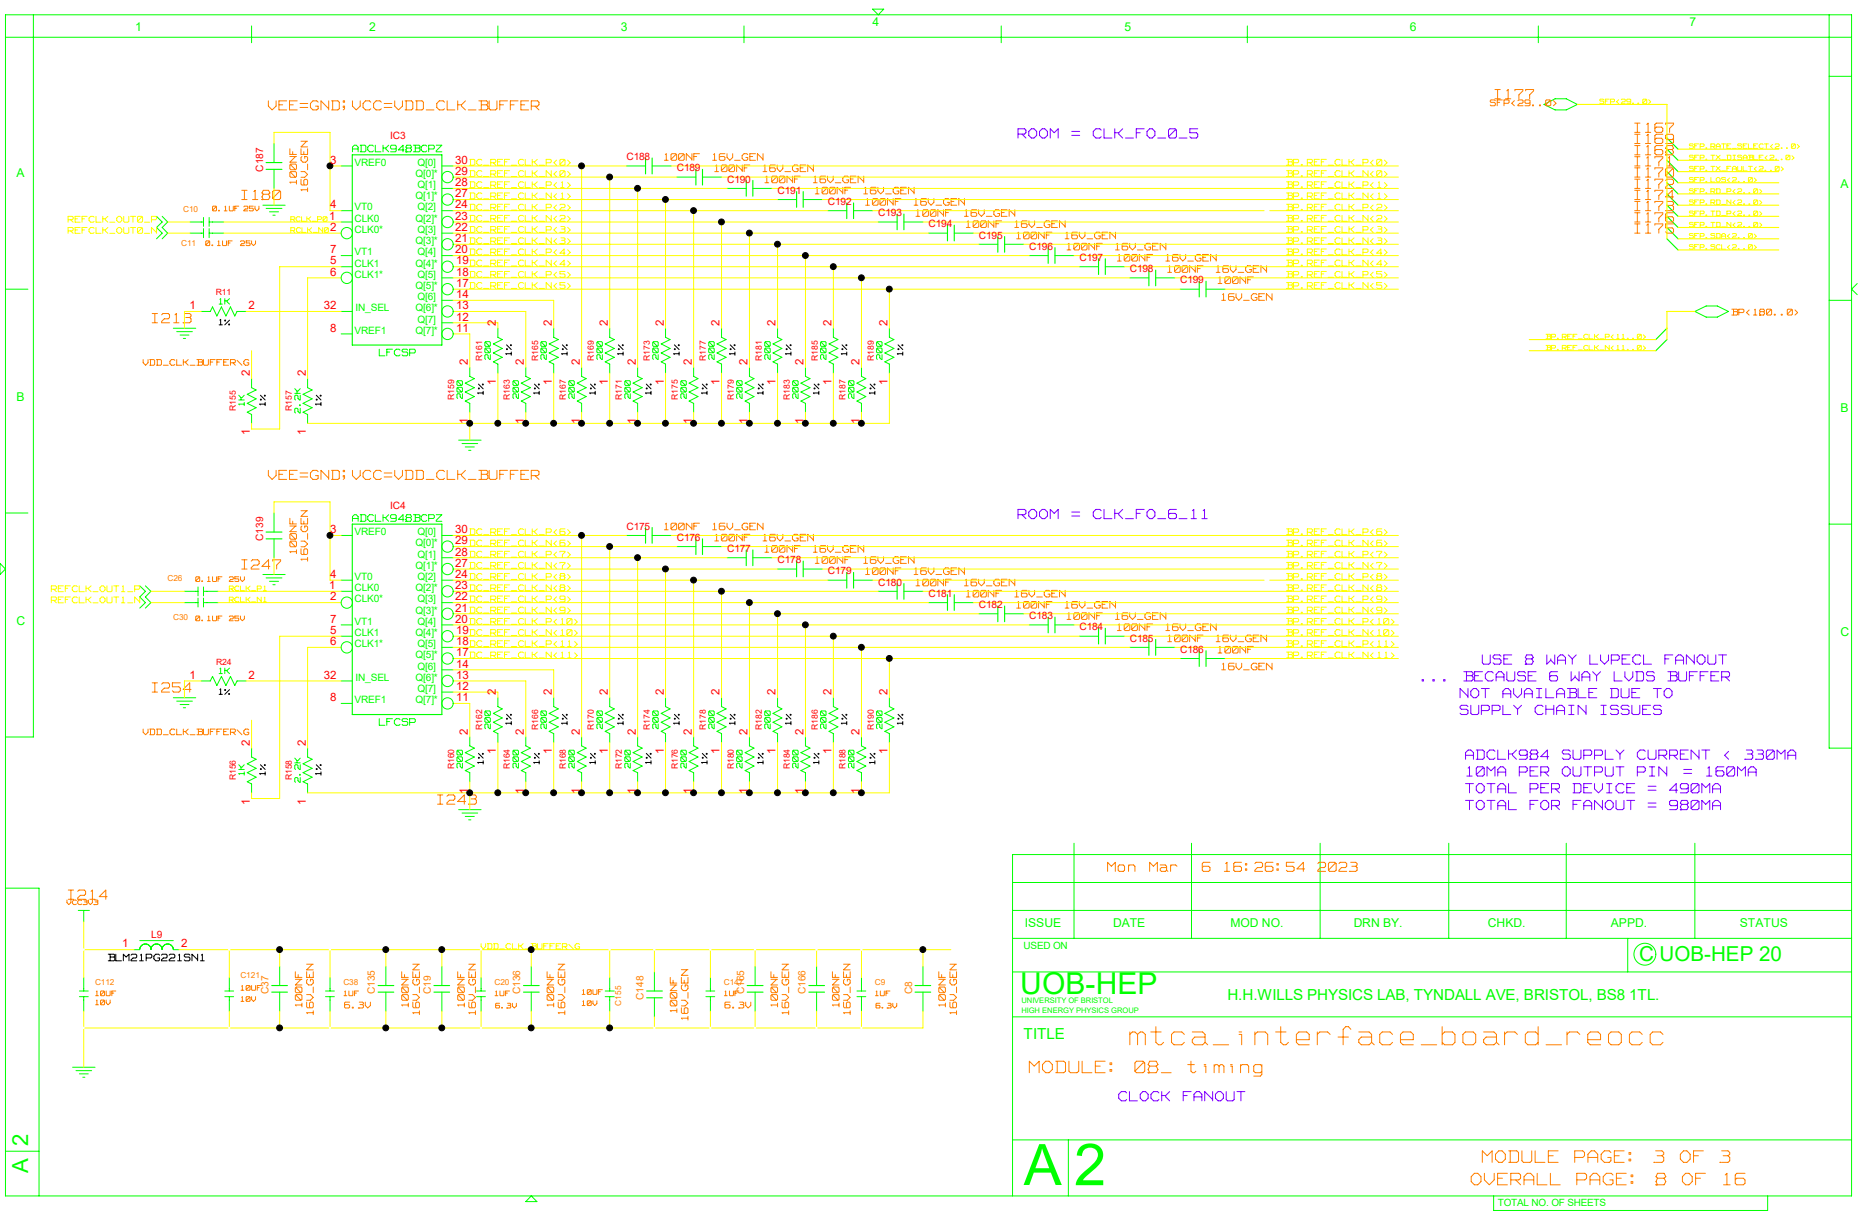
[picture p126: page 8]

USE 8 WAY LVPECL FANOUT
NOT AVAILABLE DUE TO
SUPPLY CHAIN ISSUES

... BECAUSE 6 WAY LVDS BUFFER

UNIVERSITY OF BRISTOL
HIGH ENERGY PHYSICS GROUP
TITLE
MODULE: 08_ timing

H.H.WILLS PHYSICS LAB, TYNDALL AVE, BRISTOL, BS8 1TL.

## SFP.RATE_SELECT<0>

A

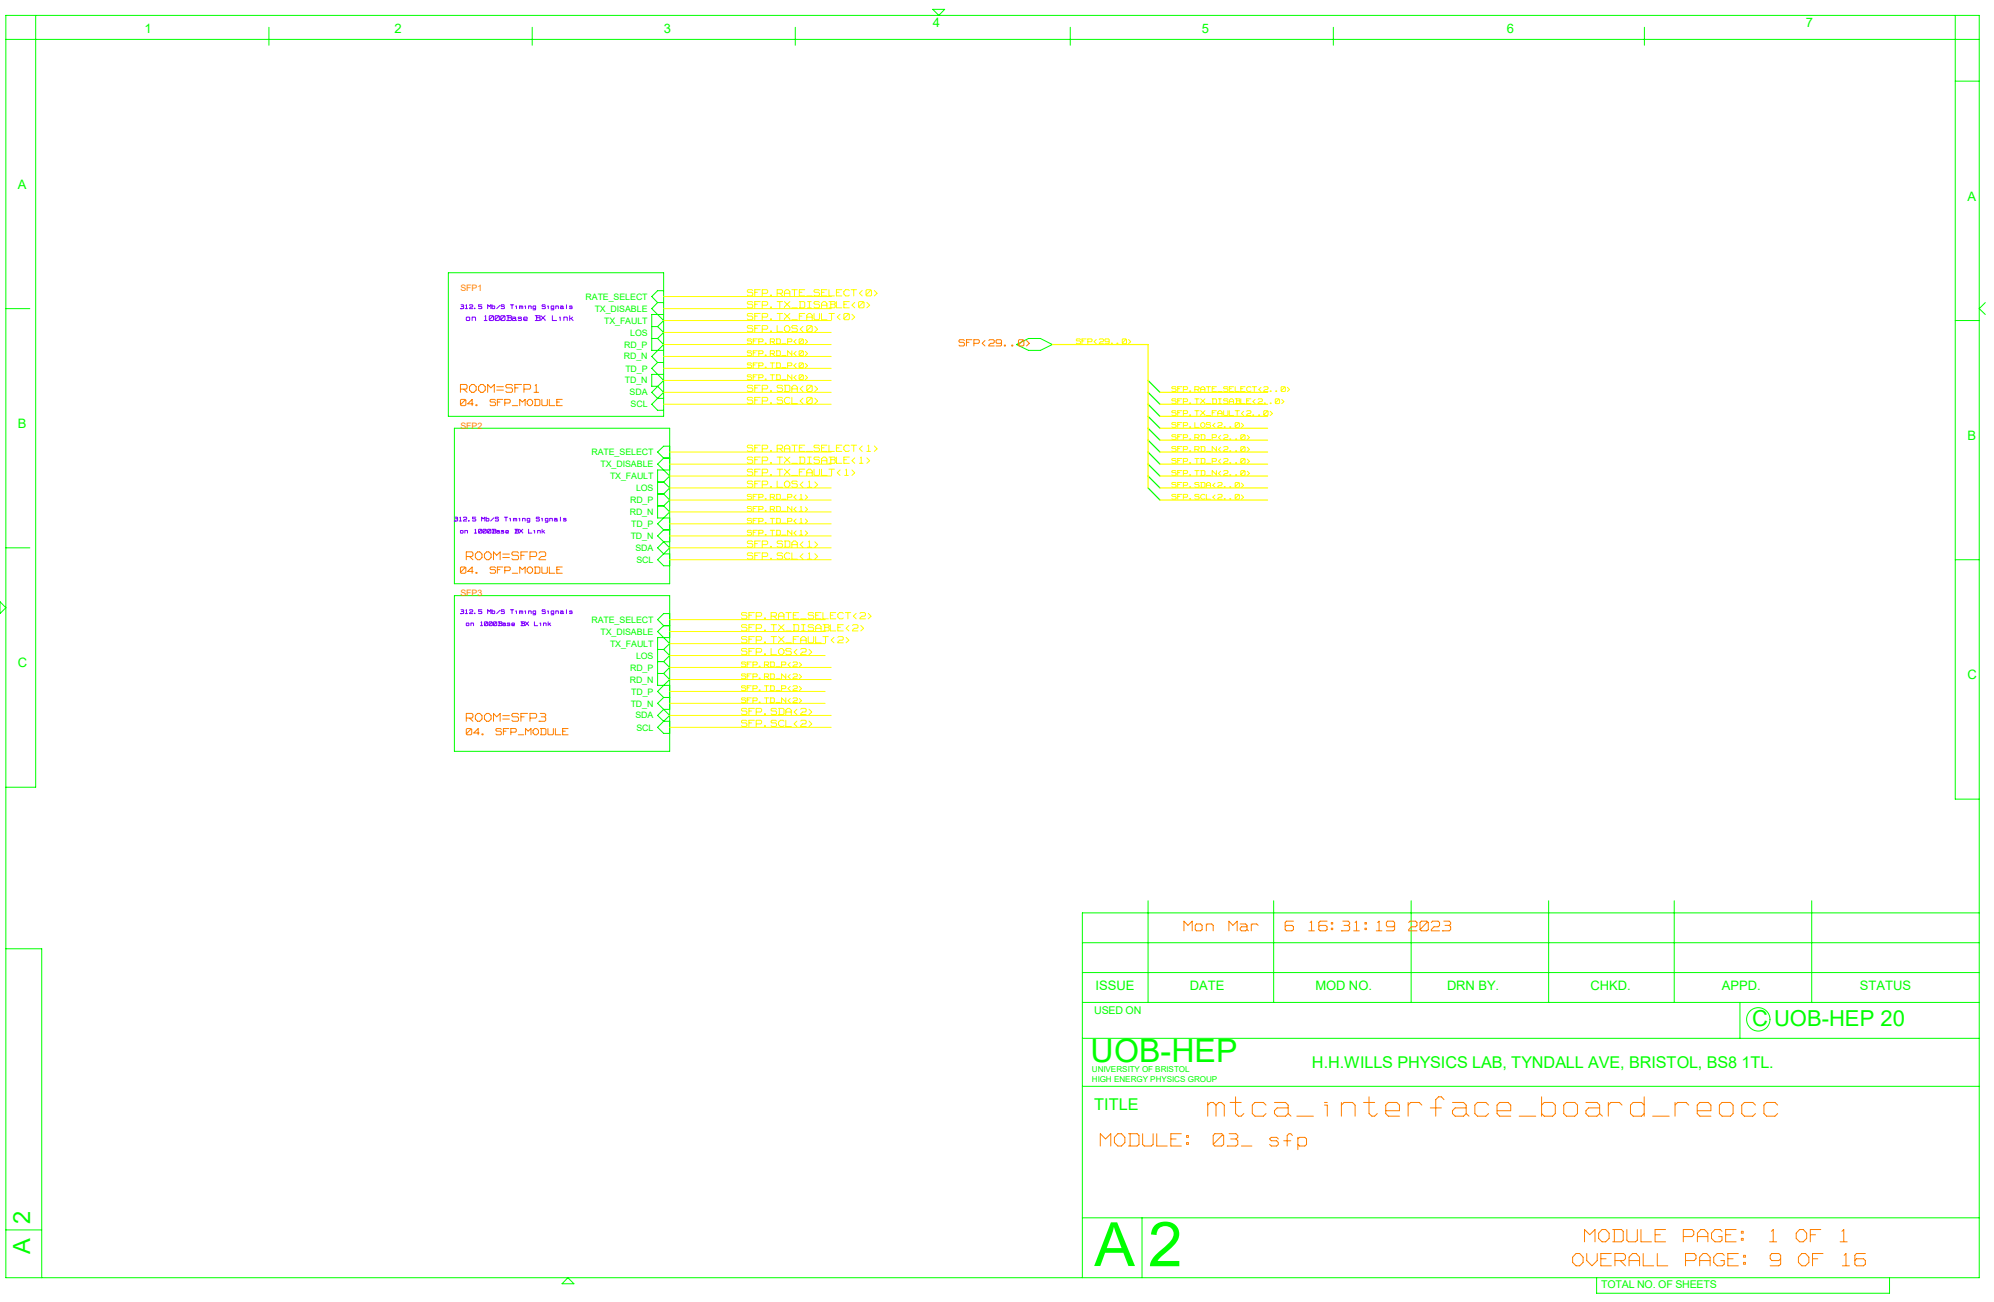
[picture p127: page 9]
Mon Mar 6 16:31:19 2023; mtca_interface_board_reocc; ROOM=SFP1 04. SFP_MODULE; ROOM=SFP3 04. SFP_MODULE; SFP.RATE_SELECT<2> SFP.TX_DISABLE<2> SFP.TX_FAULT<2> SFP.LOS<2>; SFP<29..0>; SFP.TD_P<2>; SFP.RD_N<2>; SFP.RD_P<2>; SFP.TD_N<0>; SFP.TD_P<0>; SFP.RD_P<0> SFP.RD_N<0>; SFP.SCL<0>; SFP.SDA<0>; SFP.TX_DISABLE<0>; SFP.LOS<0>; SFP.TX_FAULT<0>; SFP.SCL<2>; SFP.SDA<2>; SFP.TD_N<2>; SFP.SCL<1>; SFP.SDA<1>; SFP.TD_N<1>; SFP.TD_P<1>; SFP.RD_N<1>; SFP.RD_P<1>; SFP.LOS<1>; SFP.TX_FAULT<1>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

312.5 Mb/S Timing Signals
on 1000Base BX Link

ROOM=SFP2
04. SFP_MODULE

UNIVERSITY OF BRISTOL
HIGH ENERGY PHYSICS GROUP
TITLE
MODULE: 03_ sfp

H.H.WILLS PHYSICS LAB, TYNDALL AVE, BRISTOL, BS8 1TL.

MODULE PAGE: 1 OF 1
OVERALL PAGE: 9 OF 16

22UF
6.3V

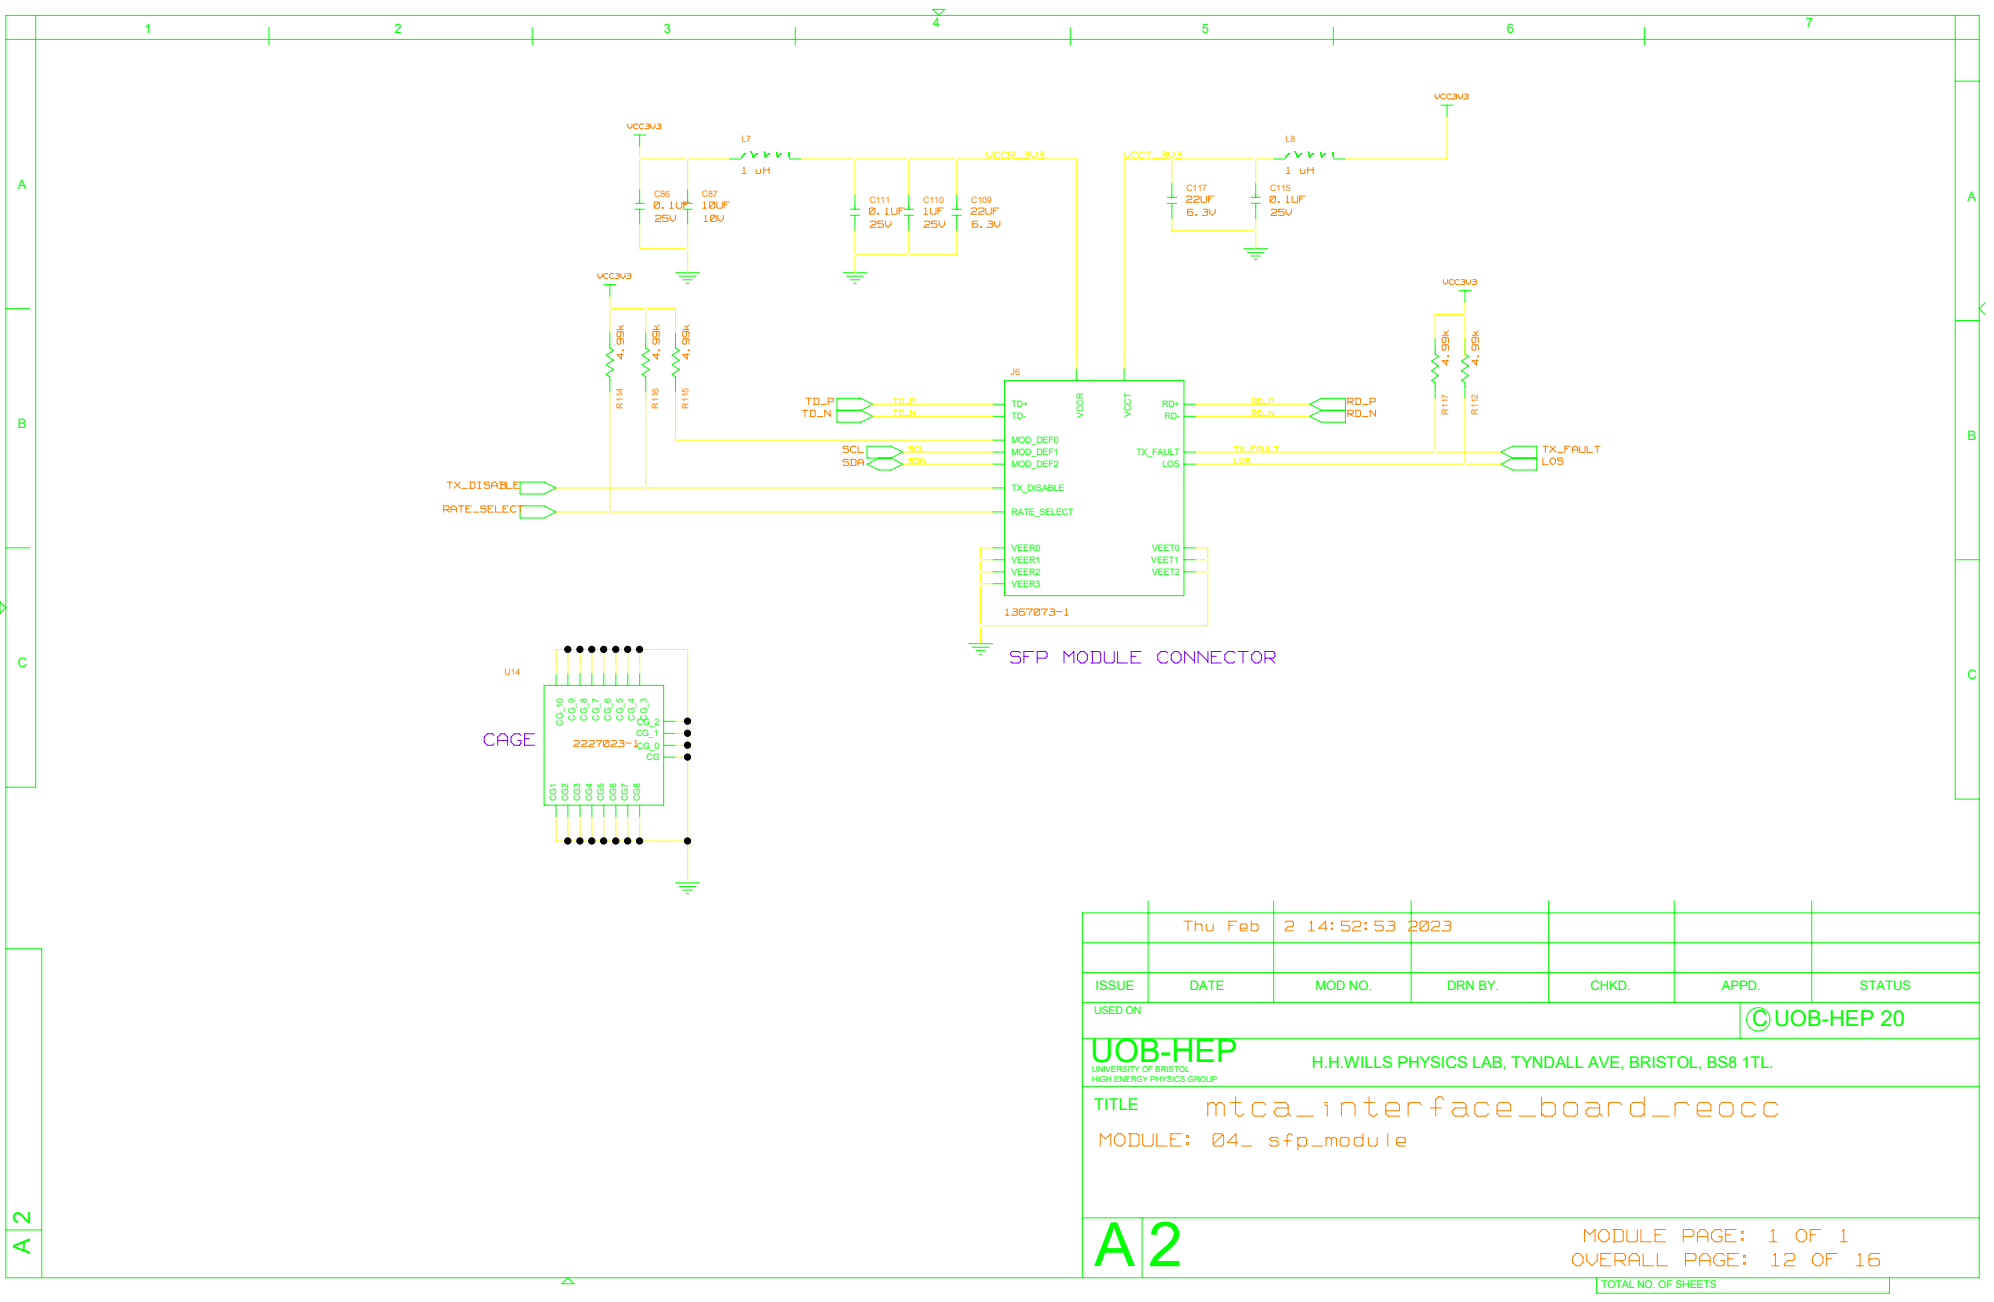
[picture p128: page 10]

UNIVERSITY OF BRISTOL
HIGH ENERGY PHYSICS GROUP
TITLE
MODULE: 04_ sfp_module

H.H.WILLS PHYSICS LAB, TYNDALL AVE, BRISTOL, BS8 1TL.

# AUX IO INTERFACE

JTAG CONNECTOR | EEPROM

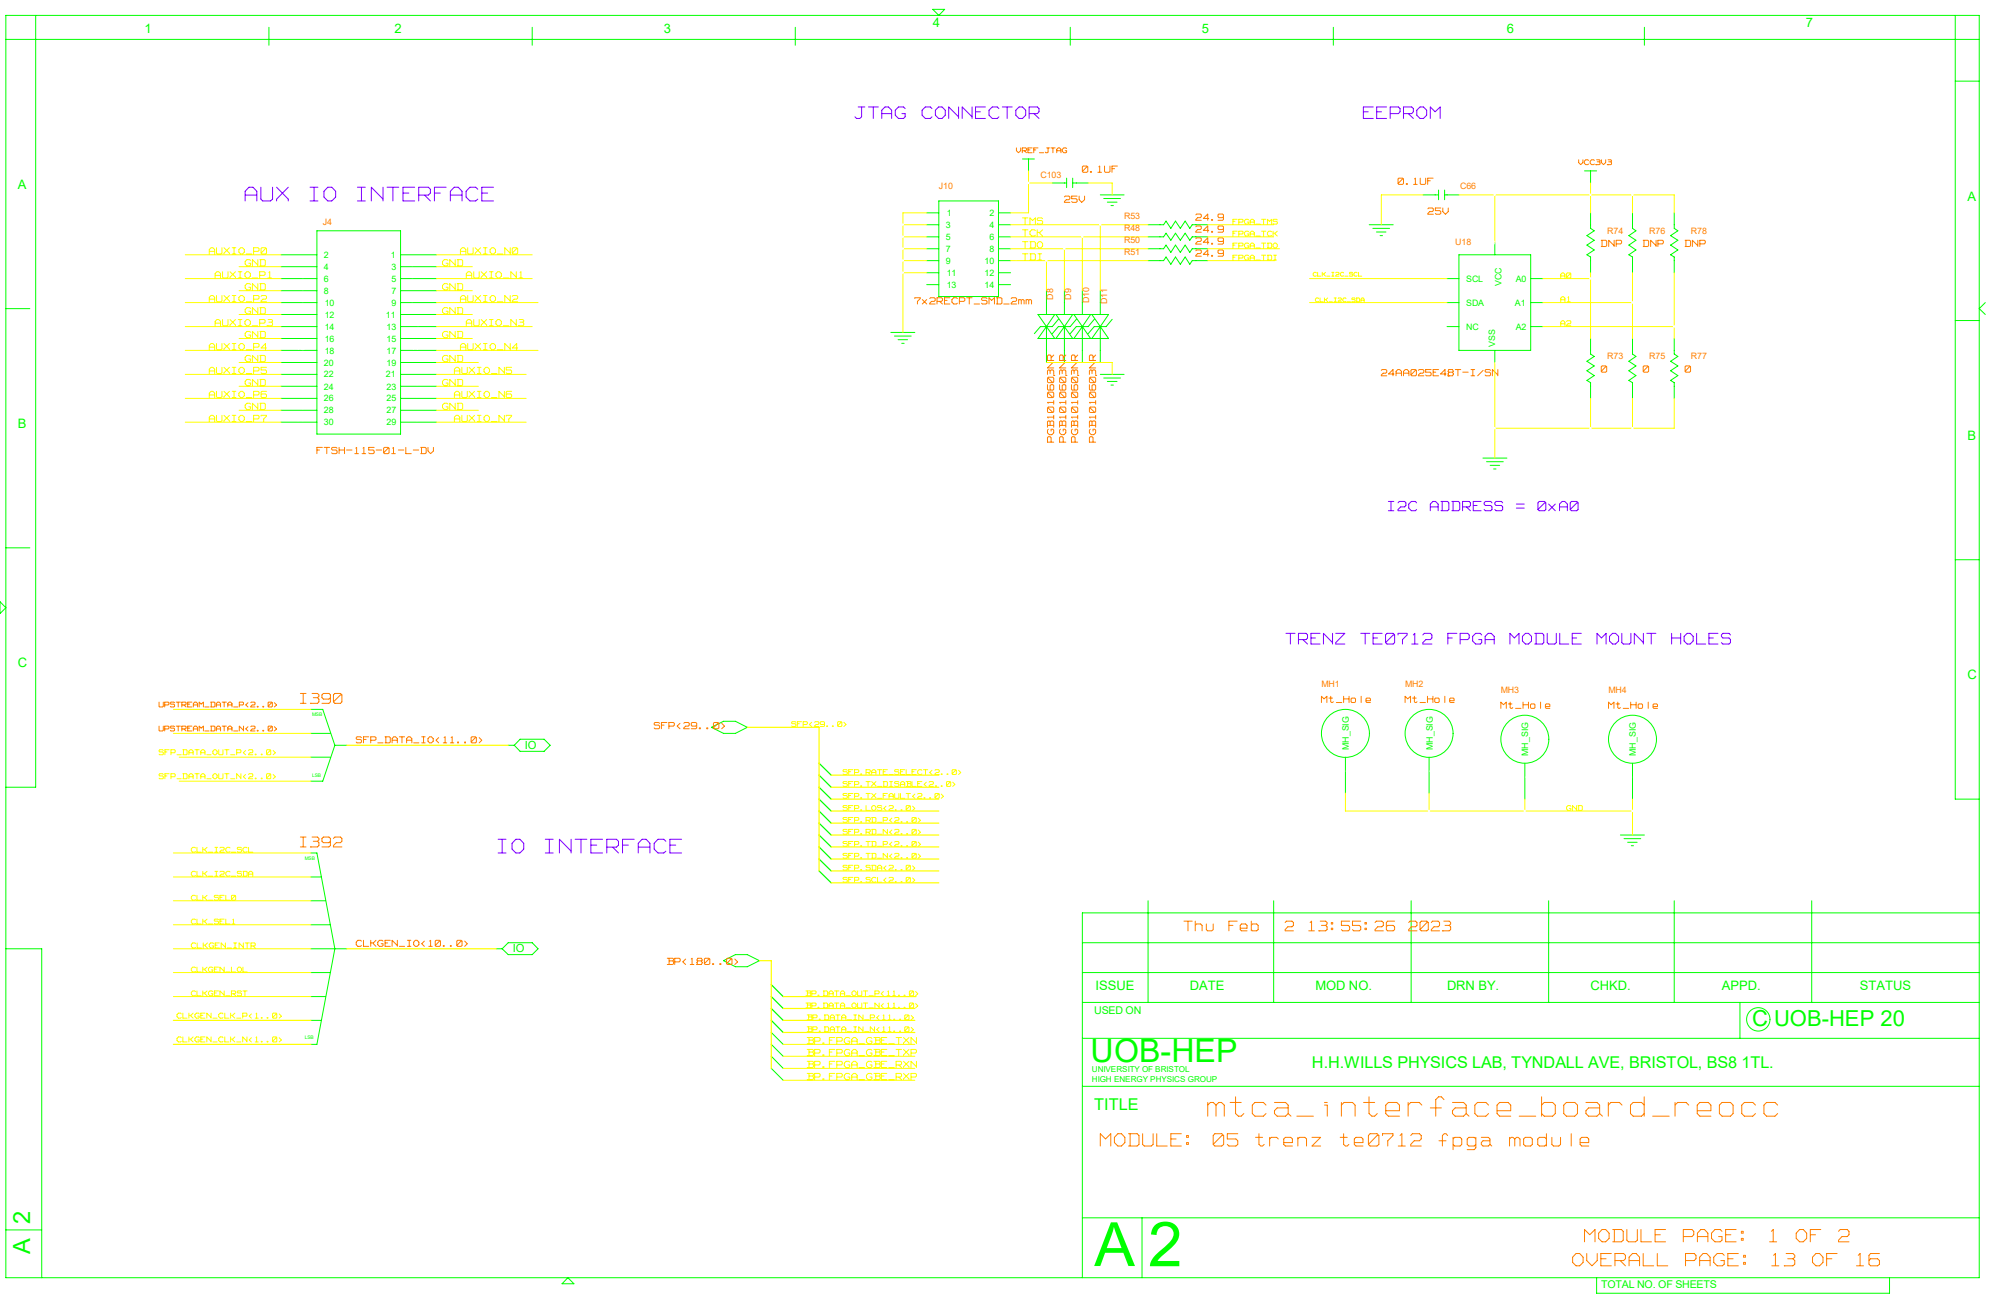
[picture p129: page 11]

TRENZ TE0712 FPGA MODULE MOUNT HOLES

UNIVERSITY OF BRISTOL
HIGH ENERGY PHYSICS GROUP
TITLE
MODULE: 05 trenz te0712 fpga module

H.H.WILLS PHYSICS LAB, TYNDALL AVE, BRISTOL, BS8 1TL.

## FPGA_PG

## P1V5_OUT

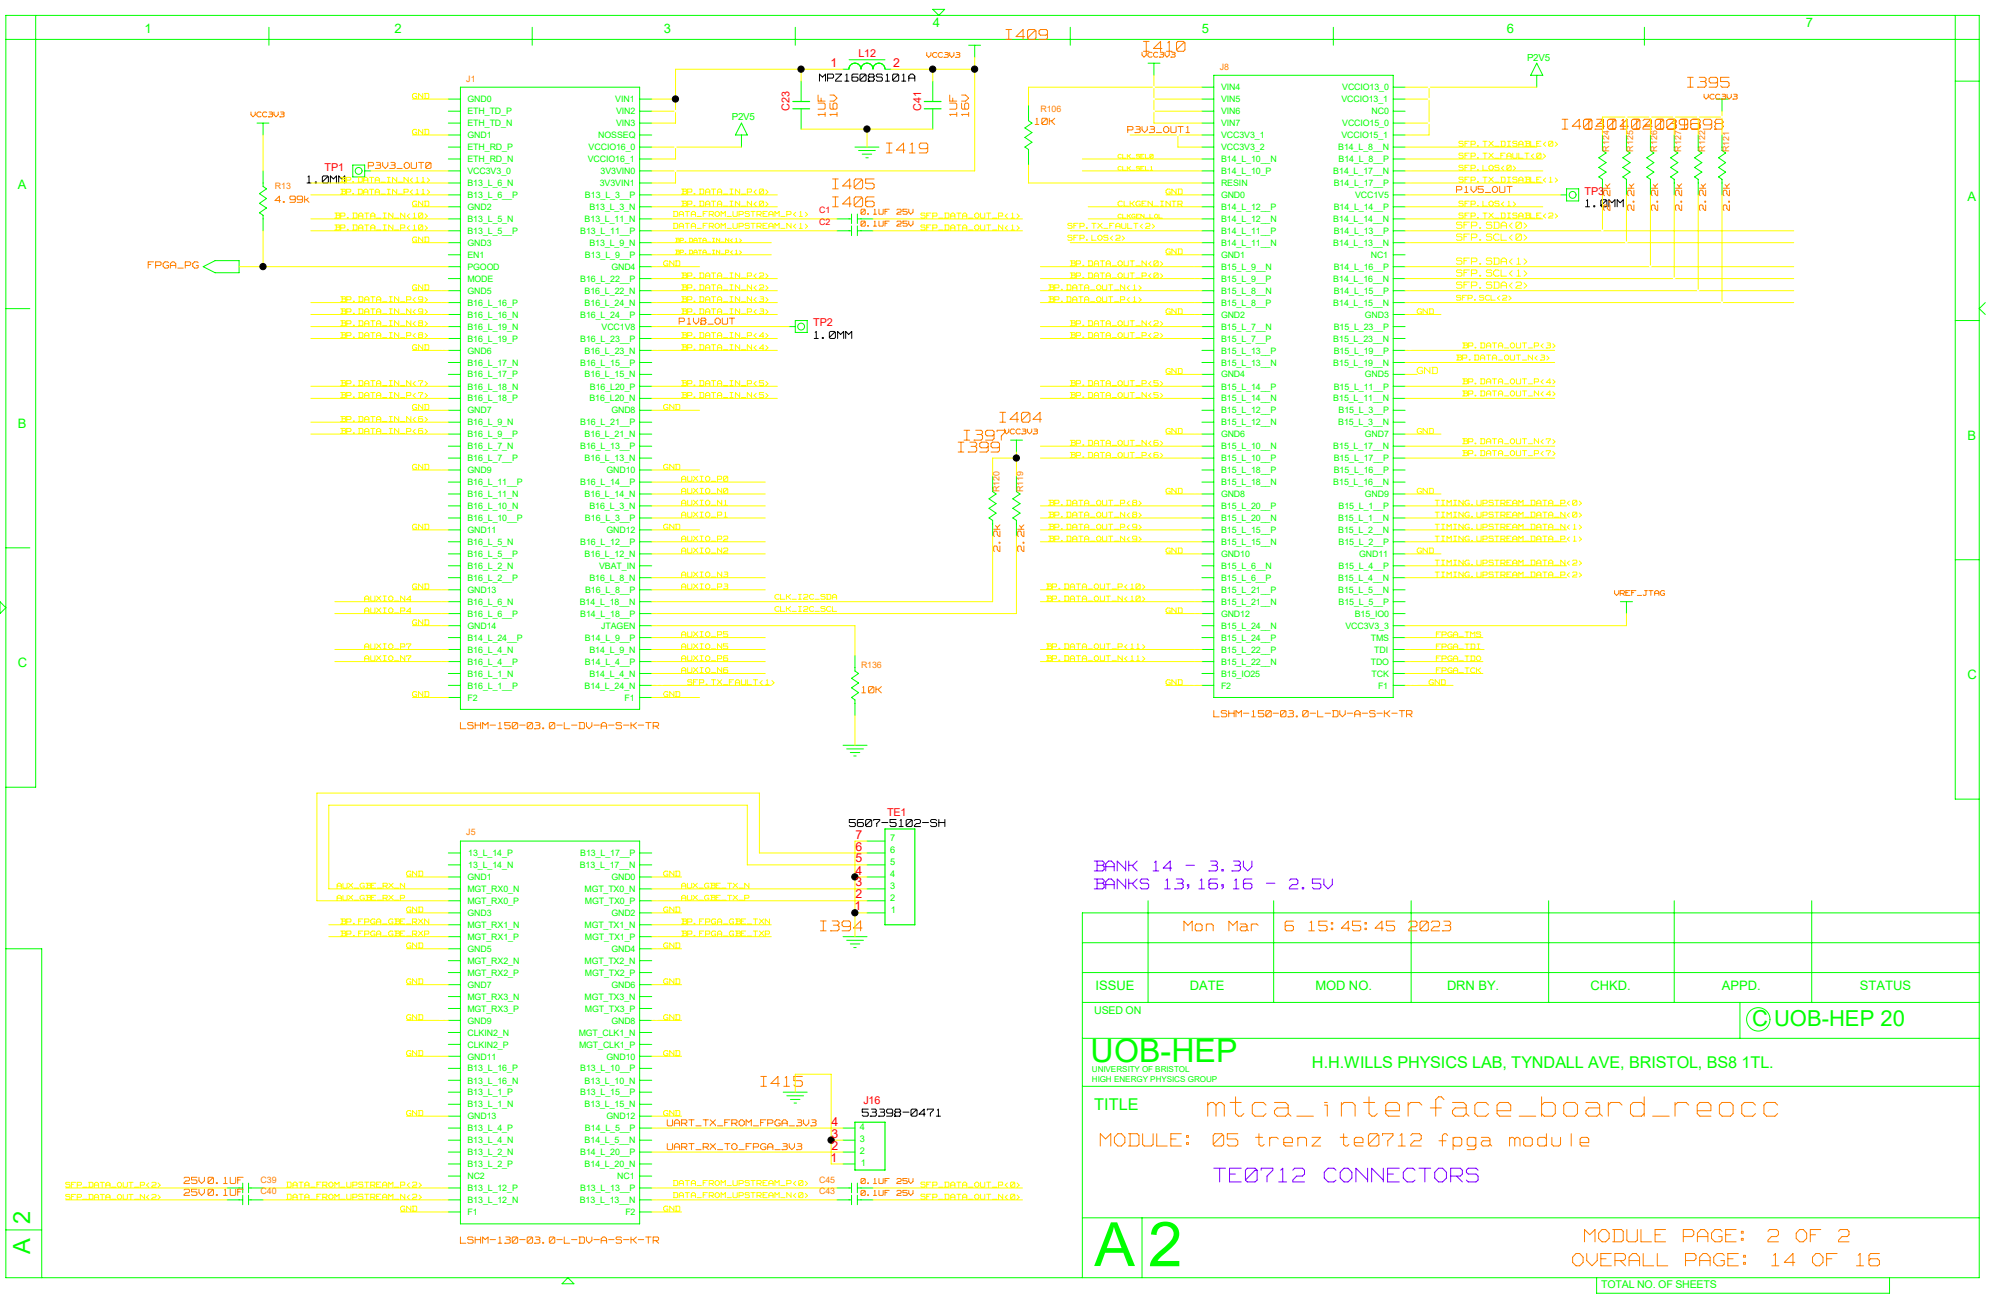
[picture p130: page 12]

UNIVERSITY OF BRISTOL
HIGH ENERGY PHYSICS GROUP
TITLE
MODULE: 05 trenz te0712 fpga module

H.H.WILLS PHYSICS LAB, TYNDALL AVE, BRISTOL, BS8 1TL.

# TONGUE 2 MEZZENINE CONNECTOR

## GND

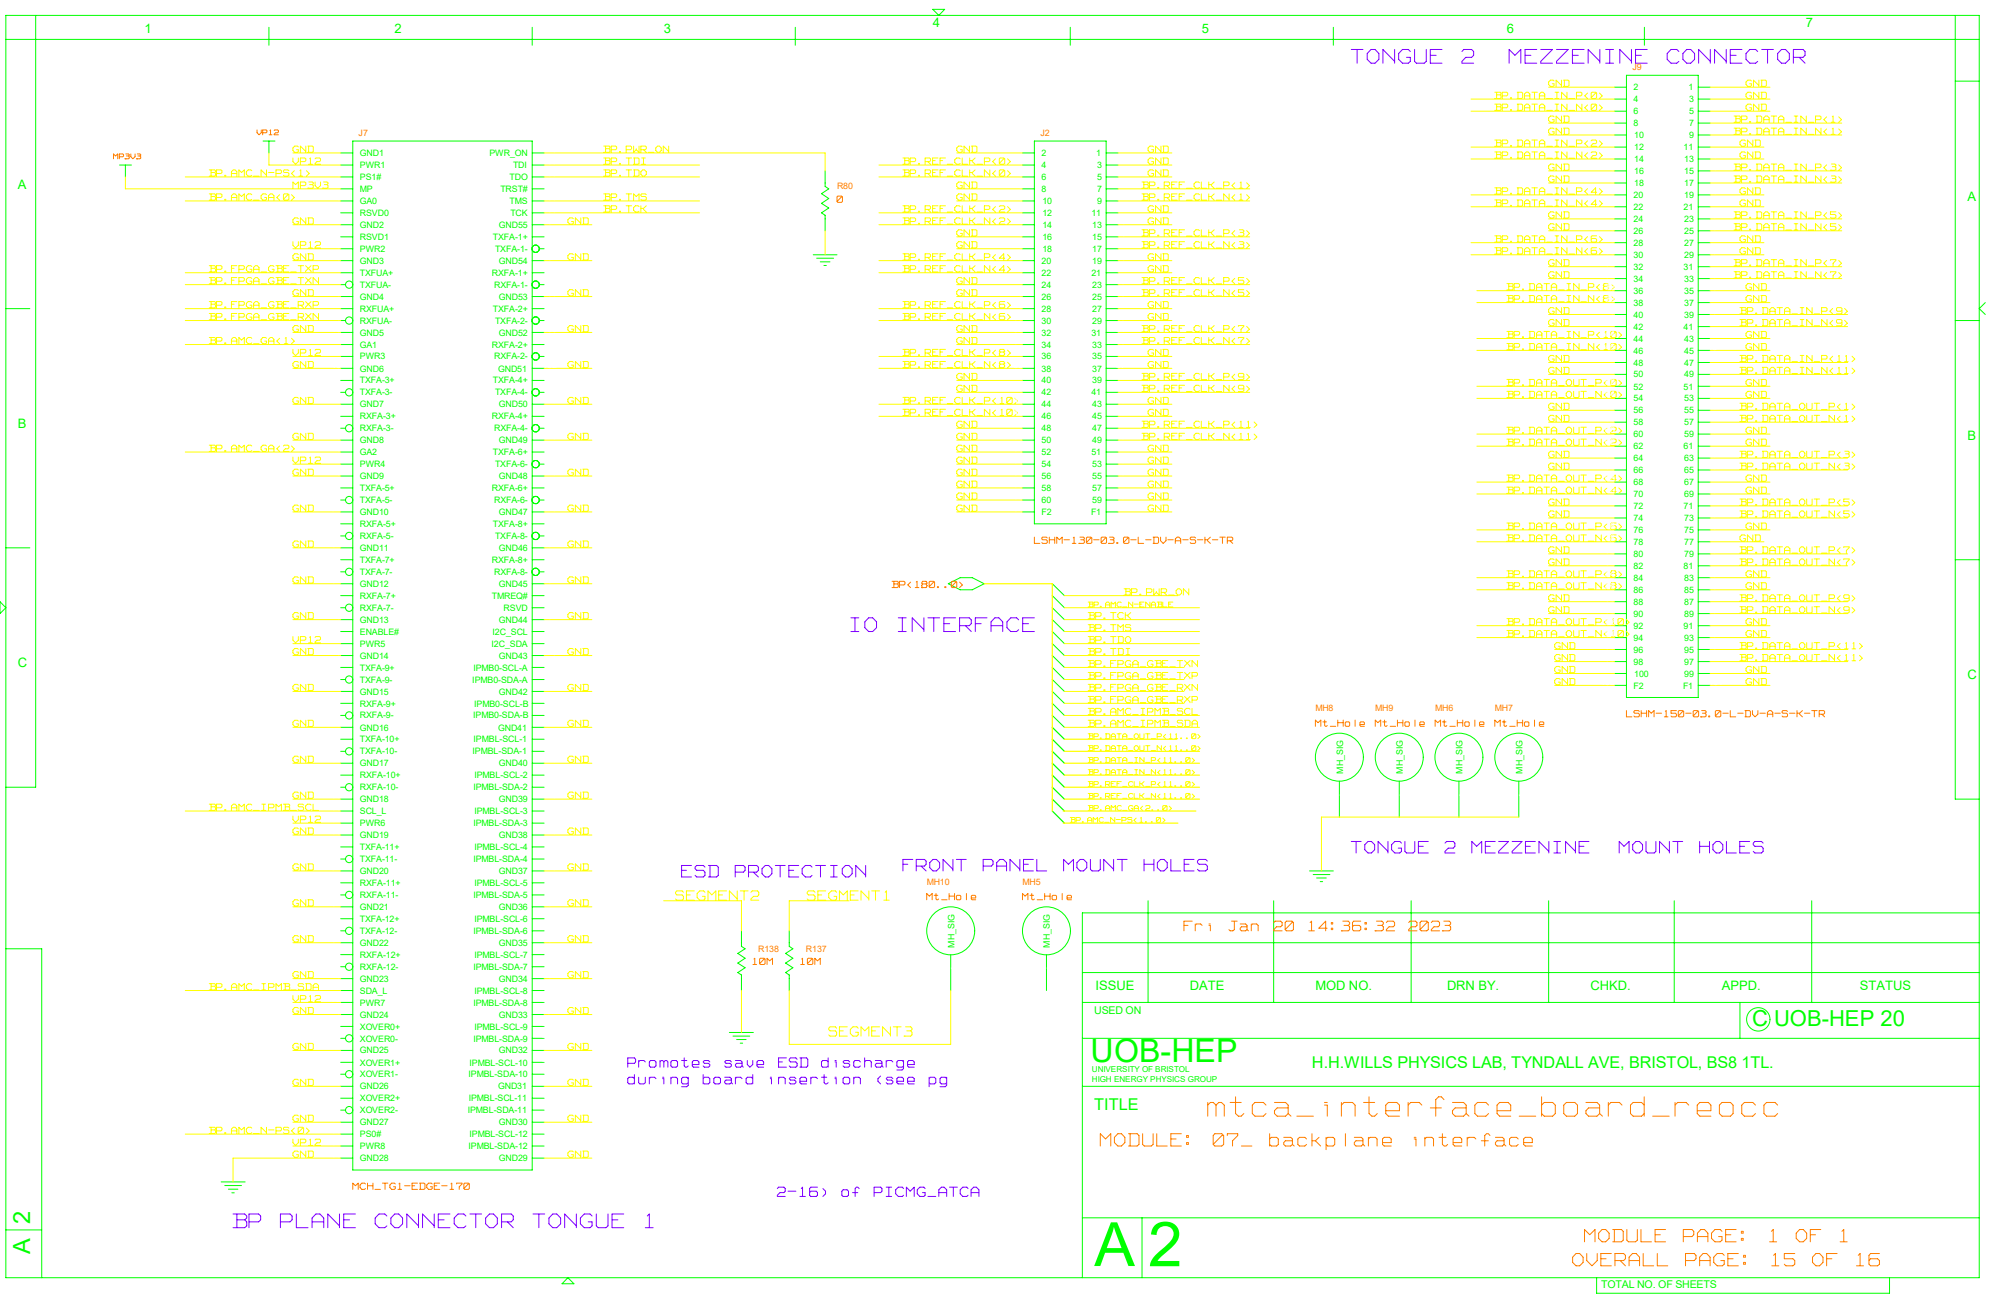
[picture p131: page 13]
2-16) of PICMG_ATCA; IO INTERFACE; ESD PROTECTION; Fri Jan 20 14:36:32 2023; mtca_interface_board_reocc; SEGMENT3; SEGMENT2; SEGMENT1; Mt_Hole; Mt_Hole Mt_Hole Mt_Hole Mt_Hole; BP.AMC_GA<2..0> BP.AMC_N-PS<1..0>; BP.REF_CLK_N<11..0>; BP.REF_CLK_P<11..0>; BP.DATA_IN_N<11..0>; BP.DATA_IN_P<11..0>; BP.DATA_OUT_N<11..0>; BP.AMC_IPMB_SDA; BP.AMC_IPMB_SCL; BP.FPGA_GBE_RXN BP.FPGA_GBE_RXP; BP.FPGA_GBE_TXP; BP.FPGA_GBE_TXN; BP.TDI; BP.TMS BP.TDO; BP.TCK; BP.AMC_N-ENABLE; BP.PWR_ON; BP.DATA_OUT_P<11..0>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

LSHM-130-03.0-L-DV-A-S-K-TR

LSHM-150-03.0-L-DV-A-S-K-TR

TONGUE 2 MEZZENINE MOUNT HOLES

FRONT PANEL MOUNT HOLES

Promotes save ESD discharge
during board insertion (see pg

UNIVERSITY OF BRISTOL
HIGH ENERGY PHYSICS GROUP
TITLE
MODULE: 07_ backplane interface

H.H.WILLS PHYSICS LAB, TYNDALL AVE, BRISTOL, BS8 1TL.

BP PLANE CONNECTOR TONGUE 1

MODULE PAGE: 1 OF 1
OVERALL PAGE: 15 OF 16

# IO INTERFACE

# MODULE MANAGEMENT CONTROL

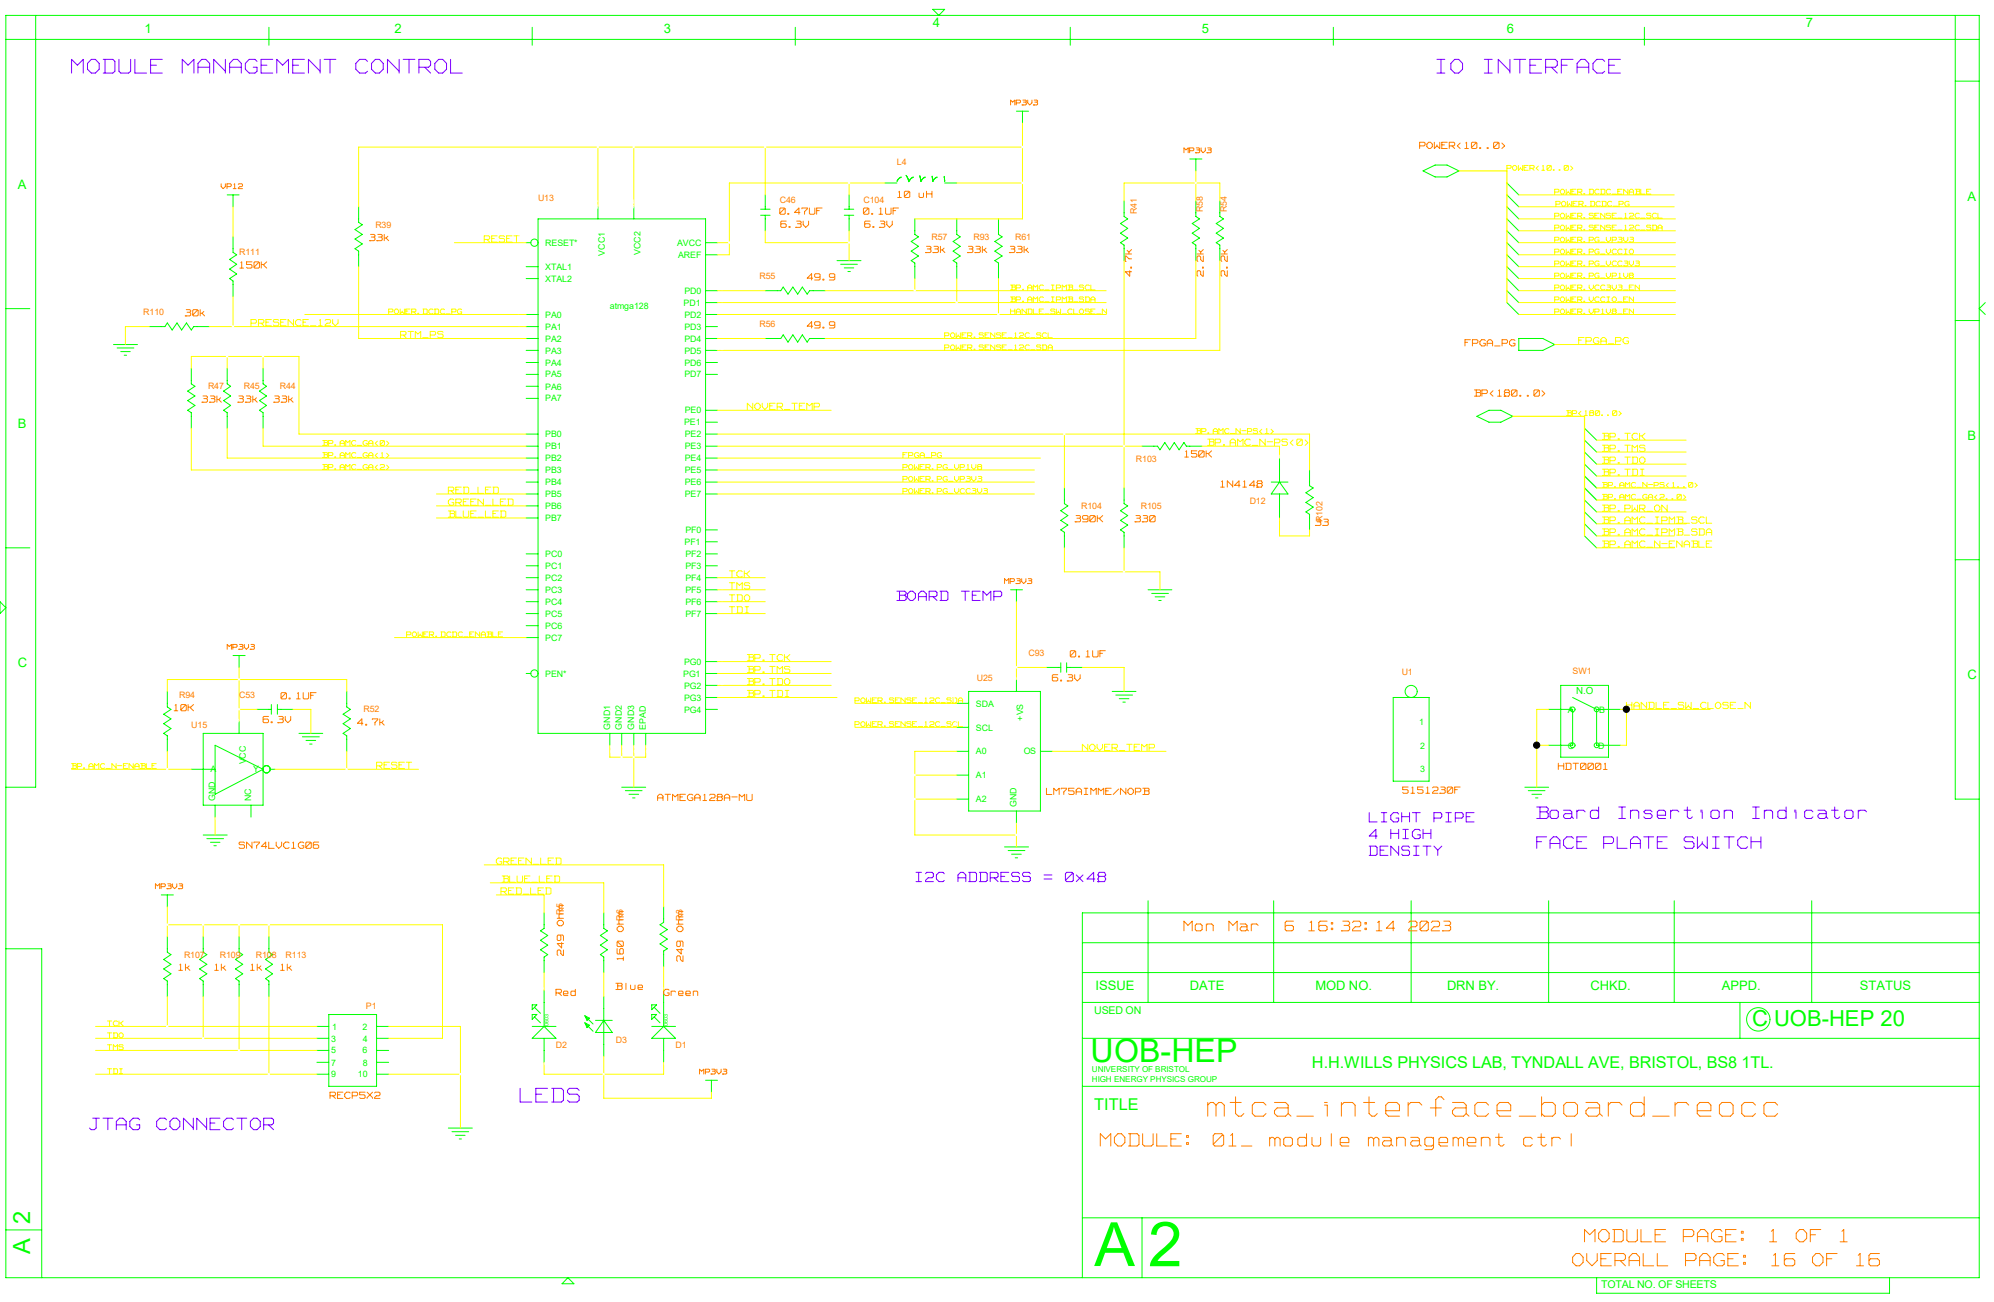
[picture p132: page 14]

A C R3 R102 R5 R6 21 22 52 536365 GND1 GND2 GND3 EPAD VCC1 VCC2 GND NC VCC GND +VS

BP.AMC_N-PS<1>
BP.TCK BP.AMC_N-PS<0>

UNIVERSITY OF BRISTOL
HIGH ENERGY PHYSICS GROUP
TITLE
MODULE: 01_ module management ctrl

H.H.WILLS PHYSICS LAB, TYNDALL AVE, BRISTOL, BS8 1TL.
