uob-hep-cad/uob-hep-pc072/hardware/Schematics/dune_mib_v2_2mar23.pdf

1 | 3
5 | 6

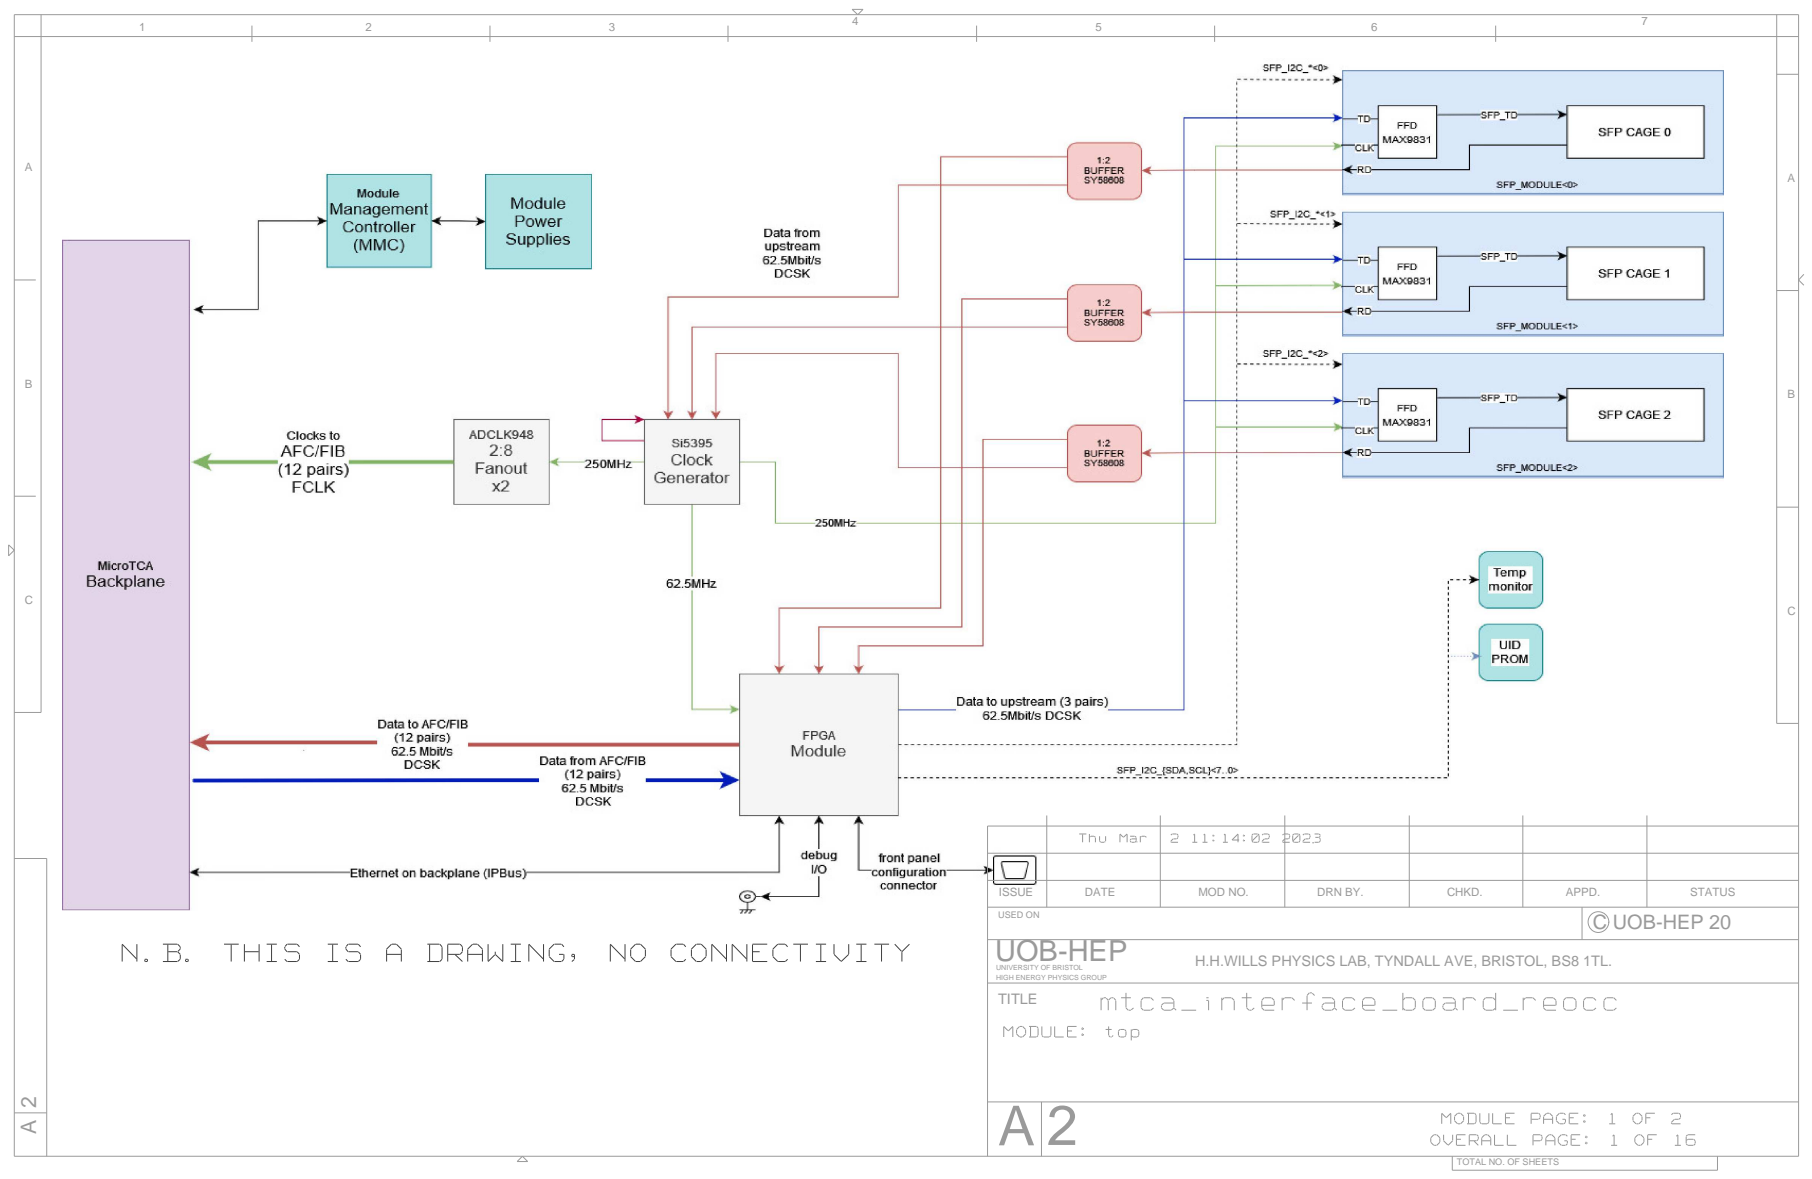
[picture p139: page 1]
N.B. THIS IS A; DRAWING, NO; CONNECTIVITY; Thu Mar; mtca_interface_board_reocc; UOB-HEP

ISSUE | DATE | MOD NO. | DRN BY. | CHKD. | APPD. | STATUS

USED ON | C UOB-HEP 20

H.H.WILLS PHYSICS LAB, TYNDALL AVE, BRISTOL, BS8 1TL.

UNIVERSITY OF BRISTOL
HIGH ENERGY PHYSICS GROUP
TITLE
MODULE: top

MODULE PAGE: 1 OF 2
OVERALL PAGE: 1 OF 16

TOTAL NO. OF SHEETS

1 | 3 | 4 | 5 | 6 | 7

A

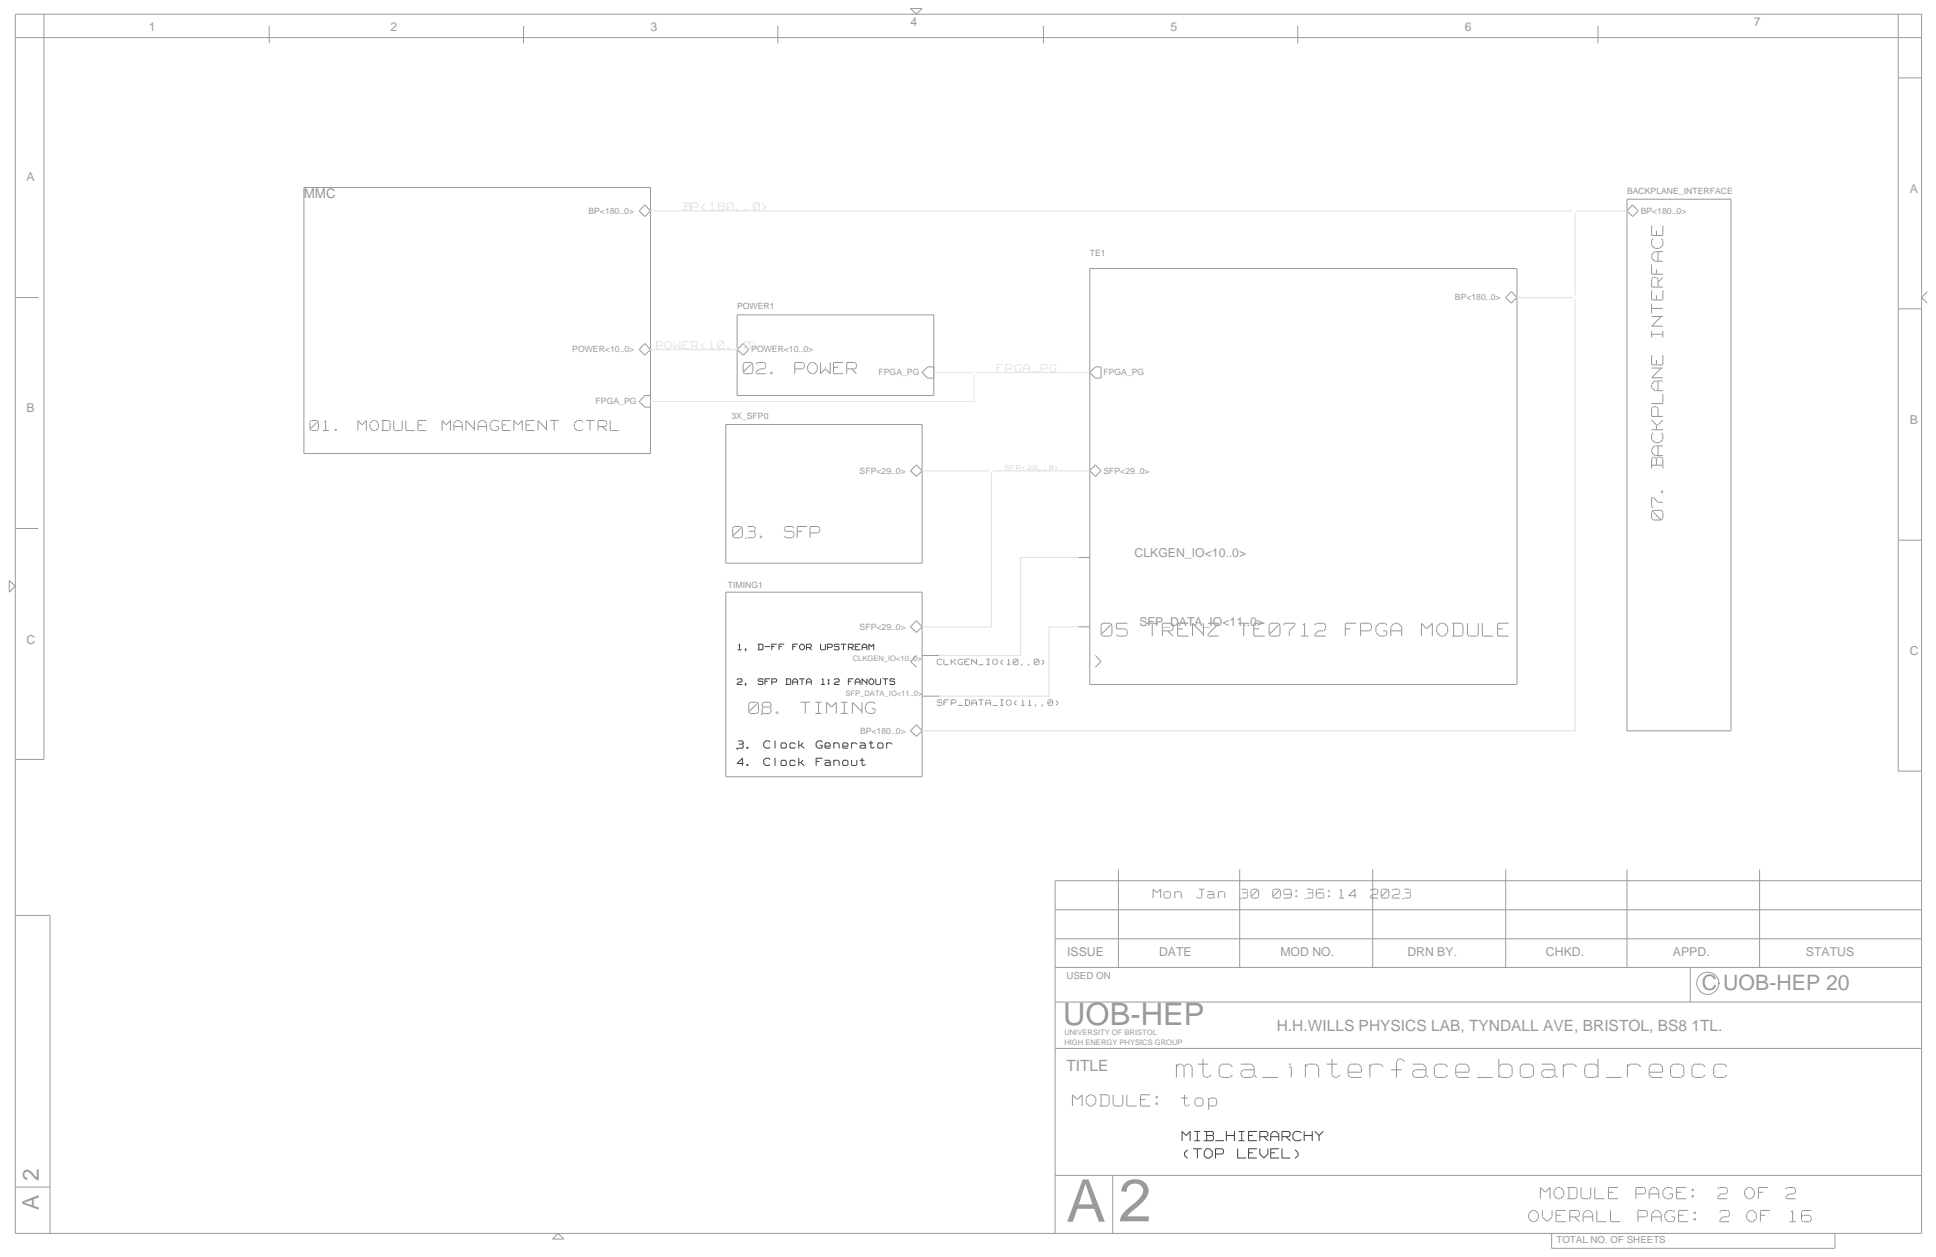
[picture p140: page 2]
MIB_HIERARCHY; (TOP; LEVEL); 3. Clock Generator 4. Clock Fanout; Mon Jan 30 09:36:14; mtca_interface_board_reocc; 03. SFP; POWER<10..0>; CLKGEN_IO<10..0>; SFP_DATA_IO<11..0>; 05 TRENZ TE0712 FPGA; MODULE; 02. POWER; MODULE MANAGEMENT; CTRL; SFP<29..0>; 07. BACKPLANEINTERFACE FPGA_PG BP<180..0>; 3X_SFP0; TIMING1; POWER1; BACKPLANE_INTERFACE; FPGA_PG; MMC; UOB-HEP

1. D-FF FOR UPSTREAM

2. SFP DATA 1:2 FANOUTS
08. TIMING

ISSUE | DATE | MOD NO. | DRN BY. | CHKD. | APPD. | STATUS

USED ON | C UOB-HEP 20

H.H.WILLS PHYSICS LAB, TYNDALL AVE, BRISTOL, BS8 1TL.

UNIVERSITY OF BRISTOL
HIGH ENERGY PHYSICS GROUP
TITLE
MODULE: top

MODULE PAGE: 2 OF 2
OVERALL PAGE: 2 OF 16

VP3V3 IV | MONITOR
WANT 0.3V DROP AT | 2A

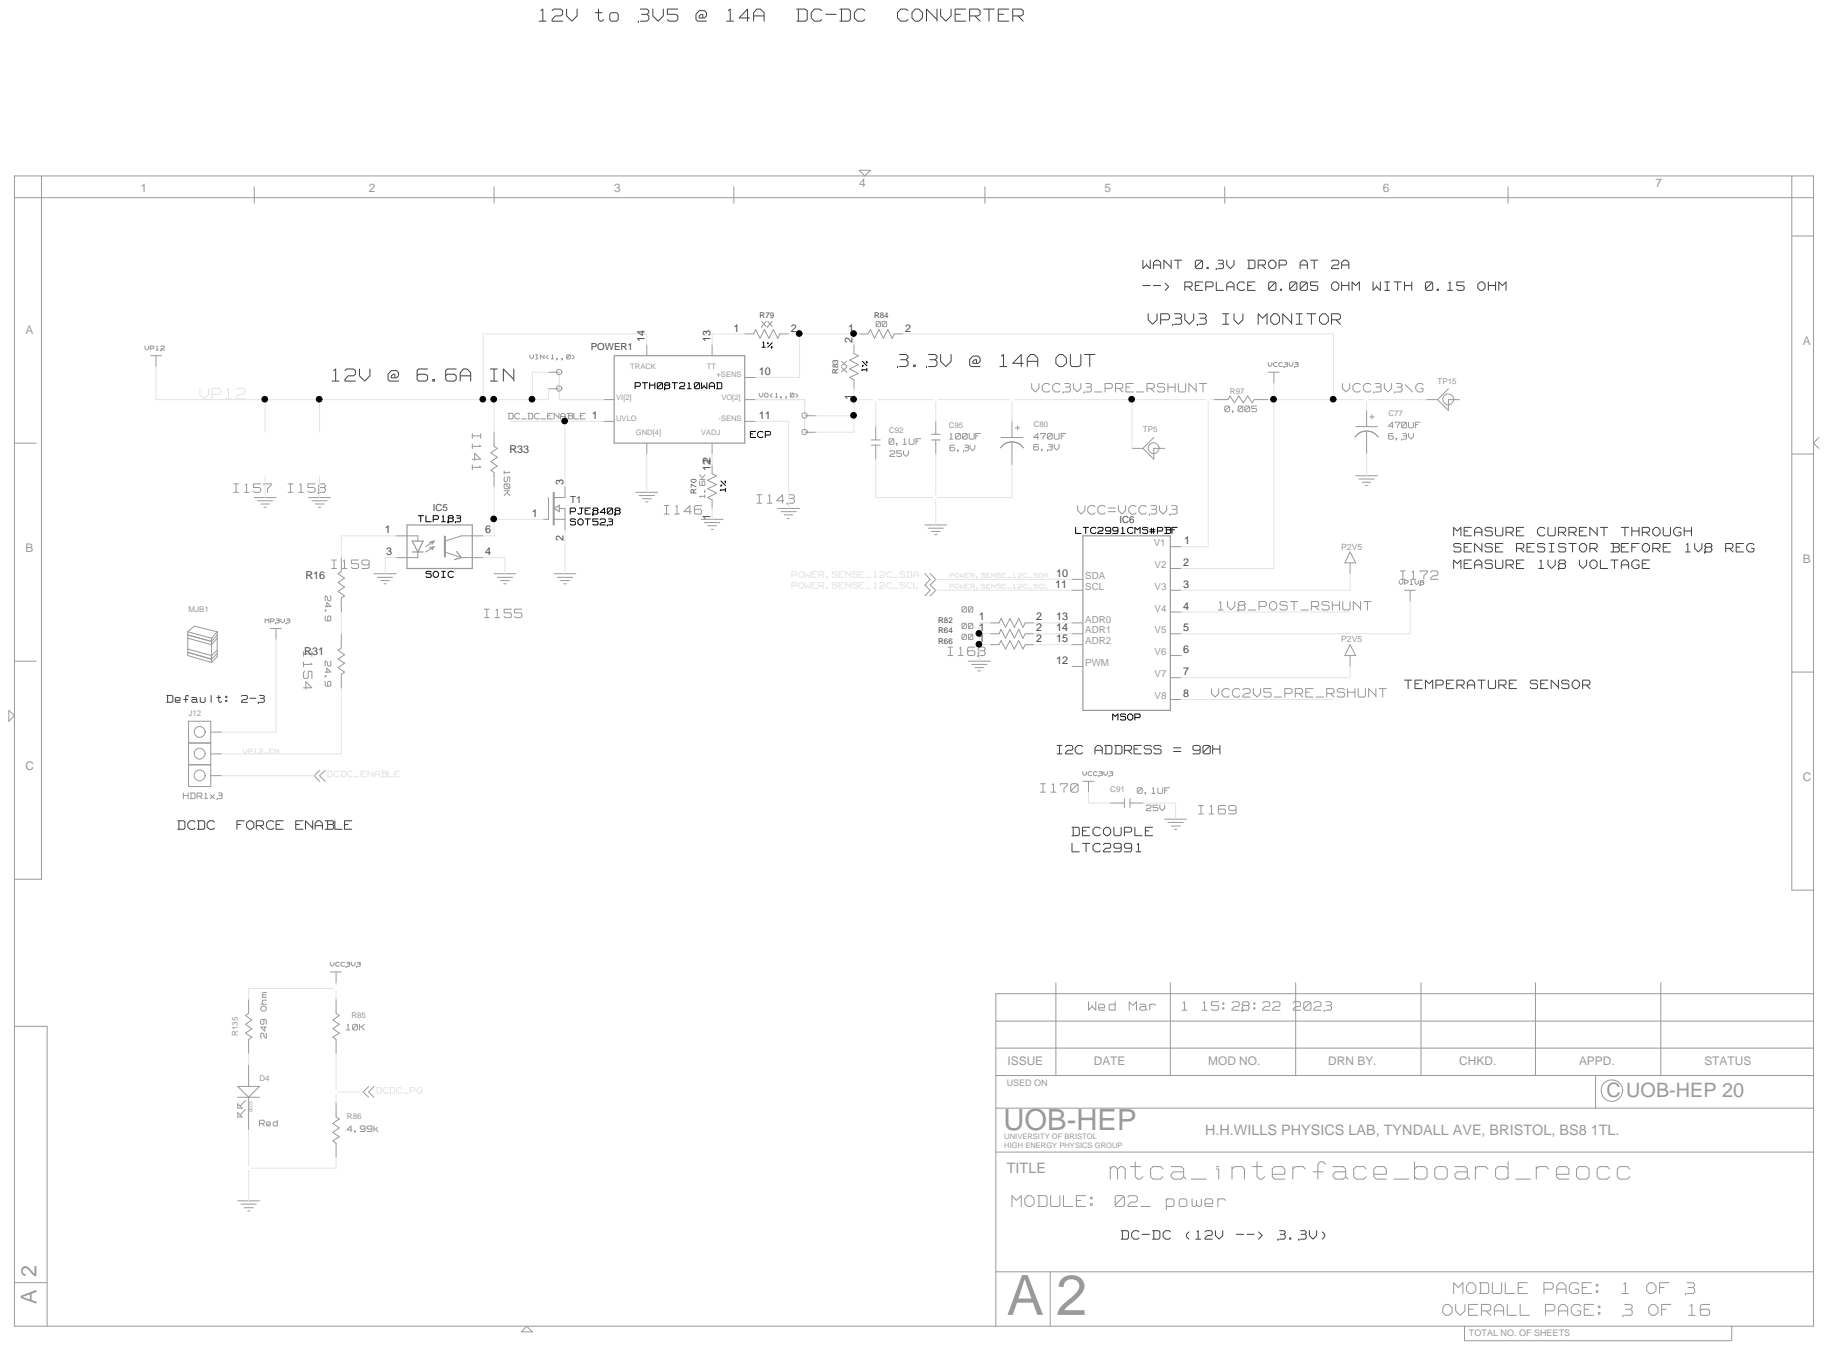
[picture p141: page 3]

ISSUE | DATE | MOD NO. | DRN BY. | CHKD. | APPD. | STATUS

USED ON | C UOB-HEP 20

H.H.WILLS PHYSICS LAB, TYNDALL AVE, BRISTOL, BS8 1TL.

UNIVERSITY OF BRISTOL
HIGH ENERGY PHYSICS GROUP
TITLE
MODULE: 02_ power

12V to 3V5 @ 14A | DC-DC CONVERTER
1 | 3 | 4 | 5 | 6 | 7

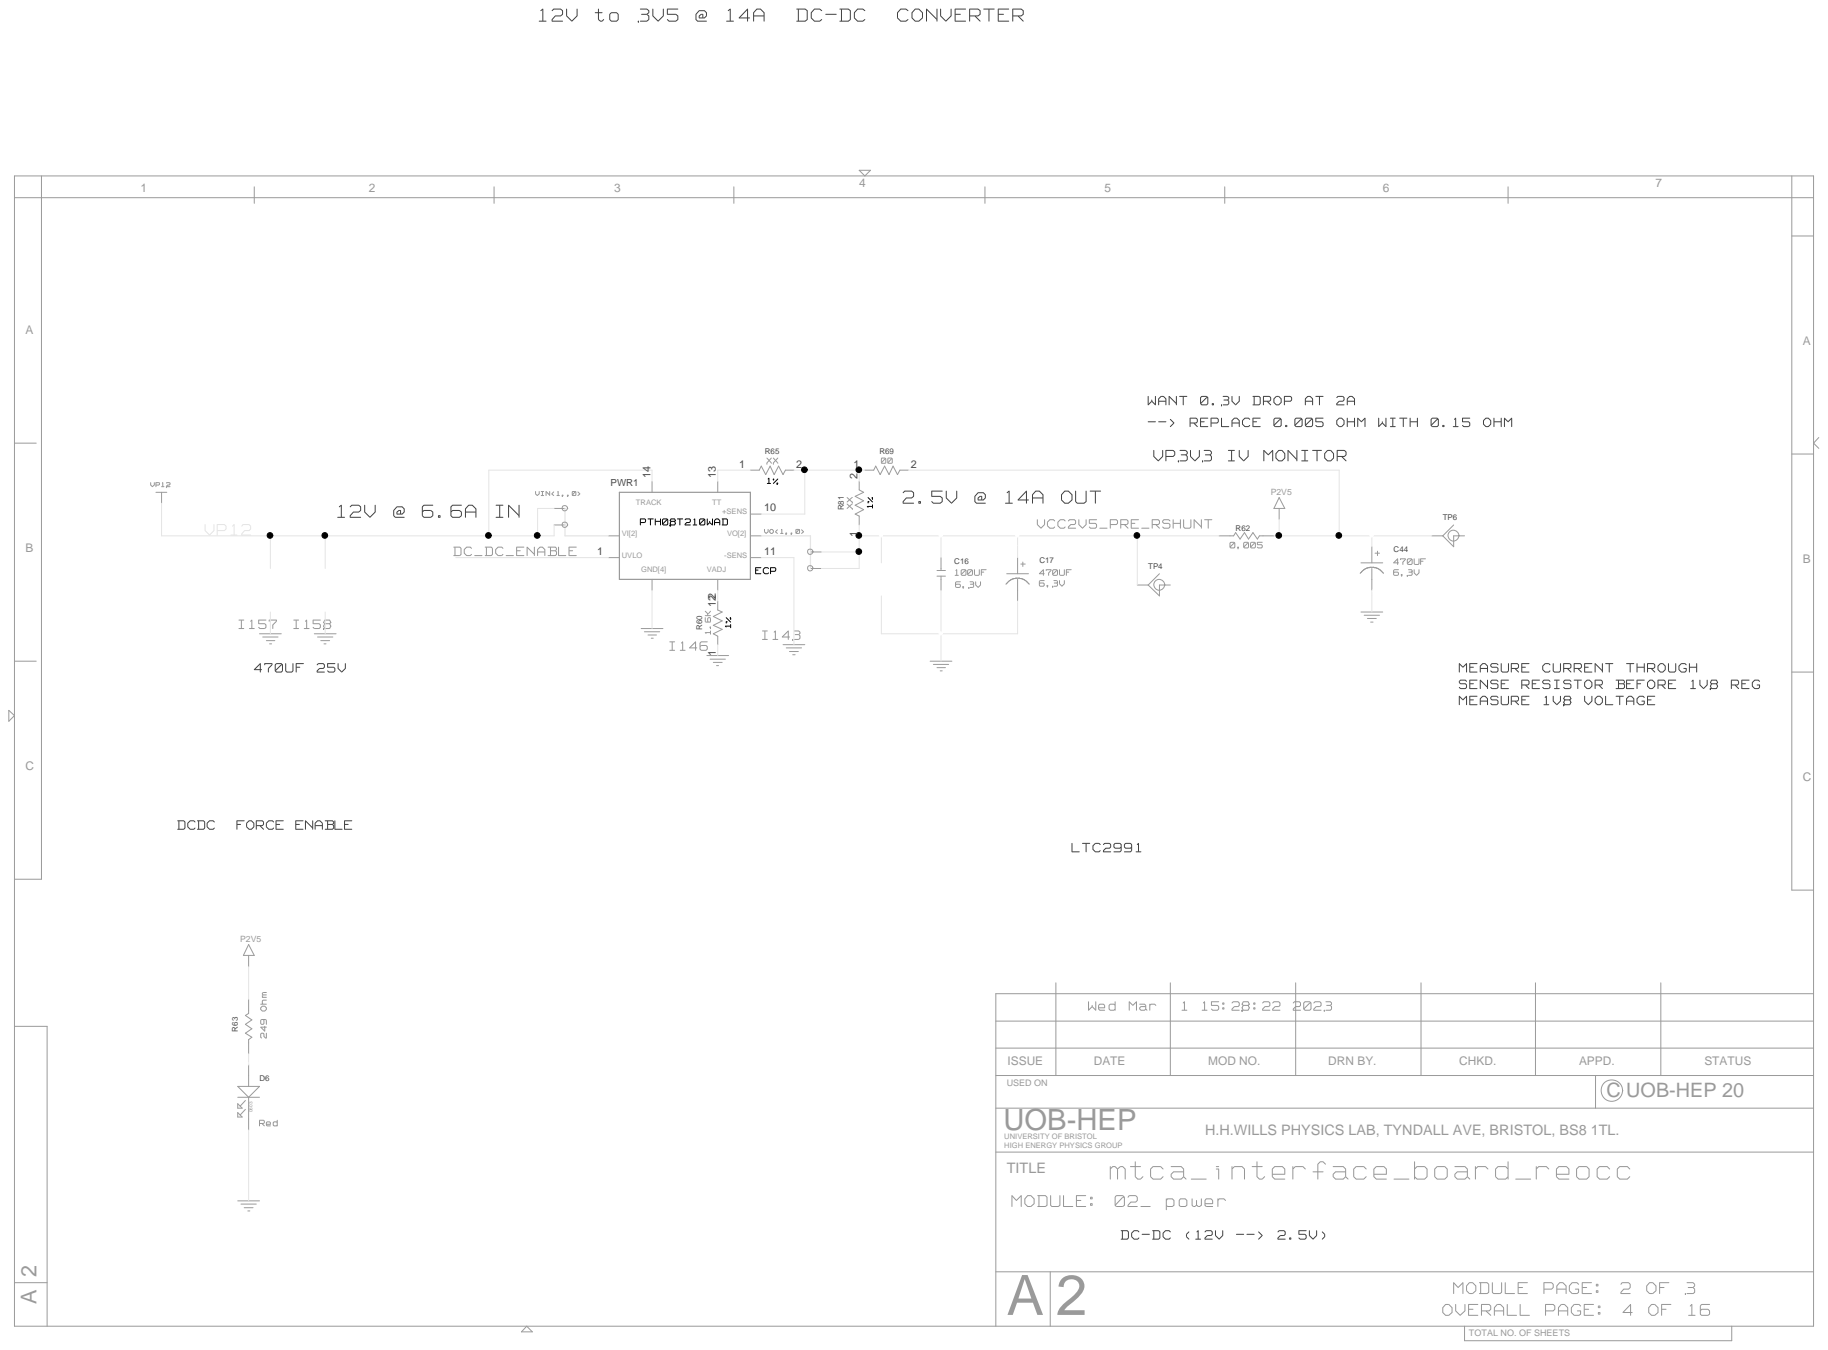
[picture p142: page 4]

ISSUE | DATE | MOD NO. | DRN BY. | CHKD. | APPD. | STATUS

USED ON | C UOB-HEP 20

H.H.WILLS PHYSICS LAB, TYNDALL AVE, BRISTOL, BS8 1TL.

UNIVERSITY OF BRISTOL
HIGH ENERGY PHYSICS GROUP
TITLE
MODULE: 02_ power

## PJE8408

1

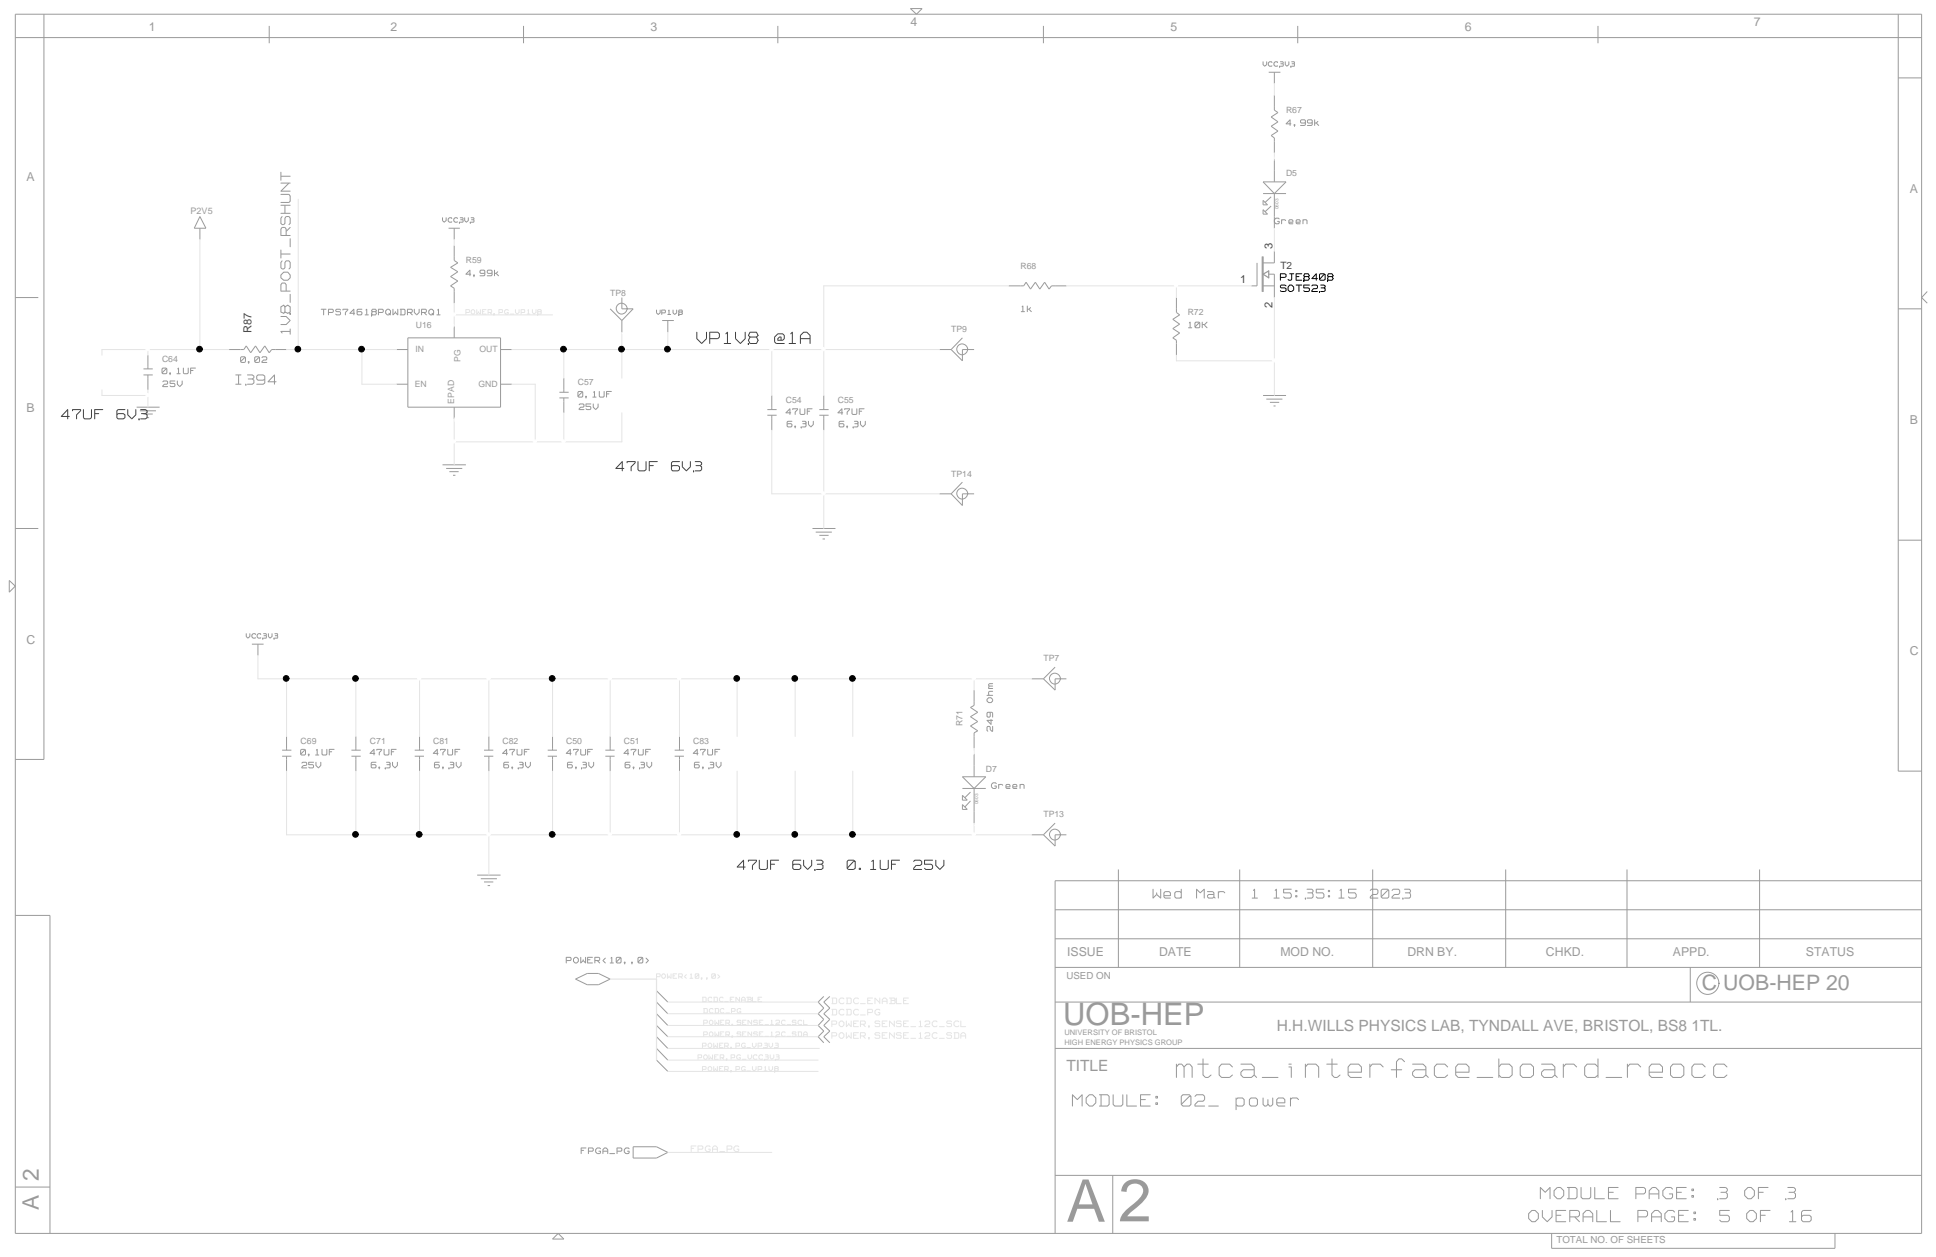
[picture p143: page 5]

ISSUE | DATE | MOD NO. | DRN BY. | CHKD. | APPD. | STATUS

USED ON | C UOB-HEP 20

H.H.WILLS PHYSICS LAB, TYNDALL AVE, BRISTOL, BS8 1TL.

UNIVERSITY OF BRISTOL
HIGH ENERGY PHYSICS GROUP
TITLE

# SFP DATA TO FPGA

## SY58608UMG

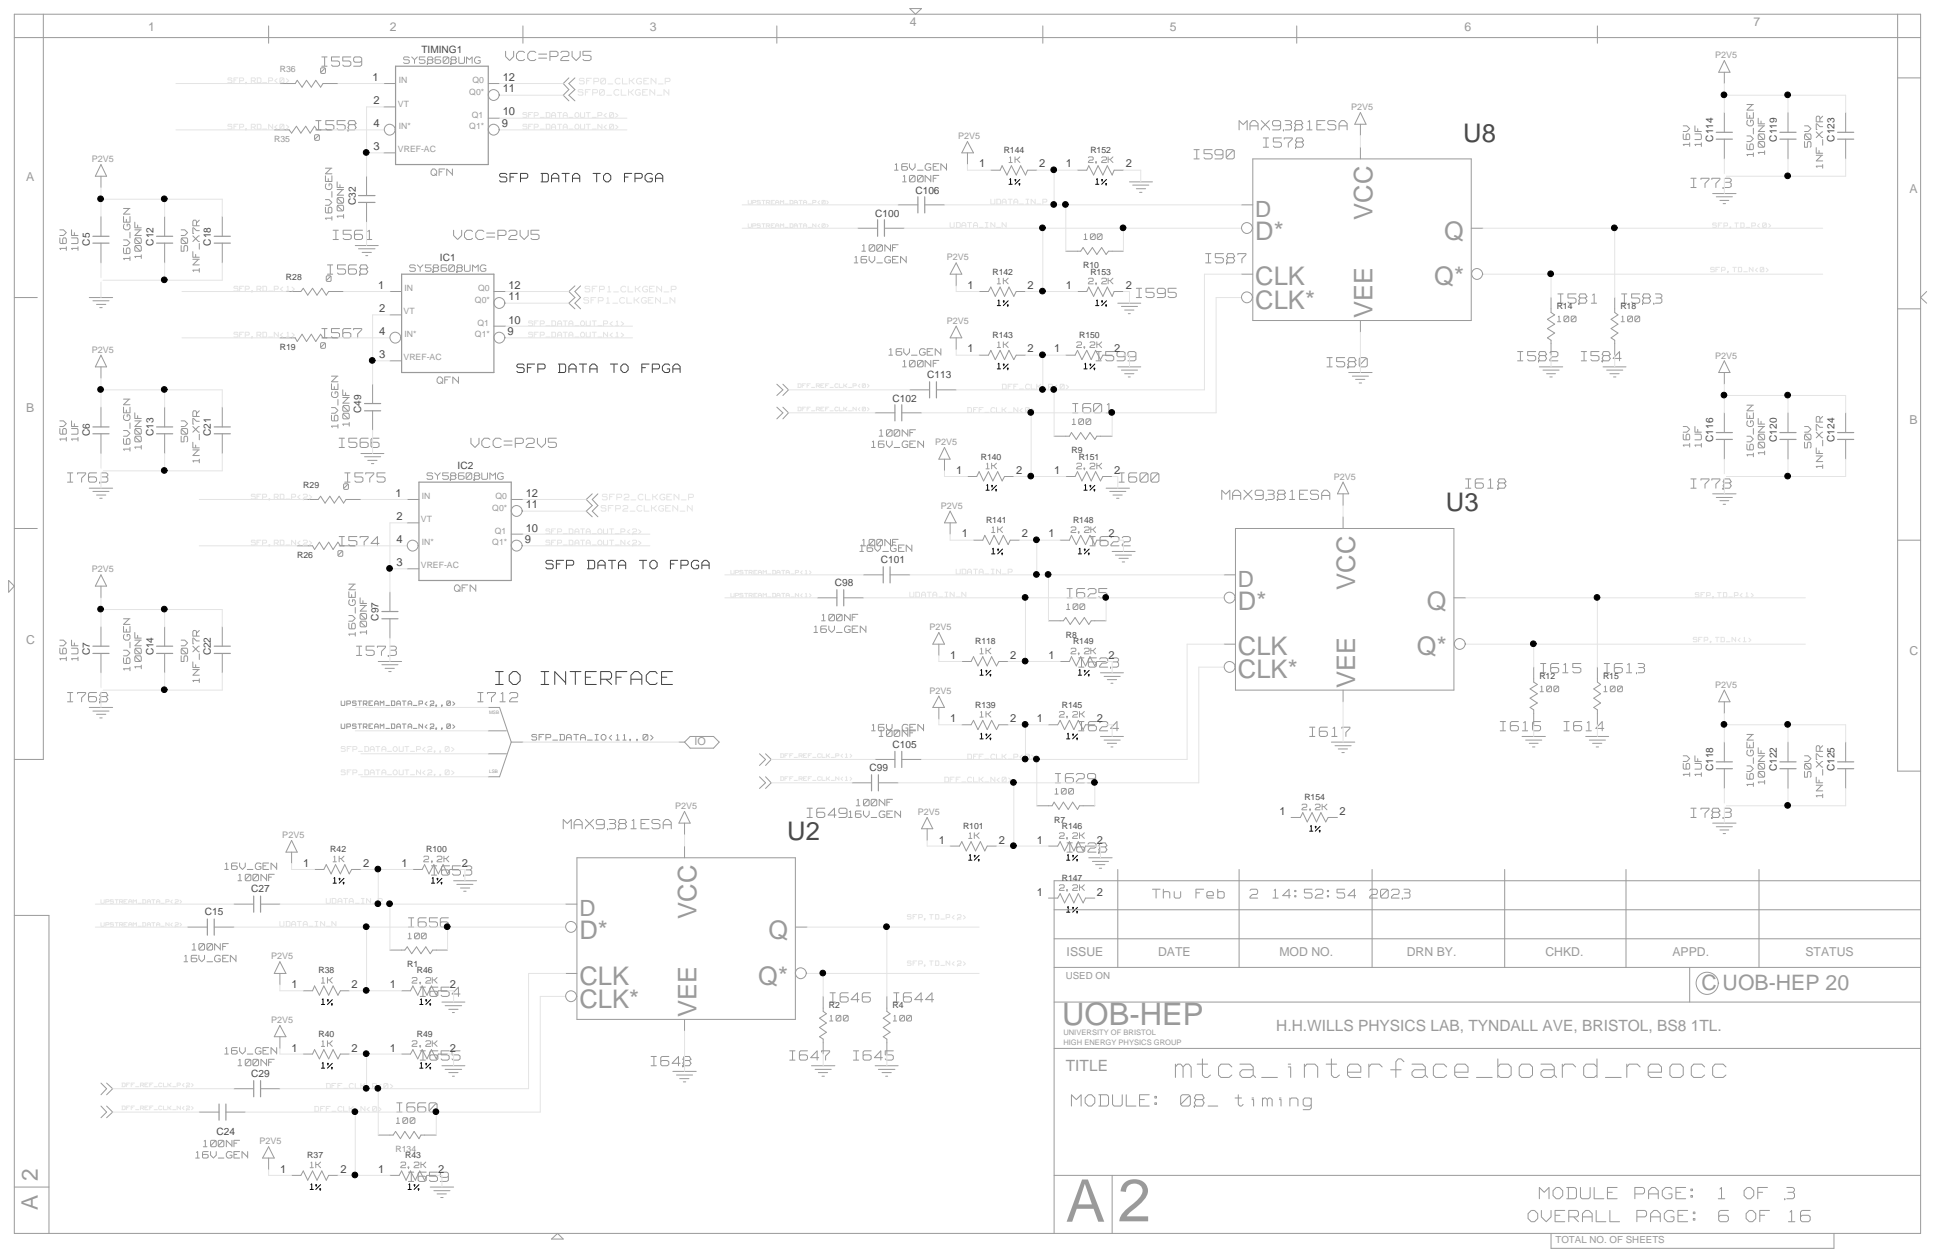
[picture p144: page 6]

ISSUE | DATE | MOD NO. | DRN BY. | CHKD. | APPD. | STATUS

USED ON | C UOB-HEP 20

H.H.WILLS PHYSICS LAB, TYNDALL AVE, BRISTOL, BS8 1TL.

UNIVERSITY OF BRISTOL
HIGH ENERGY PHYSICS GROUP
TITLE
MODULE: 08_ timing

# VDDO_CLK

I327

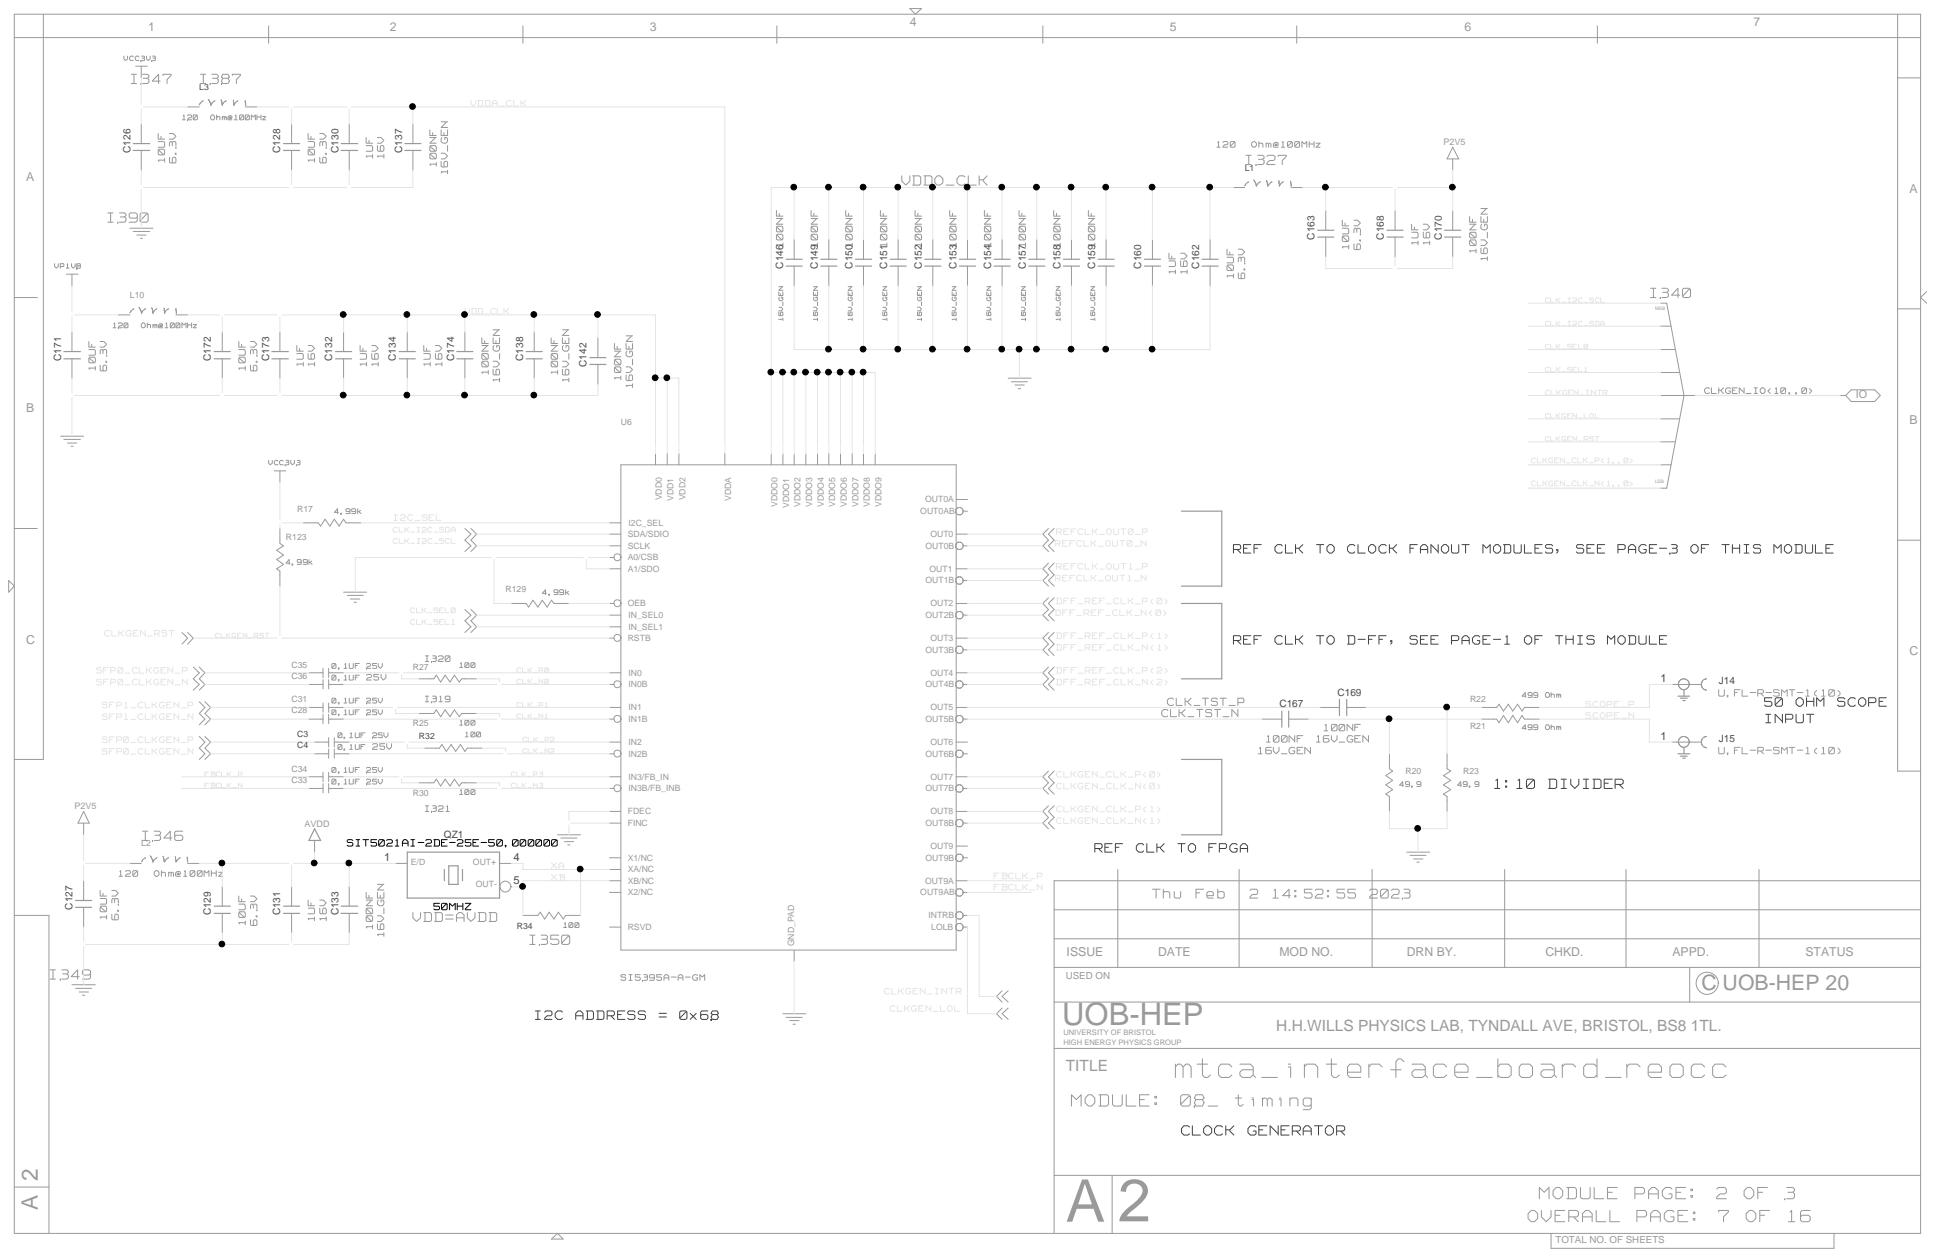
[picture p145: page 7]

REF CLK TO CLOCK FANOUT MODULES, SEE PAGE-3 OF THIS MODULE

REF CLK TO D-FF, SEE PAGE-1 OF THIS MODULE

ISSUE | DATE | MOD NO. | DRN BY. | CHKD. | APPD. | STATUS

USED ON | C UOB-HEP 20

H.H.WILLS PHYSICS LAB, TYNDALL AVE, BRISTOL, BS8 1TL.

UNIVERSITY OF BRISTOL
HIGH ENERGY PHYSICS GROUP
TITLE
MODULE: 08_ timing

## 16V_GEN

# I176 I175 I173

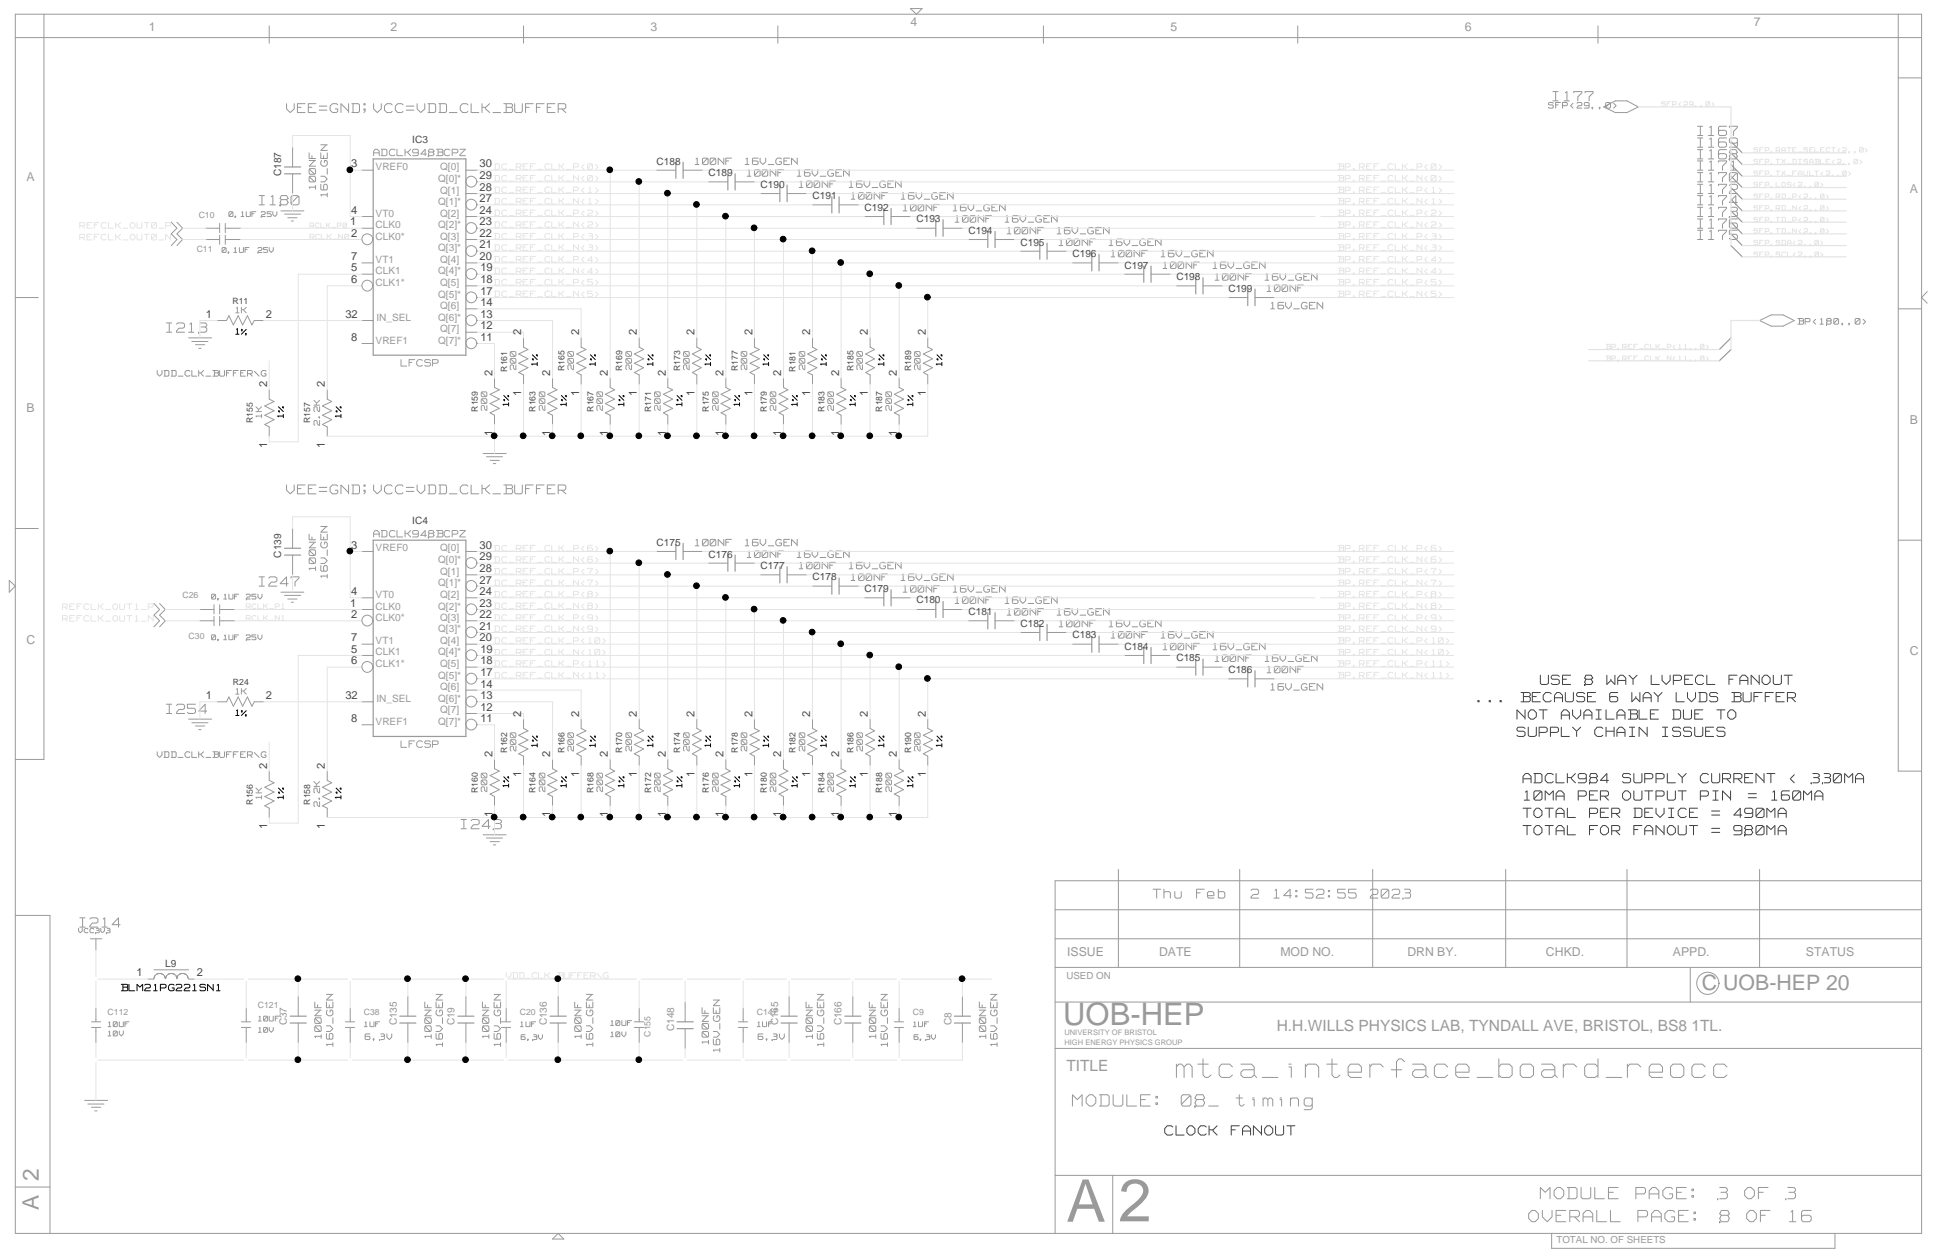
[picture p146: page 8]

USE 8 WAY LVPECL FANOUT
NOT AVAILABLE DUE TO
SUPPLY CHAIN ISSUES

... BECAUSE 6 WAY LVDS BUFFER

ISSUE | DATE | MOD NO. | DRN BY. | CHKD. | APPD. | STATUS

USED ON | C UOB-HEP 20

H.H.WILLS PHYSICS LAB, TYNDALL AVE, BRISTOL, BS8 1TL.

UNIVERSITY OF BRISTOL
HIGH ENERGY PHYSICS GROUP
TITLE
MODULE: 08_ timing

A
A

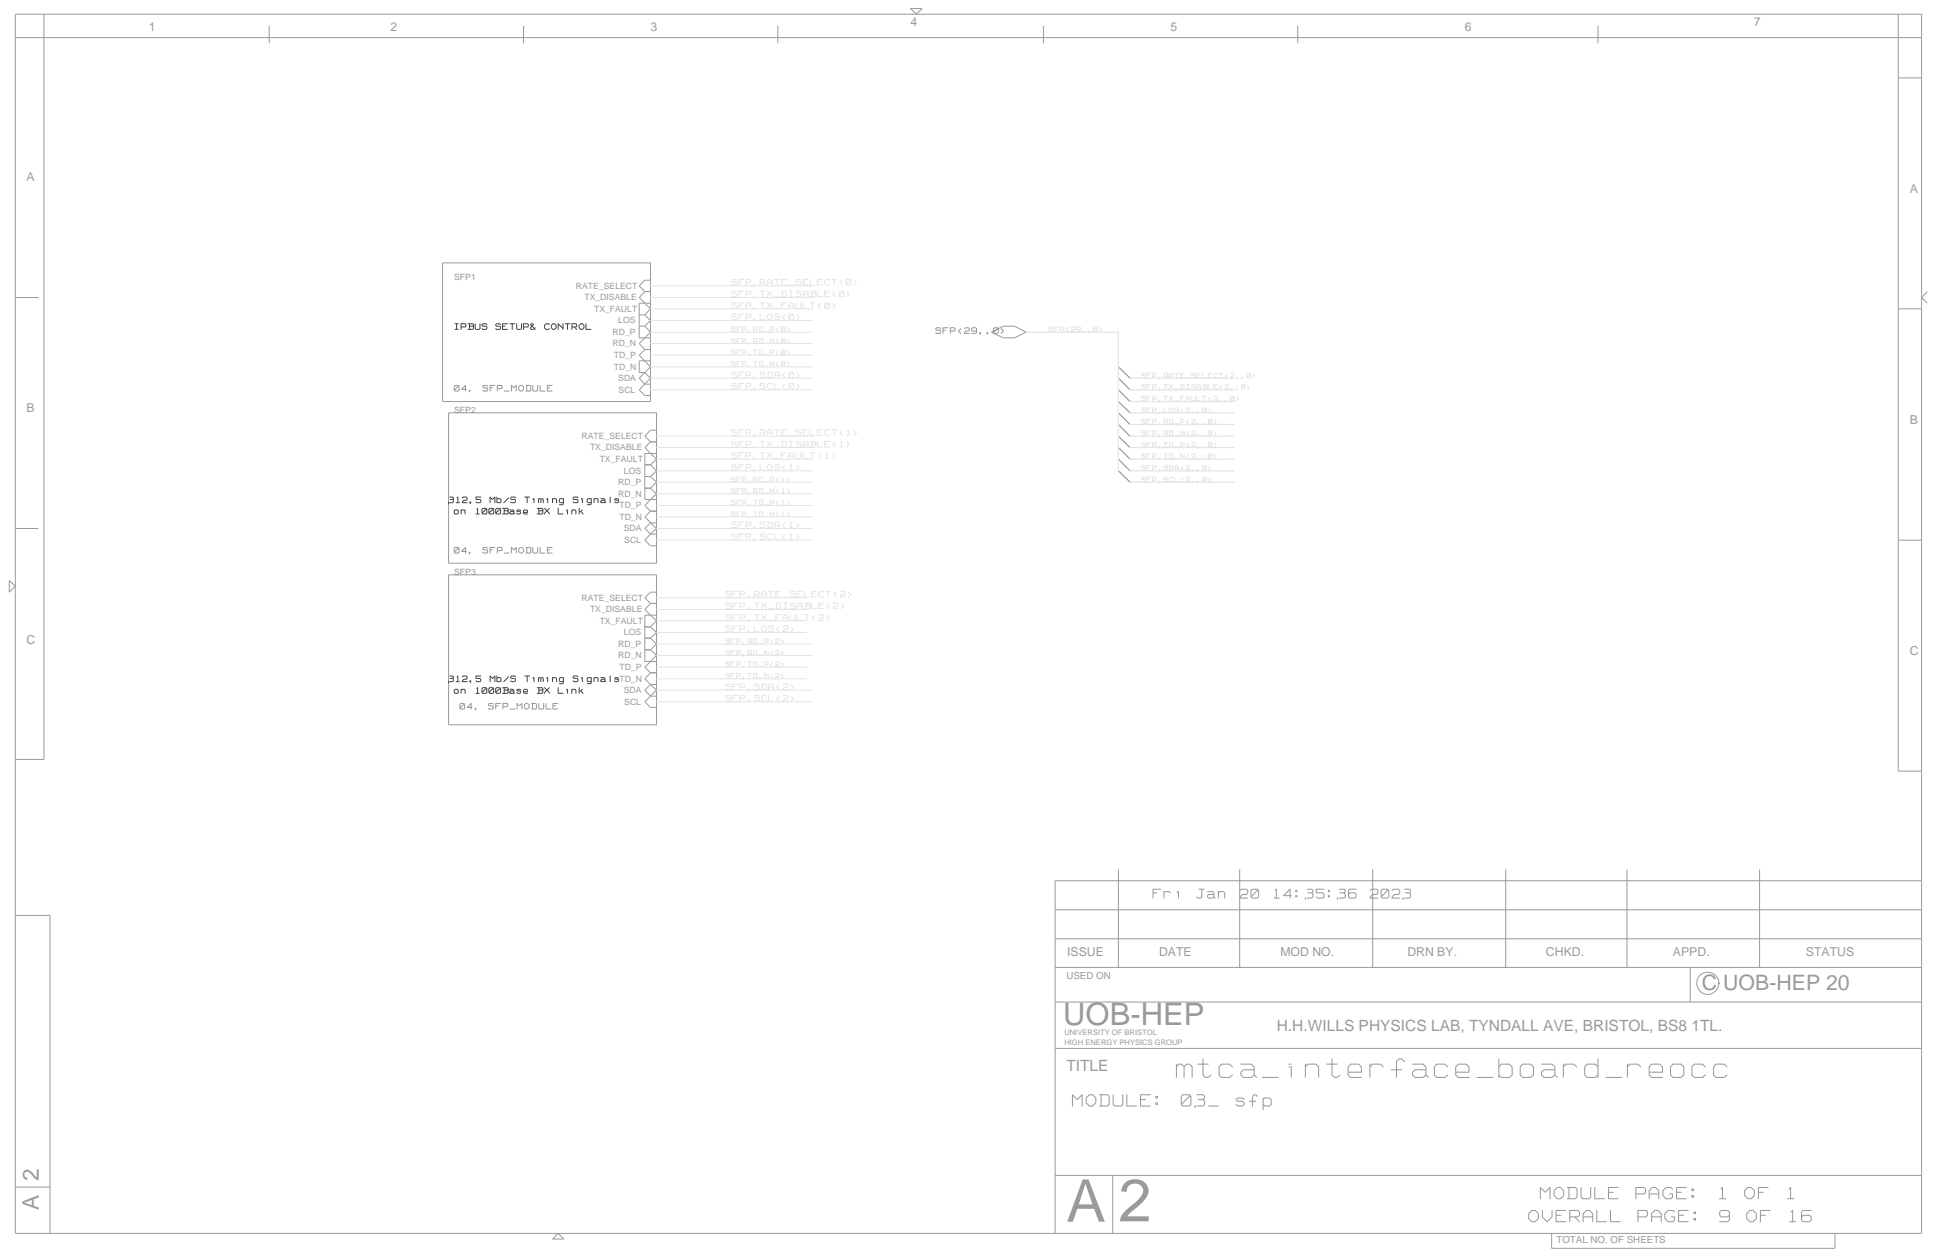
[picture p147: page 9]
Fri Jan 20 14:35:36 2023; OVERALL PAGE: 9; mtca_interface_board_reocc; MODULE:; 03_ sfp; SFP<29..0>; SFP.TD_P<2>; SFP.RD_N<2>; SFP.RD_P<2>; SFP.LOS<2>; SFP.TX_FAULT<2>; 04. SFP_MODULE; SFP.TD_N<0>; SFP.TD_P<0>; SFP.RD_P<0> SFP.RD_N<0>; SFP.RATE_SELECT<0>; SFP.SCL<0>; SFP.SDA<0>; SFP.TX_DISABLE<0>; SFP.LOS<0>; SFP.TX_FAULT<0>; SFP.SCL<2>; SFP.SDA<2>; SFP.TD_N<2>; SFP.TX_DISABLE<2>; SFP.RATE_SELECT<2>; SFP.SCL<1>; SFP.SDA<1>; SFP.TD_N<1>; SFP.TD_P<1>; SFP.RD_N<1>; SFP.RD_P<1>; SFP.LOS<1>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

IPBUS SETUP& CONTROL

312.5 Mb/S Timing Signals
on 1000Base BX Link

04. SFP_MODULE

ISSUE | DATE | MOD NO. | DRN BY. | CHKD. | APPD. | STATUS

USED ON | C UOB-HEP 20

H.H.WILLS PHYSICS LAB, TYNDALL AVE, BRISTOL, BS8 1TL.

UNIVERSITY OF BRISTOL
HIGH ENERGY PHYSICS GROUP
TITLE

MODULE PAGE: 1 OF 1

A
A

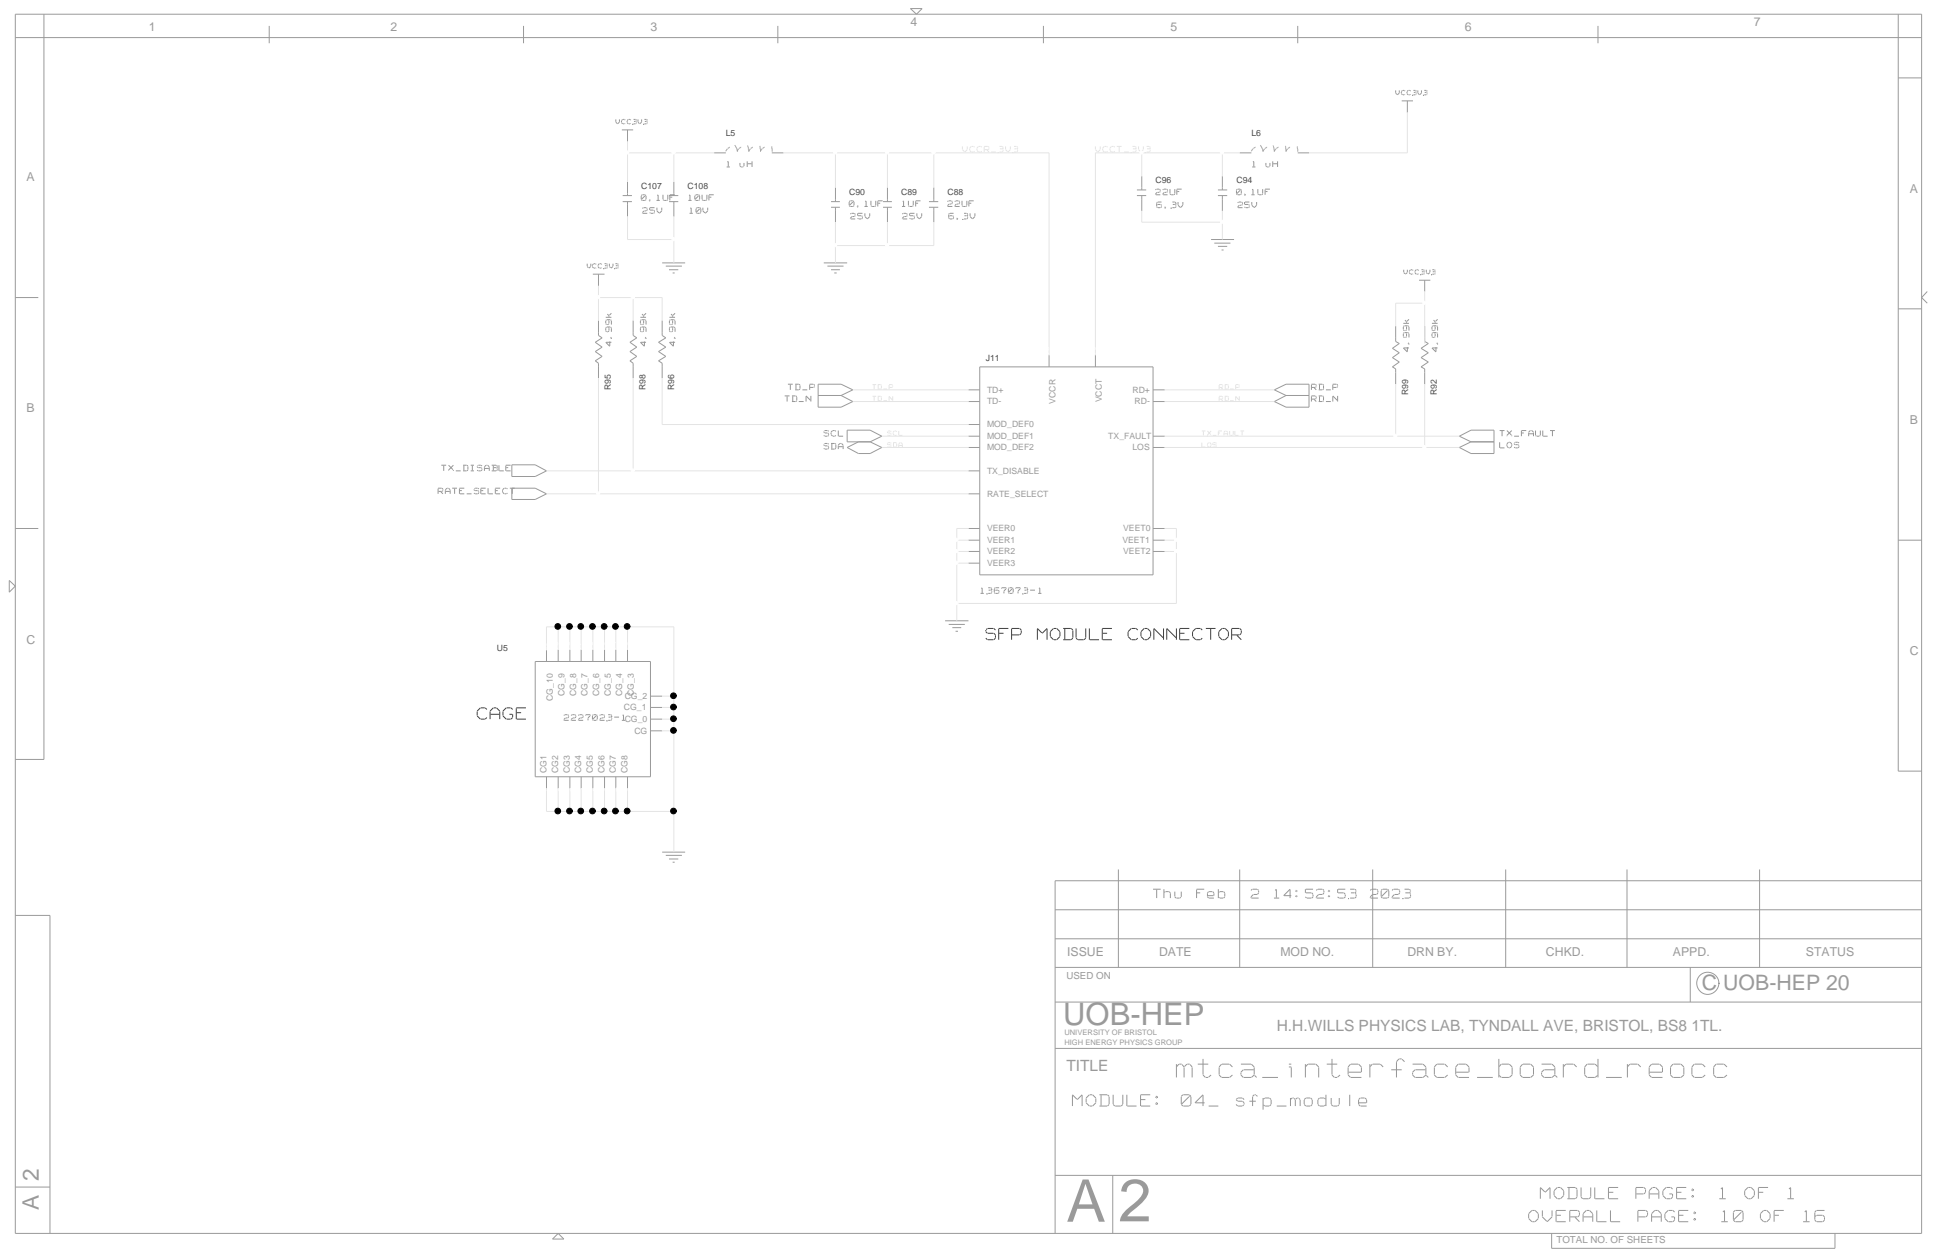
[picture p148: page 10]

VCC3V3

ISSUE | DATE | MOD NO. | DRN BY. | CHKD. | APPD. | STATUS

USED ON | C UOB-HEP 20

H.H.WILLS PHYSICS LAB, TYNDALL AVE, BRISTOL, BS8 1TL.

UNIVERSITY OF BRISTOL
HIGH ENERGY PHYSICS GROUP
TITLE

A
A

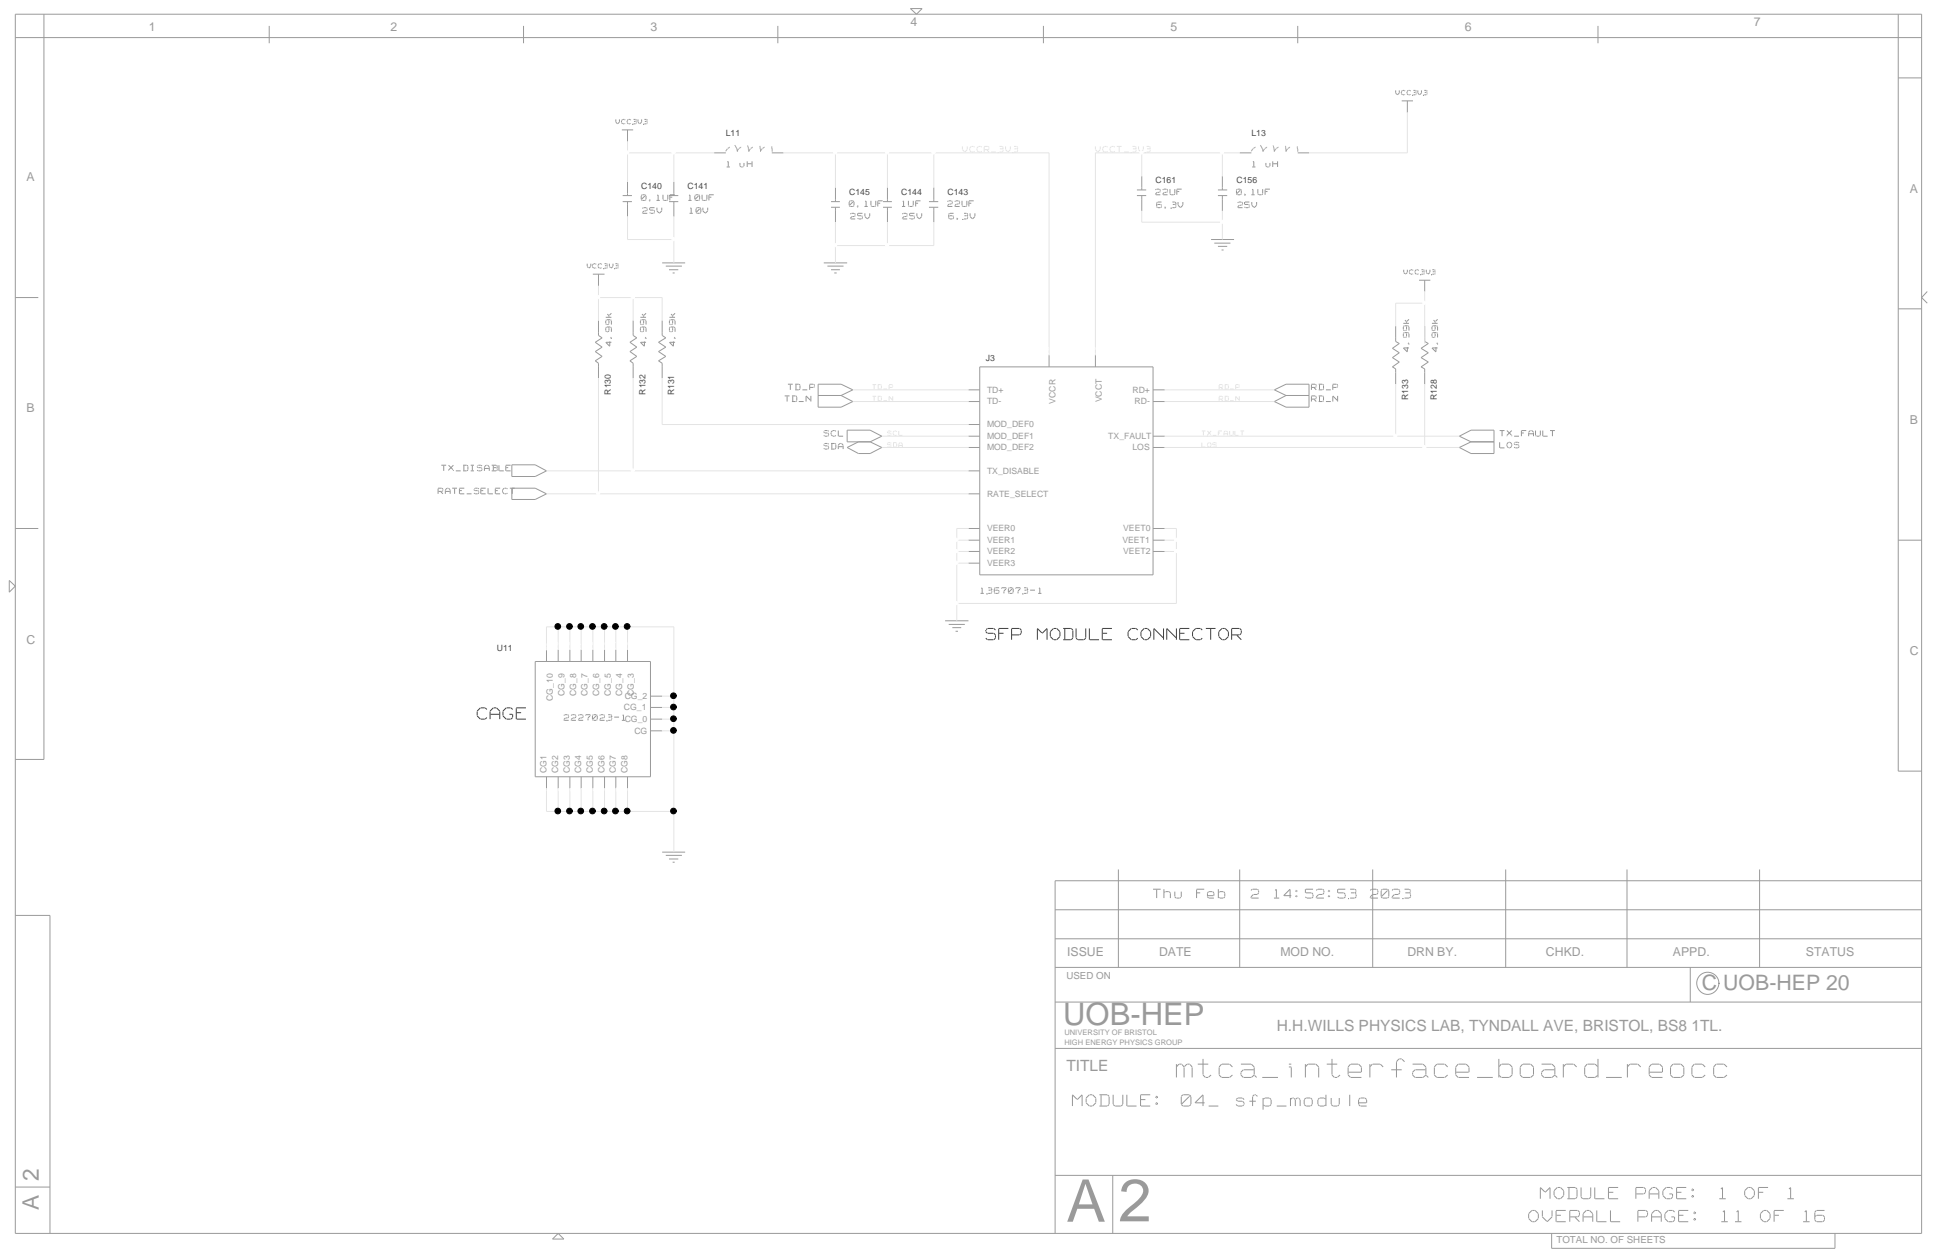
[picture p149: page 11]

VCC3V3

ISSUE | DATE | MOD NO. | DRN BY. | CHKD. | APPD. | STATUS

USED ON | C UOB-HEP 20

H.H.WILLS PHYSICS LAB, TYNDALL AVE, BRISTOL, BS8 1TL.

UNIVERSITY OF BRISTOL
HIGH ENERGY PHYSICS GROUP
TITLE

A
A

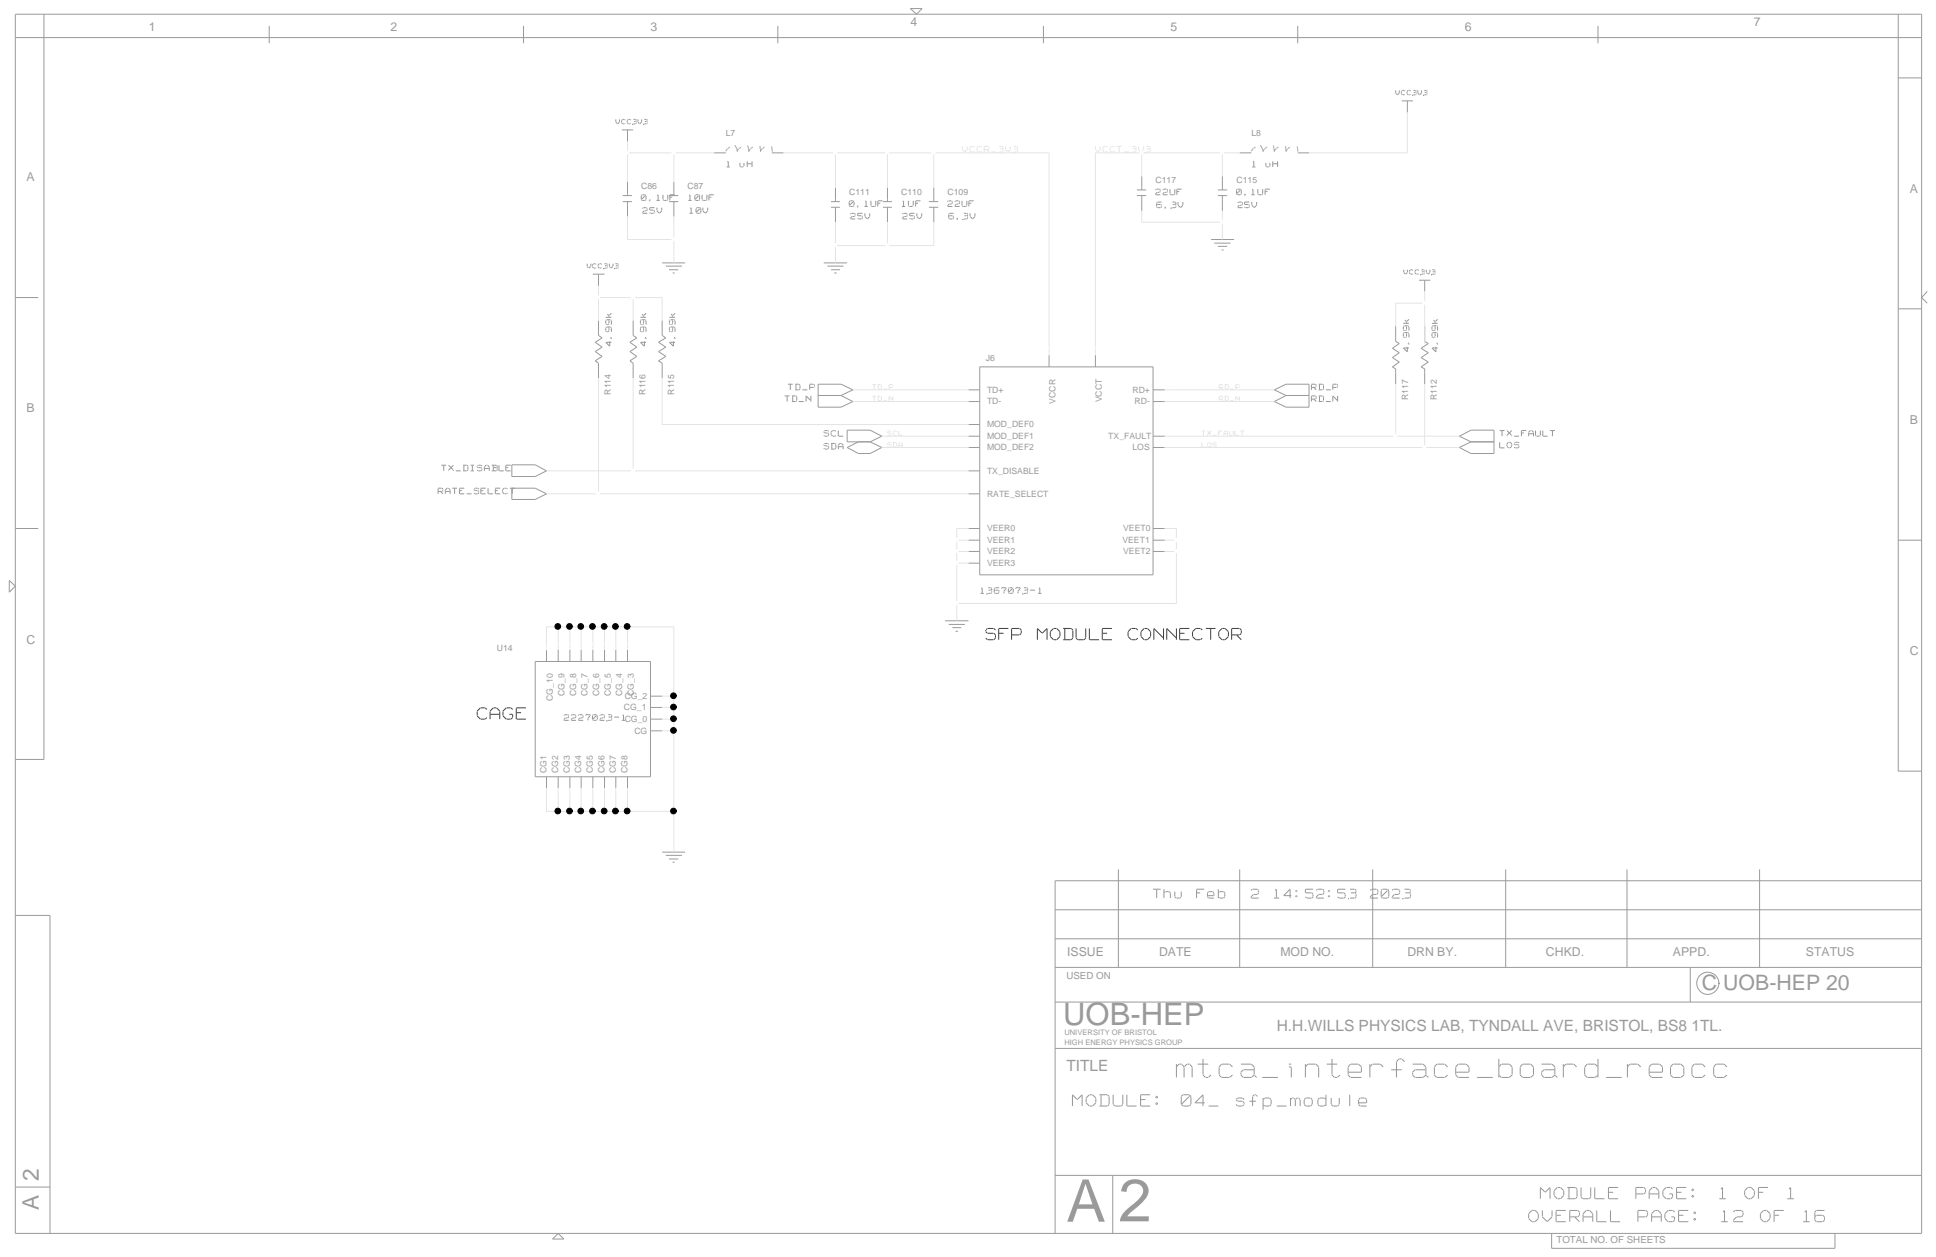
[picture p150: page 12]

VCC3V3

ISSUE | DATE | MOD NO. | DRN BY. | CHKD. | APPD. | STATUS

USED ON | C UOB-HEP 20

H.H.WILLS PHYSICS LAB, TYNDALL AVE, BRISTOL, BS8 1TL.

UNIVERSITY OF BRISTOL
HIGH ENERGY PHYSICS GROUP
TITLE

# AUX IO INTERFACE

JTAG CONNECTOR | EEPROM

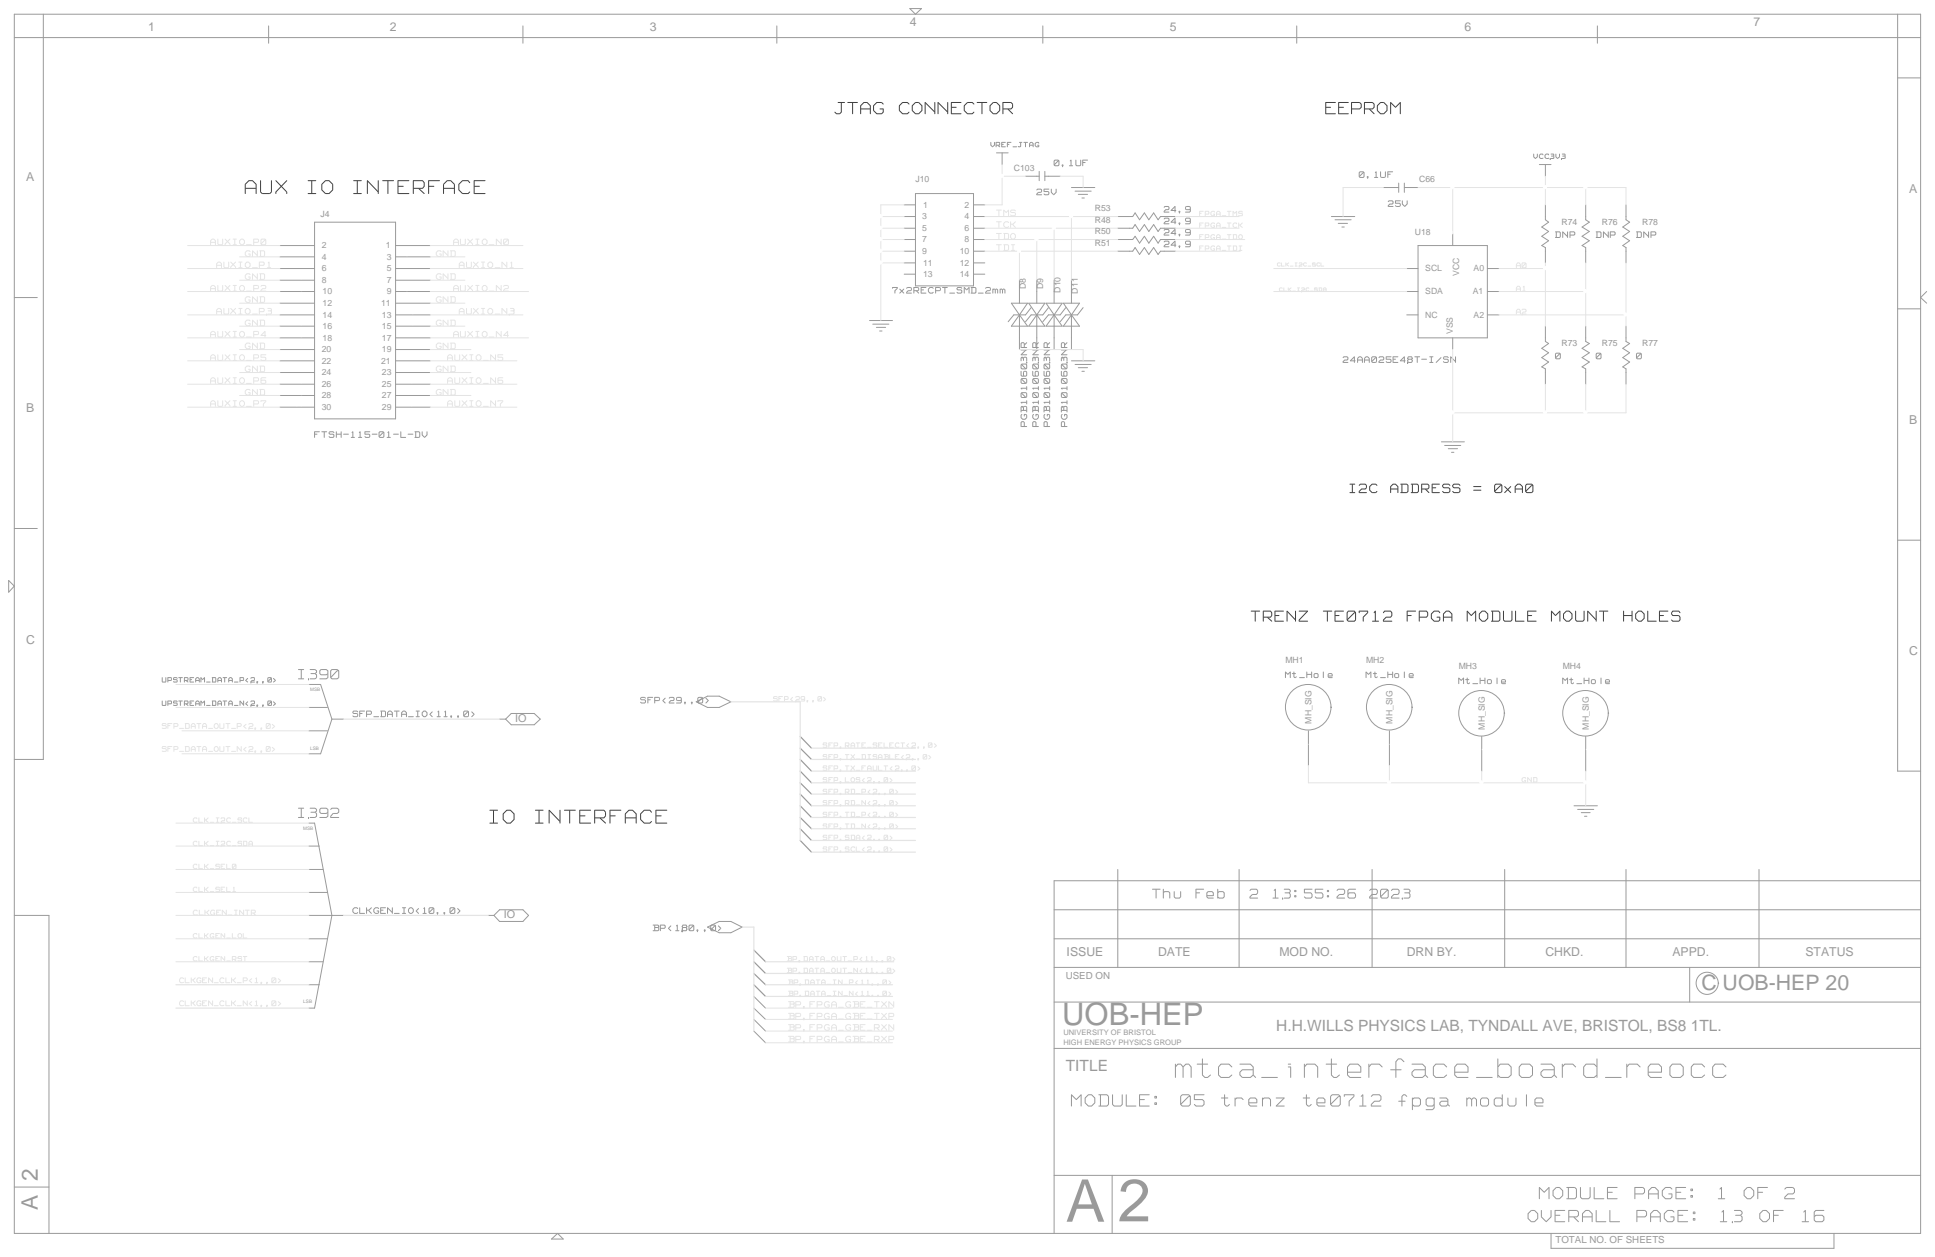
[picture p151: page 13]

TRENZ TE0712 FPGA MODULE MOUNT HOLES

ISSUE | DATE | MOD NO. | DRN BY. | CHKD. | APPD. | STATUS

USED ON | C UOB-HEP 20

H.H.WILLS PHYSICS LAB, TYNDALL AVE, BRISTOL, BS8 1TL.

UNIVERSITY OF BRISTOL
HIGH ENERGY PHYSICS GROUP
TITLE
MODULE: 05 trenz te0712 fpga module

1.0MM

1.0MM

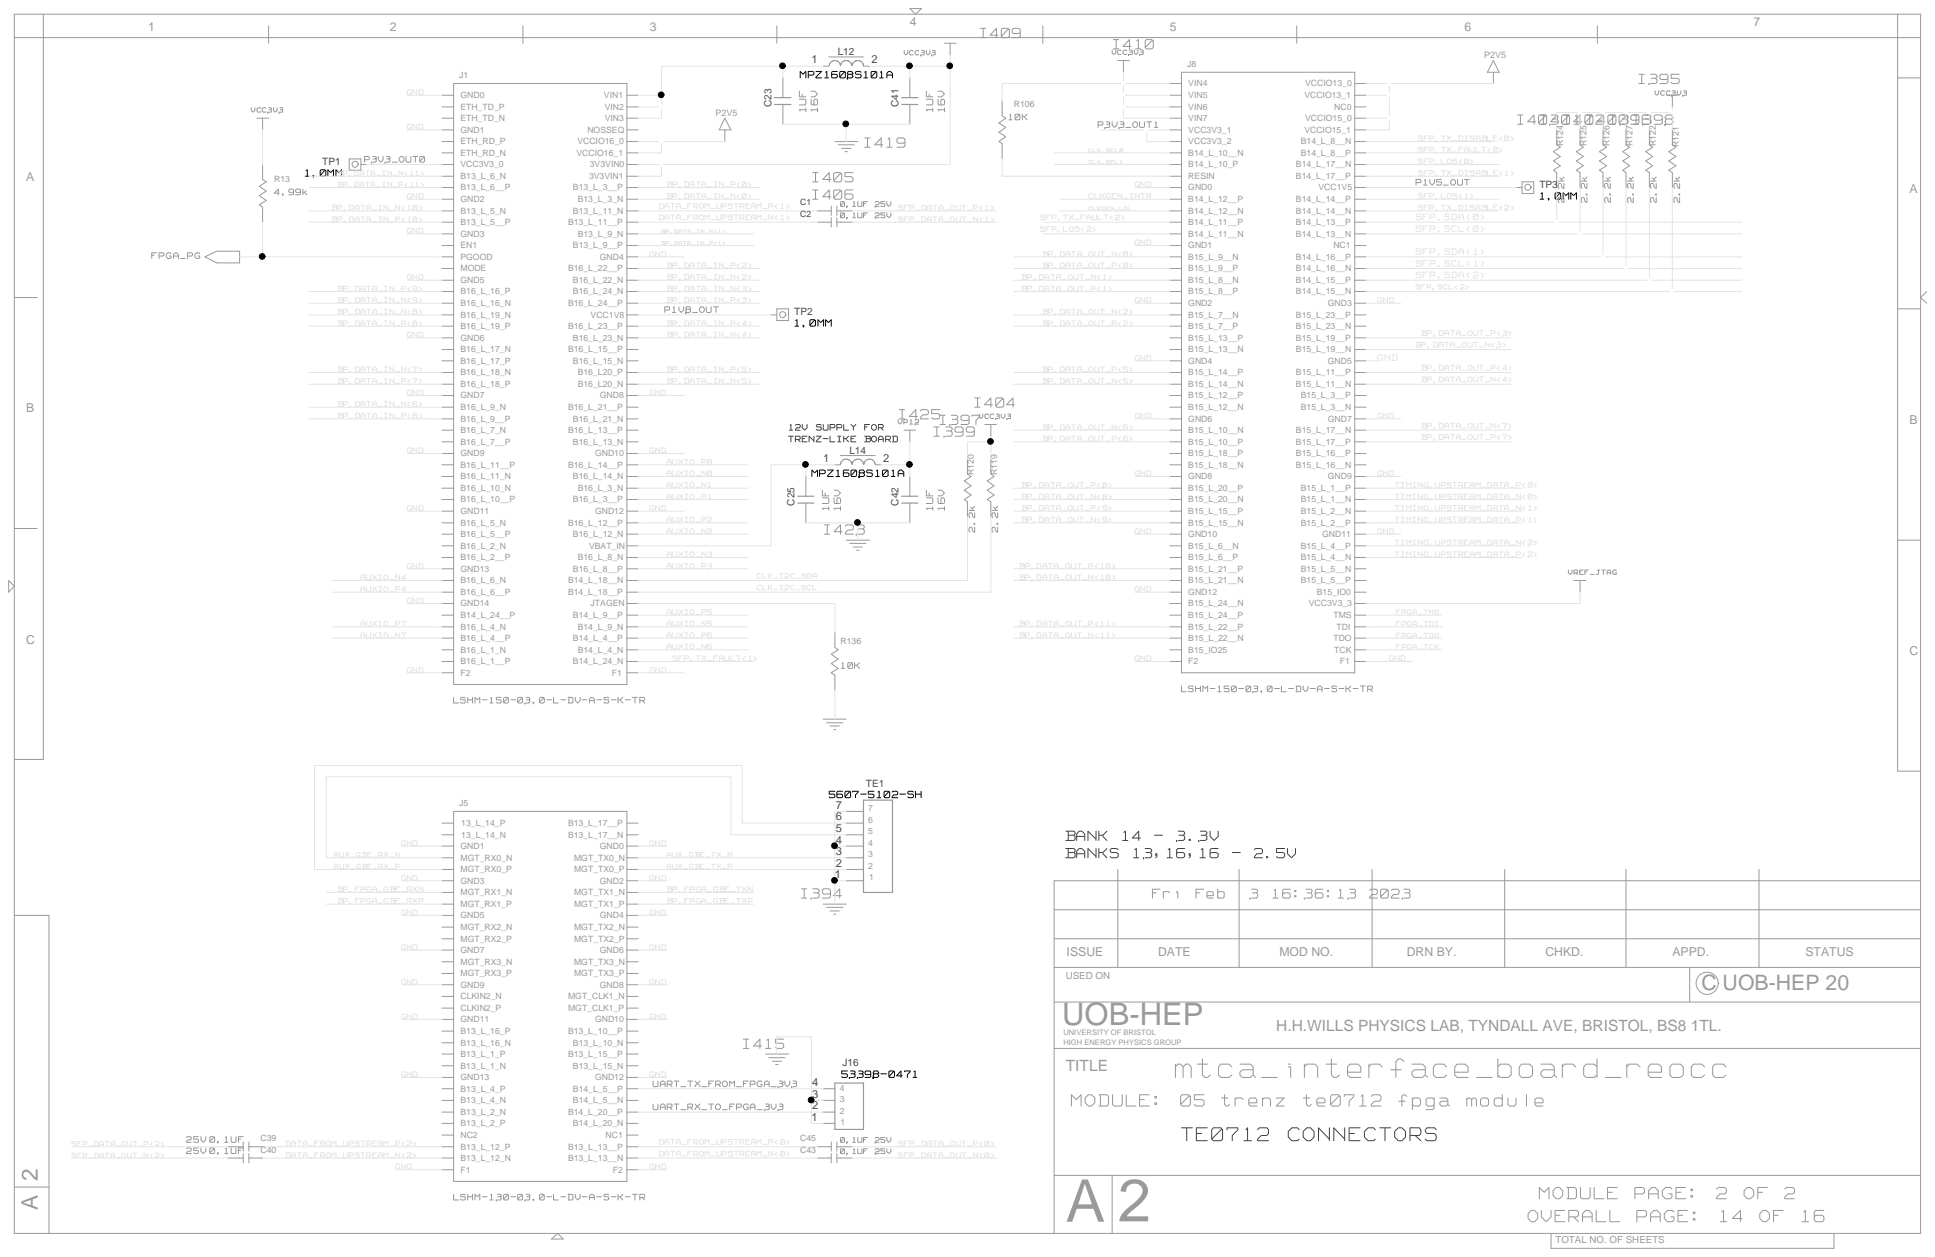
[picture p152: page 14]

ISSUE | DATE | MOD NO. | DRN BY. | CHKD. | APPD. | STATUS

USED ON | C UOB-HEP 20

H.H.WILLS PHYSICS LAB, TYNDALL AVE, BRISTOL, BS8 1TL.

UNIVERSITY OF BRISTOL
HIGH ENERGY PHYSICS GROUP
TITLE
MODULE: 05 trenz te0712 fpga module

# TONGUE 2 MEZZENINE CONNECTOR

1 | 3

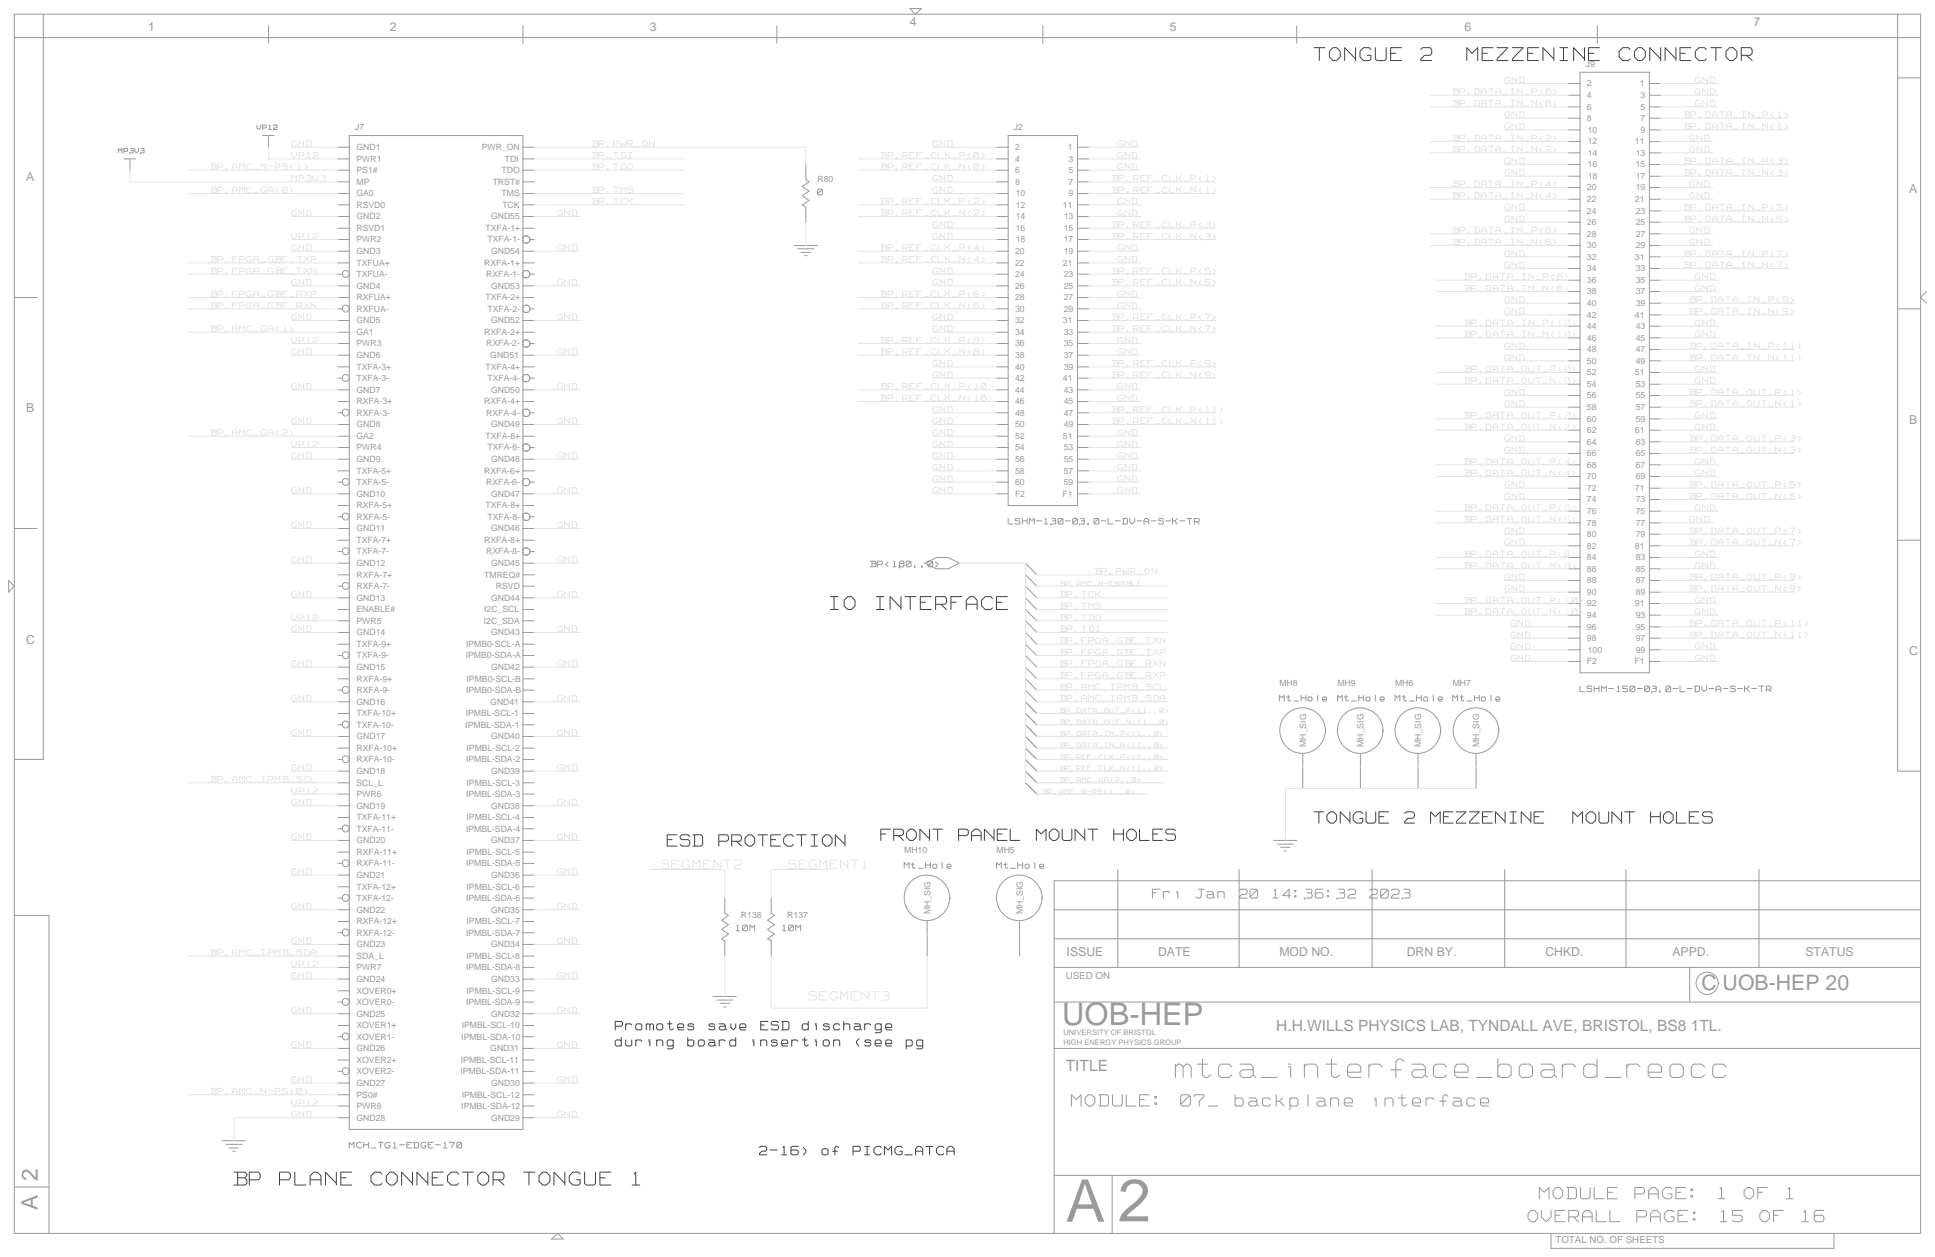
[picture p153: page 15]
2-16) of PICMG_ATCA; IO INTERFACE; TONGUE 2 MEZZENINE; MOUNT HOLES; ESD PROTECTION; Fri Jan 20 14:36:32 2023; mtca_interface_board_reocc; SEGMENT3; SEGMENT2; SEGMENT1; Mt_Hole; BP.AMC_GA<2..0> BP.AMC_N-PS<1..0>; BP.REF_CLK_N<11..0>; BP.REF_CLK_P<11..0>; BP.DATA_IN_N<11..0>; BP.DATA_IN_P<11..0>; BP.DATA_OUT_N<11..0>; BP.AMC_IPMB_SDA; BP.AMC_IPMB_SCL; BP.FPGA_GBE_RXN BP.FPGA_GBE_RXP; BP.FPGA_GBE_TXP; BP.FPGA_GBE_TXN; BP.TDI; BP.TMS BP.TDO; BP.TCK; BP.AMC_N-ENABLE; BP.PWR_ON; BP.DATA_OUT_P<11..0>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

LSHM-130-03.0-L-DV-A-S-K-TR

LSHM-150-03.0-L-DV-A-S-K-TR

FRONT PANEL MOUNT HOLES

ISSUE | DATE | MOD NO. | DRN BY. | CHKD. | APPD. | STATUS

USED ON | C UOB-HEP 20

Promotes save ESD discharge
during board insertion (see pg

H.H.WILLS PHYSICS LAB, TYNDALL AVE, BRISTOL, BS8 1TL.

UNIVERSITY OF BRISTOL
HIGH ENERGY PHYSICS GROUP
TITLE
MODULE: 07_ backplane interface

BP PLANE CONNECTOR TONGUE 1

MODULE PAGE: 1 OF 1
OVERALL PAGE: 15 OF 16

# IO INTERFACE

# MODULE MANAGEMENT CONTROL

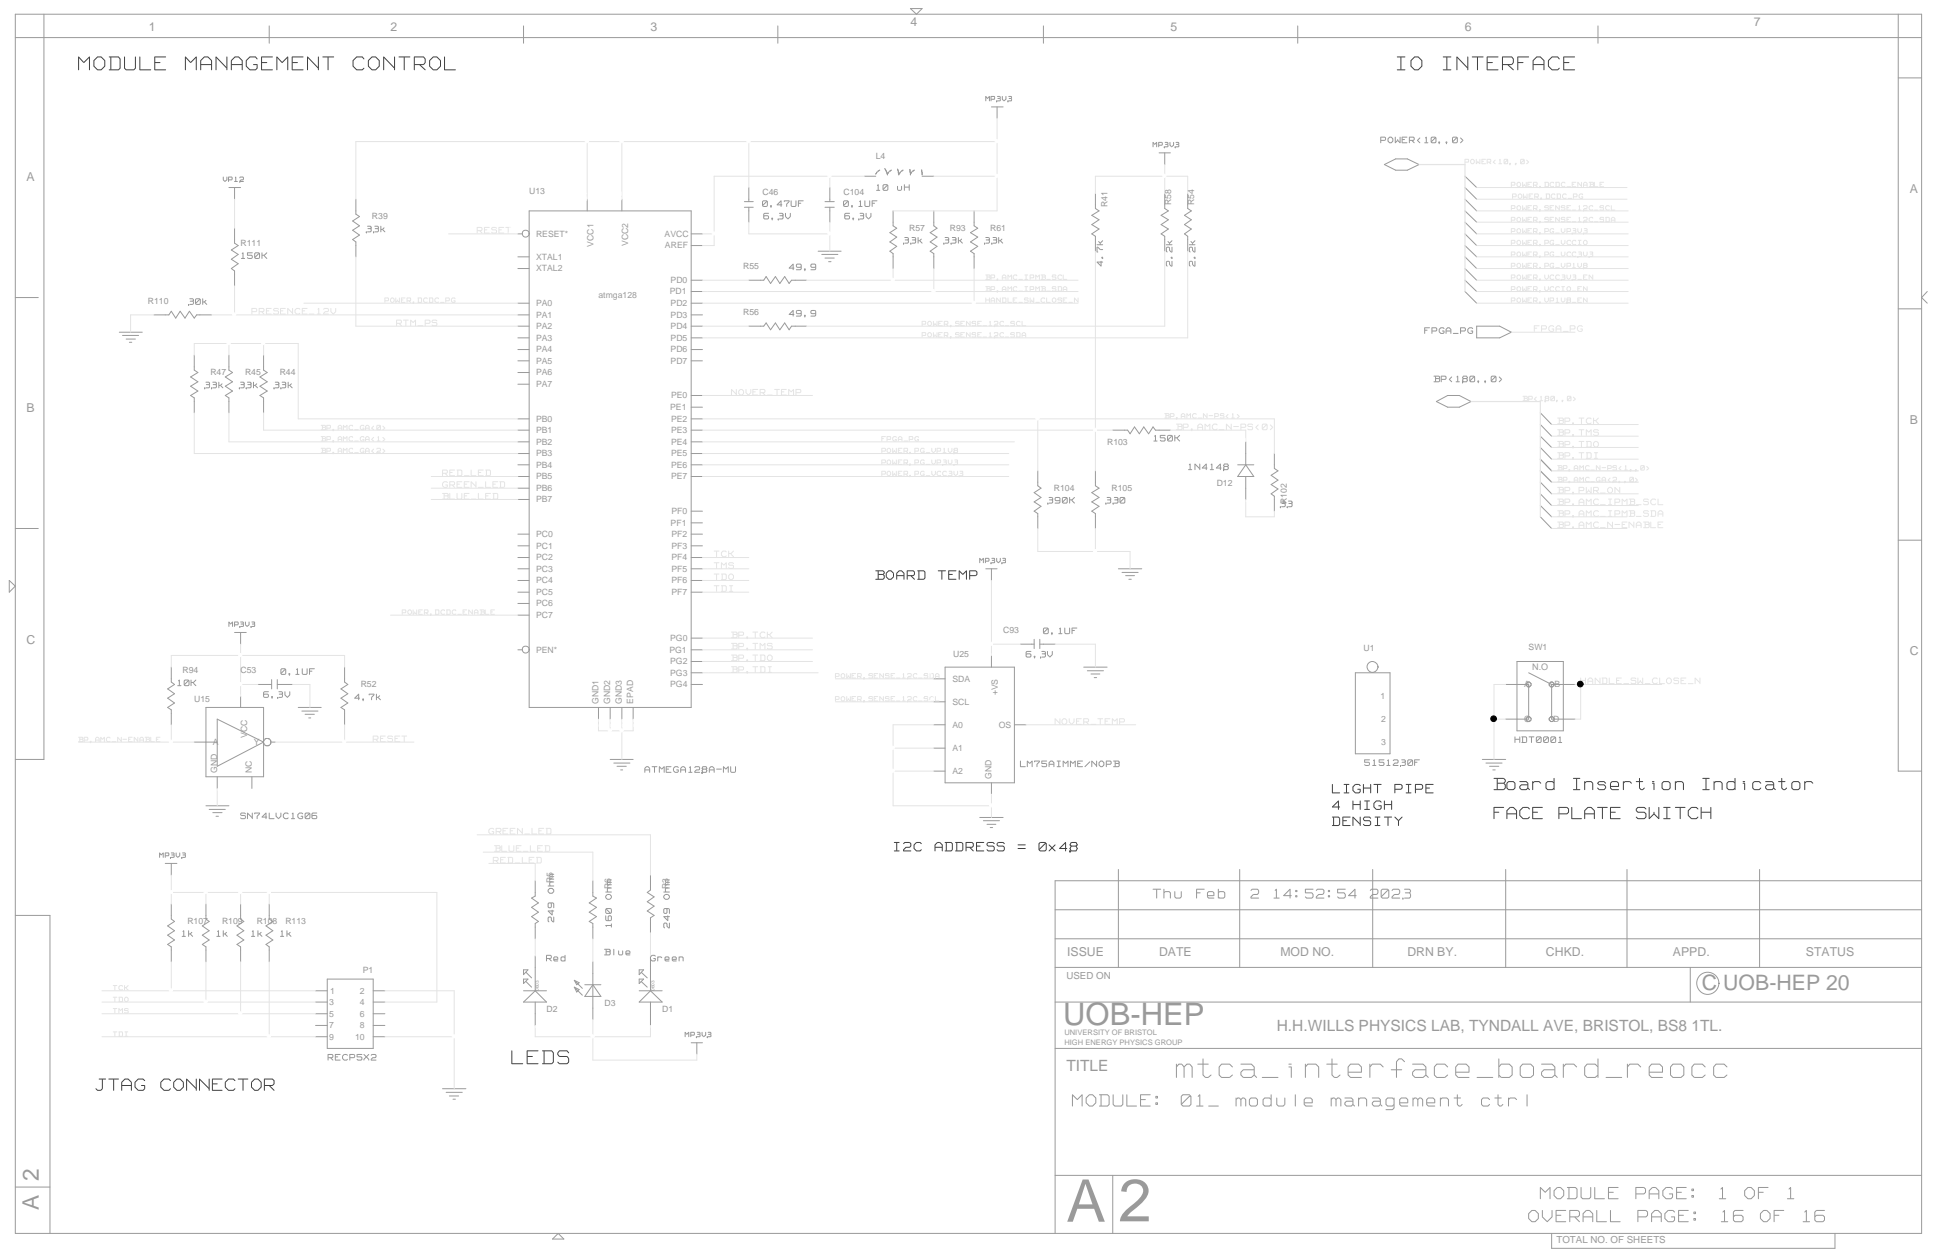
[picture p154: page 16]

BP.TCK BP.AMC_N-PS<0> BP.AMC_N-PS<1>

ISSUE | DATE | MOD NO. | DRN BY. | CHKD. | APPD. | STATUS

USED ON | C UOB-HEP 20

H.H.WILLS PHYSICS LAB, TYNDALL AVE, BRISTOL, BS8 1TL.

UNIVERSITY OF BRISTOL
HIGH ENERGY PHYSICS GROUP
TITLE
