uob-hep-cad/uob-hep-pc072/hardware/Schematics/dune_mib_v2_3feb23.pdf

1 | 3 | 4
5 6

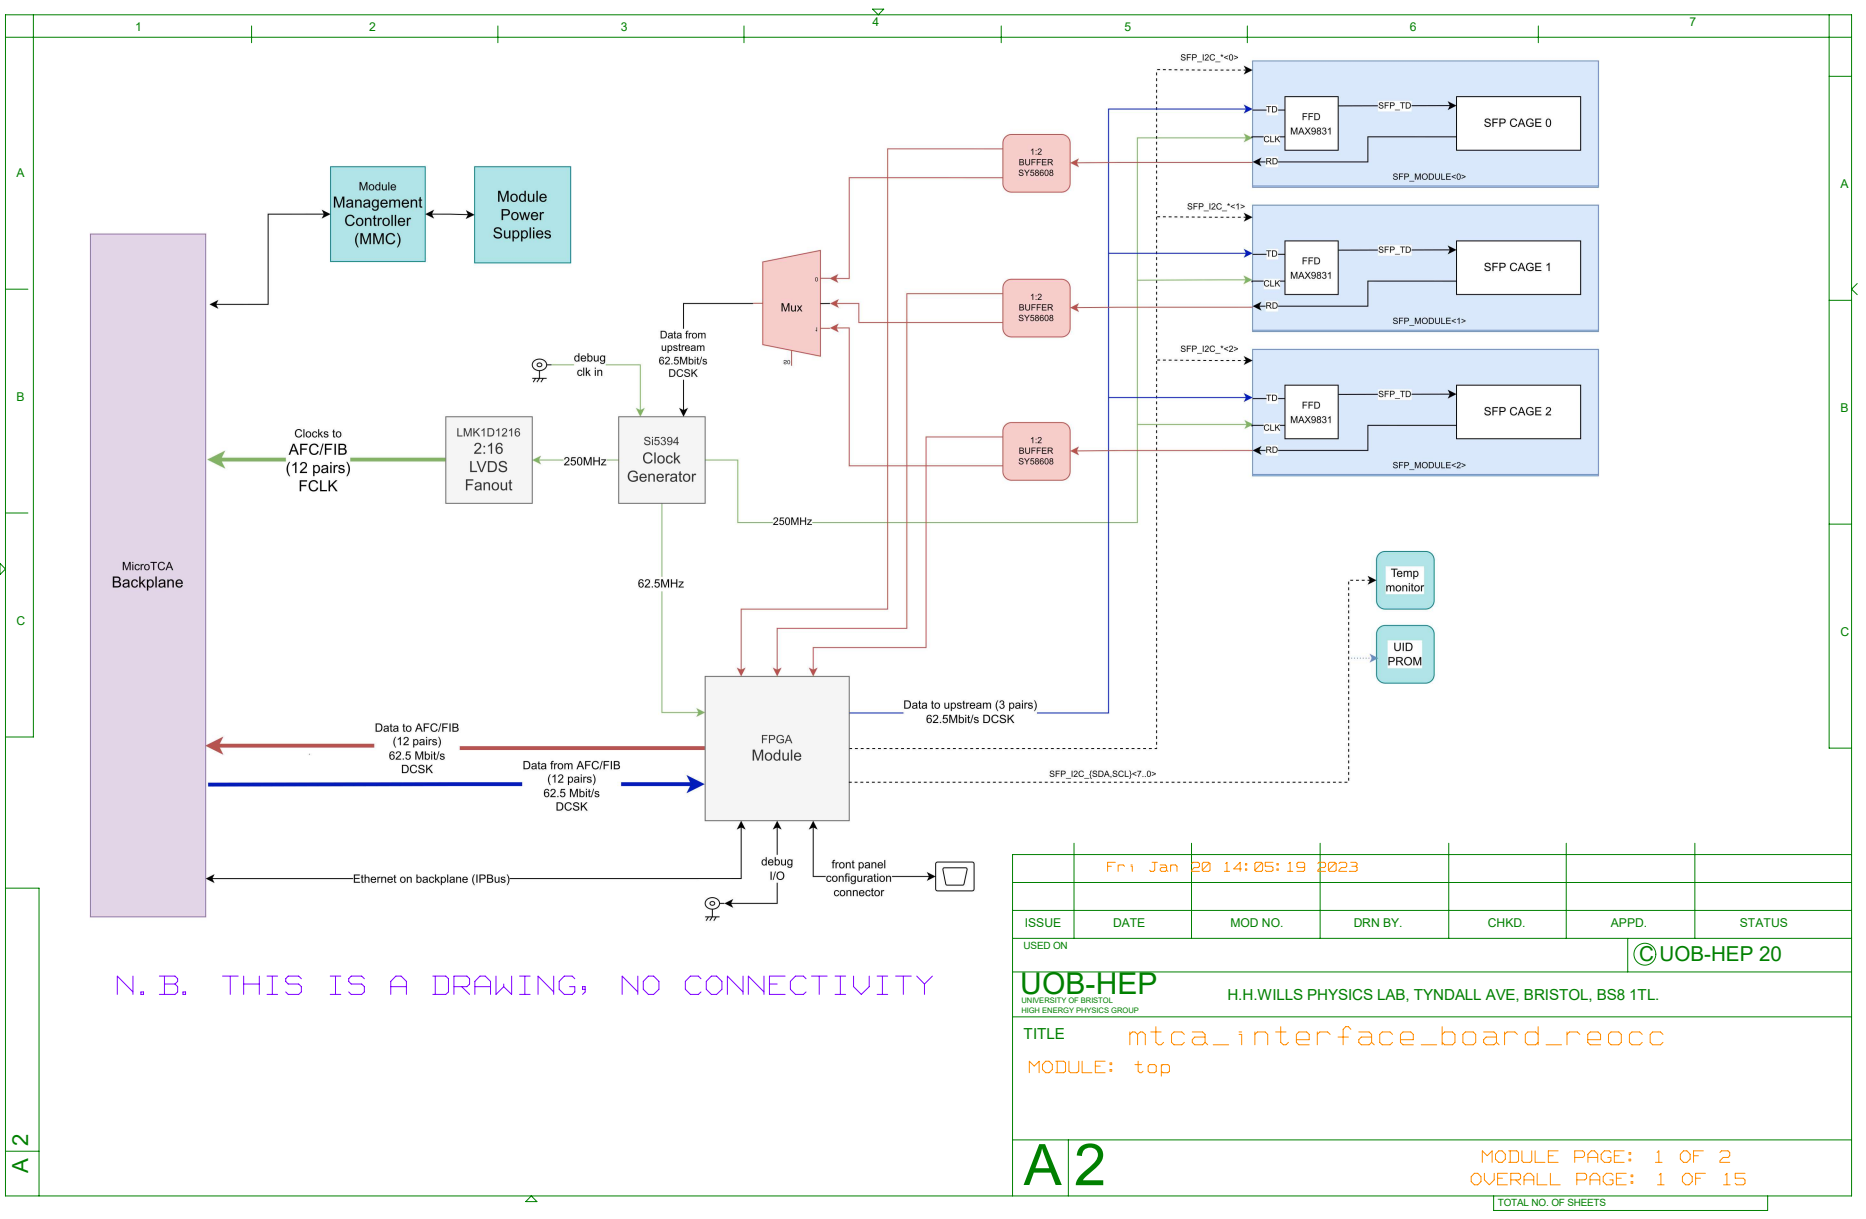
[picture p155: page 1]
Fri Jan 20 14:05:19 2023; mtca_interface_board_reocc; USED ON; ISSUE; APPD. DATE; MOD NO.; DRN BY.; CHKD.; STATUS; C UOB-HEP 20; UOB-HEP

N.B. THIS IS A DRAWING, NO CONNECTIVITY

UNIVERSITY OF BRISTOL
HIGH ENERGY PHYSICS GROUP
TITLE
MODULE: top

H.H.WILLS PHYSICS LAB, TYNDALL AVE, BRISTOL, BS8 1TL.

MODULE PAGE: 1 OF 2
OVERALL PAGE: 1 OF 15

TOTAL NO. OF SHEETS

SFP<29..0> | 07. BACKPLANE INTERFACE FPGA_PG

BP<180..0>

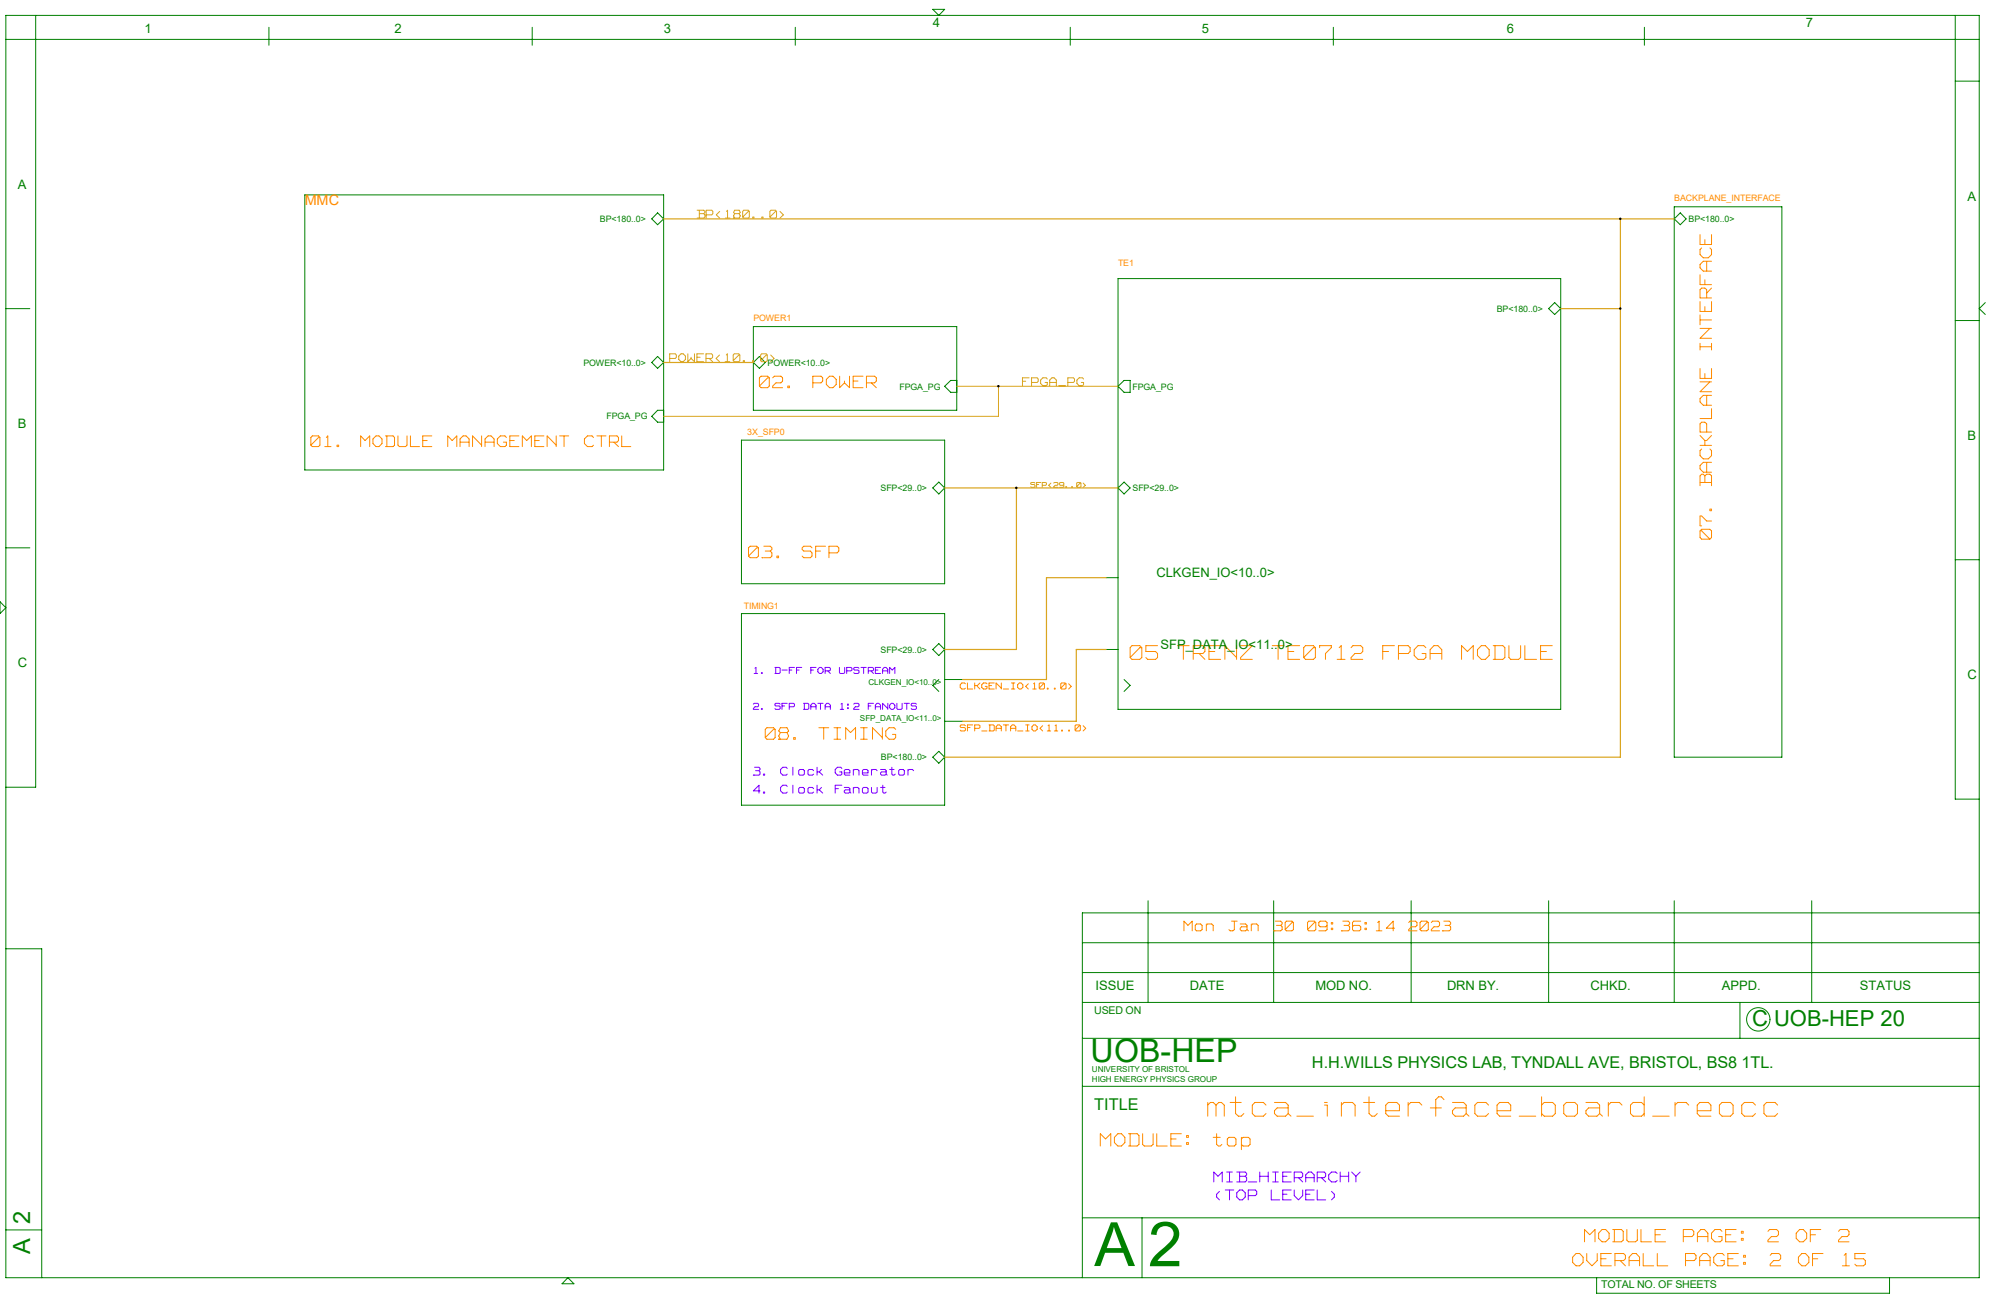
[picture p156: page 2]
MIB_HIERARCHY (TOP LEVEL); 3. Clock Generator 4. Clock Fanout; Mon Jan 30 09:36:14 2023; mtca_interface_board_reocc; 03. SFP; POWER<10..0>; CLKGEN_IO<10..0>; SFP_DATA_IO<11..0>; 02. POWER; 3X_SFP0; TIMING1; POWER1; BACKPLANE_INTERFACE; FPGA_PG; SFP<29..0>; USED ON; ISSUE; APPD. DATE; MOD NO.; DRN BY.; CHKD.; STATUS; MMC; C UOB-HEP 20; UOB-HEP

01. MODULE MANAGEMENT CTRL

SFP_DATA_IO<11..0>
05 TRENZ TE0712 FPGA MODULE

1. D-FF FOR UPSTREAM

2. SFP DATA 1:2 FANOUTS
08. TIMING

UNIVERSITY OF BRISTOL
HIGH ENERGY PHYSICS GROUP
TITLE
MODULE: top

H.H.WILLS PHYSICS LAB, TYNDALL AVE, BRISTOL, BS8 1TL.

MODULE PAGE: 2 OF 2
OVERALL PAGE: 2 OF 15

# 12V to 3V5 @ 14A DC-DC CONVERTER

# VP3V5 IV MONITOR

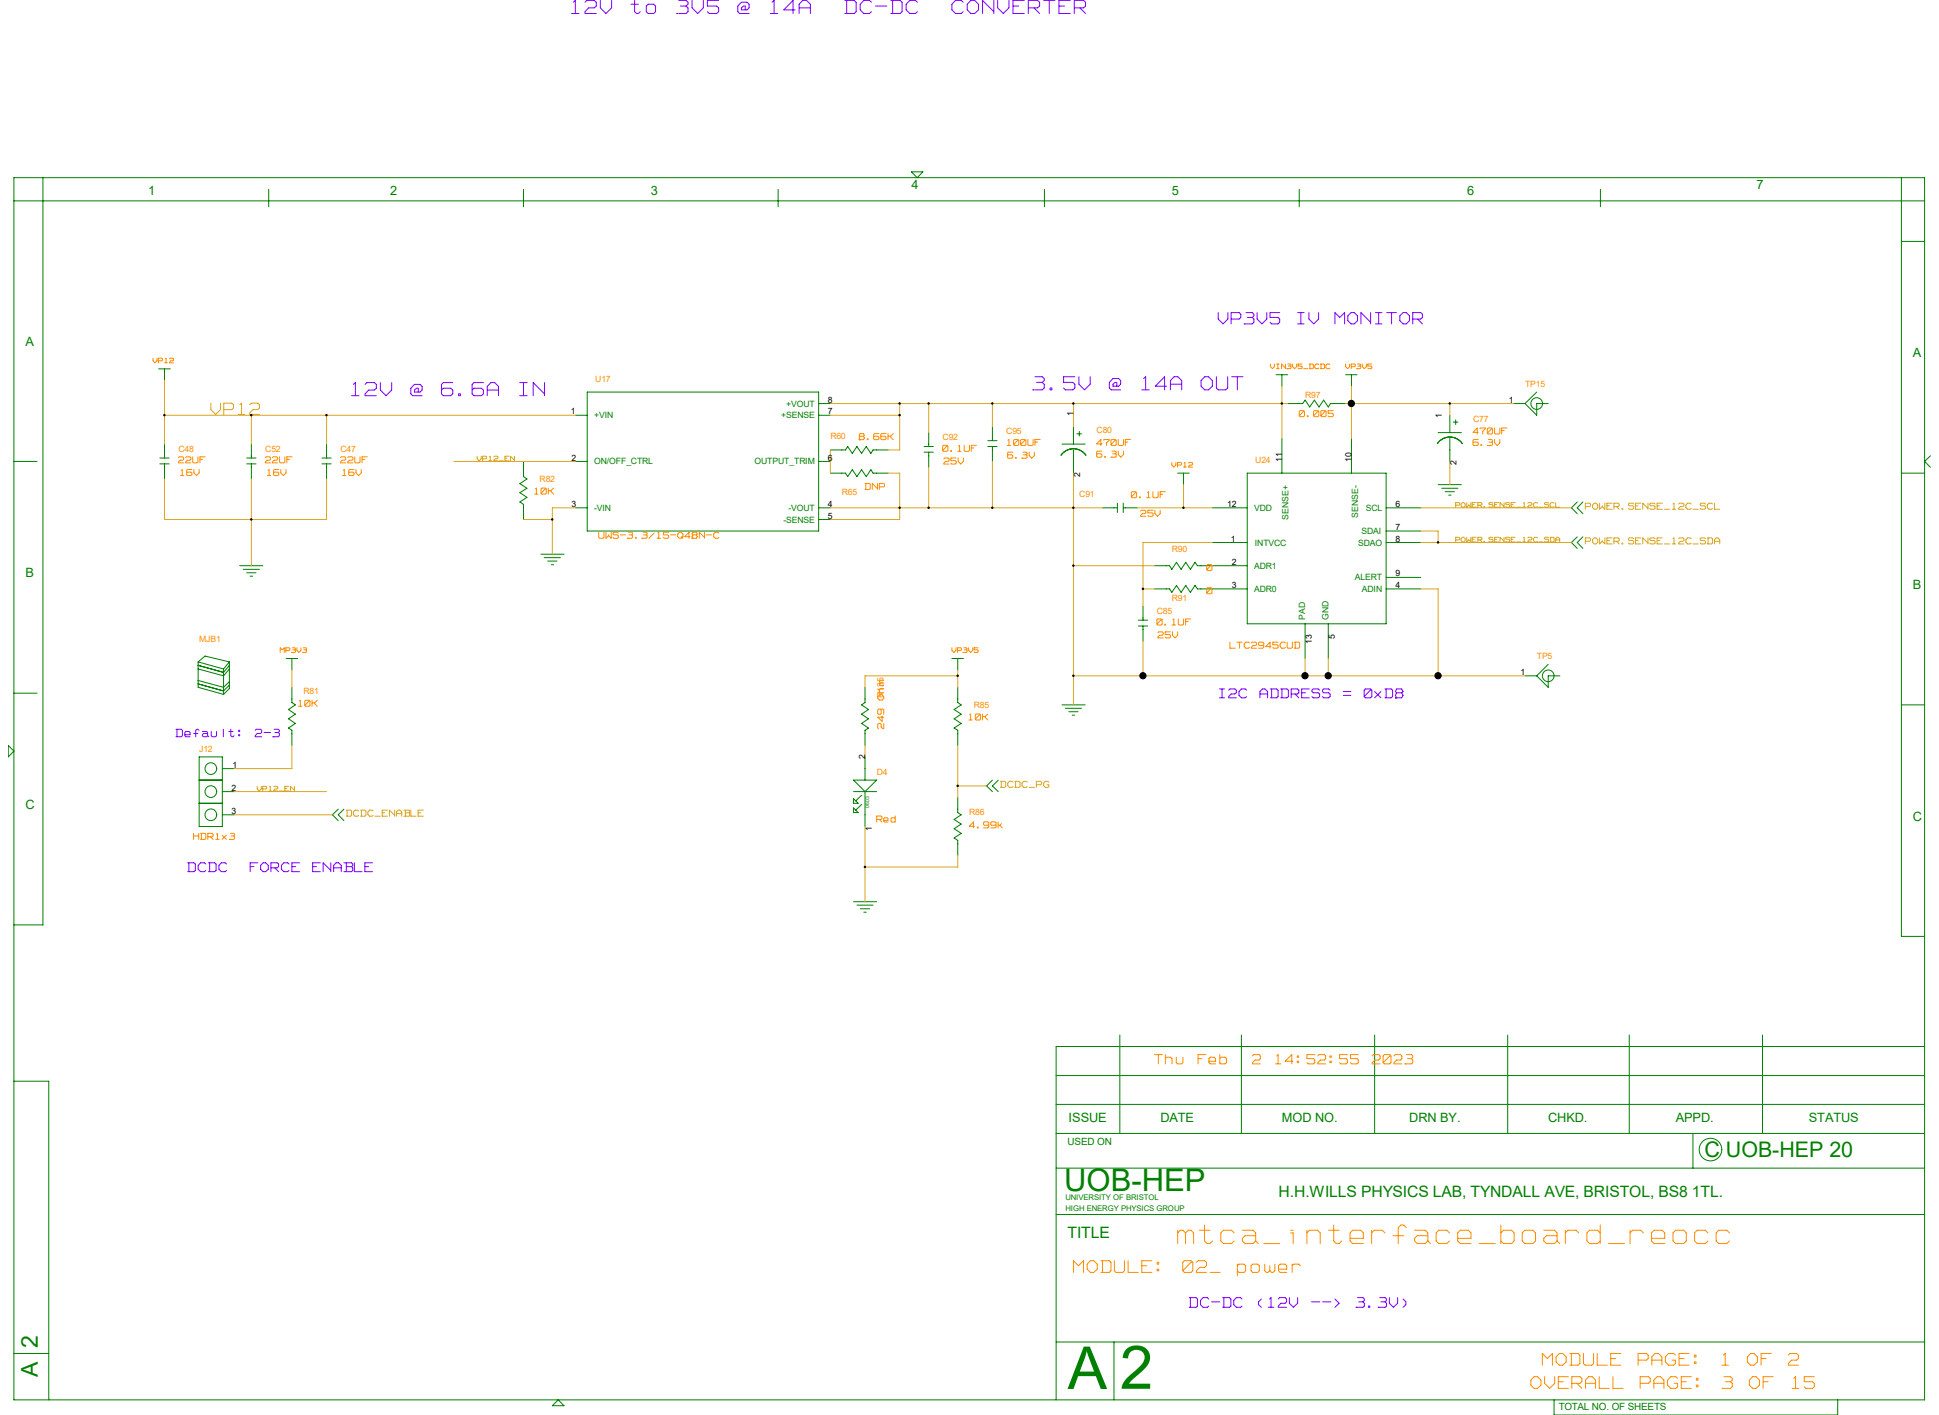
[picture p157: page 3]

2 GND SENSE+ SENSE- PAD

H.H.WILLS PHYSICS LAB, TYNDALL AVE, BRISTOL, BS8 1TL.

UNIVERSITY OF BRISTOL
HIGH ENERGY PHYSICS GROUP
TITLE
MODULE: 02_ power

# VP3V3 IV MONITOR

# VP3V3 @4A

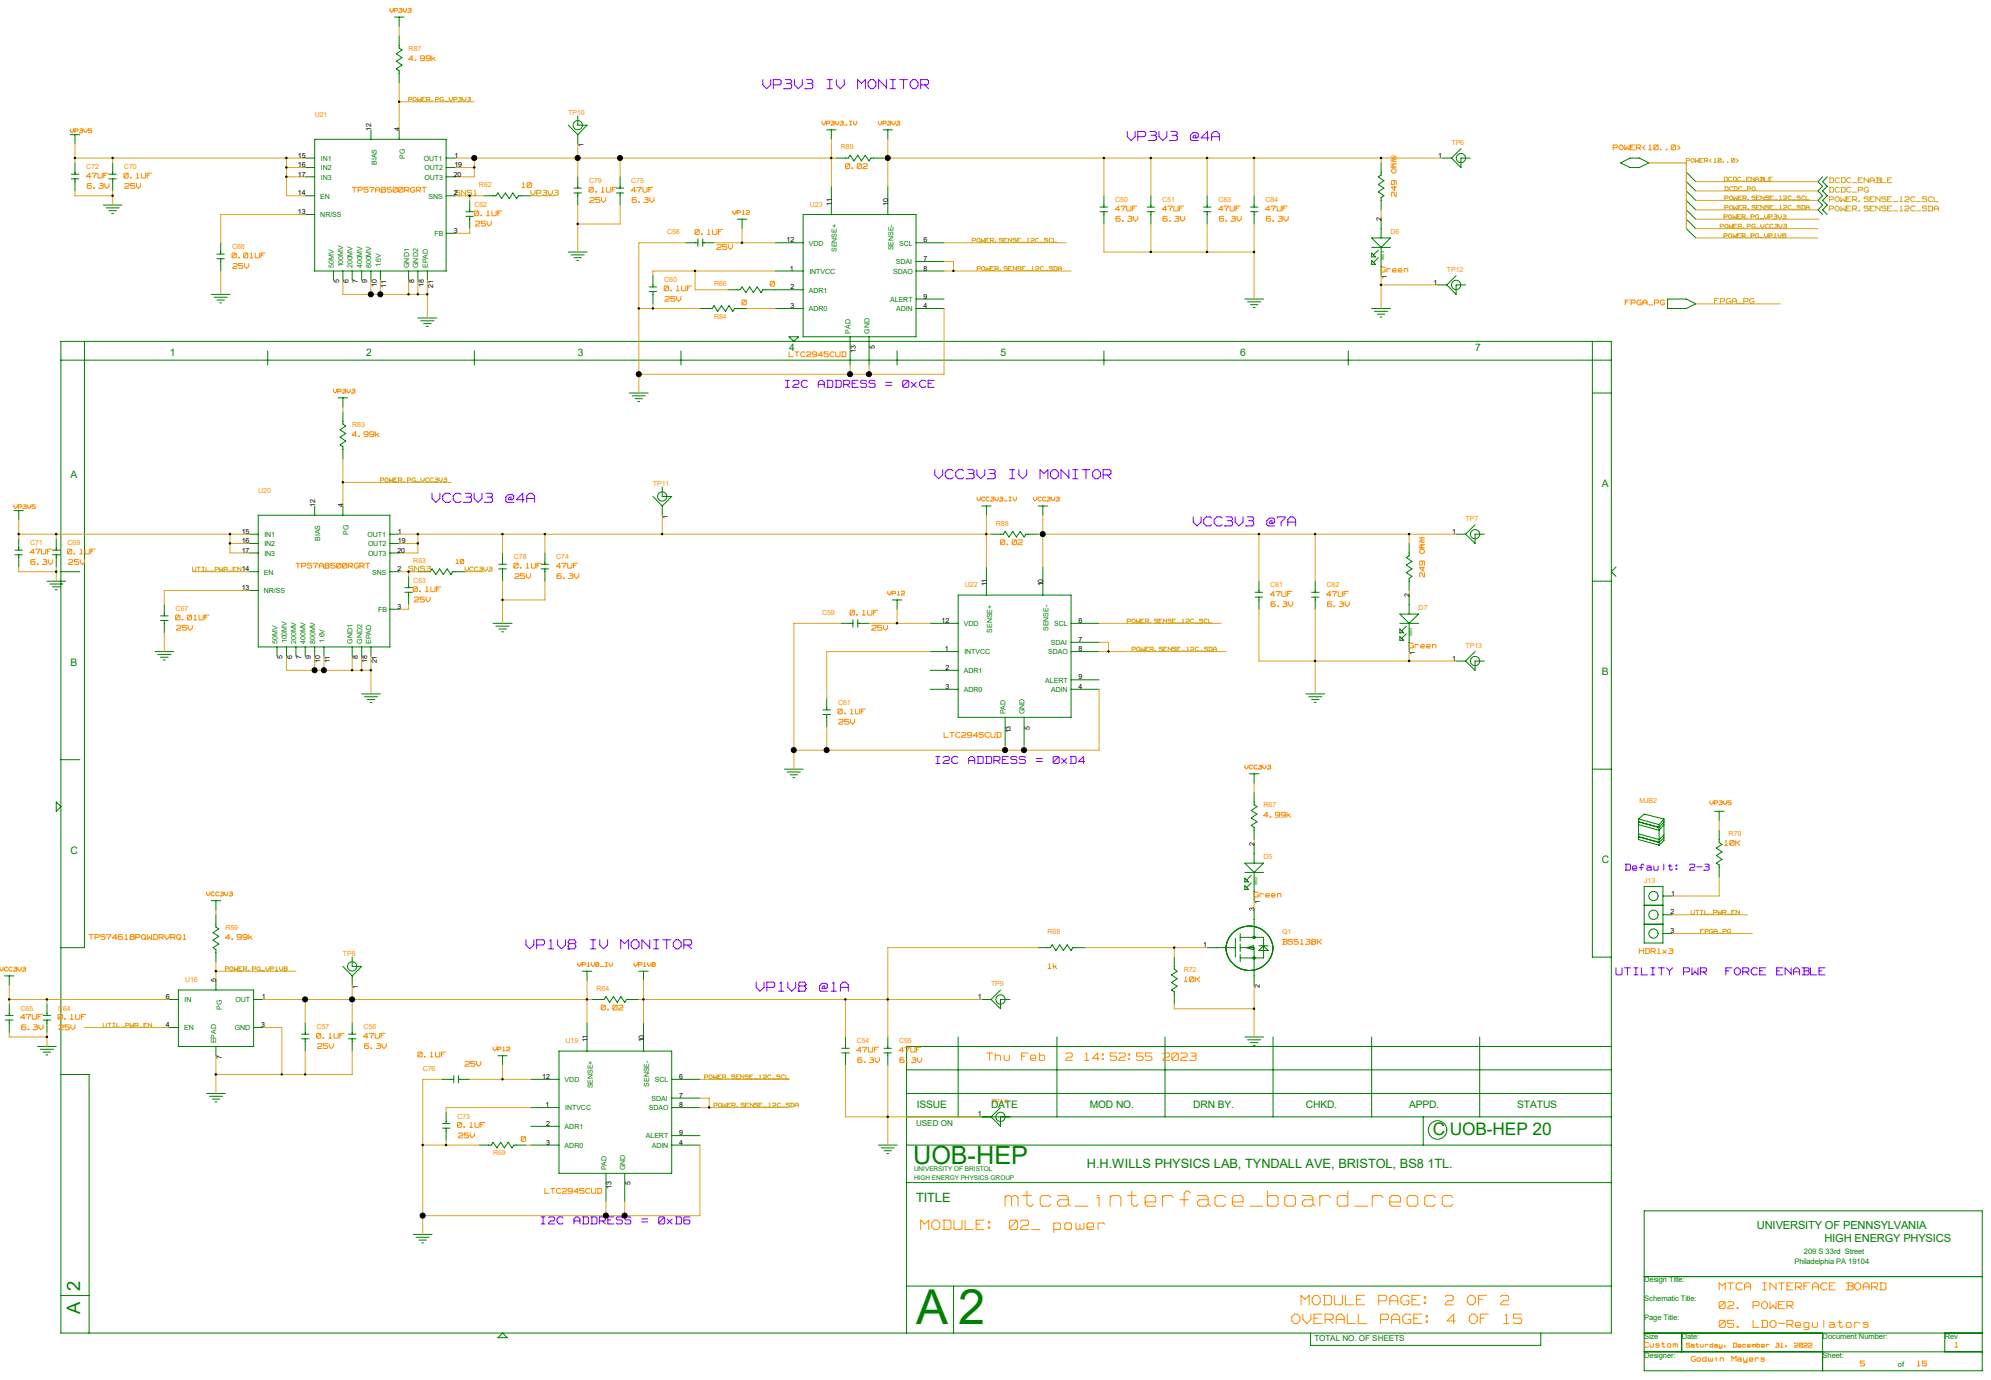
[picture p158: page 4]

9 12 1821810115 R70 R71 PG 50MV 100MV 200MV 400MV 800MV 1.6V GND1 EPAD BIAS GND2 PG 50MV 100MV 200MV 400MV 800MV 1.6V GND1 EPAD BIAS GND2 GND SENSE+ SENSE- PAD PG EPAD GND SENSE+ SENSE- PAD GND SENSE+ SENSE- PAD

HDR1x3
UTILITY PWR FORCE ENABLE

H.H.WILLS PHYSICS LAB, TYNDALL AVE, BRISTOL, BS8 1TL.

UNIVERSITY OF BRISTOL
HIGH ENERGY PHYSICS GROUP
TITLE
MODULE: 02_ power

# SFP DATA TO FPGA

# 100NF 16V_GEN 100NF 16V_GEN 100NF 16V_GEN 100NF

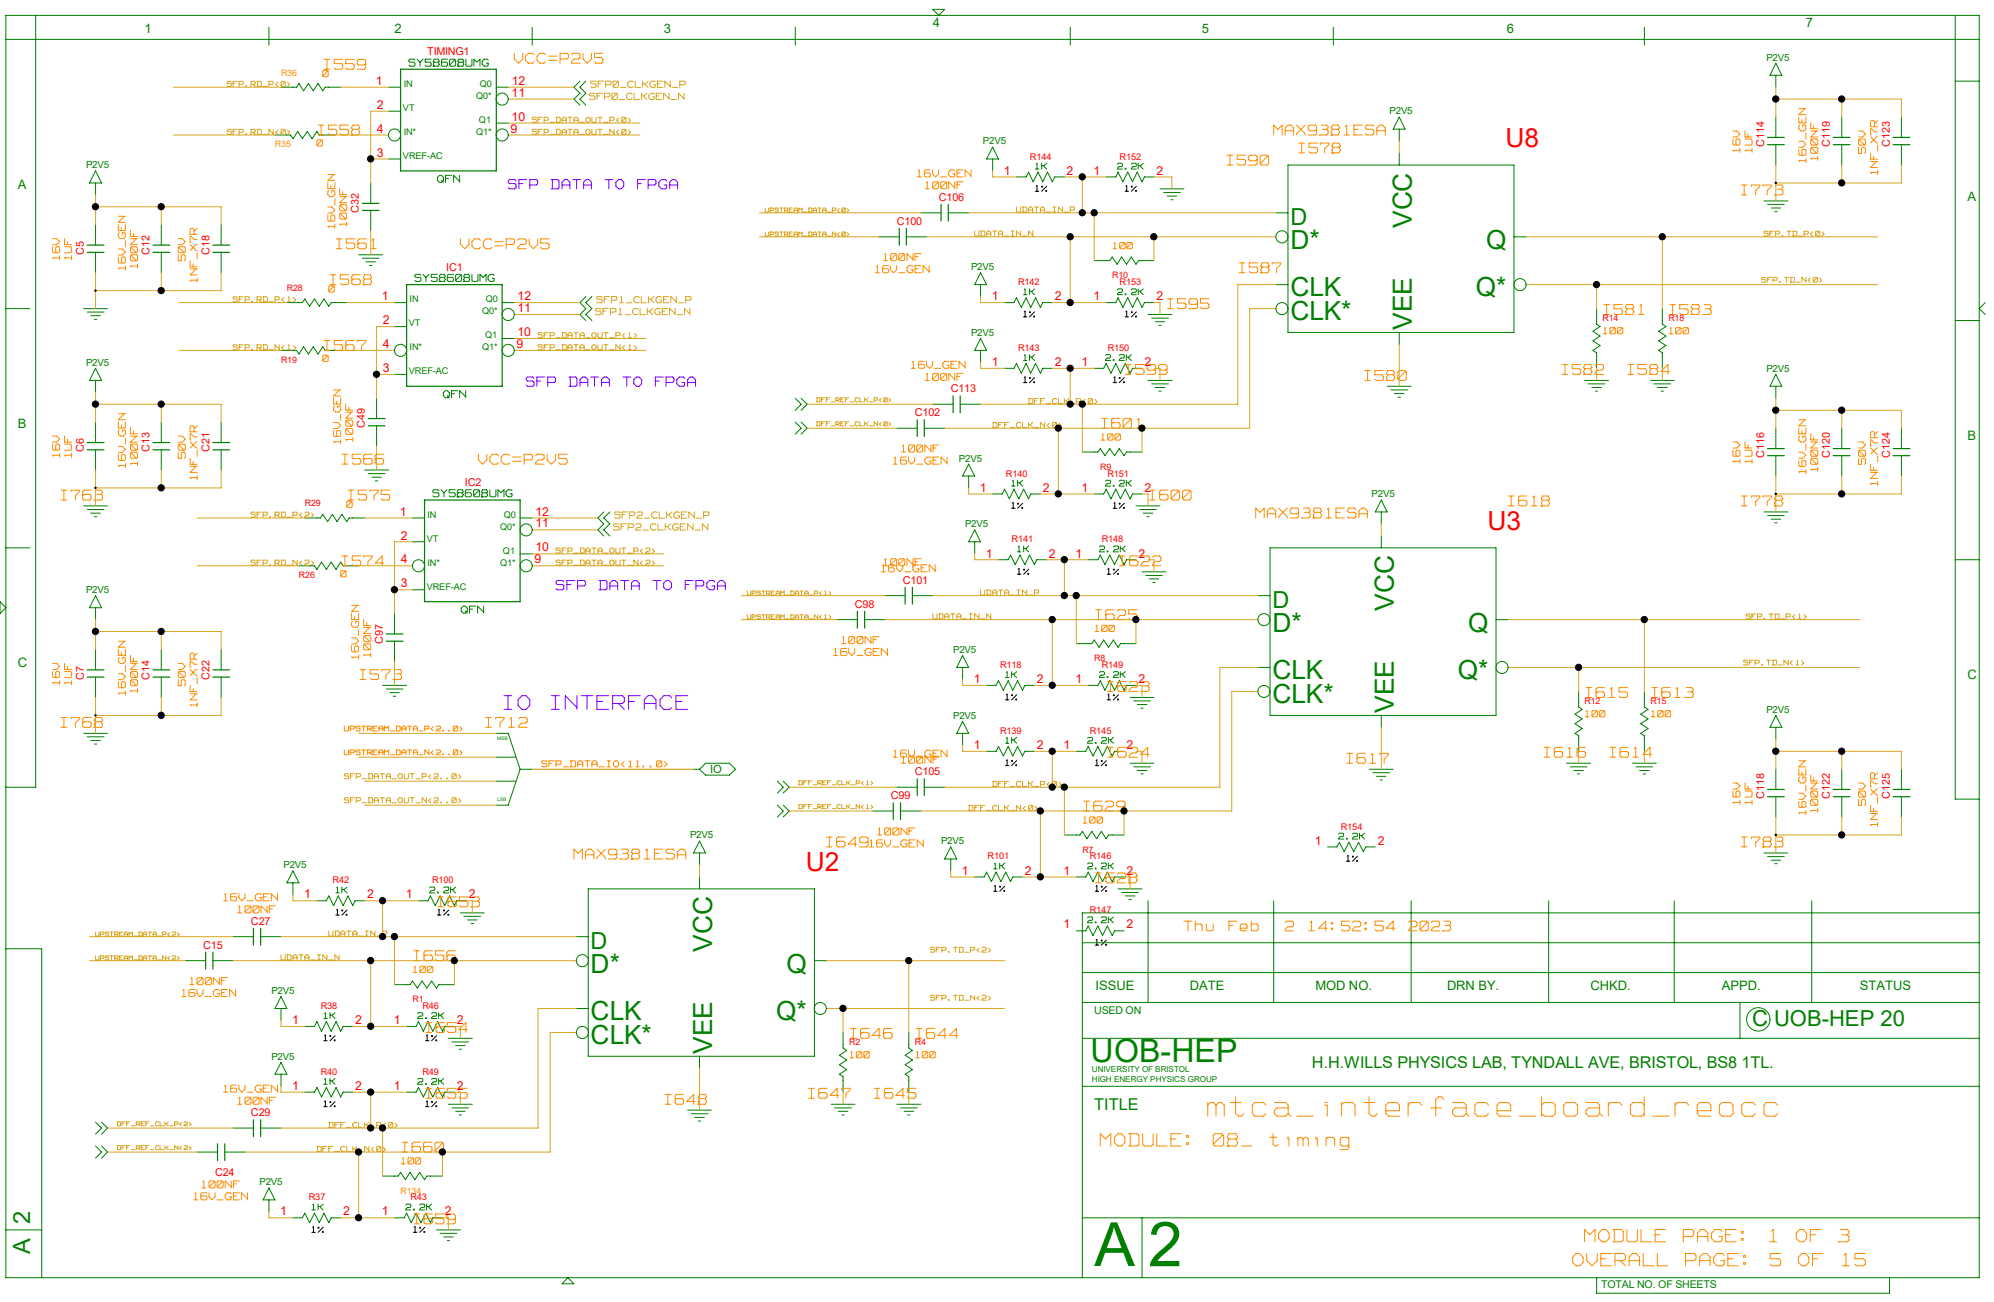
[picture p159: page 5]

UNIVERSITY OF BRISTOL
HIGH ENERGY PHYSICS GROUP
TITLE
MODULE: 08_ timing

H.H.WILLS PHYSICS LAB, TYNDALL AVE, BRISTOL, BS8 1TL.

# VDDO_CLK

I340

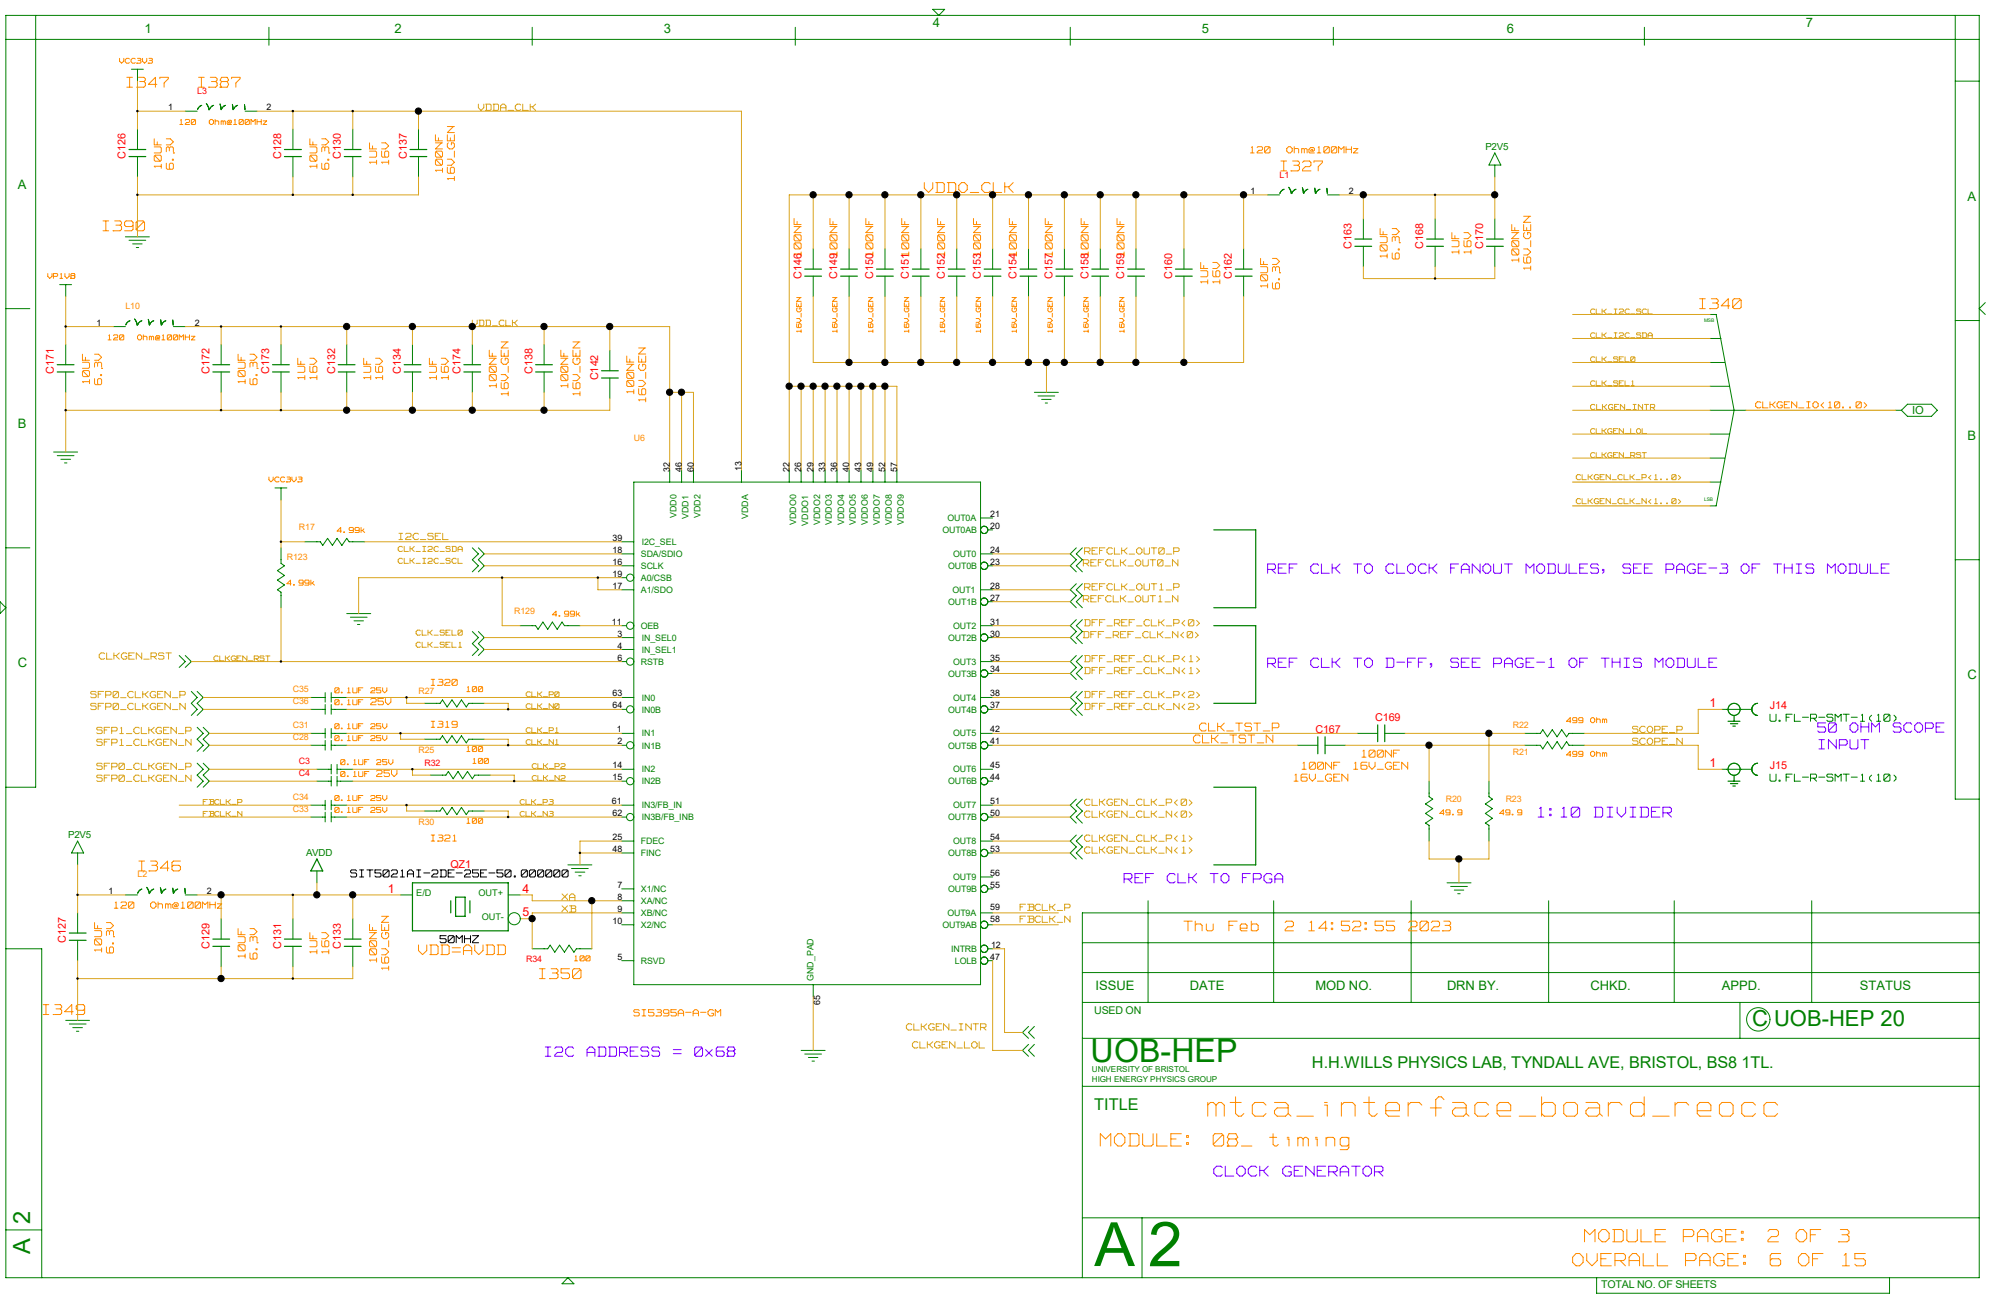
[picture p160: page 6]

REF CLK TO CLOCK FANOUT MODULES, SEE PAGE-3 OF THIS MODULE

REF CLK TO D-FF, SEE PAGE-1 OF THIS MODULE

UNIVERSITY OF BRISTOL
HIGH ENERGY PHYSICS GROUP
TITLE
MODULE: 08_ timing

H.H.WILLS PHYSICS LAB, TYNDALL AVE, BRISTOL, BS8 1TL.

# 16V_GEN 1% 16V_GEN

I176

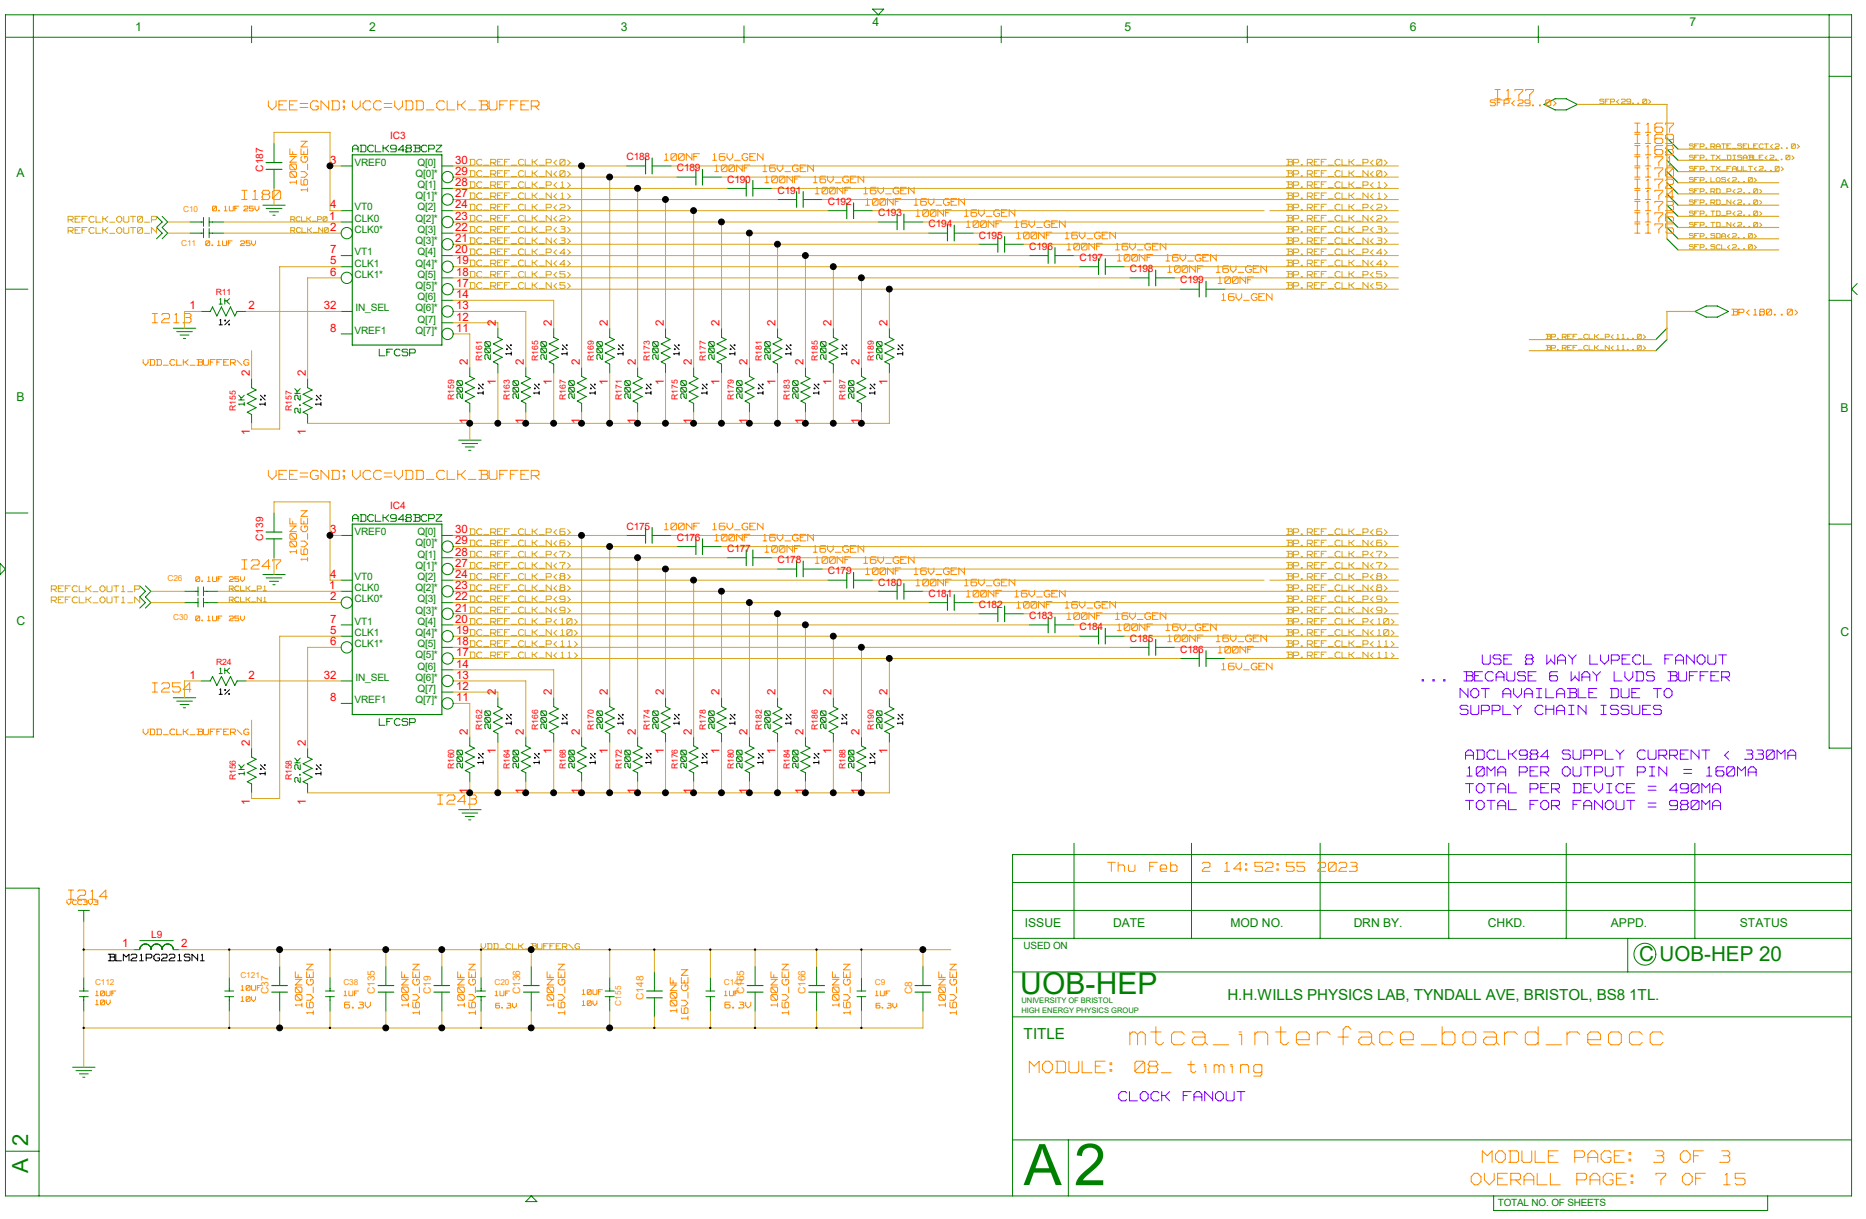
[picture p161: page 7]

USE 8 WAY LVPECL FANOUT
NOT AVAILABLE DUE TO
SUPPLY CHAIN ISSUES

... BECAUSE 6 WAY LVDS BUFFER

UNIVERSITY OF BRISTOL
HIGH ENERGY PHYSICS GROUP
TITLE
MODULE: 08_ timing

H.H.WILLS PHYSICS LAB, TYNDALL AVE, BRISTOL, BS8 1TL.

## SFP.RATE_SELECT<0>

A

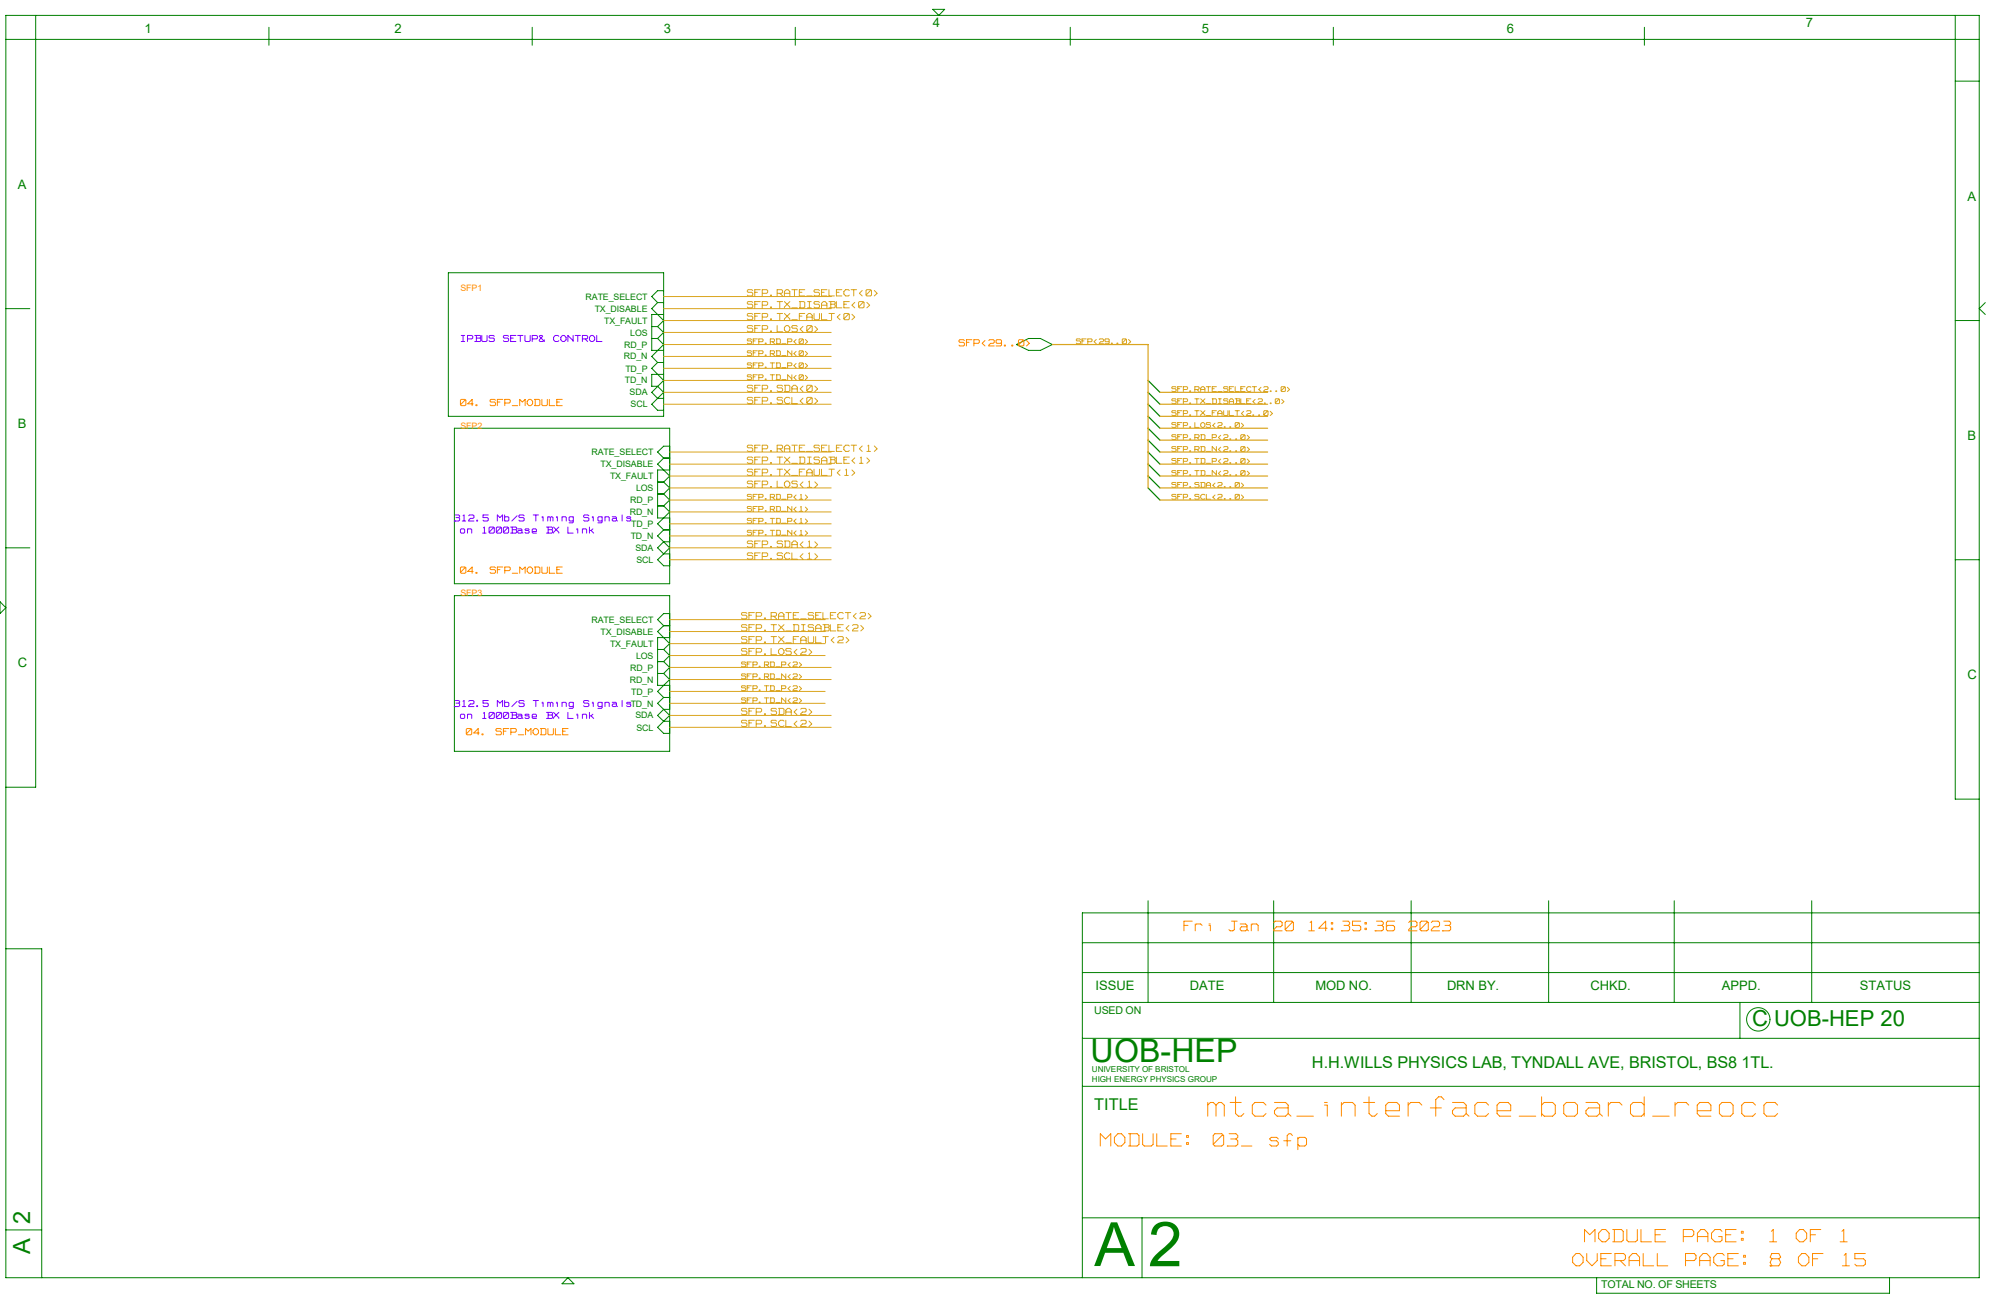
[picture p162: page 8]
Fri Jan 20 14:35:36 2023; mtca_interface_board_reocc; SFP<29..0>; SFP.TD_P<2>; SFP.RD_N<2>; SFP.RD_P<2>; SFP.LOS<2>; SFP.TX_FAULT<2>; 04. SFP_MODULE; SFP.TD_N<0>; SFP.TD_P<0>; SFP.RD_P<0> SFP.RD_N<0>; SFP.SCL<0>; SFP.SDA<0>; SFP.TX_DISABLE<0>; SFP.LOS<0>; SFP.TX_FAULT<0>; SFP.SCL<2>; SFP.SDA<2>; SFP.TD_N<2>; SFP.TX_DISABLE<2>; SFP.RATE_SELECT<2>; SFP.SCL<1>; SFP.SDA<1>; SFP.TD_N<1>; SFP.TD_P<1>; SFP.RD_N<1>; SFP.RD_P<1>; SFP.LOS<1>; SFP.TX_FAULT<1>; SFP.TX_DISABLE<1>; SFP.RATE_SELECT<1>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

IPBUS SETUP& CONTROL

312.5 Mb/S Timing Signals
on 1000Base BX Link

04. SFP_MODULE

UNIVERSITY OF BRISTOL
HIGH ENERGY PHYSICS GROUP
TITLE
MODULE: 03_ sfp

H.H.WILLS PHYSICS LAB, TYNDALL AVE, BRISTOL, BS8 1TL.

MODULE PAGE: 1 OF 1
OVERALL PAGE: 8 OF 15

22UF
6.3V

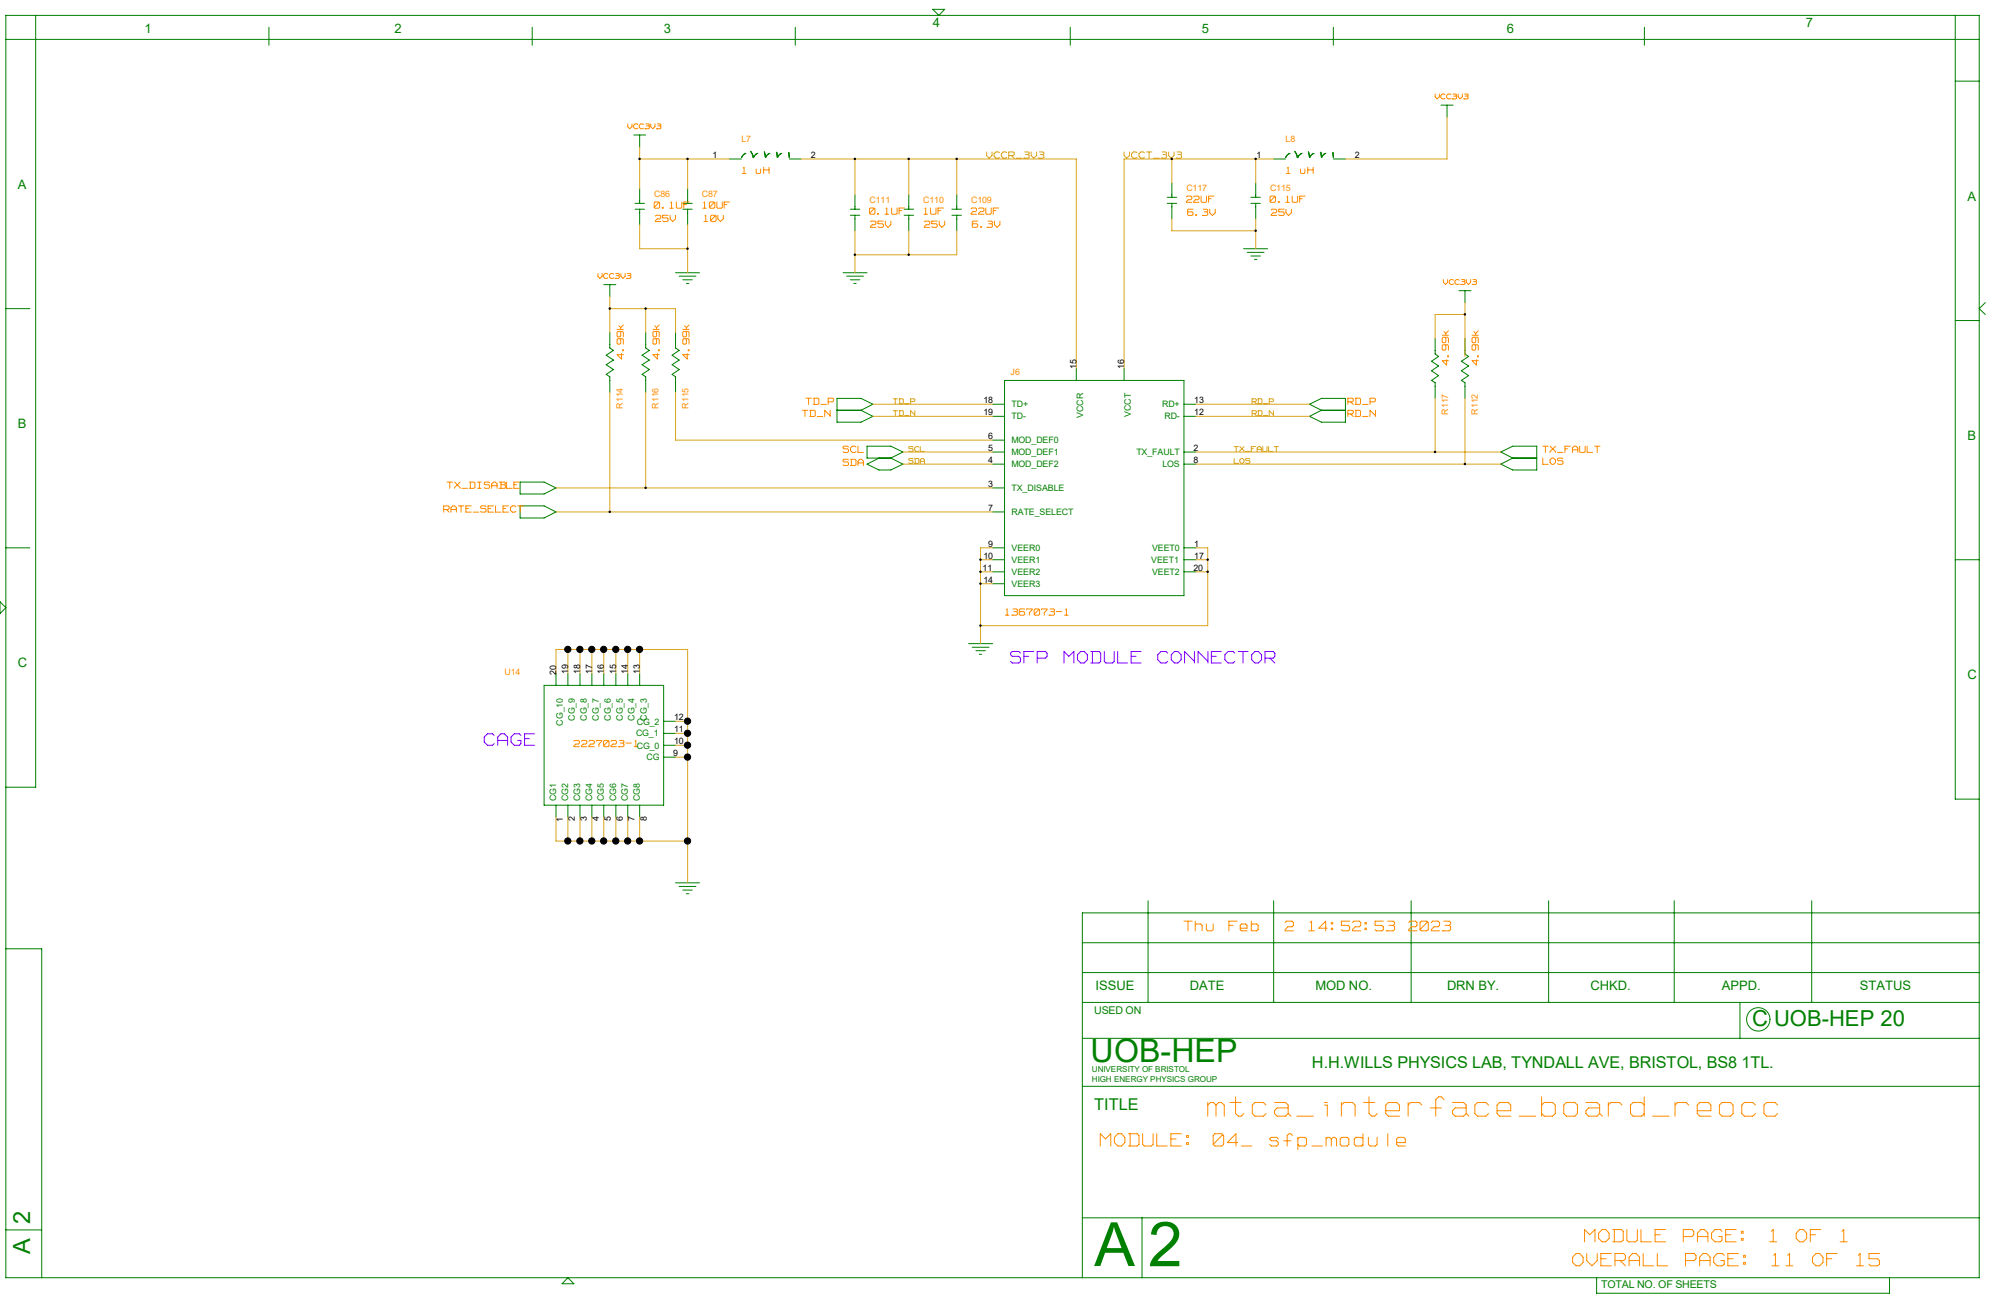
[picture p163: page 9]

UNIVERSITY OF BRISTOL
HIGH ENERGY PHYSICS GROUP
TITLE
MODULE: 04_ sfp_module

H.H.WILLS PHYSICS LAB, TYNDALL AVE, BRISTOL, BS8 1TL.

# AUX IO INTERFACE

JTAG CONNECTOR | EEPROM

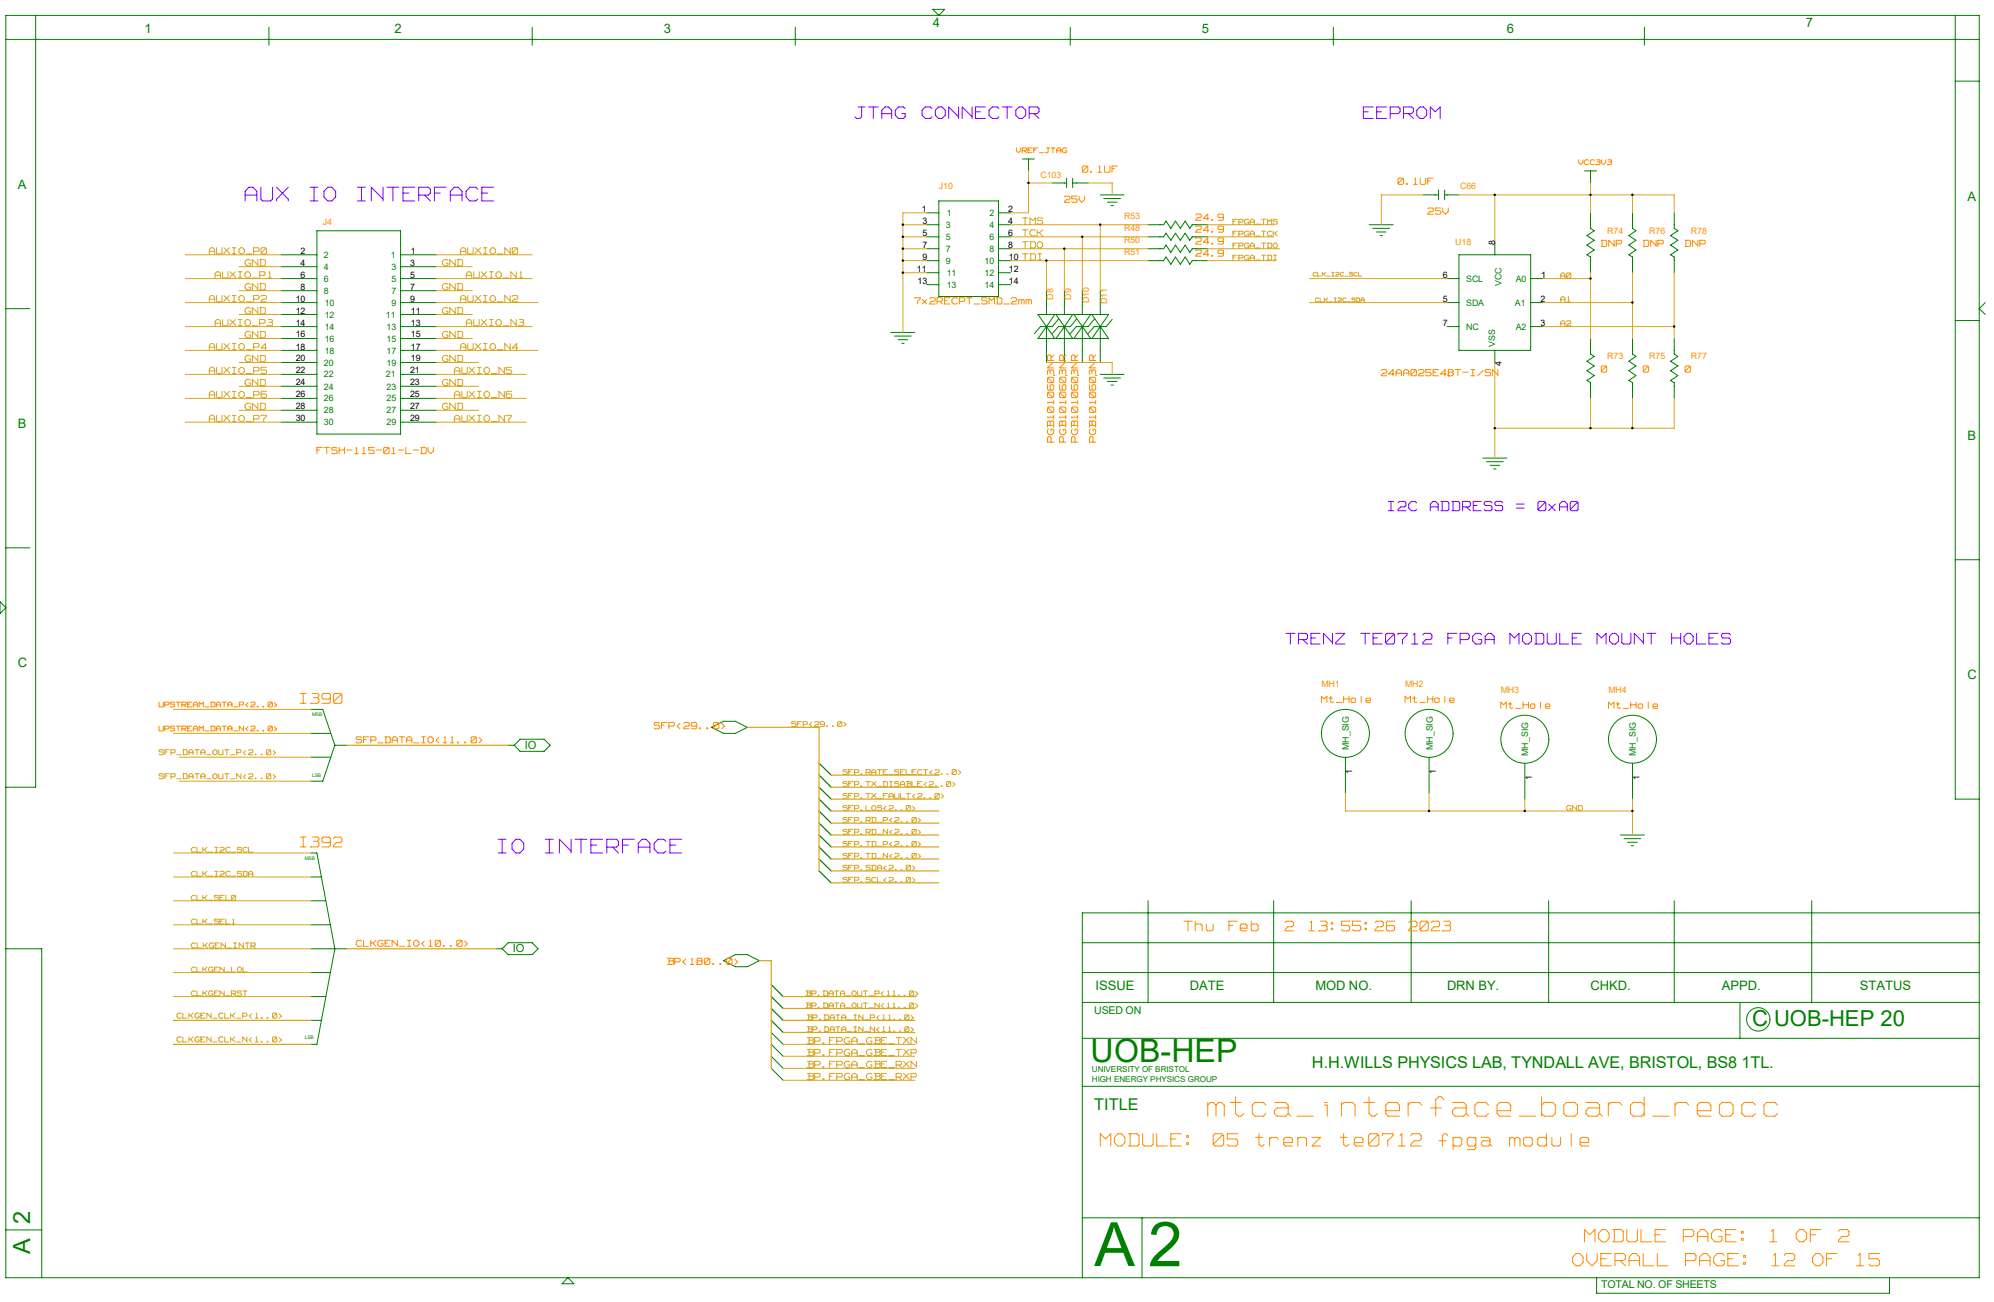
[picture p164: page 10]

TRENZ TE0712 FPGA MODULE MOUNT HOLES

UNIVERSITY OF BRISTOL
HIGH ENERGY PHYSICS GROUP
TITLE
MODULE: 05 trenz te0712 fpga module

H.H.WILLS PHYSICS LAB, TYNDALL AVE, BRISTOL, BS8 1TL.

## P1V5_OUT

1.0MM

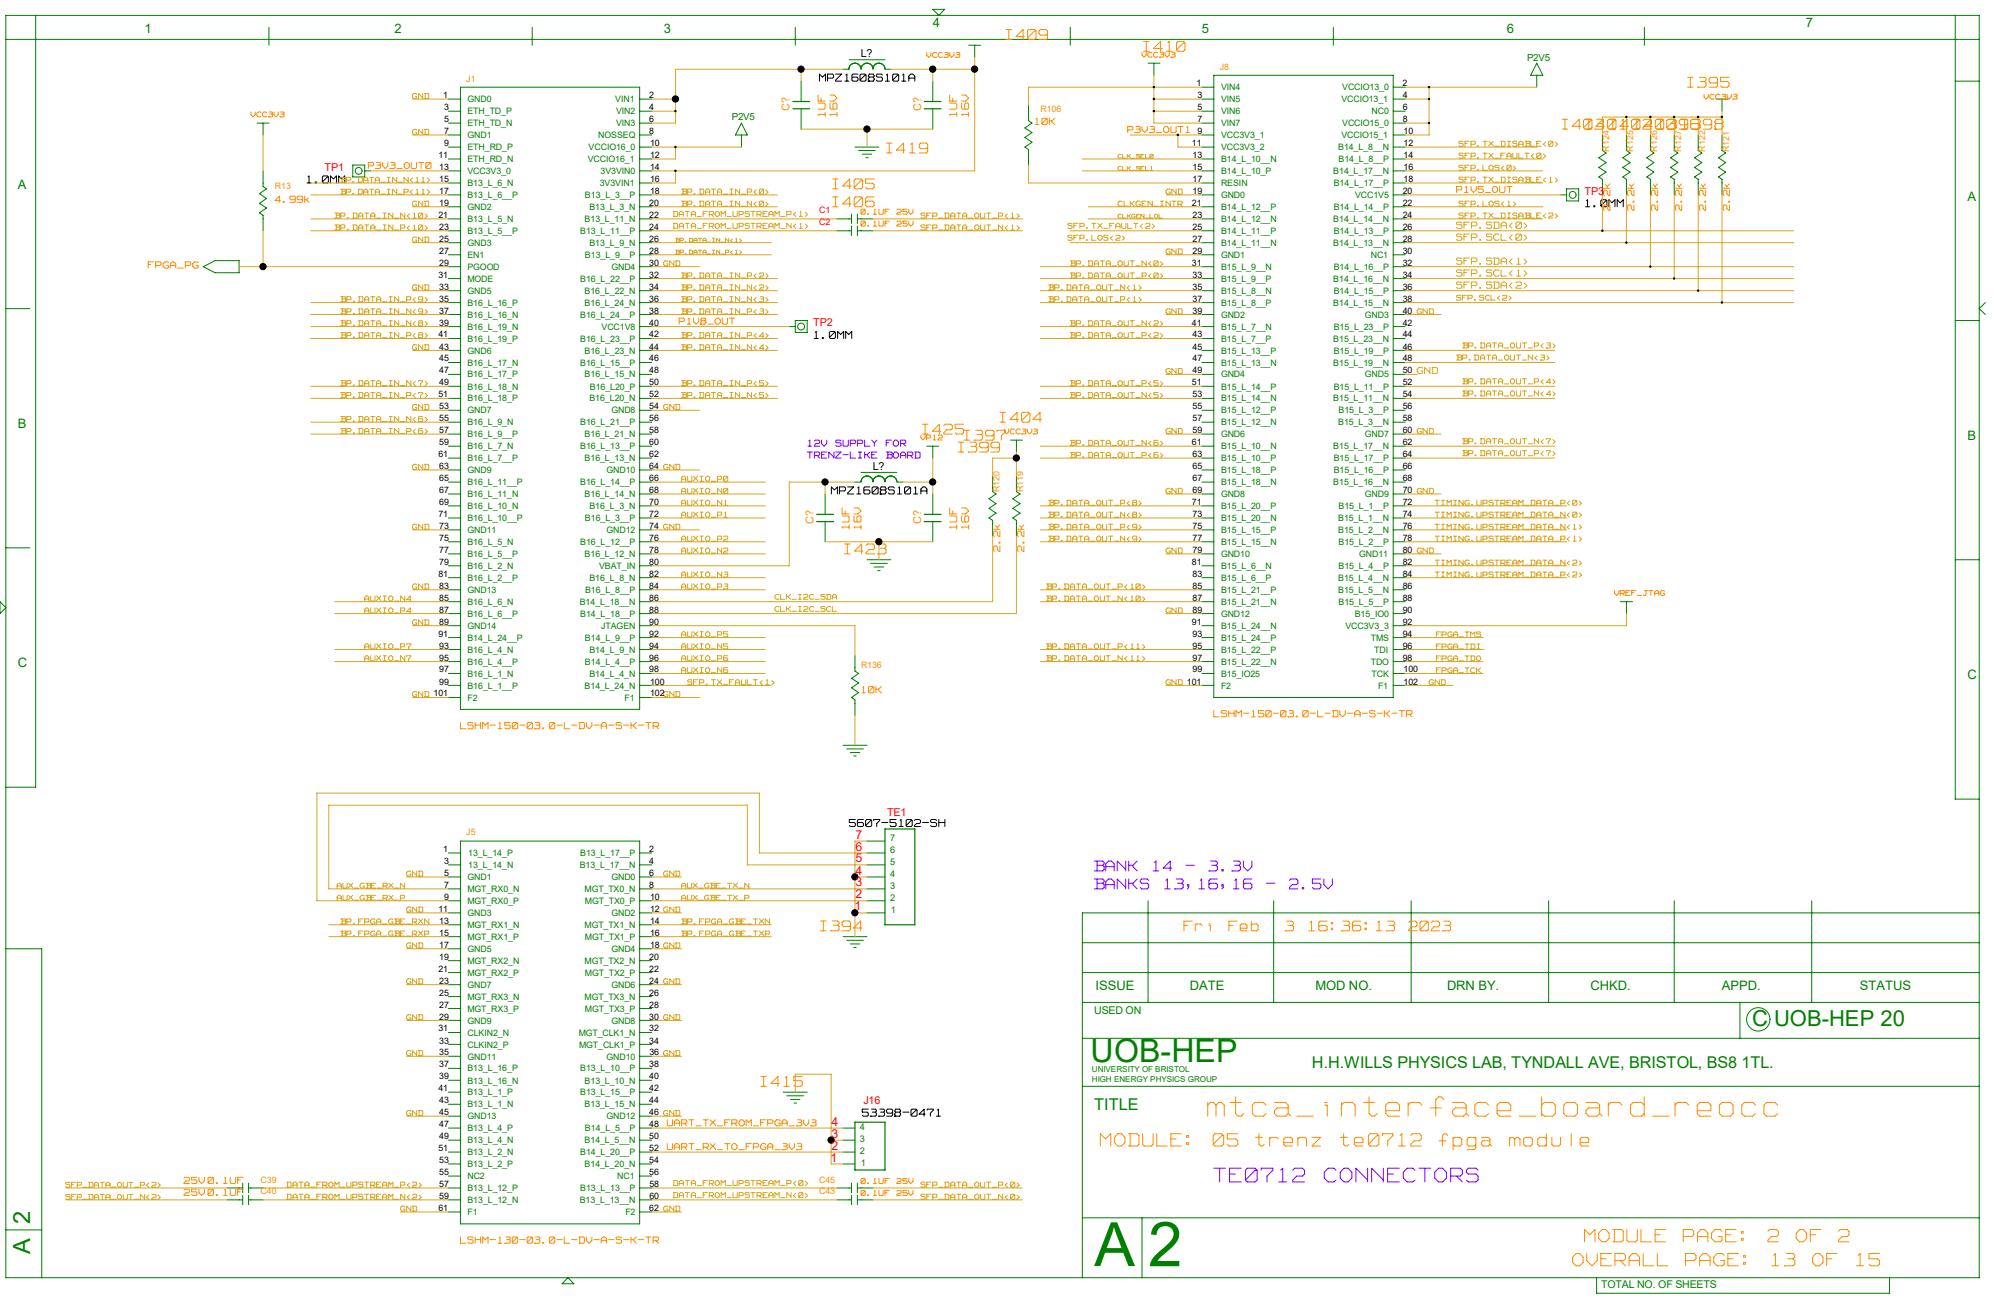
[picture p165: page 11]

UNIVERSITY OF BRISTOL
HIGH ENERGY PHYSICS GROUP
TITLE
MODULE: 05 trenz te0712 fpga module

H.H.WILLS PHYSICS LAB, TYNDALL AVE, BRISTOL, BS8 1TL.

# TONGUE 2 MEZZENINE CONNECTOR

## GND

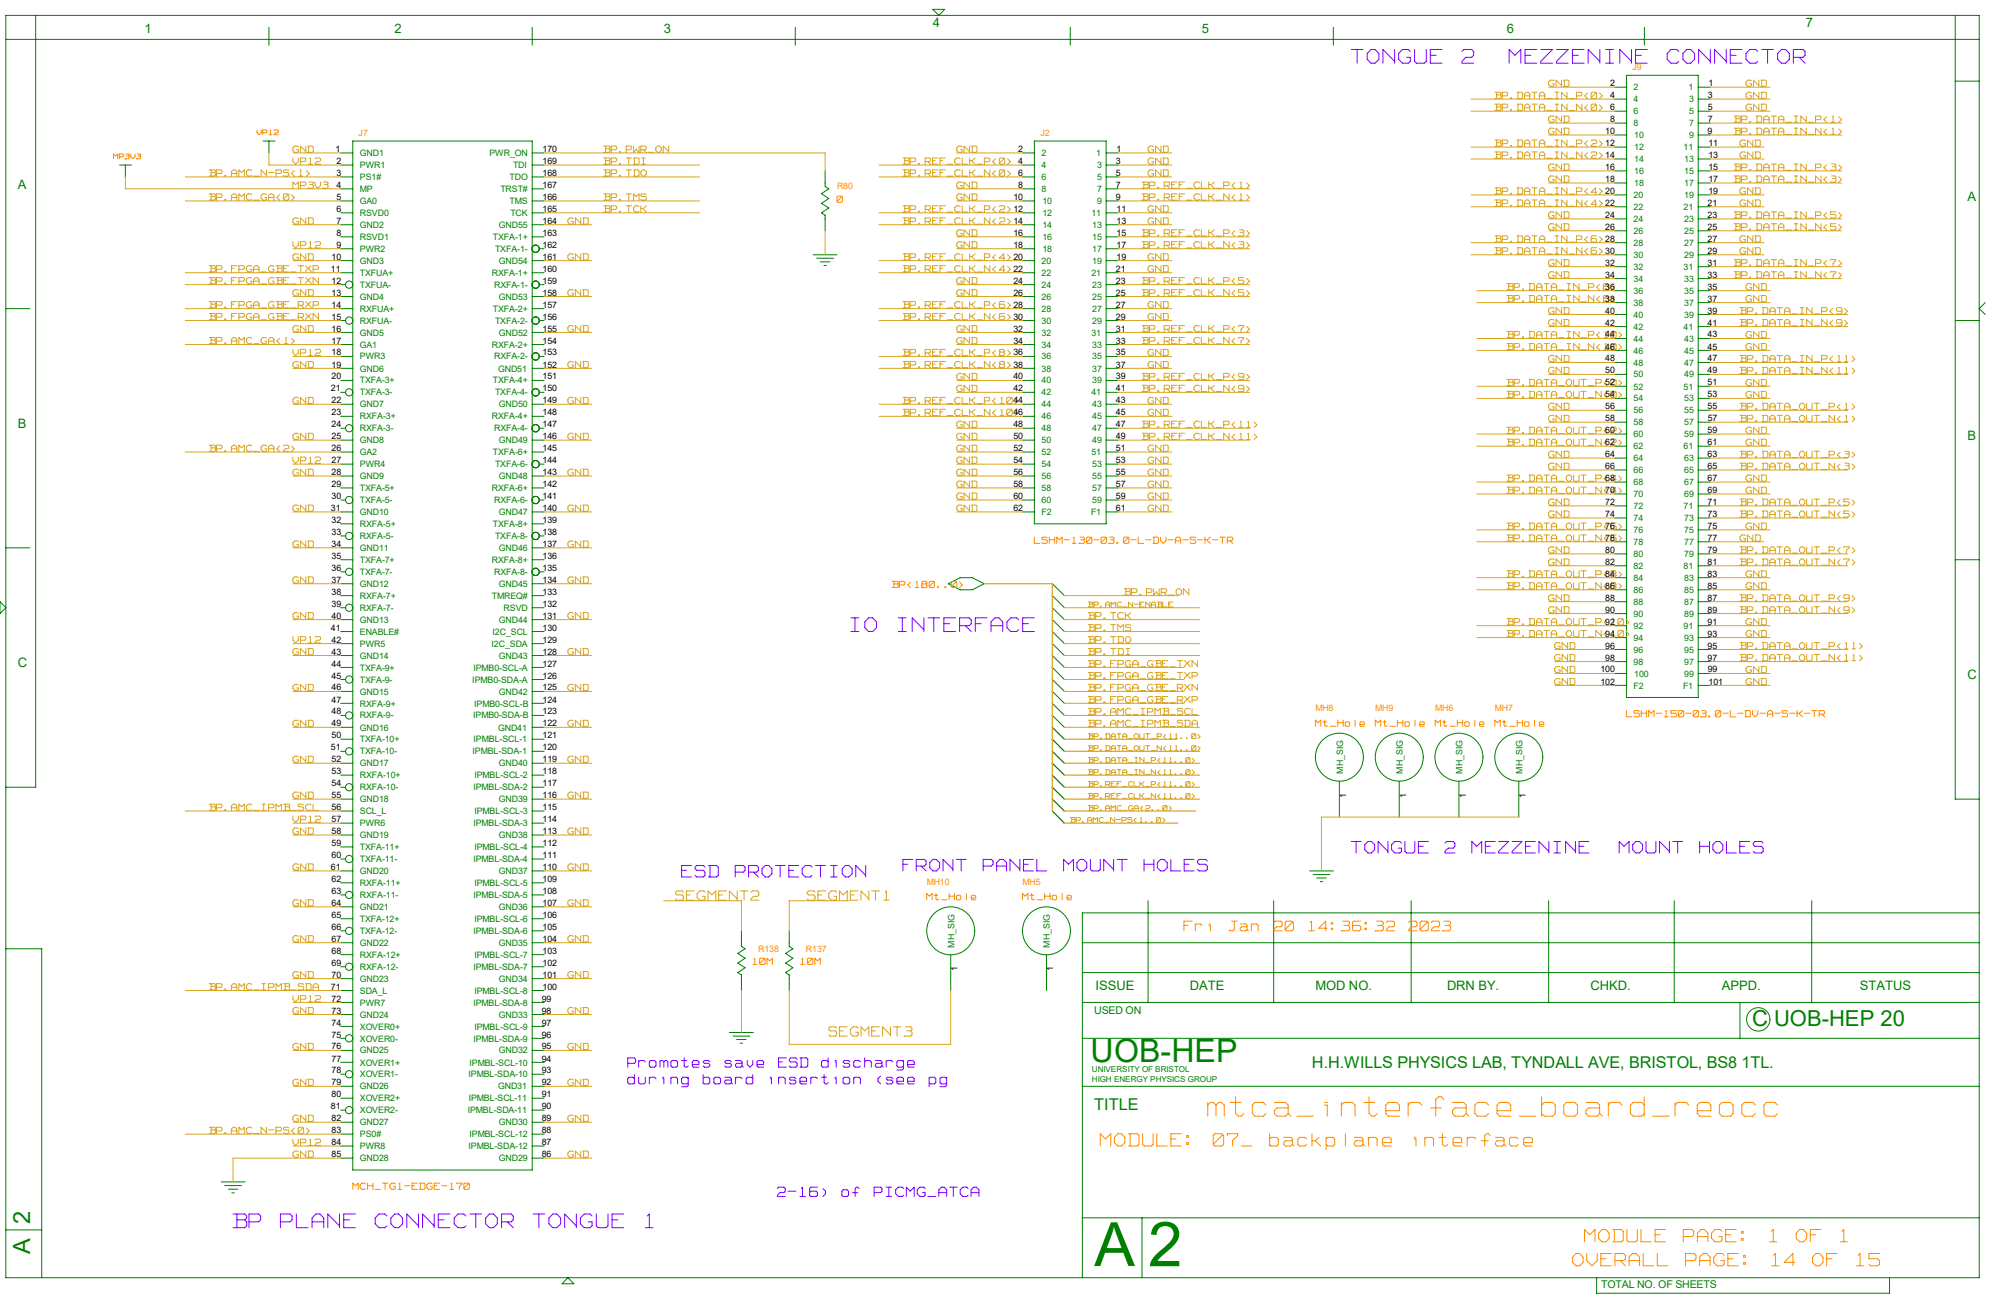
[picture p166: page 12]
2-16) of PICMG_ATCA; IO INTERFACE; ESD PROTECTION; Fri Jan 20 14:36:32 2023; mtca_interface_board_reocc; SEGMENT3; SEGMENT2; SEGMENT1; Mt_Hole; Mt_Hole Mt_Hole Mt_Hole Mt_Hole; BP.AMC_GA<2..0> BP.AMC_N-PS<1..0>; BP.REF_CLK_N<11..0>; BP.REF_CLK_P<11..0>; BP.DATA_IN_N<11..0>; BP.DATA_IN_P<11..0>; BP.DATA_OUT_N<11..0>; BP.AMC_IPMB_SDA; BP.AMC_IPMB_SCL; BP.FPGA_GBE_RXN BP.FPGA_GBE_RXP; BP.FPGA_GBE_TXP; BP.FPGA_GBE_TXN; BP.TDI; BP.TMS BP.TDO; BP.TCK; BP.AMC_N-ENABLE; BP.PWR_ON; BP.DATA_OUT_P<11..0>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

LSHM-130-03.0-L-DV-A-S-K-TR

LSHM-150-03.0-L-DV-A-S-K-TR

TONGUE 2 MEZZENINE MOUNT HOLES

FRONT PANEL MOUNT HOLES

Promotes save ESD discharge
during board insertion (see pg

UNIVERSITY OF BRISTOL
HIGH ENERGY PHYSICS GROUP
TITLE
MODULE: 07_ backplane interface

H.H.WILLS PHYSICS LAB, TYNDALL AVE, BRISTOL, BS8 1TL.

BP PLANE CONNECTOR TONGUE 1

MODULE PAGE: 1 OF 1
OVERALL PAGE: 14 OF 15

# IO INTERFACE

# MODULE MANAGEMENT CONTROL

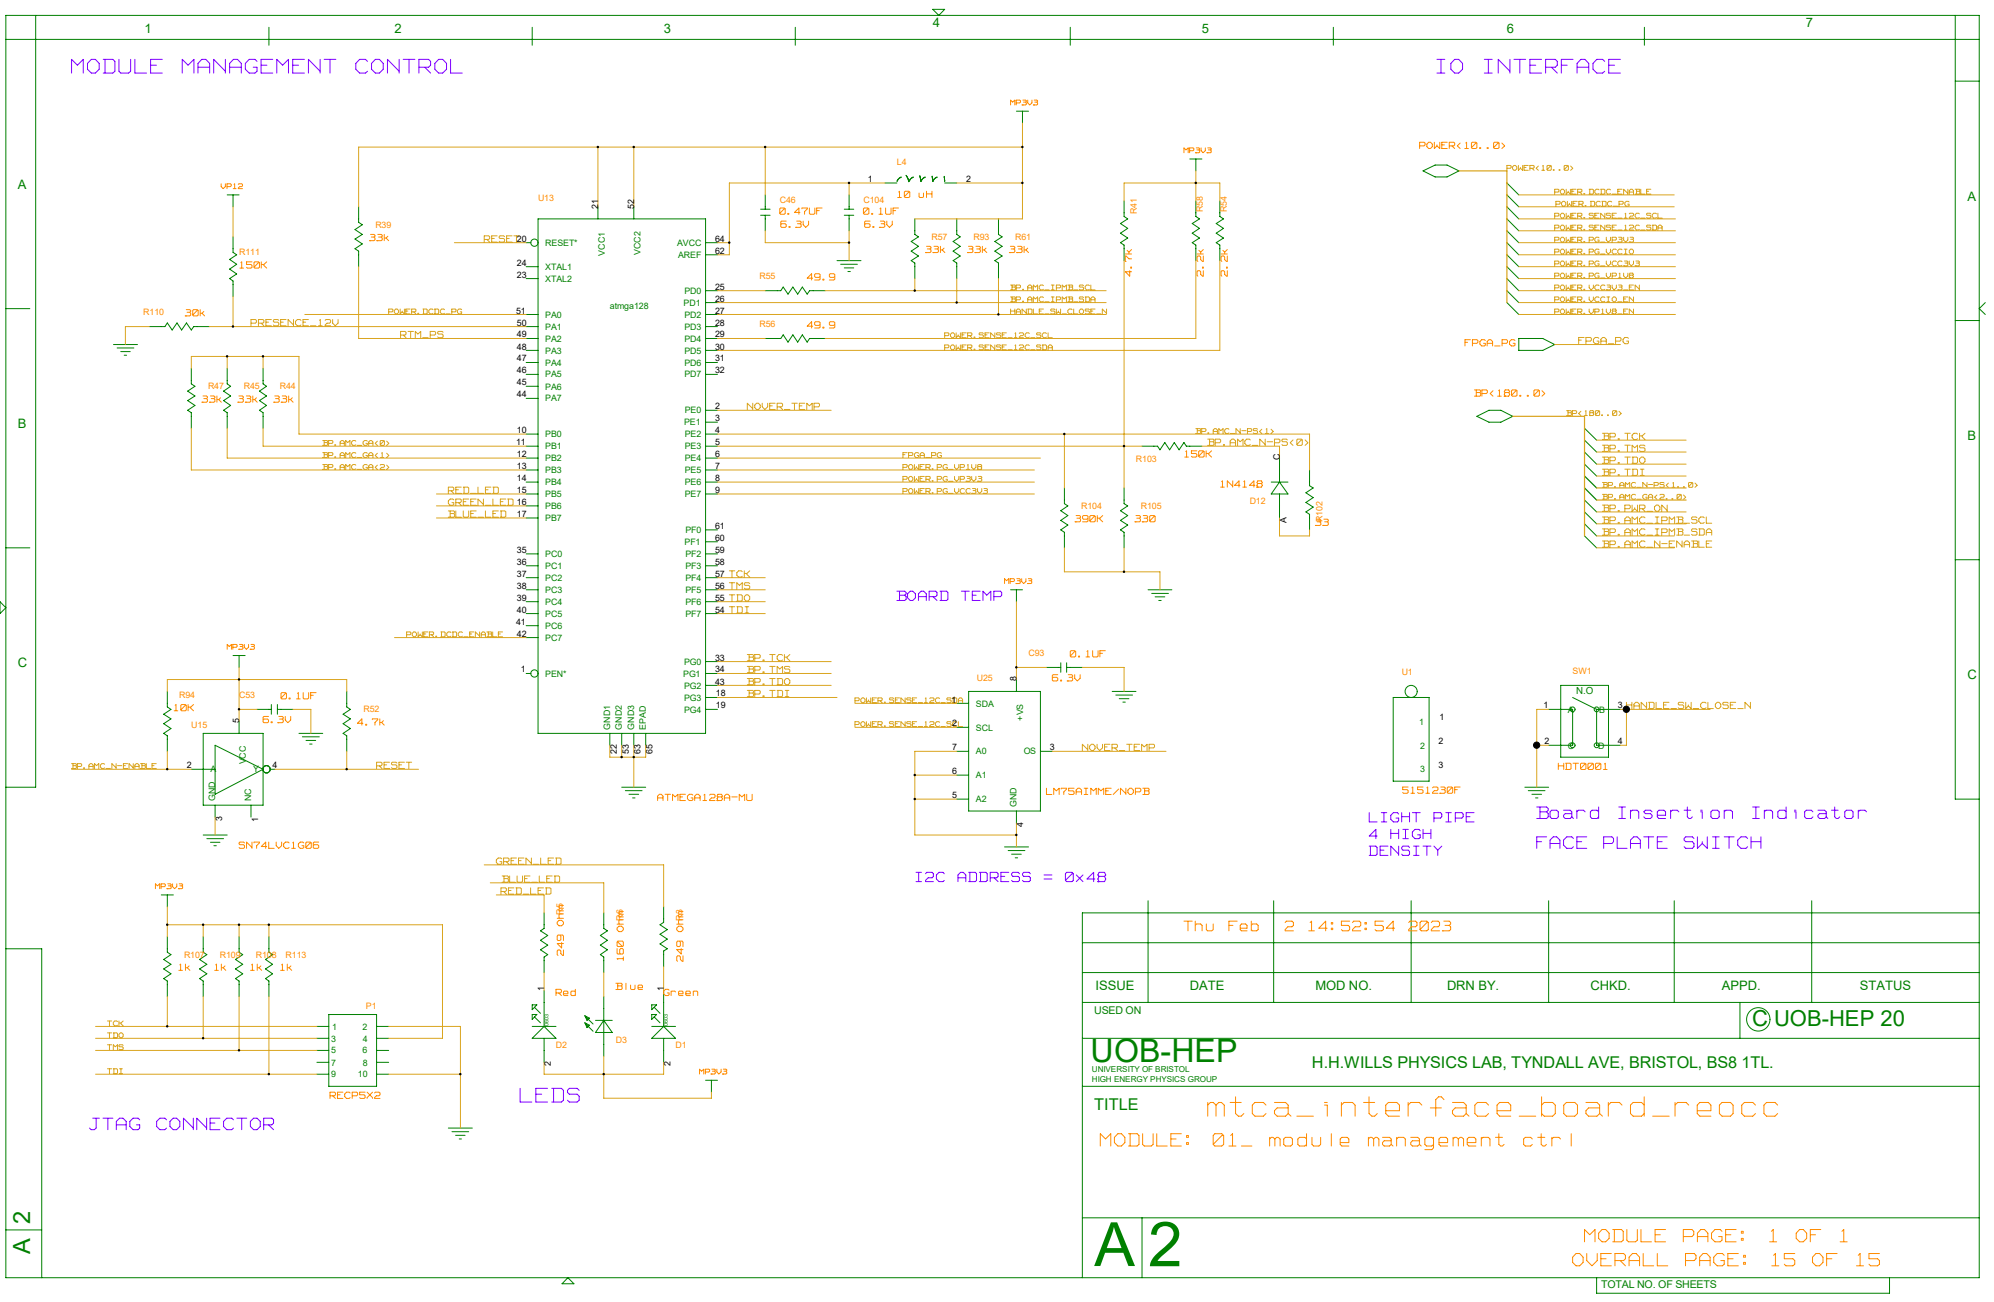
[picture p167: page 13]

A C R3 R102 R5 R6 21 22 52 536365 GND1 GND2 GND3 EPAD VCC1 VCC2 GND NC VCC GND +VS

BP.AMC_N-PS<1>
BP.TCK BP.AMC_N-PS<0>

UNIVERSITY OF BRISTOL
HIGH ENERGY PHYSICS GROUP
TITLE
MODULE: 01_ module management ctrl

H.H.WILLS PHYSICS LAB, TYNDALL AVE, BRISTOL, BS8 1TL.
