uob-hep-cad/uob-hep-pc072/hardware/Cadence/top/mtca_interface_board_reocc/top_mib_v3/physical/xsectionChartParams.txt

CHART_UNIT Millimeter
LAYER_NAME YES
LAYER_THICKNESS YES
LAYER_THICKNESS_TOL YES
MATERIAL_NAME YES
EMB_STATUS NO
ATTACH_METHOD NO
LAYER_TYPE YES
DRILL_SPAN YES
BACKDRILL_SPAN NO
STACKED_VIAS YES
EMD_COMP_LEGEND  NO
DRILL_LABEL  YES
X_SCALE_FACTOR  3.000
DIELECTRIC_SCALE_FACTOR  10.000
TEXT_BLOCK  1
MAX_CHART_HEIGHT 50.8 MM
