uob-hep-cad/uob-hep-pc072/hardware/Manufacturing/artwork/mib_v3b_pc072-manufacturing-artwork-2026-10-08/art_param.txt

DEVICE-TYPE           GERBER_RS274X
OUTPUT-UNITS          MM
FILM-SIZE             40000000 20000000
FORMAT                3.5
ABORT-ON-ERROR        NO
SCALE                 1
SUPPRESS-LEAD-ZEROES  YES
SUPPRESS-TRAIL-ZEROES NO
SUPPRESS-EQUAL        YES
UNDEF-APT-CONT        NO
